WongyuKoh/Toccata/hardware/mechanical/touchscreen/rev3/README.md

# R31 터치스크린 수정 3판 (B1 · L2) — 2026-10-01

화면은 사용자가 고른 **B1 Waveshare 7-DSI-TOUCH-C**입니다(7인치, 가로 1024×600, DSI). 자리는 **L2 가운데 화면 뚜껑**(x501~721, y214~341.5, 윗면 z72.85)입니다. 모든 좌표는 `design/numbers.json`의 `placement` 블록(L2 확정값 `cad/spec/body_L2.json`)에서 스크립트로 계산합니다.

**상태:** 2026-10-01 사용자 승인("3판 승인"). `design/CAD_SPEC_rev3.md`를 CAD 세션에 넘겼고 CAD가 만드는 중입니다(사양과 다르게 만든 곳은 CAD가 목록으로 보냄). 설계 기준 R31·D14·D16·D19·D20~D24를 3판 값으로 고쳤습니다. 2판(공식 TD2, L1) 기록은 `../rev2_td2/`로 옮겼습니다(CAD L1 보관본이 거기서 읽음). CAD 3판은 통합본 v15 탭 09, `cad/src/touchscreen_rev3.py`입니다(사양과 다르게 만든 18곳은 W1 확인 완료).

| 폴더·파일 | 내용 |
|---|---|
| `touch_rev3_review.html` | 검수용 한 장짜리 페이지(검수할 것, 3D 렌더 9장, 도면 6장, 회로도 2장, 개념도) |
| `design/` | numbers.json(3a) · design.json · texts.json · **CAD_SPEC_rev3.md** · README_rev3.md · 개념도 · 스크립트(geom3 → build3 → draw3 → build3d) |
| `drawings/` | 치수 도면 t01 조립 옆 단면 · t02 뚜껑 평면 · t03 받침 부품도 · t04 뚜껑 변경부 · t05 받침다리·작은 부품 · t06 배선 (SVG·PNG, 생성기 `src/`, 점검 결과 drawings.json) |
| `model3d/` | 3D 미리보기(출력용 아님): 렌더 9장, GLB 2개(세운/접은), `viewer_B1.html`(브라우저에서 돌려 보기), 간섭 검사 결과(22°·25°·90° + 69자세, 간섭 0) |

회로도는 `hardware/pcb` 개정 C(SCH-01·SCH-06, △16)입니다.

**받은 뒤 확인할 것:**
- 화면 뒤 커넥터 방향: 반대면 받침 창·홈·뚜껑 구멍·클립을 x611 기준으로 뒤집고, A형 리본을 씁니다.
- M2.5 구멍 깊이
- 동봉 전원선 3핀 하우징 핀 배치: 통전 검사로 확인합니다.
- Pi 5 방열판과 리본 사이 틈
- 뒤꿈치 틈 0.37 mm와 클립 틈

**L2 앞판 40° 반영 뒤 바뀐 값 (10/1, CAD 실측)** — numbers.json·도면은 43° 때 L2 값으로 계산했고, CAD가 rev 3을 만드는 동안에는 다시 돌리지 않습니다.
- 가운데 유닛 뒷면이 y341.5 → y342.5로 바뀌어 뚜껑 깊이가 128.5가 됐습니다. 접은 받침 끝(y339.05)과 뚜껑 뒤끝 사이 여유는 2.45 → 3.45입니다. 뚜껑 나사 자리는 그대로입니다.
- 스피커 윗면이 z148.06 → z144.65로 바뀌었습니다. 접은 화면 위(z95.35)와의 여유는 52.71 → 49.30입니다.
- 소리 길 27° 규칙은 3.50 mm, D14는 228.5 mm로 둘 다 통과합니다. 화면과는 관계없습니다.
