WongyuKoh/Toccata/hardware/mechanical/sound-requirements.md

# Toccata — 요구 조건 (소리 · 제작 · 비용)

> 2026-09-24 · 대화에서 정한 요구 조건 모음. 설계와 부품 선정은 **이 문서만을 기준**으로 한다
> 근거 조사: [오디오 체인 조합 조사 보고서](../../docs/report/toccata-audio-chain.html) · 출발점 메모: [curcuit/material.md](curcuit/material.md)
> 이 문서로 만든 설계: [제작 설계서 v3 — 도면·치수·부품표·비용](../../docs/report/toccata-build-v3.html)

이 문서는 두 층으로 나뉜다.

- **요구사항(R)**: 사용자가 직접 말한 것
- **도출 조건(D)**: 요구사항을 지키려고 조사 중에 나온 기술 조건

---

## 1. 요구사항 (R)

### 1.1 음원 — 소리를 만드는 프로그램

| ID | 요구 | 원문 요지 |
|---|---|---|
| R1 | 피아노 소리를 낸다 | "피아노 소리를 낼 수 있는 것" |
| R2 | 누르는 세기·속도에 따라 소리가 달라진다 | "누르는 파워, 스피드에 따라 소리의 크기가 달라지잖아" |
| R3 | 댐퍼 페달을 지원한다 | "댐퍼 페달도 있으니까 그것도 되는 프로그램" |
| R4 | 88키 전부, 시간 제한 없이 동작한다 | "키 제한과 시간 제한 없는 프로그램" |
| R5 | 무료이거나 비용이 적게 들고, 위 기능을 모두 제공한다 | "무료거나 비용이 얼마 안 들면 좋을 거 같고, 내가 말한 기능을 모두 제공해야" |
| R6 | 실제 피아노처럼 동작한다 | "실제 피아노처럼 작동되게 할 수 있는 프로그램 혹은 오픈소스" |

### 1.2 입력 — 건반·페달에서 신호로

| ID | 요구 | 원문 요지 |
|---|---|---|
| R7 | 건반을 얼마나, 어느 속도로 눌렀는지와 페달 여부를 전달한다 | "건반이 어느정도, 어느 속도로 눌렸는지를 측정해서 정보를 전달… 페달 여부도" |
| R8 | 입력 신호는 우리가 변환해서 제공한다 | "입력 신호를 변환을 해서 제공을 할 수밖에 없어" |
| R9 | 하드웨어는 그대로 두고 음원 소프트웨어만 바꿀 수 있다 | "하드웨어는 동일하고 소프트웨어만 바꾼다고 하면 호환이 될까?" |

### 1.3 구현 방식

| ID | 요구 | 원문 요지 |
|---|---|---|
| R10 | 음원 칩이 아니라 소프트웨어로 소리를 만든다 | "그러면 소프트웨어로 해보자" |
| R11 | 꼭 라즈베리파이일 필요는 없다 | "라즈베리파이가 아니여도 되는데" |

### 1.4 소리 출력 — 앰프와 스피커

| ID | 요구 | 원문 요지 |
|---|---|---|
| R12 | 프로그램 + 앰프 + 스피커가 모두 호환되고 음질 그대로 동작한다 | "3개가 모두 호환 및 음질 그대로 작동이 되는 구성" |
| R13 | 스피커는 피아노 본체에 부착한다. 완제품보다 부품형 | "우리 피아노에 부착형… 아두이노 스피커에 가까운 제품" |
| R14 | 좋은 스피커와 앰프로 음량 손실이 없어야 한다 | "좋은 스피커를 사용해서 음량손실이 없게" |
| R15 | 헤드폰을 꽂으면 스피커가 꺼진다 | "2번방식으로 가는데" (② = 헤드폰 자동 차단 구성) |
| R16 | 88키 모두 소리가 깨지지 않고 제대로 나온다 | "88키 모두 소리가 깨지는 거 없이 제대로 나오게" |

### 1.5 기준선 — "실제 피아노처럼"의 의미

R2·R3는 고급 기능이 아니라 **지금 팔리는 입문형 디지털 피아노도 갖춘 기본기**다(Yamaha P-145, Roland FP-10에서 확인).

| 항목 | 입문형 디지털 피아노 | Toccata 목표 |
|---|---|---|
| 세기 → 음량·음색 | 있음 | 있음 |
| 페달 공명 | 있음 | 있음 |
| 하프페달 | 본체는 지원, 동봉 스위치 페달로는 불가(연속형 페달 별매) | 있음 |
| 스피커 | P-145: 7W×2, 12×8cm 타원 ×2 | 이 이상의 음량 |
| 최저음 | 실제 그랜드도 A0(27.5Hz) 기본음은 가장 강한 배음보다 최대 25dB 약하다 | 27.5Hz를 크게 내는 것이 아니라 **찌그러짐 0**. ~~30~100Hz 채움~~ → R25로 서브를 두지 않는다(P-145처럼 최저 옥타브는 배음으로 들린다) |

### 1.6 제작 · 구조 · 비용

| ID | 요구 | 원문 요지 |
|---|---|---|
| R17 | 도~시(C–B) 12건반을 한 세트(모듈)로 만들고, 나머지 건반도 같은 구조로 만든다 | "도부터 시까지를 한세트로 해서 똑같은 구조로 나머지 건반들이 만들어지고" |
| R18 | 모듈 단위로 탈부착해서 나눠 들고 다닐 수 있다 | "해당 부분을 묶음으로 해서 분할해서 가지고 다닐 수 있게" |
| R19 | PCB를 만들지 않고 손 납땜으로 배선한다 | "pcb를 만드는게 아니라 땜을 할거니까 케이블도 사야되고" |
| R20 | 건반은 3D 프린팅으로 만든다 | "피아노 건반은 cad로 뽑을거니까 필라멘트 등" |
| R21 | 총비용 100만원 이하. 케이블·필라멘트 같은 소모품 때문에 넘는 것은 허용 | "최대 비용을 100만원으로 잡고… 소모용 부품들에 의한 100만원 넘김은 넘어가자" |
| R22 | 건반 구조는 최대한 단순하게 해서, 원하는 기능만 최소한으로 구현한다 | "피아노 건반의 구조가 최대한 단순하게 구성해서 우리가 원하는 기능이 최소한으로 적용되도록" |
| R23 | 건반의 탄성과 복귀는 참고 영상의 컴플라이언트 메커니즘(플라스틱이 휘어서 움직이는 구조)을 참고해 구현한다. 똑같이 만들 필요는 없다 | "Compliant Mechanism 를 사용해서 탄성과 회복 동작을 구현했는데 우리도 똑같이는 아니더라도 이 점을 참고해서" |
| R24 | 페달은 댐퍼(서스테인) 하나만 둔다. 소스테누토·소프트 페달은 두지 않는다 | "나는 댐퍼만 필요하거든? 다른 페달은 빼도 돼" |
| R25 | 스피커는 좌우 2개면 된다(서브우퍼 없음). 스피커와 앰프는 비싸지 않은 것으로 고른다 | "양쪽 2개면 충분하잖아… 이정도로 비싸지 않더라도 소리는 다 커버가 될 거 같은데… 엠프도 너무 비싼 거 같아" |
| R26 | 건반뿐 아니라 스피커·CPU 상자 등 모든 파트를 따로 떼어 보관할 수 있는 독립 구조로 한다. 파트 사이는 물리적으로 고정되는 결합부를 두고, 전선은 꽂았다 뺐다 하는 커넥터로 잇는다 | "각 파트 별로 분할해서 보관이 되도록 파트별 독립적인 시스템… 결합 부분을 만들어 둬서 물리적 고정 결합… xt90? 같은 꼈다 뺐다 할 수 있는 케이블" |
| R27 | 스피커·CPU 상자 사이의 빈 뒷공간을 채워 본체 전체를 직사각형으로 하고, 그 속을 케이블 공간으로 써서 전체 길이(깊이)를 줄인다 | "뒷공간이 빈공간으로 되어있는데 그부분을 채워서 피아노의 전체적인 디자인 직사각형이 되게… 오히려 길이를 줄일 수 있잖아" |
| R28 | 보조배터리로 전원 없이(무선으로) 쓸 수 있게 하고, 보조배터리 수납 공간을 둔다 | "보조 베터리로 무선으로 할 수 있게 보조베터리 수납 공간도 제공하면 좋을 거 같아" |
| R29 | ~~빈 공간 한쪽에 건반 보관용 공간을 둔다~~ → R32 L2에서 본체 안 보관 칸 없음(사용자 승인 10/2). L2 가운데 유닛은 건반과 같은 높이(z72.85)라 안 높이가 44.85 mm뿐이고(예비 빗살 2층은 58.8 mm 필요) 안폭도 전자부로 꽉 찬다. 예비 건반은 따로 출력하는 부품 상자(약 210×180×65)에 넣어 모듈 가방과 함께 들고 다닌다 — `cad/spec/body_L2.json` key_storage | "건반 보관용 공간도 있으면 좋을 거 같아. 빈 공간은 많으니까 한쪽에 만들 수 있을 거 같아 보여" → "보관 칸은 빼도 돼"(10/2, CAD 세션 전달) |
| R30 | 스피커 파트 높이를 낮추고(210 → 150 mm 제안 → CAD L1 확정: 윗면 z232 → z134, 받침 22 → 5 mm), 앞판은 위쪽을 비스듬히(30°) 눕혀 유닛이 연주자 귀를 향하게 한다 (2026-09-30) | "스피커가 연주자쪽을 바라보게 되어있는데… 위쪽을 바라보게 해서 해도 되는 거 아니야?" → "비스듬하게 하는데 지금 보면 높이가 너무 높아. 높이를 좀 낮출 수 있어?" → "바꾸자" |
| R31 | 라즈베리파이 호환 터치스크린을 피아노 본체에 단다. ~~공식 Touch Display 2 7인치를 가운데 유닛의 출력 CU 뚜껑 위에 25° 뒤로 기울여 세운다(경첩 축 y290 z96, 화면 중심 x656 y304.7 z165.4, 가장 앞 y276.7). 운반할 때는 받침다리를 받침 뒤에 붙이고 화면을 뒤로 접어 z113에 눕힌다(스피커 윗면 z134 아래)~~ → 3판: 공식 제품이 아니어도 되는 호환 화면으로 한다. 13가지 조합을 비교해 사용자가 B1 Waveshare 7-DSI-TOUCH-C(7인치, 가로 1024×600, DSI)를 골랐다(10/1). L2 가운데 화면 뚜껑(x501~721, y214~341.5, 윗면 z72.85) 위에 25° 뒤로 기울여 세운다(경첩 축 y226.55 z81.35, 뒤꿈치 22°). 화면 가운데 x611, 보이는 영역 가운데 y240.91 z142.91, 가장 앞 y216.0이다. 운반할 때는 받침다리를 받침 뒤 클립에 끼우고 화면을 뒤로 접어 z78.35~95.35에 눕힌다(y233.05~339.05, 뚜껑 뒤끝 y341.5 안쪽 2.45 mm, 스피커 윗면 아래). 음색·볼륨·메트로놈·게임 메뉴를 터치로 조작한다. 재료는 추가되는 것만 따로 정리한다(~~103,600원~~ → 86,674원) (2026-09-30, 3판 승인 2026-10-01) | "라즈베리파이 호환 터치스크린을 피아노에 설치하면 좋겠어. 그걸 고려해서 설계 및 재료 정리를 다시 해줄래? 재료는 추가되는 재료만 알려줘. 그리고 그걸 바탕으로 ppt를 업데이트 해줘" → "모니터가 굳이 라즈베리파이 공식이 아니여도 라즈베리파이에서 터치되는 호환 제품으로 해도 돼" → "B1으로 하자" → "3판 승인" |
| R32 | 뒷바를 건반 바로 뒤에 붙여(L2) 뒤 영역을 최대한 줄이고, 케이블이 밖으로 보이지 않게 모두 닫힌 통로·앞 공간으로 넣는다. 스피커는 더 눕히고 작게, 가운데 유닛은 빈 공간 없이 촘촘하게 한다. CAD L2 확정값: 깊이 447 → ~~341.5~~ → 342.5, 가운데 윗면 z72.85(건반과 같은 높이), 스피커 앞판 수평에서 ~~43°~~ → **40°**(사용자 10/1), 스피커 윗면 ~~z148.06~~ → z144.65(L1 z134보다 10.65 높음 — 소리 길·그릴 R18·앞판 각도가 정함), 뒤 래치 없음 — `cad/spec/body_L2.json` (2026-10-01) | 사용자 요청(CAD 세션 전달): "건반과 뒤 부품을 합쳐서 뒤 영역을 최대한 줄이고, 케이블이 밖으로 안 나오게, 스피커는 더 눕히고 작게" → "앞판은 40°로 해줘" |

### 1.7 진행 방식

- 후보는 최대한 많이 찾고 보고서로 정리한다
- 부품은 이미지, 세부 스펙, 구매처 링크, 가격을 함께 보여 주어 바로 확인할 수 있게 한다
- 건반 구조는 도형 추상화가 아니라 **실제 치수를 기입한 평면도·측면도**로 설계한다. 그 도면대로 CAD를 짜면 실제로 구현되는 수준이어야 한다
- 기존 설계 자료는 참고하지 않고 이 문서만 기준으로 새로 설계한다
- 참고 영상은 §3의 분석을 기준으로 삼는다

---

## 2. 도출 조건 (D)

요구사항을 지키는 데 필요한 기술 조건이다. 사용자가 직접 말한 것이 아니라 조사에서 나왔다.

### 2.1 펌웨어 (Pico)

| ID | 조건 | 이유 |
|---|---|---|
| D1 | 페달 CC64를 0/127 대신 ADC 연속값으로 보낸다. 발을 뗐을 때는 정확히 0, ±2 이상 변할 때만 송신 | R3 하프페달. 켜짐/꺼짐 엔진에서 64 경계 떨림 방지 |
| D2 | Note Off는 정식 `0x80`, 릴리즈 벨로시티 하한 5 | Pianoteq에서 1이면 댐퍼가 내려가지 않는다는 보고 |
| D3 | 모듈마다 USB 제품 이름을 다르게 준다 (`Toccata O1`~`O7`, `Toccata PED`) | 고장 난 모듈 특정, 연결 스크립트 단순화 |
| D4 | 하드웨어 편차 보정(건반별, 흑건/백건)은 펌웨어에, 취향 곡선은 엔진에 둔다 | R9. 엔진을 바꿔도 펌웨어를 다시 보정할 필요가 없다 |
| D5 | ~~CC66(소스테누토)·CC67(소프트)도 보낸다~~ → R24로 페달을 두지 않는다(펌웨어 처리 코드는 남겨도 무해). 선택: CC88 고해상도 벨로시티 | 이해하는 엔진만 쓰고 나머지는 무시한다. 오동작은 없다 |

### 2.2 Pi 5와 소프트웨어

| ID | 조건 | 이유 |
|---|---|---|
| D6 | 8개 입력 병합은 한 곳에서만 한다 (FluidSynth `midi.autoconnect=1` 또는 Pianoteq `listen-all="1"`) | 병합 층이 겹치면 모든 음이 두 번 난다 |
| D7 | 오디오는 ALSA `hw:` 직결, 48kHz 통일, PipeWire 미설치 | 지연과 숨은 리샘플링 방지 |
| D8 | 키→소리 지연 10ms 미만 | 누르고 소리가 나기까지 지연이 체감되지 않는 한계 |
| D9 | 디지털 피크 −3~−6dBFS (최악 조건: 페달 + 저음 화음 ff) | R16. 페달 화음의 클리핑이 가장 흔한 깨짐 원인이고, 스피커로는 못 막는다 |
| D10 | 엔진 전환은 systemd 서비스 전환으로 한다 (`Conflicts=`) | DAC는 한 번에 한 프로그램만 쓸 수 있다 |
| D11 | 커널 #7320(Pi 5 I2S DMA) 대비: `hw:` 직결, 스트림 상시 유지, 워치독, 24~48시간 연속 재생 테스트 (R25로 USB 오디오를 쓰면 이 버그는 해당 없음, 연속 재생 테스트는 유지) | DAC2 Pro와 같은 PCM512x 계열 HAT에서 보고된 미해결 버그 |

### 2.3 스피커와 앰프

| ID | 조건 | 이유 |
|---|---|---|
| D12 | 스피커 유닛은 반드시 상자에 넣는다 (~~DMA105-4~~ → R25 CW-100B25: 밀폐 ~~약 4.7L~~ → ~~R26 스피커 파트 5.05L~~ → R30 **안 부피 2.9 L 이상**; CAD L1 확정값: 바깥 폭 213 × 깊이 195 × 높이 129(z5~134), 30° 앞판, 안 부피 2.95 L(유닛 빼기 전), 유닛 중심 y282.25 z81.5 — `cad/spec/body_low_L1.json`) → R32 L2: 안 부피 ~~2.218 L(유닛 빼면 2.118 L, 43°)~~ → 2.159 L(유닛 빼면 2.059 L, 앞판 40°, 유닛 중심 y260 z100.45), 흡음솜을 상자 전체에 느슨하게(유닛 뒤 10 mm·폴 벤트 앞은 비움) — `cad/spec/body_L2.json` | 상자가 없으면 뒤로 나간 소리가 앞소리를 상쇄해 저음이 사라진다 (R14). 5.05 L는 예전 유닛(DMA105-4, Qts 0.51, Vas 4.3 L)의 Qtc 0.707 값이 남은 것이다. CW-100B25(Qts 0.72, Fs 90~128 Hz)는 상자를 줄여도 Qtc가 크게 오르지 않는다: Vas 3 L로 가정하면 5.05 L에서 Qtc 0.91·Fc 약 126 Hz, 2.9 L에서 1.02·약 142 Hz(부밍 +1.4 dB). L1(2.95 L): 조준 28~39°(앉은 연주자 귀), 콘 아래 가장자리에서 귀로 가는 선이 모듈 윗판 위 약 5 mm로 지나가므로 모듈 뒤 y212~252 통로에는 z72 위로 아무것도 두지 않는다. 센서 줄과 226 mm. 앰프 앞 RC 필터가 93 Hz 아래를 이미 자르므로 체감 차이는 작고, 작은 상자가 저음 과진폭을 더 잘 막는다. Vas는 공개값이 없어 단계 0에서 추가 질량법으로 재어 확인한다. R32 L2 40°(2.06 L 유닛 뺌): Qtc 1.13, Fc 약 141~201 Hz, 솜으로 약 1.08. Vas 4 L이면 1.24라 솜을 기본으로 넣는다. 폴 벤트 앞 55.6 mm 비어 있음. 첫 x방향 공진 약 686 Hz(안폭 250, 유닛이 가운데보다 40 mm 안쪽)는 공기 속도가 큰 가운데 쪽까지 솜을 채워 줄인다. L2에서는 통로가 닫혀(y212~241, z0~27) 통로 규칙 대신 "콘 아래 끝에서 27° 선이 모듈 모서리(y212, z72.85) 위 3 mm 이상"을 지킨다(L2 40°: 3.50, 플랜지 모서리 2.61은 유닛 자기 테두리라 허용). 그릴 아래 링 벽은 없앴다(40°에서 선이 구멍 판 아래 끝 밑 1.72로 지나감, 개구율 72 %·구멍 Ø3 이상·판 2 mm). D14: 자석 중심에서 가장 가까운 홀센서까지 3D 228.5 mm, 가장 가까운 쇠까지 159.7 mm |
| D13 | 위성 스피커에 직렬 콘덴서(베이스 블로커)를 쓰지 않는다 | 계산상 330µF에서 80Hz를 오히려 +2.5dB 키운다. 상자 공진 근처에서 유닛 저항값이 약 17Ω까지 올라 콘덴서와 공진 |
| D14 | 스피커는 건반 센서 열에서 10cm 이상, 서브우퍼는 15cm 이상 떨어뜨린다. 설치 후 센서의 유휴 흔들림을 다시 측정한다 R31: 화면·경첩·받침다리에는 자석을 쓰지 않는다(3판도 같음). 3판 화면의 가장 앞(y216.0)은 센서 줄(y≈67)에서 149.0 mm 뒤다. 화면을 켠 상태와 끈 상태, 밝기 0 %와 100 %(`/sys/class/backlight/*/brightness`에 0·255, D20)에서 센서 유휴 흔들림을 다시 잰다. | 홀센서는 스피커 자석의 자기장을 입력으로 오인한다. SS49E급 기준 허용치(계산): 흔들리는 자기장 약 1.2mT, 고정 자기장 약 12mT |
| D15 | 스피커 상자, 특히 서브는 키베드에 직접 고정하지 않고 고무 등으로 진동을 격리한다 | 건반·센서 기판이 떨리면 치지 않은 음이나 잡음이 생긴다 |
| D16 | ~~앰프 HAT이 Pi에 전원을 공급하므로 Pi USB-C에 동시 급전 금지. EEPROM `PSU_MAX_CURRENT=3000`~~ → R25로 앰프 HAT이 없다. ~~Pi는 전용 5V 5A 어댑터 하나로만 급전한다~~ → R28로 Pi는 본체 안 5.1V 강압 전원 하나로만 급전한다(동시 급전 금지는 그대로, EEPROM `PSU_MAX_CURRENT=5000`) R31: 화면은 Pi GPIO 2번(5 V)·6번(GND)에서 전원을 받는다(Pi에서 나가는 방향이라 허용). 3판(B1)은 넷 `+5V_PI`다(회로 개정 C △16). 헤더 2·6번 → 점퍼 F/F 20 cm → 점퍼 M/M 20 cm → 화면 동봉선의 2.54 3핀(1 빨강 5 V · 2 빈 칸 · 3 검정 GND) → 화면 MX1.25 2핀으로 잇는다. 화면과 연장선에 다른 전원을 넣지 않는다. 화면은 약 2.15 W(5 V에서 0.43 A)다. Pi USB-C 입력은 ~~약 2.1 A~~ → 약 2.02 A, 5.1 V 레일은 2.42 A다. 피그테일(MT666) 정격은 공개되지 않았으므로 최대 부하(FluidSynth + 화면 밝기 100 % + USB 장치)에서 `vcgencmd get_throttled`가 0x0인지 확인한다. | 동시 급전으로 Pi가 파손된 사례가 있다 |
| D17 | 스피커는 연주자 쪽을 향하게 하고, 구멍이 넉넉한 그릴을 쓴다. R30: 앞판 위쪽을 30° 뒤로 눕혀 유닛 축이 앉은 연주자의 귀(스피커 중심에서 약 30° 위)를 향하게 한다. 위로 쏘기(윗판에 유닛)는 쓰지 않는다. R32(L2): 앞판을 수평에서 ~~43°~~ → 40°(수직에서 50°, 사용자 10/1)로 눕혀 유닛 축이 수평에서 50° 위를 향한다. 한계는 수평에서 37° 이상(권장 40~45°); 가운데 귀(유닛에서 32.7° 위)와 y-z면 어긋남 ~~14.4°~~ → 17.3° | 고음 손실 방지. 4인치 유닛은 약 1.2 kHz 위부터 소리가 앞으로 모인다. 위로 쏘면 연주자 귀가 축에서 약 60° 비껴 4 kHz 위가 6~10 dB 약해진다(평판 진동판 어림) |
| D18 | 서브가 없으므로(R25) 유닛에 맞춘 고역 통과 필터(약 60~100Hz)와 리미터를 걸고, 소리 게이트로 볼륨 상한을 정한다. 필터는 D7(`hw:` 직결) 때문에 ~~소프트웨어에서~~ → 앰프 입력의 콘덴서·저항(RC)으로, 리미터는 FluidSynth `synth.limiter`로 | R16. 작은 유닛은 최저 옥타브를 크게 내려 하면 과진폭으로 먼저 찌그러진다 |
| D19 | 보조배터리·충전기는 USB-C PD 20V 3A(60W) 이상을 쓴다. ~~45W 제품이면 볼륨 상한을 1dB 낮춘다~~ → R31: 45W 제품이면 볼륨 상한을 2dB 낮춘다(화면 포함). 1dB만 낮출 때는 화면을 끈다(밝기 0, D20) | R28. 평균 약 12W(SCH-06 표 13~17 W, ~~R31 화면을 더하면 16~20 W~~ → 3판 B1 화면 2.15 W로 15.69~19.69 W)지만 최대 음량의 저음 화음에서 순간 약 52W(SCH-06 rev B는 50 W, 큰 값을 기준으로 함), R31 화면을 더하면 ~~약 55 W~~ → 54.39 W(52 W + 2.15 W ÷ 0.9)까지 올라, 모자라면 전원이 끊긴다. 60 W까지 여유 ~~약 5 W~~ → 5.61 W. 45 W에서 −1 dB면 화면 포함 약 46 W로 넘치고(밝기 0이면 약 43.6~44.2 W: 백라이트를 꺼도 패널·터치 회로가 약 0.5 W 쓴다고 봄, 추정), −2 dB면 ~~약 40 W~~ → 39.39 W다. 보조배터리(74 Wh × 0.85 ≈ 62.9 Wh)로 약 3.19~4.01시간 쓴다(62.9 Wh ÷ 평균 19.69~15.69 W) |

### 2.4 검증 — 소리 게이트

R16의 합격 기준.

1. 최악 조건 연주 파일을 만든다: 88키 반음계 ff + 페달, A0~C2 뭉친 화음 최대 세기 + 페달, 옥타브 글리산도, A0 연타
2. 디지털 피크가 −3dBFS 이하인지 확인한다
3. 20~300Hz 사인 스윕을 최대 볼륨으로 튼다: 덜그럭거림·바람 소리가 없어야 하고, 건반 센서의 유휴 흔들림도 기준 안이어야 한다
4. 최악 조건 파일을 최대 볼륨으로 녹음한다: 모든 건반에서 찌그러짐이 없어야 한다
5. 통과한 볼륨보다 3dB 낮은 곳을 볼륨 상한으로 고정한다

---

### 2.5 터치스크린 (R31, 3판: B1 · L2, 2026-10-01 승인)

> 3판 값 출처: [numbers.json](touchscreen/rev3/design/numbers.json)(3a) · [CAD_SPEC_rev3.md](touchscreen/rev3/design/CAD_SPEC_rev3.md) · 회로 [hardware/pcb](../pcb/README.md) 개정 C(△16) · 재료 [hardware/bom](../bom/README.md). 2판(공식 TD2, L1 CU 뚜껑) 값은 취소선으로 남긴다

| ID | 조건 | 이유 |
|---|---|---|
| D20 | 화면은 ~~공식 Touch Display 2(DSI)로 하고 Pi 5 CAM/DISP 1 포트의 자동 인식을 쓴다(config.txt 수정 없음). 안 뜨거나 0번 포트면 `dtoverlay=vc4-kms-dsi-ili9881-7inch`(0번 포트는 `,dsi0`)를 넣는다~~ → 3판: Waveshare 7-DSI-TOUCH-C(DSI)를 Pi 5 CAM/DISP 1에 잇는다. config.txt 끝에 `dtoverlay=vc4-kms-dsi-waveshare-panel-v2,7_0_inch_c` 한 줄을 넣는다(0번 포트면 끝에 `,dsi0`). 기본 줄 `dtoverlay=vc4-kms-v3d`는 그대로 둔다. OS는 Raspberry Pi OS Lite(64-bit, 쓰는 판 고정)다. ~~가로 회전은 콘솔은 cmdline `video=DSI-1:720x1280@60,rotate=90`(이름은 kmsprint로 확인), 메뉴·게임(pygame KMSDRM)은 앱 안에서 1280×720을 돌리고 터치 좌표도 같이 돌린다~~ → 화면이 처음부터 가로 1024×600(60.0 Hz)이라 화면도 터치도 돌리지 않는다. 메뉴·게임(pygame KMSDRM)과 터치 좌표를 그대로 쓴다. 출력 이름은 kmsprint로 확인한다(Pi 5에서는 DSI-2일 수 있다). 밝기는 `/sys/class/backlight/*/brightness`에 0~255를 쓴다. 0이면 꺼진다(D14 시험, D19 화면 끄기). 연주만 할 때는 0으로 줄여 전력을 아낀다 | ~~공식 문서: `rotate=`는 텍스트 콘솔만 돌린다. KMSDRM 앱은 스스로 돌려야 한다.~~ → 3판: 오버레이와 터치 드라이버(Goodix, 5점)는 지금 Pi OS(2026-09-15, 커널 6.18.50)에 들어 있어 따로 설치하지 않는다. 그릴 픽셀이 0.61 MP로 TD2(0.92 MP)보다 33 % 적어 게임 60 fps 여유가 크다. 찬 부팅에서 가끔 화면이 안 켜진다는 보고가 있다(I2C write failed −5, raspberrypi/linux PR #7182 미반영). 재부팅으로 복구한다. 데스크톱 판은 PipeWire를 깔아 D7과 부딪힌다 |
| D21 | 터치 메뉴는 소리를 직접 내지 않는다. 음색·볼륨·리버브·메트로놈은 FluidSynth 셸(TCP)로 명령을 보낸다. 메트로놈은 피아노 음원의 높은 음(C7/G6)을 16번 채널로 짧게 낸다(선택: 작은 GM SF2의 우드블록) | D7·D10: DAC는 한 번에 한 프로그램만 쓴다. Salamander 피아노 SF2에는 10번 채널 드럼이 없다 |
| D22 | 화면은 받침(PETG, 170.7×106.0×17.0) 뒤에서 M2.5×6 4개로 화면 모서리 구멍(154×88)에 조인다. 받침은 앞 경첩 2개(축 ~~y290 z96~~ → y226.55 z81.35, M3×20, ~~x616~636.4·x703.8~724.2~~ → x538.6~559.0·x663.0~683.4, 나사는 바깥에서)와 받침 뒤 받침다리 1개(~~u20에 경첩, 95 mm~~ → u30에 축, 67 mm, 수평에서 39.78°, 발은 뚜껑 주머니 y290.43~300.7)로 25°에 세운다. 뒤꿈치는 22°에서 닿게 해 앞으로 3° 놀이를 둔다(3판: 귀 홈 바닥의 3.5 mm 멈춤 블록 z76.35에 닿음, 25°에서 0.37 mm 뜸). 다리는 화면을 22°에 댄 채 넣고 뺀다(25°에서 넣으면 발이 뒷벽 모서리를 0.66 mm 긁음). 접으면 받침 뒤 패드 4개가 뚜껑의 받침 발(16×16×5.5) 위 z78.35에 얹힌다. ~~모든 부품은 x559~753 안, y277보다 뒤에 두어 통로 규칙(y212~252에 z72 위 금지: D12 이유 칸, cad/spec/body_low_L1.json trough_rule)을 지킨다~~ → L2에는 열린 통로가 없다(소리 길은 D12의 27° 규칙). 화면 쪽은 모듈을 위로 빼야 하므로 모듈 위 금지 규칙을 지킨다. y≤215이면서 z≥72.85에는 화면 부품·선을 두지 않는다(모듈 뒤끝 y212, 뒷바 앞면 y214, 여유 1 mm). 22~90° 도는 동안 가장 앞 부품은 y216.0, 선은 약 y222.51이다. 경첩 축 y226.55 = 215 + 1 + 10.55(22°에서 받침 앞 아래 모서리가 축보다 앞으로 나오는 길이), z81.35 = 뚜껑 윗면 + 8.5 | 10 N 터치가 다리 압축 ~~39.3 N(좌굴 394 N)~~ → 27.22 N(좌굴 792 N, 29.08배)으로 간다. 경첩에는 앞뒤 12 N, 위아래 9 N이 걸린다. 사용 각도를 한 곳(다리)만 정해 과구속을 피한다. 다리는 받침 뒤에 붙여 접으므로 접은 높이가 늘지 않는다. ~~양옆 합판 뚜껑을 막지 않는다~~ → 받침 x525.65~696.35는 뚜껑 안이다(양쪽 24.65 mm). 모듈은 위로 빼므로 모듈 위에 아무것도 걸치면 안 된다. CAD 권장 경첩(y216~218, z76)은 22°에서 받침이 모듈 위로 넘어가 쓰지 않는다. 뒷바만 따로 놓였을 때(운반 중, 3.3 kg 추정) 넘어짐 여유는 1.58배이고, 건반 틀에 붙으면 훨씬 크다. 연주자 눈(y−350 z450 추정)에서 화면 가운데까지 아래로 27.46°라 기울기 25°와 2.46° 차이로 거의 정면이다. 화면은 스피커 콘과 x로 약 318 mm 떨어져 소리 길(D12)에 들어가지 않는다 |
| D23 | ~~CU 뚜껑 앞 모서리 2곳을 M3×10으로 나사형 모서리 받침에 조인다(CU-FL 자석 대신). 이 두 받침은 MS 폴리머로 합판에 붙인다. 뚜껑을 열 때는 받침 점검창에서 리본·J1 전원선을 빼고 나사 2개를 푼다~~ → L2(3판): 가운데 화면 뚜껑을 이음 레일의 M3 열압입 인서트에 M3×10 4개(앞 y246, 뒤 y322, x506·716)로 조인다. 뚜껑 쪽은 Ø6.5 × 5.5 자리파기(머리 자리 z67.35)이고 인서트 물림은 4다. 나사는 받침보다 19.6 mm 바깥이라 화면을 세운 채 풀 수 있다. O4 정비(O4 USB 플러그가 화면 뚜껑 밑에 있음): 화면을 뒤로 접는다 → 나사 4개를 푼다 → 뚜껑을 화면째 든다(리본을 꽂은 채 약 96 mm) → Pi 5 CAM/DISP 1 잠금을 올려 리본을 빼고 GPIO 2·6 점퍼 2개를 뺀다. 화면 쪽 ZIF는 받침 안이라 건드리지 않는다. 되돌릴 때는 리본 B형 방향과 점퍼(2번 빨강·6번 검정)를 확인한다 | 앞으로 당기면 뒤꿈치 힘(10 N 당김에 ~~약 161 N~~ → 150 N)과 경첩이 짝힘을 만들어 뚜껑 앞을 든다(나사 합계 ~~최대 약 80 N~~ → 앞 나사 2개 합계 약 34 N, 앞 나사 y246과 뚜껑 앞 받침 사이 30.5 mm 기준). 자석만으로는 확실하지 않다. ~~PVA는 PETG에 잘 붙지 않는다~~ → 자리파기 깊이 = 나사 자리 뚜껑 두께 11.5 − (10 − 인서트 물림)이다. 6.0으로 파면 나사 끝이 인서트 구멍 바닥에 닿는다(여유 0). 리본 여유 44 mm를 클립과 45° 접기 사이(뚜껑 밑)에 두어 뚜껑을 들 때 풀리게 한다 |
| D24 | DSI 리본은 ~~300 mm 하나로~~ → 22핀 0.5 mm 300 mm B형(반대면) 하나로(A형은 예비) Pi CAM/DISP 1 → 뚜껑 밑(z61.2, 리본 클립에 물림) → 뚜껑 구멍(~~x592~614, y292~298~~ → 22×6, x635.35~657.35, y228.55~234.55) → 경첩 고리(약 23 mm) → 받침 아래 홈 → 화면 DSI 커넥터(22핀, 입구 +x)로 잇는다. 45° 접기는 ~~Pi 위와 받침 안 두 곳~~ → 받침 안과 뚜껑 밑 두 곳뿐이고, R3으로 말아 접으며 세게 눌러 꺾지 않는다. Pi 쪽 끝은 안 쓰는 micro-HDMI 위에 얹혀 입구에 2.7 mm 꽂힌다. 경첩 고리는 ~~R10~~ → R6 이상이고, 남는 리본은 뚜껑 밑에 R10 이상 고리로 둔다. ~~클립 2개로~~ → 리본 클립(뚜껑 밑)과 누름 패드(받침 안)로 ZIF 커넥터가 당겨지지 않게 한다. 전원선(D16)은 화면 MX1.25 → 동봉 3핀 선 → 점퍼 M/M 20 cm → 점퍼 F/F 20 cm → GPIO 2·6이고, 리본 옆으로 같은 홈·고리·구멍을 지나 클립 윗면 전원선 홈(x652.6~656.1)으로 간다 | 필요 길이 ~~약 265 mm(여유 약 35 mm)~~ → 약 256 mm(여유 약 44 mm). 전원선은 필요 약 345 mm, 있는 길이 약 500~550 mm다. 접기마다 접점 면을 따라가면 B형이다(화면 커넥터가 왼쪽이면 A형, 약 200 mm). 선이 모듈 쪽으로 가장 나오는 곳은 약 y222.51이다(D22). 공식 안내: 리본을 접거나 당기지 말 것 |

받은 뒤 확인할 것 (3판, 받침·뚜껑을 출력하기 전에):

- 화면 뒤 커넥터 방향: 사진으로 오른쪽(입구 +x)이라고 봤다. 반대면 받침 창·홈·뚜껑 구멍·클립을 x611 기준으로 뒤집고 A형 리본을 쓴다.
- 모서리 M2.5 구멍 깊이: 물림 = min(깊이 − 0.5, 4.0), 최소 2.0. 박힌 스터드라 뗄 수 없으면 보스를 Ø6.2로 판다.
- 동봉 전원선 3핀 하우징: 통전 검사로 1 빨강 5 V · 2 빈 칸 · 3 검정 GND를 확인한 뒤 점퍼를 꽂는다. MX1.25→3핀 선이 120.54 mm 이상이면 이음이 뚜껑 밑에 온다.
- 실제 Pi 5: 방열판·micro-HDMI(윗면 추정 z27.3)와 리본 사이 틈, CAM/DISP 1 깊이(꽂는 길이 2.7 mm).
- 뒤꿈치 틈 0.37 mm는 출력 공차와 비슷하다. 다리 발이 주머니에 잘 안 들어가면 뒤꿈치를 0.3 mm 깎는다. 접은 다리 클립 턱과 뚜껑 사이 틈(0.78 mm)도 본다.
- 화면 아래 끝 작은 돌기(약 0.85 mm, 추정)가 받침 아래 벽 홈(x659~677) 안에 드는지, 뒤 볼록판 높이(약 2.1 mm 추정)가 맞는지 잰다. 뚜껑 레일 인서트는 CAD L2 값(Ø4.0 × 4.0, 구멍 깊이 4.5)으로 정해졌다.
- 리본 길은 폭 12 mm 종이띠로 잰다(약 256 mm / 300 mm).
- 전원을 뺐다 켜는 시험을 10번 한다(D20 찬 부팅 문제).

## 3. 참고 영상 분석

> dovetail studio, ["I 3D Printed a Working Piano"](https://www.youtube.com/watch?v=BAQskCuPaeY) (2026-08-03 게시, 7분 57초)
> 자막과 5초 간격 장면 미리보기(스토리보드)로 분석했다. 사용자가 지정한 3:13은 센서 구간이다.

### 3.1 영상에서 만든 것

| 항목 | 영상의 방식 |
|---|---|
| 규모 | 5옥타브 60건반 시제품. 약 7개월, 약 1,000시간, 50회 이상 반복 |
| 핵심 아이디어 | **컴플라이언트 메커니즘**: 플라스틱이 휘어서 움직이므로 관절·체결구가 없다. 플라스틱 상자의 경첩과 같은 원리 |
| 건반 회전 | 건반 뒤쪽의 얇은 **4절 링크(플렉셔)**. 깊이는 짧게 유지하면서 실제 피아노의 긴 레버 움직임을 흉내 낸다(자전거 서스펜션 링크에서 착안) |
| 무게감 | 건반을 누르면 컴플라이언트 힌지로 이어진 **해머(무게 레버)**가 올라간다. 레버 끝에 볼트·너트를 달아 실제 건반의 무게와 관성을 흉내 낸다 |
| 이스케이프먼트 느낌 | 출력된 스프링 형상이 누르는 도중 **촉각 턱**을 만든다 |
| 출력 | 옥타브를 한 번에 출력하면 서포트가 모델의 약 66%(모델 124g + 서포트 82g, 12시간 40분). 그래서 건반을 하나씩 분리하고 **도브테일 이음**으로 부분별 출력 후 조립했다. 필라멘트가 절반으로 줄었다 |
| 조립 | 건반 덮개는 별도 부품(색을 바꿔 출력). 무게 레버는 흰색으로 따로 출력. 도브테일 연결 부품이 흑건·백건 정렬을 잡고, 앞·뒤·바닥 연결 부품으로 마무리 |
| 부품 수·무게 | 옥타브당 53개(건반 12, 무게 레버 12, 연결 부품 12, 건반 덮개 12, 스페이서 5), 441g |
| 센서 (3:13 구간) | **적외선 반사 센서**가 흰색 해머의 위치를 연속으로 잰다. 반사량이 색에 따라 달라서 해머를 흰색으로 출력했다. 두 지점 통과 시간만 보는 방식 대신 연속 위치를 필터링·계산해 속도를 구한다 |
| 센서의 단점 | 주변 환경과 제조 편차 때문에 **보정이 필요**하다 |
| 전자부 | 직접 설계한 PCB. 보드 1장에 센서 16개, 모듈형으로 이어 붙이고(데이지 체인), 멀티플렉서를 2단(보드 단·센서 단)으로 써서 선 수를 줄였다. 중앙 보드의 Pico 2W 한 개가 MIDI 변환과 USB-C 전원을 맡는다 |
| 음원 | FluidSynth |
| 60건반 제작량 | 건반 800g·41시간 + 해머·덮개 660g·22시간 + 조립 연결부 470g·15시간 = 약 1,930g·78시간 (건반당 약 32g) |
| 제작자가 밝힌 문제 | 센서와 건반의 신뢰성이 부족하다. 다음 버전은 **PETG 출력과 홀 센서**로 바꿀 계획이라고 했다 |
| 시청자 반응 (댓글) | 기계 소음이 크다, 지연이 크게 느껴진다는 지적이 있었다. 시연에서는 "무게감이 딱 맞다", "집의 전자 피아노보다 낫다"는 반응도 있었다 |

### 3.2 Toccata 설계에 주는 시사점

| 구분 | 내용 | 관련 요구 |
|---|---|---|
| **가져온다** | 컴플라이언트 힌지로 회전과 복귀를 만든다 (핀·금속 스프링 없이) | R22, R23 |
| **가져온다** | 부분별로 나눠 출력하고 끼워 맞춰 조립해 서포트를 없앤다 | R20, R21 |
| **가져온다** | 건반 위치를 연속으로 재고 계산으로 속도를 구한다 | R2, R7 |
| **가져온다** | 옥타브 단위 모듈 + 멀티플렉서 | R17 |
| **가져온다** | 제작자의 교훈: PETG 출력 + 홀 센서 | 신뢰성 |
| 선택 | 무게 레버(볼트·너트 추), 이스케이프먼트 턱 — 단순성이 우선이라 기본 설계에서는 필요할 때만 넣는다 | R6 vs R22 |
| 가져오지 않는다 | 적외선 반사 센서 — 주변광·색·제조 편차 보정 부담 | 신뢰성 |
| 가져오지 않는다 | 전용 PCB — 손 납땜 조건 | R19 |
| 가져오지 않는다 | 보드 데이지 체인 + Pico 1개 — 모듈마다 독립된 USB-MIDI가 탈부착과 D3·D6에 맞다 | R18, D3, D6 |
| 주의 | 기계 소음(건반이 멈추는 곳의 완충), 지연(D8) | R6, D8 |
