WongyuKoh/Toccata/hardware/mechanical/touchscreen/rev2_td2/CAD_SPEC.md

# R31 터치스크린 — CAD 요청 사양 (W1 세션, 2026-09-30)

CAD 요청 — R31 터치스크린, 수정 2판 (좌표는 L1 world mm, 그림: scratchpad/touch/design/touch_concept.svg)

A. CU 뚜껑 v2 (CU-LID 대체, PETG, 199×195×11.5, x556.5~755.5, y252~447, z76.5~88)
1) 통풍 슬롯 15개(4 폭, 중심 x596.05~708.05, 간격 8)의 앞끝을 y297 → y301로 옮긴다(구멍·경첩 받침과 살 3 mm). 뒤끝은 y397 그대로. x652.05·x660.05 슬롯은 y384~397을 메운다(다리 주머니 자리).
2) 경첩 받침 2개를 뚜껑과 한 몸으로 출력한다. 폭 20.4 = 먼 볼 8.0 + 틈 0.2 + 귀 자리 8.0 + 틈 0.2 + 가까운 볼 4.0. 나사는 +x 쪽 가까운 볼에서 넣는다.
   왼쪽: 먼 볼 x616~624, 귀 자리 x624.2~632.2, 가까운 볼 x632.4~636.4. 오른쪽: 먼 볼 x703.8~711.8, 귀 자리 x712~720, 가까운 볼 x720.2~724.2.
   볼 옆모양(y-z): 축 (y290, z96) 둘레 R5.5 원 + 아래로 넓어지는 사다리꼴(z96에서 y284.5~295.5, z88에서 y281~299). 축 위로는 R5.5 밖으로 나오면 안 된다(받침 아래 모서리가 R6.5로 지나감).
   가까운 볼은 Ø3.3 관통, 먼 볼은 Ø2.5 × 8 깊이(M3×20 직접 탭, 물림 7.6). 귀 자리 바닥(뚜껑 윗면 y281~286)이 뒤꿈치 멈춤면이다. 경첩 받침 아래(y278~300)는 속을 채운다.
3) 리본·전원선 구멍: x592~614, y292~298 관통, 위아래 모서리 R1.
4) 받침다리 주머니: x649~663. 뒷벽은 y397.4에서 수직(위 모서리 C0.5). 바닥 z84.5는 y394.4~397.4. 앞은 30° 경사로 (y388.34, z88) → (y394.4, z84.5). 주머니 아래는 x646~666, y384~402를 z80까지 속을 채운 덩어리로 만든다.
5) 접이 받침 발 4개 16×16×8(z88~96): (x566~582, y352~368), (x566~582, y398~414), (x730~746, y352~368), (x730~746, y398~414).
6) 뚜껑 고정 구멍 2개: 중심 (570.8, 272.5), (741.3, 272.5). Ø3.4 관통, 위에서 Ø6.5 × 7.5 자리파기(머리 밑 4.0 남김). M3×10.
7) 뚜껑 밑면 CU-FL 자석 자리는 없앤다. CU-RR 자석(741.3, 426.5)은 그대로 둔다. 1판의 뒤 띠 받침대 축 받침은 없다.
8) 밑면 리본 클립 자리: (x605, y320) 둘레 30×12, 밑면 리브 사이.
9) 출력: 리브 면(z76.5)을 베드에 두고, 윗판은 리브 사이를 브리지로 출력한다(브리지 속도를 낮춤). 기존 방법 h(윗면을 베드에)는 윗면의 경첩 받침과 받침 발 때문에 쓸 수 없다. x 방향 구멍(Ø3.3, Ø2.5)은 물방울 모양으로 뽑고 드릴로 다듬는다. 약 205 g, 약 8시간.

B. 나사형 모서리 받침 2개 (CU-FL x561.8~579.8, CU-FR x732.3~750.3, 둘 다 y263.5~281.5, z64.5~76.5)
- 18×18×12, 자석 포켓 없음, 윗면 가운데 Ø2.5 × 10 구멍. 모서리 두 면을 목공본드 대신 MS 폴리머(세메다인 슈퍼X)로 붙인다. 나머지 10개 받침은 그대로. 조립 목록에서 CU-MAG-SUP-CU-FL과 CU-MAG-LID-CU-FL을 뺀다.

C. 화면 받침(크래들) 새 STL, PETG
받침 좌표: u = 유리 아래 끝에서 화면 위쪽으로, w = 유리 앞면에서 뒤로, x는 world와 같다(가운데 x656). DSI 커넥터가 −x 쪽(x≈638.7), J1이 아래(u36.5~43)에 오게 놓는다.
1) 바깥: x559.04~752.96(193.92), u −2.5~122.74(125.24), w −1.0~16.0(17.0). 옆벽 2.0, 유리와 틈 0.3. 옆벽 앞끝은 유리보다 1.0 앞(w −1).
2) 뒷판: w9.4~12.4(두께 3.0). 러그가 닿는 면 w9.4는 받은 화면으로 재서 맞춘다(도면 추정: 몸체 6.42 + 러그 3.0).
3) 러그 나사 구멍 4개: x = 586, 726 / u = 24.77, 95.48. Ø2.7 관통, 뒤에서 Ø5 자리파기(남는 두께 1.5, 동봉 M2.5).
4) Pi 스탠드오프 피함 구멍 4개 Ø7: x = 618.21, 676.21 / u = 35.62, 84.62.
5) ㄴ자 점검창: 윗부분 x596~666, u46~74(리본 접힘 + DSI 커넥터), 아랫부분 x640~666, u30~46(J1). 덮개는 창보다 사방 1.5 mm 큰 2 mm 판(턱에 얹힘)이고, 끼움부는 창보다 0.2 mm 작다. 걸쇠 2개.
6) 뒤 리브: 바깥 둘레 + 가로 리브 u20(다리 걸이 밑)과 u108(다리 클립), w12.4~16.0. 경첩 귀, 다리 걸이, 다리 클립 말고는 w16보다 뒤로 나오는 것이 없어야 한다.
7) 아래 트인 홈(리본 + 전원선): x592~614, u −2.5~3.0, w8~16, 뒤(w16) 쪽이 트여 있어 선을 뒤로 빼낼 수 있다.
8) 경첩 귀 2개: 두께 8.0, x624.2~632.2와 x712.0~720.0. 축 (u −9.0, w16.0), 구멍 Ø3.3, 축 둘레 살 R4.2 이상. 귀는 받침 아래 뒤쪽(u −2.5, w8~16)에서 축까지 이어진다.
   뒤꿈치: 모델을 22°로 돌렸을 때 귀의 앞 아래 끝이 world (y283, z88)에 닿게 한다(22° 상태에서 z88 평면으로 자름). 축에서 R10.63. 25°에서는 0.38 mm 뜬다.
9) 받침다리 걸이: 축 (u20, w19.5), x 방향. 가까운 볼 x646.7~650.7(Ø3.3 관통), 먼 볼 x661.3~667.3(Ø2.5 × 6 막힌 구멍, 물림 5.4). 다리 자리 x651~661(양쪽 틈 0.3). 볼 옆모양은 축 둘레 R3.8 + 뒷판 리브로 이어짐, 아래쪽 45° 모따기(서포트 없이).
10) 다리 클립: u105~111, x647.5~650.5와 x661.5~664.5, w16~22.5, 안쪽으로 0.5 mm 걸림 턱.
11) 리본 클립 자리(안쪽): u10~20, x597~613. 리본 접힘 자리 u52~68, x597~613(45°).
12) 확인값: 25° 사용 상태 가장 앞 (y277.34, z109.08), 가장 뒤 (y345.68, z215.4), 가장 높은 곳 z222.58. 22°에서 가장 앞 y276.67. 90° 접은 상태 y296.5~421.74, z96~113.
13) 출력: 윗변(u122.74 면)을 베드에 세워 출력(높이 약 131). 귀가 위로 온다. 다리 걸이와 클립은 45° 모따기로 서포트 없이. 러그 구멍은 물방울 모양. 약 80 g, 약 4.5시간.

D. 받침다리 새 STL: PETG 10(x) × 6, 축 구멍 Ø3.3 중심에서 발끝 중심까지 95.0, 양 끝 R3(전체 길이 101). 넓은 면을 베드에 눕혀 출력. 사용 상태: 축 world (y305.43, z120.8), 발끝 (y394.4, z87.5), 수평에서 20.5°. 접은 상태: 받침 뒤 w16.5~22.5, u17~118.

E. 작은 부품: ㄴ자 점검창 덮개 2 mm(윗부분 73×31 + 아랫부분 29×17.5), 리본 클립 2개 30×12×3. 선택: 화면 덮개 196×128×3(접은 화면 위, 받침 테두리에 얹힘).

F. 조립 파일: CU-LID 대신 CU 뚜껑 v2를 넣는다. 화면(TD2 7인치 상자 189.32×120.24×14.92)과 받침은 25° 사용 상태로, 받침다리도 사용 상태로 넣는다. 접은 상태는 별도 보기로 둔다. CU-FL·CU-FR 받침은 나사형으로 바꾼다.

G. 받은 부품으로 확인할 것: Pi 5에서 CAM/DISP 1의 실제 위치와 리본이 나오는 방향(±x). 받침과 뚜껑을 출력하기 전에 폭 16 mm 종이띠로 리본 길을 재어 285 mm를 넘지 않는지 본다. TD2 러그 높이와 스탠드오프 길이, J1 위치와 방향, 동봉 M2.5 나사 길이(4.5 mm 이상)도 잰다.
