WongyuKoh/Toccata/hardware/mechanical/key-action-v4/concepts/F1/design.md

# F1 — 오버테일 카운터레버 (over-tail counter-lever)

모든 수치는 `calc.py`가 계산했고 출력은 `results.txt`에 있다. 단위는 mm·g·ms이고, z = 0은 책상면, y = 0은 흰건반 앞끝(립)이다.

## 1. 한 줄 요약

건반은 뒤끝(y205)의 Ø3 강철봉에 걸려 도는 강체다. 보이는 부분 바로 뒤, 이름판 커버 아래의 빈 공간(y151~196)에 건반마다 무게 레버가 하나씩 있다. 레버의 짧은 앞 코(nose)가 건반 속으로 들어가 윗판을 아래에서 밀어 올리고, 뒤쪽에는 9×25 평철 조각(흰 70.6 g, 검 65.4 g)이 실려 있다.
건반을 누르면 코가 눌리면서 평철이 올라간다. 손을 떼면 평철이 떨어지면서 건반을 앞 업스톱(v3 훅 + 펠트)까지 밀어 올린다. 쉬는 위치는 업스톱 펠트가 정하고, 건반을 그 위치에 붙잡아 두는 힘은 중력뿐이다. 플라스틱에 걸리는 상시 응력은 최대 1.46 MPa다.

## 2. 제외한 네 구조와 무엇이 다른가

| 제외 구조 | F1과의 차이 |
|---|---|
| (a) 꼬리 추 시소 | 건반에는 추가 없다. 추는 별도 레버에 있어 건반 앞이 10 mm 내려갈 때 평철이 7.8 mm 오른다(R = 0.78). 그래서 같은 무게감을 내는 데 필요한 깊이가 C안 372 mm가 아니라 v3 프레임 212 mm다. |
| (b) Casio 뒤축 건반 + 건반 아래 해머 | 레버가 건반 **아래가 아니라 위·뒤**(보이지 않는 꼬리 위쪽 빈 공간)에 있다. 그래서 건반 앞쪽 아래(센서 바 y59~77.5)가 그대로 비어 있고, v3 전자부·건반 높이 z43.5·딥을 바꾸지 않는다. 연결은 슬롯이 아니라 중력으로 눌린 한쪽 접촉이라 유격이 0이다(블로그의 "덜걱" 원인 제거). |
| (c) 뒤축 건반 + 스프링 + 추가 질량 | 복귀 힘의 100 %가 중력이다. 스프링은 선택 사항이고 BOM에 넣지 않았다. |
| (d) 시소 건반 꼬리가 추 레버를 들어 올림 | 건반은 시소가 아니다(피벗이 맨 뒤). 레버를 미는 것은 꼬리가 아니라 건반 몸통 뒤끝 안쪽(y141)이고, 방향도 아래로 누르는 것이다. |

## 3. 목표 대비 결과 (brief §6)

| 항목 | 흰건반 (y13) | 검은건반 (y62.5) | 목표 |
|---|---|---|---|
| 균형 무게 B(쉼 → 바닥) | 45.8 → 42.9 g | 44.1 → 41.3 g | — |
| 마찰(손가락 환산, 쉼/중간/바닥) | 7.7 / 4.9 / 6.5 g | 5.4 / 4.6 / 6.5 g | 명시 |
| 다운웨이트 DW(움직이기 시작) | **53.5 g** (스트로크 중 49.1~53.5) | **49.5 g** (47.4~49.5) | 47~55 ✓ |
| 업웨이트 UW | **38.1 g** (36.4~39.7) | **38.7 g** (34.7~39.6) | ≥ 20 ✓ |
| y0 립 / 검 앞모서리 y52.5에서 B | 42.9 g | 41.2 g | — |
| 유효 질량 m_eff(쉼/중간/바닥) | 76.3 / 71.4 / 68.7 g (건반 10.5 + 레버 58~66) | 72.2 / 67.3 / 64.4 g | ≥ 60 ✓ |
| 재타건 지점(자석 40 % 복귀)까지 | 36.3 ms → **27.6 Hz** | 35.1 ms → **28.5 Hz** | ≥ 13.3 Hz ✓ |
| 완전 복귀(업스톱 첫 접촉) | **57.6 ms** | **55.7 ms** | < 60 ms ✓ |
| 연타(0.5 m/s로 누르고, 40 %에서 다시 누름) | 26.8 ms 간격 = 37.4 Hz | 22.2 ms = 45.1 Hz | — |
| 앞/뒤 비 F(y90)/F(y13) | 1.67 | F(y90)/F(y62.5) 1.24 | 명시 |
| 플라스틱 상시 응력 최대 | 1.46 MPa (용골 y149) | 0.75 MPa | < 2 ✓ |
| 자석 이동 / 바닥 간격 | 6.78 / 4.04 mm | 8.72 / 4.63 mm | 간격 ≥ 3 ✓ |
| 가장 높은 움직이는 점 | 레버 z54.6 (ff 타건 순간 z56.4) | z54.3 (ff z55.9) | 커버 아래 z57.5 |

재타건 가정: 펌웨어는 자석이 바닥에서 **이동량의 40 %** 만큼 돌아오면 재타건을 허용한다. 수식 추정 t = √(2·딥·m_eff/((B−마찰)·g))는 60.6 ms(완전 복귀)와 38.3 ms(40 %)이고, 시뮬레이션 값과 맞는다. 복귀 시간은 m_eff/(B−마찰)로 정해진다. 그래서 v2.0 문서의 "중력 복귀는 질량과 무관하게 약 40 ms로 고정"이라는 주장은 틀렸다. 반복 속도를 제한하는 것도 완전 복귀가 아니라 40 % 지점이다.

선택 사항인 보조 스프링을 달아 손가락 환산 +6 gf를 더하면 재타건 33.9 ms, 완전 복귀 53.8 ms가 된다. 다만 DW도 6 g 오른다. 목표를 이미 만족하므로 넣지 않는다.

## 4. 좌표표 (y, z) — 쉼 → 바닥

### 흰건반 (D 단면 기준, 레버 피벗 x = 건반 중심)

| 점 | 쉼 | 바닥 |
|---|---|---|
| 건반 피벗 봉 중심 KP (Ø3, 옥타브당 1개) | (205.00, 18.00) | 고정 |
| 레버 피벗 봉 중심 LP (Ø3, 옥타브당 1개) | (151.00, 35.83) | 고정 |
| 건반 앞 윗모서리(딥 기준점) | (0.00, 43.50) | (−1.00, 33.50) |
| 손가락 점 y13 윗면 | (13.00, 43.50) | (11.99, 34.13) |
| 업스톱 접점(크로스바 윗면 / 훅 펠트 3T 밑면 z25.1) | (12.25, 25.10) | (12.13, 15.72) |
| 다운스톱 접점(앞 바닥판 밑면 / 앞 펠트 윗면 z13.84) | (6.60, 23.50) | (6.57, 13.84) |
| 자석 면 중심(소자 열 y67, 소자 z12.68) | (65.80, 23.50) | (65.70, 16.72) |
| 연결점: 건반 쪽 천 패드 면 | (141.00, 40.90) | (139.96, 37.76) |
| 연결점: 레버 코 중심(R2) | (141.37, 38.90) | (140.89, 35.80) |
| 건반 무게중심(20.8 g) | (81.65, 32.79) | (81.08, 26.77) |
| 레버 무게중심(74.3 g) | (174.14, 31.44) | (174.37, 38.74) |
| 평철 중심(9×25×40) | (174.22, 31.59) | (174.40, 38.90) |
| 레버 탭 윗면(위 펠트 밑면 z48.75) | (203.84, 31.88) | (202.52, 48.25) |
| 레버 탭 아랫면(가드 펠트 윗면 z26.43) | (203.21, 27.93) | (203.12, 44.30) |

레버 각도는 쉼 −9.14°에서 바닥 +8.68°까지 움직인다. 건반 각도는 0 → 2.788°다.

### 검은건반 (C# 단면 기준)

| 점 | 쉼 | 바닥 |
|---|---|---|
| KP / LP | (205.00, 18.00) / (151.00, 35.83) | 고정 |
| 앞 윗모서리 y52.5 | (52.50, 55.50) | (50.47, 46.00) |
| 손가락 점 y62.5 | (62.50, 55.50) | (60.45, 46.62) |
| 업스톱 접점(크로스바 y76.5~80) | (78.25, 25.10) | (78.05, 17.25) |
| 다운스톱 접점(바닥판 y52.7~59 / 펠트 윗면 z14.27) | (55.85, 23.50) | (55.80, 14.27) |
| 자석 면 중심(소자 z10.15) | (64.20, 23.50) | (64.13, 14.78) |
| 연결점: 브리지 밑 천 패드 | (138.00, 41.42) | (136.68, 37.24) |
| 레버 코 중심(R2, 코 팔 13) | (138.42, 39.42) | (137.92, 35.31) |
| 건반 무게중심(17.2 g) | (111.13, 36.55) | (110.16, 30.71) |
| 레버 무게중심(69.0 g) | (172.64, 31.61) | (172.88, 38.58) |
| 평철 중심(9×25×37) | (172.72, 31.74) | (172.91, 38.74) |
| 탭 윗면 / 아랫면 | (203.83, 31.69) / (203.18, 27.74) | (202.48, 48.41) / (203.09, 44.46) |

검은건반 딥 각도는 3.545°다. 흰건반보다 28 % 더 도는 만큼 검은건반 레버의 코 팔을 13 mm로 늘려 레버 회전을 흰건반(17.8°)과 비슷한 18.2°로 맞췄다.

### 부품 형상 (기준 자세 = 레버 중간 행정, 흰건반)

- **레버**: 코+팔 y139~148 · z33.3~38.3 · 폭 3.6(x −0.5~3.1), 허브 링 Ø7.2/Ø3.2 · 폭 4.4, 캐리어는 옆판 1.5 + 바닥 1.2 + 앞뒤 벽 1.2(y153.4~195.8, 폭 10.5), 평철 y154.6~194.6 · z22.8~47.8, 뒤 탭 y195.8~207.8 · z36.3~40.3 · 폭 5(x 0.5~5.5). 검은건반 레버는 코 팔이 3 mm 길고(y136) 평철이 37 mm다.
- **건반 용골(keel)**: 속 웹 y136~146(x −4.5~−1.5, 두께 3), 목 y146~149 · z9.5~33.5, 추 아래 앞단 y149~172 · z9.3~16.8 · 폭 4.5, 뒷단 y172~197 · z7.8~12.3 · 폭 8, 라이저 y197~200 · z6.3~22.5, C훅 y200~208.5 · z13.5~22.5(봉 z18 둘레, 뒤로 열림).
- **프레임 추가분**: 핀 판 13장(두께 1.2, y147~160, z5~38, 레버 칸 경계 x = 이웃 건반 중심의 중점, A#|B 핀만 0.35 왼쪽으로)이 윗면 J-슬롯에 레버 봉을 받친다. 뒤 빗(rear comb) 블록 y200~209 · z5~52에는 건반 봉 구멍 Ø3.1(z18), 훅 슬롯 3.8 × 12, 탭 포켓 6 × 8.7이 있다. 포켓 바닥에는 가드 펠트 3T(윗면 z26.4), 천장에는 위 펠트 3T(밑면 z48.8)를 붙인다.
- **x 배치**: 레버 칸 폭 11.72~12.84, 캐리어 10.5, 한쪽 여유 0.61~1.17 mm(`results.txt` x layout).

## 5. v3에서 바꾼 것 / 뺀 것

- **뺀 것(v3)**: 리프 플렉서, 척추 2개, 척추 레일(y196~209), M3×40 클램프 4개, 세트스크루 4개, 황동 원판 4개, 뒤 두 번째 바닥 레일(y138~144), 운반 모드. 크리프로 무게가 10~30 % 줄던 문제가 원리적으로 없어진다.
- **뺀 것(그랜드 대비)**: 해머·윕펜·잭·렙레버·백체크·댐퍼, 밸런스 레일 핀, 건반 납추.
- **뺀 것(GHS·Casio 대비)**: 건반 아래 해머와 해머 레일, 슬롯식 연결, 해머 쪽 스위치(센서는 v3처럼 건반 자석을 그대로 읽는다).
- **바꾼 인터페이스**: (1) 제어 기판을 y145.5~195.5에서 **y82~132(z7~8.6, 부품 ≤ z14.5, 4067 모듈·RP2040-Zero는 헤더 없이 납작하게)** 로 옮긴다. 눌린 건반과의 여유는 흰 3.0, 검 1.4 mm다. USB-C는 15 cm 연장선으로 v3 USB 터널까지 뺀다. (2) 건반을 콤이 아니라 한 개씩 뽑는다. 길이는 208.5이고, 보이는 부분은 v3 그대로다. (3) 흰건반 윗판을 2.6에서 2.0으로 줄인다(리프 역할이 없어짐). (4) 흰건반 노치면 아래 모따기를 1.5에서 2.5로 늘린다. 검은건반 앞면이 원호로 움직여 흰 노치면에 닿는 것을 피하기 위해서이며, 최소 여유는 0.37 mm다. (5) 업스톱 훅 립 방향을 앞쪽으로 뒤집는다. 건반을 4 mm 뒤로 밀면 걸린다. (6) 뒤 커버 윗판을 y150~200 구간만 2.5에서 1.5로 줄인다. 밑면은 z57.5가 되고 윗면 z59는 그대로다. (7) 앞 펠트 윗면 높이를 새 피벗 기준으로 흰 z13.84, 검 z14.27로 다시 정한다.
- **그대로 둔 것**: 프레임 깊이 212, 전체 깊이 410, 흰건반 윗면 z43.5, 검은건반 z55.5, 딥 10 / 9.5, 센서 바·자석 위치, 가이드 탭과 부싱 펠트, 도브테일 모듈.

## 6. 부품표 (옥타브 1개)

| 부품 | 종류 | 재질 | 수량 | 개당 질량 | 크기 |
|---|---|---|---|---|---|
| 흰건반(몸통 + 용골 + C훅 일체) | 출력 | PETG | 7 | 20.5 g | 208.5 × 22.5 × 37.7 |
| 검은건반(몸통 + 브리지 + 용골) | 출력 | PETG | 5 | 16.9 g | 157 × 11 × 49.7 |
| 레버 캐리어(흰·검 2종, 옆판 1장 구조) | 출력 | PETG | 12 | 3.6 g | 약 72 × 10.5 × 31 |
| 평철 추 9T × 25 × 40 / × 37 | 구매 | SS400 | 7 / 5 | 70.6 / 65.4 g | 절단 조각 |
| Ø3 연마봉(건반 봉·레버 봉) | 구매 | SUS304 | 2 | 9 g | 163.5 |
| 자석 Ø5×2 N35 | 구매(v3) | NdFeB | 12 | 0.3 g | — |
| 코 패드 부싱 천 0.6T | 소모품 | 양모 | 12 | — | 8 × 4 |
| 탭 펠트 3T(위·가드) | 소모품 | 양모 | 24 | — | 5 × 8 |
| 업스톱 훅 펠트·앞 펠트·가이드 부싱 | 소모품(v3) | 양모 | v3와 같음 | — | — |
| 프레임(+ 핀 판 13, 뒤 빗 블록) | 출력(v3 개조) | PETG | 1 | 184 g | 168.5 × 212 |
| 센서 바 · 뒤 커버 | 출력(v3) | PETG | 각 1 | 16 / 44 g | — |

옥타브당 출력 부품은 건반 12 + 레버 12 = 24개이고, v3 프레임·커버·센서 바를 더하면 27개다. 구매 부품은 평철 12 + 봉 2 + 자석 12 = 26개다. 옥타브당 강철은 821 g, 88건반 전체로는 6.03 kg(평철 3.54 m)이다.

## 7. 구매 (v3 기본 구성 대비 증감)

| 품목 | 사양 | 수량 | 금액 | 출처 |
|---|---|---|---|---|
| 평철 SS400 9T×25 | 1 m 단위 4개 | 4 | 18,000 | 온라인 평철 절단 판매 — 추정 |
| 평철 절단 | 88컷(직접 쇠톱이면 약 3시간, 0원) | 88 | 26,400 | 추정 |
| SUS304 연마봉 Ø3 × 1 m | 2.46 m 필요 → 3개 | 3 | 28,800 | baegwan.net 9,600원/개 확인 |
| USB-C 연장선 15 cm | 모듈당 1개 | 7 | 24,500 | 추정 |
| v3 척추 클램프 철물 제거 | M3×40, 세트스크루, 황동 원판, 와셔, 너트 | 7 | −17,500 | 추정 |
| **기본 구성 증감** | | | **+80,200** | 583,219 → 663,419원(한도 100만원 이내) |
| 소모품: 펠트·부싱 천 추가 | | | 5,000 | 추정 |

## 8. 출력 계획

- **건반**: 윗면을 베드에 대고 거꾸로 뽑는다. 용골은 윗면에서 떨어져 있으므로 **설계에 넣은 0.8 mm 떼어내기 리브**(흰 1.5 g, 검 2.0 g)로 받친다. 흰건반 7개를 나란히 놓으면 169.5 × 208.5, 검은건반 5개는 67 × 157이라 220 베드에 한 판씩 들어간다.
- **레버**: 옆판을 베드에 눕혀 뽑으므로 서포트가 없다. 12개(72 × 31)가 한 판에 들어간다. Ø3.2 구멍은 드릴로 다듬는다.
- **프레임**: v3처럼 바로 세워 뽑는다. 핀 판과 뒤 빗 블록이 프레임에 붙어 있고, 가장 높은 곳은 z52이다.
- **양·시간(15 g/h)**: 옥타브당 건반·레버·리브 291 g(v3 콤 267 g), 프레임 +8.8 g, 모듈 합계 535 g(v3 502 g). 88건반 액션 부품은 2.14 kg · 143 h, 악기 전체는 5.25 kg · 350 h(v3 5.00 kg · 332 h)다.

## 9. 조립과 한 건반 빼기

1. 프레임 준비: EVA 시트를 깔고 앞 펠트(흰 z13.84, 검 z14.27이 되게), 업스톱 훅 펠트, 가이드 부싱 펠트를 붙인다(v3와 같다). 제어 기판은 y82~132에 둔다. 뒤 빗 포켓에 가드 펠트와 위 펠트를 붙이고, 건반 봉(Ø3 × 163.5)은 모듈 끝에서 옆으로 밀어 넣는다.
2. 건반: 자석을 CA로 붙인다. 건반 앞을 1 mm 들고 제자리보다 4 mm 앞에 내려놓은 뒤 4 mm 뒤로 민다. C훅이 건반 봉에 딸깍 걸리고 크로스바가 훅 립 아래로 들어간다. 레버가 없는 동안 건반은 앞 펠트에 눕는다. 12개를 모두 끼운다.
3. 레버 세트: 평철을 각 캐리어에 넣고 CA를 한 방울 떨어뜨린다. 레버 봉에 12개를 순서대로 끼우고, 평철 쪽을 손으로 들어 코가 내려간 자세를 유지한다. 그 상태로 제자리보다 5 mm 앞에서 봉을 핀 J-슬롯에 내리고 5 mm 뒤로 민다. 코가 건반 패드 아래로, 탭이 포켓으로 들어간다. 손을 놓으면 평철이 떨어지면서 건반 12개가 업스톱까지 올라온다. 마지막으로 봉 고정 클립을 끼운다.
4. 뒤 커버를 끼운다.
5. **한 건반 빼기(공구 없음)**: 뒤 커버를 빼고 → 레버 세트를 5 mm 앞으로 당겨 든다(평철은 들린 채 매달린다) → 건반을 4 mm 앞으로 당겨 들어낸다. 용골이 평철 밑을 지나가므로 레버를 그대로 두고는 건반만 뺄 수 없다. 옥타브 단위로 레버 세트를 먼저 빼는 방식이다.

## 10. 소음

- 다운스톱: 앞 펠트 3T(v3). 피크 7~18 N(0.1~1.0 m/s 타건).
- 레버 과회전: 탭이 뒤 빗 포켓 천장의 위 펠트 3T(5 × 8)에 닿는다. 피크는 mf 6 N, ff 약 50 N이고 ff에서 펠트가 2.4 mm 눌린다. 뒤쪽 커버 아래라 들리는 소리는 적지만 가장 큰 충돌이다.
- 복귀: 건반은 업스톱 훅 펠트 3T에, 레버 탭은 가드 펠트(쉼보다 1.5 mm 아래)에 거의 동시에 내려앉는다. 가드 피크는 3.5~4.2 N이다. 되튐은 흰 0.66, 검 0.57 mm(손가락 위치)로, 재타건 지점 40 %보다 훨씬 작다. 0.2 mm 안으로 가라앉기까지 약 100 ms 걸린다.
- 연결부: PETG 코(R2)가 부싱 천 0.6T를 누르는 한쪽 접촉이고 중력으로 늘 눌려 있어 유격이 0이다. 바닥에서만 최대 0.43 mm 떨어졌다가 0.37 m/s 이하로 천 위에 다시 앉는다("톡" 수준).
- 건반 봉 C훅: 쉴 때는 봉이 건반을 아래로 눌러 아래 턱이 받는다. 다운스톱 충격 순간에만 위 턱이 최대 +5.6 N을 받는다. 그래서 위 턱 안쪽에 부싱 천 0.5T를 붙이고 꼭 맞게 끼운다.
- 레버 봉: 늘 아래로 눌려 있어 달그락거리지 않는다. 평철은 CA로 붙어 있다.

## 11. 위험

1. **가드 펠트 공차**: 가드는 탭에서 1.5 mm, 코에서 0.29 mm 아래에 있다. 가드가 0.3 mm 이상 높게 붙으면 레버가 가드에 얹히고, 건반이 업스톱에 눌리지 않아 헐거워진다. 단계 0에서 심(shim)으로 맞춘다.
2. **ff 과회전**: 위 펠트가 67 % 눌리고 레버 꼭대기가 z56.4까지 올라 커버 밑면 z57.5와 1.1 mm만 남는다. 펠트가 주저앉으면 평철이 커버에 닿을 수 있다.
3. **용골**: 폭 3~8 mm의 얇은 판이고 상시 1.46 MPa를 받는다. 출력 공차와 떼어내기 리브 자국이 영향을 줄 수 있다.
4. **분해 순서**: 건반만 따로 뺄 수 없다. 레버 세트(840 g)를 먼저 빼야 한다.
5. **무게**: 강철 6 kg이 더해져 모듈이 0.59 kg에서 약 1.45 kg이 되고, 악기 전체는 약 18 kg이 된다.
6. **제어 기판 이전**: 부품을 z14.5 이하로 맞춰야 하고, 검은건반 아래 여유가 1.4 mm뿐이다.
7. **마찰 가정**: 피벗 μ 0.2, 가이드 2 gf, 코 μ 0.3을 가정했다. DW/UW가 이 값에 달려 있다.
8. **검은건반 앞면 여유 0.37 mm**: 흰 노치 모따기 2.5와 출력 정확도에 달려 있다.
9. **펠트 모델**: E 0.4 MPa, ζ 0.35라는 가정에 따라 되튐과 안착 시간이 바뀐다. ζ 0.5면 되튐은 0.33 mm로 줄어든다.

## 12. 단계 0 시험 (빨리 틀렸음을 확인하는 순서)

1. 흰건반 1개, 레버 1개, 2칸 프레임 조각(핀·뒤 빗·앞 레일·훅)을 뽑는다. y13에 동전을 올려 DW/UW를 잰다. 합격은 DW 47~55, UW ≥ 30이다.
2. 휴대폰 240 fps로 바닥에서의 복귀를 찍는다. 합격은 40 % 지점까지 ≤ 40 ms, 완전 복귀 ≤ 65 ms, 되튐 ≤ 1 mm다.
3. ff 낙하 시험: 100 g을 50 mm 높이에서 건반 앞에 100번 떨어뜨린다. 평철이 커버 높이(z57.5 표시)를 넘지 않는지, 위 펠트가 영구 변형되는지 본다.
4. 가드 심을 ±0.3 mm 바꿔 가며 건반이 늘 업스톱에 눌려 앉는지 확인한다.
5. 40 °C에서 7일 둔 뒤 건반 높이와 DW 변화를 잰다. 합격은 1 g 미만이다(용골·훅 크리프 확인).
6. pp/ff 녹음을 v3 리프 시제품과 비교한다(소음).
