WongyuKoh/Toccata/hardware/mechanical/key-action-v4/concepts/H1/design.md

# H1 — 뒤축 건반 + 무게추 해머 (카시오 PX-720 / 야마하 GHS 방식, 축소판)

모든 수치는 `calc.py`가 계산했고 원문은 `results.txt`에 있다. 그림은 `h1_side.png`(백건 D·흑건 C# 단면, 실선 = 정지, 점선 = 끝까지 누름).
단위 mm, g, N, ms. 좌표: y = 백건 립 앞끝 0, 뒤쪽 +; z = 책상면 0; x = 가로.

## 1. 한눈에

- **건반**은 뒤끝(y171, z40)의 Ø3 SUS304 봉에 걸려 도는 출력 레버다. 이 점은 v3 리프의 순간 회전 중심 (171.04, 40.96)과 같아서, **y146 앞쪽(센서·자석·앞 펠트·가이드 탭·훅)은 v3와 한 치도 다르지 않다.** 자석 이동량도 백 6.12 / 흑 8.46 mm로 v3와 같다.
- 건반 밑에 매달린 **러그**(R3 둥근 끝, 백 y108, 흑 y96)가 **해머 코의 펠트 1T 패드**를 누른다. 해머는 두 번째 Ø3 봉(y127.55, z15)에 걸려 있고, 긴 뒷팔 끝(건반 봉 **뒤쪽**, y182–207)에 **9×25 평철 조각**(백 24 mm 42.4 g, 흑 22 mm 38.9 g + 2 mm 출력 심)이 있다.
- 누르면 해머 코가 내려가고 추가 11.9 mm 올라간다(10.4°). 손을 떼면 추가 떨어지며 러그를 밀어 건반을 올린다. 건반은 v3와 같은 **가이드 탭의 훅(펠트 3T)**에 닿아 멈춘다. 추는 해머 무게로 늘 러그를 누르고 있어서 **결합부 유격이 0**이다(블로그의 "덜걱" 원인이 없다).
- 세게 치면 추 윗면이 **스톱 레일 밑 펠트 3T**(z55.5)에 부딪혀 멈춘다(야마하 GHS·카시오의 윗 스펀지와 같은 역할).
- 흰 건반·검은 건반이 **같은 해머 하나**를 쓴다. 흑건 러그를 앞(y96)에, 백건 러그를 뒤(y108)에 두고 해머 봉 위치를 풀어서 두 색 모두 해머가 똑같이 10.43° 돌게 했다.
- 스프링은 없다(기본). 선택 사항으로 스톱 레일에 약한 보조 스프링 자리를 둔다(§9).

## 2. 핵심 수치 (brief §6)

| 항목 | 백건 | 흑건 | 목표 |
|---|---|---|---|
| DW (y13 / 흑 y62.5) | 47.7 g | 51.0 g | 47–55 |
| UW | 35.6 g | 40.4 g | ≥ 20 |
| 균형 (DW+UW)/2 | 41.7 g | 45.7 g | |
| 마찰 (DW−UW)/2 | 6.1 g (핀 1.6 + 러그 미끄럼 4.2 + 가이드 0.3) | 5.3 g | |
| DW 립(y0) / 흑건 앞끝(y52.5) | 44.1 g | 46.7 g | |
| 앞뒤 힘 비 F(y90)/F(y13) | 1.95 (v3와 같음) | | |
| 유효 질량 m_eff (행정 중간) | 92.5 g (정지 79.5 → 바닥 107.4) | 95.0 g | 60–100 |
| 바닥 → 40 % 복귀(재타건 점) | 41.3 ms | 39.3 ms | |
| 완전 복귀 (스프링 없음 / 있음) | 63.6 / 56.4 ms | 60.8 / 53.8 ms | 이상적으로 < 60 |
| 재타건 속도, 손가락 힘 1.5 N / 2.0 N | 12.0 / 14.4 Hz | 12.4 / 15.2 Hz | ≥ 13.3 |
| 정지 시 플라스틱 최대 응력 | 0.53 MPa (해머 뒷팔 뿌리) | | < 2 |
| 자석 이동 / 바닥 틈(보스–센서 윗면) | 6.12 / 3.45 mm | 8.46 / 3.56 mm | ≥ 3.0 |
| 건반 밑면–센서 바 (바닥) | 3.38 mm | 3.12 mm | |
| 움직이는 부품 최소 틈 | 1.06 mm (링 뒤 ↔ 뒷벽) | | ≥ 1.0 |
| 백건 윗면 / 가장 높은 움직임 / 커버 | z43.5 / z56.9 (ff) / **z66** | | v3 커버 z59 |
| 프레임 깊이 / 전체 깊이 | 212 / 410 (변화 없음) | | |

재타건 속도의 가정: 바닥에서 손을 떼고, 센서 위치로 40 % 올라왔을 때 다시 일정한 손가락 힘으로 누르며, 바닥 펠트에 닿으면 다시 뗀다(6회 반복, 마지막 3주기 평균). 1.5 N(153 gf)에서는 12.0 Hz로 목표에 못 미치고, 약 1.75 N부터 13.3 Hz를 넘는다. 보조 스프링은 1.5 N 재타건 속도를 바꾸지 못한다(돌아올 때 도운 에너지를 누를 때 손가락이 다시 낸다) — §9.

## 3. 좌표표 (정지 = 펠트가 막 닿은 설계 위치, 바닥 = 앞 펠트 첫 접촉)

### 백건 (D) — 건반 3.351°, 해머 10.43°

| 점 | 정지 (y, z) | 바닥 (y, z) | 비고 |
|---|---|---|---|
| 건반 봉 중심 (고정) | (171.00, 40.00) | 같음 | Ø3 SUS304, 핀 24장 관통 |
| 해머 봉 중심 (고정) | (127.55, 15.00) | 같음 | Ø3 SUS304, 핀 24장 관통 |
| 건반 윗면 앞끝 | (0.00, 43.50) | (0.09, 33.50) | 딥 10.0 |
| 손가락 점 (DW 측정) | (13.00, 43.50) | (13.07, 34.26) | |
| 앞 다운스톱 접촉 | (6.60, 23.50) | (7.85, 13.92) | v3 앞 레일 펠트 3T |
| 크로스바 윗면 = 훅 접촉 (업스톱) | (87.50, 25.10) | (88.51, 20.25) | 훅 펠트 z25.1–28.1 |
| 자석 면 중심 | (65.80, 23.50) | (66.94, 17.38) | 센서 소자 y67 z12.68 |
| 러그 중심 (R3) | (108.73, 19.92) | (110.01, 16.31) | |
| 러그–패드 접촉점 | (108.00, 17.01) | (109.82, 13.32) | 패드 = 해머 코의 펠트 1T |
| 건반 무게중심 | (78.53, 36.02) | (78.93, 30.62) | 21.9 g |
| 해머 무게중심 | (188.74, 27.27) | (185.51, 38.15) | 49.0 g |
| 추(평철) 무게중심 | (194.50, 28.50) | (190.95, 40.40) | 42.4 g |
| 추 앞-아래 / 앞-위 | (182.0, 16.5) / (182.0, 40.5) | (180.83, 26.34) / (176.48, 49.94) | |
| 추 뒤-위 (가장 높은 점) / 뒤-아래 | (207.0, 40.5) / (207.0, 16.5) | (201.07, 54.47) / (205.41, 30.86) | |

### 흑건 (C#) — 건반 4.574°, 해머 10.43°

| 점 | 정지 (y, z) | 바닥 (y, z) | 비고 |
|---|---|---|---|
| 건반 윗면 앞끝 | (52.50, 55.50) | (51.64, 46.00) | 딥 9.5 |
| 손가락 점 (DW 측정) | (62.50, 55.50) | (61.61, 46.80) | |
| 앞 다운스톱 접촉 | (55.85, 23.50) | (57.53, 14.37) | v3 흑건 스톱 펠트 3T |
| 크로스바 = 훅 접촉 | (87.50, 25.10) | (88.95, 18.49) | |
| 자석 면 중심 | (64.20, 23.50) | (65.86, 15.04) | 소자 z10.15 |
| 러그 중심 (R3) | (96.73, 22.91) | (98.33, 17.04) | |
| 러그–패드 접촉점 | (96.00, 20.00) | (98.14, 14.05) | |
| 건반 무게중심 | (105.40, 40.19) | (105.59, 34.95) | 15.8 g |
| 해머 무게중심 | (188.37, 27.90) | (185.03, 38.70) | 46.1 g |
| 추 무게중심 | (194.50, 29.50) | (190.77, 41.38) | 38.9 g (22 mm, 밑에 2 mm 심) |

고정면: 스톱 레일 펠트 면 z55.50 (y178–209), 받침판 펠트 면 z15.70 (y180.4–209, 건반을 뺐을 때만 추가 닿음), 훅 아랫면 z28.1 (y84–91), 바닥 z5.0, 커버 z63.5–66.0.

### 해머 윤곽 (정지, 월드 y, z; 백건용. x 두께는 괄호)

- 코 패드 (8.0): (93.5,14.6) (113.0,9.7) (113.0,14.7) (93.5,19.6) — 윗면 14° 기울임, 펠트 1T. 패드 법선이 누르는 동안 늘 뒤쪽(+y)을 향해 건반을 봉 쪽으로 민다(정지 0.37 N → 바닥 0.10 N).
- 앞팔 (8.0): (113.0,9.7) (119.5,11.0) (119.5,19.0) (113.0,14.7)
- 보스 (8.0): y119.5–135.5, z11–19, 아래로 열린 Ø3 스냅 홈(목 2.8)
- 뒷팔 (6.0): (135.5,11.5) (180.4,17.5) (180.4,24.5) (135.5,18.5) — 누르면 건반 속(내폭 ≥ 8.6)으로 들어간다
- 추 링 (10.6): y180.4–207.8, z16.5–40.5, 옆벽 0.8, 앞면 9 mm 뒤 경사(건반 봉 핀과 틈 1.49)

## 4. 동작과 소음

| 충돌 | 부딪히는 면 | 계산값 | 대책 |
|---|---|---|---|
| 누름 끝 (건반) | 앞 펠트 3T (v3) | pp 0.10 mm/4 N, ff(6 N) 0.35 mm/15 N | v3와 같음 |
| 누름 끝 (추) | 스톱 레일 펠트 3T, 9×25 면 전체 | ff 0.87 mm/50 N, 10 N 타건 1.10 mm/70 N; 추 최고 z56.5 < 레일 58.5 | 면 접촉·두꺼운 펠트, 레일 5 mm |
| 추가 튕긴 뒤 러그 재착지 | 패드 펠트 1T | 떨어지는 거리 0.21–0.42 mm | 펠트 + 흑연 |
| 손 뗀 뒤 복귀 | 훅 펠트 3T | 충돌 에너지 3.9 mJ (v3 설계 4.8 mJ), 되튐 0.67 mm, 러그–패드 틈 0 | 결합부가 벌어지지 않음 |
| 건반을 뺐을 때 | 받침판 펠트 1T | 추가 0.8 mm 내려앉음 | |

결합부 유격: 0. 러그는 틈이 있는 홈이 아니라 해머 무게로 눌린 한쪽 접촉이다(누르는 힘 정지 백 1.51 N / 흑 0.86 N, 바닥 1.58 / 0.89 N). 자유 복귀 시뮬레이션에서 러그–패드 틈은 백·흑 모두 0.000 mm(보조 스프링을 넣은 흑건만 0.003 mm).

## 5. 부품표 (옥타브 1개)

| 부품 | 종류 | 수 | 질량 | 크기 / 비고 |
|---|---|---|---|---|
| 프레임 (콤 핀 24+24장 포함) | 출력 PETG | 1 | 178 g | 168.5×212, v3 척추 레일·뒤 스톱 레일 삭제 |
| 받침판 (제어 기판 덮개 + 추 휴지 펠트) | 출력 | 1 | 9 g | 164.5×28.6×1.2, 나사 2 |
| 스톱 레일 (앞 세움턱 3×3.5) | 출력 | 1 | 21 g | 164.5×31×5, 뒷벽 위 M3×10 3개 |
| 뒤 커버 | 출력 | 1 | 48 g | 윗면 z66 (v3 +7) |
| 센서 바 | 출력 | 1 | 17 g | v3 그대로 |
| 백건 | 출력 | 7 | 21.6 g | 22.5×174.5×20, 뒤 혀 슬롯(+y로 열림, 목 2.8) |
| 흑건 | 출력 | 5 | 15.5 g | 11×122×32, 같은 혀 |
| 해머 | 출력 | 12 | 6.6 g | 114.3×10.6×31, 옆으로 눕혀 출력 |
| 흑건 추 심 | 출력 | 5 | 0.56 g | 9×25×2 |
| 추 (평철 9×25 조각) | 구매 | 7 + 5 | 42.4 / 38.9 g | 24 mm / 22 mm, 링에 압입 + 에폭시 |
| SUS304 Ø3 봉 | 구매 | 2 | 9.1 g | 164 mm |
| M3×10 | 구매 | 5 | | 스톱 레일 3 + 받침판 2, PETG 직결 |
| 자석 Ø5×2 N35, DRV5055A2 | v3 | 12 | | 변화 없음 |
| 펠트 | v3 재고 | | | 패드 1T ×12, 스톱 3T 25×164, 받침 1T, 훅 3T ×12, 앞 펠트 |

출력물 34개, 구매 부품 19개(봉 2, 추 12, 나사 5) / 옥타브. 강철은 옥타브당 509 g, 88건반 3.74 kg.

## 6. 구매 (88건반 기준)

| 품목 | 사양 | 수량 | 금액 | 출처 |
|---|---|---|---|---|
| SUS304 연마봉 Ø3 × 1 m | 건반·해머 축 | 3 | 28,800 | 배관몰 baegwan.net (Φ3×1M 9,600원, 2026-09-27 확인) |
| 착불 배송비 | | 1 | 4,000 | 추정 |
| 평철 SS400 9×25, 1 m | 백 24 mm ×52 + 흑 22 mm ×36 | 3 | 18,000 | 추정 (소량 절단 판매처 가격 미확인) |
| 평철 배송비 | | 1 | 4,000 | 추정 |
| 5분 에폭시 | 추 고정 | 1 | 3,500 | 추정 |
| 흑연 가루 | 패드 마찰 0.25 → 0.15 | 1 | 3,000 | 추정 |
| M3×10 추가 | 스톱 레일·받침판 | 40 | 2,400 | v3 굿나잇몰 단가 |
| 빠지는 것: M3×40, 세트스크루, 황동 원판, M4 와셔 32, M3 너트 63 | | | −18,509 | v3 구매목록 |

기본 구성 변화 **+45,191원 → 583,219 → 628,410원** (한도 100만원). 공구: 쇠톱·줄(평철 88번 자르기) 또는 절단 주문. 1.5 mm 렌치는 필요 없어짐.

## 7. 출력 계획 (PETG, 0.4 노즐, 0.2 층, 220×220 베드)

- 모듈당 584 g, 39.0 h. 88건반(모듈 7 + 끝 부속, 낭비 10 %) 4.81 kg, 321 h. (v3 건반부 4.13 kg / 275 h, 방법 D 7.6 kg / 304 h)
- 판 배치: 프레임 168.5×212 한 판 / 백건 7개 나란히 164.5×174.5 (윗면을 베드에) / 흑건 5개 55×122 / 해머 6개씩 옆으로 눕혀 204×114 두 판 / 스톱 레일·받침판·커버·센서 바·심 한 판씩. 모두 220×220 안.
- 콤 핀(1.6 T)은 세워 출력되고, 봉 구멍 Ø3.1을 뚫린 채 출력한 뒤 Ø3 드릴로 한 번에 리밍한다.
- 해머 링 안 치수 9.1×25.1(크러시 리브 0.15), 출력 뒤 평철을 눌러 넣고 에폭시 한 방울.

## 8. 조립과 분리

1. 프레임 바닥 EVA를 붙일 때 리본 길(폭 20, y77–182)을 오려 내고, 리본을 프레임 바닥 **밑**으로 지나게 한다(콤 핀이 바닥 위를 막기 때문).
2. 제어 기판(70×28로 줄임, 4067은 헤더 소켓 없이 평납땜, 부품 ≤ z13)을 y181–209에 놓고, USB-C는 v3처럼 뒷벽 개구로 낸다. 받침판(펠트 1T)을 나사 2개로 덮는다.
3. 두 콤에 Ø3 봉을 옆면에서 밀어 넣고 끝 마개로 막는다(PTFE 그리스 소량).
4. 평철을 24 mm(52개)·22 mm(36개)로 자르고 버를 없앤다. 흑건 해머에는 2 mm 심을 먼저 넣고 추를 압입 + 에폭시. 코 패드에 펠트 1T + 흑연.
5. 해머를 해머 봉 위에서 눌러 스냅(추는 받침판 펠트 위에 0.8 mm 뜬다).
6. 스톱 레일 밑에 펠트 3T 띠를 붙이고 뒷벽 위에 M3×10 3개.
7. 건반: 자석 압입(v3), 건반을 해머 코 위에 얹고 **4 mm 뒤로 밀면** 혀 슬롯이 건반 봉에 스냅되고 크로스바가 훅 밑으로 들어간다.
8. 커버를 스냅으로 끼운다. y13에서 47–50 g 확인(가벼운 건반은 해머 링 옆에, 무거운 건반은 건반 앞 바닥판에 텅스텐 퍼티).

**건반 하나 빼기(공구·커버 분리 없음):** 건반을 4 mm 앞으로 당겨 스냅을 풀고 앞을 조금 들어 앞으로 뽑는다. 혀 윗면 z43.5가 커버 앞 가림판(아래끝 z44.5, 흑건 노치 그대로) 밑을 지난다. 해머는 받침판 위로 내려앉는다.
**해머 빼기:** 건반을 뺀 뒤 커버와 스톱 레일(나사 3)을 떼고 위로 뽑는다.

## 9. 스프링 판단 ("필요하다면")

계산상 **필요 없다.** 선택 사항으로 스톱 레일에 Ø5 구멍을 뚫어 두고, SUS 선경 0.25 / 외경 4.0 / 18회 / 자유장 12.5(k 0.0355 N/mm) 압축 스프링을 넣으면 추 행정의 마지막 40 %에서만 추를 눌러(정지 시 하중 0) 완전 복귀가 백 63.6 → 56.4 ms, 흑 60.8 → 53.8 ms로 줄어든다. 대신 바닥 근처에서 힘이 48 → 69 g으로 커져 "턱"이 생기고, 일정한 손가락 힘(1.5 N)의 재타건 속도는 12.0 Hz 그대로다. 재타건을 빠르게 하는 것은 스프링이 아니라 m_eff를 낮추는 것뿐이다(§12 표).

## 10. 무엇을 뺐나

- 그랜드 대비: 해머 섕크·이스케이프먼트(잭·렛오프)·리피티션 레버·백체크·댐퍼·캡스턴 나사·밸런스 핀/펀칭·프런트 핀을 모두 뺐다. 건반 + 추 레버 하나, 축 2개만 남았다.
- GHS/카시오 대비: 러버 돔 스위치(홀센서가 건반을 직접 읽음), 러그를 가두는 홈(한쪽 접촉 + 해머 예압으로 바꿈), 금속 섀시, 해머 아래 스펀지(추는 평소 공중에 떠 있고 받침은 건반을 뺐을 때만 씀)를 뺐다.
- v3 대비: 리프·척추·척추 레일·세트스크루·M3×40 클램프·황동 원판·뒤 두 번째 바닥을 뺐다. 늘 휘어 있는 플라스틱이 없다(정지 응력 6 MPa → 최대 0.53 MPa).
- 방법 D 대비: 추를 건반 **밑**이 아니라 건반 봉 **뒤**에 두어 건반 높이가 z58 → z43.5 그대로이고, 해머 자석도 필요 없다(건반 자석을 v3 센서가 그대로 읽음). 필라멘트 7.6 → 4.8 kg.

## 11. v3와 바뀌는 인터페이스

- 뒤 커버 윗면 z59 → **z66**(+7), 커버 뒤 스커트 7 mm 길어짐, 뒷벽 윗면 z56.5 → z58.5(스톱 레일 자리).
- 제어 기판 70×50 → 70×28, 위치 y181–209(v3 y145.5–195.5), 4067 평납땜, 받침판 밑.
- 리본: 바닥 위 차선(x60–82) → 바닥 밑 EVA 홈.
- 프레임: 척추 레일(y196–209)·뒤 스톱 레일(y138–144) 삭제, 건반 콤 핀(y165–175)·해머 콤 핀(y118.5–136.5) 추가.
- 건반: 콤(7개·5개 한 덩어리) → 낱개. 리프 대신 혀 슬롯, 밑에 러그.
- y146 앞(센서 바, 자석, 앞 펠트, 흑건 스톱, 탭·훅)과 폭 1254·깊이 410은 그대로. 건반 보관함(338.8×172×77)에는 낱개 건반을 x 방향으로 눕혀 넣는다.

## 12. 왜 커버가 올라가나, 그리고 대안

- 추가 해야 할 일은 "손가락 일 = BW × 행정 + 건반 위치에너지"를 위치에너지로 갚는 것이다. 9×25 직사각 추의 높이와 상승량을 나눠 쓰면 가능한 위치에너지는 ρ·w·L·(B/2)²에 비례한다(B = 받침판 z16.5에서 스톱 펠트까지). 같은 형상에서 커버 z59면 추 17 mm·DW 30.4 g, z62면 20 mm·37.8 g, z66이어야 24 mm·47.7 g이다. 추 밑의 제어 기판이 B를 7.5 mm 먹는다.
- 트레이드오프(건반 봉 y171, DW ≥ 47.5가 되는 가장 낮은 커버): 러그 y106 → 커버 z64.5, 추 35.3 g, m_eff 109, 완전 복귀 68.3 ms, 11.2 Hz / y108 → z66.0, 42.4 g, 92.5, 63.6 ms, 12.0 Hz / y110 → z68.0, 49.5 g, 81.6, 60.3 ms, 12.6 Hz / y112 → z71.0, 57.4 g, 75.2, 57.7 ms, 12.9 Hz (재타건은 1.5 N 기준).
- 대안 H1-B: 건반 봉을 y164로 당기고 9×32 평철(L32)을 쓰면 커버 z61(+2)에서 DW 47.0, m_eff 96.6, 완전 복귀 65.1 ms, 최소 틈 1.09. 대가는 앞뒤 힘 비 1.95 → 2.04와 자석 이동 6.12 → 5.95, 그리고 v3 앞쪽 운동이 조금 달라지는 것.

## 13. 위험과 단계 0 시험

위험: (1) 러그–패드 미끄럼(행정당 백 1.50, 흑 2.23 mm)의 마찰 계수가 불확실하다 — μ 0.10/0.25/0.35에서 백 DW 46.3/50.5/53.3, UW 37.1/32.6/29.5. 패드 펠트가 10⁶회에 닳을 수 있다. (2) 스톱 레일은 ff 타건마다 50–70 N을 받는다(굽힘 6.1–8.6 MPa, 순간). (3) 해머가 옆으로 ±0.84 mm 흔들려 이웃 링과 최악 0.94 mm — 비비면 소리. (4) 평철 88조각 절단 품질·링 압입. (5) 커버 +7 mm. (6) 훅 펠트가 오래 눌리면 건반 높이가 v3처럼 조금 올라감(훅 하중 백 0.77 N). (7) 1.5 N 손가락 힘에서 재타건 12 Hz.

단계 0 (반증 시험, 약 2일):
1. 3건반 쿠폰(백·흑·백, 프레임 조각 + 진짜 봉·추): y13 DW/UW를 동전 추로 측정. **UW < 25 g 또는 DW−UW > 16 g이면 불합격.**
2. 휴대폰 240 fps로 바닥에서 손 뗀 뒤 완전 복귀 측정. **75 ms를 넘거나 복귀 때 "덜걱" 두 번 소리가 나면 불합격.**
3. 패드 재료 3종(펠트 1T / 펠트 + 흑연 / PTFE 테이프) 경사판 마찰 계수 비교.
4. 스톱 레일 조각에 10 N 타건 10⁴회(캠 지그) → 균열·펠트 영구 눌림 < 0.3 mm.
5. 건반 혀 스냅 빼는 힘 2–5 N, 해머 보스 스냅, 봉 리밍 뒤 24장 핀 정렬.
6. ff 연타 소리 녹음을 v3 리프 쿠폰과 비교.
