WongyuKoh/Toccata/hardware/mechanical/key-action-v4/concepts/K1/design.md

# K1 — 뒤축 건반 + 강철 압축 스프링 + 관성 추 (부품 최소 기준안)

모든 수치는 `calc.py`가 계산하고 `results.txt`에 찍은 값이다. 단위 mm, g, N, ms. 좌표는 brief와 같다(z = 0 책상면, y = 0 백건 립 앞끝, +y 뒤쪽).

## 1. 한 줄 요약과 동작

- 레버는 건반 하나뿐이다. 건반 뒤끝(y200, z33.5)이 옥타브당 1개인 **Ø5 S45C 연마봉**에 걸려 돈다.
- **강철 압축 스프링**이 프레임 바닥(z5)에서 건반 꼬리 속(y138)을 밀어 올려 건반을 되돌린다. 플라스틱은 상시 힘을 거의 받지 않는다(정지 시 최대 0.89 MPa).
- 백건 머리 속에는 **16×16×34 사각봉(68.3 g)**, 흑건 앞쪽 속에는 **6×19×47 평철(42.1 g)**을 출력 중 멈춤(pause)으로 넣어 완전히 가둔다. 이 추가 관성을 만든다.
- 스프링 예압이 건반 무게와 추 무게를 함께 들어 올리므로 누르기 시작하는 힘은 50 g이다. 추의 무게는 손끝에 느껴지지 않고 **관성만** 남는다.
- 정지 높이는 앞쪽 훅 펠트(v3와 같은 수평 훅)가 정하고, 바닥은 앞 펠트가 정한다. 연결부(커플링)가 없으므로 Casio 블로그의 "덜걱" 소리 원인이 없다.

## 2. 건반 좌표표 (정지 → 끝까지 눌림 = 딥 펠트 첫 접촉)

### 백건 (D 건반 대표, 회전 2.862°)

| 점 | 정지 (y, z) | 바닥 (y, z) |
|---|---|---|
| 회전축 (고정) | (200.0, 33.5) | 고정 |
| 윗면 앞끝 (딥 기준) | (0.0, 43.5) | (−0.2, 33.5) |
| 손가락 점 (DW/UW) | (13.0, 43.5) | (12.7, 34.1) |
| 무게중심 (건반+추) | (37.9, 33.5) | (38.1, 25.4) |
| 스프링 위 시트 (윗판 밑면) | (138.0, 40.9) | (137.7, 37.8) |
| 스프링 아래 시트 (고정) | (138.0, 5.0) | 고정 |
| 업스톱 크로스바 윗면 | (43.2, 25.1) | (43.9, 17.3) |
| 다운스톱 패드 중심 (밑면) | (7.5, 23.5) | (8.2, 13.9) |
| 센서 자석 면 중심 | (65.8, 24.1) | (66.4, 17.4) |
| 뒤 팔 윗면 (y146) | (146.0, 43.5) | (145.6, 40.8) |
| 포크 끝 | (204.0, 33.5) | (204.0, 33.7) |
| 사각봉 16×16×34 | y4.0~38.0, z24.5~40.5 | 건반과 함께 회전 |

프레임 쪽: 업스톱 펠트 자유면 z24.63, 훅 손가락 z27.63~29.63 (y42.50~45.50, 두께 2.0), 가이드 탭 y45.5~50.5 (폭 7.5 + 부싱 펠트 0.5T 양쪽), 다운스톱 펠트 윗면 z13.90 (레일 윗면 z10.90, 펠트 y3~12), 스프링 가이드 기둥 Ø3.2 z5~20.

### 흑건 (C# 대표, 회전 3.675°)

| 점 | 정지 (y, z) | 바닥 (y, z) |
|---|---|---|
| 회전축 (고정) | (200.0, 33.5) | 고정 |
| 윗면 앞 모서리 (딥 기준) | (52.5, 55.5) | (51.4, 46.0) |
| 손가락 점 (DW/UW) | (62.5, 55.5) | (61.4, 46.6) |
| 무게중심 (건반+추) | (87.9, 41.7) | (87.6, 34.5) |
| 스프링 위 시트 (윗판 밑면) | (138.0, 53.5) | (136.8, 49.5) |
| 스프링 아래 시트 (고정) | (138.0, 5.0) | 고정 |
| 업스톱 크로스바 윗면 | (105.0, 25.1) | (105.7, 19.0) |
| 다운스톱 패드 중심 | (55.1, 23.5) | (56.0, 14.2) |
| 센서 자석 면 중심 | (64.2, 23.7) | (65.1, 15.0) |
| 뒤 팔 윗면 (y146) | (146.0, 43.5) | (145.5, 40.0) |
| 포크 끝 | (204.0, 33.5) | (204.0, 33.8) |
| 평철 6×19×47 (세워서) | y53~100, z33~52 | 건반과 함께 회전 |

프레임 쪽: 업스톱 펠트 자유면 z24.59, 훅 손가락 z27.59~29.59 (y104.25~107.25), 가이드 탭 y107.3~115, 다운스톱 펠트 윗면 z14.23 (레일 z11.23, 펠트 y51.5~58.7 — v3 자리), 스프링 가이드 기둥 Ø3.2 z5~30.

### 건반 몸체
- 백건: v3와 같은 아래가 열린 U채널(윗판 2.6, 벽 1.2). 머리 y0~50 폭 22.5, 꼬리 벽은 y144에서 끝(제어 기판 위를 피함), y144~196은 폭 10, 높이 z29.5~43.5의 뒤 팔. 추 공간 y2.7~38.5(바닥 1.0이 다운스톱 패드), 가이드 리브 2장 y40~50.5(슬롯 8.6), 크로스바 y41.5~45 z23.5~25.1.
- 흑건: 밑폭 11·윗폭 9.5, 몸체 벽 y51.5~144, 뒤 팔 y144~196(폭 9). 평철 받침판 z32~33(y52.7~101), 크로스바 y103.25~106.75.
- 뒤끝 포크: 폭 6, y194~204, z28~39, 뒤로 열린 슬롯 5.05(축 Ø5). 슬롯 끝 뒤에 Ø5×2 N35 고정 자석(센서 자석과 같은 품목)이 축을 끌어당겨 앉힌다.

## 3. 스프링 (피아노선 SWP-A, 양끝 닫힘·연마)

| | 백건 | 흑건 |
|---|---|---|
| 선경 × 외경 | 0.45 × 5.5 | 0.45 × 5.0 (외경이 달라 섞이지 않음) |
| 유효 권수 / 총 권수 | 40 / 42 | 75 / 77 |
| 자유장 L0 | 84.1 | 85.0 |
| 스프링 상수 | 0.0781 N/mm | 0.0570 N/mm |
| 설치 길이 정지 → 바닥 | 35.90 → 32.79 | 48.50 → 44.48 |
| 힘 정지 → 바닥 | 3.77 → 4.01 N (+6.4 %) | 2.08 → 2.31 N (+11.0 %) |
| 전단 응력 (바닥) | 638 MPa = 0.26 UTS | 335 MPa = 0.13 UTS |
| 밀착 길이 / 허용 변형 사용률 | 18.9 / 0.79 | 34.6 / 0.80 |
| 서지 주파수 | 157 Hz | 103 Hz |

- 흰·검 공용 스프링 하나는 계산으로 탈락: 흑건 시트가 z60 이상이어야 하고(흑건 윗판 밑면은 z53.5), 흑건 힘 상승이 17.2 g이 된다.
- 비틀림 스프링(축에 동축)도 계산했다: 선경 1.3이면 백건 상승 8.3 g로 압축과 비슷하고, 선경 1.2면 6.1 g로 더 평평하지만 굽힘 응력 0.79 UTS이며 코일이 건반 사이 8 mm에 들어가야 하고 건반 1개 분리가 어렵다. 그래서 압축 스프링을 택했다.
- 건반별 조정: 스프링 아래 0.5 mm 출력 와셔 1장 = 손끝 1.72 g(백) / 2.33 g(흑). 스프링 하중 공차 ±10 %면 손끝 ±12.7 g이므로 **설치 길이에서의 하중 공차를 지정해 주문**하거나 재서 나눠 쓴다.

## 4. 핵심 수치 (results.txt)

| 항목 | 백건 | 흑건 |
|---|---|---|
| DW / UW 누르기 시작 (손가락 점) | 50.0 / 43.6 g | 50.0 / 44.3 g |
| DW / UW 바닥 | 58.9 / 52.4 g | 62.2 / 56.5 g |
| 마찰 (손끝 환산) | 3.2 g (축 0.8 + 자석 0.7 + 가이드 1.6 + 스프링 0.1) | 2.8 g |
| 마찰 3배일 때 DW / UW | 56.4 / 37.0 g | 55.6 / 38.6 g |
| m_eff 앞끝 (y0 / 흑 y52.5) | 65.2 g | 37.2 g |
| m_eff 손가락 점 (y13 / 흑 y62.5) | 74.5 g | 42.9 g |
| 바닥 → 40 % 복귀 (재타건 가능) | 33.1 ms | 23.5 ms |
| 완전 복귀 (업스톱 접촉) | 51.1 ms | 35.9 ms |
| 재타건 속도 (150 / 300 gf로 다시 누름) | 17.3 / 20.7 Hz | 23.9 / 28.7 Hz |
| 앞/뒤 힘 비 (y90 ÷ y13) | 1.70 | — |
| 자석 이동량 / 바닥 간격 | 6.69 / 4.70 mm | 8.68 / 4.90 mm |
| 자기장 (축 위) 정지 → 바닥 | 3.7 → 31.9 mT | 2.3 → 29.2 mT |

- 스프링이 없으면 건반은 돌아오지 않는다(추 때문에 앞이 무겁다: 백 +148 N·mm).
- 같은 관성에 일정한 힘(중력식)으로 되돌리면 완전 복귀 54.8 ms(백). 스프링의 상승분이 3.7 ms를 줄인다.
- 관성을 더 늘리면: 사각봉 60 mm(가상, 강철 120.6 g)에서 m_eff 94.3 g(y13에서 107.8 g), 완전 복귀 60.4 ms, 재타건 14.5 Hz. 즉 이 구조로 **완전 복귀 60 ms 안에서 앞끝 m_eff 약 93 g까지** 가능하지만 앞 업스톱을 두려면 머리 속에 34 mm까지만 들어간다.
- v2.0의 "중력 복귀 약 40 ms 고정" 주장은 틀렸다: 복귀 시간은 √(m_eff / (BW − 마찰))에 비례한다(47 g → 50 ms, 128 g → 83 ms).

## 5. 부품표

### 옥타브당 출력물 (15개, 477 g, 약 31.8 h)
| 부품 | 수량 | g/개 | 비고 |
|---|---|---|---|
| 백건 | 7 | 24.0 | 윗면을 베드에, z19.0에서 멈춤 → 사각봉 넣기 |
| 흑건 | 5 | 16.6 | 윗면을 베드에, z22.5에서 멈춤 → 평철 넣기 |
| 프레임 | 1 | 165 | v3 175 g − 척추 레일 18.9 − 뒤 스톱 레일 9.1 + 핀 콤 15.6 + 스프링 기둥 2.1 |
| 센서 바 | 1 | 17 | v3 그대로 |
| 뒤 커버 | 1 | 44 | v3 그대로 |
| (선택) 조정 와셔 0.5 mm | 필요한 만큼 | — | 스프링 아래 |

### 옥타브당 구매 부품 (동작 관련 37개)
압축 스프링 12(백 7, 흑 5), 사각봉 7, 평철 5, Ø5 축 1, 고정 자석 12. 센서·자석·기판·펠트는 v3와 같다.

### 88건반 합계
- 필라멘트 3.90 kg(낭비 10 % 포함), 약 260 h(15 g/h). v3 4.13 kg / 275 h보다 조금 적다.
- 강철: 추 5.07 kg + 축 8개 + 스프링 = 5.27 kg. 모듈 무게 0.59 → **1.28 kg**.
- 220×220 베드: 백건 7개 168×204(높이 20), 흑건 5개 65×152.5(높이 32), 프레임 168.5×212(높이 36.5) — 모두 들어간다.

## 6. 조립 (옥타브 하나)
1. 건반 출력: 멈춤 층에서 추를 넣고 이어서 출력(바닥 1.0이 추 위를 브리지로 덮는다). 추가 흔들리면 CA 한 방울.
2. 센서 자석(백 0.57 mm, 흑 0.23 mm 안으로 들어가게)과 포크 고정 자석을 밑면 포켓에 압입 + CA.
3. 프레임: EVA 바닥(리본 차선 x60~82, y128~146 구간은 EVA를 22 mm 폭으로 따내 리본을 바닥판 밑으로 통과), 앞 펠트(백 y3~12, 흑 y51.5~58.7), 훅 펠트 12조각, 탭 부싱 펠트 0.5T.
4. Ø5 축을 핀 콤 13장에 끼운다(양끝 핀은 억지 끼움).
5. 스프링을 가이드 기둥에 꽂는다(백 외경 5.5, 흑 외경 5.0).
6. 건반 설치: 건반을 3.5 mm 앞쪽에 두고 스프링 위에 얹어, 살짝 누른 채 뒤로 3.5 mm 민다 → 크로스바가 훅 밑으로 들어가고 포크가 축에 "딱" 붙는다(자석).
7. y13 다운웨이트를 재서 와셔로 맞춘다. 센서 바·제어 기판은 v3 그대로. 뒤 커버를 끼운다.

**건반 1개 분리:** 뒤 커버를 뺀다(스냅) → 건반을 앞으로 3.5 mm 당긴다(자석 약 2 N 이상) → 들어낸다. 스프링은 기둥에 남는다. 공구 없음.

## 7. 소음 (모든 충돌)
- 다운스톱: 추가 든 건반이 펠트 3T(181 mm²)를 친다. 앞끝 0.3/0.6/1.0 m/s에서 2.9/11.7/32.6 mJ, 펠트 압축 25/38/50 %. 스프링 건반(m_eff 12 g)보다 5.4배 큰 에너지 → 더 묵직한 "툭".
- 업스톱(손을 뗄 때): 4.16 mJ(백) / 4.04 mJ(흑)가 훅 펠트 24 mm²로, 압축 40 %, 되튐 0.72 / 0.80 mm, 0.1 mm 안으로 가라앉기까지 97 / 102 ms.
- 스프링: 서지 157 Hz(백) / 103 Hz(흑). 멈출 때 "핑" 울림이 날 수 있다 → 가이드 기둥에 실리콘 그리스, 필요하면 기둥에 얇은 펠트 슬리브.
- 축: 자석이 포크를 축에 늘 붙여 슬롯 틈 0.05가 없어진다 → 덜걱임 없음. 흑건은 복귀 중 축 반력이 0을 지나지만 포크가 위아래를 모두 잡는다.
- 커플링 없음(레버 1개), 추는 완전히 갇힘.

## 8. v3 인터페이스 변경
- 리프·척추·클램프 나사·세트스크루·황동 원판·뒤 스톱 레일 → 없음. 그 자리(y190~205)에 핀 콤 + Ø5 축(y200, z33.5).
- 건반이 y204까지 길어짐(뒤 커버 밑). 백·흑 꼬리 벽은 y144에서 끝나고 뒤 팔은 z29.5 위로 올라가 제어 기판 부품(z20) 위 6.0 mm 이상 띄움.
- 스프링 기둥 12개(y138)를 프레임 바닥에. 리본 차선은 이 줄에서 바닥판 밑 EVA 홈으로 지나간다.
- 업스톱 훅·가이드 탭 위치: 백 y11.5~25 → y42.5~50.5, 흑 y77.5~91 → y104.25~115.
- 다운스톱 레일 윗면을 새 회전각에 맞춤(백 z10.90, 흑 z11.23). 백건 펠트 y1.5~10.5 → y3~12.
- 센서: 센서 바·기판·소자 위치 그대로. 자석만 0.57 / 0.23 mm 안으로 넣어 바닥 간격을 v3와 같은 4.7 / 4.9로 유지(이동량 6.69 / 8.68 mm로 v3보다 큼).
- 프레임 깊이 212, 전체 깊이 410, 뒤 커버 z59 그대로. 뒤 팔 윗면과 커버 가림판 사이 1.0.

## 9. 참고 구조와 비교해 뺀 것
- 그랜드: 해머·윕펜·잭·렙리션·댐퍼·백체크·밸런스 레일·앞 레일 핀·납 → 레버 1개 + 강철 추 1개 + 스프링 1개.
- GHS / Casio PX: 따로 도는 해머 레버와 그 축, 건반↔해머 연결 슬롯(떼는 소리의 원인), 고무 돔 스위치 → 없음.
- v3: 상시 약 6 MPa를 받던 PETG 리프, 척추 클램프, 세트스크루 → 없음.

## 10. 위험과 단계 0 시험
위험: 스프링 하중 공차(±10 % = ±12.7 g), 스프링 서지 울림, 바닥으로 갈수록 힘이 오름(백 +8.9 g, 흑 +12.2 g), 마찰이 작아 UW가 높음(43.6 g, 튀는 느낌), 강철 5.3 kg 추가, 흑건 관성이 백건의 약 0.57배, 자석 고정력 2 N은 추정값, 스프링 주문제작 가격 추정, 추 96개 절단.

단계 0 시험(하나라도 떨어지면 구조를 다시 본다):
1. 건반 2개(백·흑) 쿠폰 프레임: y13 DW 50±3, UW ≥ 40, 바닥 DW ≤ 62.
2. 센서 로그(5.9 kHz)로 손 뗀 뒤 40 % 복귀 ≤ 36 ms, 완전 복귀 ≤ 56 ms.
3. 포크 자석: 저울로 당겨 떼는 힘 ≥ 2 N, 1 N로 앞으로 끌어도 건반이 밀리지 않을 것. 모자라면 Ø6×3 자석 또는 닫힌 구멍 + 옥타브 단위 축 뽑기로 후퇴.
4. 100회 빠른 연타 녹음: 스프링 "핑", 업스톱 두 번 튐이 들리는지.
5. 스프링 10개를 설치 길이에서 하중 측정 → 편차로 분류·와셔 방식 결정.
6. 강철 추를 넣은 건반과 뺀 건반의 센서 곡선 비교, 이웃 건반을 눌렀을 때 신호 변화 ≤ 1 %.
7. 30일 정지 후 앞끝 높이 변화 ≤ 0.3 mm(펠트 압밀).

## 11. 구매 (88건반, v3.2 기본 583,219원 대비)
| 품목 | 사양 | 수량 | 단가 | 합계 | 출처 |
|---|---|---|---|---|---|
| 압축 스프링 백·흑 | 위 3절 사양 | 60 + 40 | — | 60,000 | 국내 소량 주문제작 — estimate |
| S45C 연마봉 Ø5 × 1 m | 164 mm × 8개로 절단 | 2 | 4,790 | 9,580 | 배관몰 baegwan.net (확인) |
| 배송비 (연마봉) | | 1 | 6,000 | 6,000 | 배관몰 안내 (확인) |
| SS400 사각봉 16×16, 34 mm 절단 | 백건 추 | 56 | 800 | 44,800 | estimate |
| SS400 평철 6×19, 47 mm 절단 | 흑건 추 | 40 | 700 | 28,000 | estimate |
| 네오디뮴 Ø5×2 N35 | 포크 고정 | 100 | 80 | 8,000 | dgmagnet (v3 L21 단가) |
| (빠짐) M3×40 34개, M3×10 세트 40개, 황동 원판 4봉, M3 너트 63개 | | | | −18,189 | v3 구매목록 |
| **차이** | | | | **+138,191** | 기본 721,410원 (한도 1,000,000) |

절단 없는 대안: 백건 5/8" 쇠구슬 2개(32.9 g, 베어링스토어 50개 5,100원 확인) + 흑건 5/16" 쇠구슬 5개 → m_eff 37.3 / 14.9 g, 완전 복귀 39.3 / 23.3 ms(표 2절). 가볍고 싸지만 피아노 관성은 절반.
