WongyuKoh/Toccata/hardware/mechanical/key-action-v4/concepts/S1/design.md

# S1 — 미니 시소 (밸런스 핀 시소 + 꼬리 강철 추, 백건만 보조 스프링)

모든 숫자는 `calc.py`를 돌린 `results.txt`에서 가져왔다(절 번호 [n]은 그 파일의 절). 좌표는 v3와 같다: x 가로, y = 백건 앞끝 0에서 뒤로 +, z = 책상 0에서 위로 +, 단위 mm·g·N·ms.

## 0. 한 줄 결론

212 mm 프레임 안에서 시소는 된다. 다만 **흑건만 순수 무게추로 돌아오고, 백건은 무게추가 복귀 힘의 48 %만 내고 나머지는 강철 압축 스프링(선경 0.4)이 낸다.** 백건까지 무게추만으로 돌리려면 회전축을 y122까지 앞으로 당겨야 해서 앞/뒤 힘 비가 3.55가 되거나([12a]), 프레임을 39~49 mm 늘리고 강철 7.8~9.6 kg을 써야 한다([12b]). 짧은 시소의 세 가지 약점이 모두 숫자로 나왔다: 앞/뒤 힘 비 2.60(v3 2.2), 백건 관성 19.4 g(GHS 약 100 g), 88건반 강철 9.0 kg.

## 1. 구조와 동작

```
 측면(백건 D, 정지)                       뒤 커버 z56.5~59
                                        ┌────────────────────────────┐
                                        │ 꼬리 스톱 바 z51.3~56.2     │ ← 뒷벽 홈에 끼우고 손나사 2개
                                        │  펠트3T(y185~197)  스프링자리 │
  손가락 y13                             └──────┬──────────────┬───────┘
  ▼  윗면 z43.5                                  ▼ (누르면 강철 막대가 올라와 펠트에 닿음 = 1차 바닥)
 ┌──────────────────────────────────────┬──────────────────────────┐ z44.2
 │ 백건 몸체(PETG, 아래 열린 U)          │█ 강철 9x32x50 (113 g) █ ○ │ ← ○ = 스프링 우물 Ø6.6
 │  훅▲   자석●                  핀◎ y140│█  y148~198             █ ○ │
 └──┬─────────────────────────────┬──┴──┴──────────────────────────┘ 용골 z11
    │v3 훅(정지=위 멈춤)  센서바 y59~77.5│밸런스 레일 y135~145 + 핀 받침 날개(홈 R1.5 + 천 0.5T)
  앞 펠트(2차 바닥, 0.5 늦게)   제어 기판 y94~133 (39x70)          뒷벽 y209~212
```

- 건반은 PETG 한 덩어리 시소다. y140에 박은 강철 평행핀 Ø3×10이 밸런스 레일 날개(두께 2.0) 윗면의 반원 홈(천 0.5T 라이닝)에 얹힌다. 날개는 건반 밑의 틈(폭 2.3)에 들어가 좌우도 잡는다. 핀 하중은 항상 아래로 향한다([8] R = 2.33 N).
- 꼬리(y146~206.5)에 강철 평철 9×32를 세워 넣는다(백건 50 mm·113 g, 흑건 37 mm·84 g). 누르면 앞이 내려가고 꼬리가 올라온다.
- 정지 위치: v3 앞 훅 그대로. 꼬리 무게(+백건 스프링)가 앞을 들어 건반 크로스바가 훅 펠트를 위로 누른 채 쉰다. 높이는 훅이 정하므로 펠트가 조금 눌려도 앞 높이는 거의 그대로다.
- 바닥: 1차 = 올라온 강철 막대 윗면이 꼬리 스톱 바 아래 펠트에 닿는다(무게추가 직접 멈춘다 = Casio의 "추가 위 스펀지에 닿음"과 같은 생각). 2차 = v3 앞 펠트가 0.5 mm 뒤에 닿아 손가락 힘을 받는다.
- 복귀: 흑건은 무게추만(중력 100 %). 백건은 무게추 48 % + 꼬리 끝 우물 속 압축 스프링 52 %([2-w]). 스프링이 부러져도 백건은 DW 25.3 g / UW 18.9 g로 여전히 돌아온다([4]).
- 센서는 v3 그대로(자석 y65.8/64.2, 소자 y67). 제어 기판은 꼬리 밑이 아니라 건반 앞팔 밑(y94~133)으로 옮겼다.

- 피아노의 앞 레일 핀 대신 v3 탭+훅을 그대로 쓴다. 탭 하나가 좌우 안내와 정지(위 멈춤)를 함께 하므로 둥근 핀을 따로 두면 정지용 부품이 하나 더 필요하다. 밸런스 레일 펀칭 펠트 대신 강철 핀 + 천 0.5T 홈을 쓴 이유는 하중을 받는 면을 딱딱하게 두어 높이가 펠트 눌림에 좌우되지 않게 하기 위해서다(앞 높이는 훅이 정하므로 홈 천이 조금 눌려도 자석 높이는 그보다 덜 변한다).

### 왜 정지는 앞 훅, 바닥은 꼬리인가 (핀이 튀지 않게)
꼬리가 무거운 시소가 앞 펠트에 부딪히면 핀이 위로 튕겨 나간다. [3]의 충격량(핀을 홈 쪽으로 누르면 +): 앞 펠트로만 멈추면 백건 −5147, 흑건 −6674(핀이 들림). 꼬리 펠트(타격 중심 앞, 백 112 mm·흑 71 mm 안쪽)로 멈추면 +3222 / +1302. 복귀도 앞 훅에 닿으면 +5251 / +7779인데, 피아노처럼 꼬리 끝 밑 백레일에 얹으면 −2210 / −474로 복귀 때마다 핀이 뜬다. 그래서 "정지 = 앞 훅, 1차 바닥 = 꼬리 펠트" 조합이다.

## 2. 목표 대비 핵심 수치 (brief §6)

| 항목 | 백건 (D) | 흑건 (C#) | 목표 / 비고 |
|---|---|---|---|
| 다운웨이트 DW (정지, 손가락 백 y13 / 흑 y62.5) | 50.0 g | 49.9 g | 47~55 |
| 업웨이트 UW (정지 근처 / 바닥에서 출발) | 42.4 / 50.0 g | 43.8 / 42.0 g | ≥ 20 |
| 균형 무게 / 마찰(정지 위치 DW−UW의 반) | 46.2 / 3.79 g | 46.8 / 3.05 g | 마찰: 핀 0.86, 탭 부싱 2.98 g |
| 앞끝(y0 / y52.5) DW / UW | 45.3 / 38.5 g | 44.1 / 38.9 g | |
| 바닥에서 DW (스프링 증가분) | 57.9 g | 47.9 g | 백 +16 %, 흑 −4 % |
| 유효 질량 m_eff (손가락 / 앞끝) | 19.4 / 16.0 g | 42.7 / 33.5 g | GHS ~100, C 47, 스프링 12 |
| 재타건점(센서 이동 40 % 복귀)까지 | 16.4 ms | 24.7 ms | 가정: 40 % 복귀 시 펌웨어 재타건 |
| 완전 복귀(훅 닿음) | 26.4 ms | 39.3 ms | < 60 ✓ |
| 재타건 속도 1/(2·t_rt) (손가락도 같은 시간) | 30.5 Hz | 20.3 Hz | ≥ 13.3 ✓ (손가락 0.3 m/s면 34.9 / 27.9 Hz) |
| 완전복귀 기준 1/(2·t_full) | 19.0 Hz | 12.7 Hz | 참고(흑건은 완전 복귀만 기다리면 13.3 미달) |
| 앞/뒤 힘 비 F(y90)/F(손가락) | 2.60 (130.2 g) | 1.56 (78.0 g) | v3 2.2, 그랜드 ~1.5 |
| 자석 이동 / 정지 틈 / 바닥 틈 | 5.27 / 10.82 / 5.55 | 8.07 / 13.35 / 5.28 | 이동 ≥ 5, 틈 ≥ 3.0 ✓ |
| 정지 시 플라스틱 최대 응력 | 0.664 MPa (프레임 훅) | | < 2 MPa ✓ |
| 복귀 후 훅에서 튐 / ±0.2 mm 안정 | 0.82 mm / 52.3 ms | 1.08 mm / 85.0 ms | 펠트 E 1.0 MPa, ζ 0.3 |
| 핀 들림(바닥 충돌, 손가락 속도 0.5/1.0/1.5 m/s) | 0.011 / 0.099 / 0.230 mm | 0.030 / 0.174 / 0.331 mm | 천 라이닝 홈에 다시 앉음 |
| 과주행(바닥 넘어 앞끝) 0.5/1.0/1.5 m/s | 0.63 / 0.78 / 0.94 mm | 1.16 / 1.55 / 1.95 mm | |

v2.0의 "무게추 복귀는 약 40 ms로 고정이라 13.3 Hz 불가" 주장 확인: 순수 무게추 변형([12c], y_b 122)의 백건 완전 복귀는 39.4 ms로 주장과 맞다. 추가 지배하는 시소에서는 가속도 ≈ g·UW/m_eff ≈ g·(앞팔/꼬리팔)이라 추 질량과 무관하다는 말도 맞다. 하지만 재타건을 40 % 복귀에서 하면 24.8 ms → 20.2 Hz로 13.3 Hz를 넘는다. 따라서 "완전 복귀를 기다리면 불가, 부분 복귀 재타건이면 가능"이 정확한 결론이다.

## 3. 좌표표 (정지 / 끝까지 누름), mm — [6]

회전 중심 = 핀 축 (140.00, 27.00). 끝까지 누른 각도: 백 4.079°, 흑 6.126°.

### 백건 (D)
| 요소 | 정지 (y, z) | 바닥 (y, z) |
|---|---|---|
| 핀 축(피벗) | (140.00, 27.00) | (140.00, 27.00) |
| 손가락점 | (13.00, 43.50) | (12.15, 34.42) |
| 앞 윗모서리(딥 10) | (0.00, 43.50) | (−0.82, 33.50) |
| 훅 접촉(크로스바 윗면, v3) | (12.25, 25.10) | (12.71, 16.02) |
| 앞 펠트 접촉(앞 바닥판 중심, v3) | (6.60, 23.50) | (7.19, 14.02) |
| 자석 면 중심 | (65.80, 23.50) | (66.24, 18.23) |
| 건반 전체 무게중심 | (159.61, 29.00) | (159.42, 30.39) |
| 강철 막대 중심 | (173.00, 28.20) | (172.83, 30.54) |
| 막대 윗면 앞/뒤 모서리 | (148.00, 44.20) / (198.00, 44.20) | (146.76, 44.73) / (196.63, 48.28) |
| 꼬리 펠트 접촉점 | (188.00, 44.20) / (196.00, 44.20) | (186.65, 47.57) / (194.63, 48.14) |
| 스프링 우물 바닥(스프링 아래 자리) | (202.50, 17.63) | (203.01, 22.10) |
| 용골 바닥 앞/뒤 | (146.00, 11.00) / (206.50, 11.00) | (147.12, 11.47) / (207.47, 15.77) |
| 꼬리 끝 윗면 | (206.50, 44.20) | (205.11, 48.89) |

### 흑건 (C#)
| 요소 | 정지 (y, z) | 바닥 (y, z) |
|---|---|---|
| 핀 축 | (140.00, 27.00) | (140.00, 27.00) |
| 손가락점 | (62.50, 55.50) | (59.90, 47.07) |
| 앞 윗모서리(딥 9.5) | (52.50, 55.50) | (49.96, 46.00) |
| 훅 접촉(v3) | (78.25, 25.10) | (78.81, 18.52) |
| 앞 펠트 접촉(v3) | (55.85, 23.50) | (56.70, 14.54) |
| 자석 면 중심 | (64.20, 23.50) | (65.01, 15.43) |
| 무게중심 | (173.74, 27.94) | (173.45, 31.53) |
| 강철 막대 중심 | (186.80, 26.21) | (186.62, 31.21) |
| 막대 윗면 앞/뒤 모서리 | (168.30, 42.21) / (205.30, 42.21) | (166.52, 45.14) / (203.30, 49.09) |
| 꼬리 펠트 접촉점 | (188.00, 42.21) / (196.00, 42.21) | (186.10, 47.24) / (194.06, 48.10) |
| 용골 바닥 앞/뒤 | (146.00, 9.01) / (206.50, 9.01) | (147.89, 9.75) / (208.04, 16.21) |
| 꼬리 끝 윗면 | (206.50, 42.21) | (204.50, 49.22) |

### 프레임 쪽 치수 — [6b], [7]
| 부위 | 값 |
|---|---|
| 백건 앞 펠트(2차 바닥) 윗면 | z13.24 @ y3.29 → z13.80 @ y11.09 (4.08° 경사), 레일 윗면 = 펠트 윗면 − 3.0 |
| 흑건 앞 펠트 윗면 | z13.70 @ y53.55 → z14.38 @ y59.85 (6.13°) |
| 꼬리 스톱 펠트 아랫면(1차 바닥) | z47.57 @ y186.65 → z48.14 @ y194.63 (4.08°), 펠트 3T 띠 y185~197, 스톱 바 z51.28~56.2 |
| 밸런스 레일 | y135~145, 윗면 z21.5, 날개 12장 두께 2.0 × y134.5~142.8, 날개 윗면 z27.0(홈 앞 평면 3.9 mm), 홈 PETG R2.0 바닥 z25.0 + 천 0.5T → 자리 R1.5 |
| 스프링(백건만) | 스톱 바 포켓 Ø6.6×3 @ y202.5, 윗자리 z54.28, 건반 우물 바닥 z17.63 |
| 제어 기판 | y94~133 × x47.25~117.25(5×7 만능기판을 39×70으로 자름), 부품 ≤ z15.0, 누른 건반 밑과 틈 백 5.24 / 흑 3.61 |
| USB 선 통로 | F 꼬리 밑 x71~80, z5~10.5 (백건 용골 z11) — 밸런스 레일·뒷벽에 같은 터널 |
| 뒤 커버 앞 가림판 | 아랫면 z44.5 → z46.5 (누른 꼬리와 틈 1.74). 흑건 솟은 부분은 y144에서 끝(누르면 z55.76, 커버와 틈 0.74) |
| 뒷벽 틈 | 누른 꼬리의 가장 뒤 점: 백 y207.47(틈 1.53), 흑 y208.04(틈 0.96) |
| 높이 범위 | 움직이는 가장 높은 곳 z55.5(흑건 윗면, 누르면 내려감), 가장 낮은 곳 z9.01(흑건 용골, 누르면 올라감), 꼬리 윗면 최고 z49.22 |
| 깊이 | 건반 y0~206.5, 프레임 212 그대로, 전체 410 그대로 |

### 건반 CAD 치수(계산 입력값)
- 공통: 윗판 2.0, 벽 1.2, 아래가 열린 U. 앞팔 밑면 z23.5, 백건 윗면 z43.5, 흑건 윗면 z55.5(v3).
- 백건: 머리 y0~50(폭 22.5), 좁은 몸 y50~134(v3 키별 폭, D 14.36 등), 피벗 보스 y134~146(속 75 %, 날개 홈 2.3×z23.5~29.5 아래 열림, 가로 구멍 Ø3.05 @ (140, 27) — 핀은 CA로 고정, 억지끼움 없음). 꼬리 y146~206.5는 164.5/12 = 13.708 균등 격자, 폭 12.708(틈 1.0). 꼬리 상자 z11.0~44.2, 바닥 1.2, 막대 주머니 y148~198(위로 열림, 안폭 10.3 — 막대 9와 에폭시로 고정), 막대 뒷벽 y198~199.2, 스프링 우물 Ø6.6 @ y202.5(바닥 z17.63), 꼬리 끝벽 y205.3~206.5.
- 흑건: 솟은 부분 y51.5/52.5~144(v3 단면), 아래 몸 y51.5~134(폭 11), 보스 y134~146(폭 11), 꼬리 y146~206.5(폭 12.708), 용골 z9.01, 꼬리 윗면 z42.21, 막대 주머니 y168.3~205.3(막대 9×32×37), 우물 없음.
- 자석·크로스바·앞 바닥판·가이드 리브: v3 치수 그대로.

## 4. 시소의 한계 — 숫자로 (왜 이 절충인가)

### 4.1 핀 위치 스윕 [11] (212 안, 막대 최대 + 스프링으로 DW 50)
| 핀 y | 백 막대 | 중력 몫 | 스프링 N | 앞/뒤 비 | 자석 이동 | m_eff | t_rt / t_full ms |
|---|---|---|---|---|---|---|---|
| 130 | 106 g | 61 % | 0.29 | 3.02 | 4.90 | 23.8 | 17.5 / 28.1 |
| 135 | 124 g | 64 % | 0.29 | 2.79 | 5.09 | 23.3 | 17.7 / 28.4 |
| **140** | **113 g** | **48 %** | **0.48** | **2.60** | **5.27** | **19.4** | **16.4 / 26.4** |
| 150 | 90 g | 21 % | 0.93 | 2.33 | 5.59 | 14.3 | 14.5 / 23.3 |
| 160 | 68 g | 1 % | 1.54 | 2.14 | 5.86 | 11.6 | 13.3 / 21.6 |

핀을 뒤로 보내면 앞/뒤 비와 자석 이동은 좋아지지만 꼬리가 짧아져 무게추가 하는 일이 사라진다(y160에서는 막대가 건반 앞팔 무게만 겨우 상쇄하는 1 %). y140이 흑건을 스프링 없이 순수 무게추로 돌릴 수 있는 가장 뒤쪽 위치이자 자석 이동 ≥ 5를 지키는 절충점이다.

### 4.2 순수 무게추 [12]
- 212 안: 막대(9×25, 스톡 폭 중 들어가는 가장 큰 것)만으로 DW 50에 닿는 가장 뒤 핀은 y122 — 앞/뒤 비 3.55, 자석 이동 4.57(< 5), 흑건 꼬리 11.0 mm 상승, 제어 기판 자리 21 mm뿐, 강철 7.0 kg. 전체 평가 [12c]: 백 t_rt 24.8 / t_full 39.4 ms(20.2 Hz), 흑 31.8 / 50.1 ms(15.7 Hz).
- 프레임을 늘리면: 핀 y150은 꼬리 y246.5까지(프레임 251, 전체 449, +39 mm, 강철 7.8 kg), 핀 y160은 y256.5(프레임 261, 전체 459, 강철 9.6 kg). +100 mm(전체 509)면 강철 3.1~3.9 kg, m_eff 59~67 g. 212 → 251 이상이면 프레임이 220 베드에 한 번에 들어가지 않는다.
- 결론: 짧은 시소는 "추 질량 ∝ (앞팔/꼬리팔)" 때문에 강철을 많이 먹고, 관성은 "추 × (꼬리팔/앞팔)²"이라 거의 안 늘어난다. 무게와 관성을 동시에 얻으려면 레버비로 증폭하는 해머(GHS·Casio식)가 맞는 구조다.

### 4.3 옵션 [10b] (백건)
| 옵션 | m_eff | 중력 몫 | 스프링 예하중 | t_rt / t_full | 비고 |
|---|---|---|---|---|---|
| 머리에 쇠구슬 Ø10 ×4(16.4 g) | 31.0 g | 17 % | 0.76 N | 20.9 / 33.5 ms | 흑건 42.7 g과 관성 차이를 줄임, 우물 z25.5로 가능 |
| 쇠구슬 ×8(32.9 g) | 41.6 g | −12 % | 1.02 N | 24.4 / 39.1 | 이 스프링으로는 바닥 근처 밀착 여유 부족(불가) |
| 평철 대신 쇠구슬 3층(자르기 없음) | 15.0 g | 19 % | 0.75 N | 14.4 / 23.2 | 강철 절반 |
| 백건 막대 없음(스프링만) | 9.7 g | −16 % | 1.07 N | 11.7 / 18.7 | 이 스프링으로 불가, 사실상 스프링 건반 |

## 5. 부품표 (옥타브 모듈 1개)

| 부품 | 종류 | 재료 | 1개 질량 | 수량 | 비고 |
|---|---|---|---|---|---|
| 백건 | 출력 | PETG 흰색 | 28.6 g | 7 | 윗면을 베드에, 서포트 없음 |
| 흑건 | 출력 | PETG 검정 | 23.0 g | 5 | 〃 |
| 프레임(바닥·앞 레일·훅/탭·흑건 스톱 레일·밸런스 레일+날개 12·뒷벽·기판 받침) | 출력 | PETG 회색 | 169 g | 1 | 164.5×212, v3에서 척추 레일 빼고 밸런스 레일 추가 |
| 센서 바 | 출력 | PETG | 16 g | 1 | v3 그대로 |
| 꼬리 스톱 바 | 출력 | PETG | 12 g | 1 | 164×23×4.9, 스프링 포켓 7 |
| 뒤 커버 | 출력 | PETG | 44 g | 1 | 앞 가림판 아랫면만 z46.5로 |
| 강철 막대 백건 9×32×50 | 구매(절단) | SS400 평철 | 113.0 g | 7 | 주머니에 에폭시 |
| 강철 막대 흑건 9×32×37 | 구매(절단) | SS400 평철 | 83.6 g | 5 | 〃 |
| 평행핀 Ø3×10 | 구매 | SUS | 0.56 g | 12 | 보스 구멍 Ø3.05 + CA |
| 압축 스프링 d0.4 OD6 L50 | 구매 | 피아노선/SUS | 0.73 g | 7 | 백건만, k 0.036 N/mm(계산), 설치 36.65 mm |
| 자석 Ø5×2 N35 | 구매(v3) | NdFeB | 0.29 g | 12 | v3와 같음 |
| M3 손나사 + 너트 | 구매 | 강 | — | 2+2 | 스톱 바 고정(공구 없이 분리) |
| 펠트 3T 띠(꼬리 스톱) 164×12 | 구매(v3 BOM 펠트) | 양모 | — | 1 | 가능하면 단단한 펠트(E ≥ 2.5 MPa → 핀 들림 0.028 mm) |
| 부싱 천 0.5T 조각(날개 홈) | 구매(v3 BOM) | 양모 천 | — | 12 | |

옥타브당 출력물 16개(v3 5개), 구매 부품 47개(막대 12, 핀 12, 스프링 7, 자석 12, 손나사 2, 너트 2 — 펠트·천 제외).

## 6. 출력 계획 [9]
- PETG: 옥타브 모듈 557 g → 37.1 h. 88건반 4.14 kg(+10 % 낭비 4.56 kg) → 304 h(15 g/h). v3는 5.0 kg·332 h.
- 모든 부품이 220×220에 들어간다: 프레임 164.5×212, 건반 길이 206.5(윗면을 베드에, 백건 22.5 폭이라 한 판에 8개, 흑건 12.7 폭이라 14개).
- 건반을 뒤집어 뽑으면 U 채널·막대 주머니·스프링 우물이 모두 베드 쪽이나 위로 열려 서포트가 필요 없다. 핀 가로 구멍은 물방울 모양(teardrop), 주머니 바닥(1.2)과 우물 바닥은 10.3 / 6.6 mm 브리지.
- 강철: 옥타브 1,225 g(막대 1,210 g = 7×113 + 5×84), 88건반 9.00 kg. 모듈 무게 약 1.87 kg(v3 0.59 kg). 평철 9×32 4.06 m(톱날 1.5 mm 포함) → 1 m ×5, 88번 절단.

## 7. 조립 순서와 건반 1개 빼기
1. 평철 9×32를 백건용 50 mm ×52, 흑건용 37 mm ×36으로 자르고(쇠톱 88회, 작업 시간은 추정 2~3시간) 모서리를 줄로 다듬는다.
2. 건반을 뽑고 자석(v3 방식), 평행핀(CA)을 붙인다. 막대를 주머니에 에폭시로 붙인다.
3. 프레임에 앞 펠트·훅 펠트(v3), 날개 홈에 천 0.5T, 스톱 바 아래 펠트 띠를 붙인다.
4. 백건 우물에 스프링을 넣는다(그리스 한 방울 — 울림 방지).
5. 건반을 제자리보다 3.5 mm 앞에 내려놓는다(핀은 날개 앞 평면에, 크로스바는 훅 앞에). 뒤로 3.5 mm 밀면 핀이 홈에 떨어지고 크로스바가 훅 밑으로 들어간다(v3 D12와 같은 동작).
6. 꼬리 스톱 바를 뒷벽 홈에 끼우고 스프링 윗끝을 포켓에 맞춘 뒤 손나사 2개를 돌린다. 뒤 커버를 끼운다.
7. 조정 [9]: 백건 DW는 우물 바닥 스페이서(1 mm당 +1.81 g), 흑건은 텅스텐 퍼티(ME14) — 꼬리(y192)에 1 g이면 +0.67 g, 앞(y57) 밑에 1 g이면 −1.07 g.

**건반 1개 빼기(공구 없음):** 뒤 커버를 벗긴다 → 백건이면 스톱 바 손나사 2개를 풀어 들어낸다(흑건은 그대로 둬도 됨) → 꼬리를 약 2 mm 들어 핀을 홈에서 빼고 → 건반을 3.5 mm 앞으로 당겨 크로스바를 훅에서 빼고 → 앞을 들어 꺼낸다. 스프링은 건반 우물에 남는다.

## 8. 소음 — 모든 충돌과 완충
| 충돌 | 무엇이 무엇에 | 완충 | 계산값 |
|---|---|---|---|
| 누름 1차 바닥 | 강철 막대 윗면 → 꼬리 스톱 펠트 3T | 펠트, 타격 중심 앞이라 핀 쪽 충격 없음 | 최대 23.8 N(백, 1 m/s) |
| 누름 2차 바닥 | 앞 바닥판 → 앞 펠트 3T (0.5 mm 뒤) | 펠트 | 16.5 N(백, 1 m/s) |
| 핀 | 핀이 홈에서 살짝 뜬 뒤 다시 앉음 | 홈에 천 0.5T | 0.099 mm(백 1 m/s), 0.174 mm(흑 1 m/s) |
| 복귀 | 크로스바 → 훅 펠트 3T | 펠트 | 튐 0.82 / 1.08 mm, 안정 52 / 85 ms |
| 스프링 | 코일 울림 | 예하중 항상 있음, 우물이 안내, 그리스 | — |
| 연결부 유격 | 없음(별도 해머·레버 없음) | — | 블로그의 "덜걱" 원인(해머-건반 슬롯 유격) 자체가 없다 |
| 막대 덜걱 | 막대가 주머니에서 흔들림 | 에폭시 고정 | — |

## 9. 위험과 단계 0 시험
위험
1. 무겁다: 88건반 강철 9.00 kg, 모듈 1.87 kg(v3 0.59 kg). R18(나눠 들기)에 부담.
2. 백건 관성 19.4 g로 가볍고 흑건 42.7 g와 차이가 크다. 쇠구슬 4개 옵션으로 31.0 g까지(스프링 0.76 N, 중력 몫 17 %).
3. 앞/뒤 힘 비 2.60 — v3(2.2)보다 나쁘다. 검은 건반 사이(y90)를 누르면 130 g.
4. 세게 칠 때 핀이 0.1~0.33 mm 뜬다(탁 소리 가능). 대책: 천 라이닝(기본), 단단한 꼬리 펠트(E 2.5 → 0.028 mm), 그래도 들리면 날개 홈에 0.1 mm 틈 걸림턱 추가.
5. 스톡 스프링의 실제 k를 모른다(계산은 선경 0.4·유효 40감김 가정) → 우물 스페이서로 맞춤.
6. 탭 부싱 마찰(2.98 g)은 가정값(한쪽 0.05 N 예압)이다.
7. 평철 88번 절단(손으로 2~3시간). 외주하면 절단비 3,000원/회(원자재닷컴 9~10t) → 264,000원.
8. 흑건 용골 z9.01은 바닥(z5)과 4 mm — 선이나 이물이 꼬리 밑에 끼면 안 된다.

단계 0 시험(빨리 반증하는 법): 백건 1 + 흑건 1 + 3건반 폭 프레임 쿠폰(밸런스 레일·날개·v3 훅·앞 펠트 레일·뒷벽 + 스톱 바)을 뽑고 막대·핀·스프링을 넣는다.
- 동전으로 DW/UW(y13, y62.5, y90) 측정 → DW 45~55, UW ≥ 30, y90/y13 ≤ 2.8이 아니면 기각.
- 휴대폰 240 fps로 복귀 촬영 → 백 t_full ≤ 35 ms, 흑 ≤ 50 ms, 40 % 복귀 ≤ 37 ms(13.3 Hz)가 아니면 기각.
- 강하게 16분음표 연타 → 핀에서 딸깍 소리가 mf에서 들리면 걸림턱 추가 후 재시험.
- 스프링 k 측정(추 50 g, 100 g) → 우물 깊이 보정.

## 10. v3 인터페이스 변경
- 리프 콤 2개(백·흑) → 개별 건반 12개(길이 206.5). 척추 레일, 클램프 나사 4, 세트스크루 4, 황동 원판 4, x기준 핀 제거.
- 밸런스 레일(y135~145, 날개 12) 추가, 꼬리 스톱 바(y186~209, z51.28~56.2) + 뒷벽 홈 + 손나사 2 추가.
- 제어 기판 y145.5~195.5 → y94~133(39×70으로 자름, 부품 ≤ z15, 4067은 짧은 핀으로 낮게). 리본은 센서 바 뒤(y77.5)에서 기판까지 16 mm로 짧아진다. RP2040-Zero USB-C는 90° 꺾인 플러그 → 바닥 통로 x71~80 → 뒷벽 구멍 x71~81 z5~12(v3 x74~94 z5~21).
- 앞 펠트 레일 경사 3.35° → 4.08°(백), 흑건 스톱 레일 4.62° → 6.13°, 펠트 윗면 높이는 §3 값.
- 뒤 커버 앞 가림판 아랫면 z44.5 → z46.5. 흑건 솟은 윗면은 y144에서 끝낸다(v3 142 테이퍼 끝과 비슷).
- 센서 바·자석 위치·훅/탭·도브테일·전체 깊이 410·폭 1254는 그대로.

## 11. 구매 품목과 가격 [10]
| 품목 | 규격 | 88건반 수량 | 단가(원) | 합계(원) | 출처 |
|---|---|---|---|---|---|
| 평철 | SS400 9×32(2.26 kg/m), 1 m | 5 | 7,000 | 35,000 | estimate (9×32 단위중량은 평철 규격표, 가격 미확인) |
| 평행핀 | SUS Ø3×10, 100개 | 1 | 10,000 | 10,000 | estimate (NFAS 다웰핀 M3 약 100원/개 표기) |
| 압축 스프링 | 선경 0.4, 외경 6, 자유장 50, 100EA | 1 | 60,000 | 60,000 | NaviMRO 현대스프링 100EA 팩 47,990~69,990원 확인, 이 규격 가격은 estimate |
| 쇠톱날 | 바이메탈 2개 | 2 | 3,000 | 6,000 | estimate |
| M3 손나사 + 너트 | 모듈당 2세트 | 18 | 300 | 5,400 | estimate |
| (옵션) 쇠구슬 Ø10 | 탄소강 1 kg(약 243개) | 0~1 | 6,500 | 0 | 다나와·베어링스토어 1 kg 5,900~6,900원 |
| 제거: v3 클램프 나사·세트스크루·황동 원판 | 모듈당 4+4+4 | — | — | −16,920 | v3 BOM, 근사 |
| **기본 구성 증감** | | | | **+99,480** | 583,219 → 약 682,700원(한도 100만 안) |

텅스텐 퍼티는 밀도가 8~11 g/cm³(강철 7.85의 1.0~1.4배)인데 값은 25 g에 약 8달러라, 추 재료로는 의미가 없고 건반별 미세 조정용으로만 쓴다.

## 12. 기준 대비 뺀 것
- 그랜드 액션 대비: 윕펜·잭·해머·섕크·렛오프·리피티션 레버·댐퍼·캡스턴·백체크·앞 레일 핀·밸런스 펀칭 펠트 없음. 건반 납(key lead)은 꼬리의 강철 막대 1개로 대체.
- GHS/Casio 대비: 별도 해머 레버와 그 축, 건반-해머 연결 슬롯(유격·덜걱 소리의 원인), 고무 돔 스위치 없음(홀 센서).
- v3 대비: 예하중이 걸린 PETG 리프(크리프 1순위 위험), 척추·세트스크루 조정, 클램프 나사 없음.
