WongyuKoh/Toccata/hardware/mechanical/key-action-v4/concepts/W1/design.md

# W1 — 짧은 시소 건반 + 꼬리가 들어 올리는 무게 레버

2026-09-27 · 모든 수치는 `calc.py`를 돌린 `results.txt`에서 옮겼다(절 번호 A~M 표기).
단위 mm · g · ms. z = 0 책상, y = 0 백건 립 앞끝, +y 뒤쪽. 대표 건반은 백건 D, 흑건 C#.

## 1. 한 줄 요약

건반은 Ø4 스테인리스 봉(y141, z21.5) 위에 얹힌 시소다. 앞을 누르면 뒤 꼬리의 캡스턴(y188.3)이 올라가고, 그 위에 펠트로 얹혀 있는 무게 레버(Ø3 봉 y203.5 z33.5에 매달린 9×50×21.5 평철 블록 76 g)를 들어 올린다. 손을 떼면 레버의 무게가 꼬리를 눌러 건반을 되돌린다. 스프링·이스케이프먼트·리피티션·댐퍼는 없다. 건반과 레버 사이에 홈(슬롯)이 없어서 덜걱거릴 틈 자체가 없다(항상 중력으로 눌려 붙어 있다).

## 2. 작동 순서 (도면 없이 읽는 설명)

1. 쉬는 상태: 레버(76 g 강철)가 건반 꼬리의 캡스턴을 1.50 N으로 누른다 → 건반 앞이 들린다 → 꼬리 끝(y196~199)의 펠트 1.5T가 뒤 선반(z20) 위에 얹혀 높이를 정한다. 멈춤 = 펠트 + 중력. 플라스틱에 상시 응력 최대 0.71 MPa(I).
2. 누름: 건반이 4.04°(흑 6.17°) 돌면서 캡스턴이 3.3 mm 올라가고, 레버가 12.4°(흑 10.3°) 돌아 강철 중심이 6.1 mm, 앞 모서리가 11.2 mm 올라간다. 바닥은 앞 펠트 3T(백 y1.5~10.5)가 받고, 같은 순간 강철 앞 윗모서리가 업스톱 레일 펠트(면 z65.7)에 닿는다(틈 0, 허용 ±0.3).
3. 떼기: 레버 무게가 건반을 밀어 올린다. 바닥 → 재타건점(자석 40 % 상승) 35.5 ms, 끝까지 55.8 ms(백). 흑건 31.2 / 49.3 ms(F).
4. 자석 Ø5×2는 y67(소자 바로 위)로 옮겼다. 백 이동 5.22 mm(정지 10.82 → 바닥 5.60), 흑 7.97 mm(13.35 → 5.38)(D).

## 3. 좌표표 (쉬는 상태 → 끝까지 누른 상태)

### 3.1 백건 (D) — B절

| 점 | 쉼 (y, z) | 바닥 (y, z) |
|---|---|---|
| 건반 회전축 K (SUS Ø4 봉 중심) | (141.00, 21.50) | 고정 |
| 레버 회전축 L (SUS Ø3 봉 중심) | (203.50, 33.50) | 고정 |
| 립 윗면 (y0) | (0.00, 43.50) | (−1.20, 33.50) |
| 손가락 점 y13 | (13.00, 43.50) | (11.77, 34.42) |
| 앞 다운스톱 접점 (건반 밑면) | (6.00, 23.50) | (6.20, 13.97) — 펠트 윗면 z13.97 |
| 뒤 멈춤 펠트 밑면 (뒤 선반 위) | (197.50, 20.00) | (197.47, 23.99) |
| 자석 면 중심 | (67.00, 23.50) | (67.04, 18.28) |
| 건반 무게중심 (21.8 g) | (85.03, 33.70) | (84.31, 29.72) |
| 캡스턴 꼭대기 = 접점 | (188.32, 31.00) | 접점 (188.39, 34.25) |
| 레버 무게중심 (80.2 g) | (174.52, 43.63) | (177.36, 49.60) |
| 강철 앞 윗모서리 (최고점) | (149.00, 54.50) | (154.76, 65.68) |
| 강철 뒤 윗모서리 | (199.00, 54.50) | (203.60, 54.98) |

회전: 건반 a = 0.0706 rad(4.04°), 레버 b = 0.2157 rad(12.36°). 레버비 j = db/da = 3.12(쉼) → 2.92(바닥).

### 3.2 흑건 (C#) — B절

| 점 | 쉼 (y, z) | 바닥 (y, z) |
|---|---|---|
| 흑건 윗면 앞모서리 | (54.50, 55.50) | (51.35, 46.00) |
| 손가락 점 (앞모서리 + 10) | (64.50, 55.50) | (61.29, 47.08) |
| 앞 다운스톱 접점 | (56.10, 23.50) | (56.38, 14.36) — 펠트 윗면 z14.36 |
| 뒤 멈춤 펠트 밑면 | (197.50, 20.00) | (197.33, 26.09) |
| 자석 면 중심 | (67.00, 23.50) | (67.21, 15.53) |
| 건반 무게중심 (16.7 g) | (112.59, 36.78) | (111.11, 33.63) |
| 캡스턴 꼭대기 = 접점 | (180.61, 31.00) | 접점 (180.22, 35.17) |
| 레버 무게중심 | (174.52, 43.63) | (176.79, 48.63) |
| 강철 앞 윗모서리 | (149.00, 54.50) | (153.61, 63.87) |

회전: 건반 0.1078 rad(6.17°), 레버 0.1791 rad(10.26°), j = 1.77 → 1.59. 레버는 백·흑 공통 부품이고, 흑건은 캡스턴 위치만 다르다(y180.61).

### 3.3 고정 부품 좌표

| 항목 | 위치 |
|---|---|
| 밸런스 레일 | y137~145, z5~19.5, 윗면에 Ø4 봉 홈. x60~82 z5~10 리본 터널(v3와 같은 자리) |
| 뒤 선반 (멈춤) | y196~209, z18~20, 아래 리브 x = 13.708·i (x82.2 리브는 USB 플러그 자리라 뺌). USB 플러그(z9.45~16.95)와 1.05 틈 |
| 지느러미(핀) 4장 | x0.5(두께 0.8) · x41.1 · x123.4(1.6) · x164.0(0.8), y148~209, z5~70.8. Ø3 레버봉 구멍(203.5, 33.5), 업스톱 레일 홈 y149~168 z67.8~70.8(앞으로 열림). 제어 기판 x47.25~117.25를 피한다 |
| 업스톱 레일 | 평철 3T×19, y149~168, 밑면 펠트 2T(면 z65.68 백 기준) |
| 먼지 커버 | 윗면 z73.18(v3 z59 → +14.2), 앞 가림판 y145~147 아래끝 z44.5 |
| 제어 기판 | v3 그대로 y145.5~195.5, 부품 ≤ z20. 건반 빔 밑면 z21.5(틈 1.50) |

### 3.4 최소 여유 (E절, 스트로크 전 구간 + ff 과다 누름 0.6 mm 포함)

백: 빔↔레버 밑면 2.16, 꼬리↔허브 2.26, 밑면↔센서 바 3.77, 밸런스 블록↔레일 1.55, 빔↔기판 1.50, 레버↔가림판 2.00.
흑: 1.49, 1.25, 2.65, 1.32, 1.50, 2.00, 흑건 앞면↔백건 노치 1.18. 자석-소자 최소 5.38(≥ 3.0).

## 4. 힘·관성·복귀 (C, F, G절)

| 항목 | 백 (y13) | 흑 (y64.5) |
|---|---|---|
| 균형 무게 BW | 47.05 g | 46.34 g |
| 마찰 (밸런스봉 0.69 / 레버봉 0.67 / 캡스턴 미끄럼 0.62 / 가이드 부싱 1.47) | 3.45 g | 4.17 g |
| 다운웨이트 DW | 50.50 g (립 y0 45.83) | 50.51 g |
| 업웨이트 UW | 43.60 g | 42.16 g |
| 바닥에서 DW / UW | 45.37 / 30.17 g | 43.11 / 27.83 g |
| 유효 질량 m_eff | 65.8 g (립 54.2) | 56.9 g |
| 재타건 t(40 %) · 1/(2t) | 35.5 ms · 14.1 Hz | 31.2 ms · 16.0 Hz |
| 끝까지 복귀 | 55.8 ms | 49.3 ms |
| 앞/뒤 힘 비 DW(y90)/DW(y13) | 2.52 | — |

- 가정: 펌웨어는 자석이 바닥에서 이동량의 40 %(백 2.09 mm, 흑 3.12 mm) 올라오면 다시 칠 준비를 한다. 1/(2·t40)은 다시 누르는 데도 같은 시간이 걸린다는 보수적 가정, 10 ms에 다시 누르면 22.0 Hz.
- v2.0의 "무게와 상관없이 약 40 ms" 주장 확인(H절): 시간은 √(m_eff/UW)로 움직인다(h10 → 44.6 ms, h24 → 35.4 ms). 재타건에 필요한 것은 40 % 상승이라 전체 복귀의 약 62 %다.
- 힘 곡선이 누를수록 10 % 가벼워진다(레버 무게중심이 축보다 10 mm 위에 있어서).

### 스프링 (사용자 허용, 기본안에는 넣지 않음)

- 보조 스프링(F절): 커버/레일에 매단 SUS 선경 0.30 · 외경 6 · 유효 약 6권 압축 스프링이 레버 이동의 뒤 50 %에서만 닿는다(바닥에서 +12 g). 백 31.4 / 50.4 ms(15.9 Hz), 흑 27.3 / 44.3 ms. 자유장 9.9 mm가 자리에 들어간다.
- W1-S 변형(F2절): 캡스턴 y191.5 + 강철 h15.9(56 g)로 m_eff 81.4 g, 커버 z68.5. 스프링 없이 12.5 Hz / 62.7 ms로 목표 미달, +12 g 스프링이면 14.2 Hz / 56.5 ms. 관성이 더 크고 강철이 줄지만 스프링 88개가 붙는다.

## 5. 소음 (G, H2절)

| 충돌 | 완충 | 계산값 |
|---|---|---|
| 건반 바닥 (앞) | 펠트 3T (v3 자리) | ff 3 N에서 최대 15.3 N |
| 레버 위 (업스톱) | 강철 레일 밑 펠트 2T, 딥과 동시에 닿게(틈 0) | ff 38 N, fff 62 N (그래서 레일이 강철이다) |
| 레버가 캡스턴에 다시 내려앉음 | 레버 밑 펠트 2T (1.5T도 가능) | 바닥에서 레버가 0.13~0.34 mm 떠올랐다 0.12~0.46 m/s로 내려앉는다(백 pp~fff). 흑 fff 1.57 mm |
| 복귀 끝 (뒤 선반) | 꼬리 밑 펠트 1.5T | 최대 13.9 N, 건반 앞이 복귀 뒤 딥의 22 %만큼 한 번 되내려간다 |
| 건반↔레버 연결 틈 | 없음 (중력 접촉, 백 1.50 N · 흑 0.99 N 예하중) | 슬롯 덜걱 소음 원인 제거 |

블로그의 '덜걱'은 연결 홈의 틈 때문이었다. W1은 홈이 없고 항상 눌려 붙어 있어 그 원인은 없다. 대신 세게 칠 때 무거운 레버가 잠깐 뜨고 다시 앉는 소리가 남는다(펠트 위라 둔탁한 '툭').

## 6. 부품 (옥타브당)

| 부품 | 종류 | 재료 | 개수 | 질량 | 치수 | 비고 |
|---|---|---|---|---|---|---|
| 백건 | 출력 | PETG | 7 | 21.5 g | y0~199, 헤드 22.5 폭 | 윗판 2.0, 벽 1.2 U채널 + 숨은 빔 8×7(y147~191), 얇은 꼬리 8×3, 노치 R2.05 |
| 흑건 | 출력 | PETG | 5 | 16.4 g | y53.5~199 | 앞면을 v3보다 2.0 뒤로(53.5/54.5) |
| 레버 캐리어 | 출력 | PETG | 12 | 4.1 g | 64×13 | 허브 Ø9·구멍 Ø3.1, 양쪽 벽 1.0, 허브 폭 13.6(핀 옆 12.8) |
| 무게 블록 | 구매 | SS400 | 12 | 76.0 g | 9×50×21.5 | 9T×50 평철을 21.5로 절단 |
| 건반 봉 | 구매 | SUS304 | 1 | 16 g | Ø4×163.5 | 밸런스 레일 홈에 눕힘 |
| 레버 봉 | 구매 | SUS304 | 1 | 9 g | Ø3×163.5 | 핀 4장 관통 |
| 업스톱 레일 | 구매 | SS400 | 1 | 73 g | 3×19×163 | 핀 홈에 앞에서 끼움 |
| 자석 | 구매 | N35 | 12 | 0.3 g | Ø5×2 | v3와 같음, 위치만 y67 |
| 펠트 | 소모 | 양모 | 12+12+1+… | — | 2T 9×19.5(레버 밑), 1.5T 8×3(꼬리), 2T 19×163(레일), 3T 앞 스톱(v3) | |
| 프레임 | 출력 | PETG | 1 | 198 g | 164.5×212 | v3 프레임 − 척추 레일 − 두 번째 바닥 + 밸런스 레일 + 뒤 선반 + 핀 4 + 높인 뒷벽 |
| 커버 | 출력 | PETG | 1 | 49 g | 164.5×67 | 먼지 커버(기능 없음) |
| 센서 바 | 출력 | PETG | 1 | 17 g | v3 | 그대로 |

옥타브당 출력 27개, 구매 15개(강철 12 + 봉 2 + 레일 1, 자석·펠트 제외). 강철 911 g/옥타브, 88건 6.68 kg. 모듈 무게 약 1.52 kg(K).

## 7. 출력 계획 (K절)

- 건반: 윗면을 베드에 대고 뒤집어(v3와 같은 방향), 숨은 빔·꼬리는 100 % 채움, 노치 R2.05는 작은 아치 브리지. 199 mm로 220 베드에 들어간다.
- 레버 캐리어: 쓰는 자세 그대로 세워서, 허브 구멍은 Ø3.0 티어드롭으로 뽑고 Ø3.1 드릴로 리밍.
- 프레임 164.5×212, 커버 164.5×67 — 전부 220×220 안.
- 모듈 545 g = 36.3 h, 88건 전체(끝 부속·v3 기타 출력·예비 건반 포함) 5.39 kg, 359 h.

## 8. 조립 · 한 건반 빼기

1. 프레임: EVA, 앞 펠트(백 y1.5~10.5, 흑 y53.5~58.7), 가이드 탭 부싱 펠트(v3), Ø4 봉을 밸런스 레일 홈에 눌러 넣기.
2. 센서 바·제어 기판: v3 그대로.
3. 건반: 자석 y67 압입, 꼬리 끝 밑에 1.5T 펠트. 건반을 위에서 내려 가이드 리브가 탭을 감싸고 노치가 Ø4 봉에 앉게 한다.
4. 레버: 강철 블록을 캐리어에 에폭시로 붙이고 밑에 2T 펠트 띠(y177~196.5). 핀 → 레버 12개 → 핀 순서로 Ø3 봉을 꿴다(허브끼리 맞대어 x 위치가 잡힘). 레버가 캡스턴 위에 내려앉는다.
5. 업스톱 레일(3T×19 + 2T 펠트)을 핀 홈에 앞에서 밀어 넣고, 커버를 얹는다.
6. 조정: 건반별 DW는 캡스턴 0.3 mm당 백 1.51 g · 흑 1.14 g이므로, 출력 뒤에는 텅스텐 퍼티(건반 앞 = 가볍게, 강철 위 = 무겁게)로 맞춘다.

한 건반 빼기(공구 없음): 커버를 들고 → 업스톱 레일을 앞으로 뽑고 → 그 건반의 레버를 손으로 27° 젖힌 채(강철 뒤 모서리가 뒷벽에 닿는 각도, 캡스턴 위로 7.2 mm가 비어 노치 2.05 mm를 들기에 충분 — K절) → 건반 앞을 들어 노치를 봉에서 떼고 앞으로 빼낸다.

## 9. v3에서 바뀌는 곳

- 뒤 커버 z59 → z73.2, 뒷벽 z56.5 → z70.8. z59로는 이 구조의 DW가 최대 12.3 g밖에 안 나온다(J2절). 제어 기판을 옮겨 빔을 9 mm 내려도 z64.3이다.
- 리프 콤·척추 레일·M3×35 클램프·세트스크루·황동 원판·훅(업스톱)·두 번째 바닥 레일 삭제 → 밸런스 레일 + Ø4 봉, 뒤 선반, 핀 4장 + Ø3 봉, 강철 업스톱 레일.
- 건반이 콤이 아니라 12개 낱개. 겉모양(y0~146, z23.5~43.5)은 v3 그대로.
- 자석 y65.8/64.2 → y67.0(백·흑). 흑건 앞면 2.0 mm 뒤로(누를 때 흑건 윗면이 3.15 mm 앞으로 미끄러지므로 백건 노치와 1.18 여유를 둠).
- 앞 가이드 탭은 v3 그대로 두고 훅만 뺀다. 커버 가림판 y146 → y145~147.
- 제어 기판·센서 바·리본 차선·USB 터널은 그대로(뒤 선반은 USB 플러그 위로 1.05 떠 있음).
- 총 깊이 410 그대로.

## 10. 비용 (L절, 가격은 모두 추정 표시)

추가: 9T×50 평철 6 m 14,000(추정) · SUS304 Ø4 4 m 7,000(추정) · SUS304 Ø3 4 m 6,000(추정) · 3T×19 평철 3,000(추정). 삭제: M3×35 32개 · 세트스크루 32개 · 황동 원판 32개 · 너트 64개 = 17,920(추정). 기본 구성 +12,080원. 절단을 맡기면 +44,000(추정, 직접 자르면 0), 펠트 +5,000(소모품), 스프링 옵션 +13,200(추정).

## 11. 위험과 단계 0 시험

위험은 StructuredOutput `risks`와 같다. 단계 0: (1) 3건반 시편 + 강철 1개로 y13 DW/UW를 저울로 재기(계산 50.5/43.6 g) (2) 240 fps 폰 영상으로 바닥 → 40 % 35.5 ms, 끝 55.8 ms 확인 (3) 펠트 낙하 시험으로 K·e 측정 (4) ff 녹음으로 업스톱·재착지 소리 비교 (5) 60 °C 2 h 뒤 건반 높이 변화.
