WongyuKoh/Toccata/hardware/mechanical/touchscreen/rev3/design/CAD_SPEC_rev3.md

# R31 터치스크린 — CAD 요청 사양 수정 3판 3a (B1: Waveshare 7-DSI-TOUCH-C, L2 뒷바)

작성 2026-10-01 · 좌표는 L2 world mm (x = A0 왼쪽에서 가로, y = 흰건반 앞끝에서 뒤로, z = 책상에서 위로) · 그림 `touch_concept_rev3.svg`
수치 출처: `numbers.json` (geom3.py가 L2 값에서 계산). L2 값: **확정본 L2_cu.json** · 스피커 유닛 자리: body_L2.json 사본(md5 2d716999, 저장소와 같음).
표시: 【새로】 3판에서 새로 생김, 【변경】 2판·v13과 다름, 【그대로】 v13 규칙을 그대로 씀, **【3a】 검수 뒤 이번에 고침**.

## 0. 자리 블록 (이 값 하나에서 모든 좌표를 계산)
| 항목 | 값 |
|---|---|
| 화면 가운데 x (XC) | 611 |
| 뚜껑 x / y / 윗면 z | x501~721 / y214~341.5 / z72.85 (판 3, 리브 밑면 = 출력 바닥 z61.35) |
| 모듈 위 금지 | y ≤ 215 이면서 z ≥ 72.85 에 화면 부품·선 없음 (여유 1) |
| 경첩 축 y / z | y226.55 / z81.35 — y = keep-out y215 + 1.0 clearance + front reach 10.55 (cradle corner u-2.5 w-1.0 at 22.0 deg); z = lid top + 8.5 |
| Pi 5 (L2 확정) | 방향 "USB/RJ45 end +x, GPIO edge +y" → 회전 0° · CAM/DISP 1 x589~592, y263~278, 입구 x589 z26.0 방향 −x, 깊이 3 · 리본 기둥 x582~600, y262~280 |
| Pi 5 GPIO 2·6 | (550.37, 315.77) · (555.45, 315.77), 핀 끝 z32.6 |
| 뚜껑 고정 (L2) | M3×10 4개: y246, y322, x≈506·716 (이음 레일 x491~511·711~731, z55.35~61.35, 인서트) |
| 통풍 슬롯 | 화면 뒤 배기 8개 34×4: x564~598 · x624~658, y300~325 (간격 7) |
| 스피커 | 윗면 z148.06, 뒷면 y341.5, 유닛 가운데 x160.5 / x1061.5, y258.5 (body_L2) |

받침 좌표: xr = x − 611, u = 유리 아래 끝에서 화면 위쪽으로, w = 유리 앞면에서 뒤로. world = M·[xr, u, w, 1] (M은 numbers.json `poses`).
L2 값이 바뀌면 `python3 geom3.py && python3 build3.py && python3 draw3.py && python3 build3d.py`만 다시 돌리면 모든 수치가 바뀝니다.

## 3a에서 고친 것 (검수 반영)
| 항목 | 3판 처음 | 3a |
|---|---|---|
| 귀 옆모양 | 뒤꿈치 옆에 점이 하나 더 있음 (u-17.4, w11.15) → 22°에서 멈춤 블록을 2.1 mm, 25°에서 1.83 mm 파고듦 → 약 42.1°에서 멈춰 25°로 못 씀 | 축 원 R4.2 + 받침 아래 u-2.5(w8~13) + 뒤꿈치 (u-16.26, w8.38)만 감싼 모양. 블록과 22°에서 0.0(닿음), 25~90°에서 0.37 이상 |
| 출력 높이 | 약 117(사양) / 120.9(도면, 잘못된 점) — 서로 다름 | 119.76 (u103.5 − 뒤꿈치 u-16.26) |
| 아래 가로 리브 | u30 (다리 축 줄) → 축 나사 머리가 2.35 mm 파고들고 넣는 길이 막힘 | u24 (u23~25) → 머리·넣는 길과 2.0 mm 이상 |
| 아래 벽 홈 | 없음 (화면 아래 끝 작은 돌기가 걸림) | xr48~66 (x659~677), u-2.5~0 관통, w-1~8 |
| 벽·보스 | 모델과 사양이 다름(모델은 아래 벽에도 틈, 보스가 따로 섬) | 아래 벽 안쪽 u0(유리가 얹힘), 위 틈 0.5, 옆 틈 0.3; 보스는 옆벽까지 채움 |
| 리본 클립 | 납작한 30×12×3 (전원선이 리본을 들어 올림) | 윗면에 전원선 홈 x652.6~656.1, 깊이 1.8; 핀 길이 4.5 |
| 뚜껑 밑 리본 높이 | z59.85 (클립과 안 맞음) | z61.2 (뚜껑 밑면에 붙고 클립에 물림 z61.05~61.35) |
| 리본 끝 (Pi 쪽) | z26까지 곧게 내려와 U자로 셈(+3.42), 추정 HDMI를 1.3 mm 파고듦, 꽂는 길이 3.5 | 기둥 x583 그대로(입구 − 보강판 3 − R3). 안 쓰는 HDMI 위(z27.45)에 얹혀 19.93°로 입구에 들어감. 꽂는 길이 2.7(커넥터 깊이 3 − 0.3) |
| 리본 길이 | 261.74 mm (여유 38.26) | 256.32 mm (여유 43.68) |
| 전원선 길이 | 341.45 (뚜껑 두께 11.5만 셈, 뚜껑 밑 3.5 빠짐) | 344.95 (길 점으로 한 번씩 셈: 뚜껑 윗면→홈 높이 12.7, 뚜껑 밑 213.21) |
| 소리 길 | 스피커 추정 자리로 259.69 | body_L2 유닛 가운데(x160.5/1061.5, y258.5)로 248.58; 27° 규칙 3.53 mm |
| 다리 넣기 | 순서 없음 | 화면을 22°(뒤꿈치)에 댄 채 넣고 뺌. 25°에서 넣으면 발이 뒷벽 위 모서리를 0.66 mm 긁음 |
| 뚜껑 나사 자리 | 값 없음 (모델과 도면이 서로 다름) | Ø6.5 × 5.5 자리파기(머리 자리 z67.35), 레일 인서트 물림 4 (추정) |
| O4 정비 | 없음 | 뚜껑을 화면째 들고 Pi 쪽 ZIF를 풂. 리본을 꽂은 채 약 96 mm 들 수 있음 |
| 스터드가 박혀 있을 때 | 스터드를 뗌 (못 뗄 수도 있음) | 보스를 Ø6.2로 w13.7까지 파고 뒤에서 나사 (뒷판·축 그대로) |
| Pi 방향 | 회전 0을 손으로 넣음 | L2 글 "USB/RJ45 end +x, GPIO edge +y"에서 읽음. CAD 커넥터 상자와 0.4 mm 안에서 맞는지 확인(틀리면 멈춤) |
| 낱말 | '귀 자리'가 귀와 귀 홈 둘 다를 뜻함 | 귀 = 받침 쪽 x542.8~550.8(8.0), 귀 홈 = 뚜껑 볼 사이 x542.6~551.0(8.4) |

## 2판·v13과 달라진 것
| 항목 | 2판 / v13 | 3판 (3a) |
|---|---|---|
| 화면 | Touch Display 2 7인치 유리 189.32×120.24 | 7-DSI-TOUCH-C 166.1×101.0×8.0 (가로 기본, 돌리지 않음) |
| 자리 | L1 CU 뚜껑 (화면 가운데 x656) | L2 가운데 뚜껑 x501~721, y214~341.5, z72.85 |
| 화면 가운데 x | 656 | 611 |
| 경첩 축 | y290 z96 | y226.55 z81.35 (모듈 위 금지 규칙에서 계산) |
| 축 자리(받침 좌표) | u-9, w16 (뒤 리브 면) | u-9, w13 (뒷판 뒷면) → 앞 돌출 17→14 |
| 받침 크기 | 193.92×125.24×17 | 170.7×106.0×17.0 |
| 화면 고정 | 러그 4개 M2.5 (TD2) | 모서리 구멍 4개(154×88) M2.5×6, 보스 Ø8(옆벽까지 채움) |
| 뒤꿈치 | 뚜껑 윗면에 닿음, 축에서 R10.63 | 귀 홈 바닥에 3.5 mm 멈춤 블록, 축에서 R8.6 |
| 경첩 x | x616~636.4 · x703.8~724.2 (나사 +x) | x538.6~559.0 · x663.0~683.4 (대칭, 나사는 바깥에서) |
| 리본 구멍 | x592~614, y292~298 | x635.35~657.35, y228.55~234.55 (22×6 그대로) |
| DSI 커넥터 | 15핀 1 mm, x≈638.66, 입구 -x | 22핀 0.5 mm, x628.85~634.25, u36.5~52.4, 입구 +x |
| 리본 | FIT0997 22→15핀 300 mm | GUOCONN 22핀 0.5 mm 300 mm B형 (A형은 예비) |
| 점검창 | ㄴ자 창 | 네모 창 x626.5~656.0, u33~69 + 접힘 자리 볼록 덮개 |
| 받침다리 | u20·w19.5 축, 95 mm, 20.5° | u30·w16.5 축, 67 mm, 39.78° |
| 다리 주머니 | 경사 앞 y383.5 (v13 기록), 뒷벽 y397.4 | 경사 앞 y290.43, 뒷벽 y300.7 |
| 접은 높이 | z96~113 | z78.35~95.35 |
| 접이 받침 발 | 16×16×8, x566~582·730~746 | 16×16×5.5, x535~551·671~687, 뒤 발에 턱 |
| 받침 뒤 패드 (v13 ⑥) | x566~582·730~746, u53~69 (v13 기록) | xr±60~76, u20~36·u70~86 (4개) |
| 채움 바닥 (v13 ②) | z76.5 (v13 기록) | z61.35 (L2 뚜껑 리브 밑면) |
| 통풍 슬롯 (v13 ③) | y302~397 (v13 기록) | 화면 뒤 배기 8개 34×4, y300~325 (CAD L2 배기 자리) |
| 리본 클립 핀 (v13 ④) | x592.05·616.05, y320 (v13 기록) | x634.35·658.35, y242.55, 핀 길이 4.5 |
| 다리 클립 턱 (v13 ⑤) | w22.52부터 (v13 기록) | w19.52부터, u87~93 |
| 받침 아래 뒤 모서리 | 없음 | C2 모따기 (경첩 볼과 틈 0.59) |
| 뚜껑 고정 | D23 모서리 받침 + 앞 나사 2 | L2 레일 인서트 M3×10 4개 (y246·322), 자리파기 Ø6.5×5.5 |

## A. 가운데 뚜껑 (L2 뚜껑에 더할 것)
뚜껑 자체(판, 리브, 뒤 자석, 이음 레일)는 CAD 세션의 L2 설계를 따릅니다. 아래는 화면 때문에 더하는 것입니다.

【10/1 CAD L2 실제값과 맞춤】 CU-SCREENLID는 x501.5~720.5, y214~341.5, z61.35~72.85(윗판 3 = z69.85~72.85, 바깥 벽 3, 갈비 2 = x531/571/611/651/691 · y254/290, 나사 보스 10×12)입니다. 아래 A의 더하는 것들이 갈비보다 먼저입니다: 갈비는 리본·전원선 구멍(x635.35~657.35 × y228.55~234.55)과 그 둘레 벽, 클립 핀 자리((634.35, 242.55)·(658.35, 242.55)), 경첩 받침 밑 채움, 주머니 덩어리, 접이 발 자리와 만나는 곳에서 끊거나 그 덩어리에 합칩니다. 특히 x651 갈비는 구멍을 지나므로 구멍 둘레 벽까지만 둡니다.
1) 【변경】 경첩 받침 2개(뚜껑과 한 몸). 폭 20.4 = 먼 볼 8.0 + 귀 홈 8.4 + 가까운 볼 4.0. 귀 홈(볼 사이) 8.4 = 귀 8.0 + 틈 0.2 × 2. 나사는 바깥쪽 가까운 볼에서 넣습니다.
   - 왼쪽: 가까운 볼 x538.6~542.6, 귀 홈 x542.6~551.0, 먼 볼 x551.0~559.0 (나사 −x 쪽에서)
   - 오른쪽: 먼 볼 x663.0~671.0, 귀 홈 x671.0~679.4, 가까운 볼 x679.4~683.4 (나사 +x 쪽에서)
   - 볼 옆모양(y-z): 축 (y226.55, z81.35) 둘레 R5.5 + 아래로 넓어지는 사다리꼴(z81.35에서 y221.05~232.05, z72.85에서 y217.55~235.55). 축 위로 R5.5 밖으로 나오면 안 됩니다.
   - 가까운 볼 Ø3.3 관통, 먼 볼 Ø2.5 × 8 (M3×20 직접 탭, 물림 7.6).
   - 【새로】 뒤꿈치 멈춤 블록: 귀 홈 바닥을 z76.35까지 올립니다(뚜껑 윗면 + 3.5). x = 귀 홈, y217.55~224.55. 22°에서 귀의 뒤꿈치가 (y219.55, z76.35)에 닿습니다.
   - 【그대로】 경첩 받침 밑은 출력 바닥 z61.35까지 채웁니다.
2) 【변경】 리본·전원선 구멍 22×6: x635.35~657.35, y228.55~234.55 관통, 위아래 모서리 R1. 둘레 벽 2 mm를 z61.35까지 채웁니다. CAD 권장(x580~602, y224~236)과 다른 이유: 화면 커넥터가 오른쪽(+x)이라 받침 안 리본이 x638.2~650.0로 내려옵니다. 구멍 밑은 L2 앞 빈 공간(y214~241)입니다.
3) 【변경】 받침다리 주머니: x604~618. 앞 30° 경사는 (y290.43, z72.85) → (y296.49, z69.35). 바닥 z69.35는 y296.49~300.7. 뒷벽 y300.7 수직(위 모서리 C0.5).
   - 경사 앞끝 규칙(v13 ①을 다시 계산): 다리를 반지름 3 캡슐로 보고 경사·윗면과 0.2 mm 이상 떨어지게 함. 2판 규칙(y291.63)이면 0.4 mm 파고듦 → y290.43로 당김(최소 틈 0.2).
   - 【3a】 다리는 화면을 22°(뒤꿈치)에 댄 채 넣고 뺍니다(D 참조). 뒷벽 위 모서리를 더 깎는 방법은 쓰지 않습니다. 발이 뒷벽에 닿는 점(z72.35)이 바로 그 모서리 아래라서 깎으면 발 자리가 없어집니다.
   - 【그대로】 주머니 밑 덩어리 x601~621, y287.43~303.7를 z61.35까지 채웁니다.
4) 【변경】 접이 받침 발 4개 16×16, 높이 5.5 (z72.85~78.35): x535.0~551.0, y255.55~271.55; x535.0~551.0, y305.55~321.55 (턱 있음); x671.0~687.0, y255.55~271.55; x671.0~687.0, y305.55~321.55 (턱 있음).
   - 【새로】 뒤 발 2개에 턱: y322.05~324.05, z78.35~80.35 (접은 받침이 뒤로 밀리지 않게).
5) 【변경】 리본 클립 자리: 뚜껑 밑 덩어리 x631.35~661.35, y236.55~248.55, z61.35~69.85(출력 바닥까지 채움). 밑에서 막힌 구멍 Ø3.1 × 5 두 개: (634.35, 242.55), (658.35, 242.55). 클립(E-2)이 밑에서 리본을 덩어리 밑면에 눌러 잡습니다.
6) 【변경】 통풍(배기) 슬롯 8개, 각 34(x) × 4(y): 왼쪽 줄 x564~598, 오른쪽 줄 x624~658, y = 300~304, 307~311, 314~318, 321~325. CAD L2의 "화면 뒤 배기 y300~325, 8×(4×34)"를 다리 주머니 덩어리 양옆으로 나눔. 접으면 덮임(운반 때, 전원 끔).
7) 【변경】【3a】 뚜껑 나사 자리 (L2 CAD 설계: 이음 레일 20×6 윗면의 M3 인서트, 앞 2개는 기둥 위): M3×10 4개, y246, y322, x506·716 (뚜껑 끝 ±5 = 레일 위 겹침 10 mm의 가운데).
   - 뚜껑 쪽: Ø8 기둥을 z61.35까지 채움, 구멍 Ø3.4, 위에서 Ø6.5 × 5.5 자리파기(머리 자리 z67.35). 머리 밑 뚜껑 살 6.
   - 레일 쪽(CAD L2 실제값, 10/1): 인서트 SEAM-INS M3 열압입 Ø4.0 × 4.0, 구멍 Ø4.0 × 깊이 4.5(레일 윗면 z61.35에서) → 물림 4.0(인서트 전체), 나사 끝 z57.35, 구멍 바닥 z56.85보다 0.5 위, 구멍 밑 레일 살 1.5.
   - 【확정】 자리파기는 5.5(머리 자리 z67.35)입니다. CAD 뚜껑의 지금 값 6.0(머리 자리 z66.85)이면 물림 4.5로 나사 끝이 구멍 바닥 z56.85에 닿아(여유 0) 조이기 전에 바닥을 칩니다.
   - 규칙: 자리파기 깊이 = 나사 자리 뚜껑 두께 11.5 − (10 − 인서트 물림). CAD가 인서트 길이를 바꾸면 이 식으로 다시 잡습니다(추정 값).
   - 앞 기둥 x496~506 · x716~726: 나사 x506·716이 기둥 안쪽 모서리 위에 옵니다. 인서트가 레일 안에 있어서 괜찮습니다. CAD가 기둥을 안쪽으로 2 옮기면 나사 밑이 기둥 가운데가 됩니다(CAD가 정함).
   - 받침 x525.65~696.35에서 19.6 mm 밖이라 화면을 세운 채 풀 수 있습니다. 경첩 받침·받침 발과 겹치지 않습니다.
8) 자석은 뚜껑 뒤에만 둡니다. 화면·경첩·다리에는 자석이 없습니다(D14).
9) 출력: 리브 면을 베드에. 경첩 받침·주머니 덩어리·구멍 벽·클립 덩어리·나사 기둥은 모두 출력 바닥 z61.35까지 채워 서포트 없이 뽑습니다. x 방향 구멍(Ø3.3, Ø2.5)은 물방울 모양으로 뽑고 드릴로 다듬습니다.

## B. 뚜껑 고정과 O4 정비
- 【변경】 L2에서는 D23의 나사형 모서리 받침 대신 레일 인서트에 M3×10 4개를 씁니다(앞 y246, 뒤 y322, A-7). 자석은 옆 뚜껑에만 있고 화면 쪽에는 없습니다(D14).
- 앞으로 10 N 당길 때(뒤꿈치 150 N과 경첩이 짝힘) 앞 나사 두 개 합계 약 34 N (앞 나사 y246와 뚜껑 앞 받침 사이 30.5 mm 기준).
- 【3a】 O4 정비(O4 USB 플러그가 화면 뚜껑 밑에 있음 — CAD 요청 "리본을 쉽게 뽑게"):
  1. 화면을 뒤로 접는다(다리는 클립에)
  2. M3×10 4개를 푼다(앞 y246, 뒤 y322)
  3. 뚜껑을 화면째 천천히 든다(리본을 꽂은 채 약 96 mm까지)
  4. Pi 5 CAM/DISP 1의 잠금 막대를 올리고 리본을 뺀다(화면 쪽 ZIF는 받침 안이라 건드리지 않음)
  5. GPIO 2·6의 암-암 점퍼 2개를 뺀다
  6. 뚜껑을 옆에 둔다 → O4 플러그 작업
  7. 되돌릴 때: 리본 B형 방향 확인 후 잠금, 점퍼 2번 빨강·6번 검정, 나사 4개
  - 리본 여유 44 mm는 클립과 45° 접기 사이 (뚜껑 밑): 뚜껑을 들 때 이 여유가 풀림에 둡니다. 클립에서 Pi까지 풀린 리본은 약 131 mm(여유 포함 175)입니다. 그래서 꽂은 채 약 96 mm 들 수 있습니다(곧은 선 − 굽힘 10, 추정).
  - 뽑는 곳은 Pi 쪽 CAM/DISP 1입니다. 화면 쪽 ZIF는 받침 안(점검창 덮개 밑)이라 정비 때 건드리지 않습니다.

## C. 화면 받침(크래들) 새 STL, PETG
받침 좌표 xr·u·w (위 0장). 화면은 굵은 테두리(9.65)가 아래, 커넥터 창이 오른쪽(+x)에 오게 넣습니다.
1) 바깥: xr-85.35~85.35 (x525.65~696.35, 폭 170.7), u-2.5~103.5 (106.0), w-1.0~16.0 (17.0). 옆벽 앞끝은 유리보다 1.0 앞(w−1).
   - 【3a】 벽 안쪽 면을 정해 둡니다. 아래 벽 u-2.5~0(두께 2.5, 안쪽 면 u0에 유리 아래 끝이 얹힘, 틈 0). 위 벽 u101.5~103.5(위 틈 0.5). 옆벽 xr±83.35~±85.35(틈 0.3). 벽은 모두 w−1~16입니다.
   - 【3a】【새로】 아래 벽 홈: xr48~66 (x659~677), u-2.5~0 관통, w-1~8.
     - 이유: 화면 아래 끝에 작은 돌기가 있습니다. 도면 앞모습에서 xr54.99~59.24, 약 0.85 튀어나오고, 사진에서는 아래 면의 홈과 탭입니다.
     - 돌기 양옆 여유는 6.99/6.76 mm입니다. 유리는 홈 양옆의 아래 벽에 얹힙니다.
     - 앞모습 기준이라 커넥터 쪽과 상관없습니다. G-1에서 뒤집어도 홈은 그대로입니다.
     - 오른쪽 귀(xr60.2~68.2)와 x가 xr60.2~66에서 겹치지만, 홈은 w8 앞쪽만 뚫습니다. 귀가 붙는 아래 벽 w8~13는 남습니다.
2) 뒷판: w10.5~13.0 (두께 2.5). 화면 뒷면은 w8. 가운데 볼록판(높이 약 2.1, xr-56.65~14.35, u32.2~71.0)과 0.4 mm 뜹니다. 판과 화면 사이 2.5 mm 틈으로 리본·전원선이 지나갑니다.
3) 【변경】 화면 고정 보스 4개: xr ±77 (534, 688) / u 6.5, 94.5. Ø8 기둥 w8~16, 화면 뒷면(w8)에 닿음. 구멍 Ø2.8, 뒤(w16)에서 Ø5.5 자리파기, 나사 머리 자리 w11 → M2.5×6 물림 3 mm.
   - 【3a】 보스는 옆벽 안쪽 면(xr±83.35)까지 폭 8(u)로 이어 채웁니다(w8~16).
   - 구멍 깊이 규칙(깊이 모름): 물림 e = min(구멍 깊이 − 0.5, 4.0), 최소 2.0. 머리 자리 w = 8.0 + (6 − e). 받은 화면에서 깊이가 3.5보다 얕으면 그만큼 와셔를 넣거나 머리 자리를 올립니다.
4) 【변경】 커넥터(화면 뒤, 추정 ±0.5 — G 참조):
   - DSI: 22핀 0.5 mm ZIF(가로형), xr17.85~23.25 (x628.85~634.25), u36.5~52.4(핀 가운데 u43.8), 입구는 +x(xr23.25).
   - 전원: MX1.25 2핀(가로형), xr19.35~24.35, u56.6~65.2, 입구 +x. 5V·GND.
   - 화면 뒤 창: xr17.35~43.55, u30.2~70.5.
5) 【변경】 점검창(뒷판을 뚫음): xr15.5~45 (x626.5~656.0), u33~69. ZIF 잠금, MX1.25, 리본 접힘 자리가 모두 보입니다. 창 둘레 리브는 창보다 1.8 mm 밖에 둡니다(덮개 턱 자리).
6) 【새로】 리본 길(받침 안): 커넥터 입구에서 +x로 4 mm → 45° 접기 자리 xr27.25~38.95, u37.95~49.65(R3으로 말아 접기, 날카롭게 꺾지 않음) → −u로 xr27.25~38.95를 따라 내려감 → 아래 홈. 전원선은 xr40.45~43.45로 리본 옆을 내려감.
7) 【새로】 리본 누름 패드(뒷판 안쪽): xr26.75~39.45, u8~16, w8.6~10.5 (리본 두께 + 0.3 틈). 캡톤테이프를 함께 씁니다.
8) 【변경】 아래 트인 홈(리본 + 전원선): xr25.75~44.95 (x636.75~655.95), u-2.5~3, w8~16. 아래와 뒤가 트여 선을 뒤에서 넣고 뺍니다.
9) 뒤 리브(w13~16, 두께 2): 바깥 둘레 벽을 w16까지, 가로 리브 2개, 다리 길 벽 2개, 점검창 둘레, 패드 4개, 보스 4개. 가로 리브는 다리 길(xr±7.3)에서 끊습니다.
   - 【3a】 가로 리브는 u24(u23~25)와 u80입니다.
     - 3판 처음의 u30는 다리 축 줄 위였습니다. 그래서 축 나사 머리가 2.35 mm 파고들고 넣는 길이 막혔습니다. 이제 다리 축 줄(u30) 둘레에는 리브가 없습니다.
     - 규칙: 리브 가운데 u = 다리 축 u − 걸이 볼 R3.8 − 여유 1.2 − 리브 반 두께 1 (내림).
   - 확인: 축 나사 머리(Ø5.7 × 1.65, xr-10.95~-9.3)와 −x에서 넣는 나사 전체(xr-30.95~-9.3, u27.15~32.85, w13.65~19.35)가 모든 뒤 리브·패드·보스와 2.0 mm 이상 떨어집니다(가장 가까운 것: 다리 길 벽 1).
10) 【새로】 받침 아래 뒤 모서리(u-2.5, w16) C2 모따기: 22~90° 도는 동안 경첩 볼과 0.59 mm 이상 떨어집니다(모따기 없으면 1 mm 파고듦).
11) 【변경】 뒤 패드 4개 16×16, w13~16: (xr-76~-60, u20~36), (xr-76~-60, u70~86), (xr60~76, u20~36), (xr60~76, u70~86). 접으면 뚜껑 받침 발 위에 얹힙니다.
12) 【변경】 경첩 귀 2개: 두께 8.0, 귀 x542.8~550.8와 x671.2~679.2(뚜껑의 귀 홈 x542.6~551.0·671.0~679.4 안, 양쪽 틈 0.2). 축 (u-9, w13), 구멍 Ø3.3.
    - 【3a】 귀 옆모양(u, w)은 아래 네 가지만 감싼 볼록 모양이고, 다른 돌기는 두지 않습니다. 앞 변은 뒤꿈치 (u-16.26, w8.38) → 받침 아래 (u-2.5, w8) 곧은 선. 받침 아래 변은 u-2.5 (w8~13)로 받침 아래 벽에 붙음. 뒤 변은 (u-2.5, w13) → 축 원 접점 (u-6.27, w16.19). 축 원 R4.2(중심 u-9, w13)를 뒤쪽으로 돌아 접점 (u-12.69, w15). 아래 변은 접점 (u-12.69, w15) → 뒤꿈치 (u-16.26, w8.38) 곧은 선.
    - 이렇게 하면 22°에서 뒤꿈치 (u-16.26, w8.38)가 귀의 가장 낮은 점이 됩니다. 이 점이 world (y219.55, z76.35)에서 멈춤 블록에 닿습니다(축에서 R8.6).
    - 귀 전체 윤곽과 블록·홈 바닥 사이 틈은 22°에서 0.0(닿음), 25~90°에서 0.37 이상입니다(25°에서 가장 작음). 윤곽 점은 numbers.json `cradle.ear.profile_uw`에 있습니다.
    - 뒤꿈치 모서리는 R0.3 이하로만 둥글게 합니다. 더 둥글면 멈추는 각이 22°보다 조금 커집니다.
13) 【변경】 받침다리 걸이: 축 (u30, w16.5), x 방향. 가까운 볼 xr-9.3~-5.3 (Ø3.3 관통), 먼 볼 xr5.3~11.3 (Ø2.5 × 6 막힘, 물림 5.4). 다리 자리 xr−5~5 (틈 0.3). 볼 둘레 R3.8, 아래쪽 45° 모따기.
    - 【3a】 축 나사는 M3x20 ISO 7380(머리 Ø5.7 × 1.65)입니다. −x에서 넣고 육각 L렌치 2.0로 조입니다. 머리는 가까운 볼 바깥 면 xr-9.3에 평평하게 닿고, C-9 확인값대로 둘레가 비어 있습니다.
14) 【변경】 다리 길: 벽 xr-7.3~-5.3·5.3~7.3, u26.2~103.5. 접은 다리는 뒷판 위 w13.5~19.5에 눕습니다.
15) 【그대로·값 변경】 다리 클립 턱(v13 ⑤): 몸 xr−8.5~−5.3 / 5.3~8.5, u87~93, 걸림 0.8(다리 위 0.5), 걸림 턱 w19.52~20.72 (두께 1.2). 접으면 턱 끝 z73.63 (뚜껑과 0.78).
16) 확인값: 25° 가장 앞 (y216.61, z93.16), 가장 높은 곳 z189.23, 가장 뒤 y276.81. 22° 가장 앞 y216.0. 22~90° 전체 가장 앞 y216.0 (> y215). 90° 접음 y233.05~339.05, z78.35~95.35.
    - 평면 자리: 25°에서 y216.61~276.81, 22°에서 앞끝 y216.0입니다. 도면에 '25° y216.00'으로 쓰면 틀립니다.
17) 【3a】 출력: 윗변(u103.5 면)을 베드에 세워 출력합니다. 높이는 119.76(= u103.5 − 뒤꿈치 u-16.26)이고 귀가 위로 옵니다.
    - 다리 걸이·클립·패드는 45° 모따기로 서포트 없이 뽑습니다. 보스 구멍은 물방울 모양입니다. 아래 벽 홈은 맨 위라 서포트가 필요 없습니다.
    - 약 82 g, 약 3.7시간(추정).

18) 【새로】 선 나가는 방향과 굽힘 반경 (CAD 요청):
    - DSI 리본(22핀 0.5 mm, 폭 약 11.7, 두께 약 0.3): 화면 ZIF 입구 +x → 45° 말아 접기 R3 → −u로 내려감 → 아래 홈에서 아래로 나감 → 경첩 고리 약 23.04 mm (줄 길이 17.04(22°)·16.95(25°)·12.34(접음), 둥근 고리 R6.36~8.83) → 뚜껑 구멍으로 −z.
    - 【3a】 뚜껑 밑: 리본을 뚜껑 밑면에 붙입니다(가운데 z61.2, 클립에 물리는 높이 z61.05~61.35). 길은 +y 38.95 → 45° 접기 → −x 63.35 → 리본 기둥 x583에서 아래로 33.75입니다. 기둥은 CAD 지킴 구역 x582~600 안입니다.
    - 【3a】 Pi 쪽 끝: R3로 +x로 굽혀 안 쓰는 micro-HDMI 위(z27.45)에 2 mm 얹힙니다. 그다음 19.93°로 4 mm 가서 CAM/DISP 1 입구(x589, 입구 −x)에 2.7 꽂습니다.
    - 기둥 x583은 규칙 값입니다(drop column = mouth - (stiffener 3.0 + R3) = 583.00). 기둥을 입구 쪽으로 옮기면 보강판이 곧게 나올 길이가 없어 실제 리본으로 만들 수 없습니다.
    - 아래로 내려가서 +x로 도는 것은 90° 굽힘 두 번이고 U자가 아닙니다. 길이를 더하지 않습니다.
    - 【3a】 전원선(MX1.25 2핀 → 2.54 3핀 → 점퍼): 입구 +x → 리본 옆 xr40.45~43.45로 내려감 → 같은 홈·고리·구멍(x654.35) → 뚜껑 밑 클립의 전원선 홈(z60.15) → +y → −x → GPIO 2·6 (550.37, 315.77)로 내려감. 3핀 이음은 22×6 구멍을 지나갑니다.
    - 선이 모듈 쪽으로 가장 나오는 곳은 약 y222.51입니다(> y215).

## D. 받침다리 새 STL
PETG 10(x) × 6, 축 구멍 Ø3.3 중심에서 발끝 중심까지 67, 양 끝 R3(전체 73). 넓은 면을 베드에 눕혀 출력.
사용 상태: 축 world (y246.2, z115.22), 발끝 (y297.7, z72.35), 수평에서 39.78°. 접은 상태: 받침 뒤 w13.5~19.5, u27~100.
다리 길이·축 자리 결정: 접은 다리가 받침 윗끝 안(u100 ≤ 102.5), 발이 뚜껑 뒤끝에서 40.8 mm 안, 각도 25~40°에서 팔 길이가 가장 큰 쪽(38.6 mm).
【3a】 넣고 빼는 순서: **화면을 22°(뒤꿈치)까지 앞으로 기울여 댄 채** 다리를 내리거나 올립니다.
- 22°에서는 다리 축이 y244.4 z116.2로 2.05 mm 옮겨 갑니다. 그래서 뒷벽 위 모서리까지 71.36로 발 끝 반경 70.0보다 멉니다.
- 다리가 수평 아래 39.95°까지 내려오면 발이 경사(y294.29, z70.62)에 먼저 닿습니다. 손을 놓으면 화면이 25°로 돌아가며 발이 경사를 타고 뒷벽까지 미끄러집니다.
- 25°에서 그대로 내리면 뒷벽 위 모서리까지 69.34로 70.0보다 가깝습니다. 다리가 수평 아래 36.15°에서 발이 모서리에 먼저 닿고, 최대 0.66 mm 긁습니다(수평 아래 38.2°).

## E. 작은 부품
1) 【변경】 점검창 덮개: 끼움부는 창보다 0.2 mm 작고(두께 = 뒷판 2.5), 턱은 사방 1.5 mm 크고 두께 2. 【새로】 안쪽 볼록 자리 xr26.25~39.95, u36.95~50.65를 w15.2까지 비움(R3 말아 접은 리본 자리), 바깥 살 1.2. 걸쇠 2개.
2) 【3a】 리본 클립 30×12×3 (뚜껑 밑, z58.05~61.05):
   - 윗면에 핀 Ø3 두 개, 길이 4.5(구멍 5보다 0.5 짧게).
   - 윗면에 전원선 홈 x652.6~656.1(폭 3.5), 깊이 1.8, y 방향으로 끝까지.
   - 평평한 나머지 면은 리본(x640.50~652.2)만 누릅니다. 홈은 리본 끝에서 0.4, 핀 가장자리에서 0.75 떨어집니다.
3) 선택: 화면 덮개 173×108×3 (접은 화면 위, 받침 테두리에 얹힘).

## F. 조립 파일 / 3D
- 화면 상자 166.1×101.0×8.0 (+ 뒤 볼록판 2.1), 커넥터 두 개 표시. 받침·화면은 25° 사용 상태(M = poses.cradle_use), 받침다리는 사용 상태. 접은 상태(poses.cradle_fold)는 별도 보기.
- 변환: world = M·[xr, u, w, 1]. M(25°) = [[1, 0, 0, 611.0], [0, 0.422618, 0.906308, 218.57], [0, 0.906308, -0.422618, 95.0], [0, 0, 0, 1]]. (u, w 좌표계는 왼손계라 det = −1. 오른손계가 필요하면 v = −w를 쓰고 3번째 열 부호를 바꿈.)
- Pi 5(L2 확정): 판 x542.0~627.0, y262.0~318.0, 윗면 z24.1, 회전 0°. CAM/DISP 1 x589~592, y263~278. micro-HDMI(추정) x562.0~585.0, y262.0~269.5, 윗면 z27.3; 방열판(추정) x572.0~583.0, y276.0~293.0.
- 【3a】 3D 모델은 이 사양과 같게 만듭니다.
  - 아래 벽 안쪽 u0(유리가 얹힘), 위 벽 안쪽 u101.5. 보스는 옆벽까지 채웁니다.
  - 귀는 `cradle.ear.profile_uw`, 가로 리브는 u24·u80, 아래 벽 홈을 넣습니다.
  - 리본은 `ribbon.waypoints`(뚜껑 밑 z61.2, Pi에 2.7 꽂음), 전원선은 `power_wire.waypoints`입니다.
  - 클립 핀은 4.5, 뚜껑 나사 자리는 A-7입니다. 미리보기 STL은 출력용이 아닙니다.

## G. 받은 부품으로 확인할 것 (출력 전에)
1) 커넥터가 어느 쪽인지: 사진 3장(Pi 구멍 좌우 반전, 케이블 위치, 전원이 FPC 위)으로 "화면 앞에서 볼 때 커넥터 창이 오른쪽, 입구 +x"로 판단했습니다.
   - 반대면 창·홈·구멍·클립을 x611 기준으로 뒤집습니다. 구멍은 x564.65~586.65이 되어 CAD 권장 x580~602와 거의 같습니다.
   - 그때 리본은 약 200 mm이고 A형(같은 면, 예비로 산 것)입니다. 경첩·다리·패드와 아래 벽 홈(앞모습 기준)은 그대로입니다.
2) 모서리 구멍: 나사산 깊이를 잽니다(C-3 규칙). 동봉 스탠드오프는 달지 않습니다.
   - 【3a】 모서리가 박힌 스터드(도면 옆모습 13.4, 약 5.4 튀어나옴)라서 뗄 수 없으면 보스를 팝니다.
     - Ø6.2(둥근 스터드 5.8 이하 또는 육각 5)로 w8~13.7까지 파고, 보스는 Ø8.6로 키웁니다.
     - 남은 바닥 2.3를 지나 뒤에서 M2.5×6을 스터드 암나사에 조입니다(물림 3.7). 머리는 w16 면 위로 1.8 나옵니다.
     - 뒷판과 축은 그대로입니다. 접었을 때 머리는 뚜껑과 3.7, 받침 발과 평면에서 3.83 떨어집니다.
   - (하지 말 것) 뒷판을 스터드 뒤로 물리면 2.9 mm 뒤로 갑니다. 그러면 축 y229.23, 접은 끝 y341.73(뚜껑 뒤끝과 -0.23 mm)이라 맞지 않습니다.
3) 뒤 볼록판 높이(약 2.1 추정): 2.1보다 높으면 뒷판 안쪽 면 = 8.0 + 높이 + 0.4로 다시 계산.
4) Waveshare MX1.25→3핀 선 길이(약 100~150 추정): 120.54 mm 이상이면 3핀 이음이 뚜껑 밑에 옵니다. 짧으면 경첩 고리 안에 오므로 열수축튜브로 감쌉니다(22×6 구멍 통과 가능).
5) 리본: 받침과 뚜껑을 출력하기 전에 폭 12 mm 종이띠로 길을 잽니다. L2 Pi 자리까지 약 256 mm / 300 mm (여유 44). Pi 자리가 바뀌면 numbers.json `ribbon_table`과 공식으로 다시 봅니다.
6) 뒤꿈치 틈 0.37 mm는 출력 공차와 비슷합니다. 다리 발이 주머니에 잘 안 들어가면 뒤꿈치를 0.3 mm 깎습니다.
7) 【3a】 화면 아래 끝 돌기: 받으면 위치(xr54.99~59.24 추정)와 튀어나온 높이(약 0.85, 1 이하로 봄)를 잽니다. 홈 xr48~66 밖이면 홈을 옮깁니다. 스위치나 슬롯이면 손이 닿는지도 봅니다.
8) 【3a】 실제 Pi 5에서 확인할 것:
   - micro-HDMI 윗면 높이(추정 z27.3)와, 리본이 그 위에 얹혀 입구로 들어가는지.
   - CAM/DISP 1 깊이(CAD 상자 3, 꽂는 길이 2.7).
   - 추정 방열판은 CAD 리본 지킴 구역(x582부터)을 1 mm 넘게 그려져 있습니다. 실제 방열판은 지킴 구역 밖이어야 합니다(리본 끝과 추정 방열판 모서리: y -0.35, x -0.15).
9) 【3a】 뚜껑 레일 인서트 길이(추정 4): 다르면 A-7 식으로 자리파기 깊이를 다시 잡습니다.

## H. 도면·3D 반영 기록 (검사에서 나온 것, 3a에서 모두 반영함 — 2026-10-01)
- 귀(t01 확대 A, t03 단면 C–C): 뒤꿈치 옆 점 (u-17.4, w11.15)을 빼고 `cradle.ear.profile_uw`로 그립니다. 출력 높이는 119.76입니다.
- t03 뒤 모습·F–F: 가로 리브는 u24이고, 축 나사 머리 둘레가 비어 있어야 합니다. 뒤에서 본 모습(좌우 반전)은 왼쪽이 +x이므로 '+x' 글자가 왼쪽에 옵니다(반영).
- t03 앞 모습·아래 단면: 아래 벽 홈 xr48~66.
- t05·t06: 클립 전원선 홈, 핀 4.5, 리본은 HDMI 위에 얹혀 입구로(U자 아님), O4 정비 순서(B).
- t02 J: 평면 자리는 '22~25° y216.0~276.81' 또는 '25° y216.61~276.81'로 씁니다.
- t01: z110.19는 '보이는 영역 아래 끝을 보는 선'입니다(가운데를 보는 선은 y212에서 z157.93). 52.71 치수 글자 가림은 고쳤습니다.
- t04 7번과 이 사양 A-7·B: 뚜껑 고정은 【변경】(L2 CAD 설계)입니다. 자리파기 Ø6.5 × 5.5, 인서트 물림 4. 3D 모델도 이 값입니다(반영).
- 리본 기둥은 x583 그대로입니다(입구 쪽으로 옮기자는 제안은 보강판 규칙을 깸). 추정 HDMI·방열판과 닿는 것은 실제 Pi 5로 확인합니다(G-8).
- 도면 보기 틀과 제목의 x611·뚜껑 범위는 numbers.json에서 계산해 넣어야 자리 블록이 바뀌어도 맞습니다.
