WongyuKoh/Toccata/hardware/pcb/page/circuit.html

## 전자부 회로도

W1(v4 W1+ r4.5) 건반 액션의 전자부 회로도입니다. W1은 센서 바·센서 기판·제어 기판·리본·USB를 이전 설계에서 그대로 가져와 글과 블록도로만 적어 두었는데, 이것을 W1 좌표·자석 위치·기판 외곽에 맞춰 CAD에 그대로 옮길 수 있는 회로도로 만들었습니다. 부품 번호·핀 번호·넷 이름·값·연결을 모두 적었고, 보드 두 장은 실제 구멍 좌표로 부품 자리를 잡았습니다. 기준은 W1 r4.5 좌표 모델(geometry.json 2026-09-29, circuit_r43·circuit_r44 블록)과 DESIGN.md입니다. 모듈 핀 배치는 판매 페이지·데이터시트·위키로 확인했고, 전기 설계 검토에서 나온 필수 수정 3건을 반영했습니다(△ 표시).

### 00W1에서 전자부로 들어오는 값

항목 | W1 값 (r4.3~r4.5) | 회로에 반영한 곳
자석 | Ø5×2 N35, 건반 밑 y67 (센서 소자 열 바로 위), S극 아래 | SCH-02 표, BRD-02
자석 x (센서 x) | C 7.431 · C# 21.215 · D 35.25 · D# 49.285 · E 63.07 · F 77.359 · F# 90.573 · G 104.037 · G# 117.5 · A 130.964 · A# 144.427 · B 157.641; 끝 부속 A0 10.287 · A#0 26.927 · B0 40.141 · C8 11.75(오른쪽 로컬) | SCH-02·04, BRD-02
자석–소자 간격 쉼/강체 바닥/과다 | 백 10.82 / 5.60 / 5.24 mm, 흑 13.35 / 5.32 / 4.76 mm; 1 N 정착 바닥 백 5.52 · 흑 5.47(흑은 강체 바닥보다 0.15 위) | SCH-02 표
센서 출력 (DRV5055A2, 3.3 V) | 백 약 4 → 22 mT (ADC 약 2207 → 2862), 흑 약 2 → 25 mT (2138 → 2962); 최대 31 mT < 선형 ±44 mT. 재무장(자석 복귀 50 %) 백 ADC ≈2373 · 흑 ≈2282, 1 N 바닥 백 ≈2890 · 흑 ≈2907 | SCH-02 표 · A2 형 유지
펌웨어 규칙 | 재무장 = 자석 복귀 50 %. 유령 거름(U6, W1 r4.5 DESIGN 0.1 = gfilter): 같은 건반, 앞끝 0.3 m/s 이상 음의 note-on부터 250 ms 안에 재무장하면 의심 → note-on부터 500 ms 안의 첫 다시 눌림이 min(0.45 m/s, 앞 음 × 25 %)보다 느리면 버림, 500 ms 뒤는 보통 음. 자석 단위: 앞끝 = 자석 × 1.91(백)/1.18(흑), 비율 27.5 / 28.2 % | SCH-03 주 9
제어 기판 외곽 | x47.25~117.25 × y145.5~195.5, 홈 x81.92~84.72 × y≤172 (F|F# 핀 발 y148.6~170.7 + 킬 y144.5~148.6, r4.5), 금지 x81.22~85.42 × y≤173.2 (제로 PCB만 y172~173.2에 걸침) | BRD-01
기판 고정 (r4.4~r4.5) | 바닥 구멍 x46.25~118.25 × y144.5~196.5로 기판을 밑에서 넣음. 매단 Ø6 보스 4개(받침 6 × 7.5 / 6 × 7.3, 밑면 z10.6, 둘레 1.3 부품 없음), M3×6 ×2 밑에서(L35 ISO 7380 Ø5.7 × 1.65), 위치 핀 ×2. J301·J302는 넣기 전에 납땜 | BRD-01 주 8 (△14)
USB 플러그 · 선반 홈 | 홈 x76.45~91.55, 플러그 폭 12.5 → 양옆 1.30. Waveshare 치수도(USB-C가 오른쪽에서 4.67)로 제로를 x75.14에 → 리셉터클 x79.53~88.47 가운데 x84.00 | BRD-01 주 1·3 (△15)
끝 부속 센서 바 (r4.2) · 리드 길 (r4.4) | 왼쪽 x0.5~46.5 (A#0 낮은 구간 x19.93~33.93), 오른쪽 로컬 x0.5~23.0. 레일 밑 차선 EL x13.53~22.48 · ER x7.59~14.00, 뒷벽 홈 z5~12 | SCH-04 주 6, BRD-02 EL·ER (△13)
프레임 레일·리브 | 밸런스 레일 뒷면 y144.5, 선반 리브 앞면 y196.8(x49.4~50.6, x115.4~116.6), 기판 부품 ↔ 프레임 1.3 | BRD-01 고정 자리 (△14)
높이 | 부품 ≤ z20 (y145.8~194.5), 뒤 띠 ≤ z16.7, 제로 PCB z11.9~12.9·부품 ≤ z16.3; 기판 밑은 바닥 구멍(r4.5) | BRD-01 주 3
리본·EXT 경로 | 리본 차선 x59~82 (높이 5.0), 리본 중심 x70.48(J201 = 차선 여유 1.32 / 1.36). J301도 아랫면 납땜, 기판 밑으로. EXT 선: 기판 밑 → USB 플러그 밑 → 뒷벽 개구 | SCH-02·03, BRD-01 주 6·7

9장회로도 7 + 배치도 2 (A3)

6종 보드SB ×7 · MB ×7 · EL · ER · PB · PS + CU 배선

115줄부품표 (KiCad 심볼·풋프린트 포함)

117개넷 (도면마다 다시 계산)

0 / 0연결 검사 오류 / 글자끼리 겹침 (자동)

3줄구매 목록에 반영됨: L67 10 µF 50개 7,150원 · L68 1206 1 kΩ 10개 440원 · 핀헤더 1×40 5 → 9줄

저장 위치: 저장소 hardware/pcb/ — schematic/(SCH-01~07 SVG), board/(BRD-01·02), netlist/(CSV), src/(생성기), README.md(규칙·KiCad 옮기는 순서). 도면은 한 소스에서 만들고, 그린 선·라벨로 연결을 다시 계산해 의도한 넷리스트와 대조했습니다.

### 01도면

1. SCH-01 · 시스템 연결도
2. SCH-02 · 옥타브 센서 기판 (SB ×7)
3. SCH-03 · 옥타브 제어 기판 (MB ×7)
4. SCH-04 · 끝 부속 센서 기판 (EL · ER) + EXT 연결
5. SCH-05 · 페달 보드 (PB) + 댐퍼 페달 센서 (PS)
6. SCH-06 · 전원 (CU)
7. SCH-07 · 오디오 (CU)
8. BRD-01 · 제어 기판 배치 (위에서 봄, 모듈 좌표)
9. BRD-02 · 센서 기판 배치 (SB · EL · ER, 위에서 봄)

">>" 표시는 맞물린 커넥터(플러그–잭)입니다. KiCad에서는 연결이 아니므로 양쪽 핀에 같은 넷 이름을 붙여 두었습니다. 도면을 누르면 크게 볼 수 있고, "2배·3배"로 페이지 안에서 확대해 옆으로 넘겨 볼 수 있습니다. 색: 초록 선 = 배선, 갈색 테두리 = 부품, 파란 상자 = 산 모듈, 점선 갈색 = 케이블, 노란 △ = 이전 글 사양 대비 변경.

SCH-01 · 시스템 연결도맞춤2배3배크게 보기 ↗

SCH-01 · 시스템 연결도

모든 파트·보드와 그 사이 선(W 번호), 선 목록. 파트 사이는 모두 꽂았다 빼는 커넥터(R26). 개정 C: 화면 A605와 W605~W608(△16).

SCH-02 · 옥타브 센서 기판 (SB ×7)맞춤2배3배크게 보기 ↗

SCH-02 · 옥타브 센서 기판 (SB ×7)

DRV5055A2 ×12(U201~U212, 핀 1 VCC · 2 GND · 3 OUT), 센서마다 100 nF, 버스 양 끝 10 µF, 리본 16심 2×8 블록 J201. 표: 센서 x(= W1 자석 x)·먹스 채널·리본 선 번호, W1 자석–소자 간격과 자기장·출력·ADC 범위.

SCH-03 · 옥타브 제어 기판 (MB ×7)맞춤2배3배크게 보기 ↗

SCH-03 · 옥타브 제어 기판 (MB ×7)

RP2040-Zero(A301)가 4067 모듈(A302)의 SIG를 GP26(ADC0)로 읽고 GP2~GP5로 채널을 고른다. GP6~GP8 ID 점퍼, GP14 PED 점퍼, EXT 보호 R301~R308, 테스트 포인트. 표: ID 점퍼·핀 배정.

SCH-04 · 끝 부속 센서 기판 (EL · ER) + EXT 연결맞춤2배3배크게 보기 ↗

SCH-04 · 끝 부속 센서 기판 (EL · ER) + EXT 연결

A0·A#0·B0는 O1, C8은 O7의 EXT로. 기판은 W1 끝 부속 센서 바 안(EL x1.0~46.5, ER x1.0~23.0), 1 kΩ은 아랫면 1206(△13). JST-XH 6P 위치 1 = GND(검정 끝선) … 6 = 3V3(빨강 끝선).

SCH-05 · 페달 보드 (PB) + 댐퍼 페달 센서 (PS)맞춤2배3배크게 보기 ↗

SCH-05 · 페달 보드 (PB) + 댐퍼 페달 센서 (PS)

페달 안 DRV5055 → 1 kΩ → 3 m TRS → PJ-313(TN = GND) → 1 kΩ + 100 nF → GP26. 링 급전 20 Ω, 팁 100 kΩ 풀다운, GP14 = GND → 'Toccata PED'.

SCH-06 · 전원 (CU)맞춤2배3배크게 보기 ↗

SCH-06 · 전원 (CU)

HUSB238 20 V → 5 A 지연 퓨즈 → 로커 스위치 → +20V(앰프) · XL4016 → +5V1(Pi 5 USB-C 리드, 허브 DC). 별 접지점 = 강압 IN−. 표: 전원 예산. 개정 C(△16): 화면 A605 = Pi 40핀 헤더 2·6번 → 점퍼 F/F·M/M → 동봉선 2.54 3핀 → MX1.25 2핀(넷 +5V_PI), DSI 리본 W605, 예산에 화면 포함.

SCH-07 · 오디오 (CU)맞춤2배3배크게 보기 ↗

SCH-07 · 오디오 (CU)

동글 → 볼 헤드폰 잭 J701(노멀 TN·RN) → J702 → 1 µF×2 병렬 + 1 kΩ(AGND) → XH-A232 → XT30 → CW-100B25 ×2(BTL).

BRD-01 · 제어 기판 배치 (위에서 봄, 모듈 좌표)맞춤2배3배크게 보기 ↗

BRD-01 · 제어 기판 배치 (위에서 봄, 모듈 좌표)

5×7 cm 기판 위 RP2040-Zero·4067 모듈·리본 2×8·EXT·보호 저항·점퍼·테스트 포인트의 구멍 좌표. W1 r4.3 홈(x81.92~84.72 × y145.5~172, F|F# 핀 발)과 금지 구역(주황, x81.22~85.42 × y≤173.2). 제로 x75.14(USB-C 가운데 = 선반 홈 가운데 x84.00, △15). 기판은 W1 r4.5 바닥 구멍(점선)으로 밑에서 넣고 매단 보스 4곳에 고정(△14).

BRD-02 · 센서 기판 배치 (SB · EL · ER, 위에서 봄)맞춤2배3배크게 보기 ↗

BRD-02 · 센서 기판 배치 (SB · EL · ER, 위에서 봄)

161.6 × 15.24 SB(오른쪽 턱 기둥과 0.4): 센서 12개 리드 구멍 열, 3V3·GND·OUT 행, 100 nF·10 µF 자리, 리본 2×8 블록, 고정 구멍. 아래: 끝 부속 EL(45.5)·ER(22.0) 기판 — 센서·아랫면 1206 부품·리드 패드·필요한 리브 틈.

### 02이전 글 사양 대비 바꾼 점 (도면의 △)

△ | 도면 | 변경 | 이유 | 부품
1 | SCH-02 | 버스 양 끝 C213·C214 10 µF | 글 사양에는 있으나 구매 목록에 없었음 | 구매: 1206 10 µF 16 V 50개(아이씨뱅큐 P001248090, 7,150원)
2 | SCH-03 | 먹스 VCC–GND C301 100 nF | 모듈 C1이 사진으로만 보여 미확인 | 100 nF 여분
3 | SCH-04 | EL·ER 기판 10 µF | 3V3가 150 + 350 mm 선 끝 | △1과 같은 묶음
4 | SCH-05 | 링 급전 R503 20 Ω (100 Ω ×5 병렬) | TS 플러그·꽂는 순간 3V3–GND 단락 → PED 보드 리셋 (검토 R1, 필수) | 100 Ω 여분
5 | SCH-06 | 별 접지점 = 강압 IN− 단자 | 동글–Pi–강압–앰프 GND 루프 험 (R7) | —
6 | SCH-03·04 | EXT·XH 순서 1 GND · 2~5 EXT1~4 · 6 3V3 | 밸런스선 빨강 1 + 검정 5 → 빨강 = 3V3 | —
7 | SCH-05 | 페달 센서 OUT 뒤 R551 1 kΩ | 3 m 케이블 용량이 OUT에 직결 (TI: OUT에 C 직결 금지) | 1 kΩ 여분
8 | SCH-03·04 | EXT: 센서 옆 1 kΩ 직렬(EL R401~R403, ER R411) + MB 100 kΩ 풀다운(R301~R304, O1 1~3·O7 1만) | 끝 부속을 빼면 입력이 떠서 유령 음 (R4, 필수). 1 kΩ은 약 0.6 m 선 용량을 센서 OUT에서 뗌 | 1 kΩ·100 kΩ 여분
9 | SCH-05 | 페달 잭 TN → GND | 플러그 없으면 팁 = 0 V | —
10 | SCH-07 | AGND: 잭 슬리브·1 kΩ는 앰프 IN G로만 | 험 방지 배선 규칙 | —
11 | SCH-05 | R502 100 kΩ 팁→GND 고정, GP27 안 씀 | 이전 글 사양의 'GP27로 뗀 쪽 전압 구동'은 GPIO가 0/3.3 V만 내서 불가 (R3) | —
12 | SCH-02·03 | 리본 16심 모두 (15 GND, 16 3V3), 2×8 블록 | 끊긴 선 유령 음·전원 여유 (R27), IDC 헤더와 번호 같음 | —
— | BRD-01 | RP2040-Zero를 안쪽 구멍 핀 헤더(몰드 뺌)로, 약 +1.3 mm | 밑면에 칩·수정·LDO가 있어 평평하게 안 붙음. W1 r4.3이 뒤 선반에 플러그 홈을 내 플러그와 1.3 mm | 구매: 핀헤더 1×40 ×4 (144핀)
— | BRD-01 | 모든 구멍을 제로 핀 격자(x76.52+2.54i, y173.59+2.54j)로, 4067 모듈 x54.93~72.71 세로 | 만능기판 한 장의 구멍에 모두 맞게 · W1 r4.3 홈·금지 구역 | —
13 | SCH-04·BRD-02 | EL·ER R401~R403·R411 1 kΩ을 1206 칩(아랫면)으로, 기판을 W1 끝 부속 센서 바 안(EL 45.5, ER 22.0)으로 | 센서 바가 기판 윗면을 모두 덮어 리드형 저항 자리가 없음. W1 r4.2 끝 부속 센서 바 x0.5~46.5 / x0.5~23.0 | 구매: 1206 1 kΩ 10개(아이씨뱅큐 P011433924, 440원)
14 | BRD-01 | 기판 고정 자리 (50.0,149.0)(114.5,149.0)(50.0,192.5)(114.5,192.5) — W1 r4.5 매단 보스, M3×6 밑에서 2 · 위치 핀 2 | v3 P114 자리는 M3 머리가 밸런스 레일과 0.75, 선반 리브와 1.05 (W1 1.3 규칙 위반) | M3×6 = 구매 목록 L35
15 | BRD-01 | 제로를 x75.14로(+0.14), J301 아랫면 납땜 | Waveshare 치수도: USB-C가 오른쪽에서 4.67(가운데보다 0.14 왼쪽) → 플러그를 W1 선반 홈 가운데 x84.00에(양옆 1.30). 리본은 차선 안 중심 x70.48 그대로 | —
— | 전체 | 테스트 포인트 8곳 | 검토 R30 | —
16 | SCH-01·06 | 화면 A605 = Waveshare 7-DSI-TOUCH-C(B1): Pi 헤더 핀 2(5 V)·6(GND) → P603 → W606 F/F 20 cm → X601⇄X602 → W607 M/M 20 cm → X603⇄X604(동봉선 2.54 3핀: 1 빨강 · 2 빈 칸 · 3 검정) → W608 → P604 MX1.25 ⇄ A605. 넷 +5V_PI(Pi 안 5 V 레일, P601 MT666 ← +5V1)·GND. DSI = W605 FFC 22핀 300 mm B형. 예산: 화면 2.15 W, 평균 약 16~20 W, 순간 약 54.4 W, 60 W 여유 약 5.6 W, 45 W면 −2 dB | R31(10/1 B1 선택). D16: 화면은 Pi에서 나가는 방향으로만. D19 여유. D14: 화면·경첩·다리에 자석 없음 | 구매 목록 v4touch No.135 · No.49·50 · No.51~54 (반영됨)

W1 기구와 맞춘 것. RP2040-Zero는 밑면에 칩·수정·LDO가 있어 핀 헤더로 세웠고(약 +1.3 mm), W1 r4.3이 뒤 선반에 USB 플러그 위 홈을 내어 플러그와 선반 사이 1.3 mm를 되찾았습니다. 제어 기판 배치(BRD-01)도 r4.3 형상 검사에 들어가 기판 부품 ↔ 프레임 최소 1.3 mm입니다.

### 02bW1 기구 쪽에 요청한 것과 반영 결과 (W1 r4.4~r4.5)

# | 회로가 요청한 것 | W1 결과

1 | 제어 기판 부품 자리를 격자 좌표로: 제로 x75.14~93.14 × y172.0~195.5, 4067 x54.93~72.71 × y152.0~192.64, J301 x61.28~79.06 × y148.19/150.73(아랫면 납땜, 리본 기판 밑 z5~9), J302 x94.30~107.00 × y193.91 | 반영. 리셉터클 x79.53~88.47 그대로
2 | USB 플러그 면 y약 196.8(리셉터클이 제로 밖으로 1.0~1.5), 몰드 y196.8~221.8 | 반영. 선반 홈 x76.45~91.55 틈 1.30, 뒷벽 개구 z5~21 틈 2.70
3 | 제어 기판 고정 4곳 (50.0,149.0)(114.5,149.0)(114.5,192.5)(50.0,192.5) | 바뀜: 한 덩어리 프레임에 기판을 넣을 길이 없어 기판 밑 바닥을 뚫고(x46.25~118.25 × y144.5~196.5, 리셉터클 뒤 y197.8) 밑에서 넣음. 받침 = 위에 매단 Ø6 보스(밑면 z10.6), M3×6 ×2 밑에서(ISO 7380 머리 Ø5.7 × 1.65: 레일 1.65, 리브 1.45, 기판 모서리 밖 0.10), 위치 핀 ×2(놀음 0.10), 넣는 길 틈 0.60
4 | 끝 부속 센서 기판 받침·뒤 리브 틈(EL x15~38, ER x6~16)·리드 길 | 반영: 레일 밑 차선 EL x13.53~22.48 · ER x7.59~14.00 (z5~10), 뒷벽 홈 z5~12, 리드는 y77.39 안에서 EL x14.83~21.18 · ER x8.89~12.70으로 모음
5 | SB 뒤 받침 리브 틈 x60~82 → x59~82 | 반영 (리본 양옆 1.32 / 1.36)
6 | 금지 구역과 제로 PCB 겹침 정리 | 금지 구역 y173.2 그대로, 제로 PCB가 y172.0~173.2에 걸친다고 P23에 기록
7 | C301 = 1206 칩, 레버가 떨어지는 곳 | 반영: D#·G# 매단 보스, E·F 4067 위(13.25°), F#·G 기판 윗면, O1·O7의 G R301 위(0.40 N)
+ | F|F# 핀 발 | r4.5: 바닥 대신 킬(y144.5~148.6, z3~19.3)로 밸런스 레일 뒷면에 붙음, 핀 앞끝 y152 → y148.6 — 둘 다 기판 홈 안이라 회로 변화 없음
8 | (2차) 센서 바 오른쪽 턱(v3 P112)을 모델에 넣거나, 턱 없이 바 오른쪽 끝을 무엇이 잡는지 P36에 적기 | 반영(r4.5 회로 2차): 두 조각 ㄱ자 턱, 립 x161.5~163.0 z13.6~15.1, 기둥 x163.0~164.3. 회로: SB를 x162.6까지(기둥과 0.4). EL·ER은 턱 없이 왼쪽 M3 ×2 + 리브
9 | (2차) 유령 거름 글을 gfilter와 같게(창 = note-on부터 재무장까지 250 ms), 유령이 다시 닿는 시각을 구해 '다시 눌림 시각 상한' 정하기 | 반영: note-on부터 250 ms 안 재무장 → 의심, note-on부터 500 ms 안의 첫 다시 눌림만 판정. 재무장 28건을 1.5 s까지 돌려 스스로 다시 닿는 것 0건(흔들림 ≤ 222 ms) — 500 ms는 약 2배, 시험 11에서 확인
10 | (2차) DESIGN §11 6단계: D#·G# 레버는 매단 보스 위(16.75°) | 반영: D#·G# 매단 보스 16.75°, F#·G 기판 윗면 24.00 / 23.50°, E·F 4067 13.25°
11 | (2차) EL 바닥에 새어 든 기판 구멍 자르기 틈 x46.25~46.8 × y144.5~196.5 없애기 | 반영: EL 바닥 한 조각(x0.2~46.8)
12 | (2차) 구매 목록 글: L35 용도(매단 보스·밑에서), SE4에 MB C301 ×7(97개 사용), L20·L21 = 건반 88 + 페달 1, 엑셀 제목 r4.5 | 반영: L35 매단 보스·밑에서, SE4 97개 사용·예비 3, L20·L21 89개·예비 11, 제목 r4.5 (합계 1,060,470원 그대로)
13 | (2차) 단계 0 시험 21 뒤 리본 차선이 바뀌면 알리기 | 바뀐 것 없음 — 시험 21 결과가 나오면 W1이 알림

### 02c구매 목록에 넣거나 고칠 줄

2026-09-29 구매 목록(엑셀·07 탭 선택기)에 모두 반영됐습니다(새 줄 L67·L68). 기록으로 남깁니다.

줄 | 바꿀 내용 | 근거
L67 (반영) | 1206 10 µF 16 V 50개 (아이씨뱅큐 P001248090, 7,150원) ×1 — SB C213·C214 ×7 + EL C404 + ER C412 = 16개 | △1·△3
L68 (반영) | Yageo RC1206JR-071KL 1206 1 kΩ 10개 (아이씨뱅큐 P011433924, 44원 × 10 = 440원, VAT 포함) — EL R401~R403 + ER R411 = 4개 | △13
SE7 핀헤더 1×40 | 5 → 9줄 (먹스 7 × (16+8) = 168핀 + 제로 8 × 18 = 144핀) | 제로를 핀 헤더로
SE7 핀헤더 소켓 1×40 | 빼기 (EXT는 L66 JST-XH를 패드에 직접 납땜, 암 헤더 안 씀) | J302·J401·J411 = 패드만
SEV2 RP2040-Zero 용도 | '캐스털레이션 직접 납땜' → '안쪽 구멍 핀 헤더 1×9 ×2(몰드 뺌), 캡톤 위 약 +1.3 mm' | BRD-01 주 3
L29 1 kΩ·100 kΩ·100 Ω 용도 | 1 kΩ: R701·R702·R501·R551 / 100 kΩ: R301(O1·O7)·R302·R303·R502 / 100 Ω: R503 20 Ω = 100 Ω ×5 병렬(필수) | bom.csv
C05 리본 용도 | 리본 16심 전부(OUT 12 + 3V3 ×2 + GND ×2) ×7 + EL·ER 리드 가닥 | △12
L66 용도 | 200 mm 연장선을 모듈 쪽 150 · 끝 부속 쪽 50으로 자름 (가운데 자르면 100이라 모자람) | W403·W413 150 mm
C04 USB 케이블 (반영) | 몰드 ≤ 12.5 × 7.6 × 25 — 폭이 넘으면 안 들어감(선반 홈과 한쪽 1.30). 지금 NA993은 두께 미공개 → 단계 0 시험 19로 확인, 대안 CVILUX DH-20M50052(11.97 × 6.42 × 20.93) | W1 r4.5 1d-3
L56 1 µF 용도 | '약 80 Hz' → '약 93 Hz' (1 kΩ + 앰프 입력 9 kΩ) | SCH-07
(선택) L29 10 kΩ | 회로에서 쓰지 않음(예비로 둘지 선택) | bom.csv
L01 Raspberry Pi 5 용도 (10/1 새로 고칠 글) | '(R25: HAT 없음, GPIO 배선 없음)' → 'HAT 없음. GPIO는 헤더 2·6번에서 화면 5 V만 나감(R31)' | △16

### 03부품이 오면 먼저 확인할 것

항목 | 확인
PD 트리거 | 무부하로 전원마다 20 V. 20 V 3 A(60 W) 보조배터리는 HUSB238이 3.25 A를 요구해 15·12·5 V로 떨어질 수 있다.
XL4016 | 무부하 5.10~5.15 V에 맞추고 가변저항 고정 뒤 연결. MT666 빨강 = +, 허브 선 중심 = + 확인.
PJ-313 ×3 | 플러그 없음: T–TN, R–RN 닫힘이어야 한다. 노멀 없는 제품이면 헤드폰 차단(R15)이 안 된다.
RP2040-Zero | 복제품: LDO 표시(5핀 RT9013·ME6217) 확인, O1 3V3 전류 60~130 mA, 부팅 불안하면 XOSC 지연 64.
센서 | 자석 없이 1.59~1.71 V, S극을 표시면에 가까이 하면 오름. 건반을 얹은 쉼 백 ≈1.78 · 흑 ≈1.72 V, 바닥 백 ≈2.31 · 흑 ≈2.39 V(±10 %). EXT를 빼면 0.15 V 아래.
페달 | 꽂은 상태 링–슬리브 3.05 V 이상, 뺀 상태 팁 약 0 V.
앰프·스피커 | 36 dB 이득 확인 → 소프트웨어 음량 상한. 스피커 Re 6~7 Ω(4 Ω 판매분 주의).
허브 | Pi 선을 뺐을 때 Pi 5V 핀 0 V(역급전 없음).
화면 (△16) | 동봉선 2.54 3핀 하우징 = 1 빨강 5 V · 2 빈 칸 · 3 검정 GND인지 통전 검사 뒤 점퍼 연결. 화면 쪽 5 V를 부하 때 잼(점퍼 왕복 강하 계산 약 0.05 V). 최대 부하에서 vcgencmd get_throttled = 0x0(Pi 입력 약 2.0 A). 화면 켬·끔, 밝기 0·100 %에서 센서 유휴 흔들림 다시 잼(D14). config.txt: dtoverlay=vc4-kms-dsi-waveshare-panel-v2,7_0_inch_c.

### 04KiCad로 옮기는 순서

1. 프로젝트를 보드별로: octave-sensor(SB), octave-control(MB, PB 겸용 가능), end-parts, pedal-sensor, 문서용 cu-wiring. 한 PCB에 7장을 넣지 않는다.
2. 라이브러리: 아래 부품표의 KiCad 심볼·풋프린트 열. 직접 만들 것 = 4067 모듈 심볼·풋프린트, PJ-313 풋프린트(패드 이름 T/TN/R/RN/S), 모듈 심볼(HUSB238·XL4016·XH-A232·동글·RaspberryPi5 헤더 유닛·Waveshare 7-DSI-TOUCH-C), 전원 심볼 +20V·+5V1·+5V_PI.
3. RP2040-Zero는 dj505/RP2040-Zero-KiCAD 라이브러리(패드 번호 = 이 도면), 3V3 핀을 power_out으로. DRV5055는 Sensor_Magnetic:DRV5055A2xLPGxQ1, Value를 DRV5055A2QLPG로.
4. 번호 매기기: Annotate → First free after sheet number × 100, X 위치순 — 이 도면과 같은 번호가 나온다.
5. ERC: 선으로 들어오는 전원(SB의 +3V3, +3V3_EL·+3V3_ER, +20V, +5V1, +5V_PI, PS의 PED_VCC, 각 GND)에 PWR_FLAG. GND·+3V3는 로컬 라벨이 아니라 전원 심볼로. +3V3_EL·+3V3_ER도 프로젝트 전원 심볼로 추가.
6. 외곽·자리: BRD-01·02 좌표. 제어 기판은 x81.22~85.42 × y145.5~173.2(W1 r4.3) 비움, 홈 x81.92~84.72 × y145.5~172.0 따냄. EL·ER 기판은 BRD-02 아래 그림.

### 05부품표 (KiCad 심볼·풋프린트, 구매 목록 코드)

"전체 수량" = 보드 수 × 보드당, MB의 보호 저항은 실장하는 보드만 셈. 구매 목록 코드는 v4 재료 목록(xlsx)의 부품 코드입니다. 부품 사진·가격은 재료·절감 선택 탭에 있습니다.

SCH-02 · 센서 기판 SB — 27줄

보드 | 부품 | 값 | 설명 | 보드 수 | 보드당 | 전체 | 실장 | KiCad 심볼 | KiCad 풋프린트 | 코드
SB | U201 | DRV5055A2QLPG | TI DRV5055A2QLPG, TO-92-3 (LPG) | 7 | 1 | 7 | | Sensor_Magnetic:DRV5055A2xLPGxQ1 (Value = DRV5055A2QLPG) | Package_TO_SOT_THT:TO-92_Inline_W4.0mm_Horizontal_FlatSideUp → 2.54 간격으로 복사 수정 | L20
SB | C201 | 100n | Samsung CL31B104KCFNNNE 1206 100 nF 100 V X7R | 7 | 1 | 7 | | Device:C | Capacitor_SMD:C_1206_3216Metric_Pad1.33x1.80mm_HandSolder | SE4
SB | U202 | DRV5055A2QLPG | TI DRV5055A2QLPG, TO-92-3 (LPG) | 7 | 1 | 7 | | Sensor_Magnetic:DRV5055A2xLPGxQ1 (Value = DRV5055A2QLPG) | Package_TO_SOT_THT:TO-92_Inline_W4.0mm_Horizontal_FlatSideUp → 2.54 간격으로 복사 수정 | L20
SB | C202 | 100n | Samsung CL31B104KCFNNNE 1206 100 nF 100 V X7R | 7 | 1 | 7 | | Device:C | Capacitor_SMD:C_1206_3216Metric_Pad1.33x1.80mm_HandSolder | SE4
SB | U203 | DRV5055A2QLPG | TI DRV5055A2QLPG, TO-92-3 (LPG) | 7 | 1 | 7 | | Sensor_Magnetic:DRV5055A2xLPGxQ1 (Value = DRV5055A2QLPG) | Package_TO_SOT_THT:TO-92_Inline_W4.0mm_Horizontal_FlatSideUp → 2.54 간격으로 복사 수정 | L20
SB | C203 | 100n | Samsung CL31B104KCFNNNE 1206 100 nF 100 V X7R | 7 | 1 | 7 | | Device:C | Capacitor_SMD:C_1206_3216Metric_Pad1.33x1.80mm_HandSolder | SE4
SB | U204 | DRV5055A2QLPG | TI DRV5055A2QLPG, TO-92-3 (LPG) | 7 | 1 | 7 | | Sensor_Magnetic:DRV5055A2xLPGxQ1 (Value = DRV5055A2QLPG) | Package_TO_SOT_THT:TO-92_Inline_W4.0mm_Horizontal_FlatSideUp → 2.54 간격으로 복사 수정 | L20
SB | C204 | 100n | Samsung CL31B104KCFNNNE 1206 100 nF 100 V X7R | 7 | 1 | 7 | | Device:C | Capacitor_SMD:C_1206_3216Metric_Pad1.33x1.80mm_HandSolder | SE4
SB | U205 | DRV5055A2QLPG | TI DRV5055A2QLPG, TO-92-3 (LPG) | 7 | 1 | 7 | | Sensor_Magnetic:DRV5055A2xLPGxQ1 (Value = DRV5055A2QLPG) | Package_TO_SOT_THT:TO-92_Inline_W4.0mm_Horizontal_FlatSideUp → 2.54 간격으로 복사 수정 | L20
SB | C205 | 100n | Samsung CL31B104KCFNNNE 1206 100 nF 100 V X7R | 7 | 1 | 7 | | Device:C | Capacitor_SMD:C_1206_3216Metric_Pad1.33x1.80mm_HandSolder | SE4
SB | U206 | DRV5055A2QLPG | TI DRV5055A2QLPG, TO-92-3 (LPG) | 7 | 1 | 7 | | Sensor_Magnetic:DRV5055A2xLPGxQ1 (Value = DRV5055A2QLPG) | Package_TO_SOT_THT:TO-92_Inline_W4.0mm_Horizontal_FlatSideUp → 2.54 간격으로 복사 수정 | L20
SB | C206 | 100n | Samsung CL31B104KCFNNNE 1206 100 nF 100 V X7R | 7 | 1 | 7 | | Device:C | Capacitor_SMD:C_1206_3216Metric_Pad1.33x1.80mm_HandSolder | SE4
SB | U207 | DRV5055A2QLPG | TI DRV5055A2QLPG, TO-92-3 (LPG) | 7 | 1 | 7 | | Sensor_Magnetic:DRV5055A2xLPGxQ1 (Value = DRV5055A2QLPG) | Package_TO_SOT_THT:TO-92_Inline_W4.0mm_Horizontal_FlatSideUp → 2.54 간격으로 복사 수정 | L20
SB | C207 | 100n | Samsung CL31B104KCFNNNE 1206 100 nF 100 V X7R | 7 | 1 | 7 | | Device:C | Capacitor_SMD:C_1206_3216Metric_Pad1.33x1.80mm_HandSolder | SE4
SB | U208 | DRV5055A2QLPG | TI DRV5055A2QLPG, TO-92-3 (LPG) | 7 | 1 | 7 | | Sensor_Magnetic:DRV5055A2xLPGxQ1 (Value = DRV5055A2QLPG) | Package_TO_SOT_THT:TO-92_Inline_W4.0mm_Horizontal_FlatSideUp → 2.54 간격으로 복사 수정 | L20
SB | C208 | 100n | Samsung CL31B104KCFNNNE 1206 100 nF 100 V X7R | 7 | 1 | 7 | | Device:C | Capacitor_SMD:C_1206_3216Metric_Pad1.33x1.80mm_HandSolder | SE4
SB | U209 | DRV5055A2QLPG | TI DRV5055A2QLPG, TO-92-3 (LPG) | 7 | 1 | 7 | | Sensor_Magnetic:DRV5055A2xLPGxQ1 (Value = DRV5055A2QLPG) | Package_TO_SOT_THT:TO-92_Inline_W4.0mm_Horizontal_FlatSideUp → 2.54 간격으로 복사 수정 | L20
SB | C209 | 100n | Samsung CL31B104KCFNNNE 1206 100 nF 100 V X7R | 7 | 1 | 7 | | Device:C | Capacitor_SMD:C_1206_3216Metric_Pad1.33x1.80mm_HandSolder | SE4
SB | U210 | DRV5055A2QLPG | TI DRV5055A2QLPG, TO-92-3 (LPG) | 7 | 1 | 7 | | Sensor_Magnetic:DRV5055A2xLPGxQ1 (Value = DRV5055A2QLPG) | Package_TO_SOT_THT:TO-92_Inline_W4.0mm_Horizontal_FlatSideUp → 2.54 간격으로 복사 수정 | L20
SB | C210 | 100n | Samsung CL31B104KCFNNNE 1206 100 nF 100 V X7R | 7 | 1 | 7 | | Device:C | Capacitor_SMD:C_1206_3216Metric_Pad1.33x1.80mm_HandSolder | SE4
SB | U211 | DRV5055A2QLPG | TI DRV5055A2QLPG, TO-92-3 (LPG) | 7 | 1 | 7 | | Sensor_Magnetic:DRV5055A2xLPGxQ1 (Value = DRV5055A2QLPG) | Package_TO_SOT_THT:TO-92_Inline_W4.0mm_Horizontal_FlatSideUp → 2.54 간격으로 복사 수정 | L20
SB | C211 | 100n | Samsung CL31B104KCFNNNE 1206 100 nF 100 V X7R | 7 | 1 | 7 | | Device:C | Capacitor_SMD:C_1206_3216Metric_Pad1.33x1.80mm_HandSolder | SE4
SB | U212 | DRV5055A2QLPG | TI DRV5055A2QLPG, TO-92-3 (LPG) | 7 | 1 | 7 | | Sensor_Magnetic:DRV5055A2xLPGxQ1 (Value = DRV5055A2QLPG) | Package_TO_SOT_THT:TO-92_Inline_W4.0mm_Horizontal_FlatSideUp → 2.54 간격으로 복사 수정 | L20
SB | C212 | 100n | Samsung CL31B104KCFNNNE 1206 100 nF 100 V X7R | 7 | 1 | 7 | | Device:C | Capacitor_SMD:C_1206_3216Metric_Pad1.33x1.80mm_HandSolder | SE4
SB | C213 | 10µ | C3216-10UF(K 16V) 1206 10 µF 16 V (50개 단위) | 7 | 1 | 7 | | Device:C | Capacitor_SMD:C_1206_3216Metric_Pad1.33x1.80mm_HandSolder | L67
SB | C214 | 10µ | C3216-10UF(K 16V) 1206 10 µF 16 V (50개 단위) | 7 | 1 | 7 | | Device:C | Capacitor_SMD:C_1206_3216Metric_Pad1.33x1.80mm_HandSolder | L67
SB | J201 | 리본 16심 → 2×8 구멍 (2.54) | EUNSUNG 2651-16P 플랫 케이블 (16심 전부 사용) | 7 | 1 | 7 | | Connector_Generic:Conn_02x08_Odd_Even | Connector_PinHeader_2.54mm:PinHeader_2x08_P2.54mm_Vertical (패드만, 리본 직접 납땜) | C05

SCH-03 · 제어 기판 MB — 18줄

보드 | 부품 | 값 | 설명 | 보드 수 | 보드당 | 전체 | 실장 | KiCad 심볼 | KiCad 풋프린트 | 코드
MB | J301 | 리본 16심 입력 2×8 | EUNSUNG 2651-16P 플랫 케이블 (16심 전부 사용) | 7 | 1 | 7 | | Connector_Generic:Conn_02x08_Odd_Even | Connector_PinHeader_2.54mm:PinHeader_2x08_P2.54mm_Vertical (패드만, 리본 직접 납땜) | C05
MB | A302 | CD74HC4067 16채널 먹스 모듈 | CD74HC4067 16채널 먹스 모듈 (파츠파츠 PP-A324) | 7 | 1 | 7 | | Toccata:CD74HC4067_Breakout (직접 만듦, 핀 1~16 C0~C15, 17~24 J2) | Toccata:CD74HC4067_Breakout_40.6x17.8 (행 간격 15.24) 또는 PinHeader_1x16 + PinHeader_1x08 | SEV2
MB | A302-HDR | 1×16 + 1×8 | 핀헤더 1×40 2.54 mm (자름) — 먹스 모듈 1×16 + 1×8 | 7 | 24 | 168 | 모듈에 수 헤더가 들어 있으면 안 삼 | — | Connector_PinHeader_2.54mm (풋프린트는 A 줄 참조) | SE7
MB | C301 | 100n | Samsung CL31B104KCFNNNE 1206 100 nF 100 V X7R | 7 | 1 | 7 | | Device:C | Capacitor_SMD:C_1206_3216Metric_Pad1.33x1.80mm_HandSolder | SE4
MB | A301 | RP2040-Zero | Waveshare RP2040-Zero (파츠파츠 PP-A799-2) | 7 | 1 | 7 | | dj505/RP2040-Zero-KiCAD : RP2040-Zero (3V3 핀을 power_out으로) | bobu01/RP2040-Zero-Kicad-Footprint-1mm 또는 dj505 풋프린트를 1.0 mm 드릴로 복사 (핀 헤더용, 번호는 dj505 그대로) | SEV2
MB | A301-HDR | 1×9 ×2 | 핀헤더 1×40 2.54 mm — RP2040-Zero용 1×9 ×2 (먹스 168 + 제로 144 = 312핀 → 1×40 9줄) | 7 | 18 | 126 | 좌·우 열만 (아래 줄 없음), 몰드 뺌 | — | Connector_PinHeader_2.54mm (풋프린트는 A 줄 참조) | SE7
MB | JP304 | 열림 | SolderJumper_2_Open | 7 | 1 | 7 | 모두 열림 (PB는 JP504) | Jumper:SolderJumper_2_Open | Jumper:SolderJumper-2_P1.3mm_Open_Pad1.0x1.5mm (만능기판: 두 구멍 브리지)
MB | JP301 | | SolderJumper_2_Open | 7 | 1 | 7 | O1·O3·O5·O7 닫음 | Jumper:SolderJumper_2_Open | Jumper:SolderJumper-2_P1.3mm_Open_Pad1.0x1.5mm (만능기판: 두 구멍 브리지)
MB | JP302 | | SolderJumper_2_Open | 7 | 1 | 7 | O2·O3·O6·O7 닫음 | Jumper:SolderJumper_2_Open | Jumper:SolderJumper-2_P1.3mm_Open_Pad1.0x1.5mm (만능기판: 두 구멍 브리지)
MB | JP303 | | SolderJumper_2_Open | 7 | 1 | 7 | O4~O7 닫음 | Jumper:SolderJumper_2_Open | Jumper:SolderJumper-2_P1.3mm_Open_Pad1.0x1.5mm (만능기판: 두 구멍 브리지)
MB | J302 | EXT 패드 1×6 (2.54) | 패드만 — L66 모듈 쪽 리드를 아랫면에서 직접 납땜 (헤더 없음) | 7 | 1 | 7 | O1·O7만 L66 모듈 쪽 리드(W403·W413)를 아랫면에서 납땜, O2~O6 비움 | Connector_Generic:Conn_01x06 | Connector_PinHeader_2.54mm:PinHeader_1x06_P2.54mm_Vertical (패드만)
MB | R301 | 100k | 탄소피막 1/4 W 5 % 100 kΩ | 7 | 1 | 2 | O1·O7 | Device:R | Resistor_THT:R_Axial_DIN0207_L6.3mm_D2.5mm_P7.62mm_Horizontal | L29
MB | R302 | 100k | 탄소피막 1/4 W 5 % 100 kΩ | 7 | 1 | 1 | O1 | Device:R | Resistor_THT:R_Axial_DIN0207_L6.3mm_D2.5mm_P7.62mm_Horizontal | L29
MB | R303 | 100k | 탄소피막 1/4 W 5 % 100 kΩ | 7 | 1 | 1 | O1 | Device:R | Resistor_THT:R_Axial_DIN0207_L6.3mm_D2.5mm_P7.62mm_Horizontal | L29
MB | R304 | 100k | 탄소피막 1/4 W 5 % 100 kΩ | 7 | 1 | 0 | 없음 (비움) | Device:R | Resistor_THT:R_Axial_DIN0207_L6.3mm_D2.5mm_P7.62mm_Horizontal | L29
MB | TP301 | | TestPoint | 7 | 1 | 7 | | Connector:TestPoint | TestPoint:TestPoint_THTPad_D1.5mm_Drill0.7mm
MB | TP302 | | TestPoint | 7 | 1 | 7 | | Connector:TestPoint | TestPoint:TestPoint_THTPad_D1.5mm_Drill0.7mm
MB | TP303 | | TestPoint | 7 | 1 | 7 | | Connector:TestPoint | TestPoint:TestPoint_THTPad_D1.5mm_Drill0.7mm

SCH-04 · 끝 부속 EL·ER — 20줄

보드 | 부품 | 값 | 설명 | 보드 수 | 보드당 | 전체 | 실장 | KiCad 심볼 | KiCad 풋프린트 | 코드
EL | U401 | DRV5055A2QLPG | TI DRV5055A2QLPG, TO-92-3 (LPG) | 1 | 1 | 1 | | Sensor_Magnetic:DRV5055A2xLPGxQ1 (Value = DRV5055A2QLPG) | Package_TO_SOT_THT:TO-92_Inline_W4.0mm_Horizontal_FlatSideUp → 2.54 간격으로 복사 수정 | L20
EL | R401 | 1k | Yageo RC1206JR-071KL 1206 1 kΩ 5 % 1/4 W (10개 단위) | 1 | 1 | 1 | | Device:R | Resistor_SMD:R_1206_3216Metric_Pad1.30x1.75mm_HandSolder (아랫면) | L68
EL | C401 | 100n | Samsung CL31B104KCFNNNE 1206 100 nF 100 V X7R | 1 | 1 | 1 | | Device:C | Capacitor_SMD:C_1206_3216Metric_Pad1.33x1.80mm_HandSolder | SE4
EL | U402 | DRV5055A2QLPG | TI DRV5055A2QLPG, TO-92-3 (LPG) | 1 | 1 | 1 | | Sensor_Magnetic:DRV5055A2xLPGxQ1 (Value = DRV5055A2QLPG) | Package_TO_SOT_THT:TO-92_Inline_W4.0mm_Horizontal_FlatSideUp → 2.54 간격으로 복사 수정 | L20
EL | R402 | 1k | Yageo RC1206JR-071KL 1206 1 kΩ 5 % 1/4 W (10개 단위) | 1 | 1 | 1 | | Device:R | Resistor_SMD:R_1206_3216Metric_Pad1.30x1.75mm_HandSolder (아랫면) | L68
EL | C402 | 100n | Samsung CL31B104KCFNNNE 1206 100 nF 100 V X7R | 1 | 1 | 1 | | Device:C | Capacitor_SMD:C_1206_3216Metric_Pad1.33x1.80mm_HandSolder | SE4
EL | U403 | DRV5055A2QLPG | TI DRV5055A2QLPG, TO-92-3 (LPG) | 1 | 1 | 1 | | Sensor_Magnetic:DRV5055A2xLPGxQ1 (Value = DRV5055A2QLPG) | Package_TO_SOT_THT:TO-92_Inline_W4.0mm_Horizontal_FlatSideUp → 2.54 간격으로 복사 수정 | L20
EL | R403 | 1k | Yageo RC1206JR-071KL 1206 1 kΩ 5 % 1/4 W (10개 단위) | 1 | 1 | 1 | | Device:R | Resistor_SMD:R_1206_3216Metric_Pad1.30x1.75mm_HandSolder (아랫면) | L68
EL | C403 | 100n | Samsung CL31B104KCFNNNE 1206 100 nF 100 V X7R | 1 | 1 | 1 | | Device:C | Capacitor_SMD:C_1206_3216Metric_Pad1.33x1.80mm_HandSolder | SE4
EL | C404 | 10µ | C3216-10UF(K 16V) 1206 10 µF 16 V (50개 단위) | 1 | 1 | 1 | | Device:C | Capacitor_SMD:C_1206_3216Metric_Pad1.33x1.80mm_HandSolder | L67
EL | J401 | 리드선 패드 ×5 | Conn_pads | 1 | 1 | 1 | | Connector_Generic:Conn_01x0N (J401 = 01x05, J411 = 01x03) | Connector_PinHeader_2.54mm:PinHeader_1x05 / 1x03_P2.54mm_Vertical (패드만)
EL | X401 | JST-XH 6P (끝 부속 쪽) | JST-XH 6핀 밸런스 연장선 5S 200 mm (모듈 쪽 150 · 끝 부속 쪽 50으로 잘라 씀) | 1 | 1 | 1 | | Connector_Generic:Conn_01x06 | 보드 밖 (Exclude from board) — 선 대 선 커넥터 | L66
EL | X402 | JST-XH 6P (모듈 쪽) | JST-XH 6핀 밸런스 연장선 5S 200 mm (모듈 쪽 150 · 끝 부속 쪽 50으로 잘라 씀) | 1 | 1 | 1 | | Connector_Generic:Conn_01x06 | 보드 밖 (Exclude from board) — 선 대 선 커넥터 | L66
ER | U411 | DRV5055A2QLPG | TI DRV5055A2QLPG, TO-92-3 (LPG) | 1 | 1 | 1 | | Sensor_Magnetic:DRV5055A2xLPGxQ1 (Value = DRV5055A2QLPG) | Package_TO_SOT_THT:TO-92_Inline_W4.0mm_Horizontal_FlatSideUp → 2.54 간격으로 복사 수정 | L20
ER | R411 | 1k | Yageo RC1206JR-071KL 1206 1 kΩ 5 % 1/4 W (10개 단위) | 1 | 1 | 1 | | Device:R | Resistor_SMD:R_1206_3216Metric_Pad1.30x1.75mm_HandSolder (아랫면) | L68
ER | C411 | 100n | Samsung CL31B104KCFNNNE 1206 100 nF 100 V X7R | 1 | 1 | 1 | | Device:C | Capacitor_SMD:C_1206_3216Metric_Pad1.33x1.80mm_HandSolder | SE4
ER | C412 | 10µ | C3216-10UF(K 16V) 1206 10 µF 16 V (50개 단위) | 1 | 1 | 1 | | Device:C | Capacitor_SMD:C_1206_3216Metric_Pad1.33x1.80mm_HandSolder | L67
ER | J411 | 리드선 패드 ×3 | Conn_pads | 1 | 1 | 1 | | Connector_Generic:Conn_01x0N (J401 = 01x05, J411 = 01x03) | Connector_PinHeader_2.54mm:PinHeader_1x05 / 1x03_P2.54mm_Vertical (패드만)
ER | X411 | JST-XH 6P (끝 부속 쪽) | JST-XH 6핀 밸런스 연장선 5S 200 mm (모듈 쪽 150 · 끝 부속 쪽 50으로 잘라 씀) | 1 | 1 | 1 | | Connector_Generic:Conn_01x06 | 보드 밖 (Exclude from board) — 선 대 선 커넥터 | L66
ER | X412 | JST-XH 6P (모듈 쪽) | JST-XH 6핀 밸런스 연장선 5S 200 mm (모듈 쪽 150 · 끝 부속 쪽 50으로 잘라 씀) | 1 | 1 | 1 | | Connector_Generic:Conn_01x06 | 보드 밖 (Exclude from board) — 선 대 선 커넥터 | L66

SCH-05 · 페달 PB·PS — 14줄

보드 | 부품 | 값 | 설명 | 보드 수 | 보드당 | 전체 | 실장 | KiCad 심볼 | KiCad 풋프린트 | 코드
PS | U551 | DRV5055A2QLPG | TI DRV5055A2QLPG, TO-92-3 (LPG) | 1 | 1 | 1 | | Sensor_Magnetic:DRV5055A2xLPGxQ1 (Value = DRV5055A2QLPG) | Package_TO_SOT_THT:TO-92_Inline_W4.0mm_Horizontal_FlatSideUp → 2.54 간격으로 복사 수정 | L20
PS | C551 | 100n | Samsung CL31B104KCFNNNE 1206 100 nF 100 V X7R | 1 | 1 | 1 | | Device:C | Capacitor_SMD:C_1206_3216Metric_Pad1.33x1.80mm_HandSolder | SE4
PS | R551 | 1k | 탄소피막 1/4 W 5 % 1 kΩ | 1 | 1 | 1 | | Device:R | Resistor_THT:R_Axial_DIN0207_L6.3mm_D2.5mm_P7.62mm_Horizontal | L29
PS | P501 | TRS 플러그 (PS 쪽) | Plug_TRS | 1 | 1 | 1 | | Connector_Audio:AudioPlug3 | 보드 밖 (Exclude from board)
PB | J501 | PJ-313 페달 잭 | BSUN PJ-313 3.5 mm 스테레오 잭 (노멀 접점) | 1 | 1 | 1 | | Connector_Audio:AudioJack3_SwitchTR (핀 번호 = T, TN, R, RN, S) | 직접 만듦 Toccata:Jack_3.5mm_PJ-313 — 패드 이름을 T/TN/R/RN/S로 (통전 검사로 확인) | L15
PB | R501 | 1k | 탄소피막 1/4 W 5 % 1 kΩ | 1 | 1 | 1 | | Device:R | Resistor_THT:R_Axial_DIN0207_L6.3mm_D2.5mm_P7.62mm_Horizontal | L29
PB | R502 | 100k | 탄소피막 1/4 W 5 % 100 kΩ | 1 | 1 | 1 | | Device:R | Resistor_THT:R_Axial_DIN0207_L6.3mm_D2.5mm_P7.62mm_Horizontal | L29
PB | R503 | 20Ω | 탄소피막 1/4 W 5 % 100 Ω | 1 | 5 | 5 | | Device:R (Value 20R = 100 Ω ×5 병렬) | Resistor_THT:R_Axial_DIN0207_L6.3mm_D2.5mm_P7.62mm_Horizontal ×5 | L29
PB | C501 | 100n | Samsung CL31B104KCFNNNE 1206 100 nF 100 V X7R | 1 | 1 | 1 | | Device:C | Capacitor_SMD:C_1206_3216Metric_Pad1.33x1.80mm_HandSolder | SE4
PB | A501 | RP2040-Zero | Waveshare RP2040-Zero (파츠파츠 PP-A799-2) | 1 | 1 | 1 | | dj505/RP2040-Zero-KiCAD : RP2040-Zero (3V3 핀을 power_out으로) | bobu01/RP2040-Zero-Kicad-Footprint-1mm 또는 dj505 풋프린트를 1.0 mm 드릴로 복사 (핀 헤더용, 번호는 dj505 그대로) | SEV2
PB | A501-HDR | 1×9 ×2 | 핀헤더 1×40 2.54 mm — RP2040-Zero용 1×9 ×2 (먹스 168 + 제로 144 = 312핀 → 1×40 9줄) | 1 | 18 | 18 | 좌·우 열만 (아래 줄 없음), 몰드 뺌 | — | Connector_PinHeader_2.54mm (풋프린트는 A 줄 참조) | SE7
PB | JP504 | 닫음 (브리지) | SolderJumper_2_Bridged | 1 | 1 | 1 | | Jumper:SolderJumper_2_Bridged | Jumper:SolderJumper-2_P1.3mm_Bridged_Pad1.0x1.5mm (만능기판: 두 구멍 납땜)
PB | TP501 | | TestPoint | 1 | 1 | 1 | | Connector:TestPoint | TestPoint:TestPoint_THTPad_D1.5mm_Drill0.7mm
PB | TP502 | | TestPoint | 1 | 1 | 1 | | Connector:TestPoint | TestPoint:TestPoint_THTPad_D1.5mm_Drill0.7mm

SCH-06 · 전원 CU — 18줄

보드 | 부품 | 값 | 설명 | 보드 수 | 보드당 | 전체 | 실장 | KiCad 심볼 | KiCad 풋프린트 | 코드
CU | A601 | HUSB238 PD 트리거 → 20 V | HUSB238 PD 트리거 모듈 5~20 V (HAM6113) | 1 | 1 | 1 | | Toccata:HUSB238_Trigger (1·2 VOUT+, 3·4 GND) | 보드 밖 (Exclude from board) | L57
CU | F601 | 5 A T (0218005.MXP) | Littelfuse 0218005.MXP 5 A 지연형 5×20 mm | 1 | 1 | 1 | | Device:Fuse | 보드 밖 (Exclude from board) — 인라인 홀더 BU914 | L60
CU | F601-HLD | 5×20 mm | Coms BU914 인라인 퓨즈 홀더 5×20 mm | 1 | 1 | 1 | | — | 보드 밖 (Exclude from board) — 선 사이 | L60
CU | SW601 | KCD1-101A | KCD1-101A 로커 스위치 (SPST, 2핀) | 1 | 1 | 1 | | Switch:SW_SPST | 보드 밖 (Exclude from board) — I/O 판 | L59
CU | A602 | XL4016 강압 → 5.1 V | XL4016 강압 모듈 XH-M401 (HAM6415) → 5.1 V | 1 | 1 | 1 | | Toccata:XL4016_Buck (1 IN+, 2 IN−, 3 OUT+, 4 OUT−) | 보드 밖 (Exclude from board) | L58
CU | P601 | USB-C 수 2선 (MT666) | MAXTEK MT666 USB-C 수 2선 DIY 전원선 | 1 | 1 | 1 | | Connector:USB_C_Plug_USB2.0 (A4 VBUS, A1 GND만 사용 — A5·B5·A6·A7·S1에 NC 표시) | 보드 밖 (Exclude from board) | C24
CU | P602 | DC 플러그 (허브 어댑터 선) | NEXTU 710U3 유전원 USB 허브 (10포트) | 1 | 1 | 1 | | Connector_Generic:Conn_01x02 (1 = 중심 +, 2 = 슬리브) | 보드 밖 (Exclude from board) — 허브 어댑터 선 | L17
CU | TP601 | | TestPoint | 1 | 1 | 1 | | Connector:TestPoint | TestPoint:TestPoint_THTPad_D1.5mm_Drill0.7mm
CU | TP602 | | TestPoint | 1 | 1 | 1 | | Connector:TestPoint | TestPoint:TestPoint_THTPad_D1.5mm_Drill0.7mm
CU | TP603 | | TestPoint | 1 | 1 | 1 | | Connector:TestPoint | TestPoint:TestPoint_THTPad_D1.5mm_Drill0.7mm
CU | A603 | Raspberry Pi 5 2GB — 40핀 헤더 유닛 | Raspberry Pi 5 2GB | 1 | 1 | 1 | | Toccata:RaspberryPi5 유닛 B = 40핀 헤더 (2 = 5V, 6 = GND만 그림; 4 = 5V 안 씀) | 보드 밖 (Exclude from board) — Pi 5 보드 | L01
CU | P603 | F/F 끝 → 핀 2·6 | 실리콘 점퍼 26 AWG 20 cm F/F 빨강 1 + 검정 1 (W606, Pi 헤더 쪽 끝) | 1 | 1 | 1 | | Connector_Generic:Conn_01x02 (1 = 빨강 5 V, 2 = 검정 GND) | 보드 밖 (Exclude from board) — 점퍼 선 끝 (1핀 하우징 ×2) | v4touch No.51 · No.52
CU | X601 | F/F 끝 | W606 다른 끝 — P603과 같은 점퍼 (따로 사지 않음) | 1 | 1 | 1 | | Connector_Generic:Conn_01x02 (1 = 빨강 5 V, 2 = 검정 GND) | 보드 밖 (Exclude from board) — 점퍼 선 끝 (1핀 하우징 ×2)
CU | X602 | M/M 끝 | 실리콘 점퍼 26 AWG 20 cm M/M 빨강 1 + 검정 1 (W607, X601에 꽂는 끝) | 1 | 1 | 1 | | Connector_Generic:Conn_01x02 (1 = 빨강 5 V, 2 = 검정 GND) | 보드 밖 (Exclude from board) — 점퍼 선 끝 (1핀 ×2) | v4touch No.53 · No.54
CU | X603 | M/M 끝 | W607 다른 끝 — X602와 같은 점퍼 (따로 사지 않음) | 1 | 1 | 1 | | Connector_Generic:Conn_01x02 (1 = 빨강 5 V, 2 = 검정 GND) | 보드 밖 (Exclude from board) — 점퍼 선 끝 (1핀 ×2)
CU | X604 | 2.54 3핀 (동봉선) | 화면 동봉 전원선 W608의 2.54 3핀 하우징 (A605에 들어 있음) | 1 | 1 | 1 | | Connector_Generic:Conn_01x03 (1 = 빨강 5 V, 2 = 빈 칸 NC, 3 = 검정 GND) | 보드 밖 (Exclude from board) — 동봉 전원선 끝 | v4touch No.135 동봉
CU | P604 | MX1.25 2핀 | W608 다른 끝 — MX1.25 2핀 플러그 (X604와 같은 선, 따로 사지 않음) | 1 | 1 | 1 | | Connector_Generic:Conn_01x02 (1 = 5 V, 2 = GND — 우리 번호, 빨강 = 1) | 보드 밖 (Exclude from board) — 동봉 전원선 끝
CU | A605 | Waveshare 7-DSI-TOUCH-C | Waveshare 7-DSI-TOUCH-C 7인치 DSI 정전식 터치 1024×600 IPS (약 2.15 W, 동봉: 전원선 MX1.25 2핀 → 2.54 3핀, 22핀 200 mm 리본 2) | 1 | 1 | 1 | | Toccata:Waveshare_7-DSI-TOUCH-C (1 = 5V, 2 = GND: MX1.25 2핀. DSI 22핀은 선 목록 W605) | 보드 밖 (Exclude from board) — 화면 모듈 | v4touch No.135

SCH-07 · 오디오 CU — 18줄

보드 | 부품 | 값 | 설명 | 보드 수 | 보드당 | 전체 | 실장 | KiCad 심볼 | KiCad 풋프린트 | 코드
CU | A701 | Apple USB-C → 3.5 mm (MW2Q3) | Apple USB-C → 3.5 mm 어댑터 MW2Q3 | 1 | 1 | 1 | | Toccata:USB_Audio_Dongle (T, R, S) | 보드 밖 (Exclude from board) | L51
CU | P701 | W701 플러그 | Plug_TRS | 1 | 1 | 1 | | Connector_Audio:AudioPlug3 | 보드 밖 (Exclude from board)
CU | J701 | PJ-313 헤드폰 잭 | BSUN PJ-313 3.5 mm 스테레오 잭 (노멀 접점) | 1 | 1 | 1 | | Connector_Audio:AudioJack3_SwitchTR (핀 번호 = T, TN, R, RN, S) | 직접 만듦 Toccata:Jack_3.5mm_PJ-313 — 패드 이름을 T/TN/R/RN/S로 (통전 검사로 확인) | L15
CU | P702 | W702 플러그 | Plug_TRS | 1 | 1 | 1 | | Connector_Audio:AudioPlug3 | 보드 밖 (Exclude from board)
CU | J702 | PJ-313 앰프 입력 잭 | BSUN PJ-313 3.5 mm 스테레오 잭 (노멀 접점) | 1 | 1 | 1 | | Connector_Audio:AudioJack3_SwitchTR (핀 번호 = T, TN, R, RN, S) | 직접 만듦 Toccata:Jack_3.5mm_PJ-313 — 패드 이름을 T/TN/R/RN/S로 (통전 검사로 확인) | L15
CU | C701 | 1µ | 리드형 적층 세라믹 1 µF 50 V X7R | 1 | 1 | 1 | | Device:C | Capacitor_THT:C_Disc_D5.0mm_W2.5mm_P5.00mm (리드 간격 실측) | L56
CU | C702 | 1µ | 리드형 적층 세라믹 1 µF 50 V X7R | 1 | 1 | 1 | | Device:C | Capacitor_THT:C_Disc_D5.0mm_W2.5mm_P5.00mm (리드 간격 실측) | L56
CU | R701 | 1k | 탄소피막 1/4 W 5 % 1 kΩ | 1 | 1 | 1 | | Device:R | Resistor_THT:R_Axial_DIN0207_L6.3mm_D2.5mm_P7.62mm_Horizontal | L29
CU | C703 | 1µ | 리드형 적층 세라믹 1 µF 50 V X7R | 1 | 1 | 1 | | Device:C | Capacitor_THT:C_Disc_D5.0mm_W2.5mm_P5.00mm (리드 간격 실측) | L56
CU | C704 | 1µ | 리드형 적층 세라믹 1 µF 50 V X7R | 1 | 1 | 1 | | Device:C | Capacitor_THT:C_Disc_D5.0mm_W2.5mm_P5.00mm (리드 간격 실측) | L56
CU | R702 | 1k | 탄소피막 1/4 W 5 % 1 kΩ | 1 | 1 | 1 | | Device:R | Resistor_THT:R_Axial_DIN0207_L6.3mm_D2.5mm_P7.62mm_Horizontal | L29
CU | A702 | XH-A232 (HW-404) | XH-A232 (HW-404) TPA3110 2×15 W 앰프 보드 | 1 | 1 | 1 | | Toccata:XH-A232 (1 L, 2 G, 3 R, 4 VCC, 5 GND, 6 L+, 7 L−, 8 R+, 9 R−) | 보드 밖 (Exclude from board) | L53
CU | X703 | XT30U-M | AMASS XT30U-M 18 AWG 10 cm | 1 | 1 | 1 | | Connector:Conn_01x02_Pin | Connector_AMASS:AMASS_XT30U-M_1x02_P5.0mm_Vertical (패드 1 = −) · 보드 밖 (Exclude from board) | L61
CU | X704 | XT30U-F | AMASS XT30U-F 18 AWG 10 cm | 1 | 1 | 1 | | Connector:Conn_01x02_Socket | Connector_AMASS:AMASS_XT30U-F_1x02_P5.0mm_Vertical (패드 1 = −) · 보드 밖 (Exclude from board) | L61
CU | LS701 | CW-100B25 8 Ω (왼쪽) | 삼미 CW-100B25 4인치 8 Ω 25 W | 1 | 1 | 1 | | Device:Speaker (핀 1 = +) | 보드 밖 (Exclude from board) | L07
CU | X705 | XT30U-M | AMASS XT30U-M 18 AWG 10 cm | 1 | 1 | 1 | | Connector:Conn_01x02_Pin | Connector_AMASS:AMASS_XT30U-M_1x02_P5.0mm_Vertical (패드 1 = −) · 보드 밖 (Exclude from board) | L61
CU | X706 | XT30U-F | AMASS XT30U-F 18 AWG 10 cm | 1 | 1 | 1 | | Connector:Conn_01x02_Socket | Connector_AMASS:AMASS_XT30U-F_1x02_P5.0mm_Vertical (패드 1 = −) · 보드 밖 (Exclude from board) | L61
CU | LS702 | CW-100B25 8 Ω (오른쪽) | 삼미 CW-100B25 4인치 8 Ω 25 W | 1 | 1 | 1 | | Device:Speaker (핀 1 = +) | 보드 밖 (Exclude from board) | L07

### 06선 목록

W | 종류 | 길이 | 한쪽 | 다른 쪽 | 심선 | 코드
W101~W107 | 플랫 리본 2651-16P, 16심 전부 사용 | 약 180 mm ×7 | SB J201 (2×8) | MB J301 (2×8) | 16 (3V3 ×2, GND ×2, 신호 12) | C05
W201~W207 | USB-A → C 1 m (C 쪽 몰드 ≤ 12.5×7.6×25) | 1 m ×7 | 허브 다운스트림 | O1~O7 RP2040-Zero USB-C | USB 2.0 | C04
W208 | USB-A → C 1 m (CU 안, 짧게 묶음) | 1 m | 허브 다운스트림 | PB RP2040-Zero USB-C | USB 2.0 | C04
W209 | 허브 기본 업스트림 선 | 허브 부속 | 허브 업스트림 | Pi 5 USB-A | USB 3.0 | L17
W401 | EL 리드 (리본 가닥 5심) | 350 mm | EL J401 (아랫면) | X401 XH 6P (끝 부속 쪽 50 mm, 뒤 통로) | 5 (XH 1·2·3·4·6) | C05 · L66
W403 | O1 EXT 연장 6심 (L66 모듈 쪽 150 mm) | 150 mm | O1 MB J302 (아랫면) | X402 JST-XH 6P (모듈 쪽) | 6 | L66
W411 | ER 리드 (리본 가닥 3심) | 300 mm | ER J411 (아랫면) | X411 XH 6P (끝 부속 쪽 50 mm, 뒤 통로) | 3 (XH 1·2·6) | C05 · L66
W413 | O7 EXT 연장 6심 (L66 모듈 쪽 150 mm) | 150 mm | O7 MB J302 (아랫면) | X412 JST-XH 6P (모듈 쪽) | 6 | L66
W501 | 3.5 mm 스테레오 3 m (한쪽 잘라 페달에 납땜) | 3 m | PS U551 (페달 안) | P501 → J501 (I/O 판) | 3 (T OUT, R VCC, S GND) | L50
W502 | 잭 → PB 단선 | 약 10 cm | J501 T·TN·R·S | PB | 4 | SE12
W601 | USB-C ↔ C PD 60 W | 2 m / 0.6 m | 충전기 / 보조배터리 | A601 USB-C | PD | C23 / C22
W602 | 20 V 배선 16 AWG | 약 1 m | A601 → F601 → SW601 | A602 IN · A702 VCC | 2 | C13
W603 | USB-C 수 2선 (MT666) | 약 25 cm | A602 OUT | Pi 5 USB-C | 2 (빨강 +, 검정 −) | C24
W604 | 허브 어댑터 선 (잘라 씀) | 약 30 cm | A602 OUT | 허브 DC 입력 | 2 (중심 +) | L17 부속
W605 | DSI FFC 22핀 0.5 mm 300 mm B형(반대면), A형 보험 | 300 mm | Pi 5 CAM/DISP 1 | A605 DSI 22핀 | 22 (1 ↔ 1) | v4touch 49·50
W606 | 실리콘 점퍼 26 AWG F/F 빨강·검정 | 20 cm ×2 | Pi 헤더 핀 2·6 (P603) | X601 ⇄ X602 | 2 (빨강 5 V, 검정 GND) | v4touch 51·52
W607 | 실리콘 점퍼 26 AWG M/M 빨강·검정 | 20 cm ×2 | X602 (X601에 꽂음) | X603 ⇄ X604 (3핀 1·3) | 2 | v4touch 53·54
W608 | 화면 동봉 전원선 MX1.25 2핀 → 2.54 3핀 | 동봉 | X604 2.54 3핀 하우징 | P604 ⇄ A605 MX1.25 2핀 | 2 (가운데 빈 칸) | v4touch 135
W701 | 3.5 mm 스테레오 1.5 m (볼 쪽 잘라 납땜) | 1.5 m | 동글 A701 (플러그 P701) | J701 T·R·S (볼) | 3 | C14
W702 | 3.5 mm 스테레오 1.5 m (볼 쪽 잘라 납땜) | 1.5 m | J701 TN·RN·S | P702 → J702 (CU) | 3 | C14
W703·W705 | 스피커선 16 AWG, 쌍마다 꼼 | 약 0.6 m ×2 | A702 L± / R± | X703 / X705 XT30U-M | 2 ×2 | C13
W704·W706 | 스피커선 16 AWG | 약 0.3 m ×2 | X704 / X706 XT30U-F | LS701 / LS702 | 2 ×2 | C13
X701 | USB-C(F) → USB-A(M) 젠더 | — | 동글 | Pi 5 USB-A | — | L52

### 07모듈 핀 번호

RP2040-Zero: 패드 = dj505 KiCad 라이브러리 번호, WS P1 = Waveshare 회로도 번호. 구멍 좌표는 모듈 왼쪽 위(USB 가장자리) 기준 mm.

패드 (dj505) | Waveshare P1 | 이름 | 가장자리 | 구멍 x (mm) | 구멍 y (mm, USB 가장자리 기준) | Toccata 용도
1 | 23 | 5V | 왼쪽 | 1.38 | 1.59 | 연결 금지 (USB VBUS)
2 | 22 | GND | 왼쪽 | 1.38 | 4.13 | GND
3 | 21 | 3V3 | 왼쪽 | 1.38 | 6.67 | +3V3
4 | 20 | GP29 | 왼쪽 | 1.38 | 9.21 | NC
5 | 19 | GP28 | 왼쪽 | 1.38 | 11.75 | NC
6 | 18 | GP27 | 왼쪽 | 1.38 | 14.29 | NC
7 | 17 | GP26 | 왼쪽 | 1.38 | 16.83 | MUX_SIG / PED_ADC
8 | 16 | GP15 | 왼쪽 | 1.38 | 19.37 | NC
9 | 15 | GP14 | 왼쪽 | 1.38 | 21.91 | PED_SEL
10 | 1 | GP0 | 오른쪽 | 16.62 | 1.59 | NC
11 | 2 | GP1 | 오른쪽 | 16.62 | 4.13 | NC
12 | 3 | GP2 | 오른쪽 | 16.62 | 6.67 | MUX_S0
13 | 4 | GP3 | 오른쪽 | 16.62 | 9.21 | MUX_S1
14 | 5 | GP4 | 오른쪽 | 16.62 | 11.75 | MUX_S2
15 | 6 | GP5 | 오른쪽 | 16.62 | 14.29 | MUX_S3
16 | 7 | GP6 | 오른쪽 | 16.62 | 16.83 | ID0
17 | 8 | GP7 | 오른쪽 | 16.62 | 19.37 | ID1
18 | 9 | GP8 | 오른쪽 | 16.62 | 21.91 | ID2
19 | 14 | GP13 | 아래 | 3.92 | 21.91 | NC
20 | 13 | GP12 | 아래 | 6.46 | 21.91 | NC
21 | 12 | GP11 | 아래 | 9.00 | 21.91 | NC
22 | 11 | GP10 | 아래 | 11.54 | 21.91 | NC
23 | 10 | GP9 | 아래 | 14.08 | 21.91 | NC

4067 모듈(SparkFun BOB-09056 복제, 40.64 × 17.78, 두 줄 간격 15.24): 심볼 핀 ↔ 모듈 헤더. J2 1번(네모 패드) = GND.

심볼 핀 | 이름 | 모듈 헤더 | 헤더 핀
1 | C0 | J1 | 1
2 | C1 | J1 | 2
3 | C2 | J1 | 3
4 | C3 | J1 | 4
5 | C4 | J1 | 5
6 | C5 | J1 | 6
7 | C6 | J1 | 7
8 | C7 | J1 | 8
9 | C8 | J1 | 9
10 | C9 | J1 | 10
11 | C10 | J1 | 11
12 | C11 | J1 | 12
13 | C12 | J1 | 13
14 | C13 | J1 | 14
15 | C14 | J1 | 15
16 | C15 | J1 | 16
17 | GND | J2 | 1
18 | VCC | J2 | 2
19 | EN | J2 | 3
20 | S0 | J2 | 4
21 | S1 | J2 | 5
22 | S2 | J2 | 6
23 | S3 | J2 | 7
24 | SIG | J2 | 8

### 08파일 위치 (저장소)

파일 | 내용
hardware/pcb/schematic/SCH-01~07_*.svg | 회로도 7장 (A3, mm)
hardware/pcb/board/BRD-01·02_*.svg | 기판 배치도 2장
hardware/pcb/netlist/netlist.csv | 도면·보드·넷·부품·핀 (그린 도면에서 다시 계산)
hardware/pcb/netlist/bom.csv | 부품표 (KiCad 심볼·풋프린트·구매 목록 코드)
hardware/pcb/netlist/cables.csv | 선 목록 W101~W706
hardware/pcb/netlist/wiring_MB.csv | 제어 기판 점 대 점 배선 (구멍 좌표)
hardware/pcb/netlist/rp2040_zero_pads.csv · mux_module_pins.csv | 모듈 핀 번호표
hardware/pcb/README.md | 규칙, 변경 목록, KiCad 옮기는 순서, 도착 후 확인
hardware/pcb/src/ | 생성기 (build.py → 도면·CSV, page.py → 이 탭)

근거: TI DRV5055 SBAS640C, TI CD74HC4067, RP2040 데이터시트(E11), Waveshare RP2040-Zero 위키·회로도, SparkFun BOB-09056, Hynetek HUSB238, TI TPA3110D2, AMASS XT30, KiCad 9/10 라이브러리. 조사 노트 원문은 저장소 hardware/pcb/research/.
