WongyuKoh/Toccata/hardware/mechanical/touchscreen/compare/touch_compare_2026-10-01.html

# Toccata 터치스크린 조합 비교

R31 피아노 내장 터치스크린 · 조합 13가지 · 2026-10-01 · 값은 9/30 밤~10/1 새벽 확인 · 고르는 것은 사용자가 해요

지금 설계(rev 2)는 공식 Raspberry Pi Touch Display 2 7인치(TD2)에 맞춰 그렸고, CAD v13으로 이미 만들어 두었어요. 공식 화면이 아니어도 된다고 하셔서, Pi 5에 붙일 수 있는 화면 조합 13가지를 같은 기준(같은 경첩 축, 같은 CU 뚜껑, 같은 전력 계산)으로 다시 계산해 한곳에 모았어요. 이 페이지는 하나를 고르지 않아요. 표와 카드를 보고 고르시면 돼요.

지금 안(rev 2) 추가 비용 103,600원 = TD2 95,700 + FIT0997 리본 5,390 + 점퍼 935 × 2 + M3×20 4개 400 + M3×10 4개 240. 값은 9/30 밤~10/1 새벽에 판매 페이지에서 본 VAT 포함 값이에요. 모든 합계에 경첩·다리·뚜껑용 공통 나사 640원이 들어 있어요.

배송비: 엘레파츠·아이씨뱅큐·11번가(굿나잇몰)는 이미 주문 목록에 있는 판매처라, 이 줄들은 기존 주문에 합친다고 보고 0원으로 넣었어요. 쿠팡·G마켓·11번가 해외직구·옥션·디바이스마트(66,000원 이상) 화면은 판매처 무료배송이에요. 알리 조합(C3·C4b)은 배송비를 확인하지 못해 0원으로 두었어요. 카드마다 배송비 줄에 이유를 적었어요.

### 새 소식: 뒷바를 다시 설계해요 (L2, 10/1)

건반 뒤에 뒷바를 바로 붙이고 깊이를 447 mm에서 약 330~350 mm로 줄이는 설계(L2)를 CAD 세션에서 하고 있어요. 화면이 올라갈 가운데 뚜껑의 깊이가 약 100~125 mm로 줄고, 윗면 높이도 z88에서 z72.8쯤으로 바뀌어요. 그래서 이 페이지의 장착 그림과 숫자(경첩 축 y290 z96, 접은 높이 z113 등)는 지금 설계(L1) 기준이에요. 화면을 고르면 L2 사양에 맞춰 받침과 뚜껑을 다시 그려요.

L2에서 달라지는 점: 화면을 뒤로 접으면 받침이 뚜껑 위에 눕는데, 그 길이가 짧을수록 좋아요. CAD 세션은 "접은 깊이 약 120 mm 이하가 유리"하다고 했어요. 표에 접은 길이 칸을 넣었어요(받침 길이, 앞쪽 경첩 약 15 mm는 따로). 유리 110 mm 이하 · 경계 110~126 mm(뚜껑 뒤로 조금 넘을 수 있음) · 불리 126 mm 넘음(접는 방법을 바꿔야 할 수 있음). 가로로 짧은 1024×600·1280×800 화면(B1, C1b, C3, C4b)과 5인치(A2)가 유리하고, 16:9 7인치(A1, B2, B3)와 HDMI 7인치(A3, C1)는 길어요. L2 사양이 나오기 전이라 확정은 아니에요.

## 한눈에 보기 (추가 비용이 적은 순서)

조합 | 화면 | 연결 | 추가 비용 합계 | 지금 안 대비 | 받는 시기 | 설계 변경 | 접은 길이 (L2) | Pi 5 설정 | 한 줄 평
C1 7인치 HDMI 호환품 (쿠팡 최저가) 가장 쌈게임에 유리(가로) | 7인치 · 1024×600 가로 | HDMI + USB (FFC 선) | 56,440원 | −47,160원 | 10/20~10/23 해외, 10/20 표시 | 받침 새로 (A3와 같은 받침) | 129.3 mm 불리 | 대개 없음 (EDID) | 가장 싸요. 복제품이고 10/20에 와서 반품이 어려워요(왕복 32,200원).
C1b Surenoo 7인치 HDMI Display-D 게임에 유리(가로) | 7인치 · 1024×600 가로 | HDMI + USB-C (FFC 선) | 64,070원 | −39,530원 | 10/13~10/20 해외, 10/13 표시 | 두꺼운 받침 새로 + 다리 다시 계산 | 107.0 mm 유리 | 대개 없음 (EDID) | C1보다 7,630원 비싸고 1주 빨라요. 두꺼워서 접은 높이가 5.75 mm 올라가요.
A2 공식 5인치 Touch Display 2 | 5인치 · 720×1280 세로 · 매 프레임 90° 회전 필요 | DSI 리본 300 mm | 73,724원일부 미확인 | −29,876원 | 10/2~10/7 국내, 값 미확인 | 받침 새로 + 접이 발 손봄 | 96.5 mm 유리 | 없음 (자동 인식) | 가장 싼 국내 공식품이에요. 화면이 작아 흰 레인이 6.9 mm로 좁아요.
B1 Waveshare 7-DSI-TOUCH-C 게임에 유리(가로) | 7인치 · 1024×600 가로 | DSI 22핀 리본 300 mm | 86,274원 | −17,326원 | 10/15~10/22 해외, 추정 | 받침 새로 (뚜껑 그대로) | 106.0 mm 유리 | config.txt 한 줄 | 지금 안(rev 2)보다 1.7만 원 싸고 가로 화면이에요. 해외라 10월 중하순에 와요.
A1 공식 7인치 Touch Display 2 가장 빠름설계 변경 없음 | 7인치 · 720×1280 세로 · 매 프레임 90° 회전 필요 | DSI 리본 300 mm | 101,224원 | −2,376원 | 10/2~10/6 국내 재고 | 없음 (CAD v13 그대로) | 125.2 mm 경계 | 없음 (자동 인식) | 지금 설계 그대로라 바로 만들 수 있어요. 세로 화면이라 앱이 매 프레임 돌려야 해요.
A3 Waveshare 7인치 HDMI (C) 정품 가장 빠름게임에 유리(가로) | 7인치 · 1024×600 가로 | HDMI + USB (FFC 선) | 105,206원 | +1,606원 | 10/2~10/6 국내 재고 | 받침 새로 (뚜껑 그대로) | 129.3 mm 불리 | 대개 없음 (EDID) | 국내에서 바로 오는 가로 화면이에요. 밝기는 스위치로 켜고 끄기만 돼요.
C4b Waveshare 7inch DSI LCD (E) 게임에 유리(가로) | 7인치 · 1280×800본딩 가로 | DSI 리본 300 mm (22→15핀) | 106,464원일부 미확인 | +2,864원 | 10/12~10/25 해외, 추정 | 작은 받침만 새로 (두께·다리 그대로) | 109.2 mm 유리 | config.txt 한 줄 | 7인치 1280×800 본딩 DSI예요. 설계 변경이 작지만 알리 값이 미확인이에요.
C2 8인치 HDMI 아크릴 일체형 (쿠팡) 게임에 유리(가로) | 8인치 · 1280×800 가로 · 180° 뒤집기 (가벼움) | HDMI + USB (FFC 선) | 107,830원 | +4,230원 | 10/16~10/23 해외, 10/16 표시 | 테두리 없는 받침 새로 + 다리 다시 (여유 1.0 mm) | 137.0 mm 불리 | 대개 없음 + 180° 뒤집기 | 8인치 1280×800 중 가장 싸요. 어둡고(220 cd/m²) 반품이 사실상 안 돼요.
B2 Waveshare 7-DSI-TOUCH-A 화질 가장 좋음 | 7인치 · 720×1280본딩 세로 · 매 프레임 90° 회전 필요 | DSI 22핀 리본 400 mm | 108,449원 | +4,849원 | 10/12~10/26 해외, 추정 | 받침 외곽 그대로, 점검창 옮김 | 125.2 mm 경계 | config.txt 한 줄 | TD2와 같은 외곽에 광학 본딩이에요. 그래도 세로 화면이고 400 mm 리본이 필요해요.
C3 Waveshare 7EP-CAPLCD 게임에 유리(가로) | 7인치 · 1280×800본딩 가로 | HDMI FFC + USB 터치 + GPIO 전원 | 108,762원일부 미확인 | +5,162원 | 10/12~10/25 해외, 추정 | 받침 새로 + 다리 걸이 다시 | 109.2 mm 유리 | 대개 없음 (EDID) | HDMI 중 화질이 가장 좋아요. 국내 판매처가 없고 값·배송비가 미확인이에요.
B3 Waveshare 7inch DSI LCD (H) 화질 가장 좋음게임에 유리(가로) | 7인치 · 1280×720본딩 가로 · 회전 없음 (달기에 따라 180° 뒤집기) | DSI 22핀 리본 400 mm | 120,649원 | +17,049원 | 10/15~10/22 해외, 추정 | 받침 외곽 그대로, 창은 실물 보고 | 125.2 mm 경계 | config.txt 한 줄 | 7인치 본딩 가로 화면이에요. 비싸고, 옛 드라이버라 켜짐 문제 보고가 있어요.
B4 Waveshare 8-DSI-TOUCH-A 화질 가장 좋음 | 8인치 · 800×1280본딩 세로 · 매 프레임 90° 회전 필요 | DSI 22핀 리본 300 mm | 124,874원 | +21,274원 | 10/15~10/22 해외, 추정 (10/2 표시) | 받침 새로 (양옆 여유 0.6 mm) | 124.0 mm 경계 | config.txt 한 줄 | 8인치라 레인이 넓어요(10.7 mm). 세로라 회전이 필요하고 뚜껑 폭에 꽉 차요.
C4a Waveshare 8inch DSI LCD (C) 게임에 유리(가로) | 8인치 · 1280×800본딩 가로 | DSI 리본 300 mm (22→15핀) | 138,974원 | +35,374원 | 10/12~10/22 해외, 추정 | 받침 새로 (양옆 여유 0.6 mm) | 124.0 mm 경계 | config.txt 한 줄 | 8인치 본딩 가로 화면이에요. 가장 비싸고 뚜껑 폭에 꽉 차요.

- 가장 쌈 추가 비용 합계가 가장 적어요.
- 가장 빠름 화면이 국내 재고라 10/2~10/6에 와요. A3는 선까지 모두 이때 오고, A1의 300 mm 리본은 10/14쯤 오지만 통합(11/16) 때만 필요해요.
- 설계 변경 없음 CAD v13(rev 2)을 그대로 출력해요.
- 화질 가장 좋음 광학 본딩(유리와 액정 사이 틈을 메워 반사가 적은 방식)이면서 공개된 밝기가 400 cd/m² 이상이에요. C3·C4a·C4b도 광학 본딩이지만 밝기가 350이거나 공개되지 않았어요.
- 게임에 유리(가로) 처음부터 가로 화면이라 앱이 매 프레임 90° 돌리지 않아도 돼요. 그중 1024×600(A3·B1·C1·C1b)은 그릴 픽셀이 가장 적어 60 fps 여유가 가장 커요.
- 본딩 광학 본딩 화면이에요. 「일부 미확인」은 화면이나 리본 값 중 오늘 다시 확인하지 못한 줄이 있다는 뜻이에요.

### 고르는 법 (무엇이 중요한지에 따라)

- 설계를 그대로 두고 바로 시작하고 싶으면 → A1 (101,224원, 10/2~10/6, 설정 없음). 대신 세로 화면이라 게임이 매 프레임 90° 돌려야 해요.
- 돈이 가장 중요하면 → C1 (56,440원, 10/20 해외, 반품 어려움). 국내 공식품 중에서는 A2 (73,724원, 5인치라 작음).
- 가로 화면(게임 60 fps 여유)이 중요하고 빨리 받아야 하면 → A3 (105,206원, 10/2~10/6). 싸게는 B1 (86,274원)·C1b (64,070원), 대신 해외라 10월 중순 이후에 와요.
- 화면이 크고 레인이 넓어야 하면 → 8인치: C2 (107,830원, HDMI, 어두움), B4 (124,874원, 세로), C4a (138,974원, 가로·본딩).
- 화질(광학 본딩, 반사가 적음)이 중요하면 → 7인치 가로: C4b (106,464원, DSI, 밝기 비공개)·B3 (120,649원, 450 cd/m²), 7인치 세로: B2 (108,449원), 8인치: B4 (세로)·C4a (가로). 모두 해외라 10/12 이후에 와요.
- 받침 STL 마감(10/18) 전에 실물을 재고 싶으면 → 국내 재고인 A1·A2·A3. 나머지는 10/12 이후에 와서, 판매처 도면만 보고 받침을 먼저 그려야 해요.

## 받는 시기 (화면 = 굵은 막대, 부품 = 가는 막대)

국내 재고 화면해외 화면(추정 범위) 리본·선 같은 부품중국 국경절 한국 휴일 10/3·10/5·10/9판매 페이지 표시일(믿기 어려움)

용어 풀이 (처음 보는 말이 있으면 여기서 찾아요)

##### 화면·연결

DSI

Pi 전용 화면 단자예요. 납작한 리본 하나로 그림과 터치가 함께 가요.

HDMI

TV와 같은 단자예요. 터치는 USB 선이 따로 필요해요.

FFC / FPC

얇고 납작한 선이에요. FFC는 따로 사는 선, FPC는 화면에 붙어 나오는 선이에요. 뚜껑 구멍 22×6을 그대로 지나가요.

CAM/DISP 0·1

Pi 5에 있는 카메라·화면 겸용 단자 두 개예요. 이 페이지는 1번을 기준으로 적었어요.

GPIO 2번·6번

Pi 5의 40핀 머리에서 핀 자리 번호예요. 2번(4번도)은 5 V, 6번은 GND(0 V)예요.

광학 본딩

유리와 액정 사이 틈을 투명 접착제로 메운 방식이에요. 반사가 적고 또렷해 보여요.

IPS / TN

IPS는 옆에서 봐도 색이 덜 변하는 패널, TN은 싸지만 옆에서 보면 색이 변하는 패널이에요.

cd/m²

밝기 단위예요. 숫자가 클수록 밝아요(교실에서는 300 이상이 편해요).

NTSC 68%

표현할 수 있는 색 범위예요. 클수록 색이 진해요.

EDID

화면이 Pi에게 자기 해상도를 알려 주는 정보예요.

Goodix (GT911·GT9271)

터치 칩 이름이에요. 리눅스에 기본 드라이버가 들어 있어요.

OSD

화면 뒤 버튼으로 여는 설정 메뉴예요(밝기 등).

DDC/CI

HDMI 선으로 밝기 같은 모니터 설정을 바꾸는 규격이에요.

PWM

아주 빠르게 켰다 껐다 해서 밝기를 조절하는 신호예요.

##### Pi 5 설정 (리눅스)

config.txt / cmdline.txt

Pi가 켜질 때 읽는 설정 파일이에요. 대부분 한 줄만 넣으면 돼요.

dtoverlay (오버레이)

config.txt에 적는 한 줄짜리 장치 설정이에요. 이 화면이 붙어 있다고 Pi에게 알려 줘요.

KMS / KMSDRM

KMS는 리눅스가 화면 해상도를 정하고 그림을 내보내는 방식이에요. KMSDRM은 데스크톱 없이 게임(pygame)이 화면에 바로 그리는 방식이에요. 화면을 돌리는 기능이 없어서 세로 화면은 앱이 직접 돌려야 해요.

kmsprint

화면 출력 이름(DSI-1, HDMI-A-1 등)을 보여 주는 명령이에요.

evdev

리눅스가 터치·키 입력을 앱에 넘기는 통로예요. 게임은 여기서 손가락 위치를 받아요.

hid-multitouch

USB 터치 화면용 기본 드라이버예요. 따로 설치할 것이 없어요.

ALSA

리눅스 소리 장치 체계예요. HDMI 소리 장치가 새로 생기면 장치 번호가 바뀔 수 있어서 꺼 두기를 권해요.

sysfs (/sys/…)

리눅스 설정 파일 경로예요. /sys/class/backlight/…/brightness에 숫자를 쓰면 밝기가 바뀌어요.

세로 화면

패널이 원래 세로(720×1280 등)라, 가로로 쓰려면 앱이 매 프레임 그림을 90° 돌려 보내야 해요.

MP · fps

MP는 백만 픽셀, fps는 1초에 그리는 장수예요. 그릴 픽셀이 적을수록 60 fps를 지키기 쉬워요.

##### 위치·설계

x · y · z

피아노 전체 기준 위치(mm)예요. x는 왼쪽→오른쪽, y는 앞(연주자)→뒤, z는 바닥에서 잰 높이예요.

u · w

받침에 붙은 위치(mm)예요. u는 경첩 쪽 모서리에서 화면 위쪽으로 잰 거리, w는 유리 앞면에서 뒤로 잰 깊이예요.

D_c

받침 전체 두께(mm)예요. 두꺼울수록 접었을 때 높아져요(rev 2는 17).

받침(크래들)

화면을 잡고 경첩으로 도는 출력 부품이에요.

CU 뚜껑

가운데 칸(Pi 5·앰프가 든 칸)의 뚜껑이에요. 폭 199, 깊이 195 mm이고 모든 조합에서 그대로 써요.

여물통 · y254

건반 뒤와 CU 뚜껑 사이 홈(y212~252)이에요. 스피커 소리가 귀로 가는 길이라 z72 위로 아무것도 나오면 안 돼요. 그래서 22°로 눕혀도 화면 가장 앞이 y254보다 뒤에 있어야 해요.

안전율

부품이 견디는 힘 ÷ 실제로 받는 힘이에요. 클수록 튼튼해요.

O4

가운데 옥타브(가온 다가 있는 옥타브)예요.

rev 2 · CAD v13

공식 7인치(TD2)에 맞춘 지금 설계와 그 CAD 파일이에요.

L56

구매 목록(parts list)의 56번 줄이에요.

##### 규칙 번호 (sound-requirements.md)

D7

소리는 ALSA로 사운드 카드에 바로 보내요. HDMI 소리 장치는 꺼 두기를 권해요.

D14

스피커·화면의 자기장이 건반 센서를 흔들지 않게 하는 규칙이에요. 화면을 켜고 끈 상태, 밝기 0 %와 100 %에서 센서 흔들림을 다시 재요.

D16

Pi는 한 곳에서만 전원을 받아요. 화면 전원은 Pi(GPIO나 USB)에서 받고, 화면에 다른 전원을 넣지 않아요.

D19

충전기·보조배터리는 60 W 이상이에요. 45 W 제품이면 볼륨 상한을 2 dB 낮추고, 1 dB만 낮출 때는 화면을 꺼요.

D20

공식 TD2 화면 설정 규칙이에요. 세로 화면은 앱이 1280×720으로 그린 뒤 화면과 터치를 함께 90° 돌려요.

## 조합별 카드 (같은 순서)

C1C · 싸게·크게

### 7인치 1024×600 HDMI 호환품(쿠팡 최저가) + FFC 선 두 벌

가장 쌈게임에 유리(가로)

56,440원

지금 안 대비 −47,160원

10/20~10/23 · 해외, 10/20 표시

무명 7인치 HDMI 정전식 터치 (Waveshare 7inch HDMI LCD (C) 복제형, 쿠팡 8836448367, 옵션 [01] IPS Touch LCD) 제품 사진

제품 사진 (누르면 크게)

화면

무명 7인치 HDMI 정전식 터치 (Waveshare 7inch HDMI LCD (C) 복제형, 쿠팡 8836448367, 옵션 [01] IPS Touch LCD)

크기·해상도

7인치 · 1024×600

방향

가로(landscape) 기본, 회전 필요 없음

연결

HDMI(표준 A) + micro-USB 1개(터치와 전원 겸용), 백라이트 스위치

패널

IPS(판매 표기), 밝기 비공개, 커버 유리·광학 본딩 없음

터치

정전식 5점, USB HID(판매 문구 '드라이브 프리')

외곽 (mm)

164.90 × 124.26 (고정 귀 포함, 판매 사진 도면), 몸체 높이 106.96, 두께 약 8 (Waveshare (C) Rev4.1 기준, 이 제품은 미확인)

보이는 영역 (mm)

154.21 × 85.92

C1 쿠팡 판매 사진 치수

Waveshare (C) Rev4.1 외형 도면 (같은 모양)

쿠팡 판매 사진 치수 + Waveshare (C) Rev4.1 외형 (같은 모양) (누르면 크게)

#### 살 것

품목 | 수량 | 단가 | 금액 | 판매처 | 확인
7인치 1024×600 IPS 정전식 HDMI 터치 (쿠팡 8836448367, [01] IPS Touch LCD) 오늘 확인: 38,310원(정가 48,900원), 무료배송, 10/20 도착 예정, 5개 남음, 판매자 평가 14건 이하, 상품평 0개, 묶음배송 불가, 단순 변심 반품 왕복 32,200원 | 1 | 38,310원 | 38,310원 | 쿠팡 (판매자 제스117, 해외직구·구매대행, CJ대한통운) (https://www.coupang.com/vp/products/8836448367?itemId=25750932443) coupang.com | 확인
Wild Wire FFC HDMI 헤드 D-3 (micro HDMI 곧은형, Pi 쪽) 옵션 D-3 선택. Pi 5 HDMI0에 꽂아요 | 1 | 3,300원 | 3,300원 | 엘레파츠 (24시간 발송) (https://www.eleparts.co.kr/goods/view?no=12558075) eleparts.co.kr | 확인
Wild Wire FFC HDMI 헤드 A-1 (HDMI-A 곧은형, 화면 쪽) 옵션 A-1 선택. 화면 오른쪽 끝 HDMI에 꽂으면 옆으로 약 17 mm 나와요 | 1 | 3,300원 | 3,300원 | 엘레파츠 (24시간 발송) (https://www.eleparts.co.kr/goods/view?no=12558075) eleparts.co.kr | 확인
Wild Wire FFC HDMI-50Cm (20핀 0.5 mm 리본) 경로 약 404 mm라 30 cm는 짧아요 | 1 | 2,145원 | 2,145원 | 엘레파츠 (24시간 발송) (https://www.eleparts.co.kr/goods/view?no=11845384) eleparts.co.kr | 확인
Wild Wire FFC USB 헤드 USB A-1 (Pi 쪽) 옵션 USB A-1. Pi의 빈 USB-A 포트에 꽂아요 | 1 | 3,300원 | 3,300원 | 엘레파츠 (24시간 발송) (https://www.eleparts.co.kr/goods/view?no=11833566) eleparts.co.kr | 확인
Wild Wire FFC USB 헤드 Micro-1 (화면 쪽) 옵션 Micro-1. 화면 micro-USB(터치+전원)에 꽂아요 | 1 | 3,300원 | 3,300원 | 엘레파츠 (24시간 발송) (https://www.eleparts.co.kr/goods/view?no=11833566) eleparts.co.kr | 확인
Wild Wire FFC USB 리본 50 cm 기본 715원 + 50 cm 옵션 1,430원(VAT 포함). 경로 약 472 mm라 여유 28 mm | 1 | 2,145원 | 2,145원 | 엘레파츠 (24시간 발송) (https://www.eleparts.co.kr/goods/view?no=11851039) eleparts.co.kr | 확인
스텐 유두 렌치볼트 M3 × 20 mm (경첩 축 2, 다리 축 1, 예비 1) 모든 조합 공통. 개당 값은 추정 | 4 | 100원 | 400원 | 11번가 굿나잇몰 (기존 볼트 주문에 옵션 추가) (https://www.11st.co.kr/products/4236198413) 11st.co.kr | 미확인
스텐 유두 렌치볼트 M3 × 10 mm (CU 뚜껑 앞 고정 2, 예비 2) 모든 조합 공통. 개당 값은 추정 | 4 | 60원 | 240원 | 11번가 굿나잇몰 (기존 L56 줄 +4) (https://www.11st.co.kr/products/4236198413) 11st.co.kr | 미확인
배송비 | | | 0원 | 쿠팡 무료배송 + 엘레파츠 줄은 기존 엘레파츠 주문에 합침(따로 사면 +3,000원) + 11번가 나사는 기존 주문에 합침
합계 | | | 56,440원 | 지금 안(103,600원) 대비 −47,160원

화면 38,310 + HDMI FFC 세트 8,745 + USB FFC 세트 8,745 + 공통 나사 640 = 56,440원. 쿠팡은 무료배송이고, 엘레파츠 부품은 기존 엘레파츠 주문에 합치면 배송비가 없어요(따로 사면 공급가 6만 원 미만이라 3,000원 추가 → 59,440원). 더 싼 변형: 뚜껑 선 구멍을 22×8로 키우면 동봉 USB 선을 써서 USB FFC 세트 8,745원을 아낄 수 있어요(47,695원). 다만 선 굵기(OD 약 3.5~4 mm)가 구멍 아래 14 mm 공간에서 꺾이는지 확인해야 해요. 늦거나 불량이면 같은 받침에 맞는 Waveshare (C) 정품을 엘레파츠에서 87,076원에 24시간 안에 받을 수 있어요(그때 합계 105,206원).

##### 받는 시기

쿠팡 표시 10/20 도착 예정(해외 발송). 중국 국경절 뒤라 10/23까지 밀릴 수 있어요. FFC 부품은 엘레파츠 24시간 발송이라 10/2~10/6 도착(10/3, 10/5, 10/9 휴일 반영).

##### Pi 5 설정

대부분 설정이 필요 없어요. Pi OS Bookworm 이후 KMS는 화면이 보내는 EDID(해상도 정보)를 읽어 알맞은 해상도를 고릅니다(Raspberry Pi 공식 문서). 복제품이라 EDID가 틀리면 /boot/firmware/cmdline.txt 끝에 video=HDMI-A-1:1024x600M@60 한 줄을 넣어요(HDMI0 포트 기준). 판매자·위키의 hdmi_cvt 줄은 Bookworm부터 무시되니 넣지 않아요. 연결: Pi HDMI0 → D-3 머리 → HDMI FFC 50 cm → A-1 머리 → 화면 HDMI. 터치와 전원: Pi 빈 USB-A → A-1 머리 → USB FFC 50 cm → Micro-1 머리 → 화면 micro-USB. GPIO 선은 쓰지 않아요. 터치는 USB HID라 커널 기본 드라이버(hid-multitouch)로 evdev에 잡히고, pygame(SDL2 KMSDRM)이 손가락 이벤트로 받아요. 가로 화면이라 앱의 90° 회전 코드는 빼요. 밝기는 기판 스위치로 켜고 끄는 것만 돼요. HDMI 소리 장치 때문에 ALSA 번호가 바뀌지 않게 config.txt의 dtoverlay=vc4-kms-v3d를 dtoverlay=vc4-kms-v3d,noaudio로 바꾸는 것을 권해요. 외부 TV는 HDMI1에 가진 1 m 공식 케이블로 꽂고, 게임의 'HDMI 연결 감지'는 HDMI-A-2만 보게 해요.

##### 전력

화면이 더 쓰는 전력 | 약 3.1 W (Pi USB-A)
평균 | 16.7~20.7 W
순간 최대 | 55.4 W (60 W까지 4.6 W 남음)
배터리 | 약 3.0~3.8시간
45 W 충전기 −2 dB | 40.4 W

화면 약 3.1 W(같은 모양 Hosyond 제품의 0.62 A 기준, 이 제품 값은 미확인). Pi USB에서 받아요. 평균 16.7~20.7 W, 최대 55.4 W(60 W까지 4.6 W 여유), 45 W 충전기 −2 dB일 때 40.4 W, 배터리 3.0~3.8시간. Pi 입력 2.21 A, 5.1 V 레일 2.61 A, Pi USB 사용 0.82/1.6 A. TD2보다 약 0.6 W 더 써요.

#### 장착 (축척 스케치)

위에서 본 접은 상태. 파란 선 = 받침, 회색 = 화면 유리, 진한 회색 = 보이는 화면, 주황 = DSI 리본, 보라 = HDMI, 초록 = USB, 빨강 = 전원선, 점선 네모 = 뚜껑 아래 Pi 5. 선과 단자는 화면 뒤에 있어요. HDMI 단자 x728.5·u99 / USB 단자 x728.5·u71.

옆에서 본 모습(y·z, mm). 실선 = 25°로 세운 상태, 점선 = 뒤로 접은 상태. 경첩 축·뚜껑·다리 주머니는 모든 조합에서 같아요.

받침 x561.25~747.75 (폭 186.5), 뚜껑 여유 왼쪽 4.75 · 오른쪽 7.75 mm. 접은 상태 y296.5~425.8, 받침 두께 17.00.

들어가요. 받침 x561.25~747.75(폭 186.5), CU 뚜껑 여유 왼쪽 4.75 mm·오른쪽 7.75 mm예요(단자가 오른쪽 +x 끝이라 곧은 FFC 머리 17 mm까지 넣은 값). 접은 높이 z113(스피커 윗면 z134 아래), 22°에서 가장 앞 y276.7(통로 y254 통과), 접은 뒤끝 y425.8(뒷면 y447 안), 사용 중 맨 위 z226.2. 선 길이는 HDMI 약 404 mm, USB 약 472 mm라 둘 다 50 cm FFC로 닿아요. 뚜껑 선 구멍 22×6은 그대로 써요(얇은 FFC 두 장을 겹쳐 통과). 다리 힘 39.9 N(안전율 9.9), 뒤꿈치 163 N, 뚜껑 나사 79 N, 넘어짐 안전율 2.4예요.

설계 변경: 뚜껑 v2는 그대로예요. 받침(크래들)만 새로 그려요: 귀 구멍 156.90×114.96에 맞춘 판, 오른쪽 끝 HDMI·USB 머리 자리, 받침 뒤를 따라 오른쪽 끝에서 아래 홈(x592~614)까지 FFC 두 장이 지나는 길, 점검창을 단자 쪽으로 옮기기. 경첩 귀·뒤꿈치·다리 걸이·접이 발은 rev 2와 같아요(받침 두께 D_c 17 그대로). 이 받침은 Waveshare (C) 정품에도 그대로 맞아요.

#### 게임 영향

9.6 mm 2옥타브 흰 레인0.94 : 1 1옥타브 화면 : 실제 건반 0.61 MP 매 프레임 그릴 픽셀가로 회전 없음

1024×600 가로라 회전 없이 그려요. 그릴 픽셀이 TD2(1280×720)보다 33% 적어 Pi 5 2GB에서 60 fps 여유가 가장 커요(A3·B1·C1b와 같음). 활성 폭 154.2 mm라 2옥타브 흰 레인은 9.6 mm(64 px), 1옥타브 화면은 O4 옥타브와 0.94:1이에요. 16:9 그림은 1024×576으로 위아래에 띠가 생겨요. HDMI 변환 칩 때문에 지연이 약 1프레임 늘지만 게임의 화면 보정으로 지워져요.

##### 장점

- 가장 싸요. 지금 rev 2(TD2) 묶음보다 47,160원 적어요.
- 가로 화면이라 앱에서 매 프레임 돌릴 필요가 없어요.
- 받침 하나를 Waveshare (C) 정품과 같이 써서, 문제가 생기면 국내 정품으로 바로 바꿀 수 있어요.
- 터치가 USB HID라 드라이버가 필요 없어요.
- 두께가 약 8 mm라 접은 높이가 TD2와 같아요(z113).

##### 단점

- 10/20 도착이라 받침 모델링 마감(10/18) 전에 실물을 잴 수 없어요.
- 밝기를 소프트웨어로 못 바꿔요. 스위치로 켜고 끄기만 해서 D14 0 % 시험과 D19 화면 끄기는 손으로 해요.
- HDMI와 USB 선이 따로라 FFC 부품이 17,490원 들어요.
- 커버 유리·광학 본딩이 없어 화질은 보통이에요.

##### 위험

- 복제품이라 EDID가 틀리거나 품질이 고르지 않을 수 있어요. EDID가 틀리면 video= 한 줄로 맞춰요.
- 판매자 평가가 14건 이하이고 상품평이 0개예요. 통신판매업 신고가 2026년이라 이력이 짧아요.
- 해외직구라 단순 변심 반품은 왕복 32,200원이에요.
- 상세 표에 해상도가 '1280*800'으로 잘못 적혀 있어요. 받으면 1024×600인지 확인해요.
- Wild Wire 머리와 리본이 서로 맞는지 직접 확인하지 못했어요. 같은 브랜드로 맞춰 사요.
- 전력 3.1 W는 비슷한 제품 값이라 실제와 다를 수 있어요.

#### 확인한 것 / 미확인

오늘 다시 연 것: 쿠팡 상품 페이지(가격, 배송 방법 해외직구, 10/20, 재고 5개, 판매자 평가, 반품비, 판매자 정보), 엘레파츠 FFC 머리·리본 4개 페이지(3,300/2,145원, 24시간 발송), 엘레파츠 (C) 정품 87,076원. 더 싸거나 빠른 같은 물건을 찾아봤어요: 쿠팡 45,540원(10/13)은 다른 기판(Surenoo Display-D, C1b로 따로 정리), 쿠팡 44,660원(10/13)은 스탠드 케이스형 다른 물건, G마켓 42,770원은 TN이고 IPS는 47,270원, 롯데ON은 오늘 42,000원이라 모두 38,310원보다 비싸거나 모양이 달라요. 확인 못 한 것: 실제 전력·두께·EDID, 동봉 나사 크기, 나사 값(추정).

- 공통 나사 M3×20 4개와 M3×10 4개(640원)는 모든 조합에서 추정값이에요.

맨 위 표로 ↑

C1bC · 싸게·크게

### 7인치 1024×600 HDMI Surenoo Display-D(쿠팡, 10/13 도착) + FFC 선 두 벌

게임에 유리(가로)

64,070원

지금 안 대비 −39,530원

10/13~10/20 · 해외, 10/13 표시

Surenoo 7inch LCD Display-D 1024×600 Inner-HDMI 정전식 터치 (쿠팡 9038497904) 제품 사진

제품 사진 (누르면 크게)

화면

Surenoo 7inch LCD Display-D 1024×600 Inner-HDMI 정전식 터치 (쿠팡 9038497904)

크기·해상도

7인치 · 1024×600

방향

가로(landscape) 기본, 회전 필요 없음

연결

기판 안쪽 HDMI(표준 A, 뒤판 위에서 옆으로 꽂음) + USB-C(터치·전원) + 4핀 1.25 mm(터치·전원 확장) + PWM 패드 + OSD 버튼 5개 + 3.5 mm

패널

IPS 7인치, 밝기 비공개, OSD로 밝기 조절, 판매 문구에 PWM 밝기 조절

터치

정전식 5점, USB 터치(판매 문구 '드라이버 프리')

외곽 (mm)

유리 164.9 × 102 (보이는 틀 99.96), 기판 154.9 × 92.02, 전체 두께 15.15 (판매 사진 도면)

보이는 영역 (mm)

154.21 × 85.92

C1b 쿠팡 판매 사진 도면

쿠팡 판매 사진 도면 (네 귀 구멍 간격 없음) (누르면 크게)

#### 살 것

품목 | 수량 | 단가 | 금액 | 판매처 | 확인
Surenoo 7inch LCD Display-D 1024×600 (쿠팡 9038497904, [01] 옵션1) 오늘 확인: 45,540원(정가 68,310원), 무료배송, 10/13 도착 예정, 3개 남음, 단순 변심 반품 왕복 5,000원. 같은 상품 다른 판매자 45,840원(평가 73%) | 1 | 45,540원 | 45,540원 | 쿠팡 (판매자 Nanchang can mao clothing Co., 평가 87%·61건, 해외직구) (https://www.coupang.com/vp/products/9038497904?itemId=27643594625) coupang.com | 확인
Wild Wire FFC HDMI 헤드 D-3 (Pi 쪽) 옵션 D-3 | 1 | 3,300원 | 3,300원 | 엘레파츠 (24시간 발송) (https://www.eleparts.co.kr/goods/view?no=12558075) eleparts.co.kr | 확인
Wild Wire FFC HDMI 헤드 A-1 (화면 쪽) 옵션 A-1. 기판 안쪽 HDMI에 누워서 꽂혀요 | 1 | 3,300원 | 3,300원 | 엘레파츠 (24시간 발송) (https://www.eleparts.co.kr/goods/view?no=12558075) eleparts.co.kr | 확인
Wild Wire FFC HDMI-50Cm 경로 약 276 mm(추정) | 1 | 2,145원 | 2,145원 | 엘레파츠 (24시간 발송) (https://www.eleparts.co.kr/goods/view?no=11845384) eleparts.co.kr | 확인
Wild Wire FFC USB 헤드 USB A-1 (Pi 쪽) 옵션 USB A-1 | 1 | 3,300원 | 3,300원 | 엘레파츠 (24시간 발송) (https://www.eleparts.co.kr/goods/view?no=11833566) eleparts.co.kr | 확인
Wild Wire FFC USB 헤드 USB C-1 (화면 쪽) 옵션 USB C-1. 화면 USB-C(터치+전원) | 1 | 3,300원 | 3,300원 | 엘레파츠 (24시간 발송) (https://www.eleparts.co.kr/goods/view?no=11833566) eleparts.co.kr | 확인
Wild Wire FFC USB 리본 50 cm 기본(5 cm) 715원 + 50 cm 옵션 1,430원(VAT 포함) = 2,145원. 경로 약 348 mm(추정) | 1 | 2,145원 | 2,145원 | 엘레파츠 (24시간 발송) (https://www.eleparts.co.kr/goods/view?no=11851039) eleparts.co.kr | 확인
스텐 유두 렌치볼트 M2.5 × 8 mm (기판 고정) 동봉 액세서리에 나사가 있으면 필요 없어요. 값은 추정 | 4 | 100원 | 400원 | 11번가 굿나잇몰 (규격 목록에 M2.5 있음) (https://www.11st.co.kr/products/4236198413) 11st.co.kr | 미확인
스텐 유두 렌치볼트 M3 × 20 mm 모든 조합 공통, 값 추정 | 4 | 100원 | 400원 | 11번가 굿나잇몰 (https://www.11st.co.kr/products/4236198413) 11st.co.kr | 미확인
스텐 유두 렌치볼트 M3 × 10 mm (+4) 모든 조합 공통, 값 추정 | 4 | 60원 | 240원 | 11번가 굿나잇몰 (https://www.11st.co.kr/products/4236198413) 11st.co.kr | 미확인
배송비 | | | 0원 | 쿠팡 무료배송 + 엘레파츠 줄은 기존 엘레파츠 주문에 합침(따로 사면 +3,000원) + 11번가 나사는 기존 주문에 합침
합계 | | | 64,070원 | 지금 안(103,600원) 대비 −39,530원

화면 45,540 + HDMI FFC 세트 8,745 + USB-C FFC 세트 8,745 + M2.5 나사 400(추정) + 공통 640 = 64,070원. 엘레파츠는 기존 주문 합배송 가정(따로면 +3,000원). C1보다 7,630원 비싸지만 1주일 빨리 오고 반품비가 5,000원으로 싸요.

##### 받는 시기

쿠팡 표시 10/13 도착 예정(중국 판매자 직접 발송). 국경절(10/1~10/8) 때문에 10/20까지 늦어질 수 있어요. FFC 부품은 10/2~10/6.

##### Pi 5 설정

C1과 같아요. EDID로 1024×600이 잡히면 설정이 없고, 안 잡히면 cmdline.txt에 video=HDMI-A-1:1024x600M@60 한 줄을 넣어요. 연결: Pi HDMI0 → D-3 → FFC → A-1 → 기판 안쪽 HDMI, Pi USB-A → A-1 → FFC → C-1 → 화면 USB-C(터치+전원). 터치는 USB HID로 evdev에 잡혀요. 밝기는 뒷면 OSD 버튼으로 바꿔요. 판매 문구의 'PWM 밝기 조절'과 'USB 디밍 프로그램'이 Pi에서 되는지는 확인하지 못했어요. 이어폰 단자가 있어 HDMI 소리 장치가 생기므로 config.txt를 dtoverlay=vc4-kms-v3d,noaudio로 바꾸는 것을 권해요. 가로라 회전은 없어요.

##### 전력

화면이 더 쓰는 전력 | 약 3 W (Pi USB-A)
평균 | 16.6~20.6 W
순간 최대 | 55.3 W (60 W까지 4.7 W 남음)
배터리 | 약 3.0~3.8시간
45 W 충전기 −2 dB | 40.3 W

화면 약 3.0 W로 가정했어요(판매 페이지에 전력 없음, 미확인). Pi USB에서 받아요. 평균 16.6~20.6 W, 최대 55.3 W(여유 4.7 W), 45 W −2 dB 40.3 W, 배터리 3.05~3.78시간, Pi 입력 2.19 A, Pi USB 0.8/1.6 A.

#### 장착 (축척 스케치)

위에서 본 접은 상태. 파란 선 = 받침, 회색 = 화면 유리, 진한 회색 = 보이는 화면, 주황 = DSI 리본, 보라 = HDMI, 초록 = USB, 빨강 = 전원선, 점선 네모 = 뚜껑 아래 Pi 5. 선과 단자는 화면 뒤에 있어요. HDMI 단자 x636.0·u64 (추정) / USB 단자 x636.0·u40 (추정).

옆에서 본 모습(y·z, mm). 실선 = 25°로 세운 상태, 점선 = 뒤로 접은 상태. 경첩 축·뚜껑·다리 주머니는 모든 조합에서 같아요.

받침 x571.25~740.75 (폭 169.5), 뚜껑 여유 왼쪽 14.75 · 오른쪽 14.75 mm. 접은 상태 y296.5~403.5, 받침 두께 22.75.

들어가요. 귀가 없는 유리형이라 기판의 M2.5 구멍(판매 도면에 Pi용 58×49 위치가 나와 있음)으로 뒤판에 고정해요. 가운데 x656에 두면 받침 x571.25~740.75(폭 169.5), 뚜껑 여유 양쪽 14.75 mm. 두께가 15.15 mm라 받침이 두꺼워져(받침 두께 D_c 22.75) 접은 높이 z118.75(z133 이하 통과), 22°에서 가장 앞 y271.3(통과), 접은 뒤끝 y403.5. 단자가 뒤판 위에 누워 있어 옆으로 튀어나오지 않아요. 선 길이 추정은 HDMI 약 276 mm, USB 약 348 mm로 50 cm FFC면 넉넉해요. 뚜껑 구멍 22×6 그대로(FFC 두 장 겹침). 다리 힘 36 N(안전율 10.9), 뒤꿈치 147 N, 뚜껑 나사 71 N, 넘어짐 안전율 2.7.

설계 변경: 뚜껑 v2는 그대로예요. 받침을 새로, 그리고 rev 2보다 두껍게(뒤판 앞면 w약 21.75) 그려요. 경첩 축 기준은 같아서 뒤꿈치·접이 발은 그대로지만, 다리 걸이(u20, w19.5)는 약 5.75 mm 뒤로 옮기고 25° 각도를 다시 맞춰야 해요. 판매 도면에 네 귀 구멍 간격이 없어 Pi 구멍(58×49) 기준으로 그리고, 받으면 재서 고쳐요. Waveshare (C)와 모양이 달라 C1 받침과 바꿔 쓸 수 없어요.

#### 게임 영향

9.6 mm 2옥타브 흰 레인0.94 : 1 1옥타브 화면 : 실제 건반 0.61 MP 매 프레임 그릴 픽셀가로 회전 없음

C1과 같아요. 1024×600 가로, 2옥타브 흰 레인 9.6 mm(64 px), 1옥타브 0.94:1, 픽셀이 적어 60 fps 여유가 커요. HDMI 지연 약 1프레임은 보정으로 지워요.

##### 장점

- C1보다 1주일 빠른 10/13 도착 예정이에요.
- 판매자 평가가 보이고(87%, 61건) 반품비가 5,000원으로 싸요.
- USB-C와 OSD 밝기 버튼이 있어요.
- 단자가 뒤판 위에 누워 있어 옆으로 튀어나오지 않아요.

##### 단점

- C1보다 7,630원 비싸요.
- 두께 15.15 mm라 접은 높이가 z118.75로 5.75 mm 높아지고 다리 걸이를 다시 계산해야 해요.
- 네 귀 구멍 간격이 공개되지 않아 받기 전에는 받침을 확정할 수 없어요.
- 소프트웨어 밝기 조절은 확인되지 않았어요.

##### 위험

- 사양·치수가 판매 사진뿐이에요. 기판 모양이 사진과 다르면 받침을 다시 그려야 해요.
- 안쪽 HDMI에 FFC 머리를 꽂을 때 LCD 뒷면과 약 6 mm 틈에 들어가는지 받아서 확인해야 해요.
- 국경절 때문에 도착이 늦어질 수 있어요.
- 전력이 공개되지 않았어요.

#### 확인한 것 / 미확인

오늘 쿠팡 페이지에서 가격·도착일·재고·판매자(다른 판매자 45,840원 포함)·반품비·상세 사진을 확인했어요. 상세 사진으로 이 제품이 Waveshare (C) 복제형이 아니라 Surenoo 'Display-D'라는 다른 기판임을 확인했어요. 확인 못 한 것: 전력, 네 귀 구멍 간격, 소프트웨어 밝기 조절, 동봉품.

- 공통 나사 M3×20 4개와 M3×10 4개(640원)는 모든 조합에서 추정값이에요.

맨 위 표로 ↑

A2A · 국내·빠름

### 공식 5인치(Touch Display 2 5") + 공식 300 mm 리본: 가장 싼 공식품

73,724원

지금 안 대비 −29,876원

10/2~10/7 · 국내, 값 미확인

Raspberry Pi Touch Display 2 5" (SC1975) 제품 사진

제품 사진 (누르면 크게)

화면

Raspberry Pi Touch Display 2 5" (SC1975)

크기·해상도

5인치 · 720×1280 (세로 기본)

방향

세로 기본. 앱이 1280×720으로 그린 뒤 90° 돌림(A1과 같음)

연결

MIPI DSI: Pi 5 CAM/DISP 1(22핀) → 화면(15핀), 디스플레이용 300 mm 리본 + GPIO 5 V 전원 2가닥

패널

TFT LCD(노멀리 블랙), 시야각 80°, 500 cd/m², 안티글레어

터치

정전식 5점, 리본 안의 I2C, 커널 드라이버

외곽 (mm)

143.4 × 91.46 × 15.9 (Pi 스탠드오프 포함). 러그 면까지 8.5, 러그 간격 103.7 × 51

보이는 영역 (mm)

110.4 × 62.1

Raspberry Pi 공식 기계 도면 (Touch Display 2 5인치)

Raspberry Pi 공식 기계 도면 (Touch Display 2 5인치) (누르면 크게)

#### 살 것

품목 | 수량 | 단가 | 금액 | 판매처 | 확인
Raspberry Pi Touch Display 2 5인치 (SC1975) 오늘 19:14 페이지 저장본 값(62,000원+VAT)이에요. 23:30에 다시 열려 했지만 사이트가 접속을 거부했어요. 국내에 다른 싼 판매처가 없어요(엘레파츠 없음, 비티텍 121,600원, 쿠팡은 해외 144,200원~) | 1 | 68,200원 | 68,200원 | 디바이스마트 (평균 준비 1~2일, 66,000원 이상 무료배송) (https://www.devicemart.co.kr/goods/view?no=15907263) devicemart.co.kr | 미확인
Raspberry Pi 5 공식 디스플레이 리본 Standard–Mini 300 mm (SC1132) 5인치도 화면 쪽이 15핀이라 7인치와 같은 리본이에요 | 1 | 3,080원 | 3,080원 | 아이씨뱅큐 (해외 재고, 2주 이내, 기존 주문에 합침) (https://www.icbanq.com/P015646405) icbanq.com | 확인
[엘레파츠] 실리콘 점퍼 케이블 26AWG-RED (20cm, F/F) 5 V 연장 1단 | 1 | 451원 | 451원 | 엘레파츠 (https://www.eleparts.co.kr/goods/view?no=9461190) eleparts.co.kr | 확인
[엘레파츠] 실리콘 점퍼 케이블 26AWG-BLACK (20cm, F/F) GND 연장 1단 | 1 | 451원 | 451원 | 엘레파츠 (https://www.eleparts.co.kr/goods/view?no=9461199) eleparts.co.kr | 확인
[엘레파츠] 실리콘 점퍼 케이블 26AWG-RED (20cm, M/M) 5 V 연장 2단 | 1 | 451원 | 451원 | 엘레파츠 (https://www.eleparts.co.kr/goods/view?no=9756990) eleparts.co.kr | 확인
[엘레파츠] 실리콘 점퍼 케이블 26AWG-BLACK (20cm, M/M) GND 연장 2단 | 1 | 451원 | 451원 | 엘레파츠 (https://www.eleparts.co.kr/goods/view?no=9756998) eleparts.co.kr | 확인
스텐 유두 렌치볼트 M3 × 20 mm 모든 조합 공통, 값 추정 | 4 | 100원 | 400원 | 11번가 굿나잇몰 (https://www.11st.co.kr/products/4236198413) 11st.co.kr | 미확인
스텐 유두 렌치볼트 M3 × 10 mm (+4) 모든 조합 공통, 구매 목록 값 | 4 | 60원 | 240원 | 11번가 굿나잇몰 (https://www.11st.co.kr/products/4236198413) 11st.co.kr | 미확인
배송비 | | | 0원 | 디바이스마트 화면은 66,000원 이상 무료배송(9/30 저장본 기준), 아이씨뱅큐 리본·엘레파츠 점퍼·11번가 나사는 기존 주문에 합침
합계 | | | 73,724원 | 지금 안(103,600원) 대비 −29,876원

화면만 디바이스마트(68,200원이라 무료배송)이고 리본·점퍼·나사는 A1과 같아요. 디바이스마트 한 곳(화면+FIT0997+CH254 점퍼 2줄)으로 사면 76,100원이고, FIT0997 준비 1주 때문에 한꺼번에 오면 10/12 무렵 받아요. 다른 국내 판매처는 훨씬 비싸요.

##### 받는 시기

화면: 디바이스마트 준비 1~2일 → 10/2~10/7 도착(오늘 오후 기준). 리본은 A1과 같이 10/14 무렵, 책상 시험은 동봉 리본으로 바로 해요

##### Pi 5 설정

A1과 같아요. 자동 인식이라 설정이 없고, 안 뜨면 config.txt에 dtoverlay=vc4-kms-dsi-ili9881-5inch 한 줄을 넣어요(0번 포트면 ,dsi0). 전원은 GPIO 2번(5 V)과 6번(GND). 세로 화면이라 앱이 화면과 터치를 90° 돌려요. 밝기는 /sys/class/backlight로 조절해요.

##### 전력

화면이 더 쓰는 전력 | 약 1.5 W (GPIO 2·6번)
평균 | 15.0~19.0 W
순간 최대 | 53.7 W (60 W까지 6.3 W 남음)
배터리 | 약 3.3~4.2시간
45 W 충전기 −2 dB | 38.7 W

화면 약 1.5 W(추정). 평균 15.0~19.0 W, 순간 최대 53.7 W(60 W까지 6.3 W 여유), 배터리 3.3~4.2시간, Pi 입력 1.89 A, 5.1 V 레일 2.29 A. 45 W 충전기 −2 dB에서 38.7 W로 13개 조합 중 전력이 가장 적어요.

#### 장착 (축척 스케치)

위에서 본 접은 상태. 파란 선 = 받침, 회색 = 화면 유리, 진한 회색 = 보이는 화면, 주황 = DSI 리본, 보라 = HDMI, 초록 = USB, 빨강 = 전원선, 점선 네모 = 뚜껑 아래 Pi 5. 선과 단자는 화면 뒤에 있어요. DSI 리본 단자 x608.3·u45 (추정).

옆에서 본 모습(y·z, mm). 실선 = 25°로 세운 상태, 점선 = 뒤로 접은 상태. 경첩 축·뚜껑·다리 주머니는 모든 조합에서 같아요.

받침 x572.00~720.00 (폭 148.0), 뚜껑 여유 왼쪽 15.50 · 오른쪽 35.50 mm. 접은 상태 y296.5~393.0, 받침 두께 17.00.

받침 폭 148(x572~720), 뚜껑 여유 왼쪽 15.5, 오른쪽 35.5 mm. 도면에서 러그 면이 유리에서 8.5 mm라 받침 두께 17 mm가 그대로예요. 그래서 접은 윗면 z113, 22° 가장 앞 y276.7로 rev 2와 같아요. 접은 뒤끝 y393. 리본 길 약 228~242 mm라 300 mm에 58~72 mm가 남아요. 뚜껑 구멍 22×6은 그대로예요. 다만 접은 받침이 오른쪽 접이 발(x730~746)에 닿지 않고, 뒤쪽 접이 발(y398~414)까지 오지 않아요. 받침 뒤에 오른쪽 패드를 팔처럼 늘리거나 뚜껑의 오른쪽 접이 발을 x700~716으로 옮겨야 해요. 다리 힘 30 N(안전율 13), 뒤꿈치 123 N, 뚜껑 나사 59 N로 여유가 더 있어요.

설계 변경: 받침을 새로 그려요. 외곽 약 148 × 96.5 × 17, 가운데 x646(O4 쪽으로 10 mm), 러그 나사 자리 4개(103.7 × 51 간격), 뒷판 앞면은 w8.5(받은 화면으로 확인). 리본·전원 점검창은 커넥터가 가는 쪽(−x 끝 근처)으로 옮겨요. 다리 걸이(u20)는 그대로, 다리 클립은 u105~111에서 약 u85~91로 내려요(접으면 다리 끝이 받침 위로 약 24 mm 나오지만 뚜껑 안이에요). 오른쪽 접이 발을 받칠 패드 팔을 붙이거나, 뚜껑 v2의 오른쪽 접이 발 2개를 옮겨요. 경첩 귀·뒤꿈치·아래 홈은 rev 2와 같아요. CAD는 받침·점검창 덮개·조립 파일을 다시 만들어요.

#### 게임 영향

6.9 mm 2옥타브 흰 레인0.67 : 1 1옥타브 화면 : 실제 건반 0.92 MP 매 프레임 그릴 픽셀세로 매 프레임 90° 회전 필요

활성 폭 110.4 mm라 2옥타브 흰 레인 6.9 mm, 검은 레인 4.1 mm로 작고, 1옥타브 화면은 실제 건반과 0.67:1이에요. 9 mm 메뉴 버튼은 약 5줄 들어가요. 픽셀과 회전 부담은 A1과 같아요(1280×720 = 0.92 MP, 매 프레임 90° 회전).

##### 장점

- 국내에서 오는 조합 중 가장 싸요(rev 2보다 29,876원 적음). 13개 중에서는 C1·C1b 다음이에요
- 공식품이라 자동 인식이고 설정이 없어요
- 전력이 약 1.5 W로 가장 적어요
- 접은 높이·뚜껑 구멍·경첩 자리가 rev 2와 같아요
- 가벼워서 다리·나사 힘에 여유가 커요

##### 단점

- 화면이 작아 2옥타브 레인이 6.9 mm, 검은 레인이 4.1 mm예요
- 메뉴 글자와 버튼이 작아요(약 5줄)
- 세로 화면이라 회전 처리는 A1과 같아요
- 받침을 새로 그리고 접이 받침도 손봐야 해요

##### 위험

- 국내 판매처가 디바이스마트 하나뿐인데 오늘 밤 접속이 안 돼 값·재고를 다시 확인하지 못했어요
- 받침 재설계가 STL 마감(10/18) 안에 끝나야 해요
- 작은 레인 때문에 데모에서 게임이 잘 안 보일 수 있어요

#### 확인한 것 / 미확인

화면 값(68,200원, 준비 1~2일)은 오늘 19:14 디바이스마트 저장본이고, 밤에는 접속이 거부되어 다시 확인하지 못했어요. 리본(아이씨뱅큐 3,080원)과 점퍼(엘레파츠 451원)는 오늘 밤 확인했어요. 엘레파츠에는 5인치가 없고, 비티텍 121,600원, 쿠팡은 해외 발송 144,200~163,400원이에요(오늘 밤 확인). 외곽·러그·두께는 공식 도면(td2_5_mech.png)에서 읽었고, 커넥터 위치와 전력 1.5 W는 추정이에요. 받침 계산은 combos/fit_groupA.py로 다시 했어요.

- Raspberry Pi Touch Display 2 5인치 (SC1975) (68,200원): 오늘 19:14 페이지 저장본 값(62,000원+VAT)이에요. 23:30에 다시 열려 했지만 사이트가 접속을 거부했어요. 국내에 다른 싼 판매처가 없어요(엘레파츠 없음, 비티텍 121,600원, 쿠팡은 해외 144,200원~)
- 공통 나사 M3×20 4개와 M3×10 4개(640원)는 모든 조합에서 추정값이에요.

맨 위 표로 ↑

B1B · DSI 호환·해외

### Waveshare 7-DSI-TOUCH-C (7인치 1024×600 가로) + 22핀 300 mm 리본

게임에 유리(가로)

86,274원

지금 안 대비 −17,326원

10/15~10/22 · 해외, 추정

Waveshare 7-DSI-TOUCH-C (7인치 DSI 정전식 터치, Pi 5·CM5 전용) 제품 사진

제품 사진 (누르면 크게)

화면

Waveshare 7-DSI-TOUCH-C (7인치 DSI 정전식 터치, Pi 5·CM5 전용)

크기·해상도

7인치 · 1024×600, 60.0 Hz (커널 드라이버 타이밍으로 계산)

방향

처음부터 가로(landscape). 앱에서 화면이나 터치를 돌릴 필요가 없어요.

연결

MIPI DSI 22핀 0.5 mm (Pi 5 CAM/DISP 1) + MX1.25 2핀 5 V 전원(GPIO에서)

패널

IPS, 400 cd/m², 시야각 170°, 알루미늄 뒷판. 광학 본딩 표기가 없어서, 유리와 액정 사이에 틈이 있는 구조로 봐요(반사가 조금 더 있음).

터치

정전식 5점, Goodix 컨트롤러(리본 안 I2C), 커널 기본 드라이버 → evdev 터치 장치

외곽 (mm)

166.10 × 101.00 × 8.0 (Pi 스탠드오프를 달면 13.4). 뒷면 네 귀에 M2.5 탭 구멍 154 × 88(가장자리에서 6.05 / 6.50). 앞 테두리는 왼쪽 3.97, 오른쪽 7.55, 위 4.94, 아래 9.65. 포장 무게 약 0.34 kg

보이는 영역 (mm)

154.58 × 86.42

Waveshare 7-DSI-TOUCH-C 치수 도면

Waveshare 7-DSI-TOUCH-C 치수 (누르면 크게)

#### 살 것

품목 | 수량 | 단가 | 금액 | 판매처 | 확인
Waveshare 7-DSI-TOUCH-C 7인치 DSI 정전식 터치 1024×600 IPS 오늘 페이지 값은 기존가 79,900원이고, 7% 쿠폰을 받으면 73,510원이에요. 도착일 표시는 없고 상품평은 0개예요. 동봉품: 22핀 약 200 mm 반대면 리본 2개, MX1.25→2.54 3핀 전원선, MX1.25 4핀 선, 스탠드오프. | 1 | 79,900원 | 79,900원 | G마켓 해외직구 (판매자 이룸종합상사4, CJ 무료배송, 150달러 이하라 관부가세 없음) (https://item.gmarket.co.kr/Item?goodscode=4783965807) gmarket.co.kr | 확인
GUOCONN 0.5*22P*300*B FFC 22핀 0.5 mm 300 mm 반대면(B형, Reverse) Pi 5 CAM/DISP 1과 화면 22핀을 잇는 본 리본이에요. 오늘 페이지 기준 개당 391원, 해외재고 120개, 평균 발송 10/21, 최소 5개, 두께 0.3 mm예요. 동봉 200 mm 리본은 피아노 안 경로에는 짧아요. 책상 위 시험에는 바로 쓸 수 있어요. | 5 | 391원 | 1,955원 | 엘레파츠 (해외재고, 평균 발송 10/21, 기존 엘레파츠 주문에 합치면 배송비 0원) (https://www.eleparts.co.kr/goods/view?no=18622271) eleparts.co.kr | 확인
GUOCONN 0.5*22P*300*A FFC 22핀 0.5 mm 300 mm 같은 면(A형, Same Side) 보험용이에요. 우리 경로에는 45° 접힘이 두 번 있어서, 필요한 접점 면이 Waveshare 그림과 다를 수 있어요. 틀리면 다시 주문해서 받기까지 약 2주가 걸리니 함께 사 둬요. 빼면 1,975원 줄어요. | 5 | 395원 | 1,975원 | 엘레파츠 (해외재고, 평균 발송 10/21, 기존 엘레파츠 주문에 합치면 배송비 0원) (https://www.eleparts.co.kr/goods/view?no=18581287) eleparts.co.kr | 확인
[엘레파츠] 실리콘 점퍼 케이블 26AWG-RED (20cm, F/F) 화면 5 V 연장 1단이에요. GPIO 2번에 꽂아요. | 1 | 451원 | 451원 | 엘레파츠 (24시간 안 발송) (https://www.eleparts.co.kr/goods/view?no=9461190) eleparts.co.kr | 확인
[엘레파츠] 실리콘 점퍼 케이블 26AWG-BLACK (20cm, F/F) GND 연장 1단이에요. GPIO 6번에 꽂아요. | 1 | 451원 | 451원 | 엘레파츠 (24시간 안 발송) (https://www.eleparts.co.kr/goods/view?no=9461199) eleparts.co.kr | 확인
[엘레파츠] 실리콘 점퍼 케이블 26AWG-RED (20cm, M/M) 5 V 연장 2단이에요. 화면 동봉 전원선(MX1.25→2.54 3핀)의 암 소켓에 꽂아요. | 1 | 451원 | 451원 | 엘레파츠 (24시간 안 발송) (https://www.eleparts.co.kr/goods/view?no=9756990) eleparts.co.kr | 확인
[엘레파츠] 실리콘 점퍼 케이블 26AWG-BLACK (20cm, M/M) GND 연장 2단이에요. | 1 | 451원 | 451원 | 엘레파츠 (24시간 안 발송) (https://www.eleparts.co.kr/goods/view?no=9756998) eleparts.co.kr | 확인
스텐 유두 렌치볼트 M3 × 20 mm 경첩 축 2개, 다리 축 1개, 예비 1개예요. 모든 조합에 똑같이 들어가요. 값은 예전 추정값이에요. | 4 | 100원 | 400원 | 11번가 굿나잇몰 (기존 볼트 주문에 옵션 추가) (https://www.11st.co.kr/products/4236198413) 11st.co.kr | 미확인
스텐 유두 렌치볼트 M3 × 10 mm (기존 L56 줄 수량 +4) CU 뚜껑 앞 모서리 고정 2개와 예비 2개예요. 모든 조합에 똑같이 들어가요. 오늘 다시 보지는 않았어요. | 4 | 60원 | 240원 | 11번가 굿나잇몰 (기존 L56 줄) (https://www.11st.co.kr/products/4236198413) 11st.co.kr | 미확인
배송비 | | | 0원 | G마켓 해외직구 무료배송(CJ) + 엘레파츠 줄은 기존 엘레파츠 주문에 합침(따로 사면 +3,000원) + 11번가 나사는 기존 주문에 합침
합계 | | | 86,274원 | 지금 안(103,600원) 대비 −17,326원

화면 79,900 + 리본 B형 1,955 + A형 보험 1,975 + 점퍼 1,804 + 공통 나사 640 = 86,274원이에요. A형 보험을 빼면 84,299원(−19,301원)이에요. G마켓 쿠폰가 73,510원을 쓰면 79,884원이고, A형까지 빼면 77,909원이에요. 엘레파츠 줄은 기존 엘레파츠 주문에 합친다고 보고 배송비를 0원으로 넣었어요. 따로 주문하면 3,000원이 더 들어요. 다른 가게도 있어요. 11번가 엠알오동원은 90,600원이에요(합계 96,974원). 국내 택배로 10/2 도착이라고 나오지만, 알리 설명을 옮긴 구매대행 글이라 확인되지 않았어요. 쿠팡 다빈은 97,600원이에요(합계 103,974원, 10/16 도착 표시). 알리 목록가는 60,635원이에요(합계 약 67,009원). 로봇 확인 화면 때문에 오늘은 못 봤어요. Waveshare 직판은 42.99달러 ≈ 58,195원에 DHL 운임이 더해져요. 운임은 결제 단계에서만 나와서 확인하지 못했어요. 리본만 쿠팡 리셀포얼 300 mm B형 2개(12,170원, 10/15 도착 표시)로 바꾸면 10,215원이 더 들지만 약 1주 빨라요.

##### 받는 시기

화면은 해외 구매대행이라 중국 국경절(10/1~10/8) 뒤에 발송돼요. 약 10/15~10/22에 도착할 것으로 봐요(추정, 페이지에 날짜 없음). 리본은 엘레파츠 평균 발송이 10/21이라 10/22~10/23에 와요. 화면이 먼저 오면 동봉 200 mm 리본으로 책상 위 시험은 바로 할 수 있어요.

##### Pi 5 설정

config.txt 끝에 한 줄을 넣어요: dtoverlay=vc4-kms-dsi-waveshare-panel-v2,7_0_inch_c. CAM/DISP 1 기준이고, 0번 포트를 쓰면 끝에 ,dsi0을 붙여요. 기본 줄 dtoverlay=vc4-kms-v3d는 그대로 둬요. 이 오버레이는 지금 Pi OS(2026-09-15, 커널 6.18.50)에 들어 있어서 따로 설치할 것이 없어요. 리본은 Pi 22핀과 화면 22핀을 잇고, 15핀용이 아니에요. 전원은 동봉 3핀 선을 점퍼로 늘려 GPIO 2번(5 V)과 6번(GND)에 꽂아요. 밝기는 /sys/class/backlight/*/brightness에 0~255를 쓰면 돼요. 0이면 꺼지니 D14의 0 %/100 % 시험과 D19의 화면 끄기가 돼요. 터치는 커널 기본 Goodix 드라이버라 따로 설치할 것이 없어요. 가로 화면이라 회전 설정도 필요 없어요. 앱은 kmsprint로 DSI 출력 이름을 확인해서 골라요(Pi 5에서는 DSI-2일 수 있어요).

##### 전력

화면이 더 쓰는 전력 | 약 2.15 W (GPIO 2·6번)
평균 | 15.7~19.7 W
순간 최대 | 54.4 W (60 W까지 5.6 W 남음)
배터리 | 약 3.2~4.0시간
45 W 충전기 −2 dB | 39.4 W

화면은 약 2.15 W를 써요(위키 기준 5 V 0.43 A 이상 필요). Pi GPIO에서 전원을 받아요. 평균 15.7~19.7 W, 순간 최대 54.4 W예요. 60 W까지 5.6 W가 남아요. 배터리는 약 3.2~4.0시간으로 TD2보다 약 4~6분 길어요. 5.1 V 선은 2.42 A, Pi 입력은 2.02 A예요. 45 W 충전기 −2 dB 모드는 39.4 W로 통과해요. Pi USB 전류는 그대로예요(0.2/1.6 A).

#### 장착 (축척 스케치)

위에서 본 접은 상태. 파란 선 = 받침, 회색 = 화면 유리, 진한 회색 = 보이는 화면, 주황 = DSI 리본, 보라 = HDMI, 초록 = USB, 빨강 = 전원선, 점선 네모 = 뚜껑 아래 Pi 5. 선과 단자는 화면 뒤에 있어요. DSI 리본 단자 x633.4·u63 (추정).

옆에서 본 모습(y·z, mm). 실선 = 25°로 세운 상태, 점선 = 뒤로 접은 상태. 경첩 축·뚜껑·다리 주머니는 모든 조합에서 같아요.

받침 x570.65~741.35 (폭 170.7), 뚜껑 여유 왼쪽 14.15 · 오른쪽 14.15 mm. 접은 상태 y296.5~402.5, 받침 두께 17.00.

받침 폭이 170.7 mm(x570.65~741.35)라 CU 뚜껑 양쪽에 14.15 mm씩 남아요. 접은 높이는 z113으로 TD2와 같아요. 22°에서 가장 앞은 y276.7이라 여물통 기준 y254를 통과해요. 접은 상태는 y296.5~402.5이고, 사용 중 맨 위는 z205.1이에요. 커넥터 입이 −x(뚜껑 구멍 쪽)를 봐서 리본이 x≈636에서 홈(x605)까지 곧게 가요. 리본 경로는 약 271 mm라 300 mm 리본에 29 mm가 남아요. 뚜껑 선 구멍(22×6)은 그대로예요. 다리 힘 36.7 N(안전율 10.7), 뒤꿈치 150 N, 넘어짐 안전율 2.6이에요.

설계 변경: 받침(크래들)만 새로 그려요. 바깥 크기는 170.7 × 106이에요. 러그 대신 네 귀의 M2.5 구멍 154 × 88(x579·733, u6.5·94.5)로 고정해요. 화면 뒤가 평평해서, 뒷판을 약 1.4 mm 띄우는 받침살을 둬요. 그 틈으로 리본이 지나가요. 점검창은 커넥터 자리(대략 x605~640, u30~75)로 옮겨요. 경첩 귀, 다리 걸이, 아래 홈 위치는 그대로예요. v13 받침 뒤 패드(x566~582, x730~746)는 받침 폭 밖으로 4.65 mm씩 나가니 안쪽으로 옮겨요. 뒤쪽 접이 발(y398~414)에는 받침이 4.5 mm만 걸리니 받침 윗변에 턱을 덧대요. CU 뚜껑 v2와 구멍은 그대로 써요.

#### 게임 영향

9.6 mm 2옥타브 흰 레인0.94 : 1 1옥타브 화면 : 실제 건반 0.61 MP 매 프레임 그릴 픽셀가로 회전 없음

2옥타브 화면의 흰 레인은 9.6 mm(64 px), 검은 레인은 5.8 mm예요. 1옥타브 화면은 O4 옥타브와 0.94:1이에요. 그릴 픽셀이 0.61 MP로 TD2(0.92 MP)보다 33 % 적어요. 그래서 Pi 5 2GB에서 pygame 60 fps 여유가 B 그룹 네 조합 중 가장 커요(13개 중에서는 A3·C1·C1b와 같이 가장 커요). 가로 화면이라 매 프레임 그림을 돌리는 복사가 없어요. 16:9 그림은 1024×576으로 넣고, 위아래에 12 px씩 남아요.

##### 장점

- 가로 화면이라 앱이 화면과 터치를 돌리지 않아도 돼요.
- 그릴 픽셀이 가장 적어서 게임 속도 여유가 커요.
- config.txt 한 줄과 커널 기본 드라이버로 터치와 밝기 조절까지 돼요.
- 확인된 값으로 지금 안보다 약 1.7만 원 싸요. 쿠폰을 쓰면 약 2.4만 원 싸요.
- CU 뚜껑을 그대로 쓰고, 리본 길이도 29 mm가 남아 넉넉해요.

##### 단점

- 5점 터치이고 광학 본딩이 없어서 반사가 조금 더 있어요.
- 해상도가 1024×600로 TD2보다 낮아요. 다만 714 mm 거리에서는 거의 구별이 안 돼요.
- 받침을 새로 그려야 해요.
- 해외 구매대행이라 반품과 수리가 어려워요.

##### 위험

- G마켓 판매자는 상품평이 0개이고, 알리 상품을 옮긴 구매대행 글이에요. 받으려면 개인통관고유부호(해외 물건을 받을 때 쓰는 번호)가 필요해요.
- 페이지에 도착일이 없어요. 중국 연휴 때문에 10월 중순~하순으로 봐요. 10/23까지 안 오면 국내에서 TD2 7인치를 사는 길을 남겨 둬요.
- 경로의 접힘 때문에 리본 접점 면이 반대일 수 있어요. A형 보험 리본으로 대비해요.
- Waveshare DSI 드라이버에 '오래 꺼 둔 뒤 켜면 가끔 화면이 안 켜진다'는 보고가 있어요. 고치는 패치는 아직 반영되지 않았어요. 받으면 전원을 뺐다 켜는 시험을 10번 해요.
- 커넥터 위치는 사진 도면에서 읽은 추정값이에요. 받침을 뽑기 전에 실물로 재요.

#### 확인한 것 / 미확인

오늘 다시 연 것: G마켓 4783965807의 가격·쿠폰·무료배송(브라우저), 11번가 9512310445와 쿠팡 9380265718의 값과 표시 도착일, 엘레파츠 리본(391·395원, 재고, 평균 발송 10/21, Reverse 0.3 mm)과 점퍼(451원), Waveshare 직판 42.99달러와 10/1~4 출고 중지 공지. 지금 Pi OS(2026-09-15, 커널 6.18.50)가 쓰는 rpi-6.18.y의 오버레이 설명서와 v2 드라이버(7_0_inch_c 1024×600, 60.0 Hz), 위키의 설정 줄·밝기 명령·0.43 A도 확인했어요. 확인 못 한 것: 알리 가격(로봇 확인 화면, 우회하지 않음), Waveshare DHL 운임, 실제 도착일, 커넥터 좌표(사진 도면 추정), M3 나사값(예전 추정), 디바이스마트(접속 시간 초과), 네이버(접속 차단).

- 공통 나사 M3×20 4개와 M3×10 4개(640원)는 모든 조합에서 추정값이에요.

맨 위 표로 ↑

A1A · 국내·빠름

### 공식 7인치(Touch Display 2) + 공식 300 mm 디스플레이 리본: 지금 설계 그대로

가장 빠름설계 변경 없음

101,224원

지금 안 대비 −2,376원

10/2~10/6 · 국내 재고

Raspberry Pi Touch Display 2 7" (SC1635) 제품 사진

제품 사진 (누르면 크게)

화면

Raspberry Pi Touch Display 2 7" (SC1635)

크기·해상도

7인치 · 720×1280 (세로 기본)

방향

세로 기본. 앱이 1280×720으로 그린 뒤 화면과 터치를 90° 돌림(D20)

연결

MIPI DSI: Pi 5 CAM/DISP 1(22핀) → 화면(15핀), 디스플레이용 300 mm 리본 + GPIO 5 V 전원 2가닥

패널

TFT LCD(노멀리 블랙), 시야각 85°, 500 cd/m², 안티글레어, 커버 유리 0.7 mm

터치

정전식 5점. 리본 안의 I2C로 연결되고 커널 드라이버가 기본으로 잡음

외곽 (mm)

189.32 × 120.24 × 14.92 (Pi 스탠드오프 포함). 러그 면까지 9.4

보이는 영역 (mm)

154.56 × 86.94

Raspberry Pi 공식 기계 도면 (Touch Display 2 7인치)

Raspberry Pi 공식 기계 도면 (Touch Display 2 7인치) (누르면 크게)

#### 살 것

품목 | 수량 | 단가 | 금액 | 판매처 | 확인
Raspberry Pi Touch Display 2 7인치 (SC1635) 9/30 23:29 확인: 재고 있음, 24시간 안 발송. 동봉품: Pi 5용 22→15핀 200 mm 리본(책상 시험용), 15→15핀 리본, GPIO 전원선, M2.5 나사 8개 | 1 | 95,700원 | 95,700원 | 엘레파츠 (기존 엘레파츠 주문에 합침, 무료배송) (https://www.eleparts.co.kr/goods/view?no=16630499) eleparts.co.kr | 확인
Raspberry Pi 5 공식 디스플레이 리본 Standard–Mini 300 mm (SC1132) 2,800원+VAT. 22핀(Pi)→15핀(화면) 디스플레이용이라 TD2 동봉 리본과 같은 종류이고 길이만 300 mm예요. rev 2의 FIT0997(5,390원)과 길이가 같아 설계가 바뀌지 않아요 | 1 | 3,080원 | 3,080원 | 아이씨뱅큐 (해외 재고, 2주 이내, 기존 아이씨뱅큐 주문에 합침) (https://www.icbanq.com/P015646405) icbanq.com | 확인
[엘레파츠] 실리콘 점퍼 케이블 26AWG-RED (20cm, F/F) 화면 5 V 연장 1단(GPIO 2번). 재고 있음 | 1 | 451원 | 451원 | 엘레파츠 (https://www.eleparts.co.kr/goods/view?no=9461190) eleparts.co.kr | 확인
[엘레파츠] 실리콘 점퍼 케이블 26AWG-BLACK (20cm, F/F) GND 연장 1단(GPIO 6번) | 1 | 451원 | 451원 | 엘레파츠 (https://www.eleparts.co.kr/goods/view?no=9461199) eleparts.co.kr | 확인
[엘레파츠] 실리콘 점퍼 케이블 26AWG-RED (20cm, M/M) 5 V 연장 2단(TD2 전원선 하우징에 꽂음) | 1 | 451원 | 451원 | 엘레파츠 (https://www.eleparts.co.kr/goods/view?no=9756990) eleparts.co.kr | 확인
[엘레파츠] 실리콘 점퍼 케이블 26AWG-BLACK (20cm, M/M) GND 연장 2단 | 1 | 451원 | 451원 | 엘레파츠 (https://www.eleparts.co.kr/goods/view?no=9756998) eleparts.co.kr | 확인
스텐 유두 렌치볼트 M3 × 20 mm 경첩 축 2 + 다리 축 1 + 예비 1. 옵션 값은 추정(모든 조합 공통) | 4 | 100원 | 400원 | 11번가 굿나잇몰 (기존 볼트 주문 옵션) (https://www.11st.co.kr/products/4236198413) 11st.co.kr | 미확인
스텐 유두 렌치볼트 M3 × 10 mm (+4) CU 뚜껑 앞 모서리 고정 2 + 예비 2. 구매 목록 값(모든 조합 공통) | 4 | 60원 | 240원 | 11번가 굿나잇몰 (기존 L56 줄) (https://www.11st.co.kr/products/4236198413) 11st.co.kr | 미확인
배송비 | | | 0원 | 엘레파츠(화면·점퍼)는 6만 원 이상이라 무료배송, 아이씨뱅큐 리본과 11번가 나사는 기존 주문에 합침
합계 | | | 101,224원 | 지금 안(103,600원) 대비 −2,376원

화면은 엘레파츠, 리본은 아이씨뱅큐, 점퍼는 엘레파츠, 나사는 11번가예요. 모두 이미 있는 주문에 합쳐서 배송비가 없어요. 다른 조합: 디바이스마트 한 곳(rev 2 BOM, 화면+FIT0997+CH254 점퍼) 103,600원(오늘 오후 값, FIT0997 준비 1주). 리본만 아이씨뱅큐 FIT0997(4,620원, 1주)로 하면 102,764원, Adafruit 5822(3,520원, 미국 재고 7~10일)면 101,664원, 엘레파츠 Waveshare DSI 300 mm(B)(4,532원, 10/16 발송)면 102,676원. 화면을 쿠팡(103,370원, 10/2 도착)에서 사면 7,670원 더 비싸요. 아이씨뱅큐 기존 주문에 해외 재고 리본을 넣을 때는 다른 부품이 늦게 오지 않게 부분 배송을 고르세요(리본만 따로 주문하면 배송비가 붙을 수 있어요, 금액 미확인).

##### 받는 시기

화면: 10/1 발송 → 10/2(금)~10/6(화) 도착(10/3·10/5 택배 휴무). 300 mm 리본: 해외 재고 2주 이내라 10/14 무렵(중국 연휴로 10/20까지 늦을 수 있음). 리본은 통합(11/16) 때만 필요하고, 책상 시험은 동봉 200 mm 리본으로 바로 해요

##### Pi 5 설정

설정이 필요 없어요. CAM/DISP 1 포트에 꽂으면 Pi 5가 스스로 알아봐요(공식 문서). 안 뜨면 config.txt에 dtoverlay=vc4-kms-dsi-ili9881-7inch 한 줄을 넣어요(0번 포트면 끝에 ,dsi0). 리본은 22핀(Pi)→15핀(화면) 디스플레이용이어야 해요. 카메라용 리본은 모양이 같아도 핀 배열이 달라 안 돼요. 전원은 빨간 선을 GPIO 2번(5 V), 검은 선을 6번(GND)에 꽂아요. 세로 화면이라 앱이 1280×720으로 그린 뒤 화면과 터치 좌표를 함께 90° 돌려요. 콘솔 글자만 돌릴 때는 cmdline.txt에 video=DSI-1:720x1280@60,rotate=90을 써요. 밝기는 커널이 만드는 /sys/class/backlight 장치로 조절해요(정확한 이름은 받은 뒤 확인).

##### 전력

화면이 더 쓰는 전력 | 약 2.5 W (GPIO 2·6번)
평균 | 16.1~20.1 W
순간 최대 | 54.8 W (60 W까지 5.2 W 남음)
배터리 | 약 3.1~3.9시간
45 W 충전기 −2 dB | 39.8 W

화면 약 2.5 W(공식 수치가 없어 추정). Pi GPIO 2·6번에서 받아요(Pi에서 나가는 방향이라 D16 허용). 평균 16.1~20.1 W, 순간 최대 54.8 W(60 W까지 5.2 W 여유), 배터리 3.1~3.9시간, Pi 입력 2.09 A, 5.1 V 레일 2.49 A. 45 W 충전기는 −2 dB에서 39.8 W로 괜찮고, −1 dB에서는 화면을 꺼야 해요(sysfs로 끔).

#### 장착 (축척 스케치)

위에서 본 접은 상태. 파란 선 = 받침, 회색 = 화면 유리, 진한 회색 = 보이는 화면, 주황 = DSI 리본, 보라 = HDMI, 초록 = USB, 빨강 = 전원선, 점선 네모 = 뚜껑 아래 Pi 5. 선과 단자는 화면 뒤에 있어요. DSI 리본 단자 x629.7·u60.

옆에서 본 모습(y·z, mm). 실선 = 25°로 세운 상태, 점선 = 뒤로 접은 상태. 경첩 축·뚜껑·다리 주머니는 모든 조합에서 같아요.

받침 x559.04~752.96 (폭 193.9), 뚜껑 여유 왼쪽 2.54 · 오른쪽 2.54 mm. 접은 상태 y296.5~421.7, 받침 두께 17.00.

rev 2와 같아요. 받침 폭 193.92(x559.04~752.96), 뚜껑 양쪽 여유 2.54 mm. 접은 윗면 z113으로 스피커 윗면 z134보다 21 mm 낮아요. 접은 뒤끝 y421.7로 뒷면 y447 안이에요. 22°에서 가장 앞이 y276.7이라 통로(y254)를 지켜요. 리본 길 264.7 mm로 300 mm 리본에 35 mm가 남아요. 뚜껑 구멍 22×6은 그대로예요. 다리 힘 39.4 N(안전율 10), 뒤꿈치 161 N, 뚜껑 나사 78 N.

설계 변경: 없어요. CAD v13(rev 2)을 그대로 출력해요. 리본을 FIT0997 대신 공식 SC1132로 사도 둘 다 22→15핀 300 mm라 리본 클립·홈·구멍이 그대로예요.

#### 게임 영향

9.6 mm 2옥타브 흰 레인0.94 : 1 1옥타브 화면 : 실제 건반 0.92 MP 매 프레임 그릴 픽셀세로 매 프레임 90° 회전 필요

활성 폭 154.6 mm. 2옥타브 흰 레인 9.6 mm(1280 기준 80 px), 검은 레인 5.8 mm, 1옥타브 화면은 실제 건반과 0.94:1이에요. 세로 패널이라 매 프레임 1280×720(0.92 MP)을 90° 돌려야 해서 pygame 60 fps 여유가 A 그룹(국내) 세 조합 중 가장 적어요(A2와 같음). 13개 중 가장 적은 것은 8인치 세로인 B4예요. GPU로 돌리는 방법은 아직 시험하지 않았어요.

##### 장점

- 설계와 CAD(v13)가 끝나 있어 다시 그릴 것이 없어요
- Pi 5가 자동으로 알아봐 설정이 없어요
- 국내 재고, 24시간 안 발송이에요
- 공식품이라 KC 인증과 교환이 쉬워요
- 밝기를 소프트웨어로 0~100 % 조절할 수 있어 D14·D19 시험이 쉬워요
- 선이 리본 1개와 전원선 2가닥뿐이에요

##### 단점

- 세로 화면이라 앱이 매 프레임 화면과 터치를 돌려야 해요
- A 그룹(국내) 세 조합 중 두 번째로 비싸요
- 그릴 픽셀이 0.92 MP로 A3보다 50% 많아요

##### 위험

- 회전 처리가 60 fps를 깎을 수 있어요(GPU 회전은 미시험)
- 300 mm 리본이 해외 재고라 10/14~10/20쯤 와요. 통합 전에는 충분해요
- 디바이스마트는 오늘 밤 접속이 안 돼 그쪽 값은 오늘 오후 값이에요

#### 확인한 것 / 미확인

오늘 밤 23:29에 엘레파츠 TD2 7인치(95,700원, 재고 있음, 24시간 발송)와 점퍼 4종(451원, 재고 있음)을 다시 열어 확인했어요. 아이씨뱅큐 공식 SC1132 300 mm(3,080원, 해외 재고 2주 이내)도 확인했어요. 공식 SKU(SC1131/1132/1133 = 200/300/500 mm, 카메라와 호환 안 됨)는 판매처 목록으로 확인했어요. 디바이스마트는 밤에 접속이 거부되어 오늘 19:14~20:22 저장본 값(TD2 95,700원, FIT0997 5,390원 준비 1주, 66,000원 이상 무료배송·아니면 2,700원)만 있어요. 화면 전력 2.5 W와 M3 나사 값은 추정이에요.

- 공통 나사 M3×20 4개와 M3×10 4개(640원)는 모든 조합에서 추정값이에요.

맨 위 표로 ↑

A3A · 국내·빠름

### Waveshare 7인치 HDMI LCD (C) 정품 + FFC HDMI·USB 선: 가로 화면

가장 빠름게임에 유리(가로)

105,206원

지금 안 대비 +1,606원

10/2~10/6 · 국내 재고

Waveshare 7inch HDMI LCD (C) Rev4.1 (엘레파츠 WVS-11199) 제품 사진

제품 사진 (누르면 크게)

화면

Waveshare 7inch HDMI LCD (C) Rev4.1 (엘레파츠 WVS-11199)

크기·해상도

7인치 · 1024×600 (가로 기본)

방향

가로 기본. 회전 없음

연결

HDMI(화면 표준 HDMI-A) ← Pi 5 micro-HDMI(HDMI0), FFC HDMI 50 cm + 곧은 헤드 2개 / 터치·전원 micro-USB ← Pi USB-A, FFC USB 50 cm + 곧은 헤드 2개

패널

IPS, 300 cd/m², 명암비 800:1, 시야각 170°, 터치 유리 일체(광학 본딩 표기 없음)

터치

정전식 5점, USB HID(GT911). 드라이버 없이 hid-multitouch로 잡힘

외곽 (mm)

164.90 × 124.27 (고정귀 포함) / 몸체 164.90 × 106.96 × 8.0. 고정귀 구멍 156.90 × 114.96

보이는 영역 (mm)

154.21 × 85.92

Waveshare (C) Rev4.1 외형 치수 (누르면 크게)

#### 살 것

품목 | 수량 | 단가 | 금액 | 판매처 | 확인
Waveshare 7inch HDMI LCD (C) Rev4.1 (7인치 1024×600 정전식 HDMI) 79,160원+VAT. 동봉 HDMI 선·USB 선은 책상 시험용이에요(가진 1 m micro-HDMI 선으로도 시험 가능) | 1 | 87,076원 | 87,076원 | 엘레파츠 (재고 있음, 24시간 안 발송, 기존 주문 합배송) (https://www.eleparts.co.kr/goods/view?no=3321145) eleparts.co.kr | 확인
Wild Wire FFC HDMI 헤드 D-3 (micro HDMI 곧은형, Pi 쪽) 길이 26 mm, 폭 17 mm. Pi HDMI0에 꽂아요. 꺾인 D-1/D-2도 같은 값이에요 | 1 | 3,300원 | 3,300원 | 엘레파츠 (옵션 D-3) (https://www.eleparts.co.kr/goods/view?no=12558075) eleparts.co.kr | 확인
Wild Wire FFC HDMI 헤드 A-1 (HDMI-A 곧은형, 화면 쪽) 길이 27 mm, 화면 옆으로 약 17 mm 나와요 | 1 | 3,300원 | 3,300원 | 엘레파츠 (옵션 A-1) (https://www.eleparts.co.kr/goods/view?no=12558075) eleparts.co.kr | 확인
Wild Wire FFC HDMI-50Cm (20핀 0.5 mm FFC) 재고 있음. 경로 약 404 mm라 30 cm(1,672원)는 짧아요 | 1 | 2,145원 | 2,145원 | 엘레파츠 (https://www.eleparts.co.kr/goods/view?no=11845384) eleparts.co.kr | 확인
Wild Wire FFC USB 헤드 USB A-1 (USB-A 곧은형, Pi 쪽) 17 × 28.5 mm. Pi의 빈 USB-A(RJ45 쪽 위)에 꽂아요 | 1 | 3,300원 | 3,300원 | 엘레파츠 (옵션 USB A-1) (https://www.eleparts.co.kr/goods/view?no=11833566) eleparts.co.kr | 확인
Wild Wire FFC USB 헤드 Micro-1 (micro-USB 곧은형, 화면 쪽) 17 × 23 mm. 화면의 Touch 단자(전원+터치)에 꽂아요 | 1 | 3,300원 | 3,300원 | 엘레파츠 (옵션 Micro-1) (https://www.eleparts.co.kr/goods/view?no=11833566) eleparts.co.kr | 확인
Wild Wire FFC USB 2.0 케이블 50 cm (옵션 50cm) 기본(5 cm) 715원 + 50 cm 옵션 1,430원(VAT 포함) = 2,145원. 경로 약 472 mm라 여유 28 mm뿐이에요. 종이띠로 재서 485 mm를 넘으면 1 m(3,135원)로 바꿔요 | 1 | 2,145원 | 2,145원 | 엘레파츠 (https://www.eleparts.co.kr/goods/view?no=11851039) eleparts.co.kr | 확인
스텐 유두 렌치볼트 M3 × 20 mm 모든 조합 공통, 값 추정 | 4 | 100원 | 400원 | 11번가 굿나잇몰 (https://www.11st.co.kr/products/4236198413) 11st.co.kr | 미확인
스텐 유두 렌치볼트 M3 × 10 mm (+4) 모든 조합 공통, 구매 목록 값 | 4 | 60원 | 240원 | 11번가 굿나잇몰 (https://www.11st.co.kr/products/4236198413) 11st.co.kr | 미확인
배송비 | | | 0원 | 엘레파츠 한 곳에서 6만 원 이상이라 무료배송, 11번가 나사는 기존 주문에 합침
합계 | | | 105,206원 | 지금 안(103,600원) 대비 +1,606원

화면과 선 6개 모두 엘레파츠라 한 번에 와요(6만 원 이상 무료배송). GPIO 점퍼와 DSI 리본은 필요 없어요. USB FFC를 1 m로 바꾸면 106,196원이에요. 같은 모양 다른 국내 판매처: 메카솔루션 OEM (C)형 88,000원(아크릴 케이스 포함, 복제품), 디바이스마트 PRC판 88,000원(준비 1주, 오늘 밤 미확인). 둘 다 정품보다 싸지 않아요.

##### 받는 시기

모두 국내 재고, 24시간 안 발송 → 10/2(금)~10/6(화) 도착

##### Pi 5 설정

config.txt는 고치지 않아요. Pi 5의 KMS는 hdmi_cvt 같은 옛 설정을 쓰지 않고 화면이 보내는 EDID로 1024×600을 잡아요. 화면은 HDMI0(HDMI-A-1)에 꽂아 부팅 글자도 이 화면에 나오게 하고, TV는 HDMI1(HDMI-A-2)에 가진 1 m 선으로 꽂아요(TV 연결 감지는 HDMI-A-2만 봐요). 해상도가 틀리면 /boot/firmware/cmdline.txt 끝에 video=HDMI-A-1:1024x600M@60D 한 줄을 넣어요. HDMI 소리는 쓰지 않으니 dtoverlay=vc4-kms-v3d,noaudio로 꺼 두면 ALSA 번호가 바뀌지 않아요(선택, D7). 터치는 USB HID라 드라이버 없이 evdev로 SDL에 들어가고, 앱이 이 장치를 내장 화면에 맞춰 써요. 가로 기본이라 회전이 없어요. 밝기는 기판 스위치로 켜고 끄기만 돼요. 소프트웨어 밝기는 Waveshare 스크립트(Pi OS Lite에서 미확인)나 PWM 패드 개조(0 Ω 저항 떼고 GPIO PWM 연결, 미확인)가 필요해요.

##### 전력

화면이 더 쓰는 전력 | 약 2.45 W (Pi USB-A)
평균 | 16.0~20.0 W
순간 최대 | 54.7 W (60 W까지 5.3 W 남음)
배터리 | 약 3.1~3.9시간
45 W 충전기 −2 dB | 39.7 W

화면 약 2.45 W(Waveshare: 백라이트 켬 490 mA, 끔 90 mA). Pi USB-A 하나에서 받아요(Pi USB 합계 0.69/1.6 A). 평균 16.0~20.0 W, 순간 최대 54.7 W(60 W까지 5.3 W 여유), 배터리 3.1~3.9시간, Pi 입력 2.08 A, 5.1 V 레일 2.48 A. 스위치로 백라이트를 끄면 0.45 W라 45 W 충전기 −1 dB에서도 44.1 W로 들어가요. 화면에 다른 전원을 넣지 않아 역급전 걱정이 없어요(D16).

#### 장착 (축척 스케치)

위에서 본 접은 상태. 파란 선 = 받침, 회색 = 화면 유리, 진한 회색 = 보이는 화면, 주황 = DSI 리본, 보라 = HDMI, 초록 = USB, 빨강 = 전원선, 점선 네모 = 뚜껑 아래 Pi 5. 선과 단자는 화면 뒤에 있어요. HDMI 단자 x728.5·u99 / USB 단자 x728.5·u71.

옆에서 본 모습(y·z, mm). 실선 = 25°로 세운 상태, 점선 = 뒤로 접은 상태. 경첩 축·뚜껑·다리 주머니는 모든 조합에서 같아요.

받침 x561.25~747.75 (폭 186.5), 뚜껑 여유 왼쪽 4.75 · 오른쪽 7.75 mm. 접은 상태 y296.5~425.8, 받침 두께 17.00.

기판 164.9 × 124.27(고정귀 포함), 두께 8 mm. 오른쪽 끝의 HDMI·USB 헤드가 약 17 mm 나와서 화면 가운데를 x646으로 10 mm 옮겨요. 받침 폭 186.5(x561.25~747.75), 뚜껑 여유 4.75/7.75 mm. 받침 두께 17 mm가 그대로라 접은 윗면 z113, 22° 가장 앞 y276.7이에요. 접은 뒤끝 y425.8로 뒷면 y447 안이고, 접이 발 네 개가 모두 받침 밑에 와요. 선 길이는 HDMI 약 404 mm(50 cm에 96 mm 남음), USB 약 472 mm(50 cm에 28 mm로 빠듯)예요. FFC 두 장을 겹쳐 22×6 구멍과 받침 아래 홈으로 넣고, 헤드는 FFC를 넣은 뒤 끼우니 구멍을 키우지 않아요. 다리 힘 39.9 N(안전율 9.9), 뒤꿈치 163 N, 뚜껑 나사 79 N.

설계 변경: 받침을 새로 그려요. 폭 186.5, 가운데 x646, 고정귀 나사 자리 4개(156.9 × 114.96), Pi 스탠드오프 피함 구멍은 없애요. 오른쪽 벽에 HDMI·USB 헤드 자리(약 17 mm)와 백라이트 스위치 구멍을 내요. FFC 두 장이 아래 홈에서 기판 뒤를 지나 오른쪽 끝까지 가는 길을 만들어요. 뚜껑 v2는 그대로예요(구멍 22×6, 경첩 받침, 다리 주머니, 접이 발, 통풍 슬롯). 뚜껑 밑 리본 클립이 FFC 두 장을 함께 잡는지만 확인해요. 뚜껑을 뗄 때는 Pi 쪽 헤드를 빼고 FFC를 구멍으로 빼요. CAD는 받침·점검창 덮개·조립 파일을 다시 만들어요.

#### 게임 영향

9.6 mm 2옥타브 흰 레인0.94 : 1 1옥타브 화면 : 실제 건반 0.61 MP 매 프레임 그릴 픽셀가로 회전 없음

활성 폭 154.2 mm라 레인 크기가 A1과 같아요(2옥타브 흰 레인 9.6 mm = 64 px, 1옥타브 0.94:1). 가로 1024×600이라 회전이 없고 그릴 픽셀이 0.61 MP로 A1보다 33% 적어 60 fps 여유가 가장 커요(B1·C1·C1b와 같음). 16:9 그림은 1024×576으로 넣어요. HDMI 변환 칩 때문에 약 1프레임 늦지만 게임의 화면 보정으로 없애요.

##### 장점

- 가로 화면이라 회전 코드가 없어요
- 그릴 픽셀이 33% 적어 게임 60 fps에 여유가 있어요
- 국내 재고, 모든 부품이 한 판매처에서 24시간 안 발송이에요
- 드라이버 없는 USB 터치예요
- 두께 8 mm로 얇고, 뚜껑은 그대로 써요
- GPIO 선이 필요 없어요

##### 단점

- 국내 재고 조합(A1~A3) 중 가장 비싸요(rev 2보다 1,606원 많음)
- 밝기를 소프트웨어로 조절하지 못하고 스위치로 켜고 끄기만 해요
- Pi의 HDMI 포트 하나와 USB 포트 하나를 써요
- 헤드 4개의 FFC 잠금부가 약해 조심해서 다뤄야 해요
- 받침을 새로 그려야 해요

##### 위험

- USB FFC 여유가 28 mm뿐이라 실제로 짧을 수 있어요(1 m로 바꾸면 해결)
- FFC 두 장이 접을 때마다 경첩 고리를 지나서 오래 쓰면 끊길 수 있어요(시험 필요)
- D-3 헤드 폭 17 mm가 옆 HDMI 포트의 TV 선 플러그에 닿을 수 있어요(포트 간격 약 13.4 mm 추정)
- EDID가 1024×600을 제대로 안 알리면 video= 한 줄이 필요해요
- D14의 밝기 0 % 시험은 스위치로 끈 상태로만 할 수 있어요

#### 확인한 것 / 미확인

오늘 밤 23:29에 엘레파츠 화면(87,076원, 재고 있음, 24시간 발송), HDMI 헤드(3,300원, D-3·A-1 옵션 있음), FFC HDMI 50 cm(2,145원, 재고 있음), USB 헤드(3,300원, USB A-1·Micro-1 옵션 있음), USB FFC(50 cm 옵션 2,145원)를 다시 열어 확인했어요. 헤드 치수는 판매 페이지 그림에서 읽었어요. Waveshare 위키에서 외곽·전류(490/90 mA)·밝기 300 cd/m²·Rev4.1을, Raspberry Pi 문서에서 video= 문법과 HDMI-A-1/2 이름, 옛 hdmi_* 설정을 KMS가 쓰지 않는다는 것을 확인했어요. 미확인: USB FFC 폭, 실제 선 길이, Pi 5에서 EDID 동작, Waveshare 밝기 스크립트, TV 선과 헤드가 닿는지.

- 공통 나사 M3×20 4개와 M3×10 4개(640원)는 모든 조합에서 추정값이에요.

맨 위 표로 ↑

C4bC · 싸게·크게

### Waveshare 7inch DSI LCD (E) 7인치 1280×800 광학 본딩 DSI (해외 직구)

게임에 유리(가로)

106,464원

지금 안 대비 +2,864원

10/12~10/25 · 해외, 추정

Waveshare 7inch DSI LCD (E) (7인치 넓은 색역 정전식 터치, DSI) 제품 사진

제품 사진 (누르면 크게)

화면

Waveshare 7inch DSI LCD (E) (7인치 넓은 색역 정전식 터치, DSI)

크기·해상도

7인치 · 1280×800

방향

가로(landscape) 기본, 회전 필요 없음

연결

MIPI DSI 15핀 1.0 mm FPC + PH2.0 4핀(5 V·GND·SDA·SCL)

패널

IPS, 광학 본딩 강화유리 6H, 색역 NTSC 68%, 밝기 비공개

터치

정전식 10점, I2C(Goodix, 커널 기본 오버레이)

외곽 (mm)

유리 170.18 × 104.20, 두께 8.0 (Pi용 M2.5 받침 8은 떼어냄), 기판 M3 구멍 95 × 68

보이는 영역 (mm)

151.80 × 95.10

Waveshare 7inch DSI LCD (E) 치수 도면

Waveshare 7inch DSI LCD (E) 치수 (누르면 크게)

#### 살 것

품목 | 수량 | 단가 | 금액 | 판매처 | 확인
Waveshare 7inch DSI LCD (E) (알리익스프레스 Waveshare 공식 스토어) 오늘 검색 목록에 Waveshare Official Store '7인치 DSI 1280×800 IPS 광학 본딩' 100,940원이 떴지만 상품 페이지는 로봇 확인으로 열지 못했어요. 배송비 미확인. Waveshare 직판은 오늘 $66.99(약 90,624원) + 배송비(미확인) | 1 | 100,940원 | 100,940원 | 알리익스프레스 (검색 목록가) (https://ko.aliexpress.com/w/wholesale-waveshare-7inch-DSI-LCD-1280x800-optical-bonding.html) aliexpress.com | 미확인
Raspberry Pi 5 공식 디스플레이 리본 Standard–Mini 300 mm (SC1132) 2,800원+VAT. 22핀(Pi)→15핀(화면) 디스플레이용 300 mm라 rev 2의 FIT0997과 종류·길이가 같아요. A1·A2와 같은 줄이에요. 카메라용(SC1129)은 모양이 같아도 핀 배열이 달라 못 써요 | 1 | 3,080원 | 3,080원 | 아이씨뱅큐 (해외 재고, 2주 이내, 기존 아이씨뱅큐 주문에 합침) (https://www.icbanq.com/P015646405) icbanq.com | 확인
[엘레파츠] 실리콘 점퍼 26AWG 20cm F/F 빨강·검정, M/M 빨강·검정 PH2.0 4핀 선의 5 V·GND를 GPIO 2번·6번까지 늘려요 | 4 | 451원 | 1,804원 | 엘레파츠 (24시간 발송) (https://www.eleparts.co.kr/goods/view?no=9461190) eleparts.co.kr | 확인
스텐 유두 렌치볼트 M3 × 20 mm 모든 조합 공통, 값 추정 | 4 | 100원 | 400원 | 11번가 굿나잇몰 (https://www.11st.co.kr/products/4236198413) 11st.co.kr | 미확인
스텐 유두 렌치볼트 M3 × 10 mm (+4) 모든 조합 공통, 값 추정 | 4 | 60원 | 240원 | 11번가 굿나잇몰 (https://www.11st.co.kr/products/4236198413) 11st.co.kr | 미확인
배송비 | | | 0원 | 알리 배송비 미확인(0원으로 둠) + 아이씨뱅큐 리본·엘레파츠 점퍼·11번가 나사는 기존 주문에 합침
합계 | | | 106,464원 | 지금 안(103,600원) 대비 +2,864원

알리 목록가 100,940 + 공식 300 mm 리본 SC1132 3,080 + 점퍼 1,804 + 공통 나사 640 = 106,464원이에요. 알리 배송비는 확인하지 못해 0원으로 두었어요. 리본은 A1·A2와 같은 아이씨뱅큐 줄이라 기존 아이씨뱅큐 주문에 합쳐요. rev 2처럼 디바이스마트 FIT0997(5,390원)을 쓰면 디바이스마트 단독 주문(66,000원 미만)이라 배송비 2,700원이 붙어 111,474원이에요(9/30 저장본 값, 오늘 밤 미확인). 직판이면 90,624원 + 배송비(미확인)라 배송비가 약 1만 원 이하일 때만 더 싸요. 국내 판매처는 없었어요(쿠팡, 다나와, 엘레파츠, 메카솔루션, 11번가 0건, 디바이스마트 접속 불가).

##### 받는 시기

Waveshare 창고 10/5부터 출고. 알리면 10/15~10/25, 직판 DHL이면 10/12~10/19로 추정해요(미확인). 300 mm 리본(SC1132)은 아이씨뱅큐 해외 재고(2주 이내)라 10/14 무렵 와요(중국 연휴로 10/20까지 늦을 수 있어요, 추정). 리본은 통합(11/16) 때 필요해요.

##### Pi 5 설정

config.txt에 dtoverlay=vc4-kms-dsi-waveshare-panel,8_0_inch 한 줄(Waveshare 위키가 (E)에도 이 줄을 씀, 커널 기본 오버레이). CAM/DISP 1 포트, 0번이면 ,dsi0. 리본 22→15핀 디스플레이용 300 mm(공식 SC1132, 동봉 12 cm는 짧음). 전원은 동봉 PH2.0 4핀 선의 5 V·GND만 GPIO 2번·6번에 이어요. 터치는 Goodix(evdev), 밝기는 /sys/class/backlight/*/brightness 0~255. 가로라 회전 없음. HDMI 두 포트는 비어 있어요.

##### 전력

화면이 더 쓰는 전력 | 약 2.6 W (GPIO 2·6번)
평균 | 16.2~20.2 W
순간 최대 | 54.9 W (60 W까지 5.1 W 남음)
배터리 | 약 3.1~3.9시간
45 W 충전기 −2 dB | 39.9 W

화면 약 2.6 W로 가정(공개 값 없음). GPIO에서 받아요. 평균 16.2~20.2 W, 최대 54.9 W(여유 5.1 W), 45 W −2 dB 39.9 W, 배터리 3.12~3.89시간, Pi 입력 2.11 A.

#### 장착 (축척 스케치)

위에서 본 접은 상태. 파란 선 = 받침, 회색 = 화면 유리, 진한 회색 = 보이는 화면, 주황 = DSI 리본, 보라 = HDMI, 초록 = USB, 빨강 = 전원선, 점선 네모 = 뚜껑 아래 Pi 5. 선과 단자는 화면 뒤에 있어요. DSI 리본 단자 x620.0·u80 (추정).

옆에서 본 모습(y·z, mm). 실선 = 25°로 세운 상태, 점선 = 뒤로 접은 상태. 경첩 축·뚜껑·다리 주머니는 모든 조합에서 같아요.

받침 x568.61~743.39 (폭 174.8), 뚜껑 여유 왼쪽 12.11 · 오른쪽 12.11 mm. 접은 상태 y296.5~405.7, 받침 두께 17.00.

넉넉히 들어가요. 받침 x568.61~743.39(폭 174.78), 뚜껑 여유 양쪽 12.1 mm. 두께 8이라 받침 두께 D_c 17로 rev 2와 같고 접은 높이 z113, 22°에서 가장 앞 y276.7, 접은 뒤끝 y405.7. 리본 274.9/300 mm(여유 25.1). 뚜껑 구멍 22×6 그대로. 다리 38 N(안전율 10.4), 뒤꿈치 155 N, 뚜껑 나사 75 N, 넘어짐 안전율 2.5.

설계 변경: 뚜껑 v2는 그대로예요. 받침만 작게 새로 그려요(M3 95×68 고정, FPC·PH2.0 점검창). 받침 두께와 다리 걸이는 rev 2와 같아요. 리본도 rev 2와 같은 종류(22→15핀 300 mm, 공식 SC1132)라 설계 변경이 작은 고화질 안이에요.

#### 게임 영향

9.4 mm 2옥타브 흰 레인0.92 : 1 1옥타브 화면 : 실제 건반 1.02 MP 매 프레임 그릴 픽셀가로 회전 없음

1280×800 가로, 광학 본딩, 넓은 색역이라 7인치 중 가장 선명한 쪽이에요(픽셀 0.118 mm, C3와 같음). 활성 폭 151.8 mm라 2옥타브 흰 레인 9.4 mm(80 px), 1옥타브 0.92:1. 픽셀 1.02 MP로 60 fps 예산 안이고, DSI라 지연이 적어요.

##### 장점

- 7인치 중 해상도가 가장 높은 쪽이고(1280×800, C3와 같음) 색이 진해요(광학 본딩, NTSC 68%).
- DSI 설정 한 줄, sysfs 밝기, HDMI 두 포트가 남아요.
- 접은 높이·받침 두께·리본이 rev 2와 같아 설계 변경이 작은 편이에요(받침 외곽은 새로 그려요).
- 뚜껑 여유가 12 mm로 넉넉해요.

##### 단점

- 국내 판매처가 없어요.
- rev 2보다 2,864원 비싸요(알리 목록가 기준, 배송비 미확인).
- 밝기와 전력 값이 공개되지 않았어요.

##### 위험

- 알리 값·배송비를 상품 페이지에서 확인하지 못했어요.
- 국경절 때문에 늦게 와요.
- 300 mm 리본은 아이씨뱅큐 해외 재고라 10/14~10/20쯤 와요. 통합(11/16) 전에는 충분해요.

#### 확인한 것 / 미확인

오늘 Waveshare 판매 페이지($66.99, 무게 0.29 kg, 구성품: 15핀 FPC 50·160 mm, MIPI-DSI-Cable-12cm, PH2.0 4핀 선 약 200 mm, 나사)와 위키(설정 줄 8_0_inch, Pi 5는 스프링 핀 전원, sysfs 밝기)를 확인했어요. 알리 검색 목록가만 봤고 상품 페이지·배송비는 확인하지 못했어요. 리본은 아이씨뱅큐 SC1132(3,080원, 해외 재고 2주 이내)를 오늘 밤 확인했어요(A1과 같은 줄).

- Waveshare 7inch DSI LCD (E) (알리익스프레스 Waveshare 공식 스토어) (100,940원): 오늘 검색 목록에 Waveshare Official Store '7인치 DSI 1280×800 IPS 광학 본딩' 100,940원이 떴지만 상품 페이지는 로봇 확인으로 열지 못했어요. 배송비 미확인. Waveshare 직판은 오늘 $66.99(약 90,624원) + 배송비(미확인)
- 공통 나사 M3×20 4개와 M3×10 4개(640원)는 모든 조합에서 추정값이에요.

맨 위 표로 ↑

C2C · 싸게·크게

### 8인치 1280×800 HDMI 아크릴 일체형(쿠팡) + FFC 선 두 벌, 테두리 없는 받침

게임에 유리(가로)

107,830원

지금 안 대비 +4,230원

10/16~10/23 · 해외, 10/16 표시

LCDwiki MPI8008 '8inch HDMI Display-Y' (쿠팡 표기 MPI0808, 브랜드 CFsunbird, 쿠팡 9676810746) 제품 사진

제품 사진 (누르면 크게)

화면

LCDwiki MPI8008 '8inch HDMI Display-Y' (쿠팡 표기 MPI0808, 브랜드 CFsunbird, 쿠팡 9676810746)

크기·해상도

8인치 · 1280×800

방향

가로(landscape) 기본. 단자 홈을 왼쪽에 두려고 180° 돌려 달면 앱에서 상하좌우를 뒤집어요

연결

HDMI + micro-USB 'TOUCH'(터치와 전원 겸용) + micro-USB 'POWER'(전원만, 안 씀) + 백라이트 버튼

패널

IPS 8인치, 밝기 220 cd/m²(낮은 편), 커버 유리 1 mm + 아크릴 3겹 틀, 광학 본딩 없음

터치

정전식 5점, USB HID(LCDwiki: 터치 드라이버 불필요)

외곽 (mm)

197.0 × 132.0 × 12.0 (아크릴 포함 전체, LCDwiki 도면). 뒷면 가운데 Pi 고정 구멍 4개 58 × 49(M2.5 구리 기둥), 한쪽 끝에 50 × 66 단자 홈

보이는 영역 (mm)

172.22 × 107.64

LCDwiki MPI8008 도면

LCDwiki MPI8008 도면 (누르면 크게)

#### 살 것

품목 | 수량 | 단가 | 금액 | 판매처 | 확인
8인치 1280×800 IPS HDMI 터치 아크릴 케이스 일체형 (쿠팡 9676810746, 01 Capacitive touch) 오늘 확인: 89,300원, 무료배송, 10/16 도착 예정, 판매자 평가 14건 이하, 상품평 0개, 단순 변심 반품 왕복 89,300원(상품값과 같음) | 1 | 89,300원 | 89,300원 | 쿠팡 (판매자 다온전기, 해외직구·구매대행, CJ대한통운) (https://www.coupang.com/vp/products/9676810746?itemId=28934940406) coupang.com | 확인
Wild Wire FFC HDMI 헤드 D-3 (Pi 쪽) 옵션 D-3 | 1 | 3,300원 | 3,300원 | 엘레파츠 (24시간 발송) (https://www.eleparts.co.kr/goods/view?no=12558075) eleparts.co.kr | 확인
Wild Wire FFC HDMI 헤드 A-1 (화면 쪽) 옵션 A-1. 단자 홈(깊이 약 9 mm) 안에 들어가요 | 1 | 3,300원 | 3,300원 | 엘레파츠 (24시간 발송) (https://www.eleparts.co.kr/goods/view?no=12558075) eleparts.co.kr | 확인
Wild Wire FFC HDMI-50Cm 180° 돌려 달면 경로 약 231 mm라 30 cm(1,672원)도 되지만 여유를 위해 50 cm | 1 | 2,145원 | 2,145원 | 엘레파츠 (24시간 발송) (https://www.eleparts.co.kr/goods/view?no=11845384) eleparts.co.kr | 확인
Wild Wire FFC USB 헤드 USB A-1 (Pi 쪽) 옵션 USB A-1 | 1 | 3,300원 | 3,300원 | 엘레파츠 (24시간 발송) (https://www.eleparts.co.kr/goods/view?no=11833566) eleparts.co.kr | 확인
Wild Wire FFC USB 헤드 Micro-1 (화면 'TOUCH' 쪽) 옵션 Micro-1. TOUCH 포트 하나로 터치와 전원을 함께 받아요(LCDwiki) | 1 | 3,300원 | 3,300원 | 엘레파츠 (24시간 발송) (https://www.eleparts.co.kr/goods/view?no=11833566) eleparts.co.kr | 확인
Wild Wire FFC USB 리본 50 cm 기본(5 cm) 715원 + 50 cm 옵션 1,430원(VAT 포함) = 2,145원. 경로 약 357 mm | 1 | 2,145원 | 2,145원 | 엘레파츠 (24시간 발송) (https://www.eleparts.co.kr/goods/view?no=11851039) eleparts.co.kr | 확인
스텐 유두 렌치볼트 M2.5 × 8 mm (케이스 Pi 구멍 4개로 뒤판 고정) 값은 추정. 뒤판 3 mm + 구리 기둥 나사산 약 5 mm | 4 | 100원 | 400원 | 11번가 굿나잇몰 (규격 목록에 M2.5 있음) (https://www.11st.co.kr/products/4236198413) 11st.co.kr | 미확인
스텐 유두 렌치볼트 M3 × 20 mm 모든 조합 공통, 값 추정 | 4 | 100원 | 400원 | 11번가 굿나잇몰 (https://www.11st.co.kr/products/4236198413) 11st.co.kr | 미확인
스텐 유두 렌치볼트 M3 × 10 mm (+4) 모든 조합 공통, 값 추정 | 4 | 60원 | 240원 | 11번가 굿나잇몰 (https://www.11st.co.kr/products/4236198413) 11st.co.kr | 미확인
배송비 | | | 0원 | 쿠팡 무료배송 + 엘레파츠 줄은 기존 엘레파츠 주문에 합침(따로 사면 +3,000원) + 11번가 나사는 기존 주문에 합침
합계 | | | 107,830원 | 지금 안(103,600원) 대비 +4,230원

화면 89,300 + HDMI FFC 세트 8,745 + USB FFC 세트 8,745 + M2.5 나사 400(추정) + 공통 640 = 107,830원. 엘레파츠는 기존 주문 합배송 가정(따로면 +3,000원). 쿠팡에 더 싼 8인치 1280×800 HDMI는 없었어요(다음은 107,760원짜리 다른 제품, SY8008-610G 220,000원).

##### 받는 시기

쿠팡 표시 10/16 도착 예정(해외 발송). 10/23까지 밀릴 수 있어요. FFC 부품은 10/2~10/6.

##### Pi 5 설정

EDID가 맞으면 설정이 없어요. 안 맞으면 cmdline.txt에 video=HDMI-A-1:1280x800M@60 한 줄을 넣어요. LCDwiki가 알려 주는 hdmi_cvt, hdmi_group, max_usb_current 같은 줄은 Bookworm부터 무시되거나 필요 없으니 넣지 않아요. 연결: Pi HDMI0 → D-3 → HDMI FFC → A-1 → 화면 HDMI, Pi 빈 USB-A → A-1 → USB FFC → Micro-1 → 화면 'TOUCH'(터치+전원). 'POWER' 포트는 비워 둬요. 터치는 USB HID(evdev). 밝기는 뒷면 버튼으로만 바꿔요(누를 때마다 10 %씩, 3초 누르면 꺼짐). 단자 홈을 뚜껑 구멍 쪽(왼쪽)으로 두려고 180° 돌려 달면, 앱에서 화면과 터치 좌표를 상하좌우로 뒤집어요(콘솔은 video=HDMI-A-1:1280x800M@60,rotate=180). config.txt는 dtoverlay=vc4-kms-v3d,noaudio를 권해요.

##### 전력

화면이 더 쓰는 전력 | 약 3.79 W (Pi USB-A)
평균 | 17.5~21.5 W
순간 최대 | 56.2 W (60 W까지 3.8 W 남음)
배터리 | 약 2.9~3.6시간
45 W 충전기 −2 dB | 41.2 W

화면 3.79 W(LCDwiki, 밝기 100 %). Pi USB에서 받아요. 평균 17.5~21.5 W, 최대 56.2 W(60 W까지 3.8 W 여유), 45 W 충전기 −2 dB 41.2 W, 배터리 2.9~3.6시간. Pi 입력 2.34 A, 5.1 V 레일 2.74 A, Pi USB 0.96/1.6 A. TD2보다 약 1.3 W 더 써요.

#### 장착 (축척 스케치)

위에서 본 접은 상태. 파란 선 = 받침, 회색 = 화면 유리, 진한 회색 = 보이는 화면, 주황 = DSI 리본, 보라 = HDMI, 초록 = USB, 빨강 = 전원선, 점선 네모 = 뚜껑 아래 Pi 5. 선과 단자는 화면 뒤에 있어요. HDMI 단자 x607.5·u47 / USB 단자 x607.5·u77.

옆에서 본 모습(y·z, mm). 실선 = 25°로 세운 상태, 점선 = 뒤로 접은 상태. 경첩 축·뚜껑·다리 주머니는 모든 조합에서 같아요.

받침 x557.50~754.50 (폭 197.0), 뚜껑 여유 왼쪽 1.00 · 오른쪽 1.00 mm. 접은 상태 y296.5~433.5, 받침 두께 19.60.

들어가요. 다만 테두리 없는 받침으로만 들어가요. 폭이 197 mm라 CU 뚜껑(199 mm) 양옆 여유가 1.0 mm뿐이에요. 테두리 벽(2.0 + 틈 0.3)을 두르면 201.6 mm가 되어 넘치므로, 받침은 경첩 귀와 다리가 붙은 뒤판만 두고 케이스 뒤 가운데의 Pi 구멍 4개(58×49)에 M2.5 나사로 조여요. 케이스를 180° 돌려 단자 홈(50×66)을 왼쪽(뚜껑 구멍 쪽)에 둬요. 받침 x557.5~754.5, 접은 높이 z115.6(통과), 22°에서 가장 앞 y274.3(통과), 접은 뒤끝 y433.5(y447 안), 사용 중 맨 위 z234.3. 선 길이는 HDMI 약 231 mm, USB 약 357 mm. 뚜껑 구멍 22×6 그대로(FFC 두 장 겹침). 다리 힘 45 N(안전율 8.7), 뒤꿈치 184 N, 뚜껑 나사 89 N, 넘어짐 안전율 2.1로 TD2보다 낮지만 모두 기준 안이에요. 합판 뚜껑과 겹치지는 않지만 출력·조립 오차가 1 mm를 넘으면 합판 뚜껑 위로 걸쳐요.

설계 변경: 뚜껑 v2는 그대로예요. 받침은 완전히 새로 그려요: 테두리 없는 뒤판(케이스보다 좁게), 가운데 M2.5 구멍 4개(58×49), 단자 홈 창과 FFC 길, 백라이트 버튼 창, 경첩 귀·뒤꿈치·다리 걸이. 받침 두께가 D_c 19.6으로 늘어 다리 걸이 위치와 25° 각도를 다시 맞춰요. 아크릴 모서리가 드러나므로 운반할 때 긁힘을 막는 덮개를 생각해요. rev 2 받침은 쓰지 못해요.

#### 게임 영향

10.7 mm 2옥타브 흰 레인1.05 : 1 1옥타브 화면 : 실제 건반 1.02 MP 매 프레임 그릴 픽셀가로 180° 뒤집기 (가벼움)

1280×800 가로예요. 활성 폭 172.2 mm라 2옥타브 흰 레인 10.7 mm(80 px), 1옥타브 화면은 O4 옥타브와 1.05:1로 거의 같은 크기예요. 픽셀은 1.02 MP로 1024×600의 1.67배지만 pygame 60 fps 예산 안이에요. 180° 달면 매 프레임 뒤집기가 더해지지만 가벼운 작업이에요. 밝기가 220 cd/m²라 밝은 교실에서는 흐리게 보일 수 있어요. 16:9 그림은 1280×720으로 띠가 생겨요.

##### 장점

- 뚜껑에 들어가는 가장 큰 크기(8인치, B4·C4a와 같음)이고 해상도도 1280×800이에요.
- 2옥타브 레인이 10.7 mm로 넓어져 게임이 보기 쉬워요.
- LCDwiki에 치수 도면이 있고 뒷면 Pi 구멍으로 단단히 고정할 수 있어요.
- micro-USB 하나로 터치와 전원을 같이 받아요.
- C1보다 4일 빠른 10/16 도착 예정이에요.

##### 단점

- 양옆 여유가 1.0 mm뿐이라 받침을 테두리 없이 새로 그려야 해요.
- 밝기가 220 cd/m²로 어둡고, 소프트웨어로 밝기를 못 바꿔요(버튼만).
- rev 2보다 4,230원 비싸요.
- 전력이 3.79 W로 60 W 여유가 3.8 W로 줄어요.
- 무거워서(약 0.45 kg 추정) 넘어짐 안전율이 2.1로 내려가요.

##### 위험

- 쿠팡 상세 표에는 해상도 '800x480', 모델 'MPI0808'로 적혀 있어 다른 패널이 올 수 있어요. 받으면 1280×800인지 먼저 확인해요.
- 반품비가 89,300원이라 사실상 반품이 어려워요.
- 판매자 평가가 14건 이하예요.
- EDID가 틀리면 video= 한 줄로 맞춰야 해요.
- 단자 홈 안에서 FFC 머리가 제대로 꽂히는지 받아서 확인해야 해요.

#### 확인한 것 / 미확인

오늘 쿠팡 페이지(가격, 10/16, 해외직구, 반품비 89,300원, 판매자 정보, 상세 표)와 쿠팡 8인치 검색(더 싼 같은 제품 없음)을 확인했어요. LCDwiki 8inch HDMI Display-Y(MPI8008) 페이지와 도면 PDF로 외곽 197×132×12, 활성 172.22×107.64, 전력 3.79 W, 밝기 220 cd/m², TOUCH 포트가 전원 겸용, 뒷면 Pi 구멍 58×49와 단자 홈 50×66을 확인했어요. 확인 못 한 것: 쿠팡 제품이 정말 MPI8008인지(상세 표가 어긋남), 동봉품, 무게.

- 공통 나사 M3×20 4개와 M3×10 4개(640원)는 모든 조합에서 추정값이에요.

맨 위 표로 ↑

B2B · DSI 호환·해외

### Waveshare 7-DSI-TOUCH-A (7인치 720×1280, TD2와 같은 외곽) + 22핀 400 mm 리본

화질 가장 좋음

108,449원

지금 안 대비 +4,849원

10/12~10/26 · 해외, 추정

Waveshare 7-DSI-TOUCH-A (7인치 DSI 정전식 터치, 광학 본딩) 제품 사진

제품 사진 (누르면 크게)

화면

Waveshare 7-DSI-TOUCH-A (7인치 DSI 정전식 터치, 광학 본딩)

크기·해상도

7인치 · 720×1280, 61.2 Hz (커널 드라이버 타이밍으로 계산)

방향

처음부터 세로(portrait)예요. 가로로 쓰려면 앱이 매 프레임 그림을 90° 돌려서 보내야 해요. 터치는 오버레이 옵션으로 커널에서 돌려요.

연결

MIPI DSI 22핀 0.5 mm (Pi 5 CAM/DISP 1) + MX1.25 2핀 5 V 전원(GPIO에서)

패널

IPS, 광학 본딩 강화유리(6H), 지문 방지 코팅, 450 cd/m², 시야각 170°, 금속 뒷판

터치

정전식 10점, Goodix GT9271(I2C), 커널 기본 드라이버 → evdev 터치 장치

외곽 (mm)

189.32 × 120.24 × 9.3 (러그 면까지. TD2 9.4와 거의 같고, Pi 스탠드오프를 달면 14.8). M2.5 러그 4개가 140 × 70.71로 TD2와 같은 자리예요. 모서리 R8

보이는 영역 (mm)

155.00 × 88.00

Waveshare 7-DSI-TOUCH-A 도면

Waveshare 7-DSI-TOUCH-A 도면 (누르면 크게)

#### 살 것

품목 | 수량 | 단가 | 금액 | 판매처 | 확인
Waveshare 7-DSI-TOUCH-A 7인치 DSI 정전식 터치 720×1280 IPS 광학 본딩 오늘 페이지 값은 판매가 101,100원이고, 조건부 가격은 100,090원부터예요. 11번가 10월 쿠폰 2만 원 표시가 있지만 조건은 확인하지 못했어요. 동봉품은 C형과 같아요(22핀 200 mm 반대면 리본 2개, 전원선). | 1 | 101,100원 | 101,100원 | 11번가 해외직구 (판매자 신정종합상사G7, 무료배송, '중국에서 10/1 발송' 표시) (https://www.11st.co.kr/products/9609527225) 11st.co.kr | 확인
GUOCONN 0.5*22P*400*B FFC 22핀 0.5 mm 400 mm 반대면(B형, Reverse) Pi 5 CAM/DISP 1과 화면 22핀을 잇는 본 리본이에요. 오늘 페이지 기준 개당 488원, 해외재고 155개, 평균 발송 10/21, 최소 5개예요. 이 화면은 커넥터 입이 뚜껑 구멍 반대쪽을 봐서, 300 mm는 여유가 3~9 mm로 모자라요. | 5 | 488원 | 2,440원 | 엘레파츠 (해외재고, 평균 발송 10/21, 기존 엘레파츠 주문에 합치면 배송비 0원) (https://www.eleparts.co.kr/goods/view?no=18579661) eleparts.co.kr | 확인
GUOCONN 0.5*22P*400*A FFC 22핀 0.5 mm 400 mm 같은 면(A형, Same Side) 보험용이에요. 경로의 45° 접힘 때문에 필요한 접점 면이 Waveshare 그림과 다를 수 있어요. 빼면 2,465원 줄어요. | 5 | 493원 | 2,465원 | 엘레파츠 (해외재고, 평균 발송 10/21, 기존 엘레파츠 주문에 합치면 배송비 0원) (https://www.eleparts.co.kr/goods/view?no=18622270) eleparts.co.kr | 확인
[엘레파츠] 실리콘 점퍼 케이블 26AWG-RED (20cm, F/F) 화면 5 V 연장 1단이에요. GPIO 2번에 꽂아요. | 1 | 451원 | 451원 | 엘레파츠 (24시간 안 발송) (https://www.eleparts.co.kr/goods/view?no=9461190) eleparts.co.kr | 확인
[엘레파츠] 실리콘 점퍼 케이블 26AWG-BLACK (20cm, F/F) GND 연장 1단이에요. GPIO 6번에 꽂아요. | 1 | 451원 | 451원 | 엘레파츠 (24시간 안 발송) (https://www.eleparts.co.kr/goods/view?no=9461199) eleparts.co.kr | 확인
[엘레파츠] 실리콘 점퍼 케이블 26AWG-RED (20cm, M/M) 5 V 연장 2단이에요. 동봉 전원선의 암 소켓에 꽂아요. | 1 | 451원 | 451원 | 엘레파츠 (24시간 안 발송) (https://www.eleparts.co.kr/goods/view?no=9756990) eleparts.co.kr | 확인
[엘레파츠] 실리콘 점퍼 케이블 26AWG-BLACK (20cm, M/M) GND 연장 2단이에요. | 1 | 451원 | 451원 | 엘레파츠 (24시간 안 발송) (https://www.eleparts.co.kr/goods/view?no=9756998) eleparts.co.kr | 확인
스텐 유두 렌치볼트 M3 × 20 mm 경첩 축 2개, 다리 축 1개, 예비 1개예요. 모든 조합에 똑같이 들어가요. 값은 예전 추정값이에요. | 4 | 100원 | 400원 | 11번가 굿나잇몰 (기존 볼트 주문에 옵션 추가) (https://www.11st.co.kr/products/4236198413) 11st.co.kr | 미확인
스텐 유두 렌치볼트 M3 × 10 mm (기존 L56 줄 수량 +4) CU 뚜껑 앞 모서리 고정 2개와 예비 2개예요. 모든 조합에 똑같이 들어가요. | 4 | 60원 | 240원 | 11번가 굿나잇몰 (기존 L56 줄) (https://www.11st.co.kr/products/4236198413) 11st.co.kr | 미확인
배송비 | | | 0원 | 11번가 해외직구 무료배송 + 엘레파츠 줄은 기존 엘레파츠 주문에 합침(따로 사면 +3,000원) + 11번가 나사는 기존 주문에 합침
합계 | | | 108,449원 | 지금 안(103,600원) 대비 +4,849원

화면 101,100 + 400 mm 리본 B형 2,440 + A형 보험 2,465 + 점퍼 1,804 + 공통 나사 640 = 108,449원이에요. A형을 빼면 105,984원이에요. 조건부 가격 100,090원이 적용되면 1,010원 더 싸요. 엘레파츠 줄은 기존 주문에 합친다고 보고 배송비를 0원으로 넣었어요. 따로 주문하면 3,000원이 더 들어요. 다른 가게도 있어요. 쿠팡 다빈은 107,400원이에요(합계 114,749원, 10/16 도착 표시). 11번가에는 g13trading 108,200원(해외배송)과 테크성원 120,200원이 있어요. 알리 목록가는 67,572원이에요(합계 약 74,921원, 오늘 못 봄). Waveshare 직판은 49.99달러 ≈ 67,671원에 DHL 운임이 더해져요(운임 미확인).

##### 받는 시기

화면은 11번가에 '중국에서 10/1 발송'으로 나와요. 해외직배송은 영업일로 5~15일이라 10/12~10/26에 올 것으로 봐요(추정, 한국 휴일 10/3·10/5·10/9 제외). 쿠팡 판매분은 10/16 도착으로 나와요. 리본은 10/22~10/23에 와요. 책상 위 시험은 동봉 200 mm 리본으로 바로 할 수 있어요.

##### Pi 5 설정

config.txt에 한 줄을 넣어요: dtoverlay=vc4-kms-dsi-waveshare-panel-v2,7_0_inch_a,swapxy,invx. swapxy와 invx는 터치 좌표를 커널에서 90° 돌리는 옵션이에요. 방향이 거꾸로면 invx 대신 invy를 써요. 이 오버레이는 지금 Pi OS(커널 6.18.50)에 들어 있어요. 화면은 KMS에서 720×1280 세로로 잡혀요. KMSDRM은 데스크톱 없이 화면에 바로 그리는 방식인데, SDL2의 KMSDRM에는 화면 회전 기능이 없어요(SDL2 소스로 확인). 그래서 게임이 1280×720으로 그린 뒤 매 프레임 90° 돌려서 보내야 해요. cmdline.txt의 rotate=는 글자 콘솔만 돌려요. 전원은 GPIO 2번과 6번이고, 밝기는 /sys/class/backlight에 0~255를 써요.

##### 전력

화면이 더 쓰는 전력 | 약 2.5 W (GPIO 2·6번)
평균 | 16.1~20.1 W
순간 최대 | 54.8 W (60 W까지 5.2 W 남음)
배터리 | 약 3.1~3.9시간
45 W 충전기 −2 dB | 39.8 W

화면은 약 2.5 W를 써요(위키 기준 5 V 0.5 A 이상 필요). GPIO에서 전원을 받아요. 평균 16.1~20.1 W, 순간 최대 54.8 W로 5.2 W가 남아요. 배터리는 약 3.1~3.9시간이에요. 5.1 V 선은 2.49 A, Pi 입력은 2.09 A예요. 모두 지금 TD2 안과 같아요.

#### 장착 (축척 스케치)

위에서 본 접은 상태. 파란 선 = 받침, 회색 = 화면 유리, 진한 회색 = 보이는 화면, 주황 = DSI 리본, 보라 = HDMI, 초록 = USB, 빨강 = 전원선, 점선 네모 = 뚜껑 아래 Pi 5. 선과 단자는 화면 뒤에 있어요. DSI 리본 단자 x671.0·u53 (180° 돌려 달기, 추정).

옆에서 본 모습(y·z, mm). 실선 = 25°로 세운 상태, 점선 = 뒤로 접은 상태. 경첩 축·뚜껑·다리 주머니는 모든 조합에서 같아요.

받침 x559.04~752.96 (폭 193.9), 뚜껑 여유 왼쪽 2.54 · 오른쪽 2.54 mm. 접은 상태 y296.5~421.7, 받침 두께 17.00.

겉치수와 러그가 TD2와 같아서 rev 2 받침 외곽을 그대로 써요(폭 193.92, 뚜껑 여유 양쪽 2.54). 접은 높이는 z113, 22°에서 가장 앞은 y276.7, 접은 뒤끝은 y421.7이에요. 다만 커넥터 입이 T자 홈 쪽을 봐요. 도면과 Waveshare 연결 사진으로 판단한 추정이에요. 도면 방향 그대로 달면 입이 +x(뚜껑 구멍 반대)를 봐서 리본이 받침 안에서 되돌아와야 해요. 그래서 화면을 180° 돌려 달기를 권해요. 그러면 커넥터가 x≈671, u≈53에 오고 입이 −x를 봐서 리본이 홈까지 곧게 가요. 이때 경로가 약 297 mm라 300 mm 리본은 3 mm밖에 남지 않아요. 400 mm 리본을 쓰면 약 100 mm가 남는데, 뚜껑 밑 리본 클립 옆에 납작하게 접어 둬요. 뚜껑 선 구멍(22×6)은 그대로예요. 다리 힘 39.6 N(안전율 10.0), 넘어짐 안전율 2.4예요.

설계 변경: rev 2 받침의 외곽, 러그 구멍, 경첩 귀, 다리 걸이는 그대로 써요. ㄴ자 점검창은 180° 돌려 단 커넥터 자리(대략 x660~680, u44~78, 전원 소켓 포함)로 옮기거나 넓혀요. 리본 접힘 자리(x597~613)에서 커넥터까지 +x로 가는 길(u 약 53)도 비워 둬요. TD2용 Ø7 스탠드오프 피함 구멍은 없어도 돼요. 러그 면이 9.3으로 TD2(9.4)와 0.1 mm 차이지만 무시해도 돼요. CU 뚜껑 v2는 그대로예요.

#### 게임 영향

9.6 mm 2옥타브 흰 레인0.94 : 1 1옥타브 화면 : 실제 건반 0.92 MP 매 프레임 그릴 픽셀세로 매 프레임 90° 회전 필요

2옥타브 화면의 흰 레인은 9.6 mm(80 px), 검은 레인은 5.8 mm예요. 1옥타브 화면은 0.94:1이에요. 픽셀은 0.92 MP로 TD2와 같아요. 세로 화면이라 매 프레임 1280×720 그림을 90° 돌려 한 번 더 복사해야 해요. 그래서 60 fps 여유가 B1(7-DSI-TOUCH-C)보다 적어요(지금 TD2 안과 같은 조건). pygame의 GPU 회전(pygame._sdl2)은 아직 시험하지 않았어요. 터치 회전은 커널 옵션이라 앱 코드가 필요 없어요.

##### 장점

- 광학 본딩, 10점 터치, 450 cd/m²로 7인치 중 화질이 좋아요.
- 겉치수와 러그가 TD2와 같아서 받침 외곽을 그대로 써요.
- config.txt 한 줄로 켜지고, 터치 회전도 같은 줄의 옵션으로 해결돼요.
- 국내 판매 값이 지금 TD2 묶음과 거의 같아서(+4,849원) 값 부담이 작아요.

##### 단점

- 세로 화면이라 앱이 매 프레임 그림을 돌려야 해요. TD2와 같은 문제가 그대로 남아요.
- 300 mm 리본으로는 모자라서 400 mm가 필요해요.
- 점검창 위치를 옮겨야 해요.
- 해외 구매대행이라 반품과 수리가 어려워요.

##### 위험

- 커넥터 입 방향은 도면과 사진으로 판단한 추정이에요. 받으면 먼저 확인하고 받침을 뽑아요.
- 11번가 판매자 평가가 거의 없고, 알리 글을 옮긴 구매대행이에요.
- 도착 예상이 10/12~10/26로 넓게 퍼져 있어요(추정).
- 400 mm DSI 리본은 Pi 공식 500 mm 리본도 팔리는 만큼 괜찮다고 보지만, 실제 화면으로 시험해야 해요.
- Waveshare 드라이버에 '오래 꺼 둔 뒤 켜면 가끔 화면이 안 켜진다'는 보고가 있어요(패치 미반영). 받으면 전원을 뺐다 켜는 시험을 10번 해요.

#### 확인한 것 / 미확인

오늘 다시 연 것: 11번가 9609527225(101,100원, 조건부 100,090원, 중국 10/1 발송 표시), 쿠팡 9165577833(107,400원, 10/16 도착 표시), 11번가 g13trading·테크성원, 엘레파츠 400 mm 리본 B형 488원·A형 493원(재고, 평균 발송 10/21, Reverse/Same Side 표기), Waveshare 직판 49.99달러. rpi-6.18.y 오버레이의 7_0_inch_a와 swapxy·invx·invy 옵션, 드라이버 720×1280 61.2 Hz도 확인했고, SDL2 KMSDRM 소스에 회전 코드가 없다는 것도 확인했어요. 확인 못 한 것: 알리 가격, DHL 운임, 도착일, 커넥터 입 방향과 좌표(도면·사진 추정), M3 나사값.

- 공통 나사 M3×20 4개와 M3×10 4개(640원)는 모든 조합에서 추정값이에요.

맨 위 표로 ↑

C3C · 싸게·크게

### Waveshare 7EP-CAPLCD 7인치 1280×800 광학 본딩 HDMI (해외 직구)

게임에 유리(가로)

108,762원

지금 안 대비 +5,162원

10/12~10/25 · 해외, 추정

Waveshare 7EP-CAPLCD (7인치 넓은 색역 정전식 터치, HDMI) 제품 사진

제품 사진 (누르면 크게)

화면

Waveshare 7EP-CAPLCD (7인치 넓은 색역 정전식 터치, HDMI)

크기·해상도

7인치 · 1280×800

방향

가로(landscape) 기본, 회전 필요 없음

연결

HDMI(표준) + HDMI FFC 20핀 헤더 + USB-C(터치) + USB-C(전원) + PH1.25 4핀(터치) + PH2.0 3핀(전원) + 3.5 mm + 버튼 보드 헤더

패널

IPS, 광학 본딩 강화유리 6H, 350 cd/m², 명암비 800:1, 색역 NTSC 68%

터치

정전식 10점, USB HID(드라이버 불필요, Waveshare)

외곽 (mm)

유리 170.18 × 104.20 (R4.5), 기판 161.00 × 99.50, 두께 8.30 + M2.5 받침 4.0

보이는 영역 (mm)

150.72 × 94.20

Waveshare 7EP-CAPLCD 치수 도면

Waveshare 7EP-CAPLCD 치수 (누르면 크게)

#### 살 것

품목 | 수량 | 단가 | 금액 | 판매처 | 확인
Waveshare 7EP-CAPLCD (알리익스프레스 Waveshare 공식 스토어) 오늘 검색 목록에서 104,800원을 봤지만 상품 페이지는 로봇 확인이 떠서 열지 못했어요. 배송비·도착일 미확인. Waveshare 직판은 오늘 $78.99(약 106,857원) + 배송비(결제 단계에서만 나옴, 미확인) | 1 | 104,800원 | 104,800원 | 알리익스프레스 (검색 목록가, 25개 판매) (https://ko.aliexpress.com/item/1005008057666559.html) aliexpress.com | 미확인
[Waveshare] DIY HDMI 케이블 0.5 m FFC (20핀 0.5 피치, 반대면) 동봉 FFC 2개의 길이를 몰라서 삽니다. 경로 약 274 mm. 동봉 'Micro HDMI Adapter'와 같은 Waveshare 규격 | 1 | 1,518원 | 1,518원 | 엘레파츠 (24시간 발송) (https://www.eleparts.co.kr/goods/view?no=6135661) eleparts.co.kr | 확인
[엘레파츠] 실리콘 점퍼 26AWG 20cm F/F 빨강·검정, M/M 빨강·검정 동봉 PH2.0 3핀 전원선을 GPIO 4번(5 V)·6번(GND)까지 늘려요. F/F 검정 9461199, M/M 빨강 9756990, M/M 검정 9756998도 오늘 451원 확인 | 4 | 451원 | 1,804원 | 엘레파츠 (24시간 발송) (https://www.eleparts.co.kr/goods/view?no=9461190) eleparts.co.kr | 확인
스텐 유두 렌치볼트 M3 × 20 mm 모든 조합 공통, 값 추정 | 4 | 100원 | 400원 | 11번가 굿나잇몰 (https://www.11st.co.kr/products/4236198413) 11st.co.kr | 미확인
스텐 유두 렌치볼트 M3 × 10 mm (+4) 모든 조합 공통, 값 추정 | 4 | 60원 | 240원 | 11번가 굿나잇몰 (https://www.11st.co.kr/products/4236198413) 11st.co.kr | 미확인
배송비 | | | 0원 | 알리 배송비 미확인(0원으로 둠) + 엘레파츠 줄은 기존 엘레파츠 주문에 합침(따로 사면 +3,000원) + 11번가 나사는 기존 주문에 합침
합계 | | | 108,762원 | 지금 안(103,600원) 대비 +5,162원

알리 목록가 기준 104,800 + FFC 1,518 + 점퍼 1,804 + 공통 640 = 108,762원(알리 배송비 미확인이라 0으로 둠). Waveshare 직판이면 106,857원 + 배송비(미확인)라 12~14만 원대로 봐요. 국내 판매처는 찾지 못했어요(쿠팡, 다나와 가격비교, 엘레파츠, 메카솔루션, 11번가 검색 0건, 디바이스마트는 접속 불가). 동봉 PH1.25→USB-A 터치선이 짧으면 USB 연장선(약 1~2천 원)이 더 필요해요.

##### 받는 시기

Waveshare 창고가 10/1~10/4 출고를 멈추고 10/5부터 보내요. 알리 일반 배송이면 10/15~10/25, 직판 DHL이면 10/12~10/19쯤으로 추정해요(미확인).

##### Pi 5 설정

EDID로 1280×800이 잡히면 설정이 없어요. Waveshare 위키는 옛 방식 hdmi_cvt 줄만 알려 주는데 Bookworm부터 무시되므로, 안 잡히면 cmdline.txt에 video=HDMI-A-1:1280x800M@60을 넣어요. Pi 5에서 직접 확인한 자료는 없어요. 연결: Pi HDMI0 → 동봉 'Micro HDMI Adapter' → 0.5 m FFC → 화면 HDMI FFC 헤더. 터치: 동봉 PH1.25 4핀→USB-A 선을 Pi 빈 USB-A에 꽂아요(PH1.25 쪽을 뚜껑 구멍 아래에서 위로 넣어요). 전원: 동봉 PH2.0 3핀 선 + 점퍼 2단으로 GPIO 4번(5 V)·6번(GND)에 꽂아요(0.6 A, Pi에서 나가는 방향이라 D16 허용). 밝기: 버튼 보드(OSD)나 DDC/CI로 바꿔요. Waveshare 위키 방법은 sudo apt install ddcutil 후 ddcutil setvcp 10 <0~100>이에요(Pi 5 KMS에서 되는지는 미확인). config.txt는 dtoverlay=vc4-kms-v3d,noaudio를 권해요. 가로라 회전은 없어요.

##### 전력

화면이 더 쓰는 전력 | 약 3 W (GPIO 4·6번 (터치는 USB))
평균 | 16.6~20.6 W
순간 최대 | 55.3 W (60 W까지 4.7 W 남음)
배터리 | 약 3.0~3.8시간
45 W 충전기 −2 dB | 40.3 W

화면 3 W(위키: 5 V 600 mA). GPIO에서 받아요. 평균 16.6~20.6 W, 최대 55.3 W(여유 4.7 W), 45 W −2 dB 40.3 W, 배터리 3.05~3.78시간, Pi 입력 2.19 A, 5.1 V 레일 2.59 A, Pi USB 0.3/1.6 A(터치만).

#### 장착 (축척 스케치)

위에서 본 접은 상태. 파란 선 = 받침, 회색 = 화면 유리, 진한 회색 = 보이는 화면, 주황 = DSI 리본, 보라 = HDMI, 초록 = USB, 빨강 = 전원선, 점선 네모 = 뚜껑 아래 Pi 5. 선과 단자는 화면 뒤에 있어요. HDMI 단자 x578.9·u70 / USB 단자 x626.0·u8 (터치 PH1.25) / 전원 단자 x646.0·u8 (추정).

옆에서 본 모습(y·z, mm). 실선 = 25°로 세운 상태, 점선 = 뒤로 접은 상태. 경첩 축·뚜껑·다리 주머니는 모든 조합에서 같아요.

받침 x568.61~743.39 (폭 174.8), 뚜껑 여유 왼쪽 12.11 · 오른쪽 12.11 mm. 접은 상태 y296.5~405.7, 받침 두께 19.90.

들어가요. 받침 x568.61~743.39(폭 174.78), 뚜껑 여유 양쪽 12.1 mm. 기판의 M2.5 받침 4개(153×91.5)로 뒤판에 고정해요. 두께 8.3 + 받침 4.0 = 12.3 mm라 받침 두께 D_c 19.9, 접은 높이 z115.9(통과), 22°에서 가장 앞 y274.0(통과), 접은 뒤끝 y405.7. FFC 헤더와 PH 선을 쓰면 옆으로 나오는 플러그가 없어요. HDMI FFC 경로 약 274 mm라 50 cm면 넉넉하고 30 cm는 짧아요. 터치선은 약 306 mm가 필요해요(동봉 선 길이 미확인). 뚜껑 구멍 22×6 그대로(FFC 한 장 + PH1.25 하우징 + 전원선 2가닥을 하나씩 통과). 다리 힘 38 N(안전율 10.4), 뒤꿈치 155 N, 뚜껑 나사 75 N, 넘어짐 안전율 2.5.

설계 변경: 뚜껑 v2는 그대로예요. 받침을 새로 그려요: M2.5 받침 4개 자리(153×91.5), 왼쪽 끝 HDMI FFC 헤더 창, 아래 가장자리 PH1.25·PH2.0 창, 버튼 보드 헤더 창. 받침 두께가 D_c 19.9로 늘어 다리 걸이 위치를 다시 맞춰요. 유리 크기가 7inch DSI LCD (E)와 같아서(170.18×104.2) C4b 받침과 바깥 모양을 같이 쓸 수 있어요.

#### 게임 영향

9.4 mm 2옥타브 흰 레인0.92 : 1 1옥타브 화면 : 실제 건반 1.02 MP 매 프레임 그릴 픽셀가로 회전 없음

1280×800 가로, 광학 본딩에 색역 NTSC 68%라 HDMI 후보 가운데 화질이 가장 좋아요. 보이는 폭 150.7 mm라 2옥타브 흰 레인 9.4 mm(80 px), 1옥타브 0.92:1이에요. 픽셀 1.02 MP로 60 fps 예산 안이에요. HDMI 지연 약 1프레임은 보정으로 지워요.

##### 장점

- HDMI 후보 중 화질이 가장 좋아요(본딩, 350 cd/m², 넓은 색역, 10점 터치).
- FFC 헤더와 PH 선을 써서 옆으로 튀어나오는 플러그가 없어요.
- 필요한 선 대부분이 상자에 들어 있어요.
- DDC/CI로 밝기를 소프트웨어로 바꿀 가능성이 있어요.

##### 단점

- 국내 판매처가 없어요.
- rev 2보다 5,162원 이상 비싸고, 직판이면 더 비싸요.
- 10월 중하순 도착이라 받침 모델링 마감 전에 실물을 못 재요.
- 선이 세 갈래(FFC, 터치선, 전원선)라 배선이 가장 많아요.

##### 위험

- 알리 값·배송비·도착일을 상품 페이지에서 확인하지 못했어요(로봇 확인).
- 동봉 FFC와 터치선 길이를 몰라요.
- Pi 5 KMS에서 EDID와 DDC/CI 밝기 조절이 되는지 확인한 자료가 없어요.
- 국경절 때문에 출고가 늦어요.

#### 확인한 것 / 미확인

오늘 Waveshare 판매 페이지에서 $78.99와 구성품(HDMI 납작 선 1 m, USB-A→C 1 m, Micro HDMI·HDMI 어댑터, FFC 20핀 2개, PH1.25→USB-A 선, 3핀 선, 버튼 보드)을 확인했고, 위키에서 3 W·600 mA, 350 cd/m², DDC/CI 밝기, 옛 방식 설정 줄을 확인했어요. 알리 검색 목록가 104,800원은 봤지만 상품 페이지는 로봇 확인으로 열지 못했어요. 국내 판매처 검색은 모두 0건이었어요. Waveshare 배송비는 장바구니·결제 단계에서만 계산되어 확인하지 않았어요.

- Waveshare 7EP-CAPLCD (알리익스프레스 Waveshare 공식 스토어) (104,800원): 오늘 검색 목록에서 104,800원을 봤지만 상품 페이지는 로봇 확인이 떠서 열지 못했어요. 배송비·도착일 미확인. Waveshare 직판은 오늘 $78.99(약 106,857원) + 배송비(결제 단계에서만 나옴, 미확인)
- 공통 나사 M3×20 4개와 M3×10 4개(640원)는 모든 조합에서 추정값이에요.

맨 위 표로 ↑

B3B · DSI 호환·해외

### Waveshare 7inch DSI LCD (H) (7인치 1280×720 가로, TD2와 같은 외곽) + 22핀 400 mm 리본

화질 가장 좋음게임에 유리(가로)

120,649원

지금 안 대비 +17,049원

10/15~10/22 · 해외, 추정

Waveshare 7inch DSI LCD (H) (7인치 DSI 정전식 터치, 광학 본딩) 제품 사진

제품 사진 (누르면 크게)

화면

Waveshare 7inch DSI LCD (H) (7인치 DSI 정전식 터치, 광학 본딩)

크기·해상도

7인치 · 1280×720, 62.1 Hz (커널 드라이버 타이밍으로 계산)

방향

처음부터 가로(landscape)예요. 다는 방향에 따라 앱이 그림을 180° 뒤집어야 할 수 있어요(받은 뒤 확인).

연결

MIPI DSI 22핀 0.5 mm (Pi 5 CAM/DISP 1) + MX1.25 2핀 5 V 전원(GPIO에서)

패널

IPS, 광학 본딩 강화유리(6H), 지문 방지 코팅, 450 cd/m², 시야각 170°, 금속 뒷판

터치

정전식 10점, Goodix GT911(I2C), 커널 기본 드라이버예요. 오버레이가 터치 축을 가로에 맞게 이미 돌려 줘요.

외곽 (mm)

189.32 × 120.24 × 9.3 (러그 면까지. Pi 스탠드오프를 달면 14.8). M2.5 러그 4개가 140 × 70.71로 TD2와 같은 자리예요. 7-DSI-TOUCH-A와 같은 판이에요.

보이는 영역 (mm)

155.00 × 88.00

Waveshare 7inch DSI LCD (H) 치수 도면

Waveshare 7inch DSI LCD (H) 치수 (누르면 크게)

#### 살 것

품목 | 수량 | 단가 | 금액 | 판매처 | 확인
Waveshare 7inch DSI LCD (H) 7인치 1280×720 IPS 광학 본딩 10점 터치 (Standard Ver.) 오늘 페이지 값은 판매가 113,300원이고, 에브리직구 8% 쿠폰(−9,060원)을 받으면 104,240원이에요. 옵션은 추가금 없는 '02 Standard Ver.'를 골라요. 도착일 표시는 없어요. 동봉품: 22핀 200 mm 반대면 리본 2개, 전원선. | 1 | 113,300원 | 113,300원 | G마켓 해외직구 (판매자 이룸종합몰2, CJ 무료배송, 150달러 이하라 관부가세 없음) (https://item.gmarket.co.kr/Item?goodscode=4787571376) gmarket.co.kr | 확인
GUOCONN 0.5*22P*400*B FFC 22핀 0.5 mm 400 mm 반대면(B형, Reverse) Pi 5와 화면 22핀을 잇는 본 리본이에요. 이 화면은 커넥터 입이 뚜껑 구멍 반대쪽을 봐서, 어느 방향으로 달아도 300 mm는 모자라요. | 5 | 488원 | 2,440원 | 엘레파츠 (해외재고, 평균 발송 10/21, 기존 엘레파츠 주문에 합치면 배송비 0원) (https://www.eleparts.co.kr/goods/view?no=18579661) eleparts.co.kr | 확인
GUOCONN 0.5*22P*400*A FFC 22핀 0.5 mm 400 mm 같은 면(A형, Same Side) 보험용이에요. 접점 면이 반대일 때 써요. 빼면 2,465원 줄어요. | 5 | 493원 | 2,465원 | 엘레파츠 (해외재고, 평균 발송 10/21, 기존 엘레파츠 주문에 합치면 배송비 0원) (https://www.eleparts.co.kr/goods/view?no=18622270) eleparts.co.kr | 확인
[엘레파츠] 실리콘 점퍼 케이블 26AWG-RED (20cm, F/F) 화면 5 V 연장 1단이에요. GPIO 2번에 꽂아요. | 1 | 451원 | 451원 | 엘레파츠 (24시간 안 발송) (https://www.eleparts.co.kr/goods/view?no=9461190) eleparts.co.kr | 확인
[엘레파츠] 실리콘 점퍼 케이블 26AWG-BLACK (20cm, F/F) GND 연장 1단이에요. GPIO 6번에 꽂아요. | 1 | 451원 | 451원 | 엘레파츠 (24시간 안 발송) (https://www.eleparts.co.kr/goods/view?no=9461199) eleparts.co.kr | 확인
[엘레파츠] 실리콘 점퍼 케이블 26AWG-RED (20cm, M/M) 5 V 연장 2단이에요. | 1 | 451원 | 451원 | 엘레파츠 (24시간 안 발송) (https://www.eleparts.co.kr/goods/view?no=9756990) eleparts.co.kr | 확인
[엘레파츠] 실리콘 점퍼 케이블 26AWG-BLACK (20cm, M/M) GND 연장 2단이에요. | 1 | 451원 | 451원 | 엘레파츠 (24시간 안 발송) (https://www.eleparts.co.kr/goods/view?no=9756998) eleparts.co.kr | 확인
스텐 유두 렌치볼트 M3 × 20 mm 모든 조합에 똑같이 들어가요(경첩 2, 다리 1, 예비 1). 값은 예전 추정값이에요. | 4 | 100원 | 400원 | 11번가 굿나잇몰 (기존 볼트 주문에 옵션 추가) (https://www.11st.co.kr/products/4236198413) 11st.co.kr | 미확인
스텐 유두 렌치볼트 M3 × 10 mm (기존 L56 줄 수량 +4) 모든 조합에 똑같이 들어가요(CU 뚜껑 앞 모서리 2, 예비 2). | 4 | 60원 | 240원 | 11번가 굿나잇몰 (기존 L56 줄) (https://www.11st.co.kr/products/4236198413) 11st.co.kr | 미확인
배송비 | | | 0원 | G마켓 해외직구 무료배송(CJ) + 엘레파츠 줄은 기존 엘레파츠 주문에 합침(따로 사면 +3,000원) + 11번가 나사는 기존 주문에 합침
합계 | | | 120,649원 | 지금 안(103,600원) 대비 +17,049원

화면 113,300 + 400 mm 리본 B형 2,440 + A형 보험 2,465 + 점퍼 1,804 + 공통 나사 640 = 120,649원이에요. 쿠폰가 104,240원을 쓰면 111,589원(+7,989원)이고, A형까지 빼면 109,124원이에요. 엘레파츠 줄은 기존 주문에 합친다고 봤어요. 따로 주문하면 3,000원이 더 들어요. 다른 가게도 있어요. 알리 목록가는 98,000원이에요(합계 약 105,349원, 오늘 못 봄). Waveshare 직판은 58.99달러 ≈ 79,854원에 DHL 운임이 더해져요(운임 미확인). DHL이 약 1.5만 원보다 싸면 이 조합에서는 직판이 가장 싸요. 11번가 이룸상사46은 180,900원이에요. 쿠팡에서는 이 모델을 찾지 못했어요.

##### 받는 시기

화면은 해외 구매대행이라 중국 국경절 뒤에 발송돼요. 약 10/15~10/22에 올 것으로 봐요(추정, 페이지에 날짜 없음). Waveshare 직판이면 10/5 이후 출고, DHL 3~8 영업일이라 약 10/12~10/20이에요(추정). 리본은 10/22~10/23에 와요.

##### Pi 5 설정

config.txt에 한 줄을 넣어요: dtoverlay=vc4-kms-dsi-waveshare-panel,7_0_inchH. v2가 아닌 예전 오버레이예요. 0번 포트를 쓰면 끝에 ,dsi0을 붙여요. 지금 Pi OS(커널 6.18.50)에 들어 있어요. 가로 1280×720으로 잡혀서 회전이 필요 없어요. 화면을 도면 기준 180° 돌려 달아야 하면, 앱이 그림을 뒤집어요(매 프레임 복사 1번). 이때 터치는 같은 줄에 invx=0,invy 같은 옵션을 붙여 맞춰요(시험 필요). 오버레이의 rotation 옵션은 SDL2 KMSDRM이 무시해요. 밝기는 /sys/class/backlight에 0~255를 써요(이 드라이버에도 밝기 장치가 있어요). 전원은 GPIO 2번과 6번이에요.

##### 전력

화면이 더 쓰는 전력 | 약 2.5 W (GPIO 2·6번)
평균 | 16.1~20.1 W
순간 최대 | 54.8 W (60 W까지 5.2 W 남음)
배터리 | 약 3.1~3.9시간
45 W 충전기 −2 dB | 39.8 W

화면은 약 2.5 W를 써요(위키 기준 5 V 0.5 A 이상 필요). 평균 16.1~20.1 W, 순간 최대 54.8 W로 5.2 W가 남아요. 배터리는 약 3.1~3.9시간이에요. 5.1 V 선은 2.49 A, Pi 입력은 2.09 A예요. 모두 지금 TD2 안과 같아요.

#### 장착 (축척 스케치)

위에서 본 접은 상태. 파란 선 = 받침, 회색 = 화면 유리, 진한 회색 = 보이는 화면, 주황 = DSI 리본, 보라 = HDMI, 초록 = USB, 빨강 = 전원선, 점선 네모 = 뚜껑 아래 Pi 5. 선과 단자는 화면 뒤에 있어요. DSI 리본 단자 x671.0·u53 (180° 돌려 달기, 추정).

옆에서 본 모습(y·z, mm). 실선 = 25°로 세운 상태, 점선 = 뒤로 접은 상태. 경첩 축·뚜껑·다리 주머니는 모든 조합에서 같아요.

받침 x559.04~752.96 (폭 193.9), 뚜껑 여유 왼쪽 2.54 · 오른쪽 2.54 mm. 접은 상태 y296.5~421.7, 받침 두께 17.00.

겉치수와 러그가 TD2와 같아서 rev 2 받침 외곽을 그대로 써요. 접은 높이는 z113, 22°에서 가장 앞은 y276.7, 접은 뒤끝은 y421.7이에요. 커넥터는 7-DSI-TOUCH-A와 같은 자리이고, 입이 T자 홈 쪽을 봐요(추정). 그림이 똑바로 나오는 방향으로 달았을 때 입이 +x를 보면, 리본이 받침 안에서 되돌아와야 해서 경로가 약 330 mm가 돼요. 180° 돌려 달면 약 297 mm예요. 어느 쪽이든 300 mm는 모자라고 400 mm면 돼요. 뚜껑 선 구멍(22×6)은 그대로예요.

설계 변경: rev 2 받침의 외곽, 러그 구멍, 경첩 귀, 다리 걸이는 그대로예요. 점검창은 다는 방향에 따라 둘 중 하나로 정해요. 도면 방향이면 rev 2 창(x596~666, u46~74)을 그대로 두고 리본이 되돌아올 자리를 더해요. 180° 방향이면 창을 x660~680 쪽으로 옮겨요. 어느 쪽이 위인지는 받은 뒤에 봐야 해서, 받침 출력은 실물 확인 뒤로 미뤄요. CU 뚜껑 v2는 그대로예요.

#### 게임 영향

9.6 mm 2옥타브 흰 레인0.94 : 1 1옥타브 화면 : 실제 건반 0.92 MP 매 프레임 그릴 픽셀가로 회전 없음 (달기에 따라 180° 뒤집기)

2옥타브 화면의 흰 레인은 9.6 mm(80 px), 검은 레인은 5.8 mm예요. 1옥타브 화면은 0.94:1이에요. 픽셀은 0.92 MP로 TD2와 같지만, 가로 화면이라 90° 회전 복사가 없어서 TD2보다 여유가 있어요. 다만 180° 뒤집어 달아야 하면 매 프레임 뒤집기 복사가 한 번 생겨요. 16:9 그림이 1280×720에 꼭 맞아요.

##### 장점

- 7인치 중 가장 밝은 본딩 화면이고(광학 본딩, 10점, 450 cd/m², B2와 같은 패널), 처음부터 가로 화면이에요.
- 겉치수와 러그가 TD2와 같아서 받침 외곽을 그대로 써요.
- config.txt 한 줄과 커널 기본 드라이버로 터치와 밝기까지 돼요.

##### 단점

- 확인된 값이 지금 TD2 묶음보다 비싸요(+17,049원, 쿠폰을 쓰면 +7,989원).
- 300 mm 리본으로는 모자라서 400 mm가 필요해요.
- 위아래 방향에 따라 앱에서 뒤집거나 점검창 위치를 바꿔야 할 수 있어요.
- 해외 구매대행이라 반품과 수리가 어려워요.

##### 위험

- 예전(v1) 드라이버를 써요. '오래 꺼 둔 뒤 켜면 가끔 화면이 안 켜진다'는 보고가 주로 이 드라이버 쪽이고, 패치는 아직 반영되지 않았어요. 받으면 전원을 뺐다 켜는 시험을 10번 해요.
- 커넥터 입 방향과 그림의 위쪽 방향은 받은 뒤에야 확실해요.
- G마켓 판매자는 상품평이 0개이고 도착일 표시도 없어요.
- 알리와 Waveshare 직판 값은 오늘 확인하지 못했어요.

#### 확인한 것 / 미확인

오늘 다시 연 것: G마켓 4787571376(113,300원, 8% 쿠폰가 104,240원, 옵션, 무료배송), 11번가 이룸상사46 180,900원, 엘레파츠 400 mm 리본, Waveshare 직판 58.99달러와 출고 중지 공지. rpi-6.18.y의 v1 오버레이 7_0_inchH(터치 swapxy·invx 기본), 드라이버 1280×720 62.1 Hz와 밝기 장치, GitHub PR #7182(냉간 부팅 문제, 미반영)도 확인했어요. 확인 못 한 것: 알리 가격, DHL 운임, 도착일, 커넥터 입 방향과 그림의 위쪽 방향, M3 나사값. 쿠팡과 11번가에서 더 싼 판매처는 찾지 못했어요.

- 공통 나사 M3×20 4개와 M3×10 4개(640원)는 모든 조합에서 추정값이에요.

맨 위 표로 ↑

B4B · DSI 호환·해외

### Waveshare 8-DSI-TOUCH-A (8인치 800×1280) + 22핀 300 mm 리본

화질 가장 좋음

124,874원

지금 안 대비 +21,274원

10/15~10/22 · 해외, 추정 (10/2 표시)

Waveshare 8-DSI-TOUCH-A (8인치 DSI 정전식 터치, 광학 본딩) 제품 사진

제품 사진 (누르면 크게)

화면

Waveshare 8-DSI-TOUCH-A (8인치 DSI 정전식 터치, 광학 본딩)

크기·해상도

8인치 · 800×1280, 60.0 Hz (커널 드라이버 타이밍으로 계산, 2레인)

방향

처음부터 세로(portrait)예요. 가로로 쓰려면 앱이 매 프레임 90° 돌려야 해요. 터치는 오버레이 옵션으로 커널에서 돌려요.

연결

MIPI DSI 22핀 0.5 mm (Pi 5 CAM/DISP 1) + MX1.25 2핀 5 V 전원(GPIO에서)

패널

IPS, 광학 본딩 강화유리, 400 cd/m², 시야각 178°(판매 설명). 구동 회로가 FPC에 들어 있어 두께가 11.6 mm예요.

터치

정전식 10점, Goodix GT9271(I2C), 커널 기본 드라이버 → evdev 터치 장치

외곽 (mm)

194.00 × 119.00 × 11.6 (유리 1.1 포함, 뒤 보스까지). 모서리 R2. M2.5 구멍 8개(네 귀 170 × 105, Pi용 58 × 49). 포장 무게 약 0.47 kg

보이는 영역 (mm)

172.82 × 108.24

Waveshare 8-DSI-TOUCH-A 도면

Waveshare 8-DSI-TOUCH-A 도면 (누르면 크게)

#### 살 것

품목 | 수량 | 단가 | 금액 | 판매처 | 확인
Waveshare 8-DSI-TOUCH-A 8인치 DSI 정전식 터치 800×1280 IPS 광학 본딩 오늘 페이지 값은 118,500원이에요. 설명에 'Dropshipping 및 도매 지원' 같은 알리 문구가 그대로 있어서, 실제로는 해외에서 올 가능성이 커요. 설명의 11.6 mm, 800×1280, 10점이 이 모델과 맞아요. 동봉품: 22핀 약 200 mm 리본 2개, 전원선, 나사 봉지. | 1 | 118,500원 | 118,500원 | 11번가 (판매자 구대1등장사장15, 무료배송, 우체국택배 '10/2 도착' 표시) (https://www.11st.co.kr/products/9049646842) 11st.co.kr | 확인
GUOCONN 0.5*22P*300*B FFC 22핀 0.5 mm 300 mm 반대면(B형, Reverse) Pi 5와 화면 22핀을 잇는 본 리본이에요. 커넥터가 뚜껑 구멍 바로 위에 와서 경로가 약 231~269 mm라 300 mm로 충분해요(도면 추정). | 5 | 391원 | 1,955원 | 엘레파츠 (해외재고, 평균 발송 10/21, 기존 엘레파츠 주문에 합치면 배송비 0원) (https://www.eleparts.co.kr/goods/view?no=18622271) eleparts.co.kr | 확인
GUOCONN 0.5*22P*300*A FFC 22핀 0.5 mm 300 mm 같은 면(A형, Same Side) 보험용이에요. 접점 면이 반대일 때 써요. 빼면 1,975원 줄어요. | 5 | 395원 | 1,975원 | 엘레파츠 (해외재고, 평균 발송 10/21, 기존 엘레파츠 주문에 합치면 배송비 0원) (https://www.eleparts.co.kr/goods/view?no=18581287) eleparts.co.kr | 확인
[엘레파츠] 실리콘 점퍼 케이블 26AWG-RED (20cm, F/F) 화면 5 V 연장 1단이에요. GPIO 2번에 꽂아요. | 1 | 451원 | 451원 | 엘레파츠 (24시간 안 발송) (https://www.eleparts.co.kr/goods/view?no=9461190) eleparts.co.kr | 확인
[엘레파츠] 실리콘 점퍼 케이블 26AWG-BLACK (20cm, F/F) GND 연장 1단이에요. GPIO 6번에 꽂아요. | 1 | 451원 | 451원 | 엘레파츠 (24시간 안 발송) (https://www.eleparts.co.kr/goods/view?no=9461199) eleparts.co.kr | 확인
[엘레파츠] 실리콘 점퍼 케이블 26AWG-RED (20cm, M/M) 5 V 연장 2단이에요. | 1 | 451원 | 451원 | 엘레파츠 (24시간 안 발송) (https://www.eleparts.co.kr/goods/view?no=9756990) eleparts.co.kr | 확인
[엘레파츠] 실리콘 점퍼 케이블 26AWG-BLACK (20cm, M/M) GND 연장 2단이에요. | 1 | 451원 | 451원 | 엘레파츠 (24시간 안 발송) (https://www.eleparts.co.kr/goods/view?no=9756998) eleparts.co.kr | 확인
스텐 유두 렌치볼트 M3 × 20 mm 모든 조합에 똑같이 들어가요(경첩 2, 다리 1, 예비 1). 값은 예전 추정값이에요. | 4 | 100원 | 400원 | 11번가 굿나잇몰 (기존 볼트 주문에 옵션 추가) (https://www.11st.co.kr/products/4236198413) 11st.co.kr | 미확인
스텐 유두 렌치볼트 M3 × 10 mm (기존 L56 줄 수량 +4) 모든 조합에 똑같이 들어가요(CU 뚜껑 앞 모서리 2, 예비 2). | 4 | 60원 | 240원 | 11번가 굿나잇몰 (기존 L56 줄) (https://www.11st.co.kr/products/4236198413) 11st.co.kr | 미확인
배송비 | | | 0원 | 11번가 무료배송 + 엘레파츠 줄은 기존 엘레파츠 주문에 합침(따로 사면 +3,000원) + 11번가 나사는 기존 주문에 합침
합계 | | | 124,874원 | 지금 안(103,600원) 대비 +21,274원

화면 118,500 + 리본 B형 1,955 + A형 보험 1,975 + 점퍼 1,804 + 공통 나사 640 = 124,874원이에요. A형을 빼면 122,899원이에요. 엘레파츠 줄은 기존 주문에 합친다고 봤어요. 따로 주문하면 3,000원이 더 들어요. 다른 가게도 있어요. 11번가 트렌드픽_은 120,300원이에요(같은 설명). 알리 목록가는 82,969원이에요(합계 약 89,343원, 오늘 못 봄). Waveshare 직판은 54.99달러 ≈ 74,439원에 DHL 운임이 더해져요(운임 미확인). G마켓과 쿠팡에서는 이 모델을 찾지 못했어요. 8인치 800×480이나 옛 8inch DSI LCD (C)만 있었어요. 커넥터 방향이 반대로 판명되면 400 mm 리본(B형 2,440원)으로 바꿔요.

##### 받는 시기

11번가는 '10/2 도착'으로 표시하지만, 구매대행 글이라 믿기 어려워요. 해외에서 온다면 약 10/15~10/22로 봐요(추정). 리본은 10/22~10/23에 와요. 책상 위 시험은 동봉 리본으로 바로 할 수 있어요.

##### Pi 5 설정

config.txt에 한 줄을 넣어요: dtoverlay=vc4-kms-dsi-waveshare-panel-v2,8_0_inch_a,swapxy,invx. 2레인이 기본이에요. 4레인용 8_0_inch_a_4lane도 커널에 있지만 위키는 2레인을 써요. 이 오버레이는 지금 Pi OS(커널 6.18.50)에 들어 있어요. 화면은 800×1280 세로로 잡혀요. 그래서 게임이 1280×800(또는 1280×720)으로 그린 뒤 매 프레임 90° 돌려서 보내요. 터치 방향이 틀리면 invx 대신 invy를 써요. 전원은 GPIO 2번과 6번이고, 0.8 A 이상이 필요해요. 밝기는 /sys/class/backlight에 0~255를 써요.

##### 전력

화면이 더 쓰는 전력 | 약 4 W (GPIO 2·6번)
평균 | 17.7~21.7 W
순간 최대 | 56.4 W (60 W까지 3.6 W 남음)
배터리 | 약 2.9~3.5시간
45 W 충전기 −2 dB | 41.4 W

화면은 약 4.0 W를 써요(위키 기준 5 V 0.8 A 이상 필요). 평균 17.7~21.7 W, 순간 최대 56.4 W예요. 60 W까지 3.6 W가 남아서 3 W 기준은 통과해요. 배터리는 약 2.9~3.5시간으로 TD2보다 약 15~20분 짧아요. 5.1 V 선은 2.78 A, Pi 입력은 2.38 A로 3.0 A 한도 안이에요. 45 W 충전기 −2 dB 모드는 41.4 W로 통과해요. 점퍼 한 쌍으로 0.8 A를 보내면 약 0.15 V가 떨어져요(추정). 5 V 핀 2번과 4번을 둘 다 쓰면 줄어요.

#### 장착 (축척 스케치)

위에서 본 접은 상태. 파란 선 = 받침, 회색 = 화면 유리, 진한 회색 = 보이는 화면, 주황 = DSI 리본, 보라 = HDMI, 초록 = USB, 빨강 = 전원선, 점선 네모 = 뚜껑 아래 Pi 5. 선과 단자는 화면 뒤에 있어요. DSI 리본 단자 x602.6·u40 (추정).

옆에서 본 모습(y·z, mm). 실선 = 25°로 세운 상태, 점선 = 뒤로 접은 상태. 경첩 축·뚜껑·다리 주머니는 모든 조합에서 같아요.

받침 x557.10~754.90 (폭 197.8), 뚜껑 여유 왼쪽 0.60 · 오른쪽 0.60 mm. 접은 상태 y296.5~420.5, 받침 두께 19.20.

화면 폭이 194라 받침 테두리를 2.0에서 1.6 mm로 줄여야 197.8 mm(x557.1~754.9)로 CU 뚜껑에 들어가요. 양쪽 여유가 0.6 mm뿐이라 출력 오차에 민감해요. 접은 높이는 z115.2로 2.2 mm 높아지지만 z133 한도 안이에요. 22°에서 가장 앞은 y274.6이라 여물통을 통과하고, 접은 뒤끝은 y420.5예요. 커넥터 창이 짧은 변 한쪽 끝에 있어서, 그 끝을 −x로 두면 커넥터가 x≈605로 뚜껑 구멍 바로 위에 와요(도면에서 읽은 추정). 리본 경로는 돌리는 방향에 따라 약 231~269 mm라 300 mm 리본에 31 mm 이상 남아요. 뚜껑 선 구멍(22×6)은 그대로예요. 다리 힘은 약 43 N(안전율 9.2), 넘어짐 안전율은 2.2예요.

설계 변경: 받침을 새로 그려요. 외곽 197.8 × 124, 깊이 19.2(뒤판 w18.2), 테두리 1.6이에요. 네 귀 M2.5 구멍(170 × 105)으로 고정하고, 점검창은 −x 끝(대략 x590~625)에 둬요. 경첩 귀를 뒤판(w18.2)에 붙이면 축과의 관계가 같아서, CU 뚜껑 v2(경첩 받침, 다리 주머니, 접이 발, 구멍)는 그대로 써요. v13 받침 뒤 패드와 접이 발도 받침 폭 안에 들어가요.

#### 게임 영향

10.7 mm 2옥타브 흰 레인1.05 : 1 1옥타브 화면 : 실제 건반 1.02 MP 매 프레임 그릴 픽셀세로 매 프레임 90° 회전 필요

2옥타브 화면의 흰 레인은 10.7 mm(80 px), 검은 레인은 6.4 mm로 13개 중 가장 커요(C2·C4a와 같음). 1옥타브 화면은 O4 옥타브와 1.05:1로 거의 같은 크기예요. 대신 픽셀이 1.02 MP로 TD2보다 11 % 많고, 세로라 매 프레임 90° 회전 복사도 있어요. 그래서 60 fps 여유가 13개 중 가장 적어요. 16:9 그림은 1280×720으로 넣고, 남는 80 px 띠에는 게이지를 둘 수 있어요.

##### 장점

- 8인치라 레인이 넓고(C2·C4a와 같음), 1옥타브 화면이 건반과 거의 1:1이에요.
- 광학 본딩과 10점 터치예요.
- 커넥터가 뚜껑 구멍 바로 위라 B 그룹 중 리본 경로가 가장 짧아요(약 231~269 mm).
- config.txt 한 줄로 켜져요.

##### 단점

- 세로 화면이라 앱 회전이 필요하고, 그릴 픽셀도 가장 많은 쪽이에요(1.02 MP, C2·C3·C4a·C4b와 같음).
- 받침이 CU 뚜껑 폭에 0.6 mm 여유로 꽉 차요.
- 전력이 4 W라 배터리가 약 15~20분 줄어요.
- B 그룹 네 조합 중 가장 비싸요(+21,274원). 13개 중에서는 C4a 다음으로 비싸요.

##### 위험

- 받침 가장자리가 합판 뚜껑 이음(0.5 mm 틈)에 가까워요. 출력 오차가 크면 합판 뚜껑을 들 때 걸릴 수 있어요.
- 11번가 '10/2 도착'은 구매대행 글이라 믿기 어렵고, 판매자 평가도 없어요.
- 커넥터 입 방향은 도면에서 읽은 추정이에요. 반대면 400 mm 리본이 필요해요.
- Waveshare 드라이버에 냉간 부팅 문제 보고가 있어요(패치 미반영). 받으면 전원을 뺐다 켜는 시험을 10번 해요.
- 0.8 A를 점퍼로 보내니, 화면 쪽 전압을 재서 4.75 V 이상인지 확인해요.

#### 확인한 것 / 미확인

오늘 다시 연 것: 11번가 9049646842(118,500원, 10/2 도착 표시, 설명이 이 모델과 맞음)와 9188908210(120,300원), 엘레파츠 300 mm 리본과 점퍼, Waveshare 직판 54.99달러와 공지. rpi-6.18.y 오버레이의 8_0_inch_a·8_0_inch_a_4lane, 드라이버 800×1280 60.0 Hz, 위키의 0.8 A와 설정 줄도 확인했어요. Waveshare 도면(8-DSI-LCD-A-Size-20251025)으로 커넥터 위치를 다시 읽었고, 제품 사진을 img에 새로 받았어요. 확인 못 한 것: 알리 가격, DHL 운임, 실제 도착일(국내 재고인지), 커넥터 입 방향(추정), M3 나사값.

- 공통 나사 M3×20 4개와 M3×10 4개(640원)는 모든 조합에서 추정값이에요.

맨 위 표로 ↑

C4aC · 싸게·크게

### Waveshare 8inch DSI LCD (C) 8인치 1280×800 광학 본딩 DSI: 8인치 중 유일한 가로 본딩 화면

게임에 유리(가로)

138,974원

지금 안 대비 +35,374원

10/12~10/22 · 해외, 추정

Waveshare 8inch DSI LCD (C) (8인치 정전식 터치, DSI) 제품 사진

제품 사진 (누르면 크게)

화면

Waveshare 8inch DSI LCD (C) (8인치 정전식 터치, DSI)

크기·해상도

8인치 · 1280×800

방향

가로(landscape) 기본, 회전 필요 없음

연결

MIPI DSI 15핀 1.0 mm FPC + PH2.0 4핀(5 V·GND·SDA·SCL) + USB-C 전원(안 씀)

패널

IPS, 광학 본딩 강화유리 6H, 밝기 비공개

터치

정전식 10점, I2C(Goodix, 커널 기본 오버레이에 포함)

외곽 (mm)

194.00 × 119.00, 유리+LCM 5.0 + 기판 1.6 (Pi용 받침 8은 떼어냄) → 두께 약 10(추정). 기판은 7inch DSI LCD (E)와 같은 7/8/10.1인치 공용 기판

보이는 영역 (mm)

172.82 × 108.24

Waveshare 8inch DSI LCD (C) 앞·옆 치수 도면

Waveshare 8inch DSI LCD (C) 앞·옆 치수 (누르면 크게)

#### 살 것

품목 | 수량 | 단가 | 금액 | 판매처 | 확인
Waveshare 8인치 라즈베리 파이 5 정전식 터치 디스플레이 1280×800 IPS DSI (옵션 01 8inch DSI LCD (C)) 오늘 확인: 133,450원(원가 143,500원), 무료배송, '내일출발 예정' 표시지만 발송지가 중국이라 도착은 늦어요 | 1 | 133,450원 | 133,450원 | 옥션 (판매자 다진홀딩스 4.1, 중국 발송 'Mainland') (http://itempage3.auction.co.kr/DetailView.aspx?itemno=F519663381) itempage3.auction.co.kr | 확인
Raspberry Pi 5 공식 디스플레이 리본 Standard–Mini 300 mm (SC1132) 2,800원+VAT. 22핀(Pi)→15핀(화면) 디스플레이용 300 mm라 rev 2의 FIT0997과 종류·길이가 같아요. A1·A2와 같은 줄이에요. 카메라용(SC1129)은 모양이 같아도 핀 배열이 달라 못 써요 | 1 | 3,080원 | 3,080원 | 아이씨뱅큐 (해외 재고, 2주 이내, 기존 아이씨뱅큐 주문에 합침) (https://www.icbanq.com/P015646405) icbanq.com | 확인
[엘레파츠] 실리콘 점퍼 26AWG 20cm F/F 빨강·검정, M/M 빨강·검정 동봉 PH2.0 4핀 선의 5 V·GND만 GPIO 2번·6번까지 늘려요 | 4 | 451원 | 1,804원 | 엘레파츠 (24시간 발송) (https://www.eleparts.co.kr/goods/view?no=9461190) eleparts.co.kr | 확인
스텐 유두 렌치볼트 M3 × 20 mm 모든 조합 공통, 값 추정 | 4 | 100원 | 400원 | 11번가 굿나잇몰 (https://www.11st.co.kr/products/4236198413) 11st.co.kr | 미확인
스텐 유두 렌치볼트 M3 × 10 mm (+4) 모든 조합 공통, 값 추정 | 4 | 60원 | 240원 | 11번가 굿나잇몰 (https://www.11st.co.kr/products/4236198413) 11st.co.kr | 미확인
배송비 | | | 0원 | 옥션 무료배송 + 아이씨뱅큐 리본·엘레파츠 점퍼·11번가 나사는 기존 주문에 합침
합계 | | | 138,974원 | 지금 안(103,600원) 대비 +35,374원

옥션 133,450 + 공식 300 mm 리본 SC1132 3,080 + 점퍼 1,804 + 공통 나사 640 = 138,974원이에요. 옥션은 무료배송이고, 리본은 A1·A2와 같은 아이씨뱅큐 줄이라 기존 아이씨뱅큐 주문에 합쳐 배송비가 없어요. rev 2처럼 디바이스마트 FIT0997(5,390원)을 쓰면 디바이스마트 단독 주문(66,000원 미만)이라 배송비 2,700원이 붙어 143,984원이에요(9/30 저장본 값, 오늘 밤 미확인). 더 싼 길: Waveshare 직판 $78.99(오늘 확인, 약 106,857원) + 배송비(미확인)라 배송비가 약 2.6만 원 이하면 직판이 싸요. 알리 검색 목록에 Waveshare 8인치 DSI 1280×800이 97,291원으로 보였지만 모델과 배송비를 확인하지 못했어요. 네이버 스토어 150,900원(다나와 목록, 미확인).

##### 받는 시기

옥션 판매자는 중국에서 보내는 구매대행이라 국경절 뒤 10/12~10/22쯤으로 추정해요(미확인). 직판 DHL이면 10/12~10/19 추정. 300 mm 리본(SC1132)은 아이씨뱅큐 해외 재고(2주 이내)라 10/14 무렵 와요(중국 연휴로 10/20까지 늦을 수 있어요, 추정). 리본은 통합(11/16) 때 필요해요.

##### Pi 5 설정

config.txt에 dtoverlay=vc4-kms-dsi-waveshare-panel,8_0_inch 한 줄을 넣어요. Pi 커널 기본 오버레이 목록에 '8_0_inch 8.0" 1280x800'이 있고 Waveshare 위키도 같은 줄을 써요. Pi 5 CAM/DISP 1 포트(기본 DSI1)에 꽂고, 0번 포트면 끝에 ,dsi0을 붙여요. 리본은 22핀(Pi)→15핀(화면) 디스플레이용 300 mm(공식 SC1132)예요. 카메라용 리본은 모양이 같아도 핀 배열이 달라 안 돼요. 전원은 동봉 PH2.0 4핀 선에서 5 V·GND 두 가닥만 GPIO 2번·6번에 이어요(Pi 5를 화면 뒤에 붙이는 스프링 핀 방식은 우리 구조에서 못 써요). 터치는 리본 안의 I2C로 Goodix 드라이버가 잡아 evdev로 나와요. 밝기는 /sys/class/backlight/*/brightness에 0~255를 써서 바꿔요(D14 0 %·100 % 시험, D19 화면 끄기 가능). 가로라 회전은 없어요. HDMI 두 포트가 모두 비어 외부 TV는 가진 1 m 케이블로 꽂아요.

##### 전력

화면이 더 쓰는 전력 | 약 2.5 W (GPIO 2·6번)
평균 | 16.1~20.1 W
순간 최대 | 54.8 W (60 W까지 5.2 W 남음)
배터리 | 약 3.1~3.9시간
45 W 충전기 −2 dB | 39.8 W

화면 약 2.5 W(위키: 5 V 0.5 A). GPIO에서 받아요. TD2와 같아요: 평균 16.1~20.1 W, 최대 54.8 W(여유 5.2 W), 45 W −2 dB 39.8 W, 배터리 3.13~3.91시간, Pi 입력 2.09 A, 5.1 V 레일 2.49 A, Pi USB 0.2/1.6 A.

#### 장착 (축척 스케치)

위에서 본 접은 상태. 파란 선 = 받침, 회색 = 화면 유리, 진한 회색 = 보이는 화면, 주황 = DSI 리본, 보라 = HDMI, 초록 = USB, 빨강 = 전원선, 점선 네모 = 뚜껑 아래 Pi 5. 선과 단자는 화면 뒤에 있어요. DSI 리본 단자 x620.0·u87 (추정).

옆에서 본 모습(y·z, mm). 실선 = 25°로 세운 상태, 점선 = 뒤로 접은 상태. 경첩 축·뚜껑·다리 주머니는 모든 조합에서 같아요.

받침 x557.10~754.90 (폭 197.8), 뚜껑 여유 왼쪽 0.60 · 오른쪽 0.60 mm. 접은 상태 y296.5~420.5, 받침 두께 17.60.

들어가지만 빠듯해요. 폭 194 mm라 테두리를 1.6 mm로 줄이면 받침 197.8 mm(x557.1~754.9), 양옆 여유 0.6 mm예요. 높이 119라 접은 뒤끝 y420.5(y447 안). 두께 약 10으로 보면 받침 두께 D_c 17.6, 접은 높이 z113.6, 22°에서 가장 앞 y276.1(통과), 사용 중 맨 위 z221.7. 리본은 FPC가 7인치 (E)와 같은 기판 자리라고 보고 계산하면 281.9/300 mm(여유 18.1, 기준 15를 겨우 넘음)라 받으면 FPC 위치를 꼭 재야 해요. 뚜껑 구멍 22×6 그대로(리본 + 전원선 2가닥). 다리 힘 42.9 N(안전율 9.2), 뒤꿈치 175 N, 뚜껑 나사 85 N, 넘어짐 안전율 2.2.

설계 변경: 뚜껑 v2는 그대로예요. 받침은 새로 그려요: 테두리 1.6 mm, 기판 네 귀 M3 구멍(95×68, 7인치 (E) 도면 기준)으로 고정, FPC와 PH2.0 점검창. 리본은 공식 SC1132(22→15핀 300 mm)라 rev 2의 FIT0997과 같은 종류예요. rev 2 받침은 폭 193.92라 쓰지 못해요. 뒷면 도면이 공개되지 않아 기판 위치는 받아서 재고 고쳐요.

#### 게임 영향

10.7 mm 2옥타브 흰 레인1.05 : 1 1옥타브 화면 : 실제 건반 1.02 MP 매 프레임 그릴 픽셀가로 회전 없음

8인치 1280×800 가로에 광학 본딩이에요. 뚜껑에 들어가는 가장 큰 크기(B4·C2와 같은 8인치)이고, 8인치 중 가로이면서 본딩인 것은 이것뿐이에요. 2옥타브 흰 레인 10.7 mm(80 px), 1옥타브 화면은 O4 옥타브와 1.05:1로 거의 같은 크기예요. 픽셀 1.02 MP로 60 fps 예산 안이에요. DSI라 변환 칩 지연이 없어요.

##### 장점

- 8인치 중 유일하게 가로이면서 광학 본딩·10점 터치예요.
- DSI라 설정 한 줄, sysfs 밝기 조절, HDMI 포트 두 개가 모두 남아요.
- 전력이 TD2와 같아 전원 계산을 바꿀 필요가 없어요.
- 리본 종류(22→15핀)가 rev 2와 같아요.

##### 단점

- 13개 중 가장 비싸요. rev 2보다 35,374원 더 들어요(직판이면 줄 수 있음).
- 양옆 여유가 0.6 mm라 출력 오차에 민감해요.
- 밝기 값이 공개되지 않았어요.
- 해외 발송이라 10월 중하순에 와요.

##### 위험

- FPC 위치를 모르는 상태라 300 mm 리본이 모자랄 수 있어요. 더 긴 DSI 리본은 신호가 불안해질 수 있어요. 모자라면 공식 500 mm(SC1133)로 바꿀 수 있어요(값 미확인).
- 옥션 판매자는 구매대행이라 도착일과 A/S가 불확실해요(평점 4.1).
- 두께 10 mm는 추정이에요.
- 300 mm 리본은 아이씨뱅큐 해외 재고라 10/14~10/20쯤 와요. 통합(11/16) 전에는 충분해요.

#### 확인한 것 / 미확인

오늘 Waveshare 판매 페이지($78.99, 무게 0.352 kg, 구성품: 15핀 FPC 50·160 mm, DSI-Cable-12cm, PH2.0 4핀 선 200 mm, 나사), 위키(5 V 0.5 A, 설정 줄, sysfs 밝기), 커널 오버레이 목록(8_0_inch)을 확인했어요. 옥션 페이지에서 133,450원·무료배송·옵션 '8inch DSI LCD (C)'·중국 발송을 확인했어요. 리본은 아이씨뱅큐 SC1132(3,080원, 해외 재고 2주 이내)를 오늘 밤 확인했어요(A1과 같은 줄). 확인 못 한 것: 뒷면 기판 위치와 FPC 위치, 두께, 밝기, 도착일, 직판 배송비.

- 공통 나사 M3×20 4개와 M3×10 4개(640원)는 모든 조합에서 추정값이에요.

맨 위 표로 ↑

## 뺀 후보와 이유

그룹 | 후보 | 뺀 이유
A | A4: 국내 재고(1~3일) 7인치 1024×600 (C)형 HDMI 정전식 터치, 7만 원 이하 | 찾지 못했어요. 쿠팡의 7만 원 이하 제품은 모두 10/13~10/23 도착이라 해외 발송이에요. 11번가의 7만 원 이하 제품(키메라스토어 62,800원, 라온힐조 62,750원, 도원네트웍스 69,000원 등)은 '모레 도착'이라고 떠도 상세 설명이 알리 복제이고, 키메라스토어는 '해외에서 발송되는 상품'이라고 적혀 있어요. G마켓 51,250원 제품은 10/16 도착 예측이고 터치 여부가 불분명해요. 국내에서 바로 오는 7인치 HDMI 터치는 모두 8.5만 원 이상이에요(메카솔루션 OEM (C)형 88,000원, 쿠팡 SY7008-380G 105,000원). 네이버 스마트스토어는 브라우저 안전 정책과 접속 차단(418) 때문에 확인하지 못했어요.
A | A3의 얇은 micro-HDMI·micro-USB 일반 케이블 경로(FFC 대신) | 일반 선은 플러그가 22×6 구멍을 지나가지 못해 뚜껑 구멍과 받침 홈을 약 24×14로 키워야 해요. 굵기 3.5~5 mm 선은 USB 선 묶음 위 14 mm 공간과 경첩 고리(R10)에서 잘 꺾이지 않아요. 화면 쪽은 옆 여유가 27.5 mm라 꺾인 HDMI-A 플러그도 따로 필요해요. FFC 세트가 더 얇고 싸고 구멍을 그대로 써요.
A | 카메라용 22→15핀 리본(공식 SC1129 300 mm 3,080원, ShenzenAV 30 cm 1,650원) | 디스플레이에 쓸 수 없어요. 모양은 같지만 핀 배열이 달라서 Waveshare와 라즈베리파이 모두 카메라 리본과 디스플레이 리본을 섞지 말라고 해요.
A | Waveshare 7inch HDMI LCD (H) (엘레파츠 93,577원, 24시간 발송) | (C)와 모양은 같지만 6,501원 비싸고 약 4 W로 전력이 더 많아요. 붙어 있는 OSD·오디오·VGA는 이 피아노에 쓰지 않아요. HDMI 커넥터를 포함한 두께가 13.8 mm라 접은 높이도 올라가요.
A | 쿠팡 SY7008-380G 7인치 HDMI 정전식 (105,000원, 10/2 도착) | 국내에서 빨리 오지만 (C)보다 18,000원 비싸고, 치수 도면을 확인하지 못해 받침을 미리 그릴 수 없어요.
A | 공식 7인치 터치스크린 1세대 RPI-DISP-7 (쿠팡 99,900원) | 800×480에 두껍고 오래된 모델인데 값은 TD2와 비슷해요.
A | 비티텍 FIT0997 300 mm (5,000원+VAT) | 10만 원 미만 주문에 배송비 3,500원이 붙고 재고는 문의해야 해요. 같은 길이의 공식 SC1132(아이씨뱅큐 3,080원)가 더 싸요.
B | Waveshare 8inch DSI LCD (C) (G마켓 4471168663 107,020원, 11번가 드림321에이 129,400원) | 8-DSI-TOUCH-A와 다른 옛 모델이에요(15핀, 1280×800 가로). B 그룹 범위가 아니고, 두께와 커넥터 도면도 다시 보지 않았어요.
B | 알리익스프레스 상품 페이지 (7C 60,635원 / 7A 67,572원 / H 98,000원 / 8A 82,969원, 예전 검색 목록가) | 오늘 브라우저로 열었더니 로봇 확인(reCAPTCHA) 화면이 떠서 값을 확인하지 않았어요. 빼지는 않았고, 미확인 값으로 각 카드의 합계 설명에 적었어요.
B | Waveshare 직판 (7C 42.99 / 7A 49.99 / H 58.99 / 8A 54.99달러) | 물건값은 오늘 확인했지만 DHL 운임이 결제 단계에서만 나와서 합계를 정할 수 없어요. 각 카드의 합계 설명에 다른 선택지로 적었어요.
B | 화면 동봉 22핀 200 mm 반대면 리본 (피아노 안 최종 배선용) | Pi에서 받침 홈까지 고정 경로만 170 mm라 30 mm밖에 남지 않아요. 책상 위 시험용으로만 써요.
B | Pi 5용 22핀→15핀 DSI 리본 (vctec 30 cm 5,000원 = DFRobot FIT0997, 쿠팡 Pi5-Display-Cable 등) | 화면 쪽이 15핀이라 22핀 화면(B1~B4)에는 꽂을 수 없어요.
B | Adafruit 22핀 0.5 mm FPC 20 cm (vctec 3,200원) | 200 mm라 경로(약 231~297 mm)에 짧아요.
B | GUOCONN 1.0*22P*300 (엘레파츠 730원) | 핀 간격이 1.0 mm라 Pi 5와 이 화면들의 0.5 mm 커넥터에 맞지 않아요.
B | 11번가 9545768483, 9571257815 | 설명을 열어 보니 각각 7inch DSI LCD (E)와 10.1-DSI-TOUCH-A였어요. B 그룹 모델이 아니에요.
B | 쿠팡 8826092824 (800×1280 광학 본딩, 165,800원, 10/28 도착 표시) | 목록만으로는 8인치인지 10.1인치인지 확실하지 않고, 11번가 8-DSI-TOUCH-A보다 4.7만 원 비싸서 뺐어요.
B | 디바이스마트, 네이버 스마트스토어 | 디바이스마트는 오늘 밤 접속 시간이 초과됐고, 네이버 쇼핑은 접속이 차단됐어요(418). 그래서 확인하지 못했어요.
C | Waveshare 8DP-CAPLCD (8인치 1280×800 본딩, HDMI) | 오늘 옥션 드셈유통 174,320원(무료배송), 직판 $73.99 + 배송비예요. 뒷면 단자가 위를 향해 꺾인 HDMI·USB-C 플러그가 필요하고, 같은 폭(194 mm)의 8인치 DSI (C)보다 비싸면서 HDMI 변환 지연까지 있어 C4a로 대신했어요.
C | 쿠팡 7인치 1024×600 44,660원 (Huizhou Dequan, 10/13 도착) | 스탠드 케이스형 다른 물건이에요. 상세 사진과 사양이 거의 없고 분류도 '일체형PC'로 잘못돼 있으며 치수 도면이 없어요.
C | 쿠팡 Surenoo Display-D 45,840원 (Huizhou Wanyang, 평가 73%) | C1b와 같은 제품의 다른 판매자예요. 300원 비싸고 평가가 낮아 빼두었어요.
C | G마켓 7인치 1024×600 (옴니비즈2, 42,770원) | 기본 옵션이 TN이고 IPS 터치는 +4,500원(47,270원)이라 C1(38,310원)보다 비싸요.
C | 롯데ON 7인치 1024×600 (LO2740712487) | 다나와에는 37,650원으로 떴지만 오늘 페이지 값은 42,000원이라 C1보다 비싸요.
C | 쿠팡 8인치 1280×800 107,760원(8850059930), SY8008-610G 220,000원 | C2보다 비싸고 사양·치수 도면을 확인할 수 없어요.
C | Waveshare 7EP-CAPLCD Monitor (알루미늄 케이스판) | 케이스 때문에 크고 무거우며 $96.59~99.99로 C3보다 비싸요.
C | 엘레파츠의 라즈베리파이 공식 카메라 케이블 300 mm (3,080원) / 공식 디스플레이 케이블 200 mm (1,540원) | DSI 화면선으로 FIT0997 대신 쓰려고 봤어요. 300 mm는 카메라용(SC1129)이라 못 써요. 엘레파츠에는 디스플레이용 200 mm뿐이라 경로(약 275~282 mm)보다 짧아요. 300 mm 공식 디스플레이용(SC1132)은 아이씨뱅큐에 있어서 C4a·C4b에 넣었어요(A1 참고).
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
