WongyuKoh/Toccata/hardware/mechanical/touchscreen/rev3/touch_rev3_review.html

# R31 터치스크린 수정 3판 — 검수용

B1 Waveshare 7-DSI-TOUCH-C (7인치 가로 1024×600, DSI) · 자리: L2 가운데 화면 뚜껑 (x501~721, y214~341.5, 윗면 z72.85) · 2026-10-01 · 모든 숫자는 numbers.json(3a)에서 스크립트로 계산 · 검수가 끝나면 CAD 세션에 CAD_SPEC_rev3.md를 넘김

## 검수할 것

경첩 위치 | 경첩 축 y226.55 · z81.35. CAD 권장(y216~218, z76)보다 약 9 mm 뒤·5 mm 위 — 권장 자리면 22°에서 받침이 건반 모듈 위로 넘어가고 접은 다리 자리가 없음. 22~90° 어느 각도에서도 가장 앞이 y216.0(금지선 y215 뒤)
화면 높이·각도 | 25° 기울임, 보이는 영역 가운데 y240.9 · z142.9, 가장 높은 곳 z189.2. 앉은 눈(추정)에서 내려다보는 각 27.5°라 화면과 거의 직각. 건반 뒤끝에서 가리는 것 없음
접은 상태 | z78.35~95.35, y233~339 — 뚜껑 뒤끝(y341.5)까지 2.45 mm, 스피커 윗면(z148)보다 53 mm 낮음
받침다리 | 받침 뒤 u30에 경첩, 길이 67 mm, 39.8°. 10 N으로 화면 위를 누르면 다리 27 N(좌굴 한계 792 N). 다리는 22°에서 주머니에 넣음
화면 고정 | 뒷면 네 귀 M2.5 구멍(154×88)에 M2.5×6 4개. 구멍 깊이를 몰라 물림 = min(깊이−0.5, 4), 최소 2 규칙. 동봉 스터드·스탠드오프는 달지 않음(달면 접은 끝이 뚜껑을 넘음)
커넥터 방향 (추정) | 사진으로 "DSI 입구 +x"로 판단. 받은 화면이 반대면 받침의 창·홈·뚜껑 구멍·클립을 x611 기준으로 뒤집고 예비로 산 A형 리본을 씀(그때 리본 약 202 mm)
리본·전원선 | DSI 리본 256 / 300 mm(여유 44), B형. 뚜껑 밑 z61.2로 지나 Pi DISP1(x589~592)로. 추정 Pi 방열판과 0.3 mm — 실물로 확인. 전원선 약 345 mm 필요, 있는 길이 500~550 mm
공차 수준 틈 | 뒤꿈치 틈 0.37 mm(25°), 접은 다리 클립–뚜껑 0.78, 다리 걸이–뚜껑 1.2 — 첫 출력에서 확인
O4 모듈 정비 | O4의 USB 플러그가 화면 뚜껑 밑 → 뚜껑 나사 4개를 풀고 Pi 쪽 리본(ZIF)을 풀어 뚜껑을 듦(리본 꽂은 채 약 96 mm 들 수 있음)
회로도 (개정 C) | SCH-01에 화면 A605와 선 W605(DSI)·W606~W608(5 V), SCH-06에 Pi 헤더 2(5 V)·6(GND) → 점퍼 F/F·M/M → 동봉선 → 화면, 전원 예산 순간 54.4 W(60 W까지 5.6 W). 넷 이름 +5V_PI. 연결 검사 9장 오류 0. 동봉선 3핀 하우징 핀(1 빨강 5 V, 2 빈칸, 3 검정)은 사진 추정 → 받으면 통전 검사
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
