WongyuKoh/Toccata/docs/report/toccata-v4/img/bench_vise.jpg

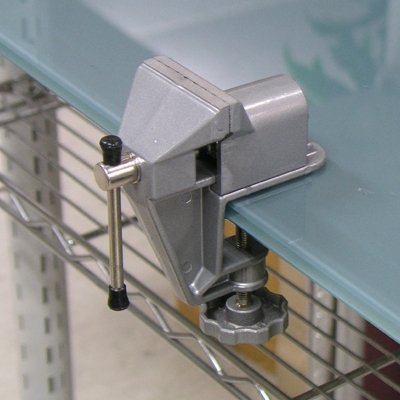
docs/report/toccata-v4/img/bench_vise.jpg
