WongyuKoh/Toccata/docs/report/toccata-v4/img/felt_2t_merino.jpg

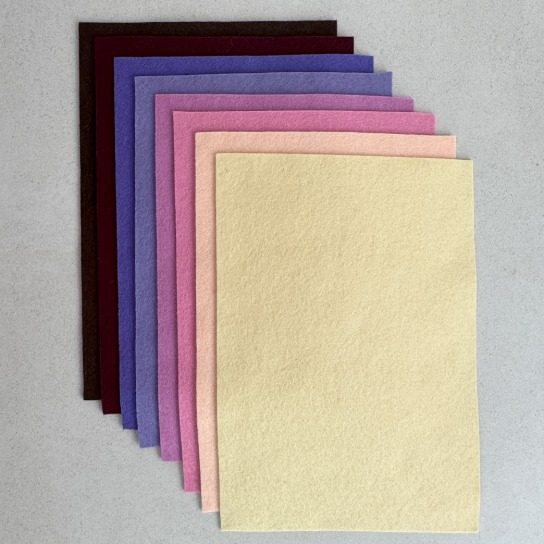
docs/report/toccata-v4/img/felt_2t_merino.jpg
