WongyuKoh/Toccata/docs/report/toccata-v4/img/felt_05t_L40.webp

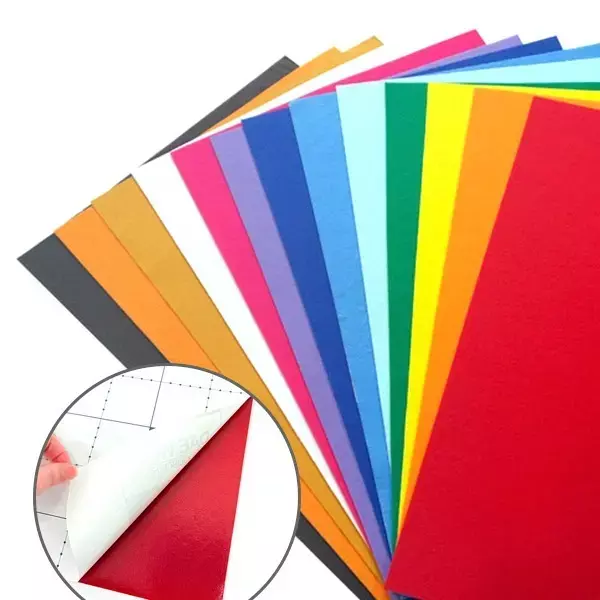
docs/report/toccata-v4/img/felt_05t_L40.webp
