WongyuKoh/Toccata/docs/report/toccata-v4/img/flat_file.jpg

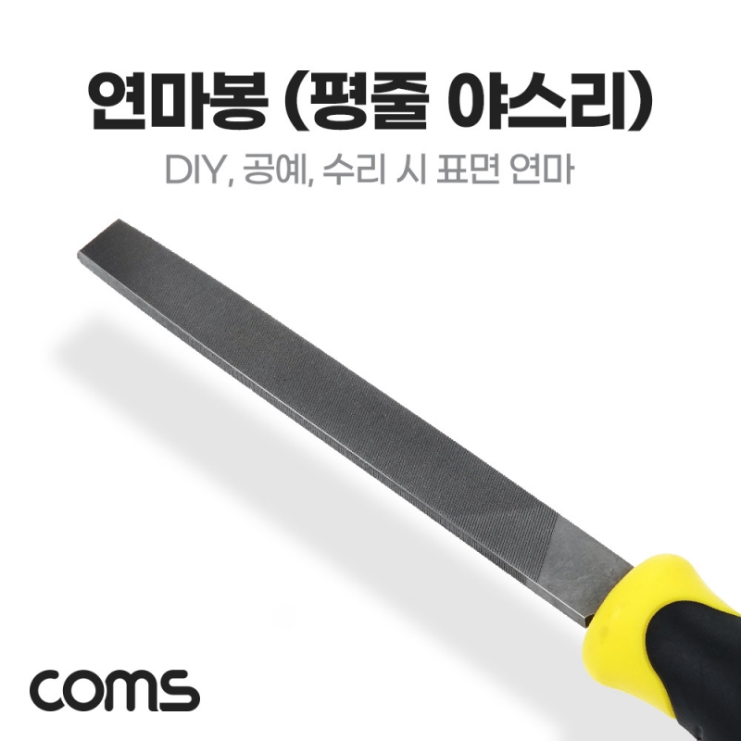
docs/report/toccata-v4/img/flat_file.jpg
