WongyuKoh/Toccata/docs/report/toccata-v4/img/goodnight_bolts.jpg

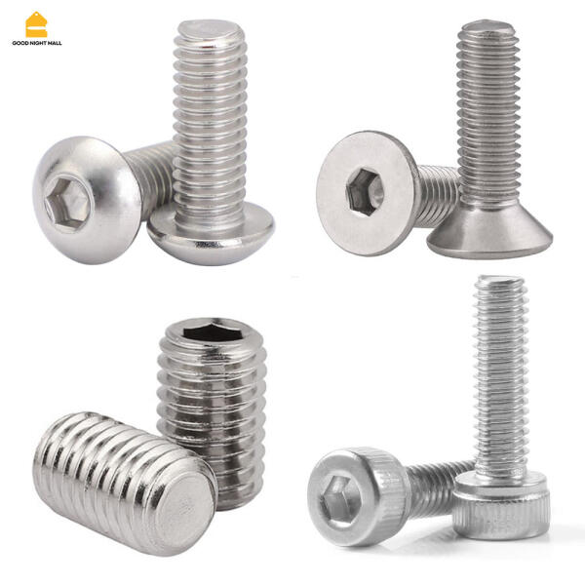
docs/report/toccata-v4/img/goodnight_bolts.jpg
