WongyuKoh/Toccata/docs/report/toccata-v4/img/m3_nut.jpg

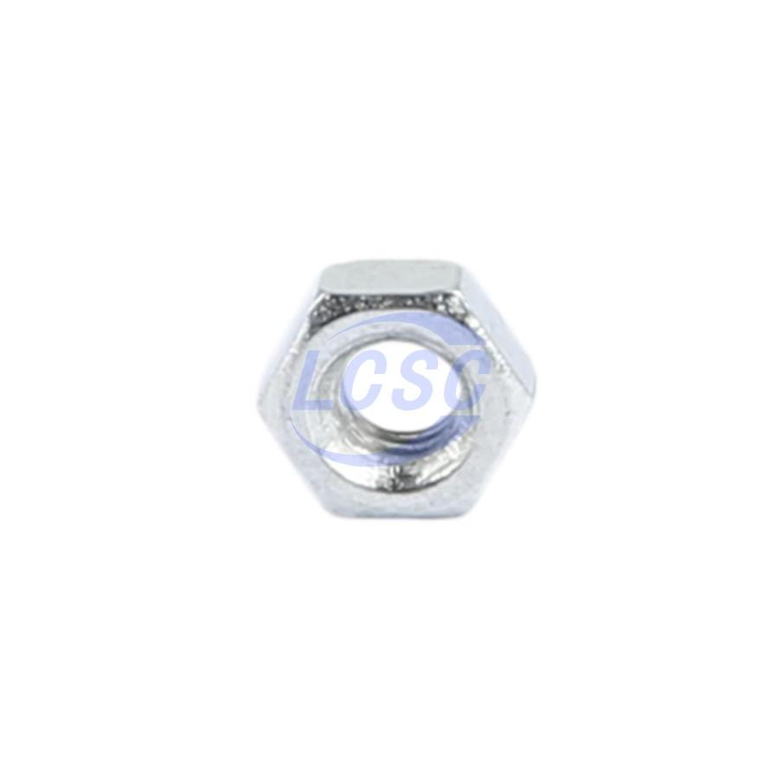
docs/report/toccata-v4/img/m3_nut.jpg
