WongyuKoh/Toccata/docs/report/toccata-v4/img/sus_rod.webp

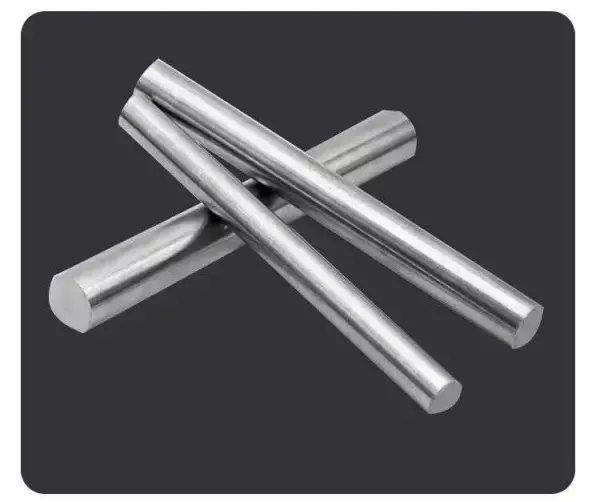
docs/report/toccata-v4/img/sus_rod.webp
