WongyuKoh/Toccata/docs/report/toccata-v4/rear/R02_rear_left.png

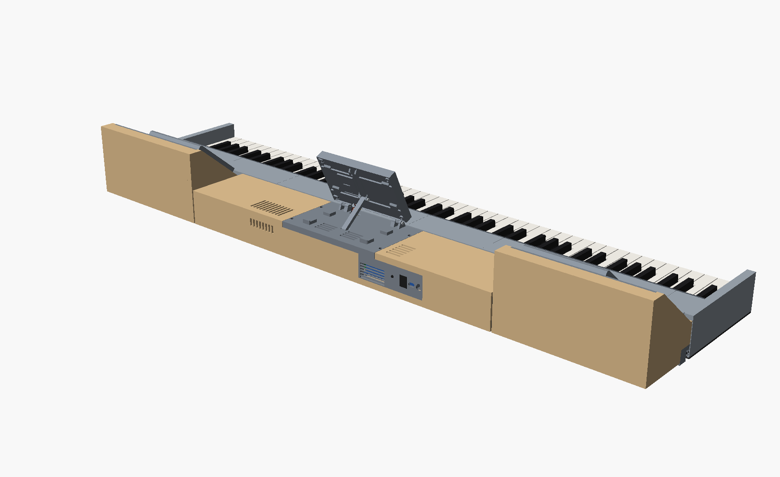
docs/report/toccata-v4/rear/R02_rear_left.png
