WongyuKoh/Toccata/hardware/mechanical/before/cad/renders/bed12.png

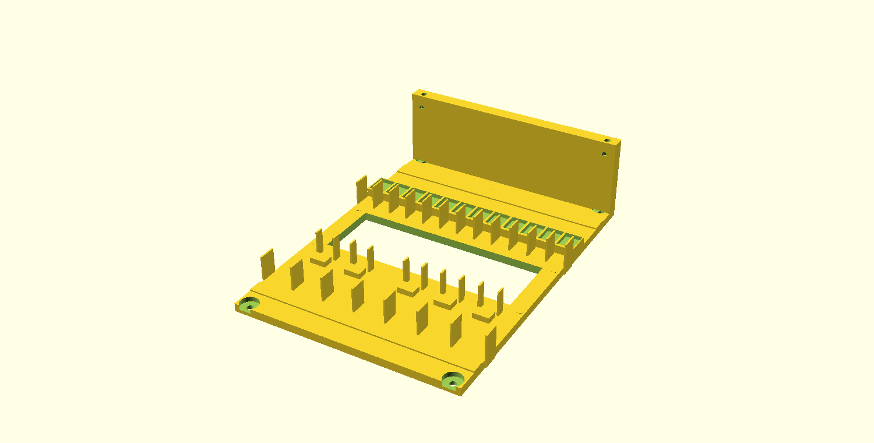
hardware/mechanical/before/cad/renders/bed12.png
