WongyuKoh/Toccata/hardware/mechanical/before/cad/renders/key_white.png

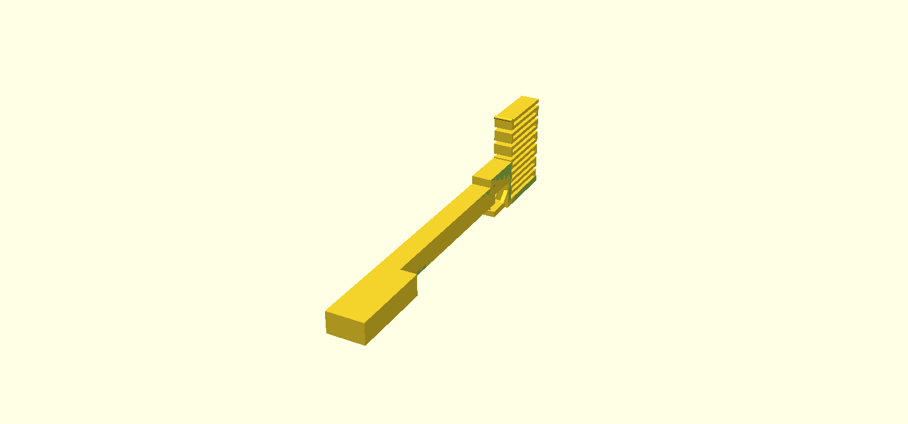
hardware/mechanical/before/cad/renders/key_white.png
