WongyuKoh/Toccata/hardware/mechanical/before/cad/renders/keys12.png

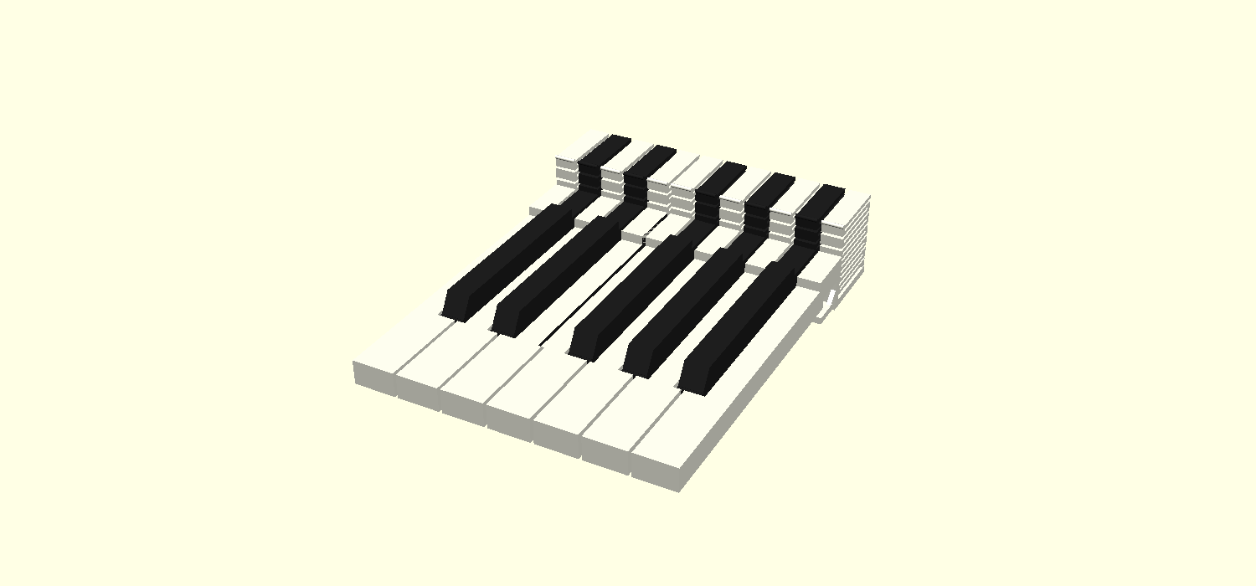
hardware/mechanical/before/cad/renders/keys12.png
