WongyuKoh/Toccata/hardware/mechanical/before/cad/renders/pivot_side.png

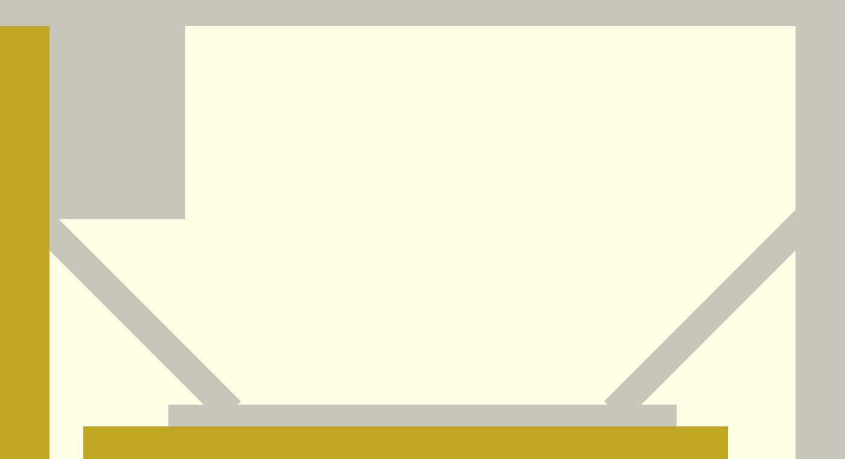
hardware/mechanical/before/cad/renders/pivot_side.png
