WongyuKoh/Toccata/hardware/mechanical/before/cad/renders/section.png

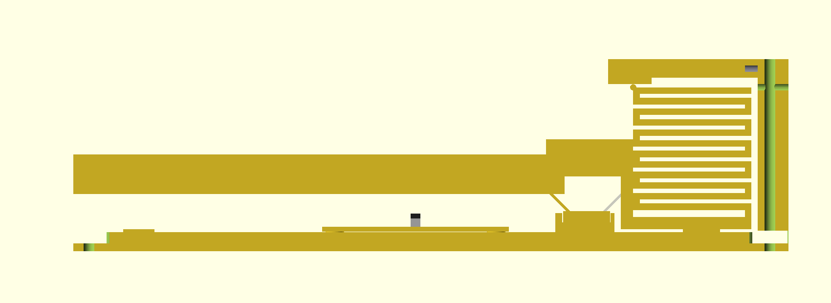
hardware/mechanical/before/cad/renders/section.png
