WongyuKoh/Toccata/hardware/mechanical/before/cad/renders/v1.5-multipart/bed3.png

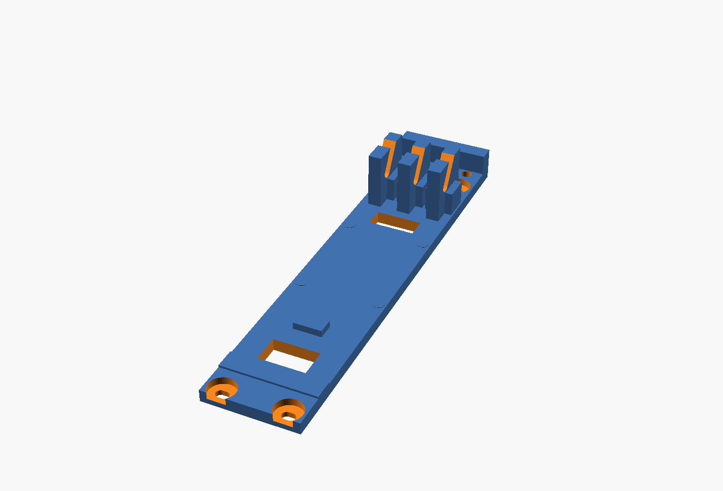
hardware/mechanical/before/cad/renders/v1.5-multipart/bed3.png
