WongyuKoh/Toccata/hardware/mechanical/before/cad/renders/v1.5-multipart/bed12.png

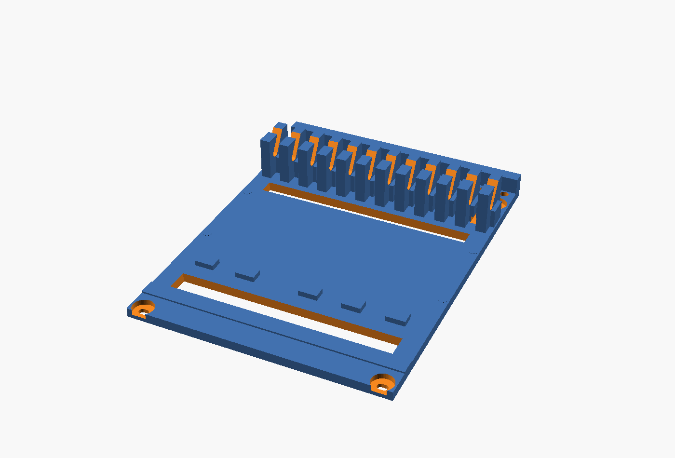
hardware/mechanical/before/cad/renders/v1.5-multipart/bed12.png
