WongyuKoh/Toccata/hardware/mechanical/before/cad/renders/v1.5-multipart/exploded.png

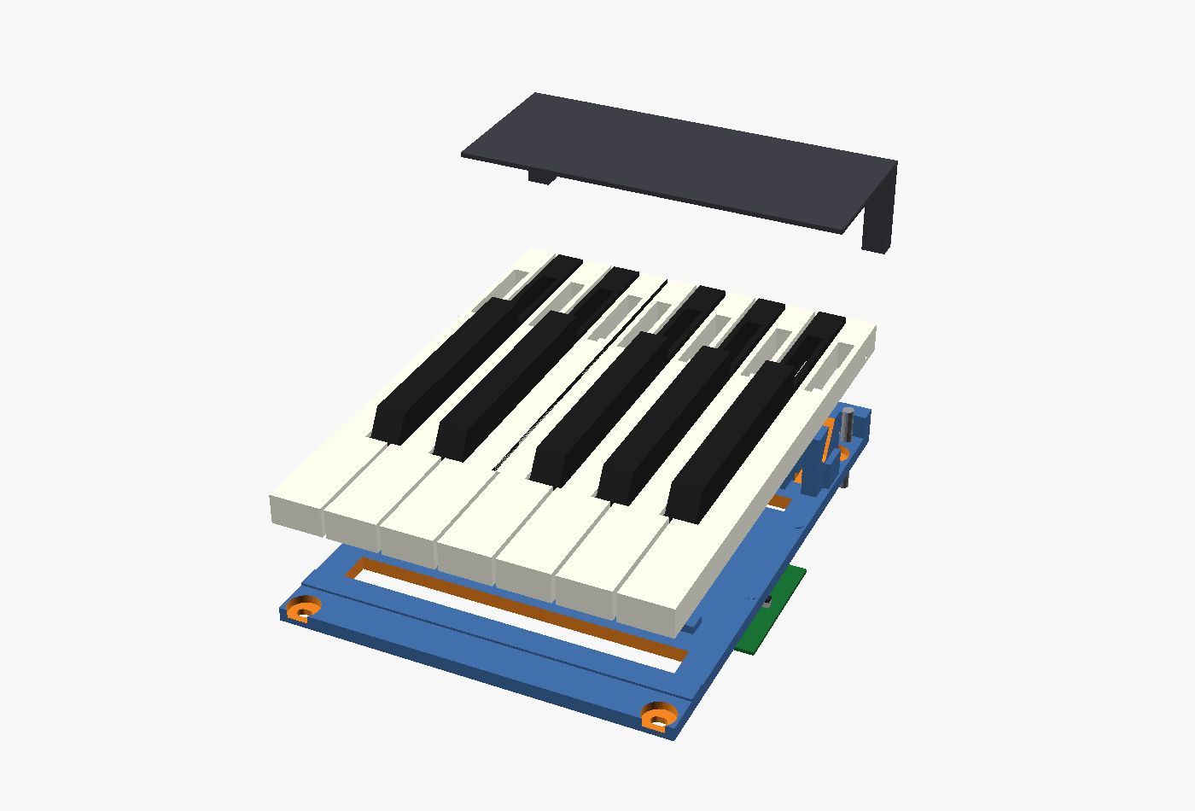
hardware/mechanical/before/cad/renders/v1.5-multipart/exploded.png
