WongyuKoh/Toccata/hardware/mechanical/before/cad/renders/v1.5-multipart/full88.png

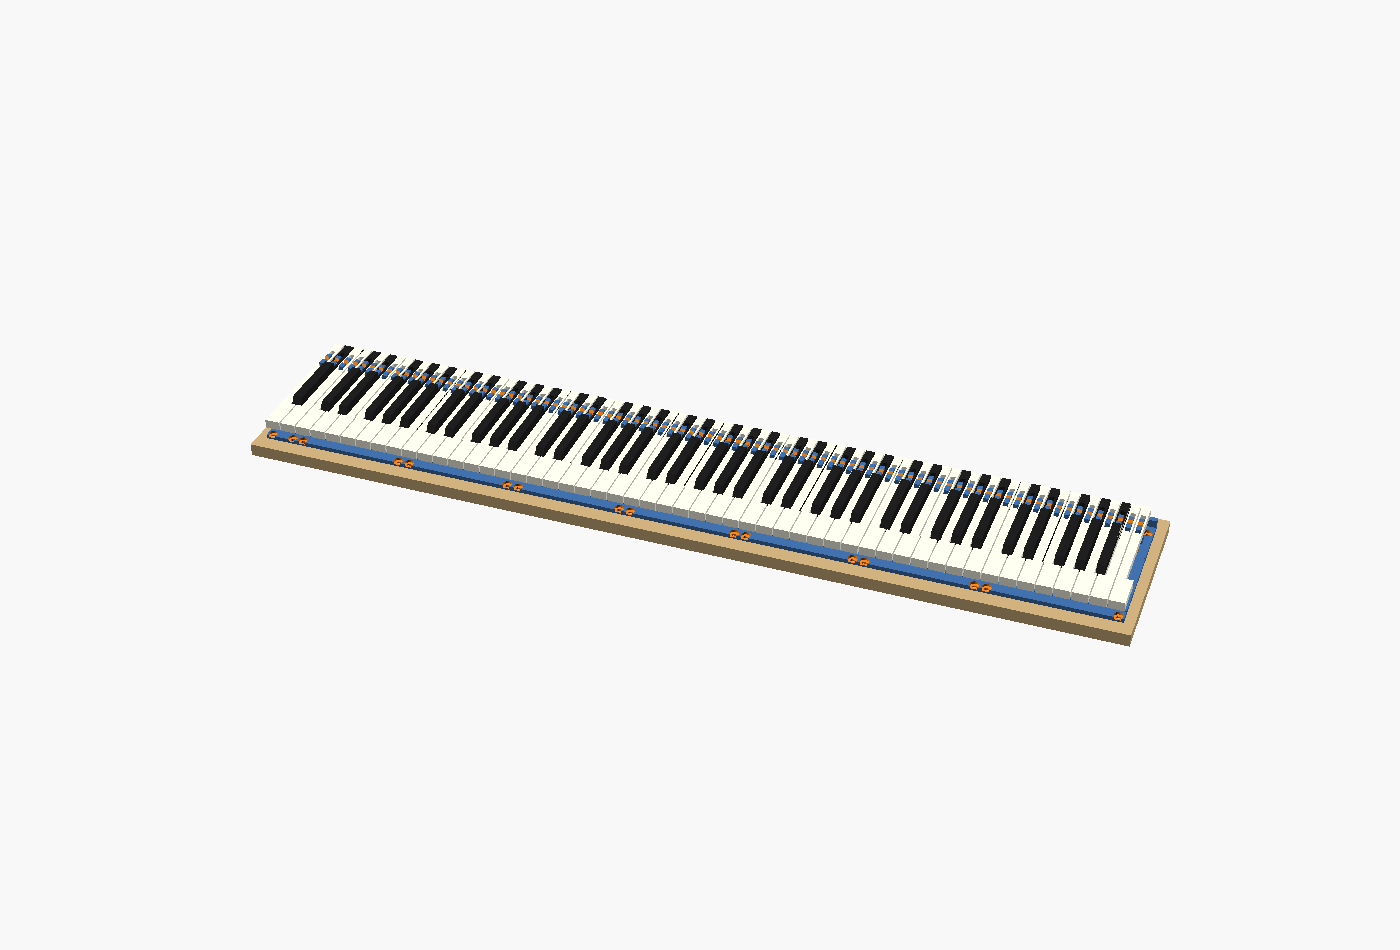
hardware/mechanical/before/cad/renders/v1.5-multipart/full88.png
