WongyuKoh/Toccata/hardware/mechanical/key-action-v4/report/r3-progress/img/hacksaw_blade.jpg

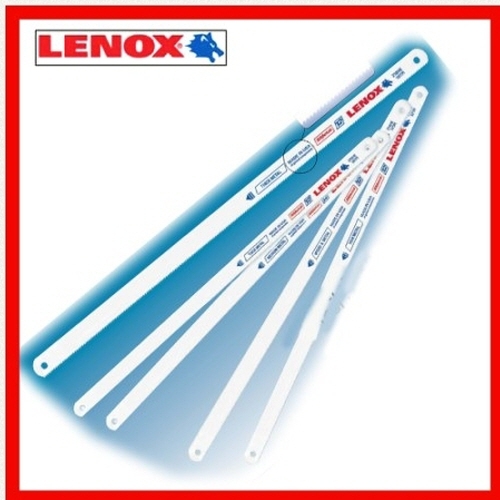
hardware/mechanical/key-action-v4/report/r3-progress/img/hacksaw_blade.jpg
