WongyuKoh/Toccata/hardware/mechanical/key-action-v4/report/r3-progress/img/spring_misumi.jpg

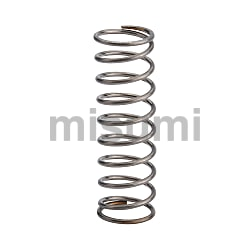
hardware/mechanical/key-action-v4/report/r3-progress/img/spring_misumi.jpg
