WongyuKoh/Toccata/hardware/mechanical/touchscreen/rev3/model3d/renders/01_연주자_시점_전체.png

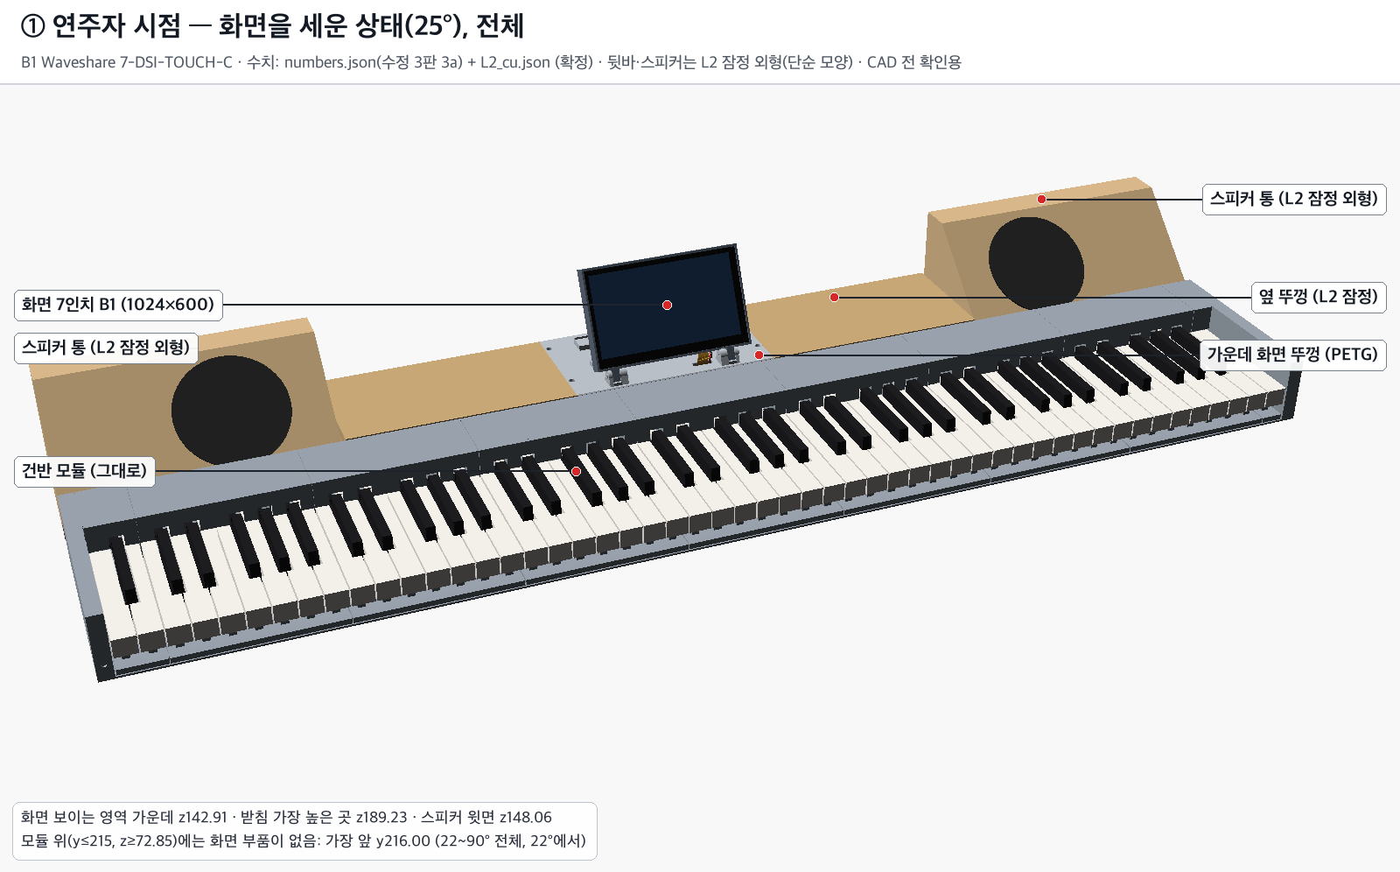
hardware/mechanical/touchscreen/rev3/model3d/renders/01_연주자_시점_전체.png
