WongyuKoh/Toccata/hardware/mechanical/touchscreen/rev3/model3d/renders/03b_옆_단면_x655_리본길.png

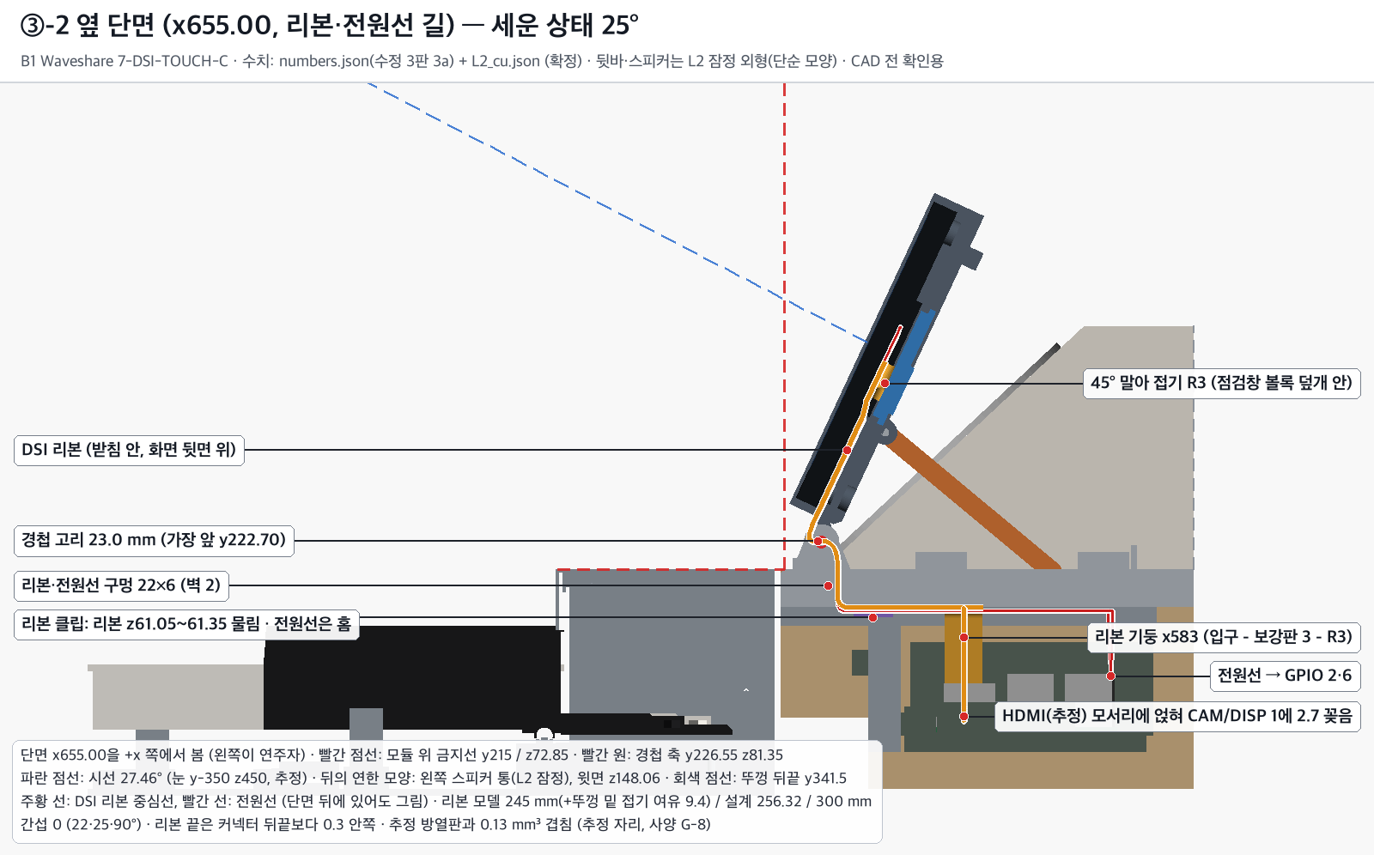
hardware/mechanical/touchscreen/rev3/model3d/renders/03b_옆_단면_x655_리본길.png
