WongyuKoh/Toccata/hardware/mechanical/touchscreen/rev3/model3d/renders/06_분해도.png

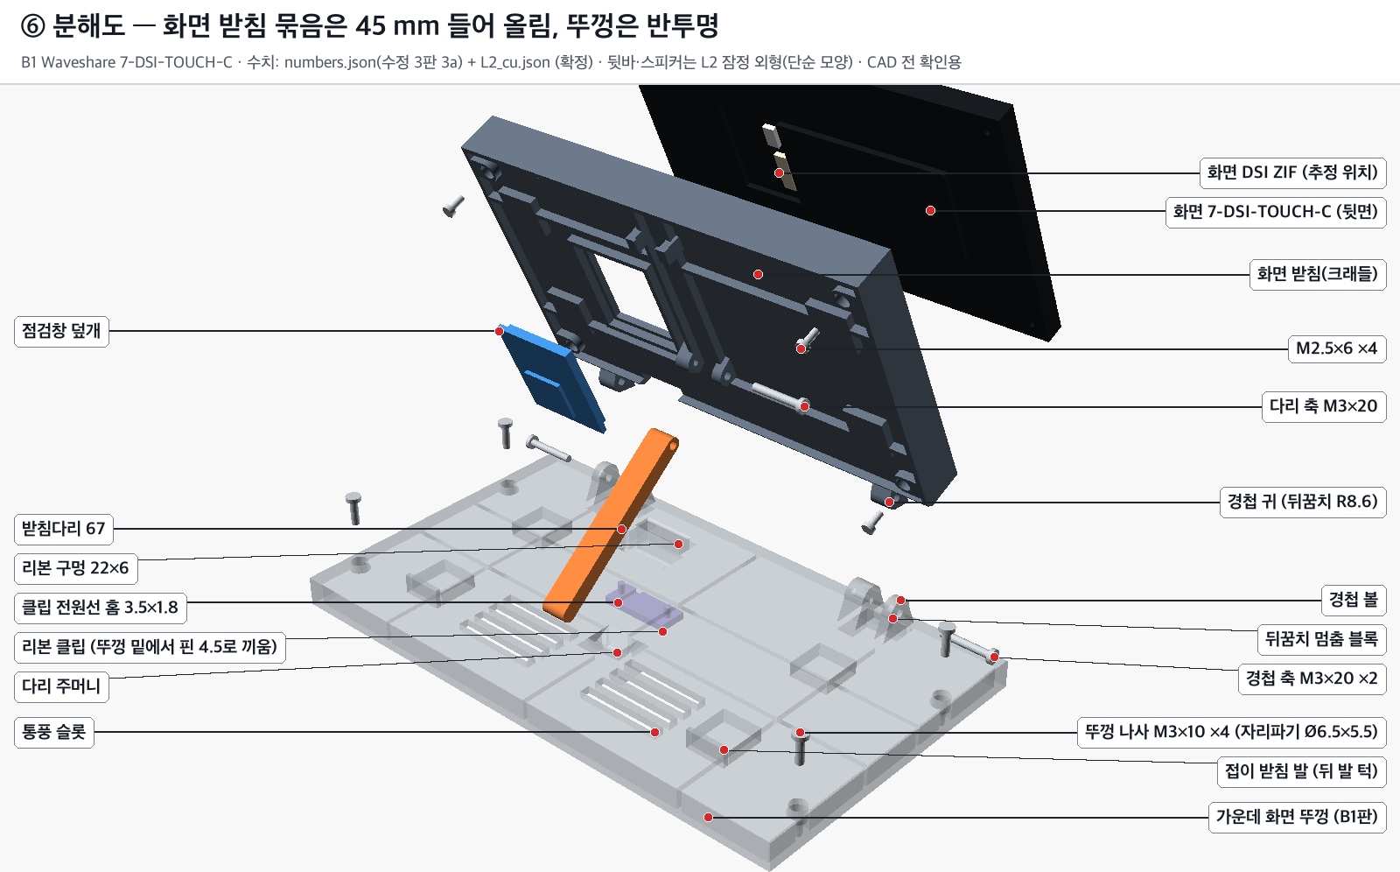
hardware/mechanical/touchscreen/rev3/model3d/renders/06_분해도.png
