WongyuKoh/Toccata/hardware/mechanical/touchscreen/rev3/model3d/renders/07_3a_고친_곳_확대.png

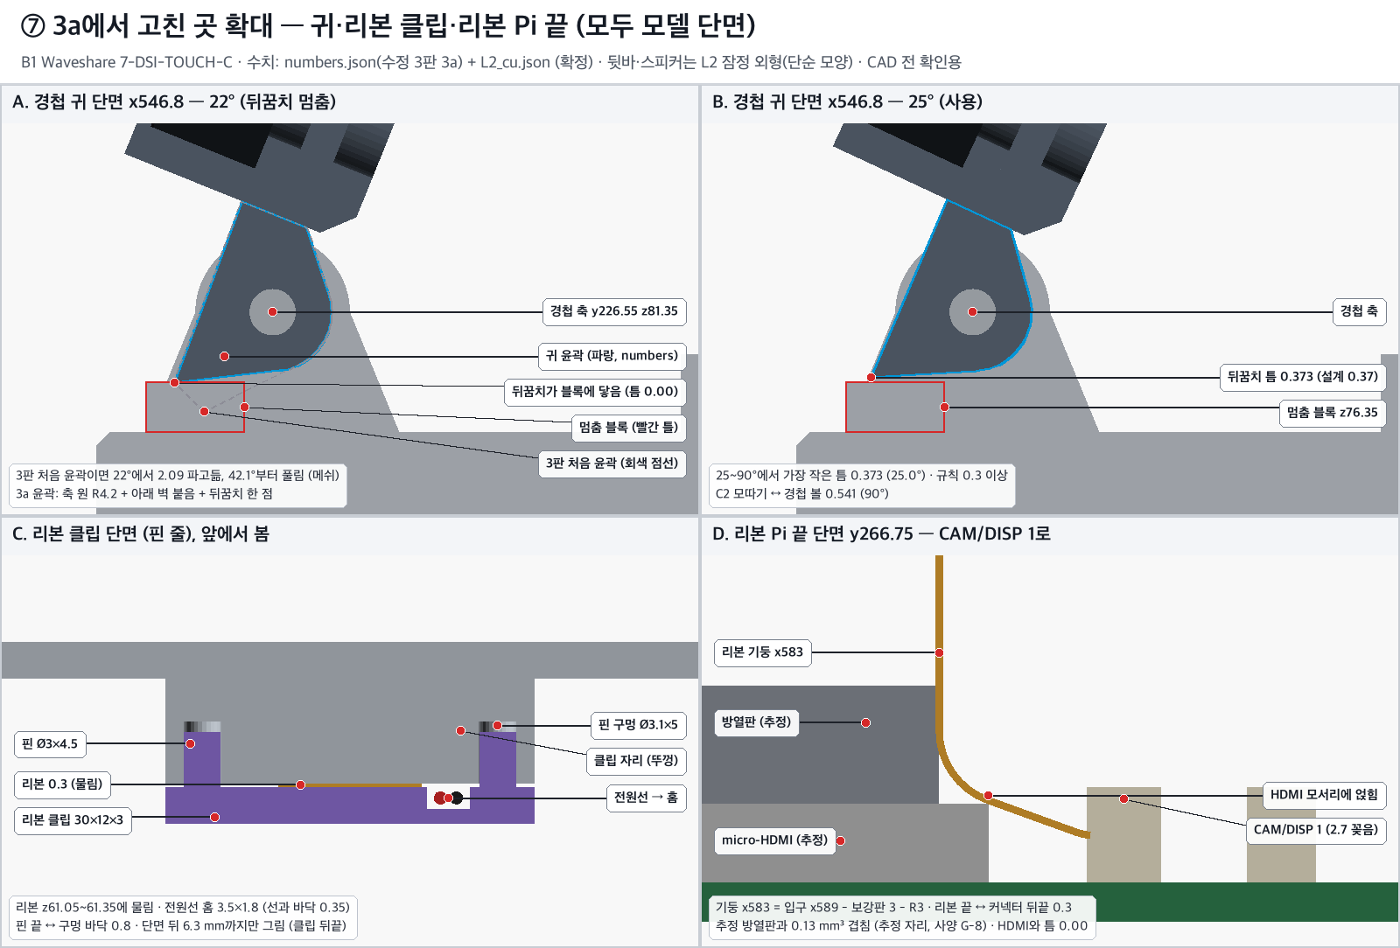
hardware/mechanical/touchscreen/rev3/model3d/renders/07_3a_고친_곳_확대.png
