WongyuKoh/Toccata/hardware/mechanical/touchscreen/rev3/model3d/renders/08_3a_다리축·아래벽홈·뚜껑나사·확인표.png

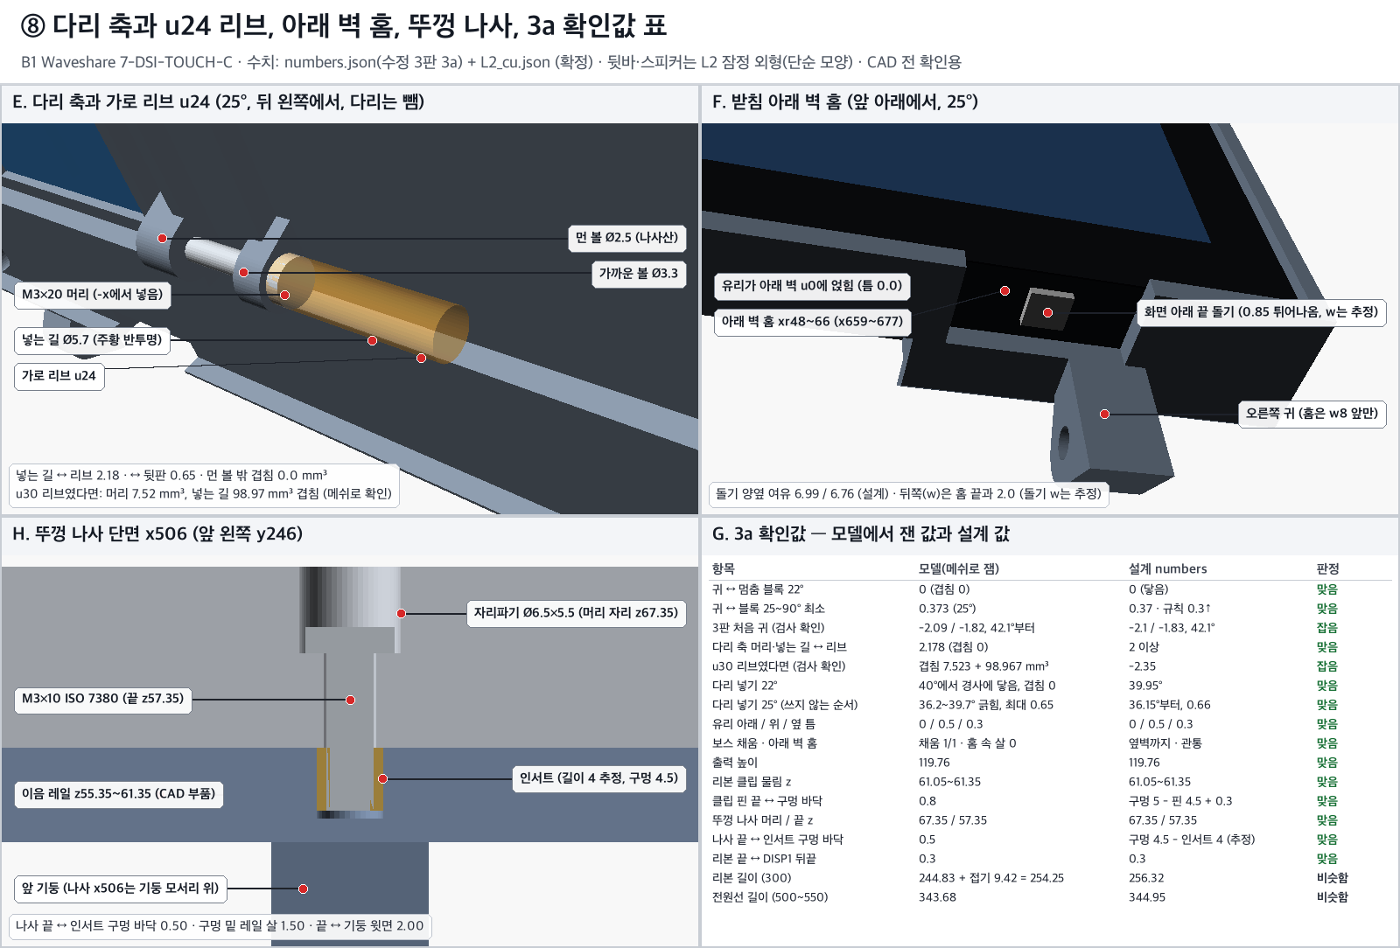
hardware/mechanical/touchscreen/rev3/model3d/renders/08_3a_다리축·아래벽홈·뚜껑나사·확인표.png
