WongyuKoh/Toccata/docs/report/toccata-purchase-list.xlsx

Sheet: 구매목록
Toccata v3.2 구매 목록 — 절감 선택 적용본
기준: 도면집 v10 절감안 탭 선택 코드(22개 부품 교체) · 가격은 2026-09-24~25 판매처 확인값(VAT·할인 반영, 원) · 구분: 기본 = 피아노에 들어가는 부품, 소모품 = 제작 중 쓰는 재료, 공구 = 제작용 공구
사용법: 파란 글씨(단위당 가격·수량·구매 O/X)만 고친다. 사지 않을 줄은 구매 칸을 X로 바꾸면 소계·최종 금액에서 빠진다(줄이 회색으로 바뀜). 예상 가격 = 단위당 가격 × 수량. 배송비는 판매처마다 따로 한 줄로 넣었다.
No | 부품명 | 단위당 가격(원) | 수량 | 용도 | 예상 가격(원) | 구매 링크 | 구분 | 구매(O/X) | 판매자 | 부품 코드 | 비고
■ 아이씨뱅큐
1 | Raspberry Pi 5 2GB (라즈베리파이 5 2GB Raspberry pi 5) | 119900원 | 1 | FluidSynth 소프트웨어 신스를 돌리고 USB-MIDI 8개(O1~O7, PED) 입력을 한 곳에서 병합하는 중앙 컴퓨터. 소리는 USB 동글(L51)로 내보낸다(R25: HAT 없음, GPIO 배선 없음) | 119900원 | https://www.icbanq.com/P016286897 | 기본 | O | 아이씨뱅큐 | L01
2 | TI DRV5055A2QLPG (TO-92-3 Linear Hall Effect Sensor, LCSC 경유) | 891원 | 100 | 건반마다 1개 + 예비 12. 표시면을 위로 눕혀 센서 바 포켓에 넣고 건반 밑 자석(Ø5×2)의 거리를 연속으로 잰다 | 89100원 | https://www.icbanq.com/P018076669 | 기본 | O | 아이씨뱅큐 (LCSC 해외 재고) | L20
3 | XHHD 육각너트 M3 강철 (LCSC C133377) | 11원 | 75 | 출력 육각 포켓·통로에 앉히는 암나사. 레일 클램프 4 + 척추 세트스크루 4 = 모듈당 8개, 끝 부속 7, 스피커 브래킷 4 → 67개 + 예비 8 | 825원 | https://www.icbanq.com/P015976209 | 기본 | O | 아이씨뱅큐 (LCSC 해외 재고) | L31
4 | Samsung CL31B104KCFNNNE (1206 100nF 100V X7R) | 44원 | 100 | 센서마다 1개(3V3–GND 디커플링, 센서 기판 아랫면) + PED 보드 | 4400원 | https://www.icbanq.com/P014968846 | 기본 | O | 아이씨뱅큐 (LCSC 해외 재고) | SE4 | 삼성 CL31B104KCFNNNE(100 V). 판매처 사진이 안 열려 품번으로 확인
5 | 핀헤더 소켓 1X40(2.54피치) | 528원 | 1 | 끝 부속 EXT 1×6 암 커넥터 2개(6+1핀 ×2)용 1줄. 4067 모듈은 암 헤더 없이 제어 기판에 직접 납땜(SE7) | 528원 | https://www.icbanq.com/P014161879 | 기본 | O | 아이씨뱅큐 | SE7
6 | 핀헤더 1×40 - 2.54MM(S/T) _ 11.5MM(1단몰드) | 165원 | 5 | 4067 모듈 7개 × (16+8)핀 = 168핀 + EXT 수 커넥터 12핀 = 180핀 → 1×40 5줄(200핀) | 825원 | https://www.icbanq.com/P005666127 | 기본 | O | 아이씨뱅큐 | SE7 | 모듈에 수 헤더가 들어 있으면 줄여도 된다
7 | [BC256] Coms 스테레오 케이블 3M AUX 3극 Stereo 3.5 M/M 고급포장 | 2860원 | 1 | 댐퍼 페달 신호선. 한쪽 플러그를 잘라 페달 안 홀센서에 납땜(팁 = 출력, 링 = 3V3, 슬리브 = GND)하고, 다른 쪽은 CU의 PJ-313 잭(L15의 두 번째)에 꽂는다 | 2860원 | https://www.icbanq.com/P004711396 | 기본 | O | 아이씨뱅큐 | L50
8 | XH-A232 (HW-404) TPA3110 2채널 앰프 보드 (제노 HAM6104) | 2750원 | 1 | 좌우 스피커(L07)를 울리는 D급 앰프. 20 V 버스(PD 트리거 L57 → 퓨즈 → 스위치)에서 8 Ω 채널당 약 21 W. 입력은 CU 트레이의 앰프 입력 잭(L15 ③)에서 받는다 | 2750원 | https://www.icbanq.com/P017179248 | 기본 | O | 아이씨뱅큐 (제노) | L53
9 | Monolithic Capacitor 1uF X7R 50V (리드형 적층 세라믹) | 133원 | 5 | 앰프 입력의 저음 차단(고역 통과) 필터. 채널마다 1 µF 2개를 병렬(2 µF)로 직렬에 넣고 1 kΩ 풀다운(L29)과 묶어 약 80 Hz 아래를 6 dB/옥타브로 줄인다(D18) | 665원 | https://www.icbanq.com/P014159115 | 기본 | O | 아이씨뱅큐 (동신전자) | L56
10 | 100W QC PD 트리거 디코이 고정출력 모듈 5V-20V (HAM6113, HUSB238) | 4950원 | 1 | 피아노의 전원 입력(USB-C). 벽 충전기(L62)나 보조배터리와 PD로 협상해 20 V를 받아 퓨즈(L60) → 스위치(L59) → 20 V 버스로 보낸다. I/O 판 안쪽 포켓에 끼워 USB-C 구멍이 밖을 향한다(R28) | 4950원 | https://www.icbanq.com/P017179277 | 기본 | O | 아이씨뱅큐 (제노) | L57
11 | 200W XL4016 DC-DC 강압 컨버터 모듈 IN 4-40V OUT 1.25-36V 5A (HAM6415, XH-M401) | 5170원 | 1 | 20 V 버스 → 5.1 V. Pi 5(USB-C 전원선 C24)와 USB 허브(L17, DC 잭)에 전원을 준다. Pi에는 이 5 V만 들어간다(D16). CU 트레이 보스에 M3×10(L34) 4개로 고정(R28) | 5170원 | https://www.icbanq.com/P017179502 | 기본 | O | 아이씨뱅큐 (제노) | L58
12 | 순간접착제 (814-2010) — V-tech 강력 순간접착제 5g (VT-041) | 1100원 | 1 | 센서 자석 Ø5×2(L21)·뚜껑 자석 Ø8×3(L65)을 포켓에 압입한 뒤 한 방울(리프 근처 사용 금지) | 1100원 | https://www.icbanq.com/P015309984 | 소모품 | O | 아이씨뱅큐 (크레텍) | ME8 | 록타이트 401 20 g 대신(ME8). 성분·점도 표기는 페이지에 없다
13 | 배송비 — 아이씨뱅큐 | 0원 | 1 | 배송비 | 0원 |  | 기본 | O |  |  | 자동 계산: 공급가(VAT 제외) 5만원 미만이면 2,700원, 이상이면 무료
 | 아이씨뱅큐 소계 |  |  |  | 233073원
■ 엘레파츠
14 | [화성고무] 피스고무발 / 28x5 (RUB-E2) | 583원 | 20 | 스피커 파트 2개(각 4개)와 가운데 유닛(6개)의 고무발 14개. 출력 받침 4 mm와 함께 뒷바를 22 mm 띄워 아래 앞쪽을 케이블 통로로 만든다(R27). 본체와 스피커 진동을 떼어 놓는다(D15) | 11660원 | https://www.eleparts.co.kr/goods/view?no=16628292 | 기본 | O | 엘레파츠 | L14
15 | [BSUN] PJ-313 3.5Ф 스테레오잭 (이어폰잭) | 198원 | 3 | ① 왼쪽 볼 앞면 헤드폰 잭: 동글(L51) 출력이 팁·링으로 들어오고 팁·링 노멀 접점이 앰프 쪽으로 나간다. 헤드폰을 꽂으면 노멀 접점이 떨어져 스피커가 기계적으로 끊긴다(R15) ② I/O 판의 댐퍼 페달 잭(R24) ③ CU 트레이의 앰프 입력 잭: 선 ②의 플러그를 받아 저음 차단 RC를 거쳐 앰프(L53) 입력으로 보낸다(R26, 파트 분리) | 594원 | https://www.eleparts.co.kr/goods/view?no=67811 | 기본 | O | 엘레파츠 | L15
16 | [ABCO] CFR 1/4W 5% 탄소피막 저항 1kΩ (10개 단위) | 25원 | 10 | 앰프 입력 풀다운 겸 저음 차단 필터(1 kΩ ×2), 필요하면 입력 감쇠(직렬 1 kΩ ×2), 페달 입력 직렬 1 kΩ | 250원 | https://www.eleparts.co.kr/goods/view?no=10911 | 기본 | O | 엘레파츠 | L29 | 10개 단위 판매(M.O.Q 10)
17 | [ABCO] CFR 1/4W 5% 탄소피막 저항 10kΩ (10개 단위) | 25원 | 10 | 예비(R25로 헤드폰 감지 회로가 빠져 설계상 필수는 아니다) | 250원 | https://www.eleparts.co.kr/goods/view?no=10951 | 기본 | O | 엘레파츠 | L29 | 10개 단위 판매(M.O.Q 10)
18 | [ABCO] CFR 1/4W 5% 탄소피막 저항 100kΩ (10개 단위) | 25원 | 10 | 페달 입력 풀다운 100 kΩ | 250원 | https://www.eleparts.co.kr/goods/view?no=10993 | 기본 | O | 엘레파츠 | L29 | 10개 단위 판매(M.O.Q 10)
19 | [ABCO] CFR 1/4W 5% 탄소피막 저항 100Ω (10개 단위) | 25원 | 10 | 예비·시험용 | 250원 | https://www.eleparts.co.kr/goods/view?no=10873 | 기본 | O | 엘레파츠 | L29 | 10개 단위 판매(M.O.Q 10)
20 | [Coms] IH190 USB-C(F) → USB-A(M) 변환 젠더 좌향 꺾임 | 1700원 | 1 | Apple 동글(USB-C 수)을 Pi 5 USB-A 포트에 꽂는 젠더 | 1700원 | https://www.eleparts.co.kr/goods/view?no=11043038 | 기본 | O | 엘레파츠 | L52
21 | [ZX Electronics] KCD1-101A BLACK I/O 로커 스위치 (2P ON-OFF, 6A 250VAC / 10A 125VAC) | 385원 | 1 | 피아노 전원 스위치. PD 트리거·퓨즈 뒤 20 V 쪽에 넣어 앰프와 강압 모듈을 함께 켜고 끈다. I/O 판의 출력 구멍에 끼운다(스냅인, R28) | 385원 | https://www.eleparts.co.kr/goods/view?no=32569 | 기본 | O | 엘레파츠 | L59
22 | [Coms] BU914 원형 휴즈 홀더 (5×20 mm, 인라인) | 1110원 | 1 | 20 V 버스 보호 퓨즈 홀더. PD 트리거 출력 + 선에 끼워 배선 단락 때 선이 타지 않게 한다 | 1110원 | https://www.eleparts.co.kr/goods/view?no=3237821 | 기본 | O | 엘레파츠 | L60
23 | [LITTELFUSE] 0218005.MXP 5 A 지연형 퓨즈 5×20 mm | 110원 | 5 | 홀더에 넣는 5 A 지연형 퓨즈 1개 + 예비 4개(R28) | 550원 | https://www.eleparts.co.kr/goods/view?no=12766820 | 기본 | O | 엘레파츠 | L60 | 최소 5개
24 | [AMASS] XT30U-M 수 커넥터 18AWG 10cm 실리콘 와이어 | 1760원 | 2 | 앰프 쪽 스피커선 커넥터(좌우 2개). 통로 양 끝으로 나온 선에 납땜 | 3520원 | https://www.eleparts.co.kr/goods/view?no=12779720 | 기본 | O | 엘레파츠 | L61
25 | [AMASS] XT30U-F 암 커넥터 18AWG 10cm 실리콘 와이어 | 1760원 | 2 | 스피커 쪽 커넥터(좌우 2개). 스피커 파트 앞판 아래로 나온 선에 납땜 | 3520원 | https://www.eleparts.co.kr/goods/view?no=12779721 | 기본 | O | 엘레파츠 | L61
26 | [NA993] Coms USB 3.1 Type C 케이블 1M USB 2.0 A to C타입 White | 1620원 | 8 | 모듈 7개 + PED 보드 → 허브 USB 8가닥. 허브에 꽂힌 채 뒷바 아래 케이블 통로에 두고, 설치 때 모듈 쪽만 꽂는다(R27). 몰드 ≤12.5×7.5×25라 통로(높이 22)에 들어간다 | 12960원 | https://www.eleparts.co.kr/goods/view?no=4313490 | 소모품 | O | 엘레파츠 | C04
27 | [EUNSUNG] Flat Data Cable 2651-16P (1m단위) | 1529원 | 2 | 센서 기판 → 제어 기판 리본(OUT 12 + 3V3 + GND, 약 180mm ×7), O1·O7 EXT 6심 연장선, 끝 부속 선 | 3058원 | https://www.eleparts.co.kr/goods/view?no=425 | 소모품 | O | 엘레파츠 | C05
28 | [EUNSUNG] Flat Data Cable 2651-16P (1m단위) | 1529원 | 1 | 점퍼 단선 대신 리본 가닥으로: 센서 기판 3V3·GND 버스, 제어 기판 링크(SIG·S0~S3·EN), ID 브리지, 기판 배선(듀폰 점퍼 X1 대체) | 1529원 | https://www.eleparts.co.kr/goods/view?no=425 | 소모품 | O | 엘레파츠 | SE12 | C05와 같은 품목을 1 m 더 산다. 주문 때 C05와 합쳐 3 m로 담아도 된다
29 | [엘레파츠] 열수축튜브 530세트 - 프라스틱케이스 | 6600원 | 1 | EXT 헤더 커넥터, 선 이음, 페달 잭 뒤쪽 절연 | 6600원 | https://www.eleparts.co.kr/goods/view?no=8170311 | 소모품 | O | 엘레파츠 | C10
30 | [KzPton] 캡톤테이프 10mm폭x33m | 4059원 | 1 | RP2040-Zero 아래 절연(캡톤 1장), 기판 아랫면 절연 | 4059원 | https://www.eleparts.co.kr/goods/view?no=557 | 소모품 | O | 엘레파츠 | C11
31 | 티테크놀로지 케이블타이, 100개 [소/100mm] [블랙] [T-C2510B] | 438원 | 1 | USB 케이블을 뒷벽 고리에 묶어 당김 방지, EXT 커넥터 고정 · 케이블 통로 안 USB 8가닥 묶음(R27) | 438원 | https://www.eleparts.co.kr/goods/view?no=9100003 | 소모품 | O | 엘레파츠 | C12
32 | [케이블스토어] 프리즘 국산 스피커케이블 50C 16AWG, 7M [블랙/PRS-50B07] | 14300원 | 1 | 앰프(L53) → 통로 → XT30 수(L61) 2쌍(좌우 각 약 0.6 m) + 스피커 파트 안 유닛 → XT30 암(각 약 0.3 m) + 20 V 전원선(PD 트리거 → 퓨즈 → 스위치 → 앰프·강압 모듈, 약 1 m) | 14300원 | https://www.eleparts.co.kr/goods/view?no=18388615 | 소모품 | O | 엘레파츠 | C13
33 | [AV0176] Coms 스테레오 케이블 1.5M AUX 3극 Stereo 3.5 M/M | 1710원 | 2 | ① 동글(L51) → 왼쪽 볼 헤드폰 잭(L15 ①) ② 헤드폰 잭 노멀 접점 → CU 트레이 앰프 입력 잭(L15 ③). 두 선 모두 CU 쪽 플러그를 남기고 끝 부속 쪽을 잘라 잭에 납땜한다(선이 끝 부속에 붙어 다니고 CU에서 뽑는다, R26) | 3420원 | https://www.eleparts.co.kr/goods/view?no=2925673 | 소모품 | O | 엘레파츠 | C14
34 | [MachLink] USB-C to C PD 60W 초고속충전 케이블, ML-CPD606 [블랙/0.6m] | 1440원 | 1 | 보조배터리 → 피아노 USB-C 입력. 보조배터리 칸에서 낮은 칸막이 위 → CU 칸 → I/O 판 선 통과 구멍으로 빼서 입력(L57)에 꽂는다(R28) | 1440원 | https://www.eleparts.co.kr/goods/view?no=17806172 | 소모품 | O | 엘레파츠 | C22
35 | [MachLink] USB-C to C PD 60W 초고속충전 케이블, ML-CPD62 [블랙/2m] | 2670원 | 1 | 벽 충전기(L62) → 피아노 USB-C 입력(L57). 제작 중에는 인두(T01) 전원선으로도 쓴다(R28) | 2670원 | https://www.eleparts.co.kr/goods/view?no=17806170 | 소모품 | O | 엘레파츠 | C23
36 | [MAXTEK] 맥스텍 USB C타입 제작용 케이블 2선 Type-C Male(숫) DIY PD 전원 [MT666] | 1190원 | 1 | 5.1 V 강압 모듈(L58) 출력 → Pi 5 USB-C 전원 입력. 벗겨진 두 선(빨강 +, 검정 −)을 강압 모듈 출력 단자에 물린다(R28) | 1190원 | https://www.eleparts.co.kr/goods/view?no=17358965 | 소모품 | O | 엘레파츠 | C24
37 | [NAVI] 종이 양면테이프, 백색/48mm/6m | 1080원 | 1 | EVA 바닥 시트와 비접착 3T 펠트를 프레임에 붙인다 | 1080원 | https://www.eleparts.co.kr/goods/view?no=17897439 | 소모품 | O | 엘레파츠 | ME9 | 2롤 → 1롤(ME9)
38 | [YUN FANG] 유연납 0.8mm 50g | 3850원 | 1 | 모듈당 약 200점, 전체 약 1,500점 손 납땜. 코어 플럭스만 쓴다(플럭스 펜 생략, CT22) | 3850원 | https://www.eleparts.co.kr/goods/view?no=12755646 | 소모품 | O | 엘레파츠 | CT5 | 모자라면 같은 상품을 더 산다(이 주문에 함께 넣으면 배송비 없음)
39 | [Coms] [NT117] Coms 디지털 테스트기 (DT-832, 9개 항목) | 7600원 | 1 | 페달 T–R–S 저항 측정, 잭 핀 확인, 통전 검사, 허브 역급전(Pi 5V 핀 0V) 확인 | 7600원 | https://www.eleparts.co.kr/goods/view?no=6779159 | 공구 | O | 엘레파츠 | CT11
40 | [Prokit] [CP-301G] PROKIT 정밀 스트리퍼 | 4500원 | 1 | 리본·단선·점퍼선 등 가는 선(AWG 20~30) 피복 벗기기 | 4500원 | https://www.eleparts.co.kr/goods/view?no=3787704 | 공구 | O | 엘레파츠 | CT21
41 | [JAKEMY] JM-CT2-2 5인치 니퍼 | 3960원 | 1 | 센서 리드·헤더 핀 자르기, 출력물 다듬기. 16AWG 스피커선 피복도 니퍼 날로 칼집을 내 벗긴다(CT16) | 3960원 | https://www.eleparts.co.kr/goods/view?no=7663472 | 공구 | O | 엘레파츠 | CT13
42 | [블루텍] 버니어캘리퍼(경제형) NA530-200 (200×0.05) | 13400원 | 1 | 리프 두께·훅 높이·164.5 수축 시편·세트스크루 돌출(1.5±0.05)·펠트 두께 측정 | 13400원 | https://www.eleparts.co.kr/goods/view?no=16549359 | 공구 | O | 엘레파츠 | CT12
43 | 배송비 — 엘레파츠 | 0원 | 1 | 배송비 | 0원 |  | 소모품 | O |  |  | 자동 계산: 공급가(VAT 제외) 6만원 미만이면 3,000원, 이상이면 무료
 | 엘레파츠 소계 |  |  |  | 110093원
■ 11번가
44 | 삼미스피커(SAAT) CW-100B25 4인치 풀레인지 8Ω 25W (KS 인증) | 9600원 | 2 | 좌우 스피커 유닛 2개(R25: 서브 없음). 스피커 파트(오꾸메 밀폐 상자, 내부 5.05 L)의 출력 앞판에 끼워 연주자 쪽을 향하게 한다. 앰프(L53)가 채널당 약 21 W(20 V)를 준다 | 19200원 | https://www.11st.co.kr/products/1565354988 | 기본 | O | 세운상가새한음향 | L07
45 | 두유레디 구름솜 300g (100% 국내산 할로우화이버) | 2700원 | 1 | 밀폐 스피커 상자 2개의 흡음재(상자당 40~60 g, 폴리필 대용) | 2700원 | https://www.11st.co.kr/products/2325598213 | 기본 | O | 두유레디 | L12
46 | 에바폼 EVA 컬러 고밀도 칼라스펀지 3T (E-210 검정, 330×490) | 2100원 | 3 | 모듈 7개·끝 부속 2개 바닥 전체에 붙이는 3T 시트(164×211 한 장씩). 남는 조각은 스피커 유닛 가스켓과 가운데 유닛 ↔ 스피커 파트 맞닿는 면의 띠(R26) | 6300원 | https://www.11st.co.kr/products/7591566666 | 기본 | O | 상우아트 | MEV1 | 상우아트 묶음배송
47 | [대원] 얇은 칼라펠트지 H 두께0.5mm 접착 30x45cm (H-20 검정) | 1500원 | 1 | 가이드 탭 양옆 부싱(0.5T, 모듈당 24조각)과, 2겹으로 겹친 뒤 스톱 펠트(1T, y138~144) | 1500원 | https://www.11st.co.kr/products/8517880969 | 기본 | O | 상우아트 | MEV1 | EVA와 같은 판매자라 묶음배송
48 | 스텐 유두 렌치볼트 M3 × 40mm (SUS304) | 130원 | 34 | 백건·흑건 척추를 레일 너트에 함께 조이는 클램프 나사(모듈당 4, 끝 부속 2씩). 굿나잇몰 묶음배송 3,500원을 이 줄에 넣었다 | 4420원 | https://www.11st.co.kr/products/4236198413 | 기본 | O | 굿나잇몰 | L32
49 | 스텐 무두 렌치볼트 M3 × 10mm (평끝 세트스크루) | 60원 | 40 | 백건·흑건 척추의 무게 조절 세트스크루(모듈당 4, 끝 부속 3). 1/8회전 = 백 2.4 g / 흑 1.8 g | 2400원 | https://www.11st.co.kr/products/4236198413 | 기본 | O | 굿나잇몰 | L33
50 | 스텐 유두 렌치볼트 M3 × 10mm | 60원 | 50 | 센서 바·센서 기판을 왼쪽 받침 기둥에 고정(모듈당 2, 끝 부속 포함)하고, CU 트레이 부품(앰프 4·강압 모듈 4·PD 트리거 2·앰프 입력 잭 기판 2·퓨즈 홀더 2)과 토글 래치 2개(각 4, L64)를 출력 보스·받침에 고정한다. PETG 구멍에 직접 탭을 내며 조인다 | 3000원 | https://www.11st.co.kr/products/4236198413 | 기본 | O | 굿나잇몰 | L34
51 | 스텐 유두 렌치볼트 M3 × 6mm | 40원 | 20 | 제어 기판을 출력 스탠드오프에 고정 — 대각 2곳만 나사, 나머지 2곳은 출력 위치 핀(v3.2) | 800원 | https://www.11st.co.kr/products/4236198413 | 기본 | O | 굿나잇몰 | L35
52 | 스텐 와셔 M4x9x0.5T | 10원 | 60 | 클램프 나사 머리 아래 Ø9 와셔(흑건 척추 카운터보어 Ø9.5×1.0 안, 32개) + 고무발 고정 피스 와셔(14개, R26) | 600원 | https://www.11st.co.kr/products/4236198413 | 기본 | O | 굿나잇몰 | L36
53 | 스텐 유두 렌치볼트 M2.5 × 6mm | 200원 | 6 | Pi 5를 CU 트레이의 출력 보스 4개(Ø2.2 탭 구멍)에 바로 조이는 나사(4개 + 예비 2). R26으로 황동 스탠드오프(L37)가 빠졌다(비용 절감안 CP7) | 1200원 | https://www.11st.co.kr/products/4236198413 | 기본 | O | 굿나잇몰 | L47
54 | 스텐 둥근머리 직결피스 8호(Ø4.2) 13mm | 40원 | 40 | 뒷바 출력 부품(도브테일 블록·CU 트레이·I/O 판·보조배터리 받침·콤 받침·XT30 받침)을 합판 면에 고정 | 1600원 | https://www.11st.co.kr/products/4353471537 | 기본 | O | 굿나잇몰 | L49 | 같은 상품의 옵션. 굿나잇몰 묶음배송(주문 화면에서 묶음 여부 확인)
55 | 스텐 둥근머리 직결피스 8호(Ø4.2) 16mm | 50원 | 8 | CW-100B25 유닛 8홀을 PETG 앞판에 고정 | 400원 | https://www.11st.co.kr/products/4353471537 | 기본 | O | 굿나잇몰 | L49 | 같은 상품의 옵션. 굿나잇몰 묶음배송(주문 화면에서 묶음 여부 확인)
56 | 스텐 둥근머리 직결피스 8호(Ø4.2) 19mm | 50원 | 8 | PETG 그릴 8곳 고정 | 400원 | https://www.11st.co.kr/products/4353471537 | 기본 | O | 굿나잇몰 | L49 | 같은 상품의 옵션. 굿나잇몰 묶음배송(주문 화면에서 묶음 여부 확인)
57 | 스텐 둥근머리 직결피스 8호(Ø4.2) 25mm | 60원 | 14 | 고무발 14개 고정 | 840원 | https://www.11st.co.kr/products/4353471537 | 기본 | O | 굿나잇몰 | L49 | 같은 상품의 옵션. 굿나잇몰 묶음배송(주문 화면에서 묶음 여부 확인)
58 | 텅스텐 퍼티 소프트 싱커 무게추 (낚시용, 22 g) | 8750원 | 1 | 무거운 건반만 낮추는 건반별 무게 미세 조정(필요할 때만, 백 ≤6 g·흑 ≤2.5 g) | 8750원 | https://www.11st.co.kr/products/9579455646 | 소모품 | O | 골드그로브 | ME14
59 | 오공 201 205 본드 800g 목공용본드 (옵션: 오공 205본드 800g) | 2840원 | 1 | 스피커 상자 2개(5.05 L ×2)와 가운데 유닛(오꾸메 11장) 접합, 출력 앞판 둘레 밀봉. 합판은 본드로만 붙이고 마스킹테이프로 눌러 굳힌다(드릴 없음) | 2840원 | https://www.11st.co.kr/products/1874655675 | 소모품 | O | 오공 본드 판매처 | SP6 | 옵션에서 "오공 205본드 800g"을 고른다(201은 다른 제품)
60 | 육각 렌치 1.5mm (볼트 상품 옵션) | 600원 | 1 | 세트스크루 무게 조절(위에서 Ø3.2 구멍으로) | 600원 | https://www.11st.co.kr/products/4236198413 | 공구 | O | 굿나잇몰 | T11
61 | 육각 렌치 2.5mm (볼트 상품 옵션) | 600원 | 1 | M3 렌치볼트 조이기 | 600원 | https://www.11st.co.kr/products/4236198413 | 공구 | O | 굿나잇몰 | T11
62 | 배송비 — 세운상가새한음향 | 4000원 | 1 | 배송비 | 4000원 |  | 기본 | O |  | L07 | 도면집 부품표 값
63 | 배송비 — 두유레디 | 3000원 | 1 | 배송비 | 3000원 |  | 기본 | O |  | L12 | 도면집 부품표 값
64 | 배송비 — 상우아트 | 3000원 | 1 | 배송비 | 3000원 |  | 기본 | O |  | MEV1 | 도면집 부품표 값 (묶음배송 1회분)
65 | 배송비 — 오공 본드 판매처 | 2500원 | 1 | 배송비 | 2500원 |  | 소모품 | O |  | SP6 | 도면집 부품표 값
66 | 배송비 — 굿나잇몰 | 3500원 | 1 | 배송비 | 3500원 |  | 기본 | O |  | L32 | 도면집 부품표 값 (묶음배송 1회분)
 | 11번가 소계 |  |  |  | 74150원
■ 메카솔루션
67 | 라즈베리파이5 방열판 / 5B 전용 / 알루미늄 (4개 세트) | 1400원 | 1 | SoC·메모리·RP1·이더넷 칩의 열을 뺀다. 팬 없는 저높이 스티커형(R25 이후 위에 HAT이 없어 높이 제한도 없다) | 1400원 | https://www.mechasolution.com/goods/goods_view.php?goodsNo=605179 | 기본 | O | 메카솔루션 | L02
68 | PCB기판/양면기판/에폭시/프로토보드 (12x18cm) | 2200원 | 2 | 센서 기판(162×15.24mm, 6행) 띠를 잘라 낸다. 1장에서 약 6띠 → 2장으로 모듈 7개 + 끝 부속 2개분 | 4400원 | https://www.mechasolution.com/goods/goods_view.php?goodsNo=540645 | 기본 | O | 메카솔루션 | L22
69 | PCB기판/양면기판/에폭시/프로토보드 (5x7cm) | 520원 | 8 | 모듈 제어 기판(RP2040-Zero + 4067) 7장 + PED 보드 1장. 자투리는 PJ-313 받침 | 4160원 | https://www.mechasolution.com/goods/goods_view.php?goodsNo=329798 | 기본 | O | 메카솔루션 | SE8 | L02·L22와 같은 주문
70 | 배송비 — 메카솔루션 | 3000원 | 1 | 배송비 | 3000원 |  | 기본 | O |  | L02 | 도면집 부품표 값 (묶음배송 1회분)
 | 메카솔루션 소계 |  |  |  | 12960원
■ 파츠파츠 직영몰
71 | (PP-A799-2) 라즈베리 파이 피코 PICO RP2040-ZERO | 3300원 | 8 | 모듈마다 1개(O1~O7) + 페달 보드 1개, 예비 없음. 4067 먹스를 스캔해 속도를 계산하고 USB-MIDI 장치('Toccata O1'~'O7', 'Toccata PED')가 된다. 캐스털레이션으로 제어 기판에 직접 납땜 | 26400원 | https://parts-parts.co.kr/product/detail.html?product_no=2383 | 기본 | O | 파츠파츠 (동신전자) | SEV2 | 예비 없음(SEV2)
72 | (PP-A324) 16채널 아날로그/디지털 멀티플렉서 모듈 | 500원 | 7 | 모듈마다 1개, 예비 없음. 홀센서 12개(C0~C11)와 끝 부속 EXT 4채널(C12~C15)을 RP2040 ADC 한 채널로 읽는다; 제어 기판에 직접 납땜(SE7) | 3500원 | https://parts-parts.co.kr/product/detail.html?product_no=303 | 기본 | O | 파츠파츠 (동신전자) | SEV2 | 합배송
73 | 배송비 — 파츠파츠 (동신전자) | 3000원 | 1 | 배송비 | 3000원 |  | 기본 | O |  | SEV2 | 도면집 부품표 값 (묶음배송 1회분)
 | 파츠파츠 직영몰 소계 |  |  |  | 32900원
■ Bambu Lab KR 공식 스토어
74 | Bambu Lab PETG Basic 화이트(30106) 스풀 포함 1kg | 16150원 | 1 | 백건 콤 7개 + 끝 부속 백건 콤 + 흰색 리프 쿠폰 + 센서 바(남는 흰색으로) | 16150원 | https://kr.store.bambulab.com/products/petg-basic | 소모품 | O | Bambu Lab | CT2 | 4개 이상 구매 시 15% 할인가
75 | Bambu Lab PETG Basic 화이트(30106) 리필 1kg | 12750원 | 1 | 흰색 두 번째 1 kg. 첫 흰색 스풀을 다 쓴 뒤 그 스풀에 끼운다 | 12750원 | https://kr.store.bambulab.com/products/petg-basic | 소모품 | O | Bambu Lab | CT2 | 4개 이상 구매 시 15% 할인가
76 | Bambu Lab PETG Basic 블랙(30105) 스풀 포함 1kg | 16150원 | 3 | 흑건 콤·A#0 콤·흑색 리프 쿠폰·방진 브래킷 + 프레임 7개·끝 부속·뒤 커버·스피커 앞판·CU 트레이·I/O 판·뒷바 받침(R26) + 시편 | 48450원 | https://kr.store.bambulab.com/products/petg-basic | 소모품 | O | Bambu Lab | CT2 | 검정 리필은 품절이라 스풀 포함. 4개 이상 15% 할인가
77 | Bambu Lab PETG Basic 스풀 포함 1kg 추가 (흰색 또는 검정) | 16150원 | 1 | R26 출력물 증가분(가운데 유닛 부품, 보관함 등) — 도면집 자동 보정 항목 | 16150원 | https://kr.store.bambulab.com/products/petg-basic | 소모품 | O | Bambu Lab | CT2+ | 색은 출력 순서를 보고 정한다. 동전 받침(CT15)도 여기서 출력
78 | 배송비 — Bambu Lab | 0원 | 1 | 배송비 | 0원 |  | 소모품 | O |  |  | 자동 계산: 7만원 이상 무료배송(미만 3,000원 가정). 15% 할인은 4개 이상 구매 조건
 | Bambu Lab KR 공식 스토어 소계 |  |  |  | 93500원
■ 다나와 (최저가 판매처)
79 | SanDisk micro SD Ultra 2022 32GB (SDSQUA4-032G-GN6MA) | 15490원 | 1 | Raspberry Pi OS Lite, FluidSynth, Salamander 음원(SF2 296MB)을 담는 부팅 카드 | 15490원 | https://prod.danawa.com/info/?pcode=20358155 | 기본 | O | 다나와 최저가 판매처 | L03 | 다나와에서 최저가 판매처로 이동해 구매. 판매처·가격이 바뀔 수 있다
80 | 이지넷유비쿼터스 NEXTU 유우젠 710U3 (10포트/USB 3.0, 유전원) | 30700원 | 1 | 모듈 7개 + PED의 USB-MIDI를 Pi 5 USB 한 포트로 모은다. 전원은 본체 5.1 V 강압 모듈(L58)에서 DC 잭으로 받는다(허브에 딸린 5 V 3 A 어댑터 선을 잘라 플러그 쪽을 쓴다). 길이 228 mm라 CU 칸(안폭 189)이 아니라 보조배터리 칸 뒤 벽에 둔다(R26·R28) | 30700원 | https://prod.danawa.com/info/?pcode=29865749 | 기본 | O | 다나와 최저가 (쿠팡 로켓배송) | L17 | 다나와에서 최저가 판매처로 이동해 구매
81 | 파워마스터 PD PPS 65W 3포트 GaN 접지형 충전기 PG65PDG2C1A (케이블미포함) | 19800원 | 1 | 벽 전원. 피아노 I/O 판의 USB-C 입력(L57)에 2 m C-C 선(C23)으로 잇는다. C1 또는 C2 포트 하나만 쓴다(두 포트를 함께 쓰면 45 W로 줄어 최대 음량에서 모자람). 제작 중에는 같은 충전기로 인두(T01)를 쓴다(R28) | 19800원 | https://prod.danawa.com/info/?pcode=59074565 | 기본 | O | 다나와 최저가 판매처 | L62 | 다나와에서 최저가 판매처로 이동해 구매
82 | 배송비 — 다나와 최저가 판매처 | 3000원 | 1 | 배송비 | 3000원 |  | 기본 | O |  | L03 | 도면집 부품표 값
 | 다나와 (최저가 판매처) 소계 |  |  |  | 68990원
■ 동진나무공장
83 | 무료배송 오꾸메 합판 400×1200×11.5mm 무료재단 | 17680원 | 1 | 스피커 파트 2개의 상자(외형 180×195×210, 내부 5.05 L)를 한 장에서 재단한다. 앞판(배플)은 PETG 출력이라 합판은 10장이다(도면 8의 재단도) | 17680원 | https://namugongjang.com/product/detail.html?product_no=1378 | 기본 | O | 동진나무공장 | L10 | 무료재단·무료배송. 재단도는 도면 8
84 | 무료배송 오꾸메 합판 600×1200×11.5mm 무료재단 | 22520원 | 1 | 가운데 유닛(894×195×100) 상자를 한 장에서 재단한다. 바닥 2·뚜껑 2·앞판·뒤판 2·끝판 2·칸막이 2 = 11장(도면 11의 재단도, R26) | 22520원 | https://namugongjang.com/product/detail.html?product_no=1378 | 기본 | O | 동진나무공장 | L63 | 무료재단·무료배송. 재단도는 도면 11
 | 동진나무공장 소계 |  |  |  | 40200원
■ 대건상사
85 | 초강력 네오디움 원형자석 5mm (Ø5×2.0T, N35) | 80원 | 100 | 건반 밑면 포켓에 압입하는 센서용 자석(S극 아래). 88 + 예비 12 | 8000원 | https://dgmagnet.com/product/%EC%B4%88%EA%B0%95%EB%A0%A5-%EB%84%A4%EC%98%A4%EB%94%94%EC%9B%80-%EC%9B%90%ED%98%95%EC%9E%90%EC%84%9D-5mm/13/ (https://dgmagnet.com/product/초강력-네오디움-원형자석-5mm/13/) | 기본 | O | 대건상사 | L21
86 | 초강력 네오디움 원형자석 8mm — 3.0T (Ø8×3mm, N35) | 160원 | 14 | 가운데 유닛 뚜껑 3장을 제자리에 붙여 두는 자석. 뚜껑마다 대각선 2곳에 뚜껑·받침 한 쌍씩(12개) + 예비 2. 출력 받침·뚜껑의 Ø8.2 포켓에 순간접착제(C18)로 붙인다(R26) | 2240원 | https://dgmagnet.com/product/detail.html?product_no=17 | 기본 | O | 대건상사 | L65 | 옵션 3.0T 선택
87 | 배송비 — 대건상사 | 2500원 | 1 | 배송비 | 2500원 |  | 기본 | O |  | L21 | 도면집 부품표 값
 | 대건상사 소계 |  |  |  | 12740원
■ 알씨뱅크
88 | 리튬폴리머 배터리 밸런스잭 연장선 5셀용 (JST-XH 6핀 수↔암, BU-LP 5S, 200mm) | 3000원 | 2 | 끝 부속 ↔ O1·O7 센서 선 6가닥을 잇는 잠금형 커넥터 2쌍. 연장선 가운데를 잘라 수·암 리드 1쌍으로 쓴다(압착 공구 불필요, R26) | 6000원 | https://www.rcbank.co.kr/shop/goods/goods_view.php?goodsno=29812 | 기본 | O | 알씨뱅크 | L66
89 | 배송비 — 알씨뱅크 | 3500원 | 1 | 배송비 | 3500원 |  | 기본 | O |  | L66 | 도면집 부품표 값
 | 알씨뱅크 소계 |  |  |  | 9500원
■ 철물박사
90 | 매미고리 1-20 (SUS304 스테인리스 토글 래치, 25×54mm) | 2400원 | 2 | 가운데 유닛 ↔ 스피커 파트를 뒷면에서 당겨 잠그는 토글 래치(이음마다 1개, 2개). 도브테일이 위치를 잡고 래치가 벌어지지 않게 한다(R26) | 4800원 | https://www.metaldiy.com/item/itemView.do?itemId=8806379117286 | 기본 | O | 철물박사 | L64
91 | 배송비 — 철물박사 | 3000원 | 1 | 배송비 | 3000원 |  | 기본 | O |  | L64 | 도면집 부품표 값
 | 철물박사 소계 |  |  |  | 7800원
■ 스튜디오분트
92 | [DHG] 3mm 대폭 양모펠트지 150×10cm | 5500원 | 1 | 백건 앞 스톱(y1.5~10.5)·흑건 스톱(y51.5~58.7) 펠트 3T와 훅 펠트 8×3 조각. 150cm 한 장에서 10mm 띠 약 15m | 5500원 | https://studiobunt.com/product/detail.html?product_no=2948 | 기본 | O | 스튜디오분트 | L39
93 | 배송비 — 스튜디오분트 | 3000원 | 1 | 배송비 | 3000원 |  | 기본 | O |  | L39 | 도면집 부품표 값
 | 스튜디오분트 소계 |  |  |  | 8500원
■ 피아노모아
94 | 듀로 피아노 페달 서스테인 (스위치형) — 홀센서 연속형 개조 | 8500원 | 1 | 댐퍼(서스테인) 페달 1개(R24). 안의 스위치를 떼고 예비 홀센서·자석을 달아 CC64를 0~127 연속값(하프페달)으로 보낸다 | 8500원 | https://pianomoa.com/product/%EB%93%80%EB%A1%9C-%ED%94%BC%EC%95%84%EB%85%B8-%ED%8E%98%EB%8B%AC-%EC%84%9C%EC%8A%A4%ED%85%8C%EC%9D%B8-%EC%A0%84%EA%B8%B0%EC%A2%8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 (https://pianomoa.com/product/듀로-피아노-페달-서스테인-전기종호환가능-전자키보드-디지털-피아노-댐퍼/4117/) | 기본 | O | 피아노모아 | L43
95 | 배송비 — 피아노모아 | 3000원 | 1 | 배송비 | 3000원 |  | 기본 | O |  | L43 | 도면집 부품표 값
 | 피아노모아 소계 |  |  |  | 11500원
■ Apple Store 온라인
96 | Apple USB-C–3.5mm 헤드폰 잭 어댑터 (MW2Q3KH/A) | 14900원 | 1 | USB DAC 겸 헤드폰 앰프. 젠더(L52)로 Pi 5 USB-A 포트에 직결해 소리를 아날로그로 바꾼다. 출력은 헤드폰 잭(L15)을 거쳐 앰프(L53)로 간다 | 14900원 | https://www.apple.com/kr/shop/product/mw2q3kh/a | 기본 | O | Apple | L51
 | Apple Store 온라인 소계 |  |  |  | 14900원
■ AliExpress
97 | 황동 라운드 디스크 8-20mm 1mm 두께 10pcs (Ø8×1, 품절이면 Ø10×1) | 2669원 | 4 | 세트스크루 끝이 PETG를 파고들지 않게 받치는 원판(레일 윗면 2 + 백건 척추 윗면 2 = 모듈당 4, 끝 부속 3, 총 31개) | 10676원 | https://ko.aliexpress.com/item/1005004333402862.html | 기본 | O | EasyNest Store | L38 | Ø8×1 옵션(품절이면 Ø10×1). 해외 배송, 환율에 따라 가격 변동
98 | FPV 비행 컨트롤러용 20개 M2/M3 실리콘 방진 그로밋 | 3040원 | 1 | 끝 부속 ↔ 스피커 파트 짧은 PETG 브래킷(40×17×6, R26)의 방진 그로밋(브래킷당 2개). 위치 고정용이고 스피커 무게는 바닥 고무발이 받친다 | 3040원 | https://ko.aliexpress.com/item/1005012184121268.html | 기본 | O | WorldBridge Store | L42 | 해외 배송, 환율에 따라 가격 변동
 | AliExpress 소계 |  |  |  | 13716원
■ PINE STORE (Pine64 공식)
99 | PINECIL – Smart Mini Portable Soldering Iron (Version 2) | 35200원 | 1 | 제어 기판·센서 기판 손 납땜(v3.2부터 인서트 열압입은 없다) | 35200원 | https://pine64.com/product/pinecil-smart-mini-portable-soldering-iron/ | 공구 | O | PINE STORE | T01 | 해외 직구. 배송비는 아래 줄
100 | PINECIL Portable Mini Stand | 2690원 | 1 | 인두 거치대 | 2690원 | https://pine64.com/product/pinecil-portable-mini-stand/ | 공구 | O | PINE STORE | T02
101 | USB TYPE-C TO USB TYPE-C SILICONE POWER CHARGING CABLE - 1 meter | 4720원 | 1 | Pinecil(T01)과 65 W PD 충전기(L62, 피아노 벽 전원)를 잇는 실리콘 C-C 케이블. 제작 중에는 피아노 충전기를 인두 전원으로 쓴다(R26) | 4720원 | https://pine64.com/product/usb-type-c-to-usb-type-c-silicone-power-charging-cable-1-meter-length/ | 공구 | O | PINE STORE | T03
102 | 배송비 — PINE STORE | 16200원 | 1 | 배송비 | 16200원 |  | 공구 | O |  | T01 | 도면집 부품표 값
 | PINE STORE (Pine64 공식) 소계 |  |  |  | 58810원
■ 무료 (다운로드)
103 | FluidSynth 2.6.1 | 0원 | 1 | 기본 피아노 엔진(0원). midi.autoconnect=1로 USB-MIDI 8개 입력을 한 곳에서 병합하고 ALSA hw:로 USB 동글(L51)에 출력, 출력 리미터 synth.limiter.active=1(D18) | 0원 | https://www.fluidsynth.org/ | 기본 | O | FluidSynth | L45 | 구매 없음
104 | Salamander Grand Piano V3 (FreePats SF2판) | 0원 | 1 | FluidSynth에 넣는 무료 그랜드 피아노 음원 | 0원 | https://freepats.zenvoid.org/Piano/acoustic-grand-piano.html | 기본 | O | FreePats | L46 | 구매 없음
 | 무료 (다운로드) 소계 |  |  |  | 0원
 | 합계
 | 기본 부품 합계 |  |  |  | 548578원
 | 소모품 합계 |  |  |  | 165284원
 | 공구 합계 |  |  |  | 89470원
 | 최종 금액 |  |  |  | 803332원
 | 확인: 판매처 소계의 합 |  |  | 최종 금액과 같아야 한다 | 803332원
 | 참고: 도면집 절감안 합계 |  |  | 출처: 사용자가 붙여 넣은 도면집 v10 절감안 선택 결과(기본 548,578 · 소모품 165,316 · 공구 89,470) | 803364원
 | 차이 (최종 − 도면집) |  |  | 모두 O일 때 −32원: 도면집이 동전 받침(CT15) 출력분 필라멘트 32원을 소모품에 더했는데, 이 표는 이미 사는 PETG로 출력하므로 따로 넣지 않았다. | -32원
 | 메모
 | · 빠진 부품(선택 코드로 사지 않음): 10µF 콘덴서(SE6), 점퍼 단선(SE12→리본), 듀폰 점퍼 40가닥(X1), 플럭스 펜(CT22), 확대경 스탠드(CT14), 전자저울(CT15→동전 추), 16AWG 스트리퍼(CT16), 4067용 암 헤더(SE7).
 | · 아이씨뱅큐·엘레파츠·Bambu Lab 배송비는 주문액에 따라 자동 계산된다. 다른 판매처 배송비는 도면집 부품표 값이며, 같은 판매자 묶음배송은 1회만 넣었다.
 | · 다나와 줄은 가격 비교 페이지다. 링크에서 최저가 판매처로 넘어가 구매하며 판매처·가격이 바뀔 수 있다.
 | · AliExpress·PINE STORE는 해외 결제라 환율·관세 기준에 따라 금액이 조금 달라질 수 있다(PINE STORE 배송비 16,200원 포함).
 | · 링크는 2026-09-25에 모두 열리는 것을 확인했다(재고·가격은 주문 시 다시 확인).

Sheet: 판매처 요약
No | 구매 사이트 | 품목 수(O) | 소계(원) | 비중
1 | 아이씨뱅큐 | 12 | 233073원 | 29.0%
2 | 엘레파츠 | 29 | 110093원 | 13.7%
3 | 11번가 | 18 | 74150원 | 9.2%
4 | 메카솔루션 | 3 | 12960원 | 1.6%
5 | 파츠파츠 직영몰 | 2 | 32900원 | 4.1%
6 | Bambu Lab KR 공식 스토어 | 4 | 93500원 | 11.6%
7 | 다나와 (최저가 판매처) | 3 | 68990원 | 8.6%
8 | 동진나무공장 | 2 | 40200원 | 5.0%
9 | 대건상사 | 2 | 12740원 | 1.6%
10 | 알씨뱅크 | 1 | 9500원 | 1.2%
11 | 철물박사 | 1 | 7800원 | 1.0%
12 | 스튜디오분트 | 1 | 8500원 | 1.1%
13 | 피아노모아 | 1 | 11500원 | 1.4%
14 | Apple Store 온라인 | 1 | 14900원 | 1.9%
15 | AliExpress | 2 | 13716원 | 1.7%
16 | PINE STORE (Pine64 공식) | 3 | 58810원 | 7.3%
17 | 무료 (다운로드) | 2 | 0원 | 0.0%
 | 최종 금액 | 87 | 803332원 | 100.0%
