WongyuKoh/Toccata/hardware/mechanical/toccata-최종-재료-2026-09-30.xlsx

Sheet: 판매처별 주문
Toccata 최종 재료 — 판매처별 주문표
만든 날: 2026-09-30 · v4 W1 r4.5 · 수량·단가를 고치면 금액·합계가 다시 계산됩니다
판매처 | 분류 | 품목 | 상품명 (판매처 표기) | 수량 | 단가(원) | 금액(원) | 구분 | 링크 | 쓰는 곳
아이씨뱅큐 | 제어·전원 | Raspberry Pi 5 (2GB) | Raspberry Pi 5 2GB (라즈베리파이 5 2GB Raspberry pi 5) | 1 | 119900 | 119900 | 기본 | https://www.icbanq.com/P016286897 | 가운데 유닛 CU 칸의 출력 트레이 보스 4개에 M2.5×6 나사(L47)로 1대를 고정한다. USB-A 한 포트에 허브 업스트림 선(W209), 다른 포트에 USB 동글(젠더 X701)을 꽂는다. 전원은 강압 모듈에서 C24 선으로 USB-C에 받는다. FluidSynth를 돌리고, 2단계 리듬게임도 콘솔 모드에서는 여기서 돌린다(PC 모드에서는 PC가 맡는다).
아이씨뱅큐 | 제어·전원 | PD 트리거 모듈 HUSB238 (20 V) | 100W QC PD 트리거 디코이 고정출력 모듈 5V-20V (HAM6113, HUSB238) | 1 | 4950 | 4950 | 기본 | https://www.icbanq.com/P017179277 | CU 칸 뒤판인 I/O 판 안쪽 포켓에 1개를 끼워 USB-C 구멍이 본체 밖을 향하게 한다. 충전기 선(C23)이나 보조배터리 선(C22)이 여기에 꽂힌다. 출력 +는 퓨즈 → 스위치로, −는 강압 모듈 IN− 별 접지점으로 간다(SCH-06 A601).
아이씨뱅큐 | 센서·MCU·기판 | 홀센서 TI DRV5055A2QLPG | TI DRV5055A2QLPG (TO-92-3 Linear Hall Effect Sensor, LCSC 경유) | 100 | 891 | 89100 | 기본 | https://www.icbanq.com/P018076669 | 건반 밑 자석(Ø5×2)과의 거리를 전압으로 재는 센서다. 모듈 센서 기판마다 12개(U201~U212) × 7 = 84, 끝 부속 EL 3개(A0·A#0·B0) + ER 1개(C8), 페달 안 1개(U551) = 89개 사용. 건반용은 표시면을 위로 눕혀 센서 바 포켓에 넣고, 다리를 2.54 간격으로 벌려 꺾어 센서 기판에 납땜한다. 페달용은 페달 바닥판에 만능기판 자투리와 함께 표시면이 위로 오게 붙인다(SCH-05 주 1). [100개 이상 개당 891원, 그 아래는 개당 1,023원]
아이씨뱅큐 | 센서·MCU·기판 | 핀헤더 1×40 (2.54 mm, 수) | 핀헤더 1×40 - 2.54MM(S/T) _ 11.5MM(1단몰드) | 9 | 165 | 1485 | 기본 | https://www.icbanq.com/P005666127 | 제어 기판에 먹스 모듈과 RP2040-Zero를 세워 납땜하는 핀이다. 먹스 7개 × (1×16 + 1×8) = 168핀, RP2040-Zero 8개(O1~O7 + 페달 보드) × 1×9 ×2 = 144핀, 합 312핀. 제로용은 플라스틱 몰드를 빼고 좌·우 줄만 쓴다(아래 줄 없음).
아이씨뱅큐 | 센서·MCU·기판 | 100 nF 1206 칩 콘덴서 (삼성) | Samsung CL31B104KCFNNNE (1206 100nF 100V X7R) | 97 | 44 | 4268 | 기본 | https://www.icbanq.com/P014968846 | 센서마다 붙이는 전원 안정 콘덴서다. 센서 기판 아랫면 센서마다 1개(C201~C212) × 7 = 84, 끝 부속 EL 3(C401~C403) + ER 1(C411), 페달 안 센서 1(C551), 페달 보드 ADC 필터 1(C501), 제어 기판 먹스 전원 C301 × 7 = 97개 사용. 센서용은 3V3–GND 패드 사이에, C301은 제어 기판 아랫면 먹스 VCC–GND 사이에, C501은 ADC 입력–GND 사이에 납땜한다.
아이씨뱅큐 | 센서·MCU·기판 | 10 µF 1206 칩 콘덴서 (50개) | C3216-10UF(K 16V) — 1206 10 µF 16 V 칩 세라믹 콘덴서 (50개 단위) | 1 | 7150 | 7150 | 기본 | https://www.icbanq.com/P001248090 | 센서 3V3 버스의 전원 안정 콘덴서다. 센서 기판 아랫면 버스 양 끝(C213 x8.25, C214 x158.11) × 7 = 14, 끝 부속 EL C404 + ER C412 = 16개 사용(회로 △1·△3).
아이씨뱅큐 | 센서·MCU·기판 | 1 kΩ 1206 칩 저항 (Yageo) | Yageo RC1206JR-071KL — 1206 1 kΩ 5 % 1/4 W 칩 저항 | 10 | 44 | 440 | 기본 | https://www.icbanq.com/P011433924 | 끝 부속 센서 기판 아랫면에서 센서 OUT에 직렬로 다는 저항이다. EL R401~R403(A0·A#0·B0) + ER R411(C8) = 4개 사용. 약 0.6 m 선의 용량이 센서 출력에 바로 걸리지 않게 한다(△8·△13). [최소 주문 10개 · 10개 단위로 판매]
아이씨뱅큐 | 오디오 | 1 µF 적층 세라믹 콘덴서 50 V | Monolithic Capacitor 1uF X7R 50V (리드형 적층 세라믹) | 4 | 133 | 532 | 기본 | https://www.icbanq.com/P014159115 | CU 트레이의 앰프 입력 잭(J702) 기판에서 앰프 입력 앞 저음 차단 필터로 쓴다. 채널마다 2개를 병렬(2 µF)로 신호에 직렬로 넣어 C701·C702(왼쪽), C703·C704(오른쪽) = 4개를 쓴다. 채널마다 1 kΩ(R701·R702, L29 줄)을 앰프 IN G(AGND)로 달아 약 93 Hz 아래를 줄인다.
아이씨뱅큐 | 건반 액션 | M3 육각너트 강철 (LCSC C133377) | XHHD 육각너트 M3 강철 (LCSC C133377) | 92 | 11 | 1012 | 기본 | https://www.icbanq.com/P015976209 | 건반 꼬리 숨은 빔의 너트 홈(폭 5.6)에 옆에서 밀어 넣어 캡스턴 나사(M3×6)를 받는다. 건반마다 1개라 모듈 12 × 7 + 끝 부속 4 = 88개다. 여기에 끝 부속 ↔ 스피커 브래킷 연결 4개(v3.2 기준, 왼쪽·오른쪽 끝 부속에 가로 너트 2개씩)를 더해 92개를 쓴다.
아이씨뱅큐 | 본체·결합 | V-tech 순간접착제 5 g (VT-041) | 순간접착제 (814-2010) — V-tech 강력 순간접착제 5g (VT-041) | 1 | 1100 | 1100 | 소모품 | https://www.icbanq.com/P015309984 | 건반 밑 센서 자석(Ø5×2) 89개(건반 88 + 페달 1)를 포켓(Ø5.2)에 눌러 넣은 뒤 한 방울씩 떨어뜨려 고정한다. 가운데 유닛 뚜껑 자석(Ø8×3) 12개도 이것으로 Ø8.2 포켓에 붙인다. 단계 0 시험 키트(C01 봉·시험 레버의 강철 고정 등)에도 조금 쓴다.
아이씨뱅큐 | 페달 | 3.5 mm 스테레오 AUX 선 3 m (페달) | [BC256] Coms 스테레오 케이블 3M AUX 3극 Stereo 3.5 M/M 고급포장 | 1 | 2860 | 2860 | 기본 | https://www.icbanq.com/P004711396 | 댐퍼 페달(책상 앞 바닥)과 가운데 유닛 I/O 판의 페달 잭(J501, L15 ②)을 잇는 신호선 1가닥(W501)이다. 한쪽 플러그를 잘라 페달 안 센서 기판에 납땜하고(팁 = 센서 출력, 링 = 3V3, 슬리브 = GND), 남은 플러그를 I/O 판 잭에 꽂는다.
아이씨뱅큐 | 건반 액션 | 캡스턴 나사 M3×6 버튼헤드 SUS304 | AOFENG ISO7380 M3-0.5X6 304 (Hex socket pan head cap screw) | 100 | 11 | 1100 | 기본 | https://www.icbanq.com/P015973844 | 건반 꼬리 숨은 빔의 캡스턴이다. 머리가 레버 밑 펠트 띠를 들어 올린다. 1/8회전(0.0625 mm)씩 돌려 높이를 맞춘다. 모듈 12 × 7 + 끝 부속 4 = 88개를 쓰고, 건반을 넣기 전에 벤치 지그와 가짜 레버(T2)에서 맞춘다. [최소 주문 100개]
아이씨뱅큐 | 배송비 | 배송비 |  | 1 | 0 | 0 | 배송비 |  | 55,000원 이상 무료
 |  | 아이씨뱅큐 소계 |  |  |  | 233897
엘레파츠 | 제어·전원 | KCD1-101A 로커 스위치 (검정) | [ZX Electronics] KCD1-101A BLACK I/O 로커 스위치 (2P ON-OFF, 6A 250VAC / 10A 125VAC) | 1 | 385 | 385 | 기본 | https://www.eleparts.co.kr/goods/view?no=32569 | I/O 판의 스위치 구멍에 1개를 끼운다(스냅인). 퓨즈 뒤 20 V 선에 들어가 앰프와 강압 모듈을 함께 켜고 끈다(SCH-06 SW601).
엘레파츠 | 제어·전원 | Coms BU914 퓨즈 홀더 (5×20) | [Coms] BU914 원형 휴즈 홀더 (5×20 mm, 인라인) | 1 | 1110 | 1110 | 기본 | https://www.eleparts.co.kr/goods/view?no=3237821 | PD 트리거 출력 + 선(트리거와 스위치 사이)에 1개를 넣는다. 홀더 빨간 선 가운데를 잘라 양쪽을 납땜하고 수축튜브로 감싼다(SCH-06 F601).
엘레파츠 | 제어·전원 | Littelfuse 5 A 지연형 퓨즈 5×20 | [LITTELFUSE] 0218005.MXP 5 A 지연형 퓨즈 5×20 mm | 5 | 110 | 550 | 기본 | https://www.eleparts.co.kr/goods/view?no=12766820 | 퓨즈 홀더(i017) 안에 1개를 넣는다. 나머지 4개는 예비로 둔다. [최소 주문 5개]
엘레파츠 | 제어·전원 | USB-C↔C PD 60W 케이블 0.6 m | [MachLink] USB-C to C PD 60W 초고속충전 케이블, ML-CPD606 [블랙/0.6m] | 1 | 1440 | 1440 | 소모품 | https://www.eleparts.co.kr/goods/view?no=17806172 | 보조배터리로 칠 때만 쓴다. 보조배터리 칸의 배터리에서 낮은 칸막이 위 → CU 칸 → I/O 판 선 통과 구멍으로 빼서 PD 트리거 USB-C 입력에 1개를 꽂는다(W601).
엘레파츠 | 센서·MCU·기판 | 16심 리본 케이블 2651-16P (센서 선) | [EUNSUNG] Flat Data Cable 2651-16P (1m단위) | 2 | 1529 | 3058 | 소모품 | https://www.eleparts.co.kr/goods/view?no=425 | 모듈마다 센서 기판 J201과 제어 기판 J301을 잇는 리본 1장(16심 전부, 약 180 mm, W101~W107) × 7. 끝 부속 EL 리드 5심 350 mm(W401)와 ER 리드 3심 300 mm(W411)도 이 리본을 갈라 만든다. 양 끝은 커넥터 없이 기판 아랫면 2×8 구멍에 바로 납땜한다.
엘레파츠 | 센서·MCU·기판 | 16심 리본 케이블 추가 1 m (배선용) | [EUNSUNG] Flat Data Cable 2651-16P (1m단위) | 1 | 1529 | 1529 | 소모품 | https://www.eleparts.co.kr/goods/view?no=425 | 리본을 한 가닥씩 갈라 기판 배선에 쓴다. 센서 기판 아랫면 3V3·GND 버스와 OUT → 리본 블록 선, 제어 기판 점 대 점 배선(SIG·S0~S3·EN·ID 브리지 등), 페달 잭 → 페달 보드 4가닥(W502, 약 10 cm).
엘레파츠 | 소모품 | 열수축튜브 530개 세트 (케이스) | [엘레파츠] 열수축튜브 530세트 - 프라스틱케이스 | 1 | 6600 | 6600 | 소모품 | https://www.eleparts.co.kr/goods/view?no=8170311 | 끝 부속 리드(EL 5가닥 + ER 3가닥)를 뒤 케이블 통로에서 L66 JST-XH 리드(끝 부속 쪽 50 mm)와 이은 8곳을 덮는다(SCH-04 주 6). CU의 퓨즈 홀더(F601) 선을 PD 트리거 출력·스위치 쪽 선과 이은 곳, 스피커선(16 AWG)을 XT30 꼬리선에 이은 곳, 페달 안 센서 납땜부, 페달 잭 뒤쪽 납땜에도 쓴다. 구매 목록은 O1·O7 제어 기판 J302 패드에 L66 리드를 납땜한 곳도 적었다. 배선 단계에서 쓴다.
엘레파츠 | 센서·MCU·기판 | 탄소피막 저항 1 kΩ (10개) | [ABCO] CFR 1/4W 5% 탄소피막 저항 1kΩ (10개 단위) | 10 | 25 | 250 | 기본 | https://www.eleparts.co.kr/goods/view?no=10911 | 1 kΩ 4개 사용. CU 칸 앰프 입력 저음 차단 필터의 풀다운 R701·R702(채널마다 1 µF 2개 병렬과 짝을 이루고, 앰프 입력 9 kΩ와 겹쳐 약 93 Hz), 페달 보드 ADC 입력 R501, 페달 안 센서 출력 바로 뒤 R551. [최소 주문 10개 · 10개 단위로 판매]
엘레파츠 | 센서·MCU·기판 | 탄소피막 저항 100 kΩ (10개) | [ABCO] CFR 1/4W 5% 탄소피막 저항 100kΩ (10개 단위) | 10 | 25 | 250 | 기본 | https://www.eleparts.co.kr/goods/view?no=10993 | EXT 입력이 떠서 유령 음이 나지 않게 하는 풀다운이다(필수, △8). O1 제어 기판 R301·R302·R303(A0·A#0·B0), O7 제어 기판 R301(C8), 페달 보드 R502(팁 → GND) = 5개 사용. [최소 주문 10개 · 10개 단위로 판매]
엘레파츠 | 센서·MCU·기판 | 탄소피막 저항 100 Ω (10개) | [ABCO] CFR 1/4W 5% 탄소피막 저항 100Ω (10개 단위) | 10 | 25 | 250 | 기본 | https://www.eleparts.co.kr/goods/view?no=10873 | 페달 보드(PB, CU 칸 안)의 링 급전 저항 R503이다. 100 Ω 5개를 병렬로 묶어 20 Ω로 쓴다. 플러그를 꽂는 순간 3V3–GND가 이어져도 전류를 약 165 mA로 막아 페달 보드가 리셋되지 않게 한다(△4, 필수). [최소 주문 10개 · 10개 단위로 판매]
엘레파츠 | 오디오 | PJ-313 3.5 mm 스테레오 잭 | [BSUN] PJ-313 3.5Ф 스테레오잭 (이어폰잭) | 2 | 198 | 396 | 기본 | https://www.eleparts.co.kr/goods/view?no=67811 | 3개 모두 쓴다. ① 왼쪽 끝 부속 볼 앞면의 헤드폰 잭(J701) ② 가운데 유닛 I/O 판의 댐퍼 페달 잭(J501) ③ CU 트레이의 앰프 입력 잭(J702). 너트 없는 PCB형이라 만능기판 자투리에 납땜해서 단다. 자투리는 12×18 기판(i081) 둘째 장의 남는 부분에서 자른다. 5×7 기판 8장은 제어 기판과 페달 보드에 모두 쓰기 때문이다. 헤드폰 잭은 왼쪽 볼의 출력 포켓에 끼운다.
엘레파츠 | 오디오 | XT30U-M 수 커넥터 (선 10 cm) | [AMASS] XT30U-M 수 커넥터 18AWG 10cm 실리콘 와이어 | 2 | 1760 | 3520 | 기본 | https://www.eleparts.co.kr/goods/view?no=12779720 | 앰프 쪽 스피커선 커넥터다. 앰프 출력에서 뒷바 아래 케이블 통로를 지나 양 끝으로 나온 스피커선(C13, 약 0.6 m) 끝에 1개씩 납땜한다(왼쪽 X703, 오른쪽 X705). 설치할 때 통로 안 XT30 받침(스피커 파트 쪽)에 끼워 둔 암(XT30U-F)에 꽂는다.
엘레파츠 | 오디오 | XT30U-F 암 커넥터 (선 10 cm) | [AMASS] XT30U-F 암 커넥터 18AWG 10cm 실리콘 와이어 | 2 | 1760 | 3520 | 기본 | https://www.eleparts.co.kr/goods/view?no=12779721 | 스피커 쪽 커넥터다. 좌우 스피커 파트 안에서 유닛 단자에 이은 스피커선(C13, 약 0.3 m)을 앞판 아래 선 구멍으로 빼서 끝에 1개씩 납땜한다(왼쪽 X704, 오른쪽 X706). 이 커넥터를 케이블 통로 안의 출력 XT30 받침(스피커 파트 쪽)에 끼워 두고, 설치할 때 앰프 쪽 수(XT30U-M)를 꽂는다.
엘레파츠 | 오디오 | 스피커선 16 AWG 7 m (프리즘) | [케이블스토어] 프리즘 국산 스피커케이블 50C 16AWG, 7M [블랙/PRS-50B07] | 1 | 14300 | 14300 | 소모품 | https://www.eleparts.co.kr/goods/view?no=18388615 | 세 곳에 잘라 쓴다. 앰프 → 통로 → XT30 수 좌우 각 약 0.6 m(W703·W705), 스피커 파트 안 유닛 → XT30 암 각 약 0.3 m(W704·W706), 20 V 전원선 약 1 m(PD 트리거 → 퓨즈 → 스위치 → 앰프·강압 모듈, W602). 모두 약 2.8 m를 쓴다.
엘레파츠 | 오디오 | 3.5 mm 스테레오 AUX 선 1.5 m | [AV0176] Coms 스테레오 케이블 1.5M AUX 3극 Stereo 3.5 M/M | 2 | 1710 | 3420 | 소모품 | https://www.eleparts.co.kr/goods/view?no=2925673 | 2가닥을 쓴다. 선 ①(W701)은 CU의 동글(L51) → 왼쪽 볼 헤드폰 잭(J701), 선 ②(W702)는 헤드폰 잭 노멀 접점 → CU 트레이 앰프 입력 잭(J702)이다. 둘 다 끝 부속 쪽 플러그를 잘라 잭에 납땜하고 CU 쪽 플러그만 남긴다(각 약 0.7 m 사용).
엘레파츠 | 본체·결합 | 화성고무 피스고무발 28×5 (RUB-E2) | [화성고무] 피스고무발 / 28x5 (RUB-E2) | 20 | 583 | 11660 | 기본 | https://www.eleparts.co.kr/goods/view?no=16628292 | 왼쪽·오른쪽 스피커 파트 밑에 4개씩, 가운데 유닛 밑에 6개 = 14개를 25 mm 직결피스로 단다. 출력 받침 4 mm와 함께 뒷바를 22 mm 띄워, 그 아래 앞쪽을 USB 케이블 통로로 쓴다. 본체와 스피커의 진동도 떼어 놓는다. [최소 주문 20개]
엘레파츠 | 배송비 | 배송비 |  | 1 | 3000 | 3000 | 배송비 |  | 66,000원 이상 무료
 |  | 엘레파츠 소계 |  |  |  | 55238
동진나무공장 | 본체·결합 | 오꾸메 합판 400×1200×11.5 (스피커) | 무료배송 오꾸메 합판 400×1200×11.5mm 무료재단 | 1 | 17680 | 17680 | 기본 | https://namugongjang.com/product/detail.html?product_no=1378 | 왼쪽·오른쪽 스피커 파트의 밀폐 상자 2개(외형 180 × 195 × 210, 안 5.05 L)를 이 한 장에서 잘라 만든다. 상자마다 옆판 2·뒤판 1·위아래판 2 = 5장, 모두 10장. 앞판(배플)은 PETG 출력이다.
동진나무공장 | 본체·결합 | 오꾸메 합판 600×1200×11.5 (가운데 유닛) | 무료배송 오꾸메 합판 600×1200×11.5mm 무료재단 | 1 | 22520 | 22520 | 기본 | https://namugongjang.com/product/detail.html?product_no=1378 | 가운데 유닛 상자(894 × 195 × 100: 예비 건반 보관함·CU 칸·보조배터리 칸)를 이 한 장에서 만든다. 바닥 2·뚜껑 2·앞판 1·뒤판 2·끝판 2·칸막이 2 = 11장.
동진나무공장 | 배송비 | 배송비 |  | 1 | 0 | 0 | 배송비
 |  | 동진나무공장 소계 |  |  |  | 40200
올스틸샵 | 건반 액션 | 강철 띠 9T×19×1 m (강철 블록용) | 사각철판 9T (SS275) 19×1000 맞춤 재단 | 4 | 8610 | 34440 | 기본 | https://www.allsteelshop.com/product/squareplate/9t | 1 m 띠를 40 mm씩 잘라 강철 블록(9×19×40, 53.7 g)을 만든다. 블록은 레버 캐리어에 밑에서 스냅으로 끼우고 MS 폴리머로 붙이는 무게 추이며, 드러난 윗면이 업스톱 패드에 닿는다. 레버마다 1개로 모듈 12 × 7 + 끝 부속 4 = 88개를 쓴다.
올스틸샵 | 배송비 | 배송비 |  | 1 | 3500 | 3500 | 배송비
 |  | 올스틸샵 소계 |  |  |  | 37940
파츠파츠 직영몰 · 파츠파츠 | 센서·MCU·기판 | RP2040-Zero 보드 (PP-A799-2) | (PP-A799-2) 라즈베리 파이 피코 PICO RP2040-ZERO | 8 | 3300 | 26400 | 기본 | https://parts-parts.co.kr/product/detail.html?product_no=2383 | 모듈 O1~O7 제어 기판마다 1개(7개) + CU 칸 페달 보드 1개 = 8개. 먹스를 돌려 센서 값을 읽고 속도를 계산해 USB-MIDI 장치('Toccata O1'~'O7', 'Toccata PED')가 된다. 안쪽 구멍에 핀 헤더 1×9 ×2(몰드 뺌)로 세워 납땜하고, 밑면 부품 위에 캡톤을 깐다(약 +1.3 mm).
파츠파츠 직영몰 · 파츠파츠 | 센서·MCU·기판 | 16채널 먹스 모듈 CD74HC4067 | (PP-A324) 16채널 아날로그/디지털 멀티플렉서 모듈 | 7 | 500 | 3500 | 기본 | https://parts-parts.co.kr/product/detail.html?product_no=303 | 모듈 O1~O7 제어 기판마다 1개(x54.93~72.71에 세로로) = 7개. 그 옥타브 홀센서 12개(C0~C11)와 끝 부속 EXT(C12~C15: O1은 A0·A#0·B0, O7은 C8)를 RP2040-Zero ADC0(GP26) 한 채널로 읽는다. 소켓 없이 핀헤더로 기판에 바로 납땜한다.
파츠파츠 직영몰 · 파츠파츠 | 배송비 | 배송비 |  | 1 | 3000 | 3000 | 배송비 |  | 100,000원 이상 무료
 |  | 파츠파츠 직영몰 · 파츠파츠 소계 |  |  |  | 32900
한국미스미 | 건반 액션 | 미스미 토션스프링 C-UA90R5-3-0.5 | 한국미스미 경제형 토션스프링 C-UA90R5-3-0.5 (SUS304-WPB, 내경 5 · 선경 0.5 · 3권 · 암 각 90° 오른쪽 감기, 암 50/50) | 100 | 310 | 31000 | 기본 | https://kr.misumi-ec.com/vona2/detail/110310556289/?HissuCode=C-UA90R5-3-0.5 | 레버 허브의 스프링 주머니(Ø6.6×3.0)에 넣고 레버 봉에 꿴다. 짧은 다리(8.0)는 허브의 가둠 홈에, 긴 다리(22.3)는 뒷벽 홈에 걸어 레버를 아래로 민다(DW 51.9 g 중 약 11 g). 레버마다 1개로 88개를 쓴다. 단계 0 시험 8에 1개, 시험 13에 3개를 더 쓰고(합 92개), 남는 8개는 보관함 옆 칸에 둔다. [100개 이상 개당 310원, 그 아래는 개당 365원]
한국미스미 | 배송비 | 배송비 |  | 1 | 0 | 0 | 배송비
 |  | 한국미스미 소계 |  |  |  | 31000
나비엠알오 | 본체·결합 | 오공 205 목공본드 800 g | [오공] 목공용 수성 접착제 (205본드) 800g K01424797 | 1 | 3949 | 3949 | 소모품 | https://www.navimro.com/g/395062/ | 스피커 상자 2개(합판 10장)와 가운데 유닛(합판 11장)을 붙인다. 출력 앞판 둘레도 이것으로 밀봉한다. 드릴 없이 본드로만 붙이고 마스킹테이프로 눌러 굳힌다.
나비엠알오 | 건반 액션 | OHP 필름 A4 0.1 mm 20매 (PET 심용) | OHP 필름 (A4) 흑백 레이저용 1PK(20매) — 카피어랜드 | 1 | 2739 | 2739 | 소모품 | https://www.navimro.com/g/37021/ | 업스톱 패드와 패드 바 쐐기 사이에 끼우는 0.1 mm PET 심이다. 6×12.2로 잘라 조립 10단계와 12장 업스톱 시점 조정에서 건반마다 필요한 만큼 넣고 뺀다(부품표 추정 약 50장). 단계 0 시험 1·6·12·14에서는 얇은 게이지로도 쓴다. 남는 심은 건반 보관함 작은 부품 통에 둔다.
나비엠알오 | 건반 액션 | WAKI PORON 5T 점착 100×100 (PON-02) | [와키(WAKI)] PORON 스폰지 접착 부착 PON-02 (100×100×5, 검정, 아크릴 점착) | 1 | 3399 | 3399 | 기본 | https://www.navimro.com/g/1028764/ | 업스톱 패드에 들어가는 폼이다. 6×12.2로 잘라 강철이 닿는 쪽에 펠트 1T를 겹치고 패드 바 쐐기에 붙인다. 모듈마다 12개 × 7 + 끝 부속 4 = 88개에, 예비 12개(건반 보관함 옆 칸)를 더해 100개를 쓴다.
나비엠알오 | 건반 액션 | WAKI 하네나이트 1T 170×245 (HNT002) | [와키(WAKI)] 충격흡수재 하네나이트 HNT002 (170×245×1, 검정) | 1 | 16489 | 16489 | 기본 | https://www.navimro.com/g/1029233/ | 앞 레일의 앞 펠트 2T 밑에 까는 1T 저반발 층이다(S21·S22). 백건 줄은 모듈 7개·끝 부속 2개마다 전체 폭 띠(y1.5~9.0, 폭 7.5, 합쳐 약 1.2 m)로, 흑건은 36개 자리마다 조각(y54.5~59.0, 폭 4.5 × 약 10.4)으로 잘라 붙인다. 필요한 면적은 약 110 cm²이다(추정).
나비엠알오 | 공구 | Ø4.0 HSS 드릴 날 SD 4.0 | [나비엠알오] 스트레이트 드릴 SD 4.0 | 1 | 990 | 990 | 공구 | https://www.navimro.com/g/171100/ | Ø3.9로 출력한 구멍을 Ø4.0으로 넓혀 Ø4 봉이 부드럽게 들어가고 레버가 잘 돌게 한다. 레버 캐리어 허브 88개, 모듈 프레임 핀 보스 5 × 7 = 35개, 끝 부속 핀 보스, 출력 공구(지그 K·L 구멍, 가짜 레버 허브), 단계 0 시편(C01a·b·d, C06a)까지 모두 약 130구멍이다.
나비엠알오 | 배송비 | 배송비 |  | 1 | 3300 | 3300 | 배송비 |  | 55,000원 이상 무료
 |  | 나비엠알오 소계 |  |  |  | 30866
스튜디오분트 | 건반 액션 | 메리노 울 펠트 2T 20×30 cm (35 블랙) | 100% 메리노양모 70수 펠트지 2mm 20×30cm (35 블랙) | 1 | 13800 | 13800 | 기본 | https://studiobunt.com/product/detail.html?product_no=4117 | 세 곳에 쓴다. 레버 88개 밑 캡스턴 펠트 띠(폭 7 × y176.5~192.0), 앞 레일의 앞 펠트(백건 줄은 모듈 7개·끝 부속 2개 전체 폭 y1.5~9.0 띠, 흑건은 36개 자리마다 y54.5~59.0 조각; 둘 다 하네나이트 1T 위), 키퍼 훅 88개 밑 펠트(5.2 × 3)이다. 한 장(600 cm²) 가운데 약 220 cm²를 쓴다(r4.5 치수로 다시 셈, 추정).
스튜디오분트 | 건반 액션 | 메리노 울 펠트 1T 20×30 cm (80 블랙) | 100% 메리노양모 70수 펠트지 1mm 20×30cm (80 블랙) | 1 | 6900 | 6900 | 기본 | https://studiobunt.com/product/detail.html?product_no=1157 | 두 곳에 쓴다. 업스톱 패드 100개(88 + 예비 12)의 강철이 닿는 면 펠트(6×12.2)와, 건반 104개(88 + 예비 16) 꼬리 밑 쉼 펠트 1.5T의 바탕이다. 쉼 펠트는 이 1T 위에 0.5T 천을 한 겹 붙여 2.7×8로 자른다(F·F#는 더 짧게). 한 장(600 cm²) 가운데 약 100 cm²를 쓴다(추정).
스튜디오분트 | 배송비 | 배송비 |  | 1 | 3000 | 3000 | 배송비 |  | 50,000원 이상 무료
 |  | 스튜디오분트 소계 |  |  |  | 23700
11번가 · 세운상가새한음향 | 오디오 | 삼미 CW-100B25 4인치 스피커 8 Ω | 삼미스피커(SAAT) CW-100B25 4인치 풀레인지 8Ω 25W (KS 인증) | 2 | 9600 | 19200 | 기본 | https://www.11st.co.kr/products/1565354988 | 좌우 스피커 파트(뒷바 양 끝, 오꾸메 밀폐 상자 내부 5.05 L)의 PETG 앞판 컷아웃(Ø94)에 1개씩 = 2개. 연주자 쪽을 향하게 EVA 가스켓(MEV1 3T 자투리)을 대고 직결피스 16 mm(L49) 4개씩으로 조인다. 선은 앞판 아래 선 구멍(본드로 막음)으로 빼서 XT30 암(L61)에 잇는다.
11번가 · 세운상가새한음향 | 배송비 | 배송비 |  | 1 | 4000 | 4000 | 배송비 |  | 100,000원 이상 무료
 |  | 11번가 · 세운상가새한음향 소계 |  |  |  | 23200
나사코리아 nasakorea.com | 건반 액션 | 밸런스 핀 Ø2×12 SUS304 (100개) | 다올핀 M2*6~20 STS304 GB119.1(ISO2338) — 옵션 2*12/100개/스텐STS304 | 1 | 16600 | 16600 | 기본 | https://www.nasakorea.com/goods/goods_view.php?goodsNo=6009 | 밸런스 레일(y135.3)에 핀 높이 게이지(T3)로 눌러 넣고 꼭대기를 z23.30에 맞춘다. 건반 블록 밑 홈(천 0.5T)이 이 핀을 물어 건반 뒤쪽의 좌우 위치를 잡는다. 모듈 12 × 7 + 끝 부속 4 = 88개를 쓴다. 이 밖에 벤치 지그(T1a) 핀 구멍에 1개, 단계 0 시험 P 쿠폰(C07a, 구멍 5개)에 5개까지 쓴다. 4개는 보관함 작은 부품 통에 둔다.
나사코리아 nasakorea.com | 배송비 | 배송비 |  | 1 | 3300 | 3300 | 배송비 |  | 100,000원 이상 무료
 |  | 나사코리아 nasakorea.com 소계 |  |  |  | 19900
11번가 · 주영종합상사 | 건반 액션 | 세메다인 슈퍼X 백색 20 mL (MS 폴리머) | 세메다인 슈퍼X 8008 탄성접착제 백색 20 mL (AX-022) | 2 | 8000 | 16000 | 소모품 | https://www.11st.co.kr/products/7459325704 | 레버 캐리어에 강철 블록을 붙이는 탄성 접착제다. 강철의 두 19×40 옆면에 얇게(블록당 약 0.2 mL) 바르고 밑에서 스냅으로 끼운 뒤 24시간 굳힌다. 조립 4단계에서 레버 88개에, 단계 0 시험 20에서 캐리어 2개에 쓴다.
11번가 · 주영종합상사 | 배송비 | 배송비 |  | 1 | 3000 | 3000 | 배송비
 |  | 11번가 · 주영종합상사 소계 |  |  |  | 19000
Apple Store 온라인 | 오디오 | Apple USB-C 헤드폰 어댑터 | Apple USB-C–3.5mm 헤드폰 잭 어댑터 (MW2Q3KH/A) | 1 | 14900 | 14900 | 기본 | https://www.apple.com/kr/shop/product/mw2q3kh/a | CU 칸에서 젠더(L52)로 Pi 5 USB-A 포트에 바로 꽂는 USB 사운드 장치(DAC + 헤드폰 앰프)다. FluidSynth 소리를 아날로그로 바꿔 선 ①(C14)로 왼쪽 볼 헤드폰 잭에 보낸다. 헤드폰을 안 꽂으면 노멀 접점을 거쳐 앰프로 간다.
Apple Store 온라인 | 배송비 | 배송비 |  | 1 | 0 | 0 | 배송비
 |  | Apple Store 온라인 소계 |  |  |  | 14900
알씨뱅크 | 센서·MCU·기판 | JST-XH 6핀 연장선 200 mm (5S) | 리튬폴리머 배터리 밸런스잭 연장선 5셀용 (JST-XH 6핀 수↔암, BU-LP 5S, 200mm) | 2 | 3000 | 6000 | 기본 | https://www.rcbank.co.kr/shop/goods/goods_view.php?goodsno=29812 | 끝 부속 센서 선과 O1·O7 제어 기판을 잇는 6핀 커넥터 2쌍이다(왼쪽 EL ↔ O1, 오른쪽 ER ↔ O7). 200 mm 선을 모듈 쪽 150 mm · 끝 부속 쪽 50 mm로 자른다. 150 mm 쪽은 O1·O7 제어 기판 J302 패드(아랫면)에, 50 mm 쪽은 끝 부속 리본 리드에 납땜하고, 두 쪽을 모듈 뒤 통로에서 꽂는다.
알씨뱅크 | 본체·결합 | M3 방진 댐퍼(그로밋) 20개 | 알씨뱅크 M3 진동 방지 댐퍼 (20개) | 1 | 4500 | 4500 | 기본 | https://www.rcbank.co.kr/shop/goods/goods_view.php?goodsno=67110 | 왼쪽·오른쪽 끝 부속과 스피커 파트를 잇는 짧은 PETG 방진 브래킷(40 × 17 × 6)에 2개씩 = 4개. 위치만 잡아 주고, 스피커 무게는 고무발이 받는다.
알씨뱅크 | 배송비 | 배송비 |  | 1 | 3500 | 3500 | 배송비 |  | 50,000원 이상 무료
 |  | 알씨뱅크 소계 |  |  |  | 14000
대건상사 | 센서·MCU·기판 | 네오디뮴 자석 Ø5×2 N35 | 초강력 네오디움 원형자석 5mm (Ø5×2.0T, N35) | 89 | 80 | 7120 | 기본 | https://dgmagnet.com/product/%EC%B4%88%EA%B0%95%EB%A0%A5-%EB%84%A4%EC%98%A4%EB%94%94%EC%9B%80-%EC%9B%90%ED%98%95%EC%9E%90%EC%84%9D-5mm/13/ | 건반 밑면 포켓(y67)에 S극이 아래로 가게 눌러 넣고 순간접착제 한 방울로 고정한다. 바로 아래 센서 바의 홀센서가 이 자석까지의 거리를 읽는다. 페달용 1개는 페달 발판 밑면 발끝 쪽에 S극이 아래로 가게 붙인다. 건반 88 + 페달 1 = 89개를 쓴다.
대건상사 | 본체·결합 | 네오디뮴 자석 Ø8×3 N35 (뚜껑) | 초강력 네오디움 원형자석 8mm — 3.0T (Ø8×3mm, N35) | 12 | 160 | 1920 | 기본 | https://dgmagnet.com/product/detail.html?product_no=17 | 가운데 유닛 뚜껑 3장이 미끄러지지 않게 붙여 둔다. 뚜껑마다 대각선 두 구석에 뚜껑 쪽·받침 쪽 한 쌍 = 12개를 Ø8.2 포켓에 순간접착제로 붙인다.
대건상사 | 배송비 | 배송비 |  | 1 | 2500 | 2500 | 배송비 |  | 50,000원 이상 무료
 |  | 대건상사 소계 |  |  |  | 11540
11번가 · 상우아트 | 본체·결합 | EVA 고밀도 폼 3T 330×490 검정 | 에바폼 EVA 컬러 고밀도 칼라스펀지 3T (E-210 검정, 330×490) | 3 | 2100 | 6300 | 기본 | https://www.11st.co.kr/products/7591566666 | 건반 모듈 7개와 끝 부속 2개 밑면 전체에 한 장씩 붙이는 3 mm 바닥 층이다(모듈 조각 163.5 × 211, 끝 부속 63 × 211·39.5 × 211). 남는 조각으로 스피커 유닛 가스켓 2개와 가운데 유닛 ↔ 스피커 파트 맞닿는 면의 띠를 만든다.
11번가 · 상우아트 | 건반 액션 | 대원 0.5T 접착 펠트지 30×45 (H-20 검정) | [대원] 얇은 칼라펠트지 H 두께0.5mm 접착 30x45cm (H-20 검정) | 1 | 1500 | 1500 | 기본 | https://www.11st.co.kr/products/8517880969 | 건반 104개(88 + 예비 16)의 스냅 노치 안쪽과 밸런스 핀 홈 양쪽 벽에 붙인다. 프레임 가이드 탭 88개의 양옆에도 붙이는 0.5T 부싱 천이다. 1.5T 쉼 펠트도 메리노 1T 위에 이 천을 한 겹 붙여 만든다. 한 장(1,350 cm²) 가운데 약 270 cm²만 쓴다(추정).
11번가 · 상우아트 | 배송비 | 배송비 |  | 1 | 3000 | 3000 | 배송비 |  | 70,000원 이상 무료
 |  | 11번가 · 상우아트 소계 |  |  |  | 10800
11번가 · 굿나잇몰 | 본체·결합 | 스텐 렌치볼트 M2.5 × 6 (Pi 고정) | 스텐 유두 렌치볼트 M2.5 × 6mm | 4 | 200 | 800 | 기본 | https://www.11st.co.kr/products/4236198413 | 가운데 유닛 CU 칸의 출력 CU 트레이 보스 4개에 Raspberry Pi 5를 바로 조인다. 4개 사용.
11번가 · 굿나잇몰 | 본체·결합 | 스텐 직결피스 8호 13 mm (뒷바) | 스텐 둥근머리 직결피스 8호(Ø4.2) 13mm | 36 | 40 | 1440 | 기본 | https://www.11st.co.kr/products/4353471537 | 뒷바 합판 면에 출력 부품을 고정한다. 도브테일 블록 4개 × 4, CU 트레이 4, I/O 판 4, 보조배터리 받침 4, 콤 받침(보관함) 4, XT30 받침 4 = 36개 사용.
11번가 · 굿나잇몰 | 본체·결합 | 스텐 직결피스 8호 16 mm (스피커 유닛) | 스텐 둥근머리 직결피스 8호(Ø4.2) 16mm | 8 | 50 | 400 | 기본 | https://www.11st.co.kr/products/4353471537 | 스피커 유닛 CW-100B25를 PETG 출력 앞판(배플)에 고정한다. 유닛마다 4개 × 2 = 8개.
11번가 · 굿나잇몰 | 본체·결합 | 스텐 직결피스 8호 19 mm (그릴) | 스텐 둥근머리 직결피스 8호(Ø4.2) 19mm | 8 | 50 | 400 | 기본 | https://www.11st.co.kr/products/4353471537 | PETG 육각 그릴을 스페이서 링(10 mm)에 통과시켜 스피커 앞판에 고정한다. 그릴마다 4곳 × 2 = 8개.
11번가 · 굿나잇몰 | 본체·결합 | 스텐 직결피스 8호 25 mm (고무발) | 스텐 둥근머리 직결피스 8호(Ø4.2) 25mm | 14 | 60 | 840 | 기본 | https://www.11st.co.kr/products/4353471537 | 고무발 14개(스피커 파트 4 × 2 + 가운데 유닛 6)를 출력 받침 4 mm와 함께 합판 바닥에 고정한다. 머리 밑에 M4 와셔를 끼운다. 14개 사용.
11번가 · 굿나잇몰 | 본체·결합 | 스텐 렌치볼트 M3 × 10 (센서 바·CU) | 스텐 유두 렌치볼트 M3 × 10mm | 36 | 60 | 2160 | 기본 | https://www.11st.co.kr/products/4236198413 | 센서 바·센서 기판을 왼쪽 받침 기둥에 고정한다: 모듈 7개 × 2 + 끝 부속 2개 × 2 = 18개. CU 트레이의 앰프 4·강압 모듈 4·앰프 입력 잭 기판 2 = 10개, 토글 래치 2개 × 4 = 8개. 합계 36개. 구매 목록 글은 PD 트리거 2·퓨즈 홀더 2를 더해 40개로 셌다.
11번가 · 굿나잇몰 | 본체·결합 | 스텐 렌치볼트 M3 × 6 (제어 기판) | 스텐 유두 렌치볼트 M3 × 6mm | 16 | 40 | 640 | 기본 | https://www.11st.co.kr/products/4236198413 | 모듈마다 제어 기판(RP2040-Zero·먹스)을 프레임의 매단 보스에 밑에서 2개로 조인다: 7 × 2 = 14개. 나머지 두 구석은 보스의 위치 핀이 잡는다. v3.2 기준으로 CU 트레이의 페달 보드(PED)도 같은 방식으로 2개를 쓴다.
11번가 · 굿나잇몰 | 본체·결합 | 스텐 평와셔 M4 (외경 9 × 0.5T) | 스텐 와셔 M4x9x0.5T | 14 | 10 | 140 | 기본 | https://www.11st.co.kr/products/4236198413 | 고무발 14개를 고정하는 25 mm 직결피스 머리 밑에 1개씩 끼운다. 14개 사용.
11번가 · 굿나잇몰 | 배송비 | 배송비 |  | 1 | 3500 | 3500 | 배송비
 |  | 11번가 · 굿나잇몰 소계 |  |  |  | 10320
11번가 · onezaze | 건반 액션 | SUS304 환봉 Ø4×1 m — 건반 봉 | [onezaze] 스텐환봉 절단판매 1M (4mm) | 2 | 1500 | 3000 | 기본 | https://www.11st.co.kr/products/1304631510 | 건반 시소의 축이다. 밸런스 레일의 봉 받침 11곳(y141, z21.5)에 놓고, 건반 노치가 위에서 스냅으로 문다. 모듈마다 161.4 mm 1토막 × 7 + 끝 부속 2토막(약 45·21) = 9토막을 쓰고, 1토막은 예비로 보관함에 둔다.
11번가 · onezaze | 건반 액션 | SUS304 환봉 Ø4×1 m — 레버 봉 | [onezaze] 스텐환봉 절단판매 1M (4mm) | 2 | 1500 | 3000 | 기본 | https://www.11st.co.kr/products/1304631510 | 무게 레버 12개가 매달려 도는 축이다(모듈 뒤쪽 y203.25, z33.5). 핀 보스 5개, 레버 허브 12개, 스프링 코일 12개를 꿰고, 이음 쪽 끝을 출력 마개로 막는다(반대쪽은 막힌 벽). 모듈마다 161.4 mm × 7 + 끝 부속 2토막(45.9·22.2) = 9토막을 쓰고, 1토막은 예비로 보관함에 둔다.
11번가 · onezaze | 배송비 | 배송비 |  | 1 | 3500 | 3500 | 배송비
 |  | 11번가 · onezaze 소계 |  |  |  | 9500
11번가 | 건반 액션 | 텅스텐 퍼티 22 g (낚시 싱커) | 텅스텐 퍼티 소프트 싱커 무게추 (낚시용, 22 g) | 1 | 8750 | 8750 | 소모품 | https://www.11st.co.kr/products/9579455646 | 조립 뒤 누르는 힘(DW)이 47~55 g을 벗어난 건반만 맞춘다. 가림판을 들고 레버 강철 앞 윗면(패드 앞)에 붙이면 DW가 오른다(1 g = 백 +1.23 / 흑 +1.14 g). 건반 앞에 붙이면 내려간다(1 g = −1.06 / −1.09 g).
11번가 | 배송비 | 배송비 |  | 1 | 0 | 0 | 배송비
 |  | 11번가 소계 |  |  |  | 8750
철물박사 | 본체·결합 | 매미고리 1-20 SUS 토글 래치 | 매미고리 1-20 (SUS304 스테인리스 토글 래치, 25×54mm) | 2 | 2400 | 4800 | 기본 | https://www.metaldiy.com/item/itemView.do?itemId=8806379117286 | 가운데 유닛과 왼쪽·오른쪽 스피커 파트의 이음 뒷면에 1개씩 = 2개. 도브테일이 위치를 잡고 래치가 당겨 잠근다. 도브테일 블록의 출력 받침에 M3 × 10 4개로 고정한다.
철물박사 | 배송비 | 배송비 |  | 1 | 3000 | 3000 | 배송비 |  | 100,000원 이상 무료
 |  | 철물박사 소계 |  |  |  | 7800
메카솔루션 | 센서·MCU·기판 | 만능기판 5×7 cm (제어 기판용) | PCB기판/양면기판/에폭시/프로토보드 (5x7cm) | 8 | 520 | 4160 | 기본 | https://www.mechasolution.com/goods/goods_view.php?goodsNo=329798 | O1~O7 모듈 제어 기판 7장(모듈 뒤쪽 바닥 구멍으로 밑에서 넣음) + CU 칸 안 페달 보드(PB) 1장 = 8장. RP2040-Zero, 먹스, 리본 블록, EXT 패드가 여기에 납땜된다.
메카솔루션 | 배송비 | 배송비 |  | 1 | 3000 | 3000 | 배송비
 |  | 메카솔루션 소계 |  |  |  | 7160
11번가 · 비젼몰 | 건반 액션 | 크레타칼라 흑연 가루 30 ml | 크레타칼라 흑연파우더(소/30ml) | 1 | 2750 | 2750 | 소모품 | https://www.11st.co.kr/products/1333385437 | 레버 캐리어 88개 밑의 캡스턴 펠트 띠 2T(S14)에서 캡스턴 머리가 닿는 면에 바른다. 붓으로 얇게 바르고 털어 낸다(조립 4단계). 단계 0 시편의 봉 구멍에도 조금 넣는다.
11번가 · 비젼몰 | 배송비 | 배송비 |  | 1 | 3000 | 3000 | 배송비 |  | 80,000원 이상 무료
 |  | 11번가 · 비젼몰 소계 |  |  |  | 5750
11번가 · 두유레디 | 오디오 | 흡음솜 300 g (할로우화이버) | 두유레디 구름솜 300g (100% 국내산 할로우화이버) | 1 | 2700 | 2700 | 기본 | https://www.11st.co.kr/products/2325598213 | 좌우 스피커 상자(밀폐, 내부 5.05 L) 안의 흡음재다. 상자당 40~60 g을 뒤판·옆판 쪽에 느슨하게 넣는다.
11번가 · 두유레디 | 배송비 | 배송비 |  | 1 | 3000 | 3000 | 배송비
 |  | 11번가 · 두유레디 소계 |  |  |  | 5700
무료 (다운로드) | 소프트웨어 | FluidSynth 2.6.1 (무료) | FluidSynth 2.6.1 | 1 | 0 | 0 | 기본 | https://www.fluidsynth.org/ | Pi 5의 microSD에 설치하는 피아노 소리 엔진. USB-MIDI 8개(O1~O7, PED)를 midi.autoconnect=1로 한 곳에 모으고, ALSA hw:로 USB 동글(L51)에 48 kHz로 낸다. 출력 리미터를 켜 둔다(D18).
무료 (다운로드) | 소프트웨어 | Salamander 그랜드 피아노 음원 (무료) | Salamander Grand Piano V3 (FreePats SF2판) | 1 | 0 | 0 | 기본 | https://freepats.zenvoid.org/Piano/acoustic-grand-piano.html | FluidSynth가 읽는 피아노 음원 SF2 파일(296 MB) 1개를 Pi 5 microSD에 넣는다.
무료 (다운로드) | 배송비 | 배송비 |  | 1 | 0 | 0 | 배송비
 |  | 무료 (다운로드) 소계 |  |  |  | 0
 |  | 최종 금액 (배송비 포함) |  |  |  | 654061

Sheet: 분류별 목록
분류 | 품목 | 수량 | 단가(원) | 금액(원) | 처음 수량 | 판매처 | 쓰는 곳 | 규격 | 링크
제어·전원 | Raspberry Pi 5 (2GB) | 1 | 119900 | 119900 | 1 | 아이씨뱅큐 | 가운데 유닛 CU 칸의 출력 트레이 보스 4개에 M2.5×6 나사(L47)로 1대를 고정한다. USB-A 한 포트에 허브 업스트림 선(W209), 다른 포트에 USB 동글(젠더 X701)을 꽂는다. 전원은 강압 모듈에서 C24 선으로 USB-C에 받는다. FluidSynth를 돌리고, 2단계 리듬게임도 콘솔 모드에서는 여기서 돌린다(PC 모드에서는 PC가 맡는다). | SoC: Broadcom BCM2712, Cortex-A76 4코어 2.4 GHz / 메모리: 2GB LPDDR4X / 포트: USB 3.0 ×2, USB 2.0 ×2, micro-HDMI ×2, USB-C 전원 / 기판 크기: 85 × 56 mm / KC: R-R-P2R-RP5 / 전원 설정: EEPROM PSU_MAX_CURRENT=5000, config.txt usb_max_current_enable=1 / 가격: 119,900원 (아이씨뱅큐 P016286897) | https://www.icbanq.com/P016286897
제어·전원 | PD 트리거 모듈 HUSB238 (20 V) | 1 | 4950 | 4950 | 1 | 아이씨뱅큐 · 아이씨뱅큐 (제노) | CU 칸 뒤판인 I/O 판 안쪽 포켓에 1개를 끼워 USB-C 구멍이 본체 밖을 향하게 한다. 충전기 선(C23)이나 보조배터리 선(C22)이 여기에 꽂힌다. 출력 +는 퓨즈 → 스위치로, −는 강압 모듈 IN− 별 접지점으로 간다(SCH-06 A601). | 칩: HUSB238 (상세 사진 'HUSB238 000DD') / 입력: USB-C 암 소켓, USB PD / 출력 전압: 5/9/12/15/20 V, 납땜 패드 3쌍 모두 열림 = 20 V(기본) / 최대 출력: 20 V 5 A 100 W (판매 표기) / 출력 단자: 구멍 패드 4개 (+ 둥근 2, − 네모 2) / 크기: 16.4 × 10 × 4.4 mm / 판매 코드: 제노 HAM6113, 아이씨뱅큐 P017179277, 4,950원 | https://www.icbanq.com/P017179277
제어·전원 | KCD1-101A 로커 스위치 (검정) | 1 | 385 | 385 | 1 | 엘레파츠 | I/O 판의 스위치 구멍에 1개를 끼운다(스냅인). 퓨즈 뒤 20 V 선에 들어가 앰프와 강압 모듈을 함께 켜고 끈다(SCH-06 SW601). | 형식: KCD1-101A, 2핀 ON-OFF(SPST), 오목형, I/O 표시 / 정격: 6 A 250 VAC / 10 A 125 VAC (DC 정격 미공개) / 패널 구멍: 약 19 × 13 mm (연구 노트 19.2 × 13.2, 테두리 21 × 15) / 단자: 러그 2개, 방향 구분 없음 / 가격: 385원 (엘레파츠 no=32569, 제품번호 EPX389PN) | https://www.eleparts.co.kr/goods/view?no=32569
제어·전원 | Coms BU914 퓨즈 홀더 (5×20) | 1 | 1110 | 1110 | 1 | 엘레파츠 | PD 트리거 출력 + 선(트리거와 스위치 사이)에 1개를 넣는다. 홀더 빨간 선 가운데를 잘라 양쪽을 납땜하고 수축튜브로 감싼다(SCH-06 F601). | 형식: 인라인 원형 홀더, 돌려 여는 뚜껑 / 퓨즈 규격: 5 × 20 mm 유리관용 / 선: 빨간 선 약 30 cm, 굵기 미공개 / 정격: 전압·전류 정격 미공개 / 가격: 1,110원 (엘레파츠 no=3237821) | https://www.eleparts.co.kr/goods/view?no=3237821
제어·전원 | Littelfuse 5 A 지연형 퓨즈 5×20 | 5 | 110 | 550 | 5 | 엘레파츠 | 퓨즈 홀더(i017) 안에 1개를 넣는다. 나머지 4개는 예비로 둔다. | 모델: Littelfuse 0218005.MXP (218 시리즈) / 크기: 5 × 20 mm 유리관 / 정격: 5 A 지연형(T, Slo-Blo), 250 VAC / 차단 용량: 50 A @ 250 VAC / 냉저항: 약 0.0104 Ω / 가격: 110원 × 5 = 550원 (엘레파츠 no=12766820) | https://www.eleparts.co.kr/goods/view?no=12766820
제어·전원 | USB-C↔C PD 60W 케이블 0.6 m | 1 | 1440 | 1440 | 1 | 엘레파츠 | 보조배터리로 칠 때만 쓴다. 보조배터리 칸의 배터리에서 낮은 칸막이 위 → CU 칸 → I/O 판 선 통과 구멍으로 빼서 PD 트리거 USB-C 입력에 1개를 꽂는다(W601). | 모델: MachLink ML-CPD606, 검정 / 단자: USB-C 수 ↔ USB-C 수, USB 2.0 / 전력: PD 60 W (20 V 3 A) / 길이: 0.6 m / 가격: 1,440원 (엘레파츠 no=17806172) | https://www.eleparts.co.kr/goods/view?no=17806172
센서·MCU·기판 | 홀센서 TI DRV5055A2QLPG | 100 | 891 | 89100 | 100 | 아이씨뱅큐 · 아이씨뱅큐 (LCSC 해외 재고) | 건반 밑 자석(Ø5×2)과의 거리를 전압으로 재는 센서다. 모듈 센서 기판마다 12개(U201~U212) × 7 = 84, 끝 부속 EL 3개(A0·A#0·B0) + ER 1개(C8), 페달 안 1개(U551) = 89개 사용. 건반용은 표시면을 위로 눕혀 센서 바 포켓에 넣고, 다리를 2.54 간격으로 벌려 꺾어 센서 기판에 납땜한다. 페달용은 페달 바닥판에 만능기판 자투리와 함께 표시면이 위로 오게 붙인다(SCH-05 주 1). | 품번: TI DRV5055A2QLPG (TO-92, LPG 벌크) / 감도: 3.3 V에서 30 mV/mT (A2 등급) / 선형 범위: 3.3 V에서 ±44 mT / 전원: 3.0~3.63 V (여기서는 3.3 V) / 자석 없을 때 출력: 1.59~1.71 V / 핀: 1 VCC · 2 GND · 3 OUT, 간격 1.27 mm / 몸통: 약 4.0 × 3.15 × 1.5 mm / 전류: 2 mA typ / 4 mA max (데이터시트 Rev C) | https://www.icbanq.com/P018076669
센서·MCU·기판 | 핀헤더 1×40 (2.54 mm, 수) | 9 | 165 | 1485 | 9 | 아이씨뱅큐 | 제어 기판에 먹스 모듈과 RP2040-Zero를 세워 납땜하는 핀이다. 먹스 7개 × (1×16 + 1×8) = 168핀, RP2040-Zero 8개(O1~O7 + 페달 보드) × 1×9 ×2 = 144핀, 합 312핀. 제로용은 플라스틱 몰드를 빼고 좌·우 줄만 쓴다(아래 줄 없음). | 형태: 1×40 수 핀헤더, 스트레이트, 1단 몰드 / 피치: 2.54 mm / 전체 길이: 11.5 mm / 나누기: 핀 손실 없이 부러뜨려 나눔 / 필요 핀: 먹스 168 + 제로 144 = 312핀 / 단가: 150원 + VAT = 165원 | https://www.icbanq.com/P005666127
센서·MCU·기판 | 100 nF 1206 칩 콘덴서 (삼성) | 97 | 44 | 4268 | 100 | 아이씨뱅큐 · 아이씨뱅큐 (LCSC 해외 재고) | 센서마다 붙이는 전원 안정 콘덴서다. 센서 기판 아랫면 센서마다 1개(C201~C212) × 7 = 84, 끝 부속 EL 3(C401~C403) + ER 1(C411), 페달 안 센서 1(C551), 페달 보드 ADC 필터 1(C501), 제어 기판 먹스 전원 C301 × 7 = 97개 사용. 센서용은 3V3–GND 패드 사이에, C301은 제어 기판 아랫면 먹스 VCC–GND 사이에, C501은 ADC 입력–GND 사이에 납땜한다. | 품번: Samsung CL31B104KCFNNNE / 용량: 100 nF ±10 % / 정격·유전체: 100 V, X7R / 크기: 1206 (3.2 × 1.6 × 1.25 mm) / 단가: 40원 + VAT = 44원 / 배송: LCSC 해외 재고, 약 1주 | https://www.icbanq.com/P014968846
센서·MCU·기판 | 10 µF 1206 칩 콘덴서 (50개) | 1 | 7150 | 7150 | 1 | 아이씨뱅큐 · 아이씨뱅큐 (오렌지반도체) | 센서 3V3 버스의 전원 안정 콘덴서다. 센서 기판 아랫면 버스 양 끝(C213 x8.25, C214 x158.11) × 7 = 14, 끝 부속 EL C404 + ER C412 = 16개 사용(회로 △1·△3). | 품명: C3216-10UF(K 16V) / 용량·정격: 10 µF ±10 %, 16 V / 크기: 1206 (3216) / 제조사·유전체: 표기 없음 (X5R 추정) / 값: 6,500원 + VAT = 7,150원 / 50개 / 배송: 국내 재고(오렌지반도체), 1~2일 | https://www.icbanq.com/P001248090
센서·MCU·기판 | 1 kΩ 1206 칩 저항 (Yageo) | 10 | 44 | 440 | 10 | 아이씨뱅큐 · 아이씨뱅큐 (element14 해외 재고) | 끝 부속 센서 기판 아랫면에서 센서 OUT에 직렬로 다는 저항이다. EL R401~R403(A0·A#0·B0) + ER R411(C8) = 4개 사용. 약 0.6 m 선의 용량이 센서 출력에 바로 걸리지 않게 한다(△8·△13). | 품번: Yageo RC1206JR-071KL / 값: 1 kΩ ±5 %, 1/4 W / 크기: 1206 (3216) 칩 / 단가: 40원 + VAT = 44원 (10개 440원) / 배송: element14 해외 재고, 4~6일 | https://www.icbanq.com/P011433924
센서·MCU·기판 | 16심 리본 케이블 2651-16P (센서 선) | 2 | 1529 | 3058 | 2 | 엘레파츠 | 모듈마다 센서 기판 J201과 제어 기판 J301을 잇는 리본 1장(16심 전부, 약 180 mm, W101~W107) × 7. 끝 부속 EL 리드 5심 350 mm(W401)와 ER 리드 3심 300 mm(W411)도 이 리본을 갈라 만든다. 양 끝은 커넥터 없이 기판 아랫면 2×8 구멍에 바로 납땜한다. | 품번: EUNSUNG 2651-16P (UL2651) / 심선: 16심, 28 AWG 연선(7/0.127) / 피치·폭: 1.27 mm, 폭 20.32 mm, 두께 0.89 mm / 표시: 1번 심 빨간 줄 / 정격: 105 °C, 300 V, 도체 저항 ≤ 224 Ω/km / 단가: 1,390원 + VAT = 1,529원/m | https://www.eleparts.co.kr/goods/view?no=425
센서·MCU·기판 | 16심 리본 케이블 추가 1 m (배선용) | 1 | 1529 | 1529 | 1 | 엘레파츠 | 리본을 한 가닥씩 갈라 기판 배선에 쓴다. 센서 기판 아랫면 3V3·GND 버스와 OUT → 리본 블록 선, 제어 기판 점 대 점 배선(SIG·S0~S3·EN·ID 브리지 등), 페달 잭 → 페달 보드 4가닥(W502, 약 10 cm). | 품번: EUNSUNG 2651-16P (C05와 같은 상품) / 심선: 28 AWG 연선(7/0.127), 16심 / 가닥 길이: 1 m × 16 = 약 16 m / 단가: 1,529원/m / 쓰는 법: 피복을 벗기고 납을 먹여 버스·점퍼로 | https://www.eleparts.co.kr/goods/view?no=425
센서·MCU·기판 | 탄소피막 저항 1 kΩ (10개) | 10 | 25 | 250 | 10 | 엘레파츠 | 1 kΩ 4개 사용. CU 칸 앰프 입력 저음 차단 필터의 풀다운 R701·R702(채널마다 1 µF 2개 병렬과 짝을 이루고, 앰프 입력 9 kΩ와 겹쳐 약 93 Hz), 페달 보드 ADC 입력 R501, 페달 안 센서 출력 바로 뒤 R551. | 품명: ABCO CFR 탄소피막 저항 / 값: 1 kΩ ±5 %, 1/4 W / 색띠: 갈·검·빨·금 / 크기: 리드형, 몸통 약 Ø2.5 × 6.3 mm (도면 풋프린트 DIN0207) / 값: 10개 250원 | https://www.eleparts.co.kr/goods/view?no=10911
센서·MCU·기판 | 탄소피막 저항 100 kΩ (10개) | 10 | 25 | 250 | 10 | 엘레파츠 | EXT 입력이 떠서 유령 음이 나지 않게 하는 풀다운이다(필수, △8). O1 제어 기판 R301·R302·R303(A0·A#0·B0), O7 제어 기판 R301(C8), 페달 보드 R502(팁 → GND) = 5개 사용. | 품명: ABCO CFR 탄소피막 저항 / 값: 100 kΩ ±5 %, 1/4 W / 색띠: 갈·검·노랑·금 / 크기: 리드형, 몸통 약 Ø2.5 × 6.3 mm / 값: 10개 250원 | https://www.eleparts.co.kr/goods/view?no=10993
센서·MCU·기판 | 탄소피막 저항 100 Ω (10개) | 10 | 25 | 250 | 10 | 엘레파츠 | 페달 보드(PB, CU 칸 안)의 링 급전 저항 R503이다. 100 Ω 5개를 병렬로 묶어 20 Ω로 쓴다. 플러그를 꽂는 순간 3V3–GND가 이어져도 전류를 약 165 mA로 막아 페달 보드가 리셋되지 않게 한다(△4, 필수). | 품명: ABCO CFR 탄소피막 저항 / 값: 100 Ω ±5 %, 1/4 W / 색띠: 갈·검·갈·금 / 쓰는 법: 5개 병렬 = 20 Ω / 값: 10개 250원 | https://www.eleparts.co.kr/goods/view?no=10873
센서·MCU·기판 | 만능기판 5×7 cm (제어 기판용) | 8 | 520 | 4160 | 8 | 메카솔루션 | O1~O7 모듈 제어 기판 7장(모듈 뒤쪽 바닥 구멍으로 밑에서 넣음) + CU 칸 안 페달 보드(PB) 1장 = 8장. RP2040-Zero, 먹스, 리본 블록, EXT 패드가 여기에 납땜된다. | 크기: 50 × 70 mm, 18 × 24 구멍 / 구조: 양면, 2.54 mm 간격 / 제어 기판 외곽: 70 × 50 mm (x47.25~117.25 × y145.5~195.5), 구멍 격자를 제로 핀 격자에 맞춰 자름 / 따낼 홈: x81.92~84.72 × y145.5~172.0 / 뚫을 구멍: M3 나사용 Ø3.2 ×2, 위치 핀용 Ø3.0 ×2 / 값: 520원 (VAT 포함) | https://www.mechasolution.com/goods/goods_view.php?goodsNo=329798
센서·MCU·기판 | RP2040-Zero 보드 (PP-A799-2) | 8 | 3300 | 26400 | 8 | 파츠파츠 직영몰 · 파츠파츠 (동신전자) | 모듈 O1~O7 제어 기판마다 1개(7개) + CU 칸 페달 보드 1개 = 8개. 먹스를 돌려 센서 값을 읽고 속도를 계산해 USB-MIDI 장치('Toccata O1'~'O7', 'Toccata PED')가 된다. 안쪽 구멍에 핀 헤더 1×9 ×2(몰드 뺌)로 세워 납땜하고, 밑면 부품 위에 캡톤을 깐다(약 +1.3 mm). | 판매 품번: 파츠파츠 PP-A799-2 (Waveshare RP2040-Zero 호환, 중국 OEM) / 크기: 18.0 × 23.5 mm / 칩: RP2040 (B2), 플래시 2 MB / USB: USB-C, USB-MIDI 장치 / 쓰는 핀: GP26(ADC0) = 먹스 SIG, GP2~5 = S0~S3, GP6~8 = ID, GP14 = PED_SEL / 3V3 전원: 원본은 RT9013-33 500 mA LDO (복제품은 확인 필요) / 값: 3,300원 (VAT 포함) | https://parts-parts.co.kr/product/detail.html?product_no=2383
센서·MCU·기판 | 16채널 먹스 모듈 CD74HC4067 | 7 | 500 | 3500 | 7 | 파츠파츠 직영몰 · 파츠파츠 (동신전자) | 모듈 O1~O7 제어 기판마다 1개(x54.93~72.71에 세로로) = 7개. 그 옥타브 홀센서 12개(C0~C11)와 끝 부속 EXT(C12~C15: O1은 A0·A#0·B0, O7은 C8)를 RP2040-Zero ADC0(GP26) 한 채널로 읽는다. 소켓 없이 핀헤더로 기판에 바로 납땜한다. | 칩: CD74HC4067 (HC, SSOP-24), 16채널 아날로그 먹스 / 기판: 약 40.6 × 17.8 mm, 두 줄 간격 15.24 mm / 핀: C0~C15 (1×16) + GND·VCC·EN·S0~S3·SIG (1×8), 2.54 mm / 고정 구멍: Ø3.3 ×2 / 기판 위 부품: 0.1 µF(VCC–GND), EN–GND 10 kΩ / 값: 500원 (VAT 포함) | https://parts-parts.co.kr/product/detail.html?product_no=303
센서·MCU·기판 | 네오디뮴 자석 Ø5×2 N35 | 89 | 80 | 7120 | 100 | 대건상사 | 건반 밑면 포켓(y67)에 S극이 아래로 가게 눌러 넣고 순간접착제 한 방울로 고정한다. 바로 아래 센서 바의 홀센서가 이 자석까지의 거리를 읽는다. 페달용 1개는 페달 발판 밑면 발끝 쪽에 S극이 아래로 가게 붙인다. 건반 88 + 페달 1 = 89개를 쓴다. | 치수: Ø5 × 2 mm (2.0T 옵션) / 재질·등급: NdFeB N35 (Br 약 1.20 T, v3 자료) / 자화 방향: 두께 방향 (원판) / 설치: 건반 밑 포켓 Ø5.2 × 2.1, S극 아래, y67 / 센서 거리: 쉼 백 10.82 / 흑 13.35 mm, 바닥 약 5.5 mm / 판매: 대건상사 80원/개, 배송비 2,500원 (5만 원 이상 무료) | https://dgmagnet.com/product/%EC%B4%88%EA%B0%95%EB%A0%A5-%EB%84%A4%EC%98%A4%EB%94%94%EC%9B%80-%EC%9B%90%ED%98%95%EC%9E%90%EC%84%9D-5mm/13/
센서·MCU·기판 | JST-XH 6핀 연장선 200 mm (5S) | 2 | 3000 | 6000 | 2 | 알씨뱅크 | 끝 부속 센서 선과 O1·O7 제어 기판을 잇는 6핀 커넥터 2쌍이다(왼쪽 EL ↔ O1, 오른쪽 ER ↔ O7). 200 mm 선을 모듈 쪽 150 mm · 끝 부속 쪽 50 mm로 자른다. 150 mm 쪽은 O1·O7 제어 기판 J302 패드(아랫면)에, 50 mm 쪽은 끝 부속 리본 리드에 납땜하고, 두 쪽을 모듈 뒤 통로에서 꽂는다. | 커넥터: JST-XH 6핀 (5S 밸런스 연장선, BU-LP 5S) / 피치: 2.50 mm / 전선: 22 AWG 실리콘, 200 mm / 선 색: 빨강 1 + 검정 5 / 자르는 길이: 모듈 쪽 150 · 끝 부속 쪽 50 mm / 값: 3,000원 | https://www.rcbank.co.kr/shop/goods/goods_view.php?goodsno=29812
건반 액션 | M3 육각너트 강철 (LCSC C133377) | 92 | 11 | 1012 | 100 | 아이씨뱅큐 · 아이씨뱅큐 (LCSC 해외 재고) | 건반 꼬리 숨은 빔의 너트 홈(폭 5.6)에 옆에서 밀어 넣어 캡스턴 나사(M3×6)를 받는다. 건반마다 1개라 모듈 12 × 7 + 끝 부속 4 = 88개다. 여기에 끝 부속 ↔ 스피커 브래킷 연결 4개(v3.2 기준, 왼쪽·오른쪽 끝 부속에 가로 너트 2개씩)를 더해 92개를 쓴다. | 규격: M3 육각너트 (건반 빔 너트 홈 폭 5.6에 들어가는 표준 크기) / 재질: 강철 (LCSC 표기 'Hex Nut M3 Steel') / 품번: XHHD, LCSC C133377 / 무게: 개당 약 0.4 g (계산값) / 가격: 11원 (VAT 포함), 아이씨뱅큐 합배송 | https://www.icbanq.com/P015976209
건반 액션 | 캡스턴 나사 M3×6 버튼헤드 SUS304 | 100 | 11 | 1100 | 100 | 아이씨뱅큐 | 건반 꼬리 숨은 빔의 캡스턴이다. 머리가 레버 밑 펠트 띠를 들어 올린다. 1/8회전(0.0625 mm)씩 돌려 높이를 맞춘다. 모듈 12 × 7 + 끝 부속 4 = 88개를 쓰고, 건반을 넣기 전에 벤치 지그와 가짜 레버(T2)에서 맞춘다. | 규격: ISO 7380 M3×6 (M3-0.5, 나사 길이 6 mm) / 재질: SUS304 스테인리스 / 머리: 둥근 버튼 Ø5.7 × 1.65, 육각 구멍 2.0 mm (ISO 7380 표준값) / 제조: AOFENG / 조정: 1/8회전 = 0.0625 mm = DW 백 +0.20 / 흑 +0.11 g / 가격: 11원 (VAT 포함), 아이씨뱅큐 해외 재고 약 1주 | https://www.icbanq.com/P015973844
건반 액션 | 대원 0.5T 접착 펠트지 30×45 (H-20 검정) | 1 | 1500 | 1500 | 1 | 11번가 · 상우아트 | 건반 104개(88 + 예비 16)의 스냅 노치 안쪽과 밸런스 핀 홈 양쪽 벽에 붙인다. 프레임 가이드 탭 88개의 양옆에도 붙이는 0.5T 부싱 천이다. 1.5T 쉼 펠트도 메리노 1T 위에 이 천을 한 겹 붙여 만든다. 한 장(1,350 cm²) 가운데 약 270 cm²만 쓴다(추정). | 제품: 대원 얇은 칼라펠트지 H, 색 H-20 검정 / 두께: 0.5 mm (접착층 포함 여부 표기 없음) / 크기: 300 × 450 mm / 뒷면: 접착형 / 재질: 폴리에스터 공예 펠트 (양모 아님) / 설계 자리: 노치 R2.55 → 유효 R2.05, 핀 홈 3.2 → 2.2, 탭 옆 놀음 ±0.05 / 가격: 1,500원/장 (11번가 상우아트) | https://www.11st.co.kr/products/8517880969
건반 액션 | 텅스텐 퍼티 22 g (낚시 싱커) | 1 | 8750 | 8750 | 1 | 11번가 · 골드그로브 | 조립 뒤 누르는 힘(DW)이 47~55 g을 벗어난 건반만 맞춘다. 가림판을 들고 레버 강철 앞 윗면(패드 앞)에 붙이면 DW가 오른다(1 g = 백 +1.23 / 흑 +1.14 g). 건반 앞에 붙이면 내려간다(1 g = −1.06 / −1.09 g). | 재질: 텅스텐 퍼티 (약 10 g/cm³, v3 자료) / 무게: 22 g / 용도: 낚시용 소프트 싱커 / 효과 (강철 앞): 1 g = DW 백 +1.23 / 흑 +1.14 g / 효과 (건반 앞): 1 g = DW 백 −1.06 / 흑 −1.09 g / 판매: 11번가 골드그로브 8,750원 | https://www.11st.co.kr/products/9579455646
건반 액션 | SUS304 환봉 Ø4×1 m — 건반 봉 | 2 | 1500 | 3000 | 2 | 11번가 · onezaze | 건반 시소의 축이다. 밸런스 레일의 봉 받침 11곳(y141, z21.5)에 놓고, 건반 노치가 위에서 스냅으로 문다. 모듈마다 161.4 mm 1토막 × 7 + 끝 부속 2토막(약 45·21) = 9토막을 쓰고, 1토막은 예비로 보관함에 둔다. | 재질: SUS304 스테인리스 환봉 / 지름: Ø4 (설계 h9 = 3.970~4.000) / 길이: 1000 mm / 자를 길이: 모듈 161.4 ± 0.2 × 7 (+예비 1), 끝 부속 약 45 / 약 21 / 토막 무게: 161.4 mm당 16.08 g / 판매: 11번가 onezaze 1,500원, 배송비 3,500원 | https://www.11st.co.kr/products/1304631510
건반 액션 | SUS304 환봉 Ø4×1 m — 레버 봉 | 2 | 1500 | 3000 | 2 | 11번가 · onezaze | 무게 레버 12개가 매달려 도는 축이다(모듈 뒤쪽 y203.25, z33.5). 핀 보스 5개, 레버 허브 12개, 스프링 코일 12개를 꿰고, 이음 쪽 끝을 출력 마개로 막는다(반대쪽은 막힌 벽). 모듈마다 161.4 mm × 7 + 끝 부속 2토막(45.9·22.2) = 9토막을 쓰고, 1토막은 예비로 보관함에 둔다. | 재질: SUS304 스테인리스 환봉 (풀림재 항복 205 MPa로 충분) / 지름: Ø4 (설계 h9 = 3.970~4.000) / 길이: 1000 mm / 자를 길이: 모듈 161.4 ± 0.2 × 7 (+예비 1), 끝 부속 45.9 / 22.2 / 꿰는 것: 핀 보스 5 (Ø3.9 출력 → Ø4.0 드릴), 레버 허브 12, 스프링 코일 12 / 판매: 11번가 onezaze 1,500원, 배송비 3,500원 (건반 봉과 합배송) | https://www.11st.co.kr/products/1304631510
건반 액션 | OHP 필름 A4 0.1 mm 20매 (PET 심용) | 1 | 2739 | 2739 | 1 | 나비엠알오 · 나비엠알오 (카피어랜드) | 업스톱 패드와 패드 바 쐐기 사이에 끼우는 0.1 mm PET 심이다. 6×12.2로 잘라 조립 10단계와 12장 업스톱 시점 조정에서 건반마다 필요한 만큼 넣고 뺀다(부품표 추정 약 50장). 단계 0 시험 1·6·12·14에서는 얇은 게이지로도 쓴다. 남는 심은 건반 보관함 작은 부품 통에 둔다. | 제품: copierland 레이저프린터용 고투명 OHP 필름 / 두께: 100 mic (0.1 mm, 포장 사진 표기) / 크기·수량: A4 (210 × 297 mm) 20매 / 자를 크기: 6 × 12.2 mm (패드와 같음, D16) / 한 장의 효과: 레버가 0.23° / 0.24° 먼저 닿음 = 건반 앞 0.18 / 0.22 mm (백 / 흑) / 가격: 5,980원, 무료배송 (11번가 핑블샵) | https://www.navimro.com/g/37021/
건반 액션 | 크레타칼라 흑연 가루 30 ml | 1 | 2750 | 2750 | 1 | 11번가 · 비젼몰 | 레버 캐리어 88개 밑의 캡스턴 펠트 띠 2T(S14)에서 캡스턴 머리가 닿는 면에 바른다. 붓으로 얇게 바르고 털어 낸다(조립 4단계). 단계 0 시편의 봉 구멍에도 조금 넣는다. | 제품: 크레타칼라(Cretacolor) 흑연 파우더 소 / 용량: 30 ml / 종류: 미술용 흑연 가루 / 바르는 곳: 캡스턴 펠트 띠 2T (y176.5~192.0, 폭 7) / 쓰는 양: 몇 g (펠트 띠 88장에 얇게) / 가격: 2,750원 + 배송 3,000원 (11번가 비젼몰) | https://www.11st.co.kr/products/1333385437
건반 액션 | 세메다인 슈퍼X 백색 20 mL (MS 폴리머) | 2 | 8000 | 16000 | 2 | 11번가 · 주영종합상사 | 레버 캐리어에 강철 블록을 붙이는 탄성 접착제다. 강철의 두 19×40 옆면에 얇게(블록당 약 0.2 mL) 바르고 밑에서 스냅으로 끼운 뒤 24시간 굳힌다. 조립 4단계에서 레버 88개에, 단계 0 시험 20에서 캐리어 2개에 쓴다. | 종류: 1액형 습기 경화 MS 폴리머(변성 실리콘) 탄성 접착제 / 제품: 세메다인 슈퍼X 8008 백색 (AX-022) / 용량·색: 20 mL 튜브, 흰색 / 접착층: 한쪽 0.10 mm (캐리어 주머니 9.2 − 강철 9.0) / 설계 값: 전단 탄성 G 약 1 MPa, 겹침 전단 1.5 MPa (가정) / 굳힘: 24시간 (선택기 카드: 24~48시간이면 쓸 수 있는 강도) / 판매: 11번가 주영종합상사 8,000원, 배송비 3,000원 | https://www.11st.co.kr/products/7459325704
건반 액션 | 메리노 울 펠트 2T 20×30 cm (35 블랙) | 1 | 13800 | 13800 | 1 | 스튜디오분트 | 세 곳에 쓴다. 레버 88개 밑 캡스턴 펠트 띠(폭 7 × y176.5~192.0), 앞 레일의 앞 펠트(백건 줄은 모듈 7개·끝 부속 2개 전체 폭 y1.5~9.0 띠, 흑건은 36개 자리마다 y54.5~59.0 조각; 둘 다 하네나이트 1T 위), 키퍼 훅 88개 밑 펠트(5.2 × 3)이다. 한 장(600 cm²) 가운데 약 220 cm²를 쓴다(r4.5 치수로 다시 셈, 추정). | 제품: 스튜디오분트 100% 메리노양모 70수 펠트지 (상품 4117) / 두께: 2 mm / 크기: 200 × 300 mm / 색: 35 블랙 / 재질: 울 100 % / 쓰는 곳: 캡스턴 띠 S14 · 키퍼 S20 · 앞 펠트 S21·S22 / 가격: 13,800원 (스튜디오분트 배송비 3,000원은 따로 한 줄, 147행) | https://studiobunt.com/product/detail.html?product_no=4117
건반 액션 | 메리노 울 펠트 1T 20×30 cm (80 블랙) | 1 | 6900 | 6900 | 1 | 스튜디오분트 | 두 곳에 쓴다. 업스톱 패드 100개(88 + 예비 12)의 강철이 닿는 면 펠트(6×12.2)와, 건반 104개(88 + 예비 16) 꼬리 밑 쉼 펠트 1.5T의 바탕이다. 쉼 펠트는 이 1T 위에 0.5T 천을 한 겹 붙여 2.7×8로 자른다(F·F#는 더 짧게). 한 장(600 cm²) 가운데 약 100 cm²를 쓴다(추정). | 제품: 스튜디오분트 100% 메리노양모 70수 펠트지 (상품 1157) / 두께: 1 mm / 크기: 200 × 300 mm / 색: 80 블랙 / 재질: 울 100 % / 쓰는 곳: 패드 닿는 면 1T (P16·D11), 쉼 펠트 1.5T 바탕 (D10·P28) / 가격: 6,900원 | https://studiobunt.com/product/detail.html?product_no=1157
건반 액션 | 강철 띠 9T×19×1 m (강철 블록용) | 4 | 8610 | 34440 | 4 | 올스틸샵 | 1 m 띠를 40 mm씩 잘라 강철 블록(9×19×40, 53.7 g)을 만든다. 블록은 레버 캐리어에 밑에서 스냅으로 끼우고 MS 폴리머로 붙이는 무게 추이며, 드러난 윗면이 업스톱 패드에 닿는다. 레버마다 1개로 모듈 12 × 7 + 끝 부속 4 = 88개를 쓴다. | 받는 형태: 9 × 19 × 1000 mm 강철 띠, 1장 1.342 kg / 재질: SS275 (설계서 SS400) / 블록 치수: 9 × 19 × 40 mm, 53.7 g, 모따기 없음 (버만 제거) / 두께 허용: 8.9~9.1 mm만 씀 (캐리어 주머니 9.2) / 자르기: 40 mm × 90번, 쇠톱 약 4시간 (DESIGN 16장) / 가격: 장당 8,610원, 배송비 3,500원 (0~10 kg) | https://www.allsteelshop.com/product/squareplate/9t
건반 액션 | 밸런스 핀 Ø2×12 SUS304 (100개) | 1 | 16600 | 16600 | 1 | 나사코리아 nasakorea.com | 밸런스 레일(y135.3)에 핀 높이 게이지(T3)로 눌러 넣고 꼭대기를 z23.30에 맞춘다. 건반 블록 밑 홈(천 0.5T)이 이 핀을 물어 건반 뒤쪽의 좌우 위치를 잡는다. 모듈 12 × 7 + 끝 부속 4 = 88개를 쓴다. 이 밖에 벤치 지그(T1a) 핀 구멍에 1개, 단계 0 시험 P 쿠폰(C07a, 구멍 5개)에 5개까지 쓴다. 4개는 보관함 작은 부품 통에 둔다. | 규격: ISO 2338 (GB119.1) 평행 핀 Ø2 × 12 / 재질: STS304 스테인리스 / 설치 위치: 밸런스 레일 y135.3, 꼭대기 z23.30 / 합격 높이: GO/NO-GO 게이지로 z23.20~23.40 / 가격: 16,600원 (판매가 100 + 옵션 16,500), 배송비 3,300원 | https://www.nasakorea.com/goods/goods_view.php?goodsNo=6009
건반 액션 | 미스미 토션스프링 C-UA90R5-3-0.5 | 100 | 310 | 31000 | 100 | 한국미스미 | 레버 허브의 스프링 주머니(Ø6.6×3.0)에 넣고 레버 봉에 꿴다. 짧은 다리(8.0)는 허브의 가둠 홈에, 긴 다리(22.3)는 뒷벽 홈에 걸어 레버를 아래로 민다(DW 51.9 g 중 약 11 g). 레버마다 1개로 88개를 쓴다. 단계 0 시험 8에 1개, 시험 13에 3개를 더 쓰고(합 92개), 남는 8개는 보관함 옆 칸에 둔다. | 품번: 한국미스미 경제형 C-UA90R5-3-0.5 / 재질: SUS304-WPB, 선경 0.5 mm / 코일: 안지름 5 (바깥 약 6), 3권 (몸통 3.25권), 오른쪽 감기 / 암: 두 암 90°, 길이 50 / 50 mm로 옴 (상품명 '암 50/50') / 자를 길이: 긴 다리 22.3 (코일 중심→끝, 코일을 떠나는 점에서 22.13), 짧은 다리 8.0 (코일을 떠나는 점에서) / 잘린 뒤: k_t 8.44 N·mm/rad, 자유각 −28.4°, 쉼 4.19 / 바닥 6.03 N·mm / 가격: 100~236개 282원 + VAT = 310원 | https://kr.misumi-ec.com/vona2/detail/110310556289/?HissuCode=C-UA90R5-3-0.5
건반 액션 | WAKI PORON 5T 점착 100×100 (PON-02) | 1 | 3399 | 3399 | 1 | 나비엠알오 | 업스톱 패드에 들어가는 폼이다. 6×12.2로 잘라 강철이 닿는 쪽에 펠트 1T를 겹치고 패드 바 쐐기에 붙인다. 모듈마다 12개 × 7 + 끝 부속 4 = 88개에, 예비 12개(건반 보관함 옆 칸)를 더해 100개를 쓴다. | 제품: WAKI PORON 스폰지 점착 PON-02 (나비엠알오 K41576125) / 재질: INOAC PORON 미세셀 우레탄 (등급 표기 없음) / 크기: 100 × 100 × 5 mm / 뒷면: 한 면 아크릴 점착 / 색: 검정 / 설계 요구: 폼 6T, 25 % 압축 0.36 MPa ± 30 %, 패드 실효 e ≤ 0.07 / 납기: 10/12 출하 예정, 해외 직수입·반품 불가 / 가격: 3,399원 (VAT 포함) | https://www.navimro.com/g/1028764/
건반 액션 | WAKI 하네나이트 1T 170×245 (HNT002) | 1 | 16489 | 16489 | 1 | 나비엠알오 | 앞 레일의 앞 펠트 2T 밑에 까는 1T 저반발 층이다(S21·S22). 백건 줄은 모듈 7개·끝 부속 2개마다 전체 폭 띠(y1.5~9.0, 폭 7.5, 합쳐 약 1.2 m)로, 흑건은 36개 자리마다 조각(y54.5~59.0, 폭 4.5 × 약 10.4)으로 잘라 붙인다. 필요한 면적은 약 110 cm²이다(추정). | 제품: WAKI 충격흡수재 하네나이트 HNT002 (나비엠알오 K41587651) / 재질: 저반발 제진 고무 (나비 표기 NBR, 내외고무) / 크기: 170 × 245 × 1 mm / 반발 탄성: 상온 10 % 미만 (제조사 자료) / 색: 검정 / 설계 요구: 저반발 PU 1T, 앞 펠트 실효 e ≤ 0.22 (설계 0.20) / 납기: 10/07 출하 예정, 해외 직수입·반품 불가 / 가격: 16,489원 (VAT 포함) | https://www.navimro.com/g/1029233/
오디오 | 1 µF 적층 세라믹 콘덴서 50 V | 4 | 133 | 532 | 5 | 아이씨뱅큐 · 아이씨뱅큐 (동신전자) | CU 트레이의 앰프 입력 잭(J702) 기판에서 앰프 입력 앞 저음 차단 필터로 쓴다. 채널마다 2개를 병렬(2 µF)로 신호에 직렬로 넣어 C701·C702(왼쪽), C703·C704(오른쪽) = 4개를 쓴다. 채널마다 1 kΩ(R701·R702, L29 줄)을 앰프 IN G(AGND)로 달아 약 93 Hz 아래를 줄인다. | 용량: 1 µF (몸통 표기 105) / 유전체·정격: X7R, 50 V / 형태: 리드형 적층 세라믹, 극성 없음, 만능기판에 바로 납땜 / 필터: 2 µF 직렬 + 1 kΩ 병렬. 앰프 입력(약 9 kΩ)과 보드 입력 콘덴서까지 넣어 계산하면 fc ≈ 93 Hz (필터만 따로 보면 79.6 Hz) / 판매: 아이씨뱅큐 P014159115 (동신전자) | https://www.icbanq.com/P014159115
오디오 | PJ-313 3.5 mm 스테레오 잭 | 2 | 198 | 396 | 3 | 엘레파츠 | 3개 모두 쓴다. ① 왼쪽 끝 부속 볼 앞면의 헤드폰 잭(J701) ② 가운데 유닛 I/O 판의 댐퍼 페달 잭(J501) ③ CU 트레이의 앰프 입력 잭(J702). 너트 없는 PCB형이라 만능기판 자투리에 납땜해서 단다. 자투리는 12×18 기판(i081) 둘째 장의 남는 부분에서 자른다. 5×7 기판 8장은 제어 기판과 페달 보드에 모두 쓰기 때문이다. 헤드폰 잭은 왼쪽 볼의 출력 포켓에 끼운다. | 규격: 3.5 mm 스테레오(TRS) 암잭 / 핀: 5핀 T·TN·R·RN·S (팁·링 노멀 접점) / 실장: 스루홀 PCB형, 너트 없음(패널형 아님) / 제조: BSUN PJ-313 / 판매: 엘레파츠 67811 | https://www.eleparts.co.kr/goods/view?no=67811
오디오 | XT30U-M 수 커넥터 (선 10 cm) | 2 | 1760 | 3520 | 2 | 엘레파츠 | 앰프 쪽 스피커선 커넥터다. 앰프 출력에서 뒷바 아래 케이블 통로를 지나 양 끝으로 나온 스피커선(C13, 약 0.6 m) 끝에 1개씩 납땜한다(왼쪽 X703, 오른쪽 X705). 설치할 때 통로 안 XT30 받침(스피커 파트 쪽)에 끼워 둔 암(XT30U-F)에 꽂는다. | 모델: AMASS XT30U-M (수) / 리드: 18 AWG 실리콘 10 cm, 빨강·검정 / 정격: 15 A (순간 30 A). 스피커 전류는 약 1.6 A rms / 크기: 앞면 약 10.2 × 5.2 mm, 길이 13.7 mm, 핀 간격 5.0 mm / 극성: 납작한 면 = +, 모따기 면 = − (KiCad 패드 1 = −, 2 = +) / 판매: 엘레파츠 12779720 | https://www.eleparts.co.kr/goods/view?no=12779720
오디오 | XT30U-F 암 커넥터 (선 10 cm) | 2 | 1760 | 3520 | 2 | 엘레파츠 | 스피커 쪽 커넥터다. 좌우 스피커 파트 안에서 유닛 단자에 이은 스피커선(C13, 약 0.3 m)을 앞판 아래 선 구멍으로 빼서 끝에 1개씩 납땜한다(왼쪽 X704, 오른쪽 X706). 이 커넥터를 케이블 통로 안의 출력 XT30 받침(스피커 파트 쪽)에 끼워 두고, 설치할 때 앰프 쪽 수(XT30U-M)를 꽂는다. | 모델: AMASS XT30U-F (암) / 리드: 18 AWG 실리콘 10 cm, 빨강·검정 / 정격: 15 A (순간 30 A). 스피커 전류는 약 1.6 A rms / 크기: 앞면 약 10.2 × 5.2 mm, 길이 12.4 mm, 핀 간격 5.0 mm / 극성: 납작한 면 = +, 모따기 면 = − (KiCad 패드 1 = −, 2 = +) / 판매: 엘레파츠 12779721 | https://www.eleparts.co.kr/goods/view?no=12779721
오디오 | 스피커선 16 AWG 7 m (프리즘) | 1 | 14300 | 14300 | 1 | 엘레파츠 | 세 곳에 잘라 쓴다. 앰프 → 통로 → XT30 수 좌우 각 약 0.6 m(W703·W705), 스피커 파트 안 유닛 → XT30 암 각 약 0.3 m(W704·W706), 20 V 전원선 약 1 m(PD 트리거 → 퓨즈 → 스위치 → 앰프·강압 모듈, W602). 모두 약 2.8 m를 쓴다. | 규격: 16 AWG (1.31 mm²), 50가닥, 2심 / 길이: 7 m / 색: 검정 겉피복, 속선 주황·흰색(판매 사진 기준) / 모델: 케이블스토어 프리즘 PRS-50B07 / 판매: 엘레파츠 18388615 | https://www.eleparts.co.kr/goods/view?no=18388615
오디오 | 3.5 mm 스테레오 AUX 선 1.5 m | 2 | 1710 | 3420 | 2 | 엘레파츠 | 2가닥을 쓴다. 선 ①(W701)은 CU의 동글(L51) → 왼쪽 볼 헤드폰 잭(J701), 선 ②(W702)는 헤드폰 잭 노멀 접점 → CU 트레이 앰프 입력 잭(J702)이다. 둘 다 끝 부속 쪽 플러그를 잘라 잭에 납땜하고 CU 쪽 플러그만 남긴다(각 약 0.7 m 사용). | 커넥터: 3.5 mm 3극(TRS) 수 ↔ 수 / 길이: 1.5 m / 모델: Coms AV0176 / 배선: 팁 = L, 링 = R, 슬리브 = AGND / 판매: 엘레파츠 2925673 | https://www.eleparts.co.kr/goods/view?no=2925673
오디오 | 삼미 CW-100B25 4인치 스피커 8 Ω | 2 | 9600 | 19200 | 2 | 11번가 · 세운상가새한음향 | 좌우 스피커 파트(뒷바 양 끝, 오꾸메 밀폐 상자 내부 5.05 L)의 PETG 앞판 컷아웃(Ø94)에 1개씩 = 2개. 연주자 쪽을 향하게 EVA 가스켓(MEV1 3T 자투리)을 대고 직결피스 16 mm(L49) 4개씩으로 조인다. 선은 앞판 아래 선 구멍(본드로 막음)으로 빼서 XT30 암(L61)에 잇는다. | 형식: 4인치 풀레인지, 8 Ω (Re 6.2 Ω) / 입력: 정격 25 W / 최대 50 W / 감도: 86 dB/1W/1m(판매처) · 89±2 dB(검사성적서) / 크기: 프레임 105 × 105 mm, 깊이 57 + 플랜지 4 mm, 컷아웃 약 Ø94 / 장착: 4-Ø4.8×6.8 장공 (PCD Ø115) / 무게: 0.74 kg (자석 280 g) / Fs: 128 Hz(판매처) / 90±18 Hz(검사성적서) — 자료가 다름 | https://www.11st.co.kr/products/1565354988
오디오 | 흡음솜 300 g (할로우화이버) | 1 | 2700 | 2700 | 1 | 11번가 · 두유레디 | 좌우 스피커 상자(밀폐, 내부 5.05 L) 안의 흡음재다. 상자당 40~60 g을 뒤판·옆판 쪽에 느슨하게 넣는다. | 소재: 100% 국내산 할로우화이버(폴리에스터), 재생솜 아님 / 용량: 300 g / 사용량: 상자당 40~60 g (두 상자 약 80~120 g) / 안전: EU RoHS 유해물질 시험성적서(FITI) / 판매: 11번가 두유레디 | https://www.11st.co.kr/products/2325598213
오디오 | Apple USB-C 헤드폰 어댑터 | 1 | 14900 | 14900 | 1 | Apple Store 온라인 · Apple | CU 칸에서 젠더(L52)로 Pi 5 USB-A 포트에 바로 꽂는 USB 사운드 장치(DAC + 헤드폰 앰프)다. FluidSynth 소리를 아날로그로 바꿔 선 ①(C14)로 왼쪽 볼 헤드폰 잭에 보낸다. 헤드폰을 안 꽂으면 노멀 접점을 거쳐 앰프로 간다. | 모델: Apple MW2Q3KH/A (USB-C → 3.5 mm) / 형식: USB 오디오 클래스 2.0 DAC + 헤드폰 앰프, 드라이버 불필요, 리눅스에서 48 kHz만 지원 / 측정(외부 자료): SNR 113 dB, SINAD 98 dB, 출력 임피던스 약 0.3~0.9 Ω / 출력: 미국판 A2049 약 1.0 Vrms, 유럽판 A2155 약 0.5 Vrms. 한국판은 확인 못 해 0.5~1 Vrms로 설계 / 지연: USB 오디오가 1~3 ms를 더함 (키→소리 계산 8~10 ms, 한계 10 ms) / 판매: Apple Store 온라인, 무료 배송 | https://www.apple.com/kr/shop/product/mw2q3kh/a
본체·결합 | V-tech 순간접착제 5 g (VT-041) | 1 | 1100 | 1100 | 1 | 아이씨뱅큐 · 아이씨뱅큐 (크레텍) | 건반 밑 센서 자석(Ø5×2) 89개(건반 88 + 페달 1)를 포켓(Ø5.2)에 눌러 넣은 뒤 한 방울씩 떨어뜨려 고정한다. 가운데 유닛 뚜껑 자석(Ø8×3) 12개도 이것으로 Ø8.2 포켓에 붙인다. 단계 0 시험 키트(C01 봉·시험 레버의 강철 고정 등)에도 조금 쓴다. | 제품: V-tech 강력 순간접착제 VT-041 (크레텍 814-2010) / 용량: 5 g / 성분·점도: 판매 페이지에 표기 없음 / 대신한 것: 록타이트 401 20 g (C18, 절감안 ME8) / 판매처·가격: 아이씨뱅큐(크레텍), 1,100원 | https://www.icbanq.com/P015309984
본체·결합 | 화성고무 피스고무발 28×5 (RUB-E2) | 20 | 583 | 11660 | 20 | 엘레파츠 | 왼쪽·오른쪽 스피커 파트 밑에 4개씩, 가운데 유닛 밑에 6개 = 14개를 25 mm 직결피스로 단다. 출력 받침 4 mm와 함께 뒷바를 22 mm 띄워, 그 아래 앞쪽을 USB 케이블 통로로 쓴다. 본체와 스피커의 진동도 떼어 놓는다. | 제조·모델: 화성고무 RUB-E2 / 크기: 외경 28 mm, 나사 구멍 약 Ø5 (판매처 표기 '28x5') / 높이: 약 18~20 mm 원뿔대 (사진과 다른 판매처 표기 D28×H18로 본 값) / 고정: 직결피스 25 mm(L49) + M4 와셔(L36) / 주문 단위: 최소 20개 / 가격: 583원/개 (엘레파츠) | https://www.eleparts.co.kr/goods/view?no=16628292
본체·결합 | 스텐 렌치볼트 M2.5 × 6 (Pi 고정) | 4 | 200 | 800 | 6 | 11번가 · 굿나잇몰 | 가운데 유닛 CU 칸의 출력 CU 트레이 보스 4개에 Raspberry Pi 5를 바로 조인다. 4개 사용. | 규격: M2.5 × 6 mm / 재질: SUS304 / 머리: 유두(소켓 캡), 2 mm 육각 렌치 / 체결: CU 트레이 보스 Ø2.2 탭 구멍, 기판 1.6 mm를 지나 약 4 mm 물림 / 판매처·가격: 11번가 굿나잇몰, 200원/개 | https://www.11st.co.kr/products/4236198413
본체·결합 | 스텐 직결피스 8호 13 mm (뒷바) | 36 | 40 | 1440 | 40 | 11번가 · 굿나잇몰 | 뒷바 합판 면에 출력 부품을 고정한다. 도브테일 블록 4개 × 4, CU 트레이 4, I/O 판 4, 보조배터리 받침 4, 콤 받침(보관함) 4, XT30 받침 4 = 36개 사용. | 종류: 스텐 둥근머리 직결피스 (끝이 드릴 모양) / 굵기: 8호, Ø4.2 / 길이: 13 mm / 구멍: 출력 부품 관통 구멍 Ø4.5 / 판매처·가격: 11번가 굿나잇몰, 40원/개 | https://www.11st.co.kr/products/4353471537
본체·결합 | 스텐 직결피스 8호 16 mm (스피커 유닛) | 8 | 50 | 400 | 8 | 11번가 · 굿나잇몰 | 스피커 유닛 CW-100B25를 PETG 출력 앞판(배플)에 고정한다. 유닛마다 4개 × 2 = 8개. | 종류: 스텐 둥근머리 직결피스 8호 (Ø4.2) / 길이: 16 mm / 물림: 16 − 유닛 플랜지 4 − EVA 가스켓 3 = 약 9 mm / 구멍: 유닛 장공 Ø4.8, PETG 앞판 파일럿 Ø3.4 / 판매처·가격: 11번가 굿나잇몰, 50원/개 | https://www.11st.co.kr/products/4353471537
본체·결합 | 스텐 직결피스 8호 19 mm (그릴) | 8 | 50 | 400 | 8 | 11번가 · 굿나잇몰 | PETG 육각 그릴을 스페이서 링(10 mm)에 통과시켜 스피커 앞판에 고정한다. 그릴마다 4곳 × 2 = 8개. | 종류: 스텐 둥근머리 직결피스 8호 (Ø4.2) / 길이: 19 mm / 체결: 그릴 스페이서 링 10 mm를 지나 PETG 앞판에 박힘 / 판매처·가격: 11번가 굿나잇몰, 50원/개 | https://www.11st.co.kr/products/4353471537
본체·결합 | 스텐 직결피스 8호 25 mm (고무발) | 14 | 60 | 840 | 14 | 11번가 · 굿나잇몰 | 고무발 14개(스피커 파트 4 × 2 + 가운데 유닛 6)를 출력 받침 4 mm와 함께 합판 바닥에 고정한다. 머리 밑에 M4 와셔를 끼운다. 14개 사용. | 종류: 스텐 둥근머리 직결피스 8호 (Ø4.2) / 길이: 25 mm / 체결: 고무발 구멍 약 Ø5 + M4 와셔(L36) / 판매처·가격: 11번가 굿나잇몰, 60원/개 | https://www.11st.co.kr/products/4353471537
본체·결합 | 오공 205 목공본드 800 g | 1 | 3949 | 3949 | 1 | 나비엠알오 · 나비엠알오 (오공) | 스피커 상자 2개(합판 10장)와 가운데 유닛(합판 11장)을 붙인다. 출력 앞판 둘레도 이것으로 밀봉한다. 드릴 없이 본드로만 붙이고 마스킹테이프로 눌러 굳힌다. | 제품: 오공 205 목공용 본드 / 용량: 800 g / 종류: 초산비닐 수지 에멀전 (흰색 목공본드) / 옵션: '오공 205본드 800g' (201은 다른 제품) / 가격: 2,840원 + 배송 2,500원 (11번가) | https://www.navimro.com/g/395062/
본체·결합 | 스텐 렌치볼트 M3 × 10 (센서 바·CU) | 36 | 60 | 2160 | 50 | 11번가 · 굿나잇몰 | 센서 바·센서 기판을 왼쪽 받침 기둥에 고정한다: 모듈 7개 × 2 + 끝 부속 2개 × 2 = 18개. CU 트레이의 앰프 4·강압 모듈 4·앰프 입력 잭 기판 2 = 10개, 토글 래치 2개 × 4 = 8개. 합계 36개. 구매 목록 글은 PD 트리거 2·퓨즈 홀더 2를 더해 40개로 셌다. | 규격: M3 × 10 mm / 재질: SUS304 / 머리: 유두 렌치볼트(육각 구멍), 2.5 mm 렌치 / 체결: 출력 구멍 Ø2.7~2.8에 자가 탭 / 센서 바 자리: (3.0, 61.9)·(3.0, 74.6) / 판매처·가격: 11번가 굿나잇몰, 60원/개 | https://www.11st.co.kr/products/4236198413
본체·결합 | 스텐 렌치볼트 M3 × 6 (제어 기판) | 16 | 40 | 640 | 20 | 11번가 · 굿나잇몰 | 모듈마다 제어 기판(RP2040-Zero·먹스)을 프레임의 매단 보스에 밑에서 2개로 조인다: 7 × 2 = 14개. 나머지 두 구석은 보스의 위치 핀이 잡는다. v3.2 기준으로 CU 트레이의 페달 보드(PED)도 같은 방식으로 2개를 쓴다. | 규격: M3 × 6 mm / 재질: SUS / 머리: DESIGN.md: ISO 7380 Ø5.7 × 1.65 (DIN 912 Ø5.5 × 3.0도 들어감) / 체결: 보스 Ø2.5 막힌 구멍에 탭, 기판 1.6 + 보스 4.4 물림 / 위치: (50.0, 149.0)·(114.5, 192.5), 밑에서 조임 / 판매처·가격: 11번가 굿나잇몰, 40원/개 | https://www.11st.co.kr/products/4236198413
본체·결합 | 스텐 평와셔 M4 (외경 9 × 0.5T) | 14 | 10 | 140 | 20 | 11번가 · 굿나잇몰 | 고무발 14개를 고정하는 25 mm 직결피스 머리 밑에 1개씩 끼운다. 14개 사용. | 규격: M4용 평와셔 / 치수: 내경 약 4.3 × 외경 9 × 두께 0.5 mm / 재질: 스테인리스 / 판매처·가격: 11번가 굿나잇몰, 10원/개 | https://www.11st.co.kr/products/4236198413
본체·결합 | EVA 고밀도 폼 3T 330×490 검정 | 3 | 2100 | 6300 | 3 | 11번가 · 상우아트 | 건반 모듈 7개와 끝 부속 2개 밑면 전체에 한 장씩 붙이는 3 mm 바닥 층이다(모듈 조각 163.5 × 211, 끝 부속 63 × 211·39.5 × 211). 남는 조각으로 스피커 유닛 가스켓 2개와 가운데 유닛 ↔ 스피커 파트 맞닿는 면의 띠를 만든다. | 제품: 대원 우드보드 EVA 고밀도 칼라스펀지 3T / 색: E-210 검정 / 크기: 330 × 490 × 3 mm (판매처가 1~3 cm 오차 고지) / 접착: 접착면 없음 (종이 양면테이프로 붙임) / 판매처·가격: 11번가 상우아트, 2,100원/장 (0.5T 펠트와 묶음배송) | https://www.11st.co.kr/products/7591566666
본체·결합 | 오꾸메 합판 400×1200×11.5 (스피커) | 1 | 17680 | 17680 | 1 | 동진나무공장 | 왼쪽·오른쪽 스피커 파트의 밀폐 상자 2개(외형 180 × 195 × 210, 안 5.05 L)를 이 한 장에서 잘라 만든다. 상자마다 옆판 2·뒤판 1·위아래판 2 = 5장, 모두 10장. 앞판(배플)은 PETG 출력이다. | 규격: 오꾸메 합판 400 × 1200 × 11.5 mm / 재단: 무료, 직선만 / 조각: 옆판 195 × 210 ×4, 뒤판 157 × 210 ×2, 위·아래판 172 × 157 ×4 / 판매처: 동진나무공장 (namugongjang.com, product_no=1378) / 가격: 17,680원 (배송 무료) | https://namugongjang.com/product/detail.html?product_no=1378
본체·결합 | 오꾸메 합판 600×1200×11.5 (가운데 유닛) | 1 | 22520 | 22520 | 1 | 동진나무공장 | 가운데 유닛 상자(894 × 195 × 100: 예비 건반 보관함·CU 칸·보조배터리 칸)를 이 한 장에서 만든다. 바닥 2·뚜껑 2·앞판 1·뒤판 2·끝판 2·칸막이 2 = 11장. | 규격: 오꾸메 합판 600 × 1200 × 11.5 mm / 재단: 무료, 직선만 / 조각: 바닥 356 × 195·338 × 195, 뚜껑 356 × 195·338 × 195, 앞판 894 × 77, 뒤판 356 × 77·338 × 77, 끝판 172 × 77 ×2, 칸막이 172 × 77·172 × 57 / 판매처: 동진나무공장 (product_no=1378) / 가격: 22,520원 (배송 무료) | https://namugongjang.com/product/detail.html?product_no=1378
본체·결합 | 네오디뮴 자석 Ø8×3 N35 (뚜껑) | 12 | 160 | 1920 | 14 | 대건상사 | 가운데 유닛 뚜껑 3장이 미끄러지지 않게 붙여 둔다. 뚜껑마다 대각선 두 구석에 뚜껑 쪽·받침 쪽 한 쌍 = 12개를 Ø8.2 포켓에 순간접착제로 붙인다. | 규격: Ø8 × 3 mm, N35 네오디뮴 / 흡착력: 한 개 약 1.1~1.2 kg (추정) / 사용 온도: 80 °C 이하 / 옵션: 3.0T (두께 3 mm) / 판매처·가격: 대건상사, 160원/개 | https://dgmagnet.com/product/detail.html?product_no=17
본체·결합 | 매미고리 1-20 SUS 토글 래치 | 2 | 2400 | 4800 | 2 | 철물박사 | 가운데 유닛과 왼쪽·오른쪽 스피커 파트의 이음 뒷면에 1개씩 = 2개. 도브테일이 위치를 잡고 래치가 당겨 잠근다. 도브테일 블록의 출력 받침에 M3 × 10 4개로 고정한다. | 제품: 매미고리 1-20, SUS304 / 길이: 잠근 상태 54 mm (본체 43.3 mm) / 본체: 폭 25.2, 높이 10 mm, 나사 구멍 2-Ø4 (간격 10.5) / 걸이: 23.3 × 11.8, 높이 8.8 mm, 나사 구멍 2-Ø4 (간격 12.5) / 판 두께: 약 1.0~1.2 mm / 판매처·가격: 철물박사, 2,400원/조 | https://www.metaldiy.com/item/itemView.do?itemId=8806379117286
본체·결합 | M3 방진 댐퍼(그로밋) 20개 | 1 | 4500 | 4500 | 1 | 알씨뱅크 | 왼쪽·오른쪽 끝 부속과 스피커 파트를 잇는 짧은 PETG 방진 브래킷(40 × 17 × 6)에 2개씩 = 4개. 위치만 잡아 주고, 스피커 무게는 고무발이 받는다. | 종류: FC 방진 댐퍼(러버), M3 볼트용 / 치수: 지름 6 mm, 높이 8.6 mm, 볼트 구멍 3 mm, 허리 홈(기판 1.6 mm용) / 수량: 20개 / 판매처·가격: 알씨뱅크 4,500원 (5만 원 미만 배송비 3,500원, 5만 원 이상 무료) | https://www.rcbank.co.kr/shop/goods/goods_view.php?goodsno=67110
소모품 | 열수축튜브 530개 세트 (케이스) | 1 | 6600 | 6600 | 1 | 엘레파츠 | 끝 부속 리드(EL 5가닥 + ER 3가닥)를 뒤 케이블 통로에서 L66 JST-XH 리드(끝 부속 쪽 50 mm)와 이은 8곳을 덮는다(SCH-04 주 6). CU의 퓨즈 홀더(F601) 선을 PD 트리거 출력·스위치 쪽 선과 이은 곳, 스피커선(16 AWG)을 XT30 꼬리선에 이은 곳, 페달 안 센서 납땜부, 페달 잭 뒤쪽 납땜에도 쓴다. 구매 목록은 O1·O7 제어 기판 J302 패드에 L66 리드를 납땜한 곳도 적었다. 배선 단계에서 쓴다. | 수축률: 2:1 / 굵기: 1.5 / 2 / 3 / 4 / 5 / 6 / 8 / 10 mm / 길이: 45 mm / 수량: 530개 / 포장: 플라스틱 보관 케이스 / 판매: 엘레파츠 no=8170311, 6,600원 | https://www.eleparts.co.kr/goods/view?no=8170311
공구 | Ø4.0 HSS 드릴 날 SD 4.0 | 1 | 990 | 990 | 1 | 나비엠알오 | Ø3.9로 출력한 구멍을 Ø4.0으로 넓혀 Ø4 봉이 부드럽게 들어가고 레버가 잘 돌게 한다. 레버 캐리어 허브 88개, 모듈 프레임 핀 보스 5 × 7 = 35개, 끝 부속 핀 보스, 출력 공구(지그 K·L 구멍, 가짜 레버 허브), 단계 0 시편(C01a·b·d, C06a)까지 모두 약 130구멍이다. | 규격: 스트레이트 드릴 SD 4.0 (나비엠알오 K11176355) / 재질: HSS (M2) / 지름: 4.0 mm / 날장·전장: 55 mm / 84 mm / 끝각: 118° / 표면: 브라이트 (은색) / 원산지: 중국 / 가격: 990원 (VAT 포함, 나비엠알오) | https://www.navimro.com/g/171100/
페달 | 3.5 mm 스테레오 AUX 선 3 m (페달) | 1 | 2860 | 2860 | 1 | 아이씨뱅큐 | 댐퍼 페달(책상 앞 바닥)과 가운데 유닛 I/O 판의 페달 잭(J501, L15 ②)을 잇는 신호선 1가닥(W501)이다. 한쪽 플러그를 잘라 페달 안 센서 기판에 납땜하고(팁 = 센서 출력, 링 = 3V3, 슬리브 = GND), 남은 플러그를 I/O 판 잭에 꽂는다. | 커넥터: 3.5 mm 3극(TRS) 수 ↔ 수 / 길이: 3 m / 모델: Coms BC256 / 배선: 팁 = OUT(페달 안 1 kΩ R551 거침), 링 = PED_VCC 3V3, 슬리브 = GND / 판매: 아이씨뱅큐 P004711396 | https://www.icbanq.com/P004711396
소프트웨어 | FluidSynth 2.6.1 (무료) | 1 | 0 | 0 | 1 | 무료 (다운로드) · FluidSynth | Pi 5의 microSD에 설치하는 피아노 소리 엔진. USB-MIDI 8개(O1~O7, PED)를 midi.autoconnect=1로 한 곳에 모으고, ALSA hw:로 USB 동글(L51)에 48 kHz로 낸다. 출력 리미터를 켜 둔다(D18). | 버전: 2.6.1 (2026-09-19 릴리스) / 형식: SoundFont 2 샘플 재생 신스, LGPL-2.1 / 입력 병합: midi.autoconnect=1 (USB-MIDI 8개) / 출력: ALSA hw:<동글>,0, 48 kHz (D7) / 리미터: synth.limiter.active=1 (D18) / 서스테인: CC64 64 이상 켜짐 / 미만 꺼짐 (하프페달 음색 없음) | https://www.fluidsynth.org/
소프트웨어 | Salamander 그랜드 피아노 음원 (무료) | 1 | 0 | 0 | 1 | 무료 (다운로드) · FreePats | FluidSynth가 읽는 피아노 음원 SF2 파일(296 MB) 1개를 Pi 5 microSD에 넣는다. | 원본: Yamaha C5 그랜드 피아노 녹음 (AKG C414 ×2, AB) / 벨로시티 층: 16단계 / 용량: SF2 296 MiB (V3+2020-06-02) / 라이선스: Creative Commons Attribution 3.0 / 배포: FreePats | https://freepats.zenvoid.org/Piano/acoustic-grand-piano.html
 | 부품·소모품·공구 합계 (배송비 제외) |  |  | 599961

Sheet: 뺀 품목
분류 | 품목 | 처음 수량 | 단가(원) | 처음 금액(원) | 판매처 | 쓰는 곳 | 링크
제어·전원 | XL4016 강압 모듈 XH-M401 | 1 | 5170 | 5170 | 아이씨뱅큐 | CU 칸 트레이 보스 4개에 M3×10(L34) 4개로 1개를 고정한다. 입력은 스위치 뒤 20 V이고, 출력 5.1 V는 Pi 5 전원선(C24)과 허브 DC 선(허브 어댑터 선을 잘라 씀) 두 곳으로 나간다(SCH-06 A602). | https://www.icbanq.com/P017179502
오디오 | TPA3110 앰프 보드 XH-A232 | 1 | 2750 | 2750 | 아이씨뱅큐 | 가운데 유닛 CU 칸 트레이의 출력 보스에 1개를 M3 나사 4개(L34)로 고정한다. 20 V 버스(PD 트리거 → 퓨즈 → 스위치 뒤)에서 전원을 받고, 입력은 앰프 입력 잭(L15 ③)과 저음 차단 RC를 거쳐 들어온다. 출력 L±·R±는 스피커선(C13) → XT30으로 좌우 스피커 2개를 울린다. | https://www.icbanq.com/P017179248
제어·전원 | USB-C↔C PD 60W 케이블 2 m | 1 | 2670 | 2670 | 엘레파츠 | 벽 충전기(L62)에서 피아노 뒤 I/O 판 USB-C 입력(L57)까지 1개로 잇는다(W601). | https://www.eleparts.co.kr/goods/view?no=17806170
제어·전원 | MAXTEK MT666 USB-C 2선 전원선 | 1 | 1190 | 1190 | 엘레파츠 | 강압 모듈(L58) 출력 단자에 빨강(+)·검정(−) 두 선을 물리고, USB-C 플러그를 Pi 5 전원 입력에 꽂는다. CU 칸 안에서 1개 사용(W603, SCH-06 P601). | https://www.eleparts.co.kr/goods/view?no=17358965
센서·MCU·기판 | USB-A → C 케이블 1 m (Coms NA993) | 8 | 1620 | 12960 | 엘레파츠 | 모듈 O1~O7의 RP2040-Zero USB-C에서 가운데 유닛 USB 허브까지 7가닥(W201~W207), 페달 보드에서 허브까지 1가닥(W208, CU 칸 안에 짧게 묶음) = 8가닥. 모듈 7가닥은 허브에 꽂힌 채 뒷바 아래 케이블 통로에 두고, 설치 때 모듈 쪽만 꽂는다(R27). | https://www.eleparts.co.kr/goods/view?no=4313490
소모품 | 캡톤 테이프 10 mm × 33 m (KzPton) | 1 | 4059 | 4059 | 엘레파츠 | RP2040-Zero 8개(모듈 제어 기판 7 + 페달 보드 1)와 만능기판 사이에 한 장씩 붙인다. 제로 밑면의 칩·수정·LDO가 양면 만능기판 윗면의 구리 패드나 납땜에 닿아 합선되지 않게 하는 절연이다. 제로는 핀 헤더로 세워 이 부품들 위(캡톤)에 얹히므로 약 1.3 mm 높아진다. 남는 테이프로 기판 아랫면 납땜 자리도 덮는다. | https://www.eleparts.co.kr/goods/view?no=557
소모품 | 케이블 타이 100 mm 100개 (T-C2510B) | 1 | 438 | 438 | 엘레파츠 | 모듈 7개의 USB-C 케이블을 모듈 뒷벽에 묶어 당겨도 빠지지 않게 한다. O1·O7의 EXT 리드(L66)도 같은 방법으로 묶는다. 뒷바 아래 케이블 통로에서 모듈 USB 케이블 7가닥을 묶어 정리하고, 페달 보드 USB(W208)는 CU 안에서 짧게 묶는다. 페달 안에서는 3 m 케이블(W501)을 한 번 묶어 당김을 막는다. | https://www.eleparts.co.kr/goods/view?no=9100003
소모품 | 유연납 0.8 mm 50 g (YUN FANG Sn63) | 1 | 3850 | 3850 | 엘레파츠 | 센서 기판 7장, 제어 기판 7장, 끝 부속 EL·ER 기판, 페달 보드, 페달 안 센서, CU 배선(잭·XT30·전원선)의 손 납땜 전체에 쓴다. 모듈당 약 200점, 전체 약 1,500점이다(구매 목록 기준). | https://www.eleparts.co.kr/goods/view?no=12755646
센서·MCU·기판 | 탄소피막 저항 10 kΩ (10개) | 10 | 25 | 250 | 엘레파츠 | 지금 회로(hardware/pcb bom.csv)에는 10 kΩ를 쓰는 곳이 없다. 예비로만 남은 줄이다. | https://www.eleparts.co.kr/goods/view?no=10951
오디오 | USB-C(암)→USB-A(수) ㄱ자 젠더 | 1 | 1700 | 1700 | 엘레파츠 | CU 칸 Pi 5의 USB-A 포트에 꽂고, 여기에 Apple 동글(L51)의 USB-C 플러그를 꽂는다(X701). 동글은 허브를 거치지 않고 Pi에 바로 붙는다. | https://www.eleparts.co.kr/goods/view?no=11043038
본체·결합 | NAVI 종이 양면테이프 48 mm × 6 m | 1 | 1080 | 1080 | 엘레파츠 | 건반 모듈 7개와 끝 부속 2개 밑면에 EVA 3T 바닥 시트를 붙일 때 띠 모양으로 쓴다. 보조배터리 칸 뒤 벽에 USB 허브(i093)를 붙일 때도 이 테이프를 쓴다. 접착면이 없는 메리노 펠트(i106 2T: 앞 펠트·키퍼 펠트)를 붙이는 데도 쓸 수 있다. 다만 펠트를 붙이는 방법은 r4.5 DESIGN.md에 적혀 있지 않다. | https://www.eleparts.co.kr/goods/view?no=17897439
공구 | Coms 디지털 멀티미터 DT-832 (NT117) | 1 | 7600 | 7600 | 엘레파츠 | 회로를 처음 켤 때 점검에 쓴다(hardware/pcb '도착 후 확인할 것' 1~8번). PD 트리거가 20 V를 내는지, 강압 모듈을 Pi에 잇기 전에 5.10~5.15 V로 맞췄는지 잰다. 잭 3개(PJ-313)는 통전 검사로 핀 글자(T·TN·R·RN·S)를 찾고, 플러그가 없을 때 노멀 접점이 닫히는지 본다. 센서 출력 1.59~1.71 V, 페달 링–슬리브 3.05 V 이상, 스피커 저항 6~7 Ω, 허브 역급전(Pi 5V 핀 0 V), O1 제로의 3V3 전류 60~130 mA도 잰다. | https://www.eleparts.co.kr/goods/view?no=6779159
공구 | Prokit 정밀 스트리퍼 CP-301G | 1 | 4500 | 4500 | 엘레파츠 | 가는 선(AWG 20~30) 피복을 벗긴다. 가장 많은 것은 리본 7줄의 양끝 16가닥씩 224가닥이다(센서 기판 J201 ↔ 제어 기판 J301 직접 납땜). 센서 기판 3V3·GND 버스와 제어 기판 링크로 쓰는 리본 가닥(SE12), 끝 부속 EL·ER 리드(W401·W411)와 JST-XH 연장선(W403·W413), 잭 → 페달 보드 선(W502), 페달 케이블(W501), 헤드폰·앰프 입력 선(W701·W702)의 자른 끝에도 쓴다. | https://www.eleparts.co.kr/goods/view?no=3787704
공구 | JAKEMY 5인치 니퍼 JM-CT2-2 | 1 | 3960 | 3960 | 엘레파츠 | 납땜 뒤 남는 다리를 자른다. 홀센서 89개(모듈 12 × 7 + 끝 부속 4 + 페달 1) × 다리 3개와 리드형 저항·콘덴서(제어 기판 R301~R303, 페달 R501~R503·R551, CU R701·R702·C701~C704)에 쓴다. 1×40 핀헤더 9줄을 1×16·1×8(먹스 7세트)과 1×9(제로 8개 × 2)로 자를 때는 핀 사이 플라스틱을 자른다(v3 CT13). 리본과 JST-XH 연장선(L66, 150 / 50 mm) 자르기, 출력물 거스러미 정리, 16 AWG 전원·스피커선 피복 칼집 내기에도 쓴다. | https://www.eleparts.co.kr/goods/view?no=7663472
공구 | 블루텍 버니어 캘리퍼스 NA530-200 | 1 | 13400 | 13400 | 엘레파츠 | 치수 확인 전반에 쓴다. 강철 블록 90개의 두께가 8.9~9.1인지 골라내고(DESIGN 10장 4단계), 봉 토막을 161.4 ± 0.2로 맞춘다. 출력 공구(지그·높이 블록·핀 게이지)를 검증하고, USB-C 케이블 몰드(≤ 12.5 × 7.6 × 25)와 제로 리셉터클 위치(오른쪽 모서리에서 4.67, pcb 확인 9번)를 잰다. 단계 0 시험의 펠트·천 두께(시험 T)와 핀 돌출(시험 P)도 이것으로 잰다. | https://www.eleparts.co.kr/goods/view?no=16549359
공구 | 코텍스 쇠톱(대) K-9301, 300 mm | 1 | 6500 | 6500 | 엘레파츠 | 강철 띠(9T×19, 1 m × 4장)를 40 mm로 90번 자른다(88 + 예비 2). Ø4 SUS 봉(1 m × 4개)도 자른다. 모듈용 161.4 mm 16토막(건반 봉 8·레버 봉 8, 예비 포함), 끝 부속용 짧은 토막 4개(건반 약 45·21, 레버 45.9·22.2), 출력 공구 3토막(31.6·20.6·31.6), 단계 0 시편 5토막(24·40·18·45·45)이다. 바이스(PD-374)에 물려 쓰며 강철·봉을 합쳐 약 3~4시간 걸린다(costsel 추정). | https://www.eleparts.co.kr/goods/view?no=9100747
공구 | LENOX 12인치 쇠톱날 T2355 | 2 | 2200 | 4400 | 엘레파츠 | 쇠톱(K-9301)에 거는 300 mm 날이다. 강철 90컷과 SUS 봉 약 28토막 자르기에 쓴다. 한 장이 무뎌지거나 부러지면 두 번째 장으로 바꾼다. | https://www.eleparts.co.kr/goods/view?no=4101973
공구 | Coms 철공용 평줄 BD079 | 1 | 6800 | 6800 | 엘레파츠 | 자른 강철 블록 90개의 절단면 버를 없앤다(모따기는 안 함). 봉 토막 끝을 161.4 ± 0.2로 맞추고 모따기한다. 출력 공구용 봉 토막 3개 끝(tools.md 준비 3)과 스프링 다리 자른 끝의 거스러미도 다듬는다(DESIGN 4장·10장 4단계). | https://www.eleparts.co.kr/goods/view?no=12185326
공구 | Prokit 탁상 바이스 PD-374 | 1 | 20000 | 20000 | 엘레파츠 | 강철 띠와 Ø4 봉을 책상 모서리에 고정해 톱질·줄질할 때 문다. 밸런스 핀이 빡빡할 때 천천히 눌러 넣는 데 쓴다(tools.md, 망치 금지). 단계 0 시험 P(핀 압입 쿠폰)와 시험 20(강철 블록을 117 N으로 누름)에서도 누르는 데 쓸 수 있다. | https://www.eleparts.co.kr/goods/view?no=2923219
공구 | 육각 렌치 2.5 mm — 볼트 상품의 추가 옵션 | 1 | 600 | 600 | 11번가 | 굿나잇몰 '유두' 렌치볼트(M3 소켓 캡)를 조인다. M3×10(L34) 36개(센서 바·기판 18 = 모듈 14 + 끝 부속 4, CU 트레이 부품 10, 토글 래치 8)와 M3×6(L35) 16개(모듈 제어 기판 7 × 2 + CU 페달 보드 2, 밑에서 조임)에 쓴다. | https://www.11st.co.kr/products/4236198413
공구 | 육각 렌치 2.0 mm — 볼트 상품의 추가 옵션 | 1 | 600 | 600 | 11번가 | 캡스턴 나사 M3×6 버튼헤드(ISO 7380) 88개를 벤치 지그에서 1/8회전씩 돌려 맞춘다(DESIGN 10장 3단계·12장). 단계 0 시험 C(캡스턴 너트 트랩)에서도 돌린다. Pi 5 고정 나사 M2.5×6(L47, 굿나잇몰 '유두') 4개에도 맞는다. | https://www.11st.co.kr/products/4236198413
건반 액션 | 0.5T 부싱 천 (i062와 같은 장, 0원) | 1 | 0 | 0 | 11번가 | 스냅 노치·밸런스 핀 홈·가이드 탭 천의 용도를 v4 비용 카드에서 따로 적은 0원 줄이다. 실제 천은 i062 한 장에서 잘라 쓴다. | https://www.11st.co.kr/products/8517880969
제어·전원 | Pi 5 방열판 (알루미늄 4조각) | 1 | 1400 | 1400 | 메카솔루션 | Pi 5 칩 4곳(SoC, 메모리, RP1, 이더넷 칩)에 한 조각씩 붙인다. 1세트 4조각을 모두 쓴다. | https://www.mechasolution.com/goods/goods_view.php?goodsNo=605179
센서·MCU·기판 | 만능기판 12×18 cm (센서 기판용) | 2 | 2200 | 4400 | 메카솔루션 | 센서 기판 띠를 잘라 내는 판이다. 모듈마다 SB 띠 161.6 × 15.24 mm(6행) 1개 × 7, 끝 부속 EL 45.5 × 15.24·ER 22.0 × 15.24. 센서 다리, 3V3·GND 버스, 칩 콘덴서, 리본이 여기에 납땜되고 센서 바 바로 아래에 들어간다. 남는 조각은 페달 안 센서 받침·PJ-313 받침으로 쓸 수 있다. | https://www.mechasolution.com/goods/goods_view.php?goodsNo=540645
3D 출력 재료 | Bambu PETG Basic 흰색 1 kg (스풀) | 1 | 16150 | 16150 | Bambu Lab KR 공식 스토어 | 흰 건반(백건) 62개를 뽑는다. 내역은 모듈마다 7개 × 7 = 49, 끝 부속 A0·B0·C8 3개, 보관함에 넣을 예비 10개다. 서포트를 포함한 백건 합계는 약 1.44 kg이라 이 스풀을 다 쓰고 리필(i088)로 이어 뽑는다. | https://kr.store.bambulab.com/products/petg-basic
3D 출력 재료 | Bambu PETG Basic 흰색 1 kg 리필 | 1 | 12750 | 12750 | Bambu Lab KR 공식 스토어 | 흰색 두 번째 1 kg이다. 첫 흰색 스풀(i087)을 다 쓴 뒤 그 빈 스풀에 끼워 나머지 백건(약 0.44 kg)을 뽑는다. 원하면 센서 바 9개(약 0.15 kg)도 여기서 뽑는다. | https://kr.store.bambulab.com/products/petg-basic
3D 출력 재료 | Bambu PETG Basic 검정 1 kg (스풀) | 5 | 16150 | 80750 | Bambu Lab KR 공식 스토어 | 백건을 뺀 나머지 출력물을 뽑는다. 모듈 프레임 7개(서포트 포함 개당 약 372 g), 끝 부속 프레임 2, 흑건 42개(88건반 36 + 예비 6), 레버 캐리어 88개, 패드 바 30, 가림판 띠 9, 봉 끝 마개 9가 여기에 들어간다. 스피커 앞판·그릴·CU 트레이·I/O 판 같은 본체 출력물과, 색이 상관없는 출력 공구 4개·단계 0 시험 키트도 이 색으로 잡았다. | https://kr.store.bambulab.com/products/petg-basic
3D 출력 재료 | Bambu PETG Basic 1 kg 추가분 | 1 | 16150 | 16150 | Bambu Lab KR 공식 스토어 | 필라멘트 여유분 1 kg이다. 흰색 2 kg과 검정 5 kg으로 모자라는 몫(주로 검정 약 0.5 kg: 단계 0 키트·출력 공구)과 실패한 출력을 다시 뽑는 데 쓴다. 색은 출력 순서를 보고 정한다. 동전 받침(CT15, 약 2 g)도 여기서 뽑는다. | https://kr.store.bambulab.com/products/petg-basic
제어·전원 | SanDisk Ultra microSD 32GB | 1 | 15490 | 15490 | 다나와 (최저가 판매처) | PC에서 Raspberry Pi OS Lite를 써 넣고 FluidSynth, Salamander 음원(296 MB), 게임을 담아 Pi 5 뒷면 microSD 슬롯에 1장 꽂는다. Pi는 이 카드로 부팅한다. | https://prod.danawa.com/info/?pcode=20358155
제어·전원 | NEXTU 710U3 10포트 전원형 USB 허브 | 1 | 30700 | 30700 | 다나와 (최저가 판매처) | 보조배터리 칸의 뒤 벽에 양면테이프로 1개를 붙인다(길이 228 mm라 CU 칸에 안 들어감). 다운스트림에 모듈 O1~O7 USB 7가닥(W201~W207)과 페달 보드 1가닥(W208)을 꽂고, 업스트림 선(W209)을 Pi 5 USB-A에 꽂는다. 전원은 허브 어댑터 선을 잘라 강압 모듈 5.1 V에 물린다(W604). | https://prod.danawa.com/info/?pcode=29865749
제어·전원 | 파워마스터 65W PD 충전기 | 1 | 19800 | 19800 | 다나와 (최저가 판매처) | 피아노를 벽 전원으로 쓸 때 콘센트에 꽂고 C23 선으로 I/O 판 USB-C 입력에 잇는다. C1 또는 C2 포트 하나만 쓴다. 제작 중에는 T03 선으로 인두(T01)에도 전원을 준다. | https://prod.danawa.com/info/?pcode=59074565
건반 액션 | DHG 양모 펠트 3T 150×10 cm (v3 부품) | 1 | 5500 | 5500 | 스튜디오분트 | v3에서는 건반 앞 멈춤 펠트 3T(백·흑)와 키퍼 훅 밑 펠트로 썼다. r4.5에서는 앞 펠트가 2T + PU 1T이고 키퍼 펠트가 2T이다. 그래서 3T 펠트를 쓰는 곳이 없다. | https://studiobunt.com/product/detail.html?product_no=2948
페달 | 듀로 서스테인 페달 (스위치형) | 1 | 8500 | 8500 | 피아노모아 | 책상 앞 바닥에 두는 댐퍼(서스테인) 페달 1개다(R24). 안의 마이크로스위치 배선을 떼고, 발판 밑면 발끝 쪽에 자석 Ø5×2를 S극이 아래로 가게 순간접착제로 붙인다. 바로 아래 바닥판에는 홀센서 DRV5055(표시면 위)·100 nF·1 kΩ을 단 만능기판 자투리(PS)를 붙이고, 3 m 선(L50)으로 I/O 판 페달 잭에 꽂는다. | https://pianomoa.com/product/%EB%93%80%EB%A1%9C-%ED%94%BC%EC%95%84%EB%85%B8-%ED%8E%98%EB%8B%AC-%EC%84%9C%EC%8A%A4%ED%85%8C%EC%9D%B8-%EC%A0%84%EA%B8%B0%EC%A2%8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
공구 | Pinecil V2 납땜 인두 | 1 | 35200 | 35200 | PINE STORE (Pine64 공식) | 모든 손 납땜에 쓴다(약 1,500점, 구매 목록 CT5). 센서 기판 7장(홀센서 12·콘덴서·리본), 제어 기판 7장과 페달 보드(RP2040-Zero 핀헤더·먹스·리본), 끝 부속 EL·ER 기판, 페달 센서, 잭 3개, 전원·스피커 선을 납땜한다. 제작 중에는 피아노 벽 충전기(L62, 65 W)로 전원을 받는다. | https://pine64.com/product/pinecil-smart-mini-portable-soldering-iron/
공구 | Pinecil 미니 인두 거치대 | 1 | 2690 | 2690 | PINE STORE (Pine64 공식) | 납땜하는 동안 달군 인두(T01)를 올려 두는 받침이다. 같이 오는 스펀지로 팁을 닦는다. 피아노에는 남지 않는다. | https://pine64.com/product/pinecil-portable-mini-stand/
공구 | Pinecil용 실리콘 USB-C 케이블 1 m | 1 | 4720 | 4720 | PINE STORE (Pine64 공식) | Pinecil(T01)을 65 W PD 충전기(L62)에 잇는 전원선이다. 인두에 닿아도 녹지 않는 실리콘 피복이라 납땜 작업대에서 쓴다. | https://pine64.com/product/usb-type-c-to-usb-type-c-silicone-power-charging-cable-1-meter-length/
공구 | 후지야 피아노선 니퍼 FKN-150G | 1 | 21989 | 21989 | 나비엠알오 | 미스미 비틀림 스프링의 두 다리를 자른다. 긴 다리는 코일 중심에서 22.3 mm(코일을 떠나는 점에서 22.13), 짧은 다리는 코일을 떠나는 점에서 8.0 mm다(DESIGN 4장·10장 4단계). 스프링 100개 × 2 = 200번이고, 실제로 쓰는 92개(건반 88 + 단계 0 시험 4)만 자르면 184번이다. | https://www.navimro.com/g/3523817/
게임 | Pi 공식 micro-HDMI→HDMI 케이블 1 m | 1 | 17050 | 17050 | 엘레파츠 | 2단계 리듬게임을 Pi 5에서 돌릴 때(콘솔 모드) Pi 5의 micro-HDMI 포트 하나에서 모니터·TV로 화면을 보낸다. 피아노 소리만 낼 때나 PC 모드로 게임을 할 때는 쓰지 않는다. | https://www.eleparts.co.kr/goods/view?no=8250328
공구 | 탭 핸들 (드릴 날 손잡이) | 1 | 5489 | 5489 | 나비엠알오 | Ø4.0 드릴 날(i126)을 끼워 손으로 돌리는 손잡이다. 출력한 레버 허브 88개와 프레임 핀 보스의 Ø3.9 구멍을 Ø4.0으로 다듬을 때(약 130구멍) 쓴다. | https://www.navimro.com/g/179331/
