WongyuKoh/Toccata/hardware/bom/final-bom/consol/brief.md

# 목표
한국에서 부품을 사는 개인(피아노 제작 취미 프로젝트)의 총비용(물건값 + 판매처별 배송비)을 최소로 만든다.
지금 판매처 19곳에 배송비가 각각 붙어 배송비만 56,600원이다. 작은 판매처의 품목을 이미 주문하는 "허브" 판매처로 옮기거나, 여러 소형 판매처 품목을 한 곳으로 묶을 수 있는지 조사한다.

## 지금 주문하는 허브와 상태 (VAT 포함 원)
- 아이씨뱅큐 icbanq.com: 이미 233,897원 → **무료배송 확정**. 여기로 옮기는 품목은 배송비 0. (5만원 VAT별도 이상 무료, 미만 2,700)
- 엘레파츠 eleparts.co.kr: 52,238원, **66,000원 이상 무료**(미만 3,000). 13,762원만 더 옮기면 3,000원도 없어진다.
- 나비엠알오 navimro.com: 20,878원, 55,000원 이상 무료(미만 3,300).
- 한국미스미 kr.misumi-ec.com: 스프링 31,000원 주문 예정. 배송비 규정 미확인(개인, 카드결제).
- 철물박사 metaldiy.com: 4,800원(매미고리), 100,000원 이상 무료(미만 3,000).
- 11번가 상우아트: 7,800원, 70,000원 이상 무료(미만 3,000).
- 11번가 굿나잇몰: 볼트류 6,820원, 배송비 3,500 무조건.
- 스튜디오분트: 20,700원, 50,000원 이상 무료(미만 3,000).
- 디바이스마트(devicemart.co.kr)는 지금 주문 없음 — 새 판매처로 여러 개를 모을 때만 의미.

# 규칙
- 사양이 **같거나 설계상 동등**해야 한다(치수·재질·핀 배치·용량). 애매하면 "동등 여부"에 이유를 쓰고 verified=false.
- 가격·재고·배송비는 **실제 상품 페이지를 열어** 확인한다(WebFetch, 안 되면 WebSearch 결과 스니펫; 그래도 안 되면 추정이라고 표시). 오늘 2026-09-30.
- 필요한 수량(qty_needed)과 판매 단위(팩)를 반영해 **필요 수량을 사는 데 드는 총액**을 계산한다.
- 각 품목마다 후보를 최대 3개(허브 판매처 우선). 후보가 없으면 "없음"과 찾아본 곳을 쓴다.
- 결과는 지정 JSON 파일에 쓴다. 채팅에 긴 설명 금지, 마지막 답은 5줄 요약.

# 출력 JSON 형식 (list)
[{"id":"i082","current":{"store":..,"total":..},"candidates":[{"store":"엘레파츠","seller":"..","url":"..","product":"상품명 그대로","pack_qty":..,"pack_price":..,"buy_packs":..,"total":..,"spec_match":"같음/동등/다름 + 이유","stock":"재고 있음/품절/미확인","verified":true,"note":".."}]}]
또, 조사하다 알게 된 판매처 배송비 규정은 "_ships" 키 대신 별도 파일 없이 목록 마지막 원소로 {"id":"_ships","ships":[{"store":..,"fee":..,"free_over_vat_incl":..,"url":..}]} 를 넣는다.
