WongyuKoh/Toccata/hardware/mechanical/before/curcuit/material.md

입력 신호를 받을려면 아날로그 신호를 받을 수 있어야 함(신호를 그래프로)
건반이 눌린 정도를 받아와야되니 버튼을 하기에는 부적절?
(건반 높이까지 버튼을 두는게 아니라 일정 높이까지 두면 그 입력신호가 들어올 때만 소리가 울리게 할 수 있음
근데? 그러면 on/off 정도지 실제 얼마나 빠르게 눌렀는지는 알 수가 없다
빠르기가 힘에 비례할까?

음 근데 그전에 midi 프로그램을 뭘 쓸건지를 정해야될 거 같은데
그 프로그램에서 신호를 지원 안해주면 결국 의미 없는 짓이잖아

——
https://www.youtube.com/watch?v=BAQskCuPaeY

참고 영상보면 볼트 너트가 있는데 그건 무게 추 인 거 같음
그리고 거기선 TCRT5000 을 사용한 걸로 추정됨
영상에선 인식하는 부분이 회전해서 거리를 측정했는데, 그러면 오차가 많이 생기지 않나?

페달도 고려를 해야될 거 같은데
