WongyuKoh/Toccata/hardware/bom/final-bom/site/img/00baac758e67.jpg

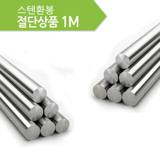
hardware/bom/final-bom/img/00baac758e67.jpg
