WongyuKoh/Toccata/hardware/bom/final-bom/img/0cbf57845308.jpg

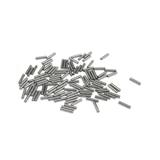
hardware/bom/final-bom/img/0cbf57845308.jpg
