WongyuKoh/Toccata/hardware/bom/final-bom/img/0d2b2344ab22.jpg

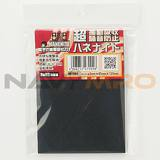
hardware/bom/final-bom/img/0d2b2344ab22.jpg
