WongyuKoh/Toccata/hardware/bom/final-bom/img/00d8f4601002.jpg

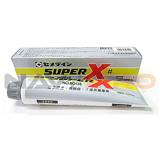
hardware/bom/final-bom/img/00d8f4601002.jpg
