WongyuKoh/Toccata/hardware/bom/final-bom/img/0d0706bb5cfb.jpg

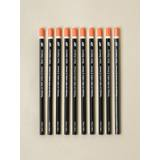
hardware/bom/final-bom/img/0d0706bb5cfb.jpg
