WongyuKoh/Toccata/hardware/bom/final-bom/img/1a706066c8da.jpg

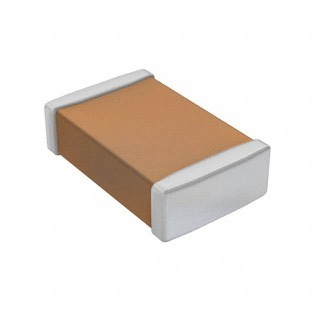
hardware/bom/final-bom/img/1a706066c8da.jpg
