WongyuKoh/Toccata/hardware/bom/final-bom/img/2b68cbbd7875.jpg

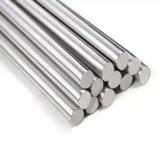
hardware/bom/final-bom/img/2b68cbbd7875.jpg
