WongyuKoh/Toccata/hardware/bom/final-bom/site/img/2b10473979c8.jpg

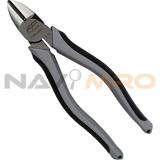
hardware/bom/final-bom/img/2b10473979c8.jpg
