WongyuKoh/Toccata/hardware/bom/final-bom/site/img/2d593d52649e.jpg

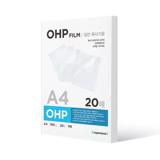
hardware/bom/final-bom/img/2d593d52649e.jpg
