WongyuKoh/Toccata/hardware/bom/final-bom/img/2ec08cbe1974.jpg

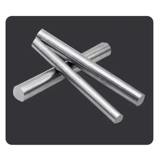
hardware/bom/final-bom/img/2ec08cbe1974.jpg
