WongyuKoh/Toccata/hardware/bom/final-bom/img/3c7d1c8180ad.jpg

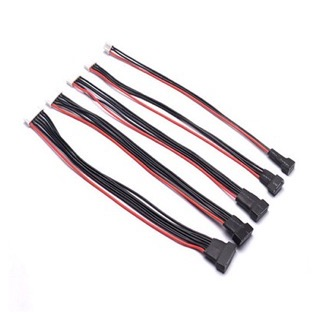
hardware/bom/final-bom/img/3c7d1c8180ad.jpg
