WongyuKoh/Toccata/hardware/bom/final-bom/site/img/3d6995011e9b.jpg

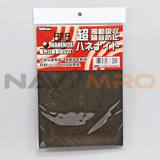
hardware/bom/final-bom/img/3d6995011e9b.jpg
