WongyuKoh/Toccata/hardware/bom/final-bom/img/3e32898e3e9e.jpg

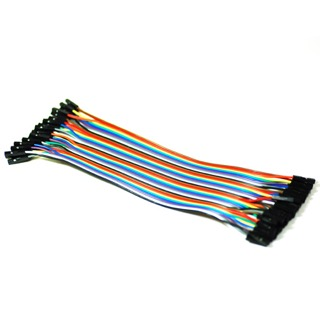
hardware/bom/final-bom/img/3e32898e3e9e.jpg
