WongyuKoh/Toccata/hardware/bom/final-bom/img/3fcfbe88de74.jpg

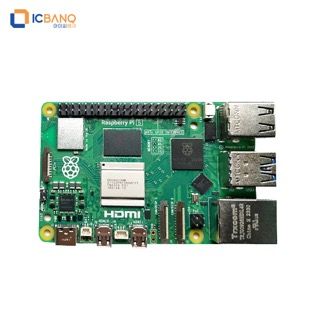
hardware/bom/final-bom/img/3fcfbe88de74.jpg
