WongyuKoh/Toccata/hardware/bom/final-bom/img/4b3b7c314418.jpg

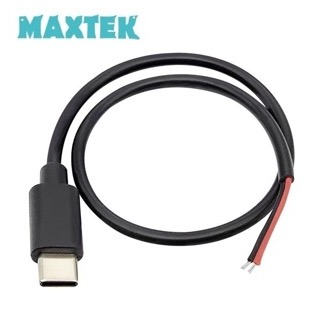
hardware/bom/final-bom/img/4b3b7c314418.jpg
