WongyuKoh/Toccata/hardware/bom/final-bom/img/4c578600e18b.jpg

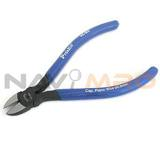
hardware/bom/final-bom/img/4c578600e18b.jpg
