WongyuKoh/Toccata/hardware/bom/final-bom/site/img/4e00f9646c31.jpg

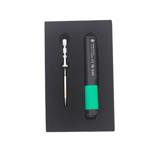
hardware/bom/final-bom/img/4e00f9646c31.jpg
