WongyuKoh/Toccata/hardware/bom/final-bom/img/5a308f747d8c.jpg

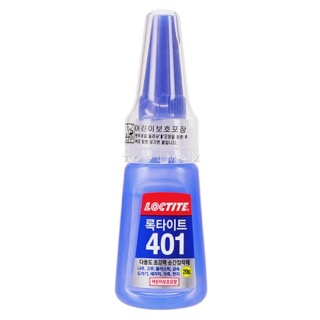
hardware/bom/final-bom/img/5a308f747d8c.jpg
