WongyuKoh/Toccata/hardware/bom/final-bom/site/img/5abd678cc75c.jpg

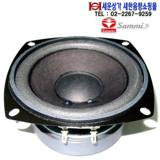
hardware/bom/final-bom/img/5abd678cc75c.jpg
