WongyuKoh/Toccata/hardware/bom/final-bom/img/5b0651d58173.jpg

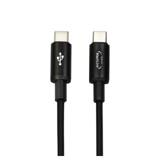
hardware/bom/final-bom/img/5b0651d58173.jpg
