WongyuKoh/Toccata/hardware/bom/final-bom/img/5efce8e1b77d.jpg

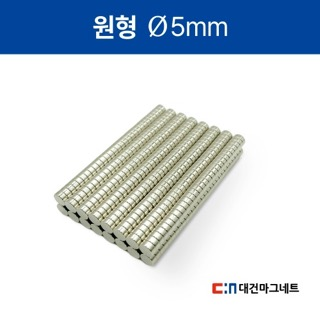
hardware/bom/final-bom/img/5efce8e1b77d.jpg
