WongyuKoh/Toccata/hardware/bom/final-bom/img/05fd5c02199e.jpg

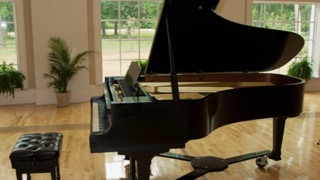
hardware/bom/final-bom/img/05fd5c02199e.jpg
