WongyuKoh/Toccata/hardware/bom/final-bom/site/img/6ad02d9cc62d.jpg

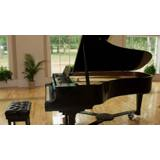
hardware/bom/final-bom/img/6ad02d9cc62d.jpg
