WongyuKoh/Toccata/hardware/bom/final-bom/site/img/6c922d71f4c1.jpg

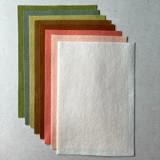
hardware/bom/final-bom/img/6c922d71f4c1.jpg
