WongyuKoh/Toccata/hardware/bom/final-bom/site/img/7fdda12d2140.jpg

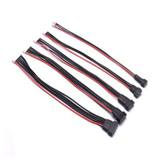
hardware/bom/final-bom/img/7fdda12d2140.jpg
