WongyuKoh/Toccata/hardware/bom/final-bom/img/8af2a2170e70.jpg

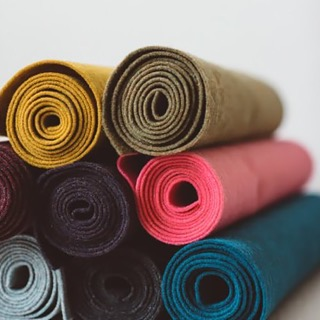
hardware/bom/final-bom/img/8af2a2170e70.jpg
