WongyuKoh/Toccata/hardware/bom/final-bom/img/8bf56228f44d.jpg

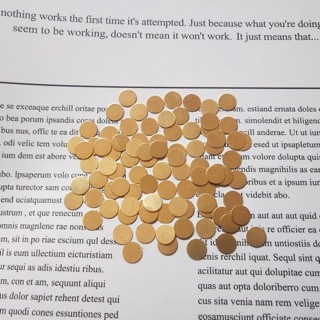
hardware/bom/final-bom/img/8bf56228f44d.jpg
