WongyuKoh/Toccata/hardware/bom/final-bom/img/8cd07baa6e51.jpg

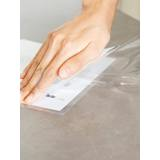
hardware/bom/final-bom/img/8cd07baa6e51.jpg
