WongyuKoh/Toccata/hardware/bom/final-bom/img/16ac3f440abe.jpg

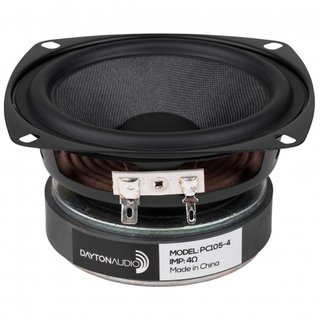
hardware/bom/final-bom/img/16ac3f440abe.jpg
