WongyuKoh/Toccata/hardware/bom/final-bom/img/30f565676a9d.jpg

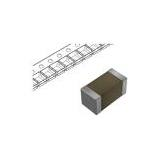
hardware/bom/final-bom/img/30f565676a9d.jpg
