WongyuKoh/Toccata/hardware/bom/final-bom/img/31cd8cda8af9.jpg

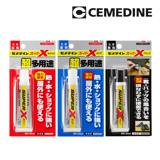
hardware/bom/final-bom/img/31cd8cda8af9.jpg
