WongyuKoh/Toccata/hardware/bom/final-bom/img/032bd517d052.jpg

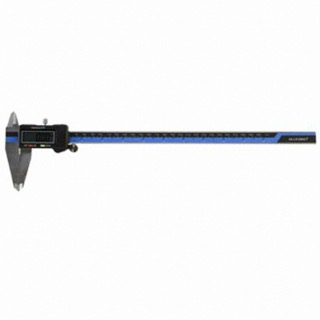
hardware/bom/final-bom/img/032bd517d052.jpg
