WongyuKoh/Toccata/hardware/bom/final-bom/img/35edd84250f3.jpg

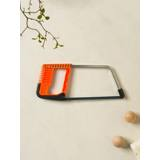
hardware/bom/final-bom/img/35edd84250f3.jpg
