WongyuKoh/Toccata/hardware/bom/final-bom/img/57b8b870c332.jpg

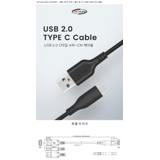
hardware/bom/final-bom/img/57b8b870c332.jpg
