WongyuKoh/Toccata/hardware/bom/final-bom/site/img/63d6ec545f23.jpg

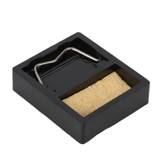
hardware/bom/final-bom/img/63d6ec545f23.jpg
