WongyuKoh/Toccata/hardware/bom/final-bom/img/77a119ff089b.jpg

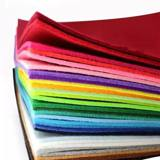
hardware/bom/final-bom/img/77a119ff089b.jpg
