WongyuKoh/Toccata/hardware/bom/final-bom/img/79c59d3f0d55.jpg

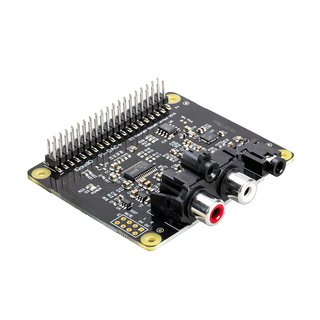
hardware/bom/final-bom/img/79c59d3f0d55.jpg
