WongyuKoh/Toccata/hardware/bom/final-bom/img/90b2122c5bdd.jpg

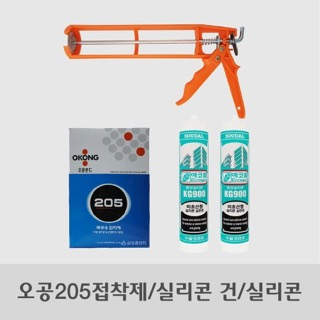
hardware/bom/final-bom/img/90b2122c5bdd.jpg
