WongyuKoh/Toccata/hardware/bom/final-bom/img/97b2b6cdd6fc.jpg

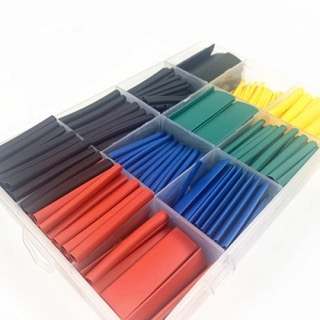
hardware/bom/final-bom/img/97b2b6cdd6fc.jpg
