WongyuKoh/Toccata/hardware/bom/final-bom/site/img/98c5c3994651.jpg

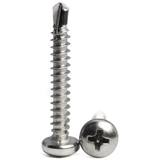
hardware/bom/final-bom/img/98c5c3994651.jpg
