WongyuKoh/Toccata/hardware/bom/final-bom/img/101d8d232244.jpg

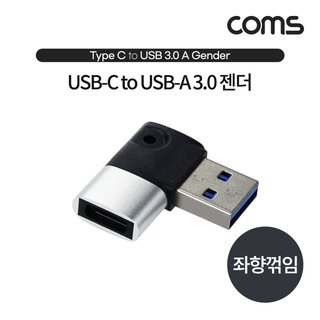
hardware/bom/final-bom/img/101d8d232244.jpg
