WongyuKoh/Toccata/hardware/bom/final-bom/img/213bdbdf4723.jpg

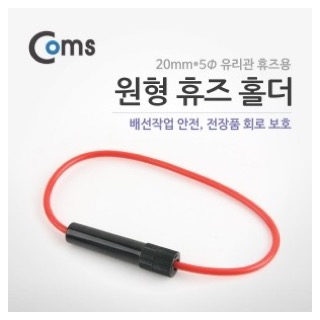
hardware/bom/final-bom/img/213bdbdf4723.jpg
