WongyuKoh/Toccata/hardware/bom/final-bom/img/314dd3e4cdbb.jpg

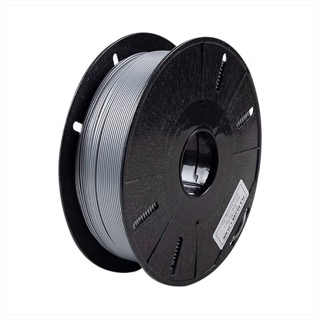
hardware/bom/final-bom/img/314dd3e4cdbb.jpg
