WongyuKoh/Toccata/hardware/bom/final-bom/site/img/382b814c1cf6.jpg

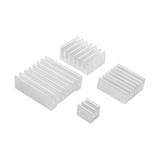
hardware/bom/final-bom/img/382b814c1cf6.jpg
