WongyuKoh/Toccata/hardware/bom/final-bom/site/img/579c9e2ec254.jpg

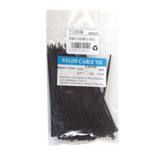
hardware/bom/final-bom/img/579c9e2ec254.jpg
