WongyuKoh/Toccata/hardware/bom/final-bom/img/622ddc4cfd4c.jpg

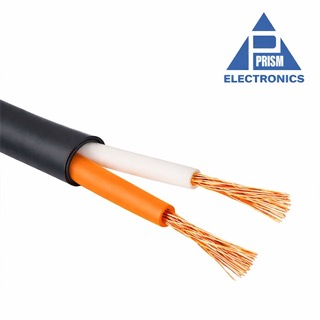
hardware/bom/final-bom/img/622ddc4cfd4c.jpg
