WongyuKoh/Toccata/hardware/bom/final-bom/site/img/1741f7a12d4f.jpg

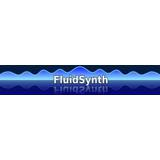
hardware/bom/final-bom/img/1741f7a12d4f.jpg
