WongyuKoh/Toccata/hardware/bom/final-bom/img/2152d238cba6.jpg

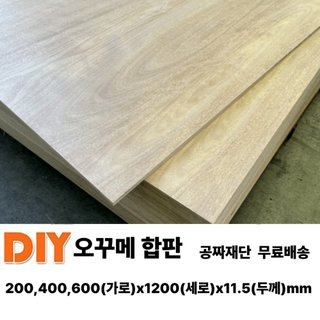
hardware/bom/final-bom/img/2152d238cba6.jpg
