WongyuKoh/Toccata/hardware/bom/final-bom/img/4931e50e480f.jpg

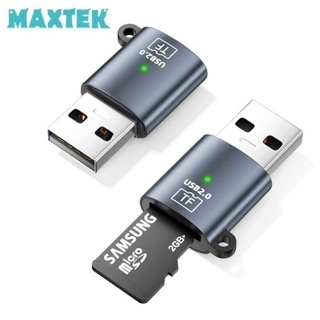
hardware/bom/final-bom/img/4931e50e480f.jpg
