WongyuKoh/Toccata/hardware/bom/final-bom/img/5543af6f773b.jpg

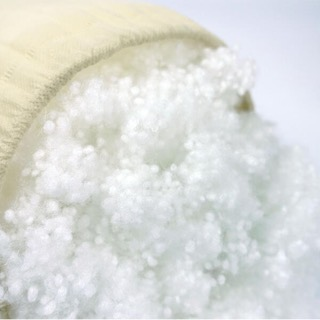
hardware/bom/final-bom/img/5543af6f773b.jpg
