WongyuKoh/Toccata/hardware/bom/final-bom/img/09948bd1c246.jpg

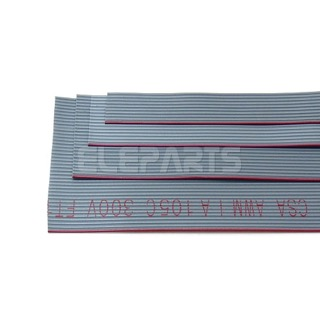
hardware/bom/final-bom/img/09948bd1c246.jpg
