WongyuKoh/Toccata/hardware/bom/final-bom/site/img/21940ad9eec2.jpg

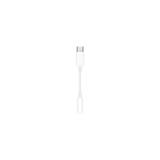
hardware/bom/final-bom/img/21940ad9eec2.jpg
