WongyuKoh/Toccata/hardware/bom/final-bom/img/29333bf05e22.jpg

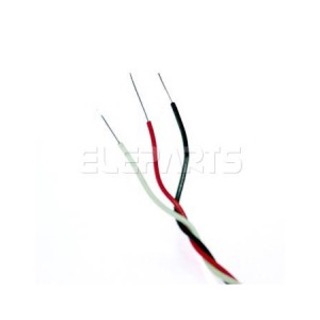
hardware/bom/final-bom/img/29333bf05e22.jpg
