WongyuKoh/Toccata/hardware/bom/final-bom/img/48245cc5c439.jpg

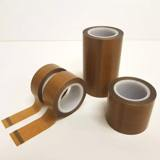
hardware/bom/final-bom/img/48245cc5c439.jpg
