WongyuKoh/Toccata/hardware/bom/final-bom/img/49668dcbfdd1.jpg

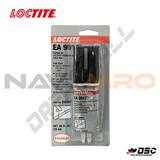
hardware/bom/final-bom/img/49668dcbfdd1.jpg
