WongyuKoh/Toccata/hardware/bom/final-bom/site/img/857016da1b7a.jpg

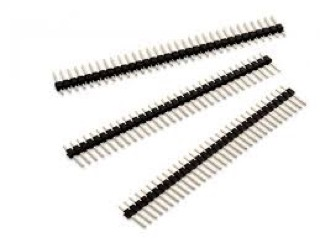
hardware/bom/final-bom/img/857016da1b7a.jpg
