WongyuKoh/Toccata/hardware/bom/final-bom/img/926713f17080.jpg

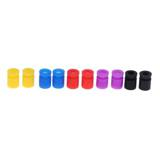
hardware/bom/final-bom/img/926713f17080.jpg
