WongyuKoh/Toccata/hardware/bom/final-bom/img/2479839be28c.jpg

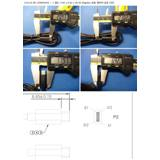
hardware/bom/final-bom/img/2479839be28c.jpg
