WongyuKoh/Toccata/hardware/bom/final-bom/site/img/5696831f28a2.jpg

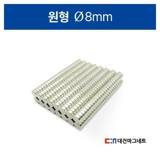
hardware/bom/final-bom/img/5696831f28a2.jpg
