WongyuKoh/Toccata/hardware/bom/final-bom/img/30359766edf1.jpg

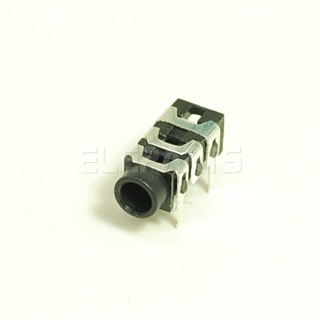
hardware/bom/final-bom/img/30359766edf1.jpg
