WongyuKoh/Toccata/hardware/bom/final-bom/img/a773c141ff21.jpg

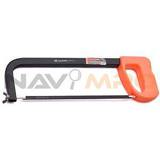
hardware/bom/final-bom/img/a773c141ff21.jpg
