WongyuKoh/Toccata/hardware/bom/final-bom/img/a6858e811c4c.jpg

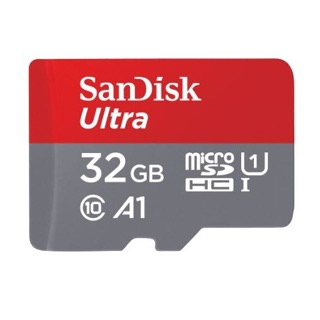
hardware/bom/final-bom/img/a6858e811c4c.jpg
