WongyuKoh/Toccata/hardware/bom/final-bom/img/a8054ecd0edc.jpg

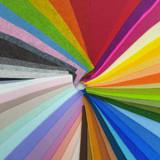
hardware/bom/final-bom/img/a8054ecd0edc.jpg
