WongyuKoh/Toccata/hardware/bom/final-bom/img/a847303e2e80.jpg

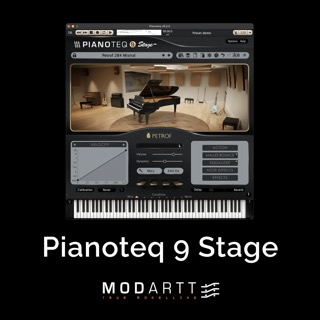
hardware/bom/final-bom/img/a847303e2e80.jpg
