WongyuKoh/Toccata/hardware/bom/final-bom/img/acb43f7c7db5.jpg

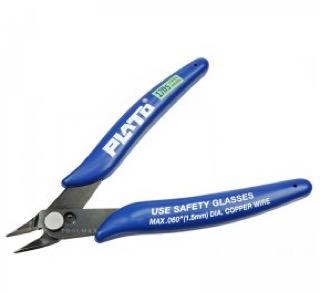
hardware/bom/final-bom/img/acb43f7c7db5.jpg
