WongyuKoh/Toccata/hardware/bom/final-bom/img/add1afb6dcb2.jpg

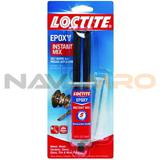
hardware/bom/final-bom/img/add1afb6dcb2.jpg
