WongyuKoh/Toccata/hardware/bom/final-bom/site/img/aed5c87a89db.jpg

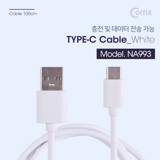
hardware/bom/final-bom/img/aed5c87a89db.jpg
