WongyuKoh/Toccata/hardware/bom/final-bom/site/img/b5cbf7bdd930.jpg

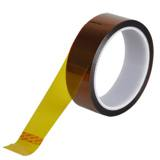
hardware/bom/final-bom/img/b5cbf7bdd930.jpg
