WongyuKoh/Toccata/hardware/bom/final-bom/site/img/b079bd4414f7.jpg

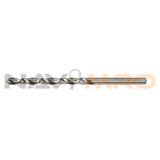
hardware/bom/final-bom/img/b079bd4414f7.jpg
