WongyuKoh/Toccata/hardware/bom/final-bom/img/beb4096e2716.jpg

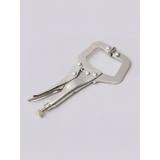
hardware/bom/final-bom/img/beb4096e2716.jpg
