WongyuKoh/Toccata/hardware/bom/final-bom/site/img/c3a75ddfcbac.jpg

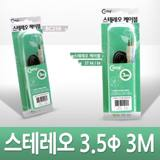
hardware/bom/final-bom/img/c3a75ddfcbac.jpg
