WongyuKoh/Toccata/hardware/bom/final-bom/site/img/c3380866f3b9.jpg

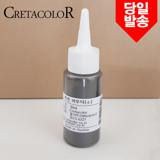
hardware/bom/final-bom/img/c3380866f3b9.jpg
