WongyuKoh/Toccata/hardware/bom/final-bom/site/img/cbdc8af7aa02.jpg

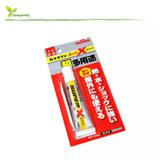
hardware/bom/final-bom/img/cbdc8af7aa02.jpg
