WongyuKoh/Toccata/hardware/bom/final-bom/site/img/cd0901dcf1cc.jpg

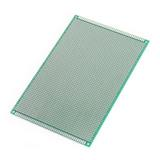
hardware/bom/final-bom/img/cd0901dcf1cc.jpg
