WongyuKoh/Toccata/hardware/bom/final-bom/img/d2026f89a87d.jpg

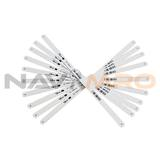
hardware/bom/final-bom/img/d2026f89a87d.jpg
