WongyuKoh/Toccata/hardware/bom/final-bom/site/img/df85a034cbc8.jpg

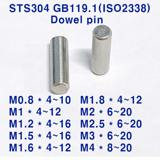
hardware/bom/final-bom/img/df85a034cbc8.jpg
