WongyuKoh/Toccata/hardware/bom/final-bom/site/img/e6a053a242ff.jpg

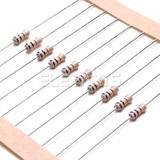
hardware/bom/final-bom/img/e6a053a242ff.jpg
