WongyuKoh/Toccata/hardware/bom/final-bom/site/img/e7f2f0b8669c.jpg

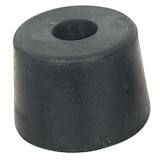
hardware/bom/final-bom/img/e7f2f0b8669c.jpg
