WongyuKoh/Toccata/hardware/bom/final-bom/site/img/e62f4203483e.jpg

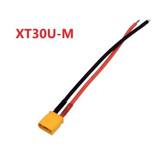
hardware/bom/final-bom/img/e62f4203483e.jpg
