WongyuKoh/Toccata/hardware/bom/final-bom/img/ea6afd9e29ac.jpg

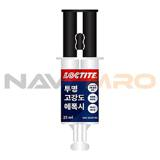
hardware/bom/final-bom/img/ea6afd9e29ac.jpg
