WongyuKoh/Toccata/hardware/bom/final-bom/img/eaaf538fc7ef.jpg

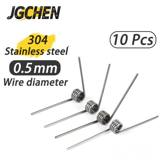
hardware/bom/final-bom/img/eaaf538fc7ef.jpg
