WongyuKoh/Toccata/hardware/bom/final-bom/img/eb859b23ecdf.jpg

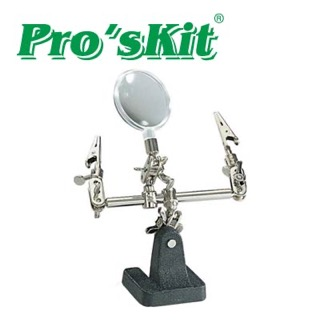
hardware/bom/final-bom/img/eb859b23ecdf.jpg
