WongyuKoh/Toccata/hardware/bom/final-bom/img/ec35c1204891.jpg

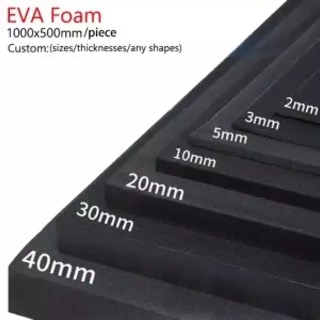
hardware/bom/final-bom/img/ec35c1204891.jpg
