WongyuKoh/Toccata/hardware/bom/final-bom/img/ec18087987eb.jpg

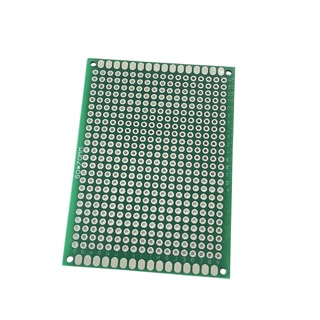
hardware/bom/final-bom/img/ec18087987eb.jpg
