WongyuKoh/Toccata/hardware/bom/final-bom/img/f7afd31e5518.jpg

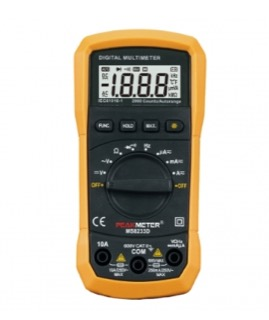
hardware/bom/final-bom/img/f7afd31e5518.jpg
