WongyuKoh/Toccata/hardware/bom/final-bom/img/f37eefface29.jpg

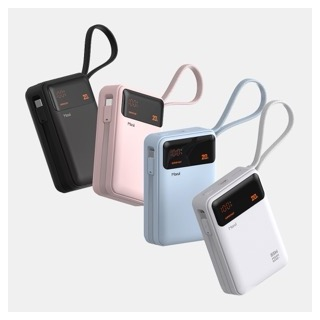
hardware/bom/final-bom/img/f37eefface29.jpg
