WongyuKoh/Toccata/hardware/bom/final-bom/img/f87ce07c9f39.jpg

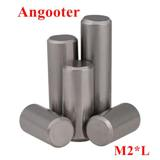
hardware/bom/final-bom/img/f87ce07c9f39.jpg
