WongyuKoh/Toccata/hardware/bom/final-bom/img/f4065a468b84.jpg

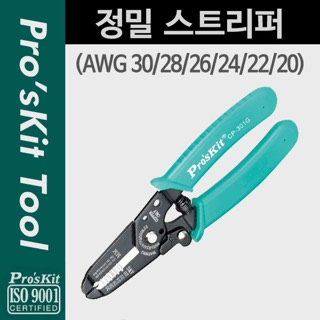
hardware/bom/final-bom/img/f4065a468b84.jpg
