WongyuKoh/Toccata/hardware/bom/final-bom/site/img/i006.jpg

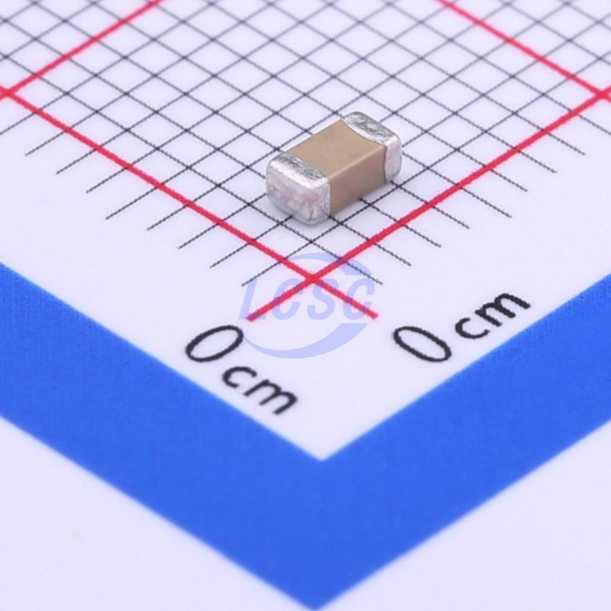
hardware/bom/final-bom/img/i006.jpg
