WongyuKoh/Toccata/hardware/bom/final-bom/site/img/i012.jpg

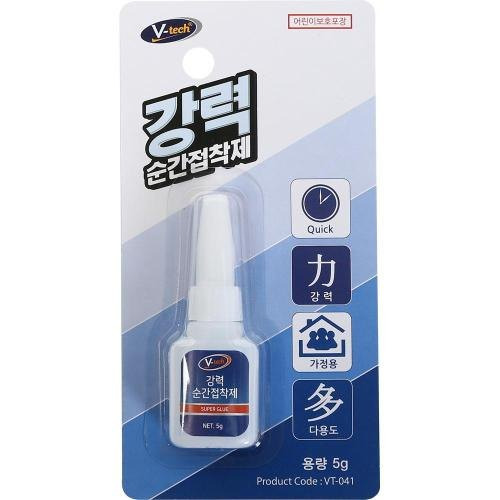
hardware/bom/final-bom/img/i012.jpg
