WongyuKoh/Toccata/hardware/bom/final-bom/site/img/i041.jpg

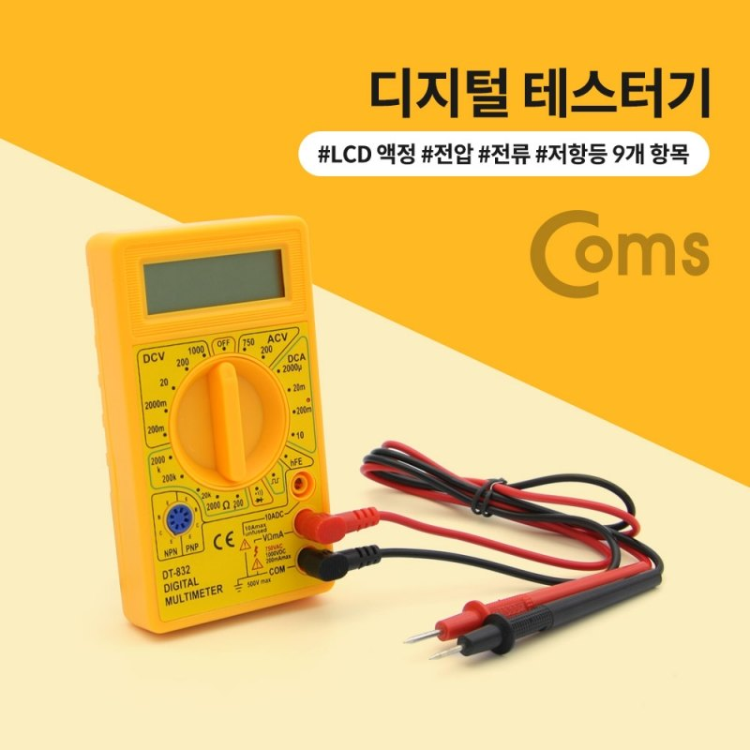
hardware/bom/final-bom/img/i041.jpg
