WongyuKoh/Toccata/hardware/bom/final-bom/site/img/i042.jpg

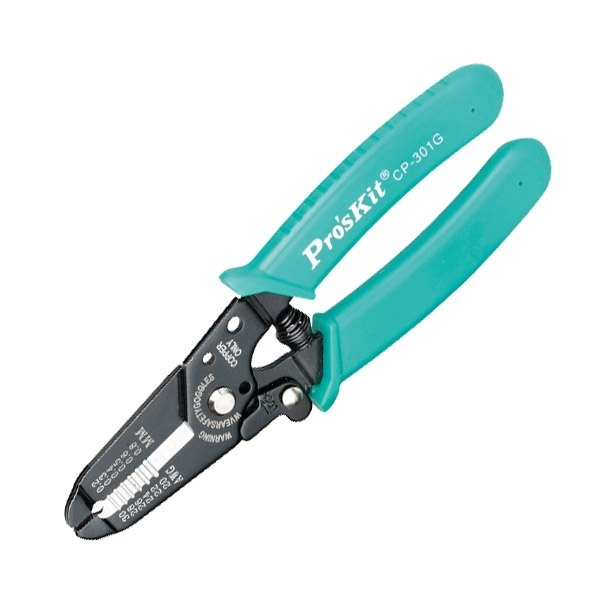
hardware/bom/final-bom/img/i042.jpg
