WongyuKoh/Toccata/hardware/bom/final-bom/site/img/i044.jpg

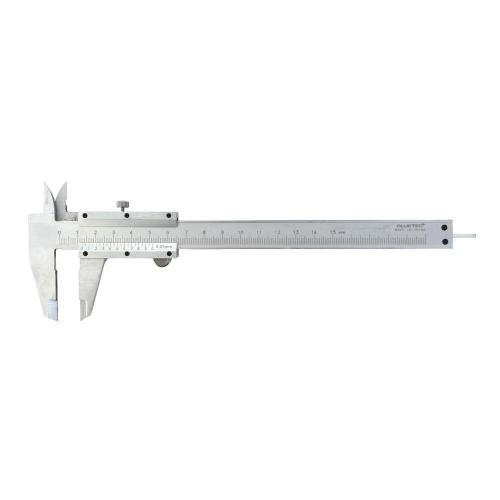
hardware/bom/final-bom/img/i044.jpg
