WongyuKoh/Toccata/hardware/bom/final-bom/site/img/i061.jpg

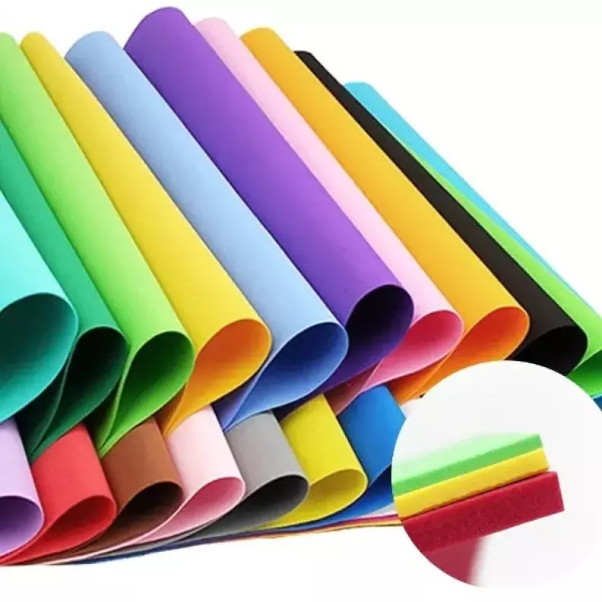
hardware/bom/final-bom/img/i061.jpg
