WongyuKoh/Toccata/hardware/bom/final-bom/site/img/i088.jpg

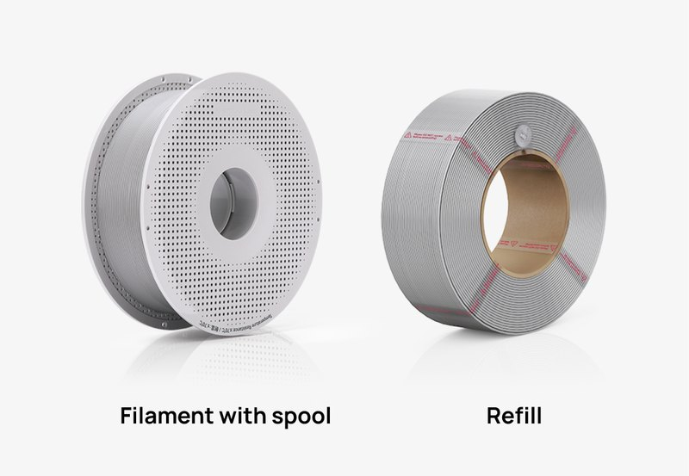
hardware/bom/final-bom/img/i088.jpg
