WongyuKoh/Toccata/hardware/bom/final-bom/site/img/i200.jpg

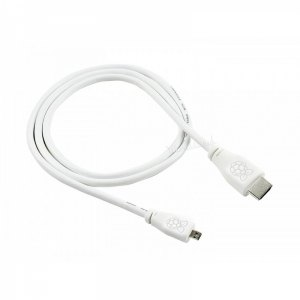
hardware/bom/final-bom/img/i200.jpg
