WongyuKoh/Toccata/hardware/bom/final-bom/site/img/t05_taphandle.jpg

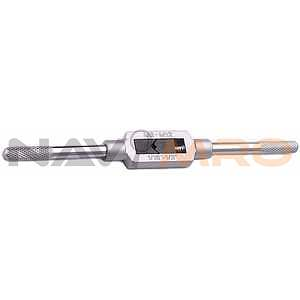
hardware/bom/final-bom/img/t05_taphandle.jpg
