WongyuKoh/Toccata/hardware/bom/final-bom/site/img/3f6031785611.jpg

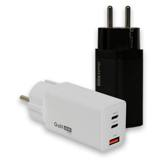
hardware/bom/final-bom/site/img/3f6031785611.jpg
