WongyuKoh/Toccata/hardware/bom/final-bom/site/img/86f46b009a06.jpg

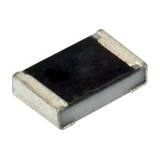
hardware/bom/final-bom/site/img/86f46b009a06.jpg
