WongyuKoh/Toccata/hardware/bom/final-bom/site/img/fbfaafef8d42.jpg

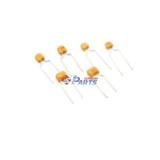
hardware/bom/final-bom/site/img/fbfaafef8d42.jpg
