WongyuKoh/Toccata/hardware/bom/final-bom/site/img/i057.jpg

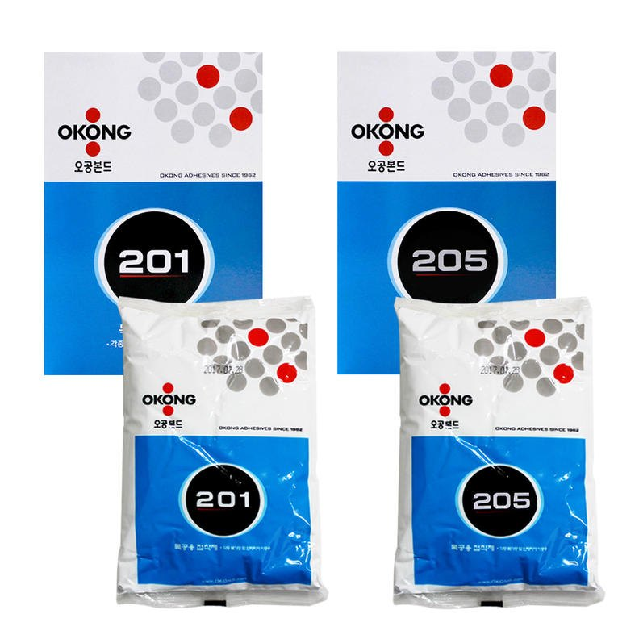
hardware/bom/final-bom/site/img/i057.jpg
