WongyuKoh/Toccata/hardware/bom/final-bom/site/img/i063.jpg

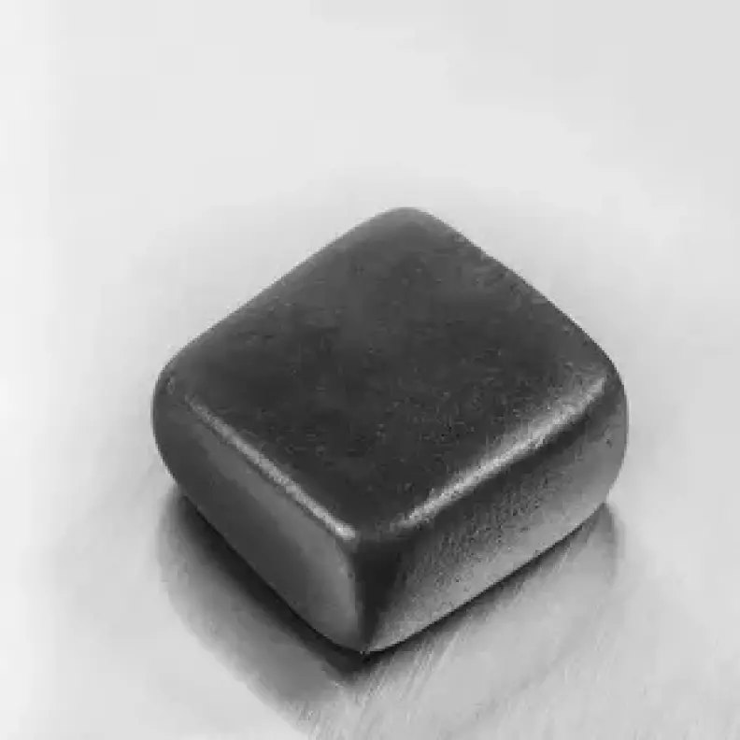
hardware/bom/final-bom/site/img/i063.jpg
