WongyuKoh/Toccata/hardware/bom/final-bom/site/img/i082.jpg

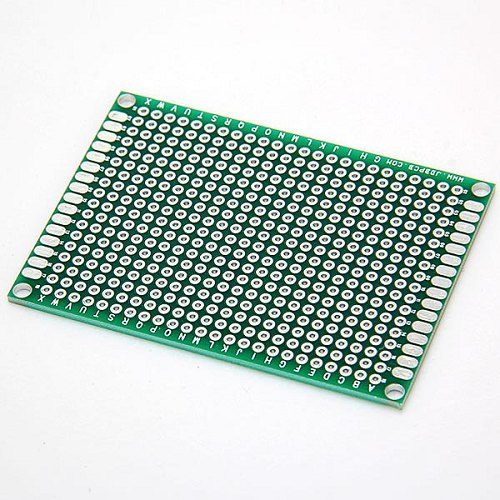
hardware/bom/final-bom/site/img/i082.jpg
