WongyuKoh/Toccata/hardware/bom/final-bom/site/img/i087.jpg

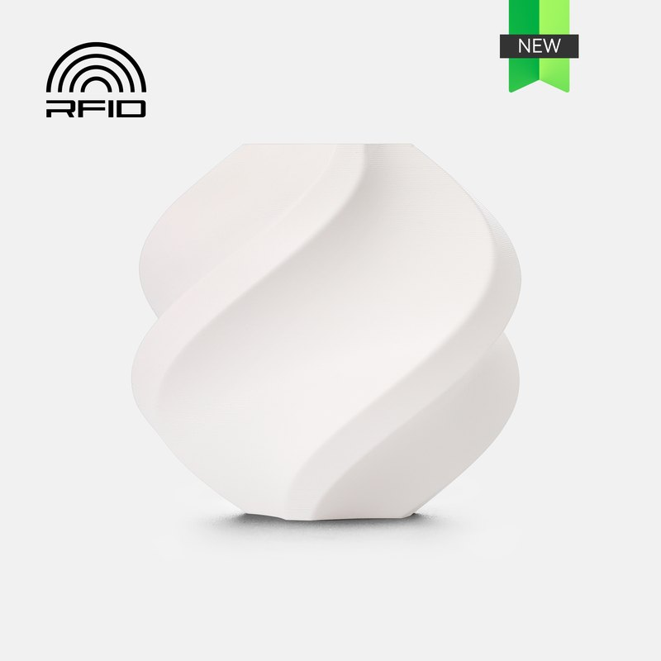
hardware/bom/final-bom/site/img/i087.jpg
