WongyuKoh/Toccata/hardware/bom/final-bom/site/img/i089.jpg

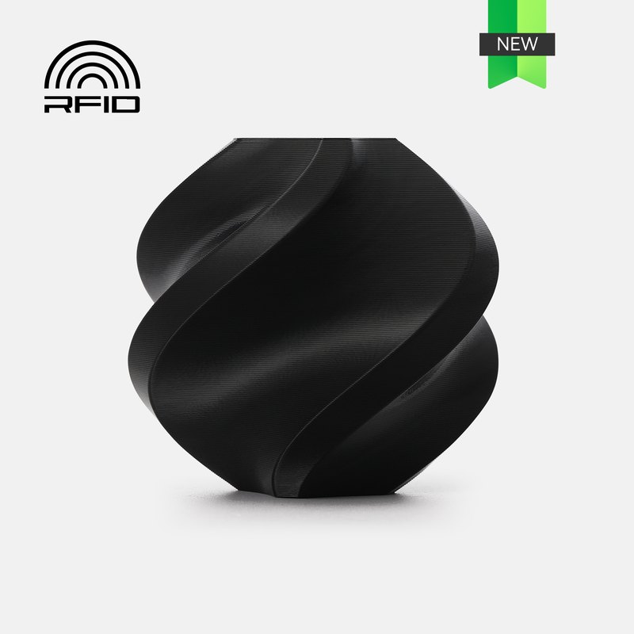
hardware/bom/final-bom/site/img/i089.jpg
