WongyuKoh/Toccata/hardware/bom/final-bom/site/img/ws_7dsi_touch_c.jpg

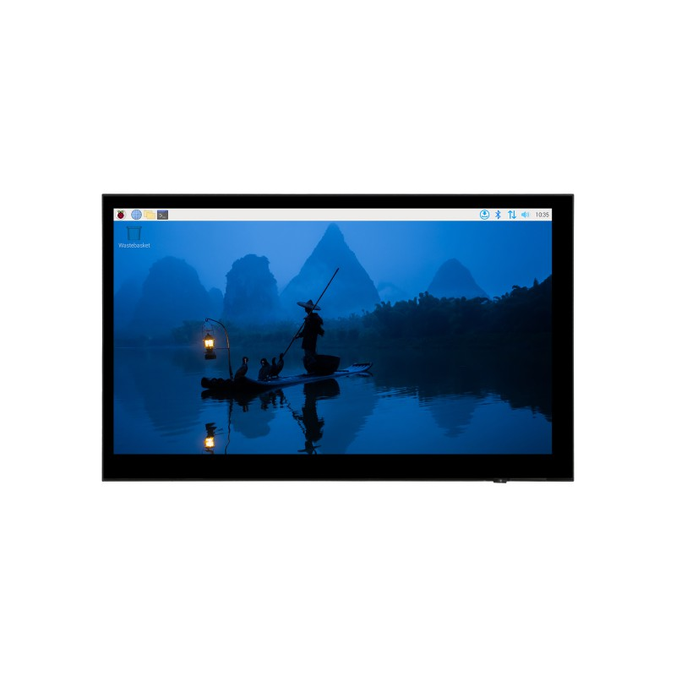
hardware/bom/final-bom/site/img/ws_7dsi_touch_c.jpg
