WongyuKoh/Toccata/hardware/mechanical/before/cad/stl/coupons.stl

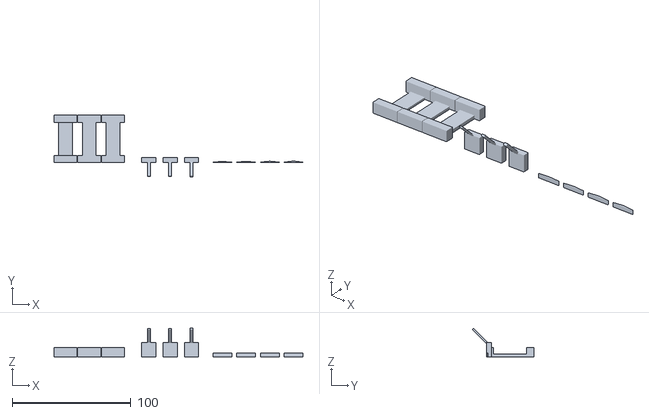
[picture p195: CAD file, 2026-10-02]
hardware/mechanical/before/cad/stl/coupons.stl
210.0 x 51.9 x 24.1
