WongyuKoh/Toccata/hardware/mechanical/before/cad/stl/v1.5-multipart/white_B.stl

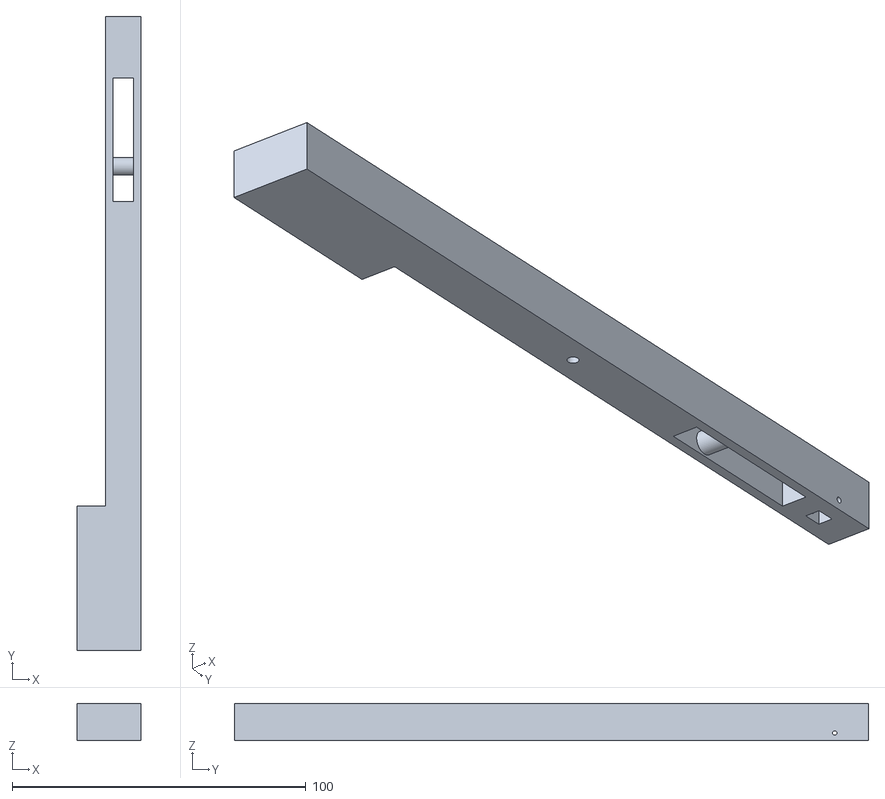
[picture p196: CAD file, 2026-10-02]
hardware/mechanical/before/cad/stl/v1.5-multipart/white_B.stl
21.9 x 216.0 x 12.7
