WongyuKoh/Toccata/hardware/mechanical/cad/stl/print/01_건반/백건_C8__1개.stl

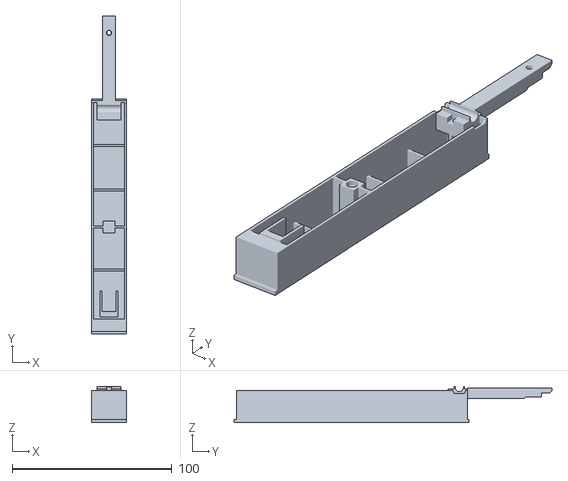
[picture p197: CAD file, 2026-10-02]
hardware/mechanical/cad/stl/print/01_건반/백건_C8__1개.stl
22.0 x 199.0 x 22.8
