WongyuKoh/Toccata/hardware/mechanical/cad/stl/print/03_프레임/끝부속프레임_왼쪽__1개.stl

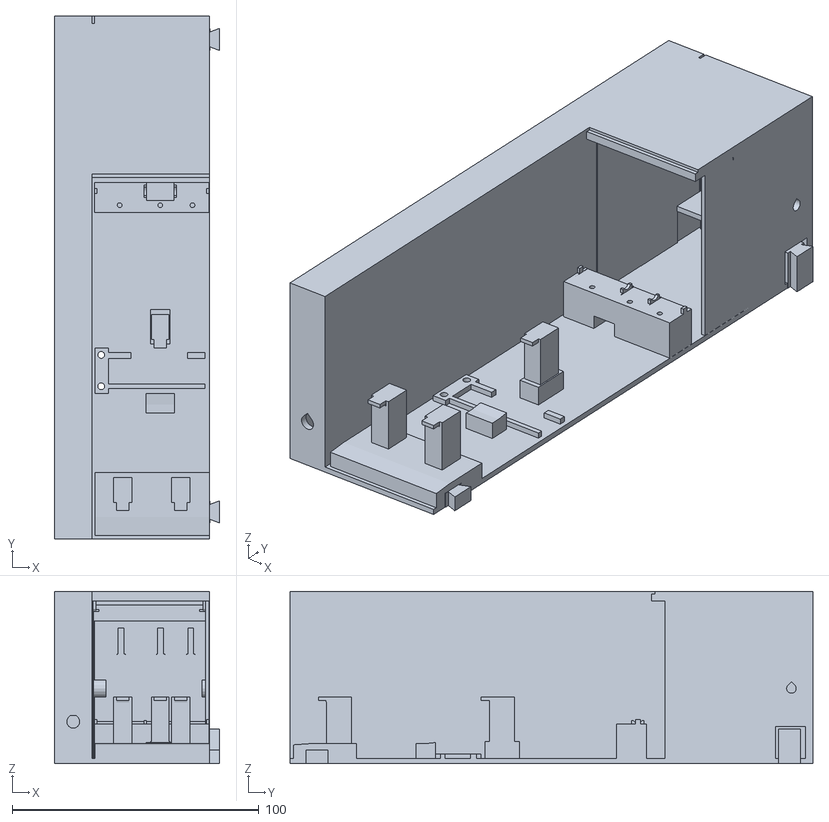
[picture p198: CAD file, 2026-10-02]
hardware/mechanical/cad/stl/print/03_프레임/끝부속프레임_왼쪽__1개.stl
67.0 x 212.0 x 69.8
