WongyuKoh/Toccata/hardware/mechanical/cad/stl/print/04b_패드바_PORON5T용/패드바_칸1_PORON5T용__7개.stl

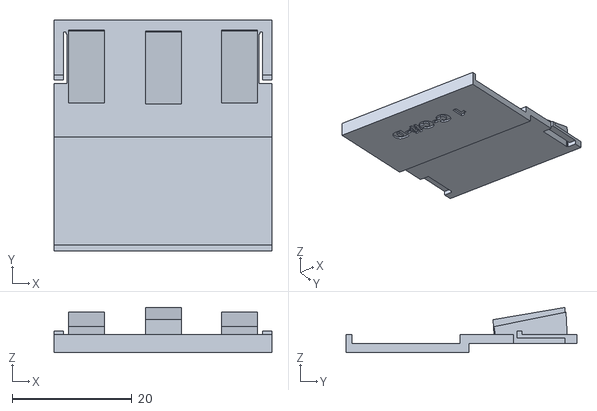
[picture p200: CAD file, 2026-10-02]
hardware/mechanical/cad/stl/print/04b_패드바_PORON5T용/패드바_칸1_PORON5T용__7개.stl
36.4 x 38.5 x 7.53
