WongyuKoh/Toccata/hardware/mechanical/cad/stl/print/05_본체출력물/통로옆마개__2개.stl

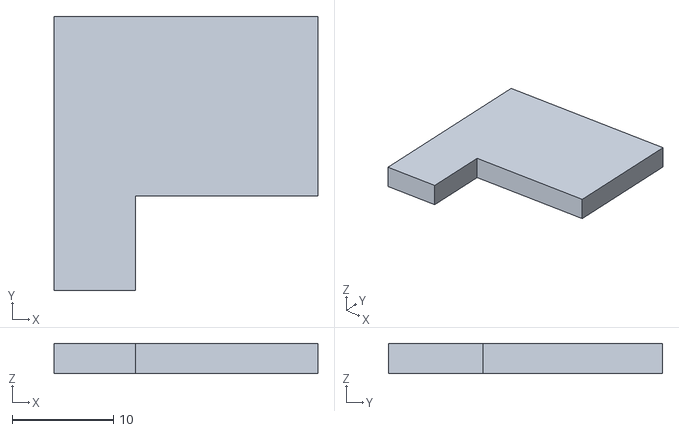
[picture p201: CAD file, 2026-10-02]
hardware/mechanical/cad/stl/print/05_본체출력물/통로옆마개__2개.stl
26.0 x 27.0 x 3.00
