WongyuKoh/Toccata/hardware/mechanical/cad/stl/print/06_출력공구/공구_벤치지그받침_T1a__1개.stl

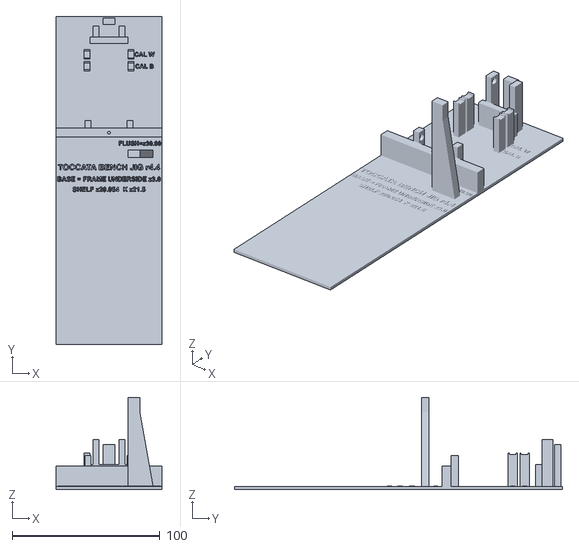
[picture p202: CAD file, 2026-10-02]
hardware/mechanical/cad/stl/print/06_출력공구/공구_벤치지그받침_T1a__1개.stl
72.0 x 222.0 x 62.5
