WongyuKoh/Toccata/hardware/mechanical/cad/stl/print/07_터치스크린/받침다리__1개.stl

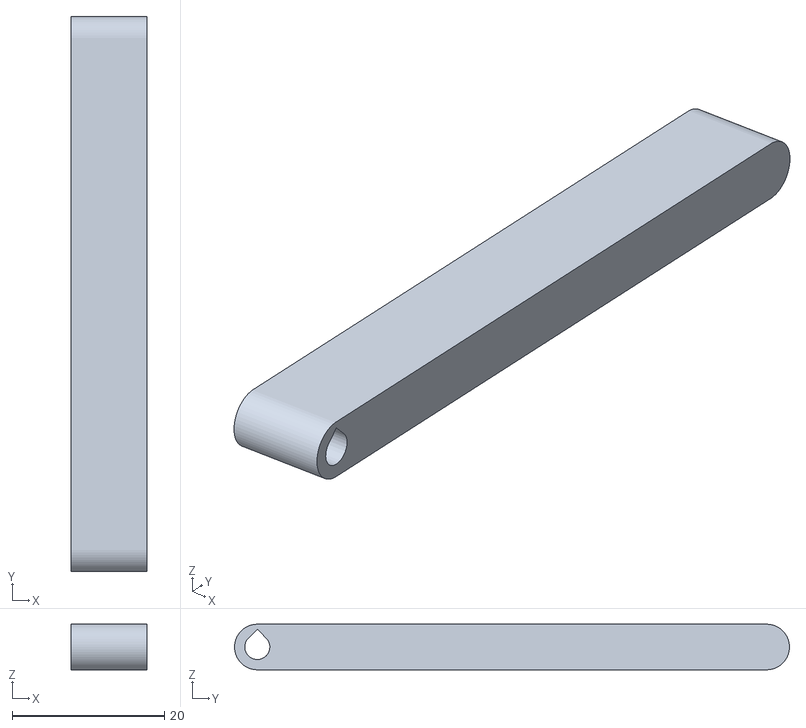
[picture p203: CAD file, 2026-10-02]
hardware/mechanical/cad/stl/print/07_터치스크린/받침다리__1개.stl
10.0 x 73.0 x 5.99
