WongyuKoh/Toccata/hardware/mechanical/key-action-v4/printables/stage0/stl/C08a.stl

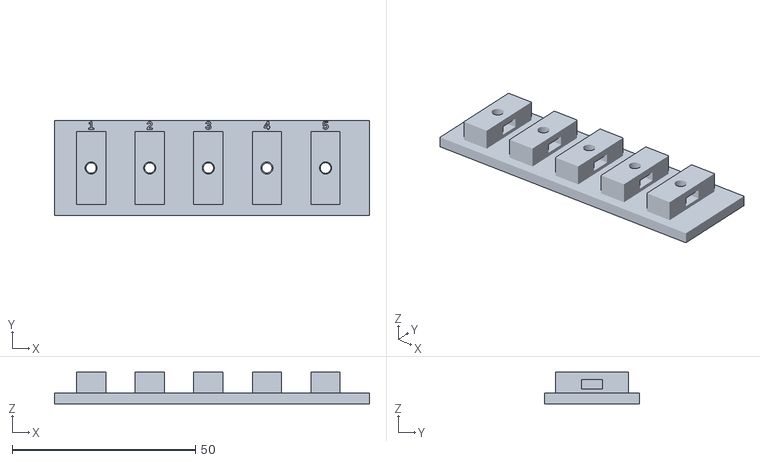
[picture p204: CAD file, 2026-10-02]
hardware/mechanical/key-action-v4/printables/stage0/stl/C08a.stl
86.0 x 26.0 x 8.70
