WongyuKoh/Toccata/hardware/mechanical/key-action-v4/printables/tools/stl/tool_pin_gauge.stl

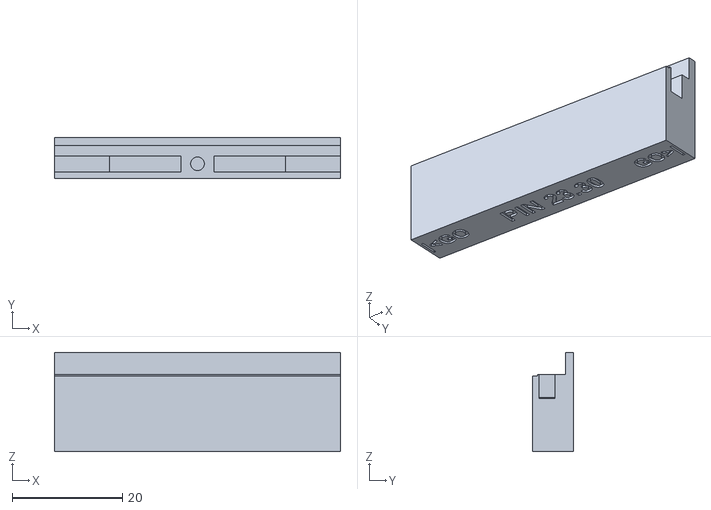
[picture p205: CAD file, 2026-10-02]
hardware/mechanical/key-action-v4/printables/tools/stl/tool_pin_gauge.stl
52.0 x 7.50 x 18.0
