WongyuKoh/Toccata/hardware/mechanical/before/cad/stl/key_black.stl

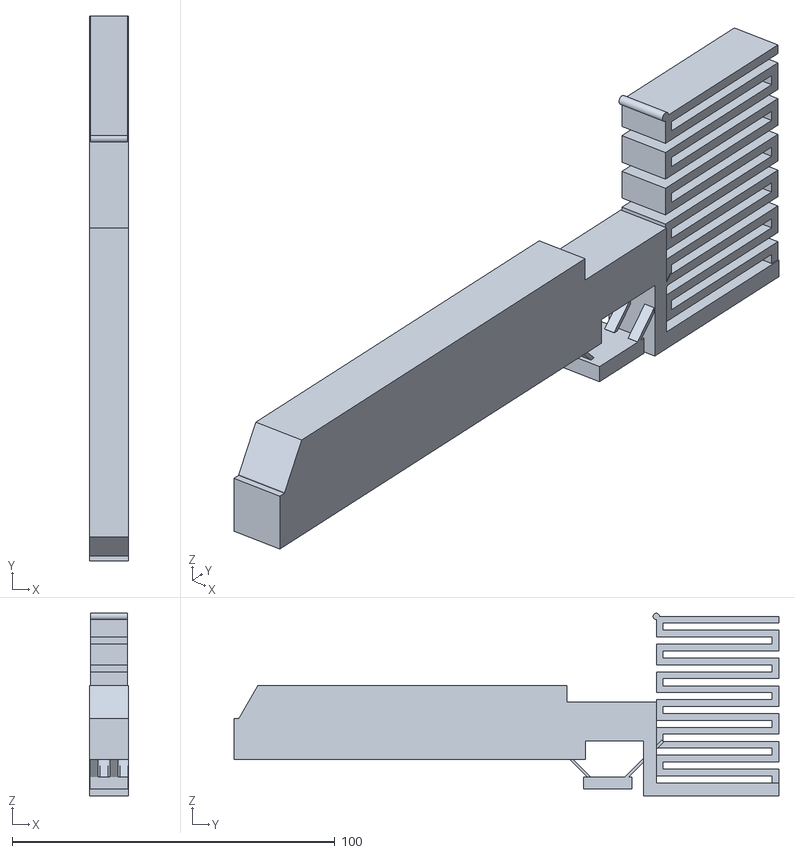
[picture p206: CAD file, 2026-10-02]
hardware/mechanical/before/cad/stl/key_black.stl
12.1 x 168.8 x 56.6
