WongyuKoh/Toccata/hardware/mechanical/before/cad/stl/v1.5-multipart/fallboard.stl

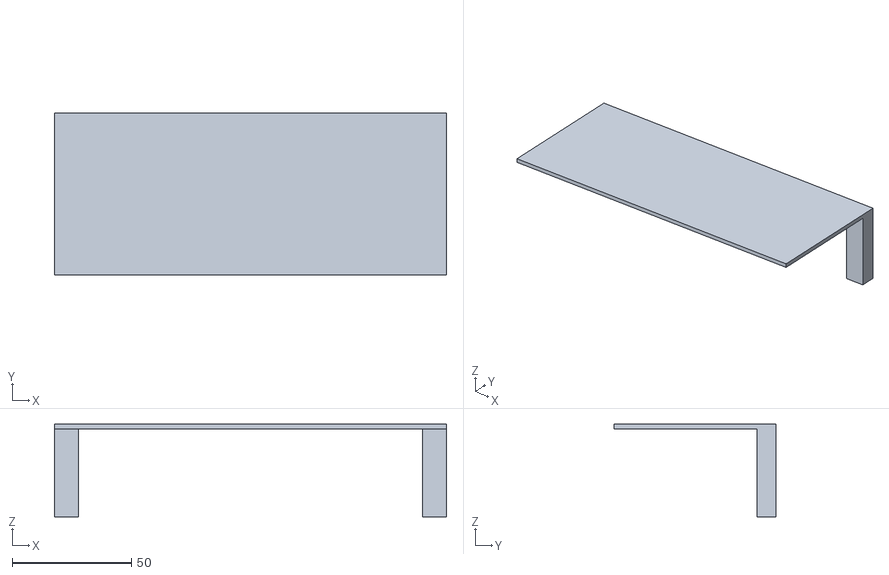
[picture p207: CAD file, 2026-10-02]
hardware/mechanical/before/cad/stl/v1.5-multipart/fallboard.stl
164.5 x 68.0 x 39.0
