WongyuKoh/Toccata/hardware/mechanical/cad/stl/print/02_레버캐리어/레버캐리어_C#__7개.stl

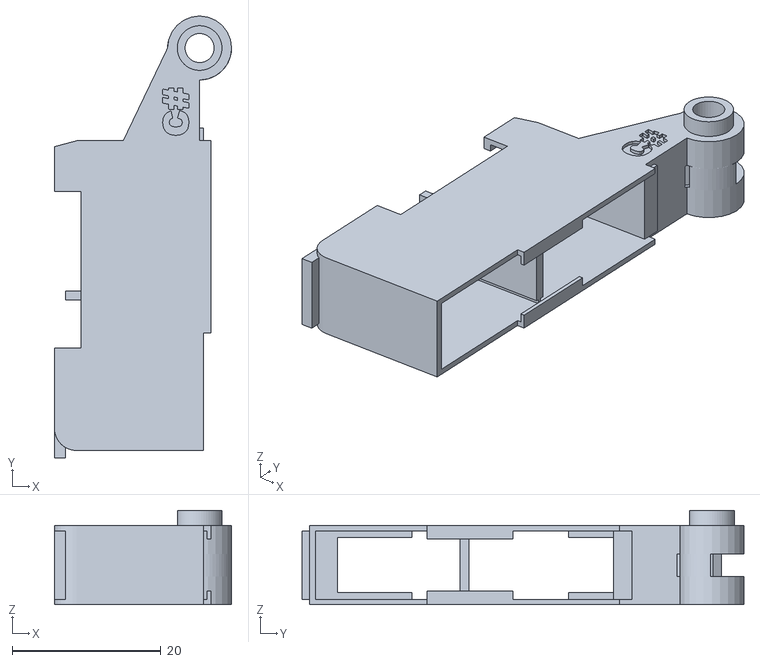
[picture p209: CAD file, 2026-10-02]
hardware/mechanical/cad/stl/print/02_레버캐리어/레버캐리어_C#__7개.stl
23.8 x 59.3 x 12.6
