WongyuKoh/Toccata/hardware/mechanical/cad/stl/print/03_프레임/끝부속프레임_오른쪽__1개.stl

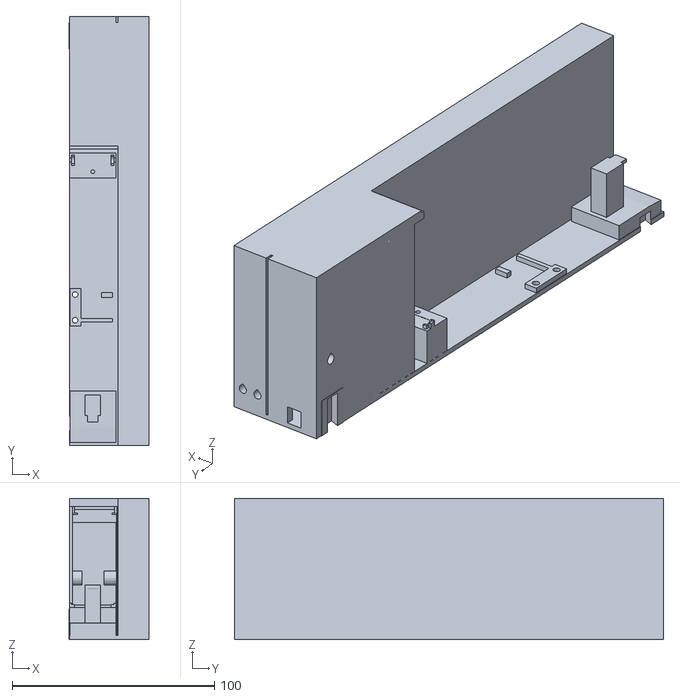
[picture p210: CAD file, 2026-10-02]
hardware/mechanical/cad/stl/print/03_프레임/끝부속프레임_오른쪽__1개.stl
39.5 x 212.0 x 69.8
