WongyuKoh/Toccata/hardware/mechanical/cad/stl/print/04_센서바·패드바·가림판·마개/레버봉끝마개__9개.stl

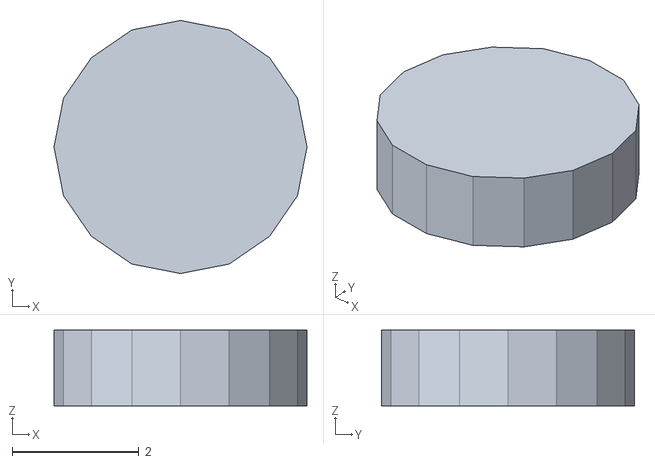
[picture p211: CAD file, 2026-10-02]
hardware/mechanical/cad/stl/print/04_센서바·패드바·가림판·마개/레버봉끝마개__9개.stl
4.00 x 4.00 x 1.20
