WongyuKoh/Toccata/hardware/mechanical/cad/stl/print/04b_패드바_PORON5T용/패드바_끝부속_오른쪽_PORON5T용__1개.stl

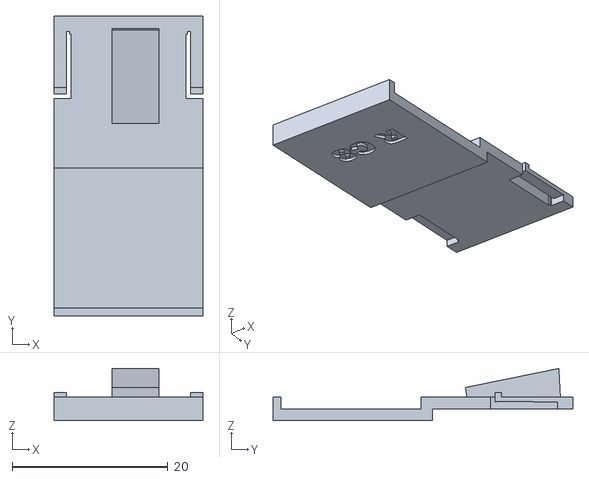
[picture p212: CAD file, 2026-10-02]
hardware/mechanical/cad/stl/print/04b_패드바_PORON5T용/패드바_끝부속_오른쪽_PORON5T용__1개.stl
19.1 x 38.5 x 6.68
