WongyuKoh/Toccata/hardware/mechanical/cad/stl/print/05_본체출력물/뒤판출력물_IO__1개.stl

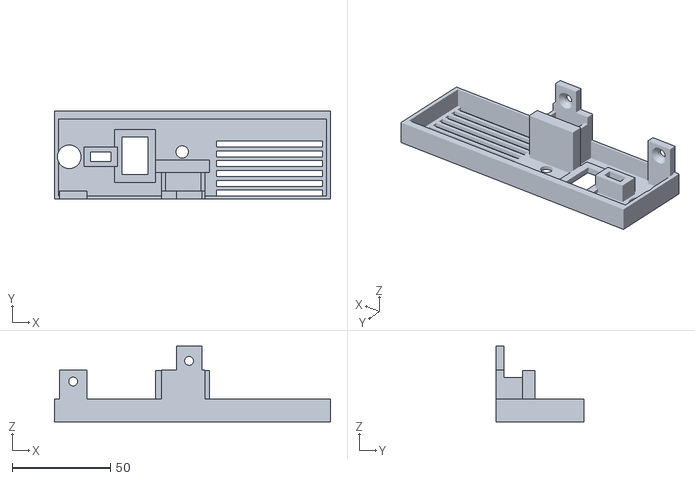
[picture p213: CAD file, 2026-10-02]
hardware/mechanical/cad/stl/print/05_본체출력물/뒤판출력물_IO__1개.stl
140.5 x 44.8 x 38.5
