WongyuKoh/Toccata/hardware/mechanical/cad/stl/print/07_터치스크린/화면받침_크래들__1개.stl

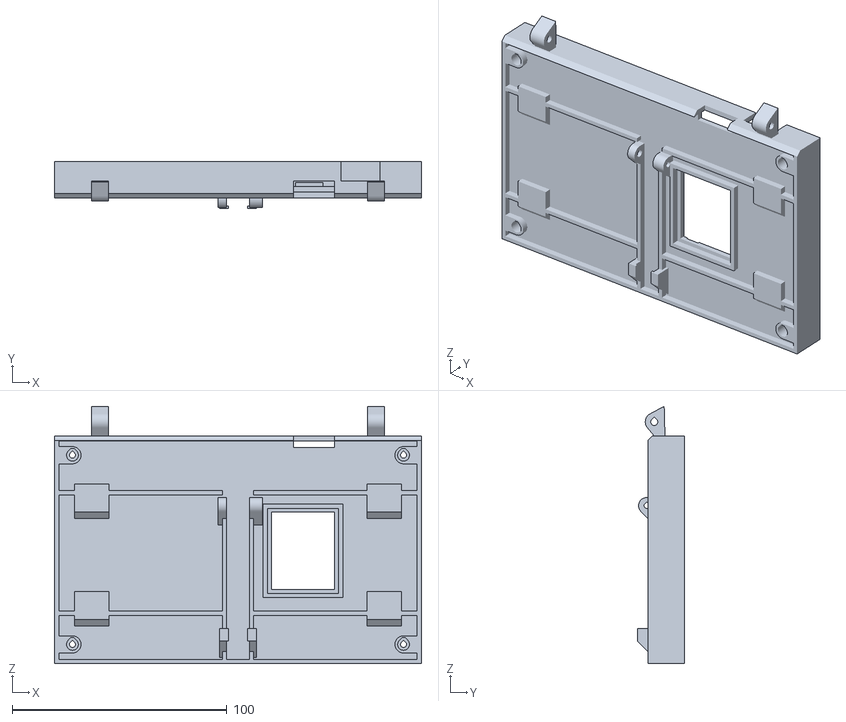
[picture p214: CAD file, 2026-10-02]
hardware/mechanical/cad/stl/print/07_터치스크린/화면받침_크래들__1개.stl
170.7 x 21.7 x 119.8
