WongyuKoh/Toccata/hardware/mechanical/key-action-v4/printables/stage0/stl/C04c.stl

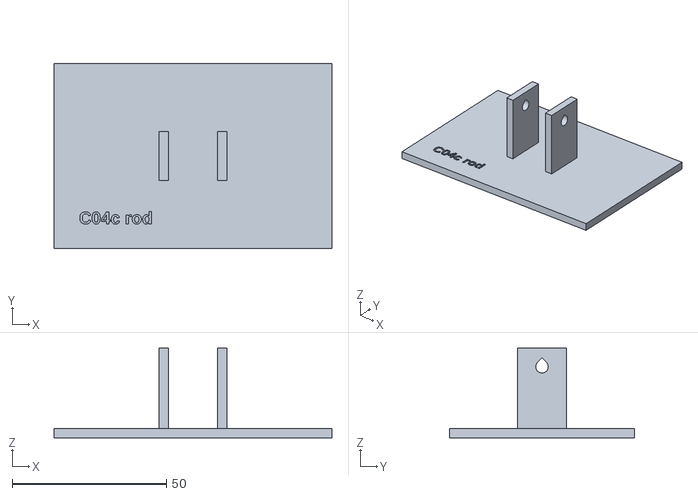
[picture p215: CAD file, 2026-10-02]
hardware/mechanical/key-action-v4/printables/stage0/stl/C04c.stl
90.0 x 60.0 x 29.0
