WongyuKoh/Toccata/hardware/mechanical/before/cad/stl/key_white.stl

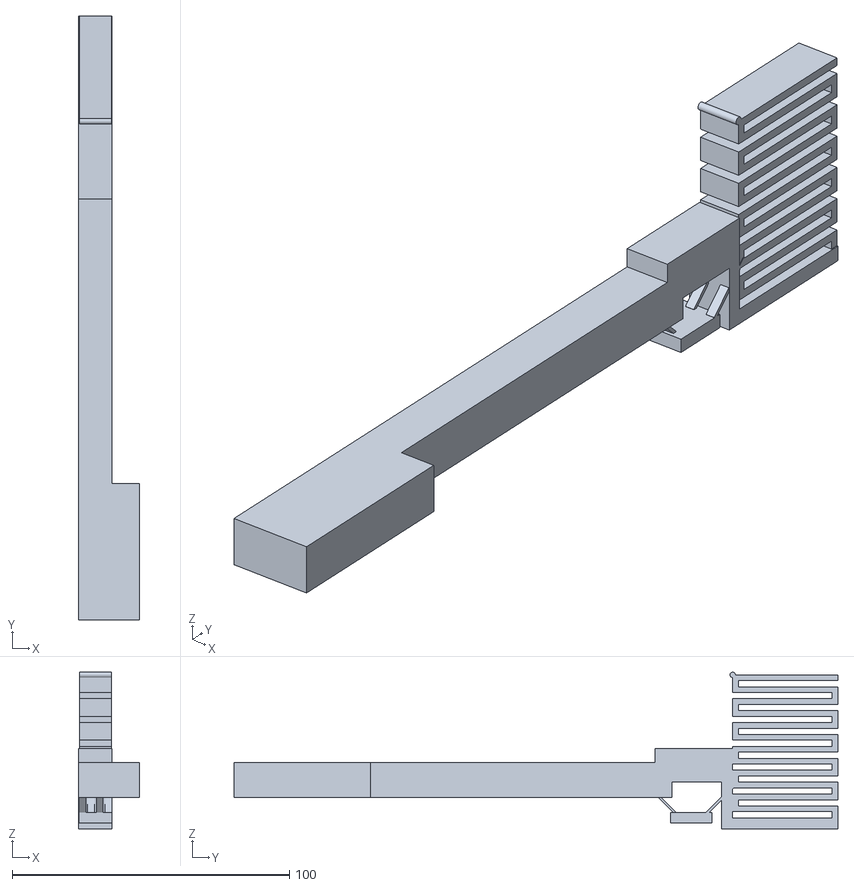
[picture p216: CAD file, 2026-10-02]
hardware/mechanical/before/cad/stl/key_white.stl
21.9 x 218.0 x 56.6
