WongyuKoh/Toccata/hardware/mechanical/before/cad/stl/v1.5-multipart/bed3.stl

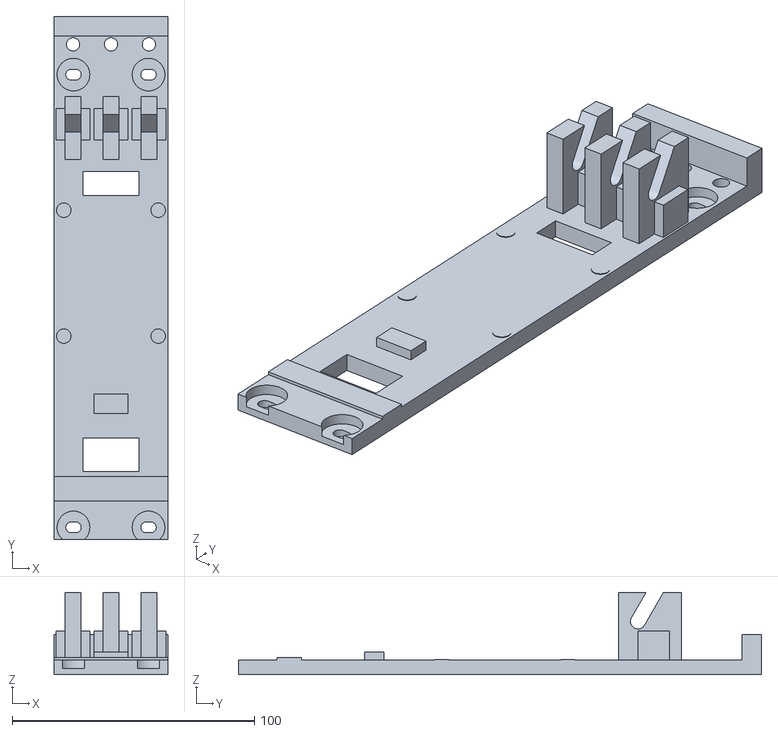
[picture p217: CAD file, 2026-10-02]
hardware/mechanical/before/cad/stl/v1.5-multipart/bed3.stl
47.0 x 216.0 x 34.0
