WongyuKoh/Toccata/hardware/mechanical/cad/stl/print/04_센서바·패드바·가림판·마개/패드바_끝부속_오른쪽__1개.stl

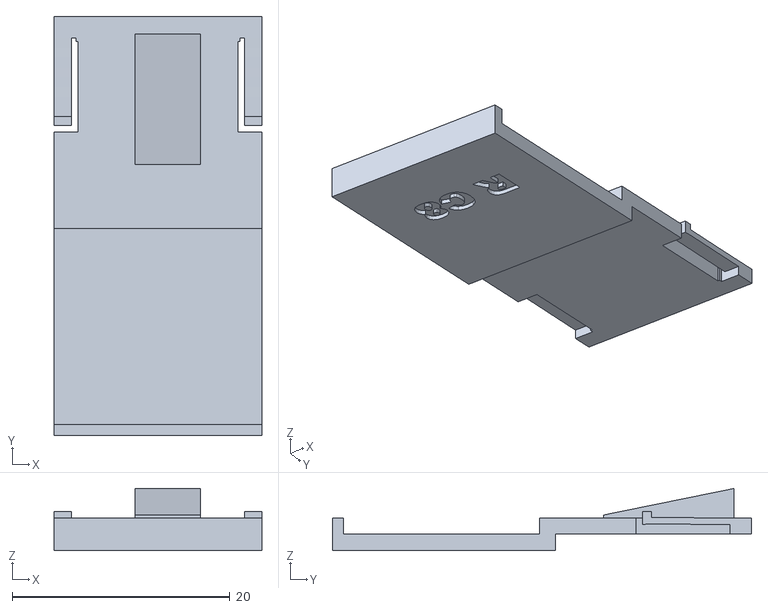
[picture p218: CAD file, 2026-10-02]
hardware/mechanical/cad/stl/print/04_센서바·패드바·가림판·마개/패드바_끝부속_오른쪽__1개.stl
19.1 x 38.5 x 5.70
