WongyuKoh/Toccata/hardware/mechanical/cad/stl/print/05_본체출력물/방진브래킷2_L__1개.stl

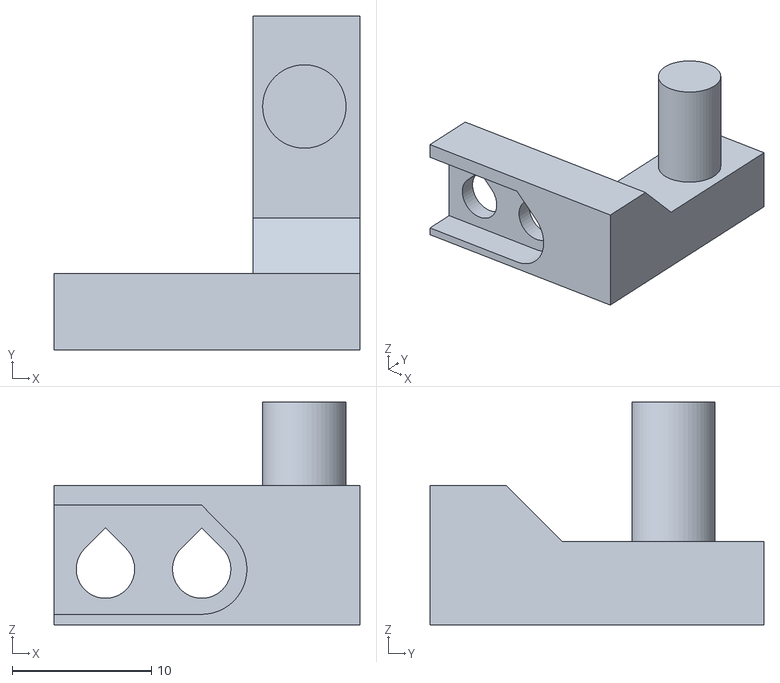
[picture p220: CAD file, 2026-10-02]
hardware/mechanical/cad/stl/print/05_본체출력물/방진브래킷2_L__1개.stl
22.0 x 24.0 x 16.0
