WongyuKoh/Toccata/hardware/mechanical/cad/stl/print/07_터치스크린/화면덮개_선택__1개.stl

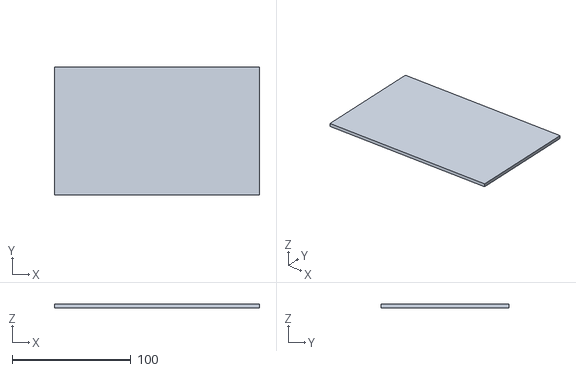
[picture p221: CAD file, 2026-10-02]
hardware/mechanical/cad/stl/print/07_터치스크린/화면덮개_선택__1개.stl
173.0 x 108.0 x 3.00
