WongyuKoh/Toccata/hardware/mechanical/key-action-v4/printables/stage0/stl/C12a.stl

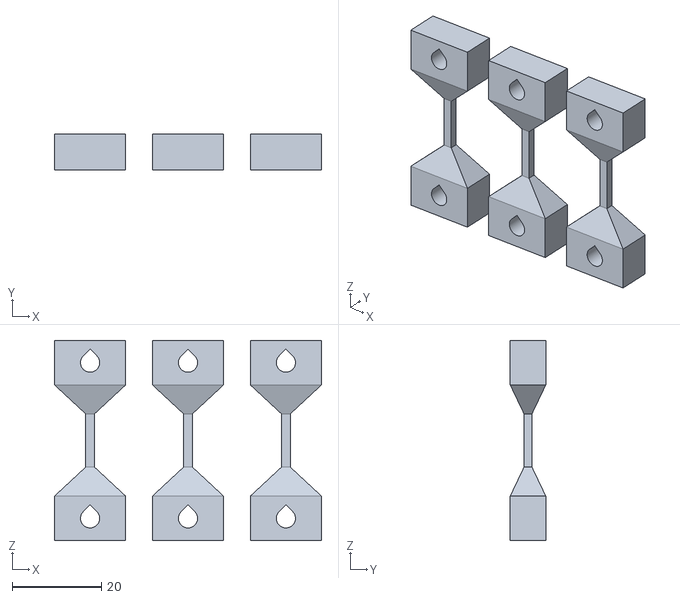
[picture p222: CAD file, 2026-10-02]
hardware/mechanical/key-action-v4/printables/stage0/stl/C12a.stl
60.0 x 8.00 x 45.0
