WongyuKoh/Toccata/hardware/mechanical/before/cad/stl/rail.stl

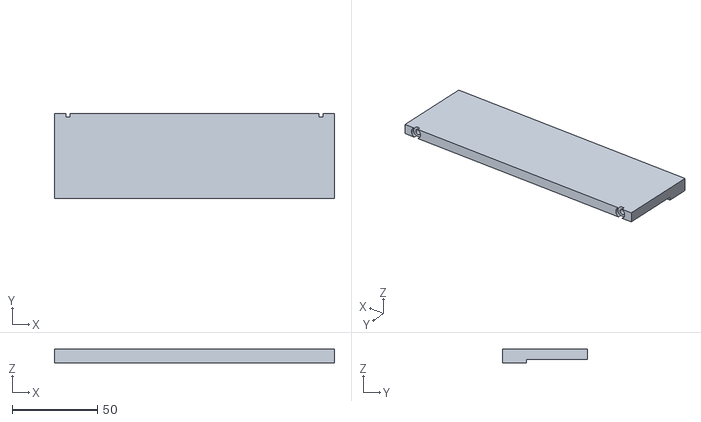
[picture p223: CAD file, 2026-10-02]
hardware/mechanical/before/cad/stl/rail.stl
164.5 x 50.0 x 8.00
