WongyuKoh/Toccata/hardware/mechanical/cad/stl/print/04_센서바·패드바·가림판·마개/센서바_오른쪽__1개.stl

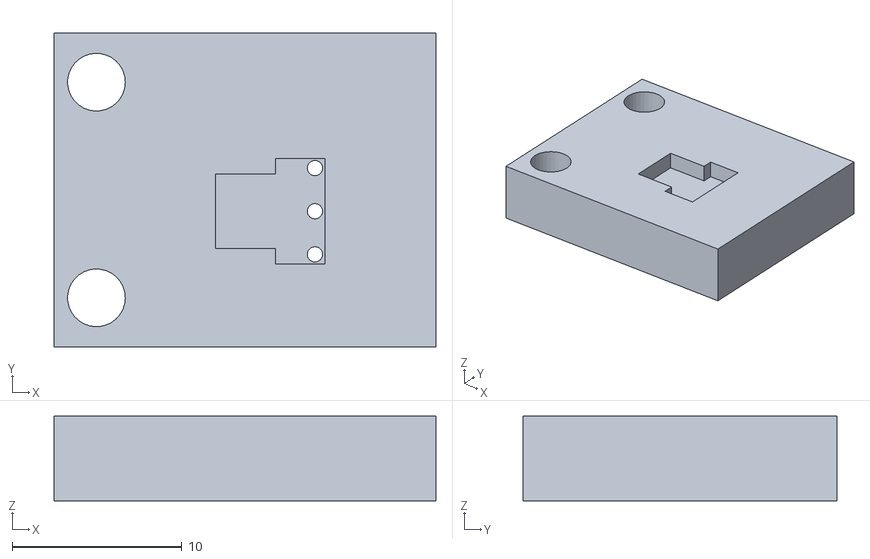
[picture p225: CAD file, 2026-10-02]
hardware/mechanical/cad/stl/print/04_센서바·패드바·가림판·마개/센서바_오른쪽__1개.stl
22.5 x 18.5 x 5.00
