WongyuKoh/Toccata/hardware/mechanical/cad/stl/print/05_본체출력물/퓨즈홀더받침__1개.stl

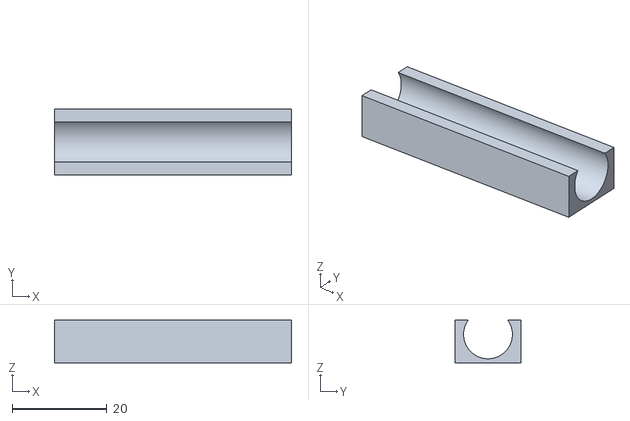
[picture p226: CAD file, 2026-10-02]
hardware/mechanical/cad/stl/print/05_본체출력물/퓨즈홀더받침__1개.stl
50.0 x 14.0 x 9.00
