WongyuKoh/Toccata/hardware/mechanical/cad/stl/print/07_터치스크린/리본클립__1개.stl

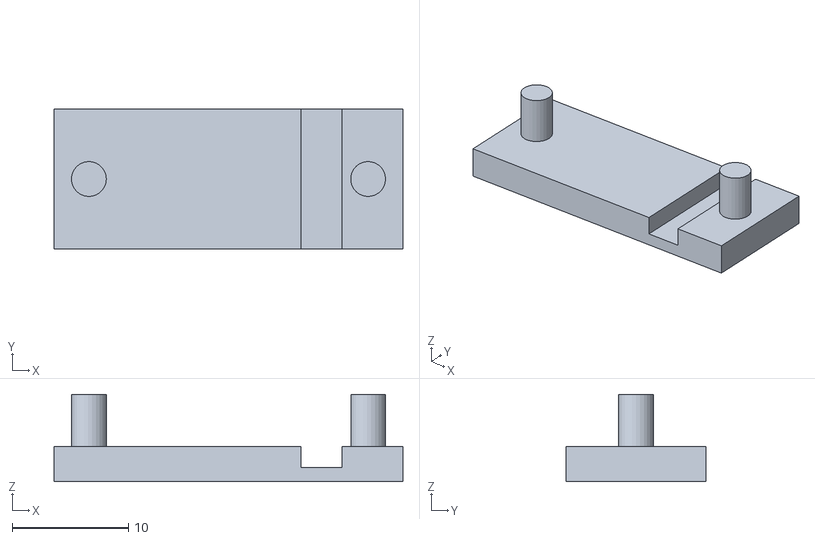
[picture p227: CAD file, 2026-10-02]
hardware/mechanical/cad/stl/print/07_터치스크린/리본클립__1개.stl
30.0 x 12.0 x 7.50
