WongyuKoh/Toccata/hardware/mechanical/key-action-v4/printables/stage0/stl/C06a.stl

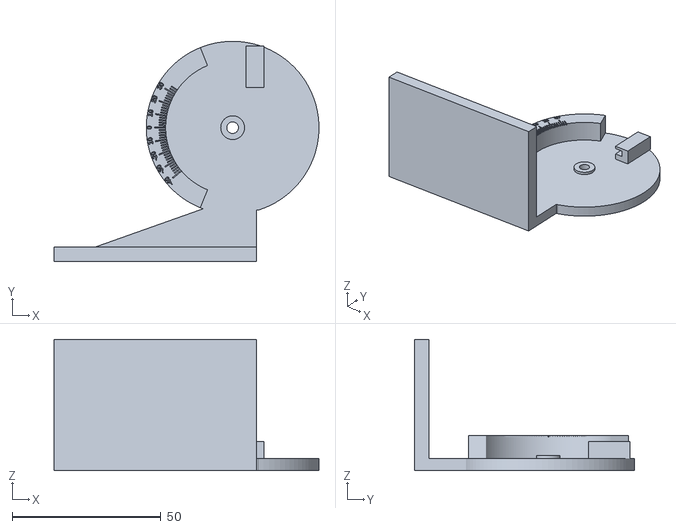
[picture p228: CAD file, 2026-10-02]
hardware/mechanical/key-action-v4/printables/stage0/stl/C06a.stl
89.0 x 74.0 x 44.0
