WongyuKoh/Toccata/hardware/mechanical/before/cad/stl/v1.5-multipart/bed13.stl

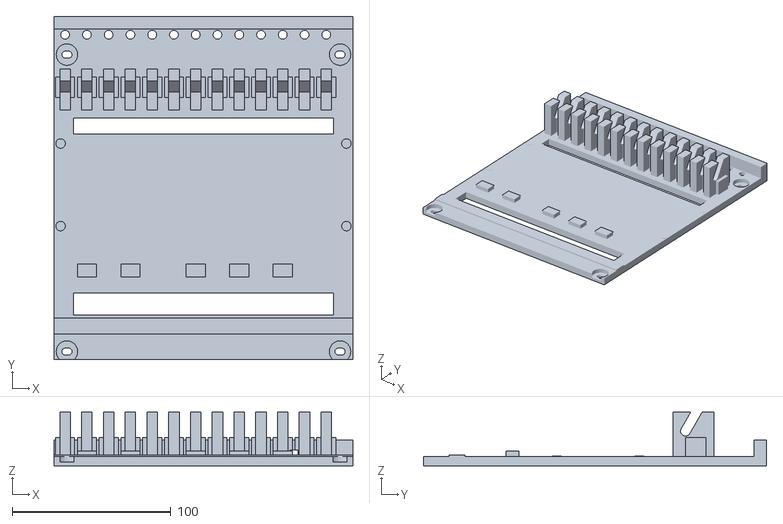
[picture p229: CAD file, 2026-10-02]
hardware/mechanical/before/cad/stl/v1.5-multipart/bed13.stl
188.0 x 216.0 x 34.0
