WongyuKoh/Toccata/hardware/mechanical/cad/stl/print/01_건반/흑건_A#·A#0__8개.stl

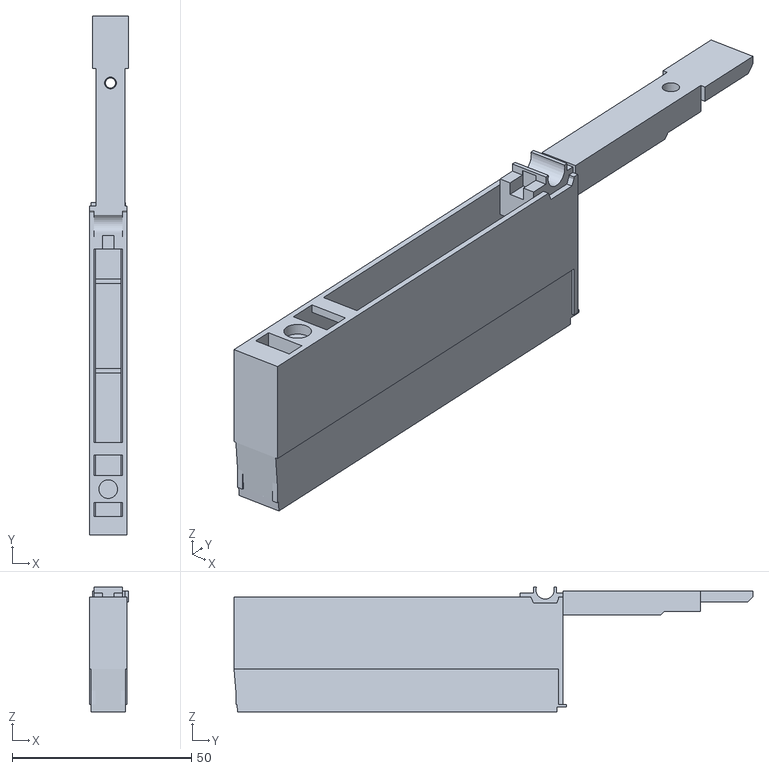
[picture p230: CAD file, 2026-10-02]
hardware/mechanical/cad/stl/print/01_건반/흑건_A#·A#0__8개.stl
10.8 x 144.8 x 34.8
