WongyuKoh/Toccata/hardware/mechanical/cad/stl/print/04_센서바·패드바·가림판·마개/패드바_칸2__7개.stl

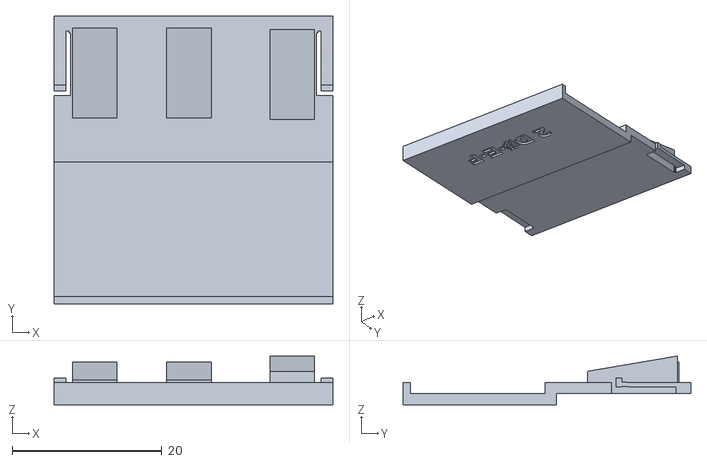
[picture p231: CAD file, 2026-10-02]
hardware/mechanical/cad/stl/print/04_센서바·패드바·가림판·마개/패드바_칸2__7개.stl
37.3 x 38.5 x 6.54
