WongyuKoh/Toccata/hardware/mechanical/cad/stl/print/04b_패드바_PORON5T용/패드바_칸2_PORON5T용__7개.stl

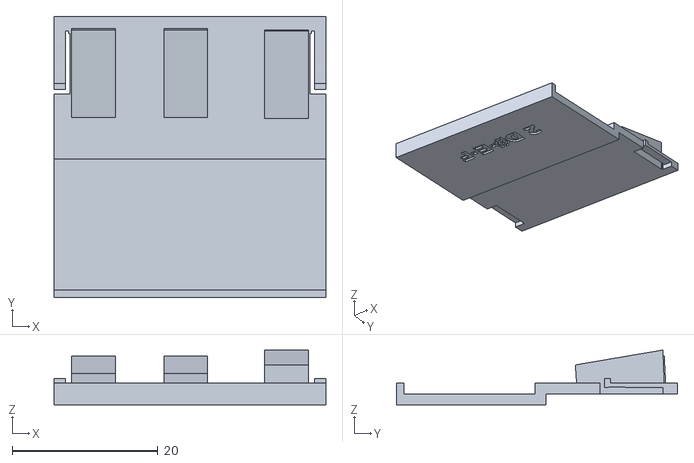
[picture p232: CAD file, 2026-10-02]
hardware/mechanical/cad/stl/print/04b_패드바_PORON5T용/패드바_칸2_PORON5T용__7개.stl
37.3 x 38.5 x 7.53
