WongyuKoh/Toccata/hardware/mechanical/cad/stl/print/05_본체출력물/뚜껑이음레일기둥_1__1개.stl

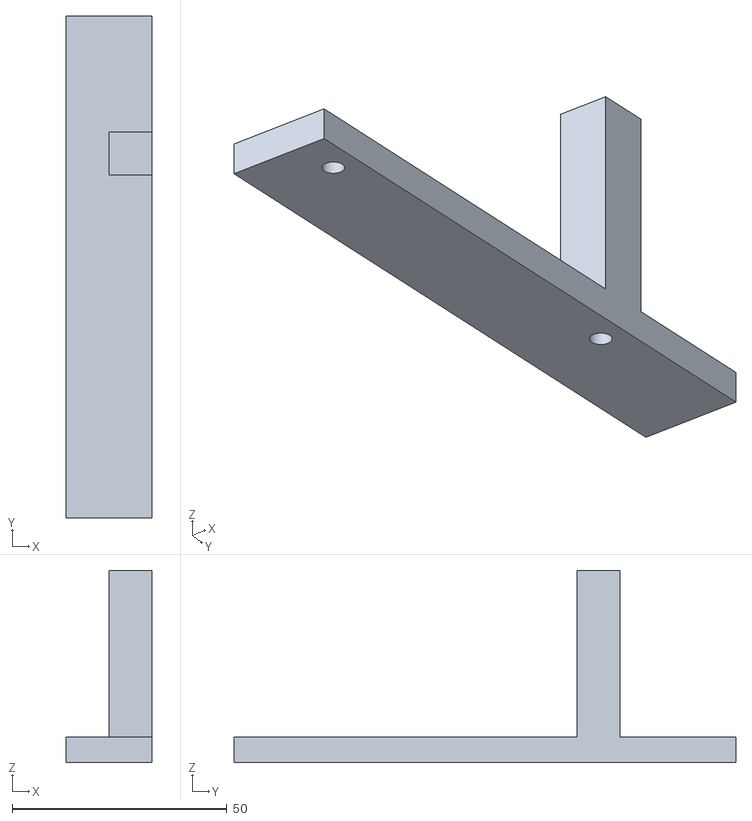
[picture p233: CAD file, 2026-10-02]
hardware/mechanical/cad/stl/print/05_본체출력물/뚜껑이음레일기둥_1__1개.stl
20.0 x 117.0 x 44.8
