WongyuKoh/Toccata/hardware/mechanical/key-action-v4/printables/stage0/stl/C04a.stl

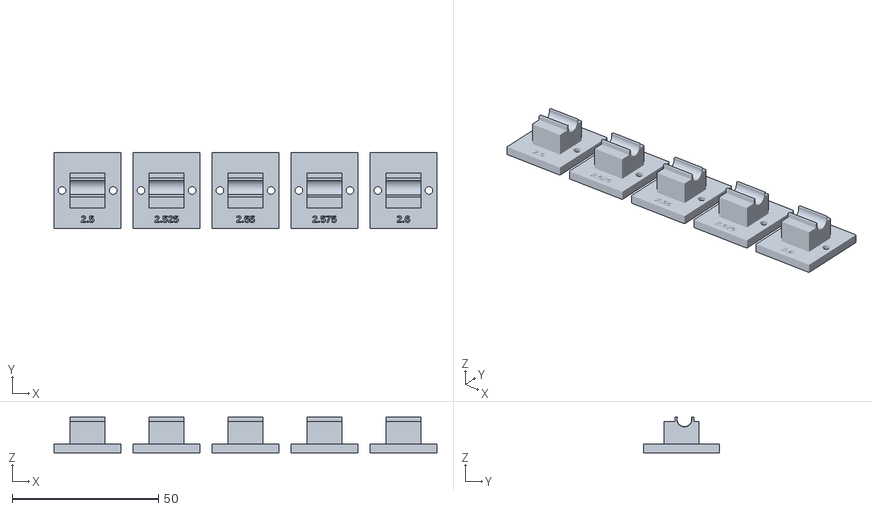
[picture p234: CAD file, 2026-10-02]
hardware/mechanical/key-action-v4/printables/stage0/stl/C04a.stl
130.8 x 26.0 x 12.2
