WongyuKoh/Toccata/hardware/mechanical/cad/stl/print/02_레버캐리어/레버캐리어_B__7개.stl

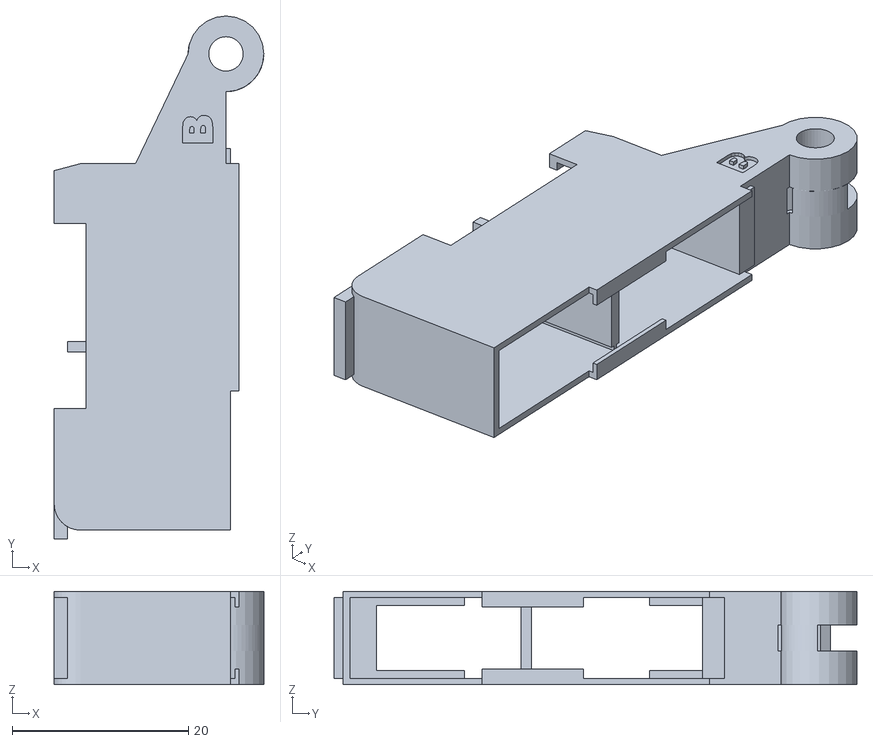
[picture p235: CAD file, 2026-10-02]
hardware/mechanical/cad/stl/print/02_레버캐리어/레버캐리어_B__7개.stl
23.8 x 59.3 x 10.6
