WongyuKoh/Toccata/hardware/mechanical/cad/stl/print/04_센서바·패드바·가림판·마개/패드바_칸3__7개.stl

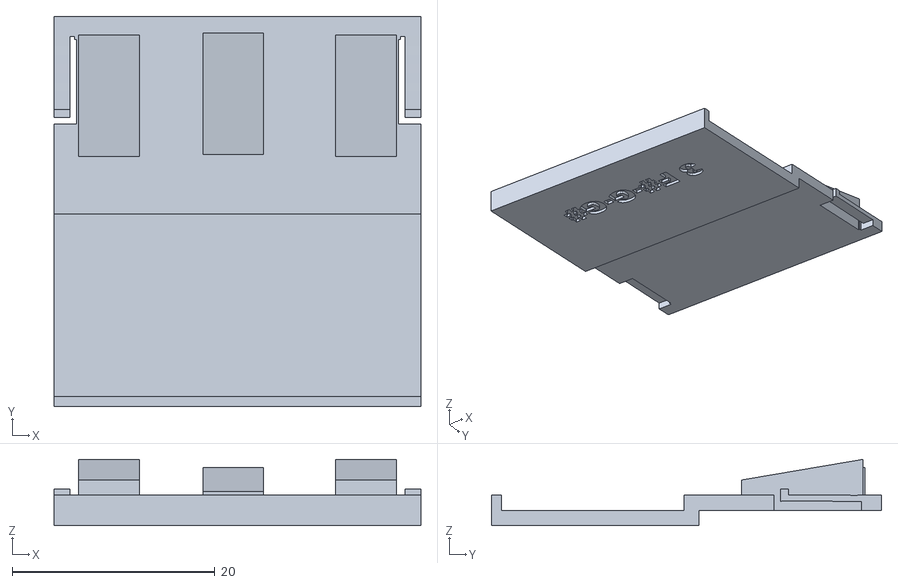
[picture p236: CAD file, 2026-10-02]
hardware/mechanical/cad/stl/print/04_센서바·패드바·가림판·마개/패드바_칸3__7개.stl
36.2 x 38.5 x 6.54
