WongyuKoh/Toccata/hardware/mechanical/cad/stl/print/05_본체출력물/스피커통로틀__2개.stl

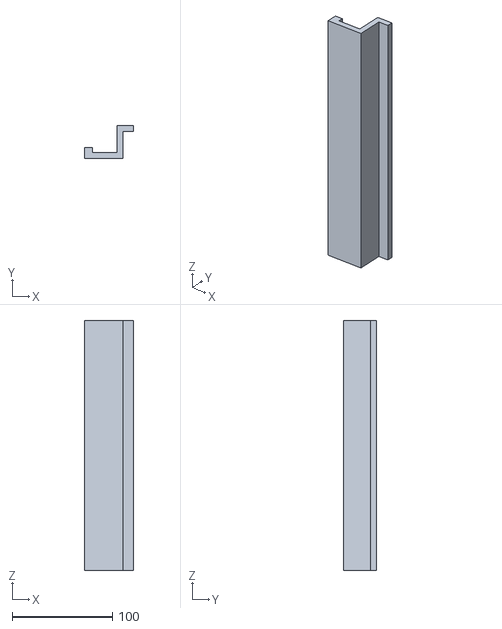
[picture p237: CAD file, 2026-10-02]
hardware/mechanical/cad/stl/print/05_본체출력물/스피커통로틀__2개.stl
48.9 x 33.0 x 250.0
