WongyuKoh/Toccata/hardware/mechanical/key-action-v4/printables/stage0/stl/C16a.stl

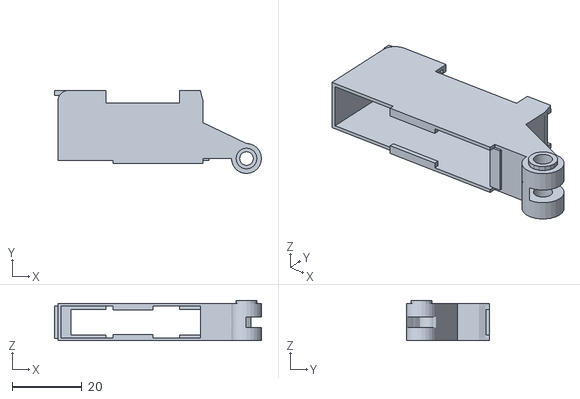
[picture p238: CAD file, 2026-10-02]
hardware/mechanical/key-action-v4/printables/stage0/stl/C16a.stl
59.3 x 23.8 x 11.6
