WongyuKoh/Toccata/hardware/mechanical/cad/stl/print/05_본체출력물/스피커그릴_경사__2개.stl

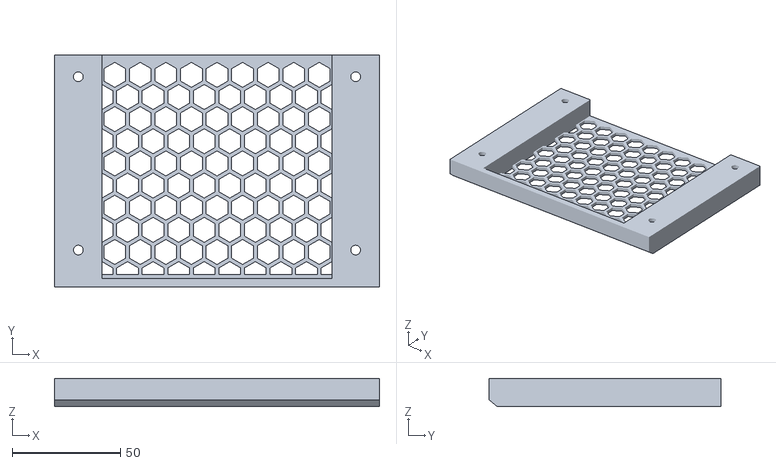
[picture p239: CAD file, 2026-10-02]
hardware/mechanical/cad/stl/print/05_본체출력물/스피커그릴_경사__2개.stl
150.0 x 107.0 x 13.0
