WongyuKoh/Toccata/hardware/mechanical/key-action-v4/printables/stage0/stl/C17a.stl

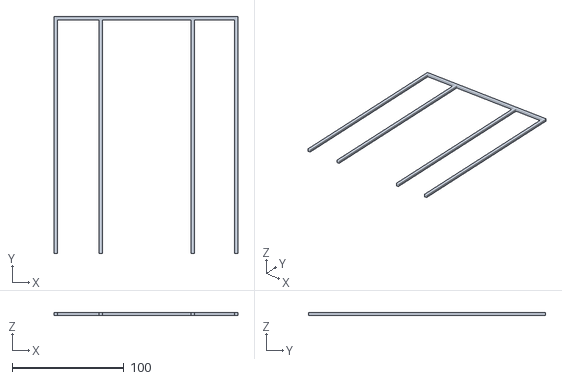
[picture p240: CAD file, 2026-10-02]
hardware/mechanical/key-action-v4/printables/stage0/stl/C17a.stl
164.5 x 212.0 x 3.00
