WongyuKoh/Toccata/hardware/mechanical/cad/stl/print/04_센서바·패드바·가림판·마개/센서바__7개.stl

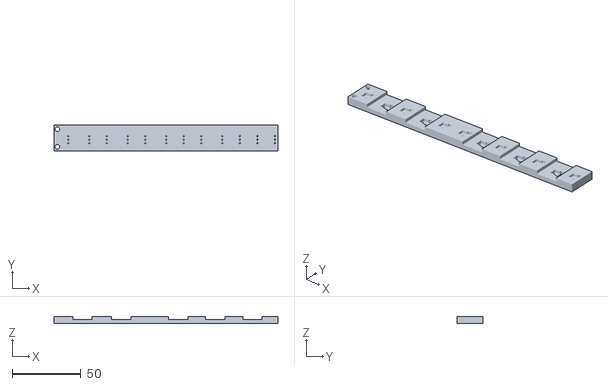
[picture p241: CAD file, 2026-10-02]
hardware/mechanical/cad/stl/print/04_센서바·패드바·가림판·마개/센서바__7개.stl
162.4 x 18.5 x 5.00
