WongyuKoh/Toccata/hardware/mechanical/cad/stl/print/05_본체출력물/보드받침기둥_PED_Ø6_5mm__2개.stl

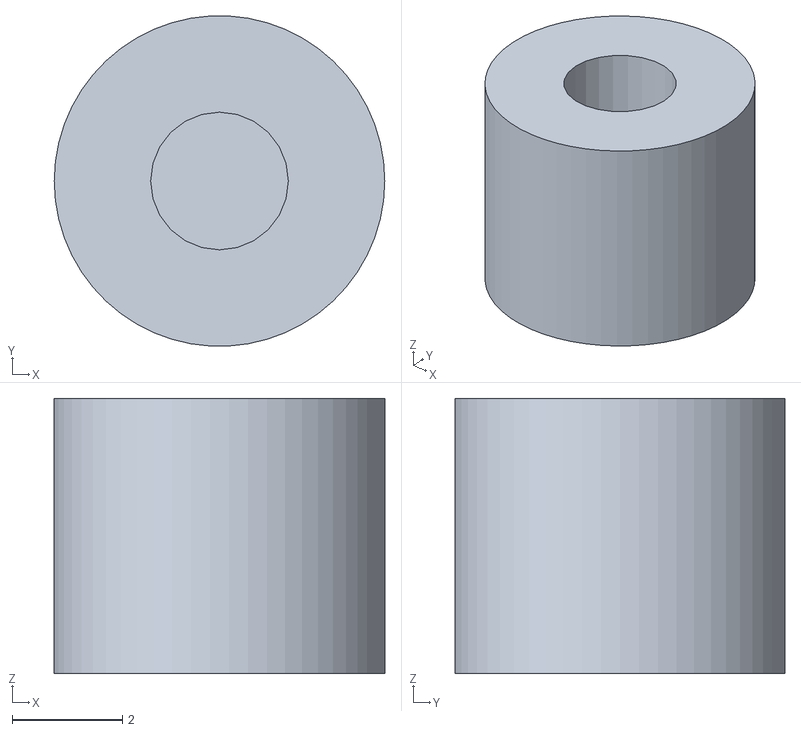
[picture p242: CAD file, 2026-10-02]
hardware/mechanical/cad/stl/print/05_본체출력물/보드받침기둥_PED_Ø6_5mm__2개.stl
6.00 x 5.99 x 5.00
