WongyuKoh/Toccata/hardware/mechanical/key-action-v4/printables/stage0/stl/C11a.stl

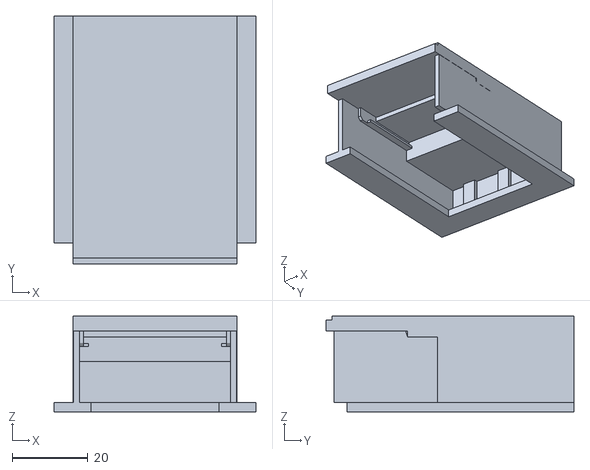
[picture p243: CAD file, 2026-10-02]
hardware/mechanical/key-action-v4/printables/stage0/stl/C11a.stl
53.5 x 65.5 x 25.4
