WongyuKoh/Toccata/hardware/mechanical/before/cad/stl/v1.5-multipart/black.stl

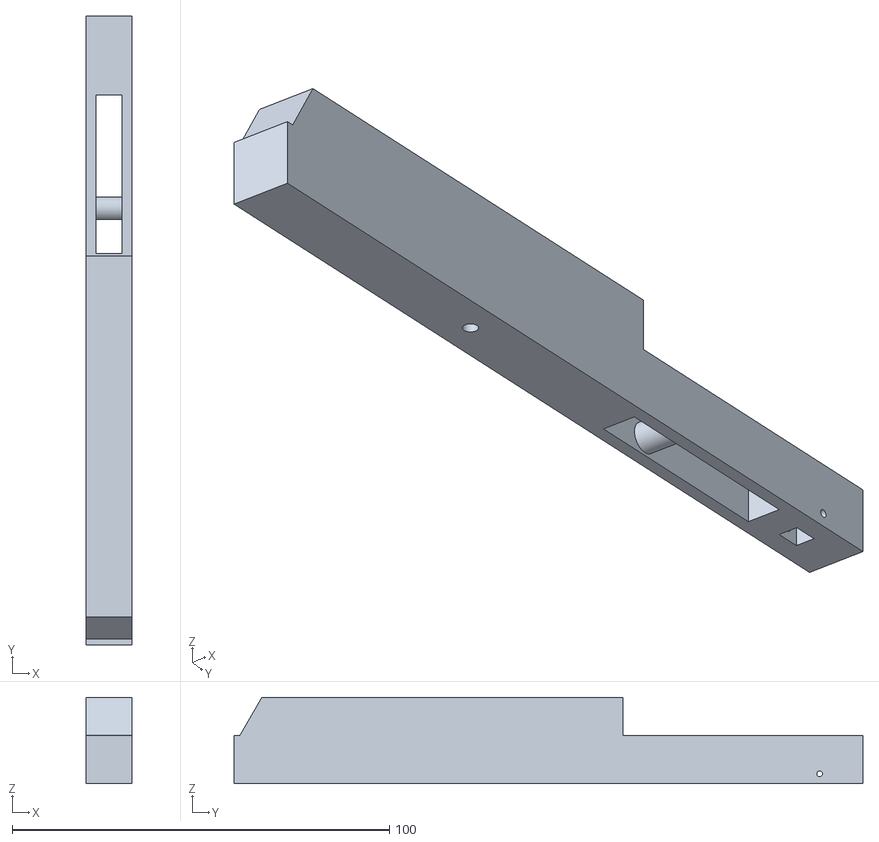
[picture p244: CAD file, 2026-10-02]
hardware/mechanical/before/cad/stl/v1.5-multipart/black.stl
12.1 x 166.8 x 22.9
