WongyuKoh/Toccata/hardware/mechanical/cad/stl/print/04_센서바·패드바·가림판·마개/가림판띠__7개.stl

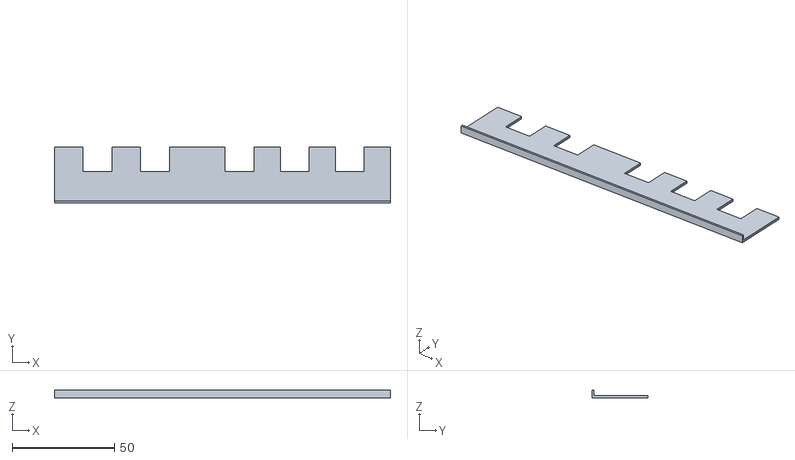
[picture p245: CAD file, 2026-10-02]
hardware/mechanical/cad/stl/print/04_센서바·패드바·가림판·마개/가림판띠__7개.stl
164.1 x 27.4 x 3.70
