WongyuKoh/Toccata/hardware/mechanical/cad/stl/print/05_본체출력물/CU화면뚜껑_터치3판__1개.stl

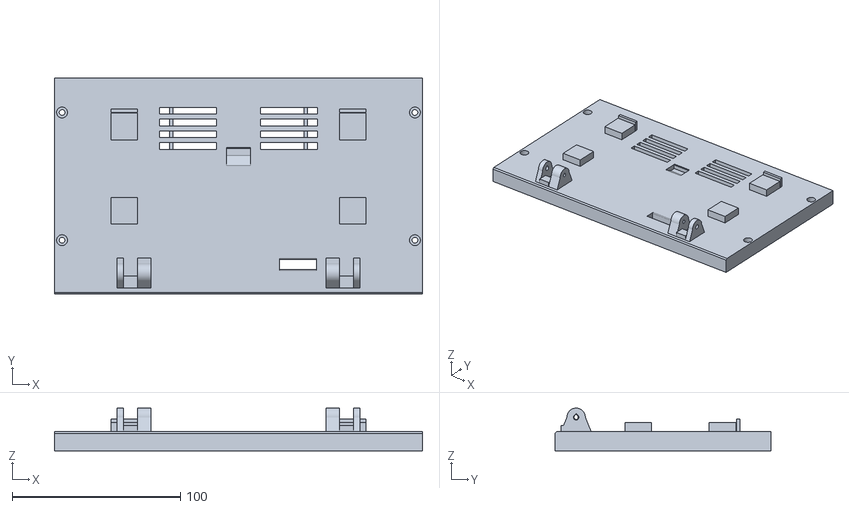
[picture p246: CAD file, 2026-10-02]
hardware/mechanical/cad/stl/print/05_본체출력물/CU화면뚜껑_터치3판__1개.stl
219.0 x 128.5 x 25.5
