WongyuKoh/Toccata/hardware/mechanical/key-action-v4/printables/stage0/stl/C03b.stl

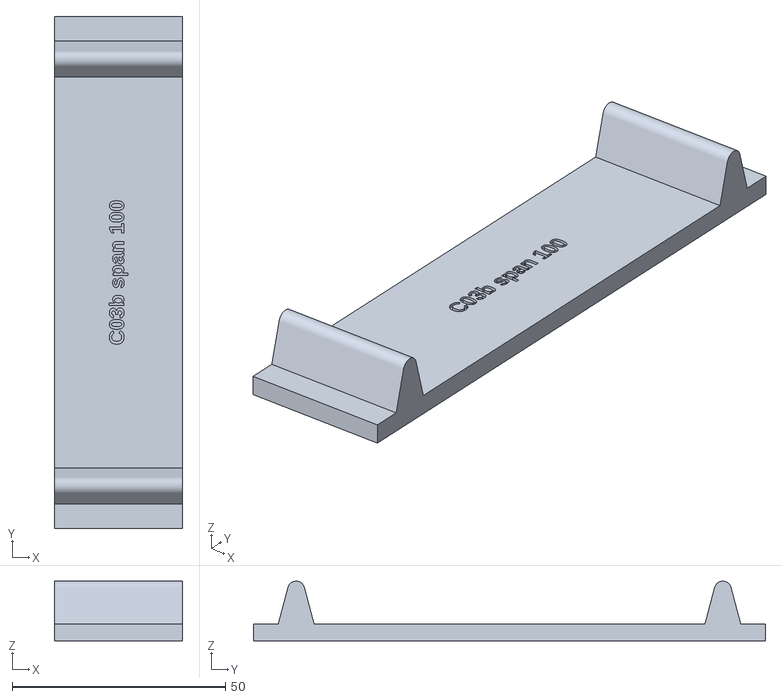
[picture p247: CAD file, 2026-10-02]
hardware/mechanical/key-action-v4/printables/stage0/stl/C03b.stl
30.0 x 120.0 x 14.0
