WongyuKoh/Toccata/hardware/mechanical/before/cad/stl/v1.5-multipart/coupons.stl

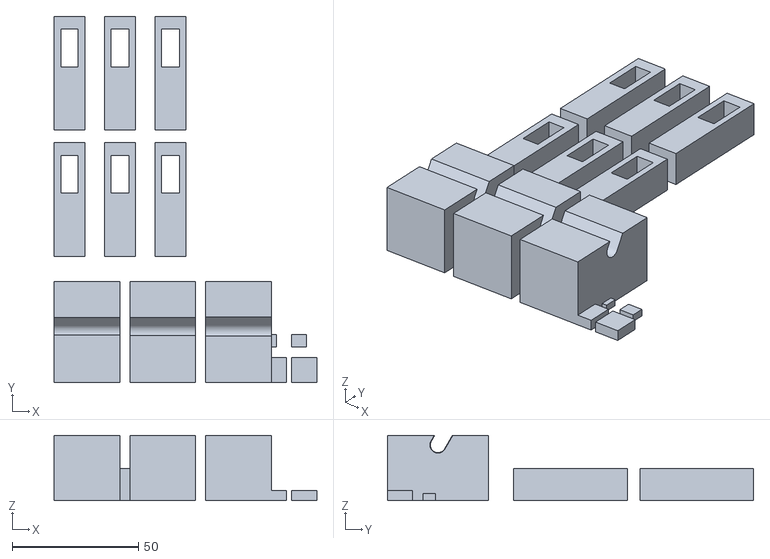
[picture p248: CAD file, 2026-10-02]
hardware/mechanical/before/cad/stl/v1.5-multipart/coupons.stl
104.0 x 145.0 x 25.8
