WongyuKoh/Toccata/hardware/mechanical/cad/stl/print/05_본체출력물/보드받침기둥_나사_Ø7_5mm__6개.stl

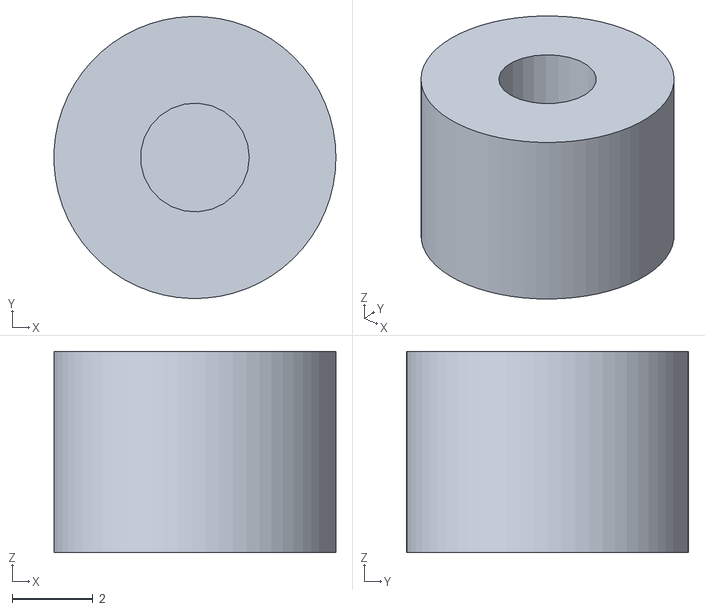
[picture p250: CAD file, 2026-10-02]
hardware/mechanical/cad/stl/print/05_본체출력물/보드받침기둥_나사_Ø7_5mm__6개.stl
7.00 x 7.00 x 5.00
