WongyuKoh/Toccata/hardware/mechanical/key-action-v4/printables/stage0/stl/C15a.stl

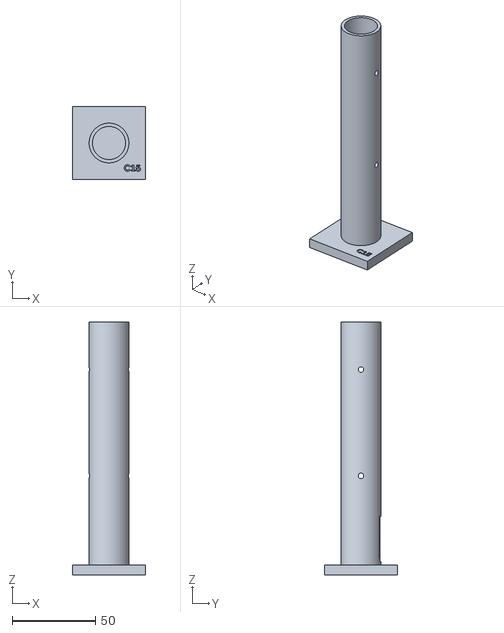
[picture p251: CAD file, 2026-10-02]
hardware/mechanical/key-action-v4/printables/stage0/stl/C15a.stl
44.0 x 44.0 x 151.8
