WongyuKoh/Toccata/hardware/mechanical/cad/stl/print/01_건반/백건_D__7개.stl

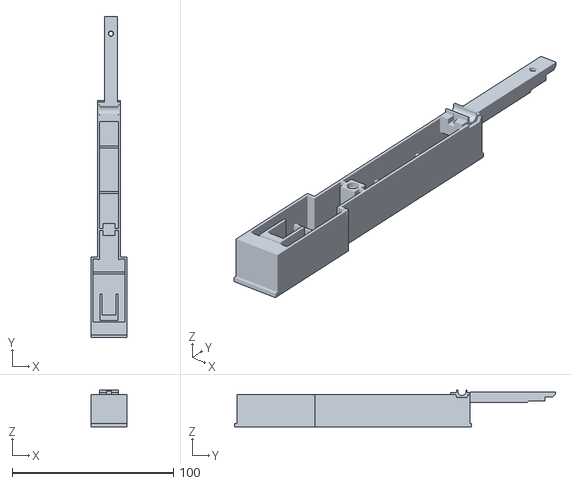
[picture p252: CAD file, 2026-10-02]
hardware/mechanical/cad/stl/print/01_건반/백건_D__7개.stl
22.0 x 199.0 x 22.8
