WongyuKoh/Toccata/hardware/mechanical/cad/stl/print/05_본체출력물/핀소켓_둥근__1개.stl

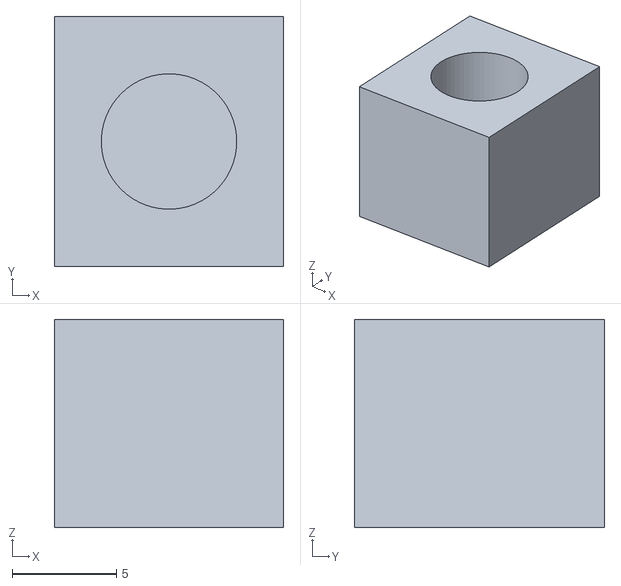
[picture p254: CAD file, 2026-10-02]
hardware/mechanical/cad/stl/print/05_본체출력물/핀소켓_둥근__1개.stl
11.0 x 12.0 x 10.0
