WongyuKoh/Toccata/hardware/mechanical/key-action-v4/printables/stage0/stl/C02b.stl

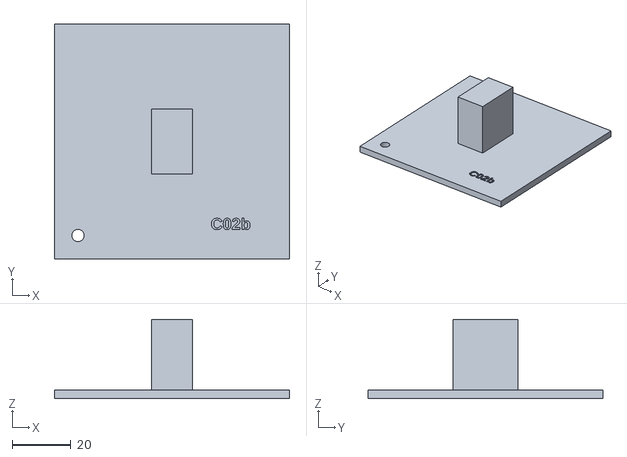
[picture p255: CAD file, 2026-10-02]
hardware/mechanical/key-action-v4/printables/stage0/stl/C02b.stl
80.0 x 80.0 x 27.0
