WongyuKoh/Toccata/hardware/mechanical/before/cad/stl/v1.5-multipart/bed12.stl

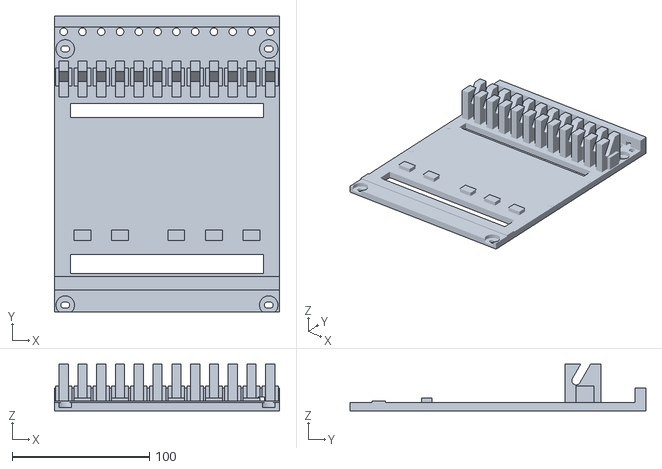
[picture p256: CAD file, 2026-10-02]
hardware/mechanical/before/cad/stl/v1.5-multipart/bed12.stl
164.5 x 216.0 x 34.0
