WongyuKoh/Toccata/hardware/mechanical/cad/stl/print/01_건반/흑건_C#·D#__14개.stl

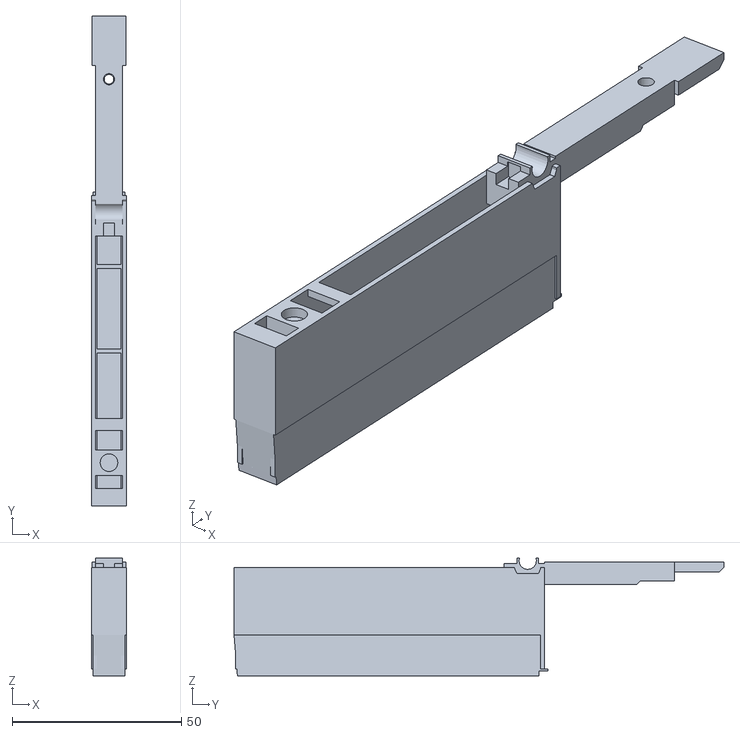
[picture p257: CAD file, 2026-10-02]
hardware/mechanical/cad/stl/print/01_건반/흑건_C#·D#__14개.stl
10.4 x 144.8 x 34.8
