WongyuKoh/Toccata/hardware/mechanical/cad/stl/print/04_센서바·패드바·가림판·마개/가림판띠_왼쪽__1개.stl

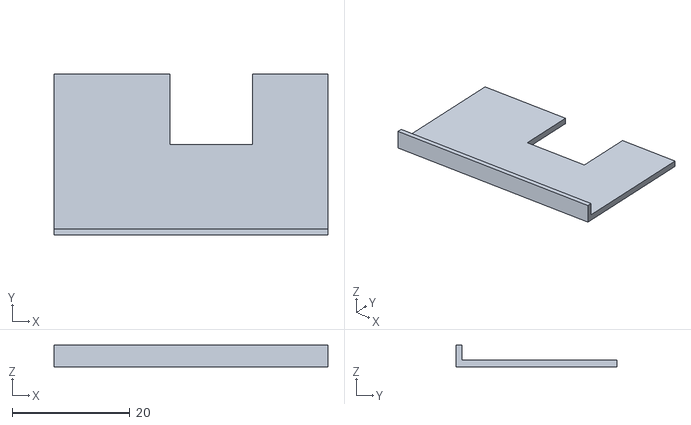
[picture p258: CAD file, 2026-10-02]
hardware/mechanical/cad/stl/print/04_센서바·패드바·가림판·마개/가림판띠_왼쪽__1개.stl
46.6 x 27.4 x 3.70
