WongyuKoh/Toccata/hardware/mechanical/key-action-v4/printables/stage0/stl/C03e.stl

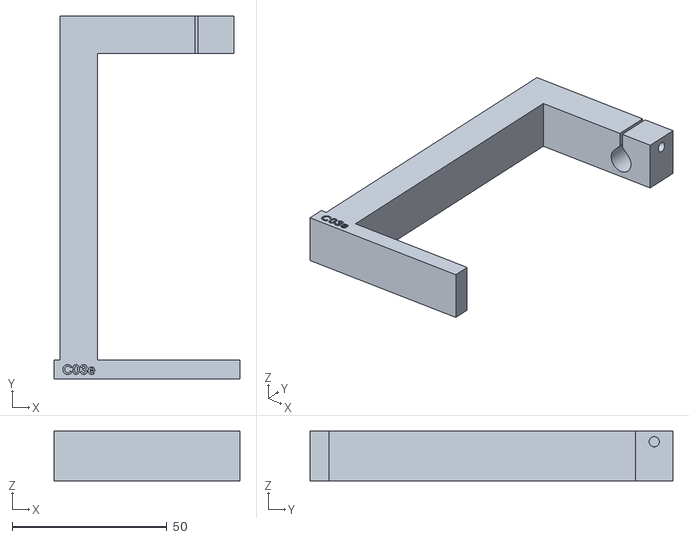
[picture p259: CAD file, 2026-10-02]
hardware/mechanical/key-action-v4/printables/stage0/stl/C03e.stl
60.0 x 117.0 x 16.0
