WongyuKoh/Toccata/hardware/mechanical/cad/stl/print/05_본체출력물/보드받침기둥_Pi_Ø6_6mm__4개.stl

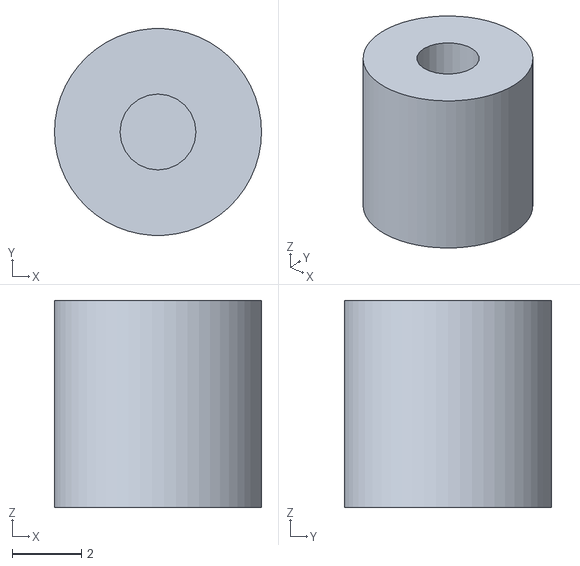
[picture p260: CAD file, 2026-10-02]
hardware/mechanical/cad/stl/print/05_본체출력물/보드받침기둥_Pi_Ø6_6mm__4개.stl
6.00 x 5.99 x 6.00
