WongyuKoh/Toccata/hardware/mechanical/key-action-v4/printables/stage0/stl/C10a.stl

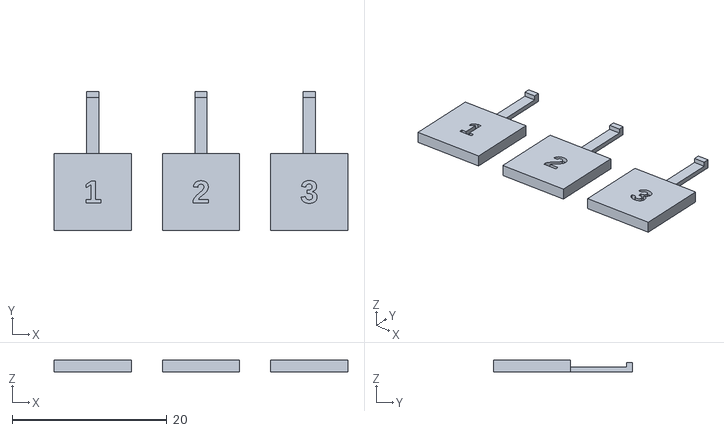
[picture p261: CAD file, 2026-10-02]
hardware/mechanical/key-action-v4/printables/stage0/stl/C10a.stl
38.0 x 18.0 x 1.50
