WongyuKoh/Toccata/hardware/mechanical/key-action-v4/printables/stage0/stl/C05a.stl

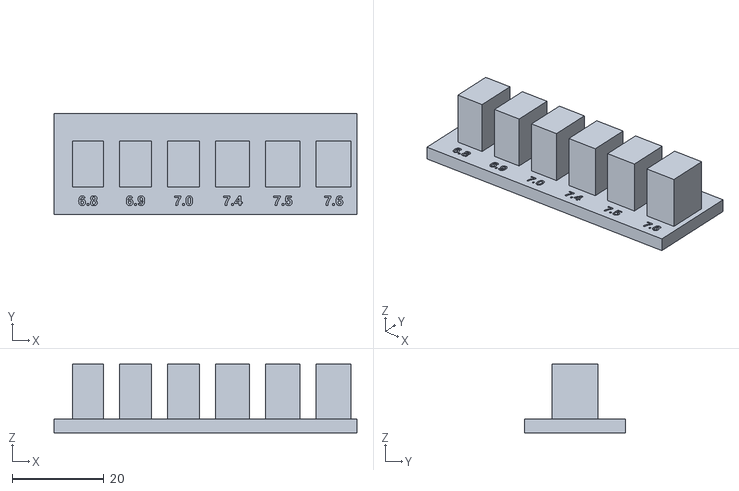
[picture p262: CAD file, 2026-10-02]
hardware/mechanical/key-action-v4/printables/stage0/stl/C05a.stl
66.0 x 22.0 x 15.0
