WongyuKoh/Toccata/hardware/mechanical/cad/stl/print/05_본체출력물/XT30집게_R__1개.stl

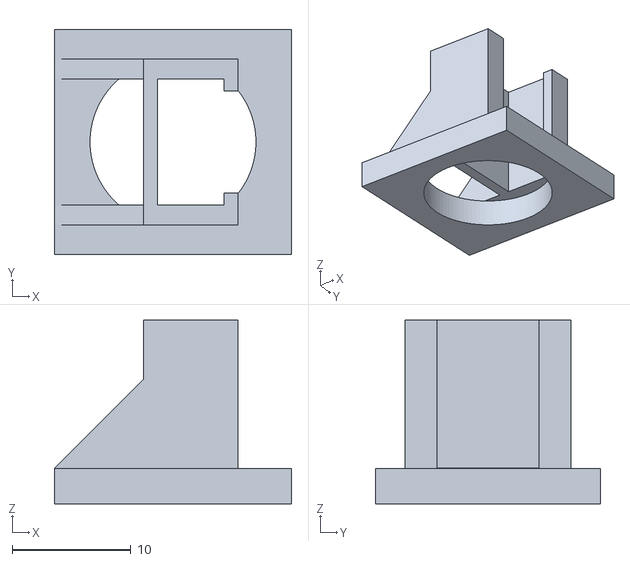
[picture p263: CAD file, 2026-10-02]
hardware/mechanical/cad/stl/print/05_본체출력물/XT30집게_R__1개.stl
20.0 x 19.0 x 15.5
