WongyuKoh/Toccata/hardware/mechanical/key-action-v4/printables/stage0/stl/C10b.stl

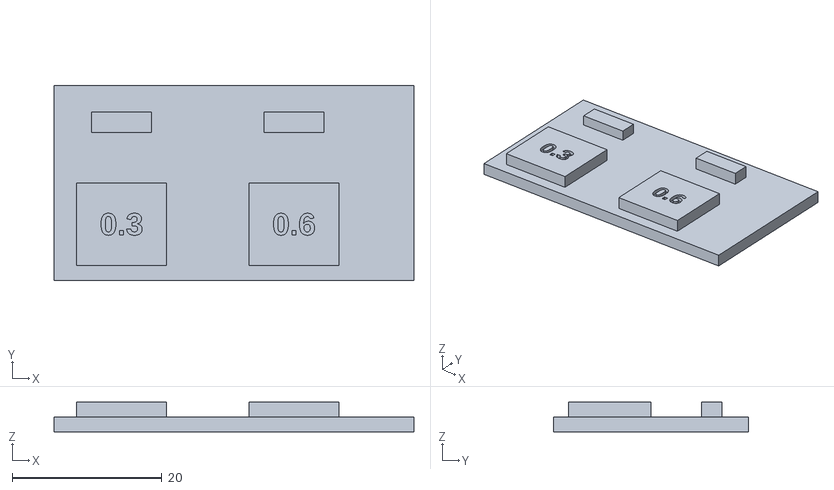
[picture p264: CAD file, 2026-10-02]
hardware/mechanical/key-action-v4/printables/stage0/stl/C10b.stl
48.0 x 26.0 x 4.00
