WongyuKoh/Toccata/hardware/mechanical/cad/stl/print/05_본체출력물/XT30집게_L__1개.stl

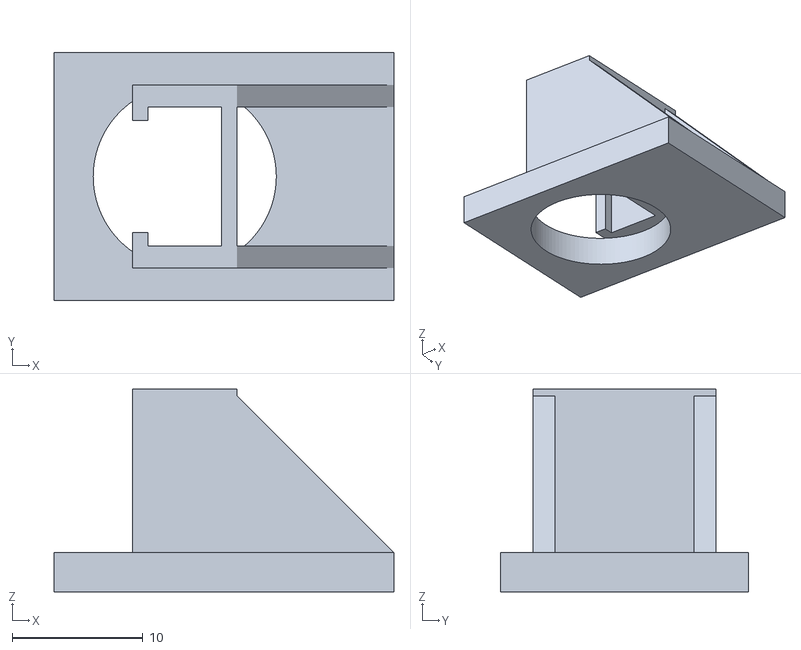
[picture p265: CAD file, 2026-10-02]
hardware/mechanical/cad/stl/print/05_본체출력물/XT30집게_L__1개.stl
26.0 x 19.0 x 15.5
