WongyuKoh/Toccata/hardware/mechanical/key-action-v4/printables/stage0/stl/C09a.stl

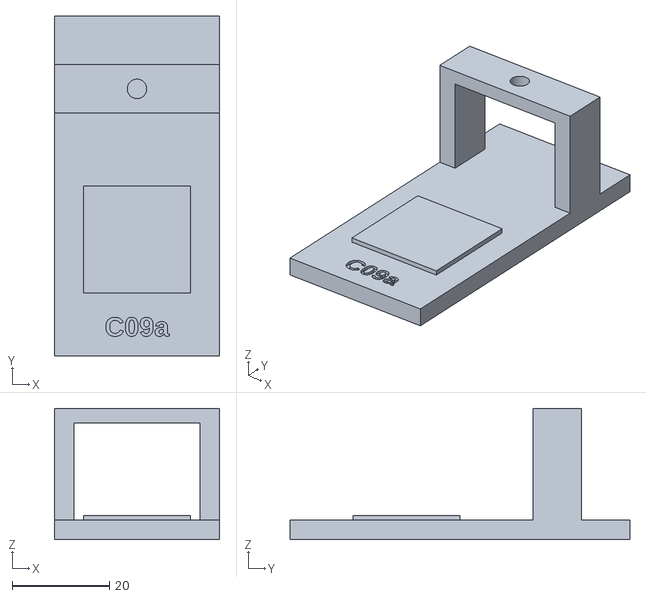
[picture p266: CAD file, 2026-10-02]
hardware/mechanical/key-action-v4/printables/stage0/stl/C09a.stl
34.0 x 70.0 x 27.0
