WongyuKoh/Toccata/hardware/mechanical/key-action-v4/printables/stage0/stl/C09b.stl

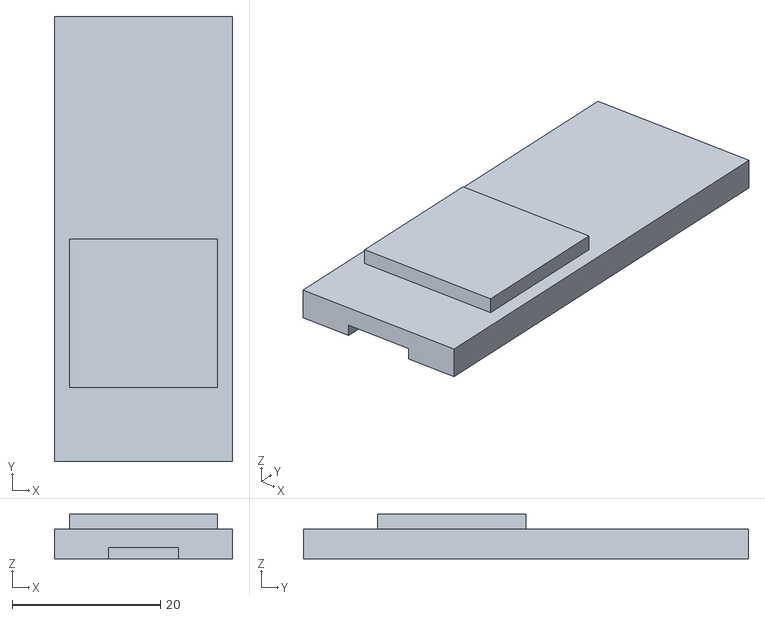
[picture p267: CAD file, 2026-10-02]
hardware/mechanical/key-action-v4/printables/stage0/stl/C09b.stl
24.0 x 60.0 x 6.00
