WongyuKoh/Toccata/hardware/mechanical/cad/stl/print/05_본체출력물/보조배터리받침__1개.stl

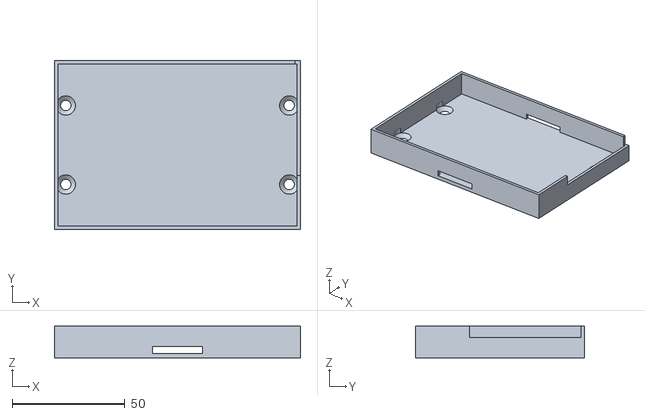
[picture p268: CAD file, 2026-10-02]
hardware/mechanical/cad/stl/print/05_본체출력물/보조배터리받침__1개.stl
109.0 x 75.0 x 14.0
