WongyuKoh/Toccata/hardware/mechanical/key-action-v4/printables/stage0/stl/C03a.stl

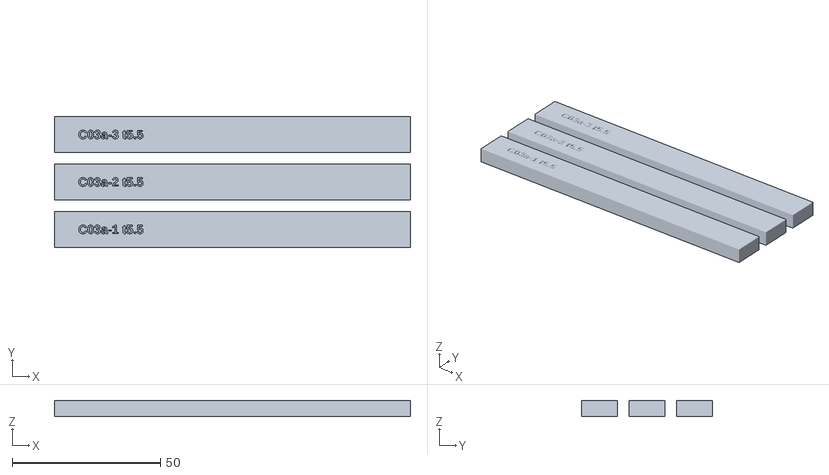
[picture p269: CAD file, 2026-10-02]
hardware/mechanical/key-action-v4/printables/stage0/stl/C03a.stl
120.0 x 44.0 x 5.50
