WongyuKoh/Toccata/hardware/mechanical/cad/stl/print/05_본체출력물/핀소켓_긴구멍__1개.stl

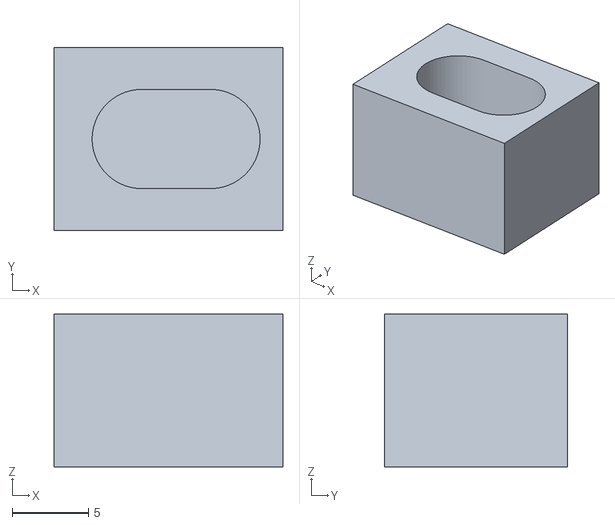
[picture p270: CAD file, 2026-10-02]
hardware/mechanical/cad/stl/print/05_본체출력물/핀소켓_긴구멍__1개.stl
15.0 x 12.0 x 10.0
