WongyuKoh/Toccata/hardware/mechanical/key-action-v4/printables/stage0/stl/C03c.stl

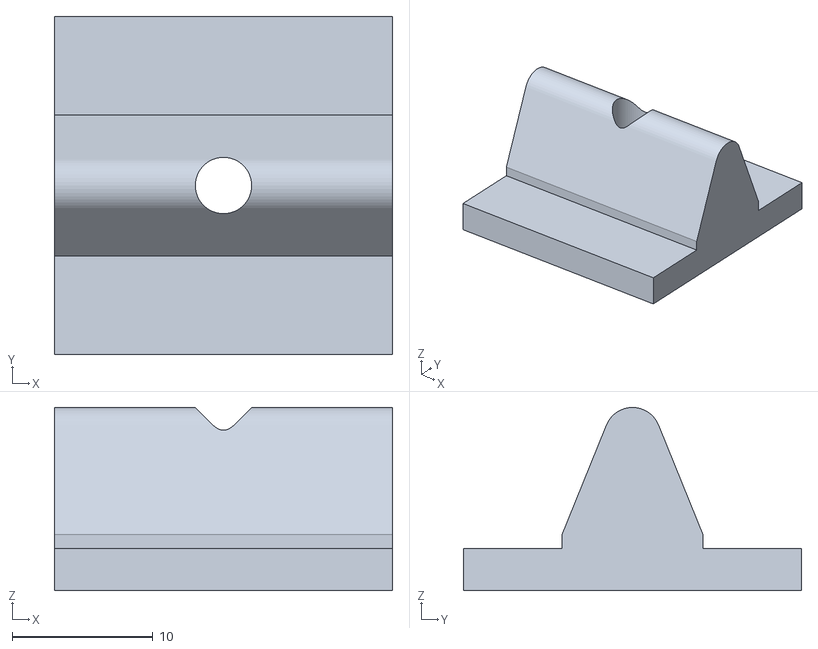
[picture p271: CAD file, 2026-10-02]
hardware/mechanical/key-action-v4/printables/stage0/stl/C03c.stl
24.0 x 24.0 x 13.0
