WongyuKoh/Toccata/hardware/mechanical/cad/stl/print/05_본체출력물/케이블집게__8개.stl

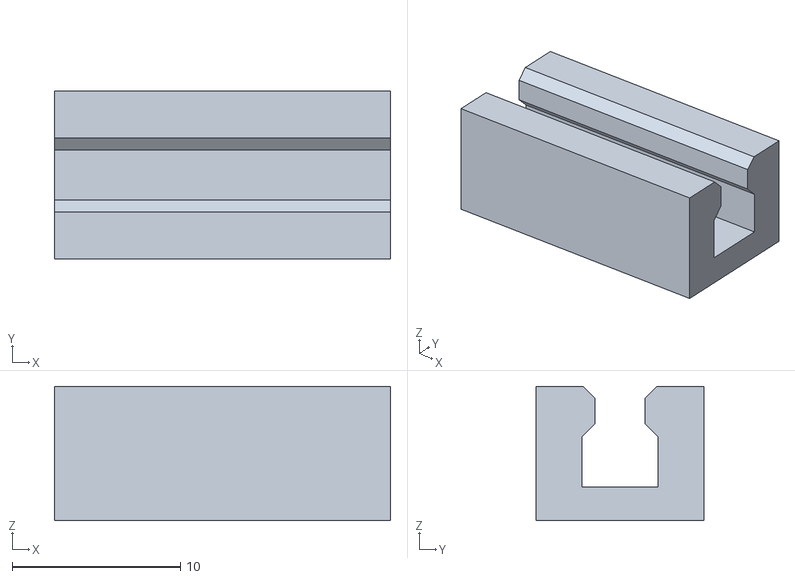
[picture p272: CAD file, 2026-10-02]
hardware/mechanical/cad/stl/print/05_본체출력물/케이블집게__8개.stl
20.0 x 10.0 x 8.00
