WongyuKoh/Toccata/hardware/mechanical/key-action-v4/printables/stage0/stl/C14a.stl

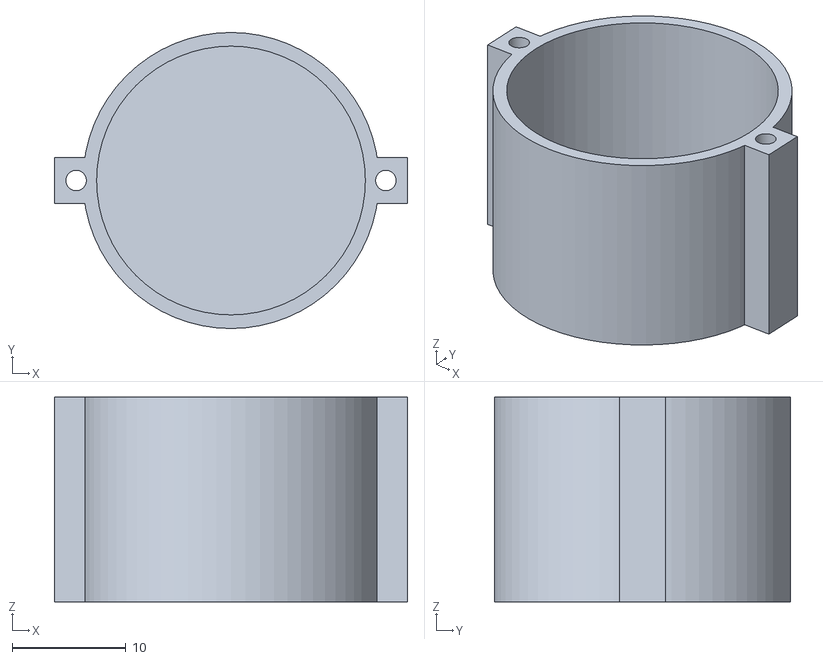
[picture p273: CAD file, 2026-10-02]
hardware/mechanical/key-action-v4/printables/stage0/stl/C14a.stl
31.0 x 26.0 x 18.0
