WongyuKoh/Toccata/hardware/mechanical/cad/stl/print/05_본체출력물/허브선반__1개.stl

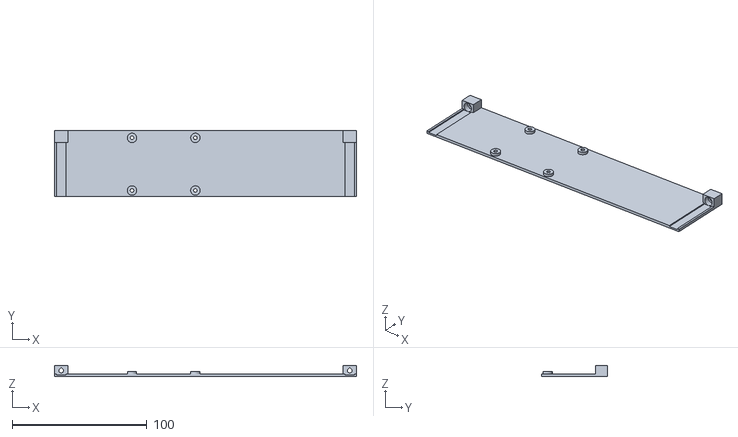
[picture p274: CAD file, 2026-10-02]
hardware/mechanical/cad/stl/print/05_본체출력물/허브선반__1개.stl
224.0 x 49.0 x 8.50
