WongyuKoh/Toccata/hardware/mechanical/key-action-v4/printables/stage0/stl/C04b.stl

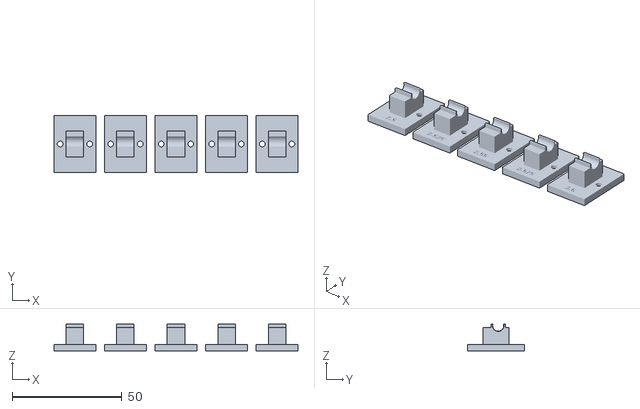
[picture p275: CAD file, 2026-10-02]
hardware/mechanical/key-action-v4/printables/stage0/stl/C04b.stl
111.0 x 26.0 x 12.2
