WongyuKoh/Toccata/hardware/mechanical/key-action-v4/printables/stage0/stl/C01d.stl

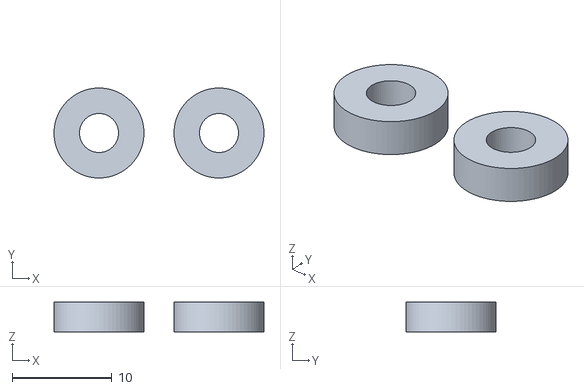
[picture p277: CAD file, 2026-10-02]
hardware/mechanical/key-action-v4/printables/stage0/stl/C01d.stl
21.0 x 9.00 x 3.00
