WongyuKoh/Toccata/hardware/mechanical/key-action-v4/printables/stage0/stl/C07b.stl

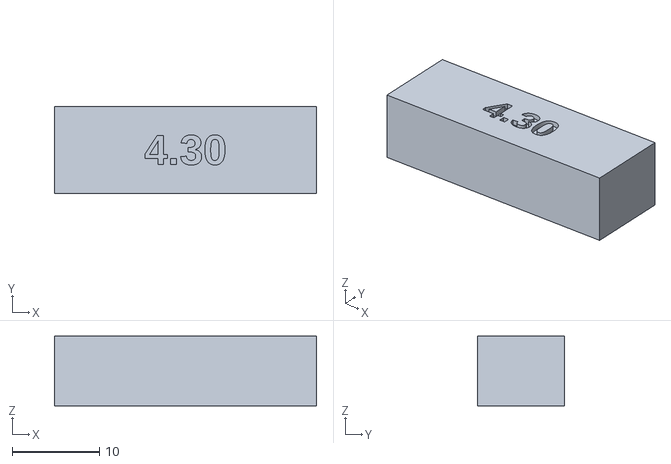
[picture p278: CAD file, 2026-10-02]
hardware/mechanical/key-action-v4/printables/stage0/stl/C07b.stl
30.0 x 10.0 x 8.00
