WongyuKoh/Toccata/hardware/mechanical/key-action-v4/printables/stage0/stl/C10c.stl

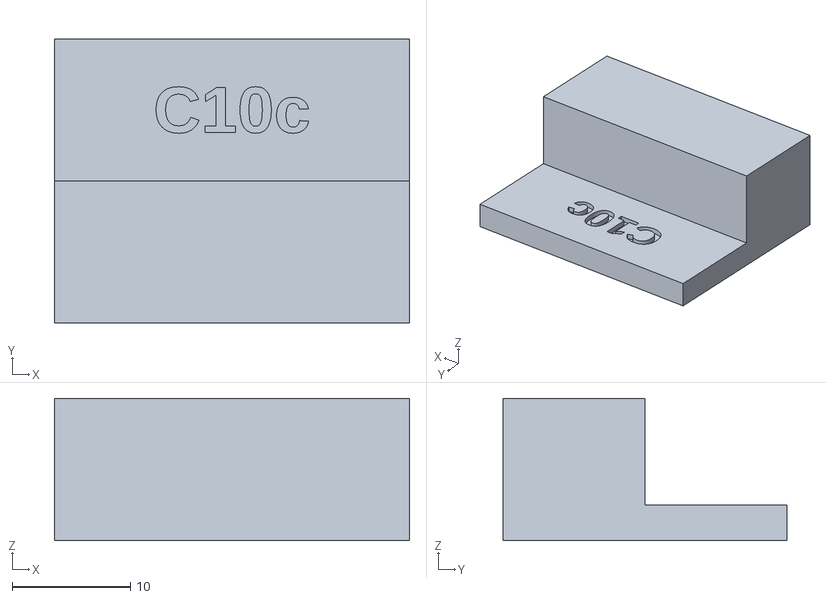
[picture p279: CAD file, 2026-10-02]
hardware/mechanical/key-action-v4/printables/stage0/stl/C10c.stl
30.0 x 24.0 x 12.0
