WongyuKoh/Toccata/hardware/mechanical/key-action-v4/printables/stage0/stl/C16b.stl

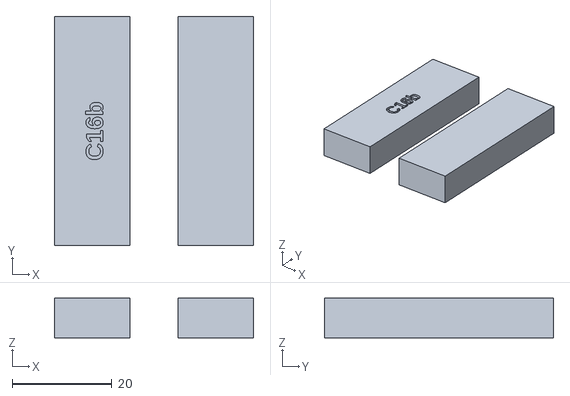
[picture p280: CAD file, 2026-10-02]
hardware/mechanical/key-action-v4/printables/stage0/stl/C16b.stl
40.0 x 46.0 x 8.00
