WongyuKoh/Toccata/hardware/mechanical/key-action-v4/printables/stage0/stl/C13a.stl

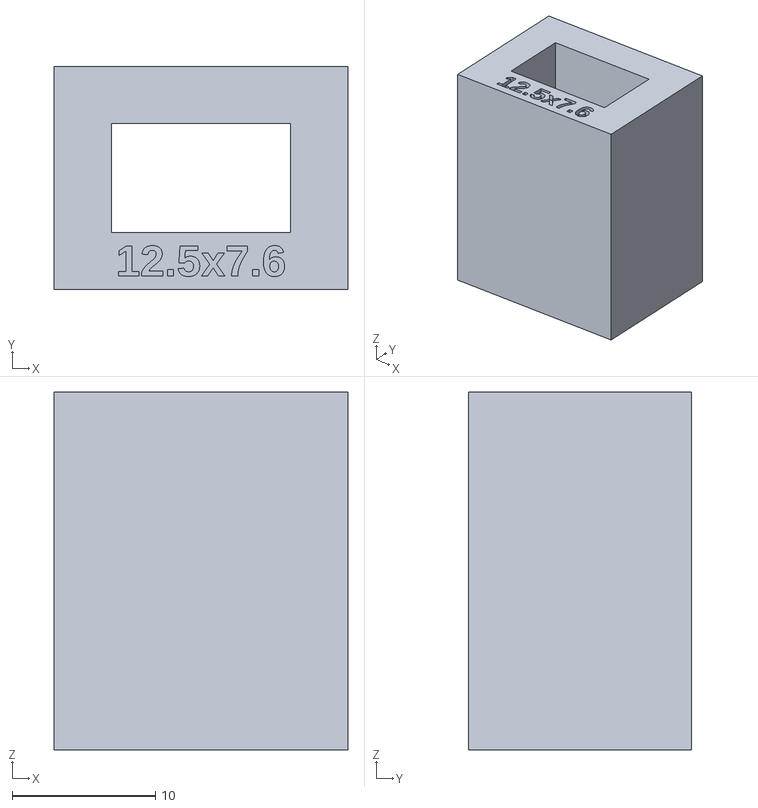
[picture p281: CAD file, 2026-10-02]
hardware/mechanical/key-action-v4/printables/stage0/stl/C13a.stl
20.5 x 15.6 x 25.0
