WongyuKoh/Toccata/hardware/mechanical/key-action-v4/printables/stage0/stl/C06b.stl

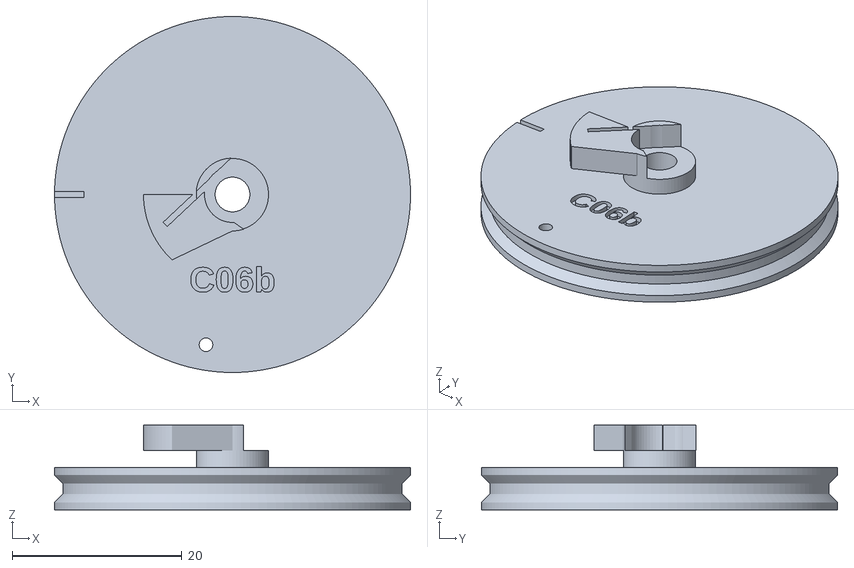
[picture p282: CAD file, 2026-10-02]
hardware/mechanical/key-action-v4/printables/stage0/stl/C06b.stl
42.0 x 42.0 x 10.0
