WongyuKoh/Toccata/hardware/mechanical/key-action-v4/printables/stage0/stl/C03d.stl

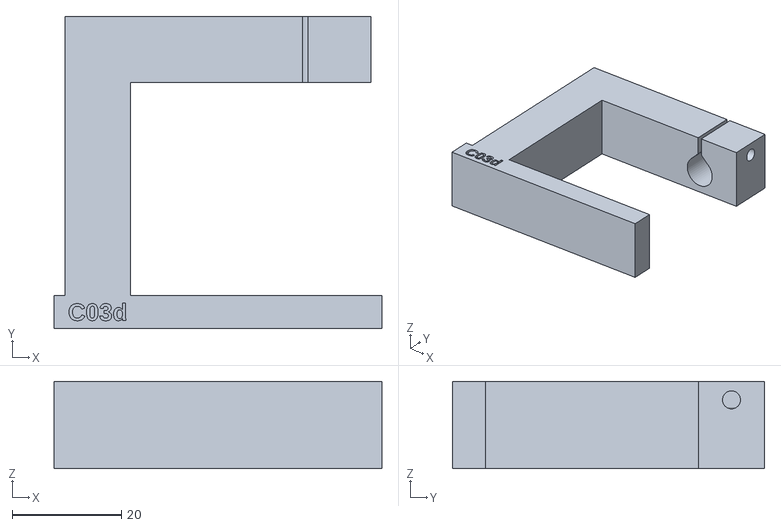
[picture p283: CAD file, 2026-10-02]
hardware/mechanical/key-action-v4/printables/stage0/stl/C03d.stl
60.0 x 57.0 x 16.0
