WongyuKoh/Toccata/hardware/mechanical/key-action-v4/printables/stage0/stl/C01b.stl

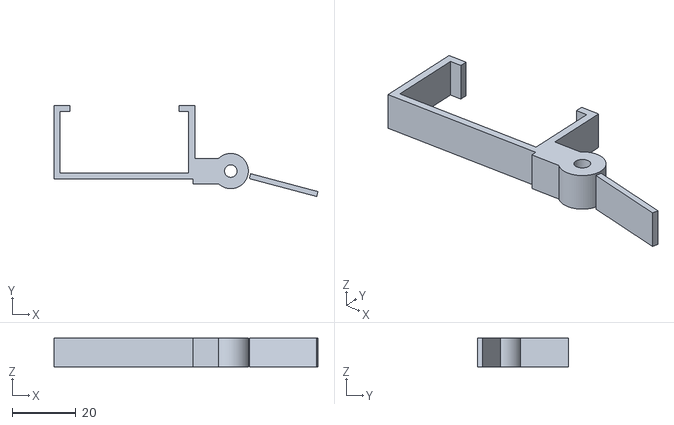
[picture p284: CAD file, 2026-10-02]
hardware/mechanical/key-action-v4/printables/stage0/stl/C01b.stl
82.5 x 28.5 x 9.00
