WongyuKoh/Toccata/hardware/mechanical/key-action-v4/printables/stage0/stl/C07a.stl

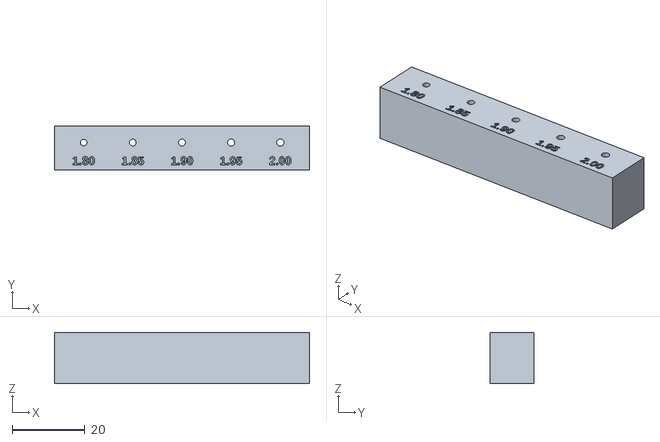
[picture p285: CAD file, 2026-10-02]
hardware/mechanical/key-action-v4/printables/stage0/stl/C07a.stl
70.0 x 12.2 x 14.0
