WongyuKoh/Toccata/hardware/mechanical/key-action-v4/printables/stage0/stl/C01c.stl

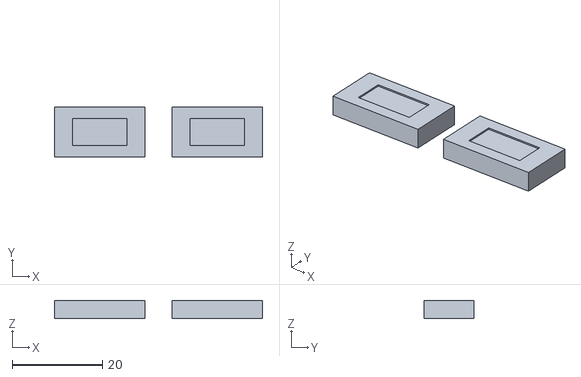
[picture p286: CAD file, 2026-10-02]
hardware/mechanical/key-action-v4/printables/stage0/stl/C01c.stl
46.0 x 11.0 x 4.00
