WongyuKoh/Toccata/hardware/mechanical/key-action-v4/printables/stage0/stl/C01a.stl

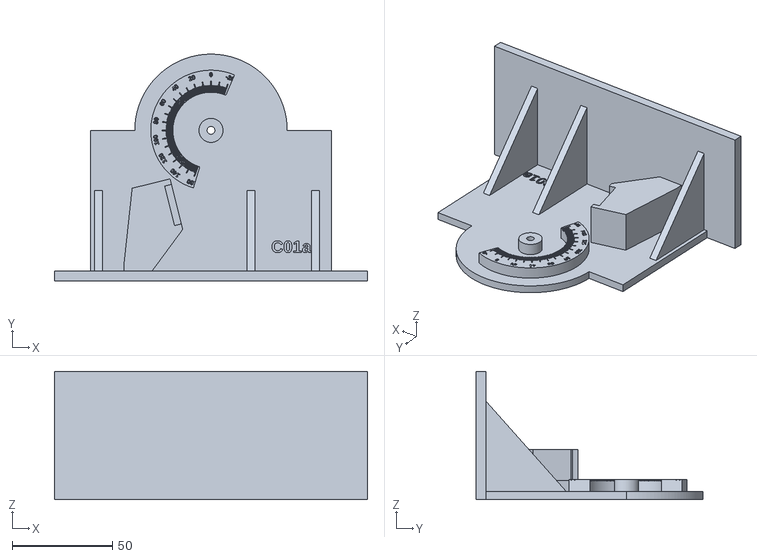
[picture p287: CAD file, 2026-10-02]
hardware/mechanical/key-action-v4/printables/stage0/stl/C01a.stl
156.0 x 113.0 x 64.0
