WongyuKoh/Toccata/hardware/mechanical/key-action-v4/printables/stage0/stl/C05b.stl

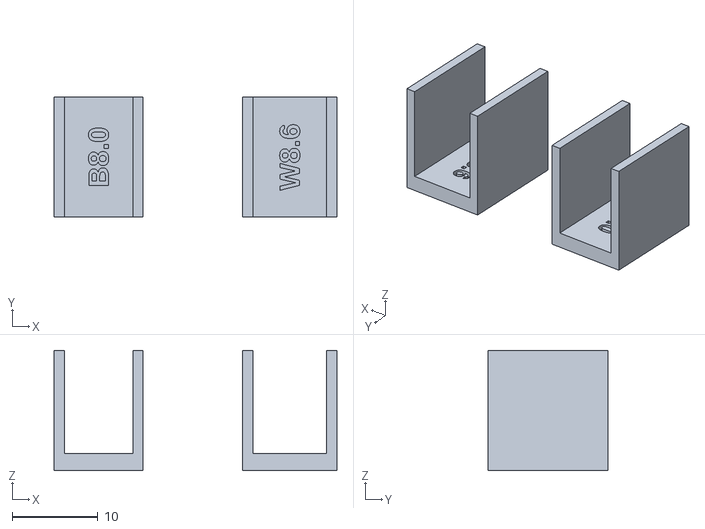
[picture p288: CAD file, 2026-10-02]
hardware/mechanical/key-action-v4/printables/stage0/stl/C05b.stl
33.0 x 14.0 x 14.0
