WongyuKoh/Toccata/hardware/mechanical/key-action-v4/printables/stage0/scad/C04a.scad

// Toccata stage-0 C04a - 스냅 노치 반지름 쿠폰 (백건 블록 폭, R2.50~2.60, 5개) (generated by make_stage0.py; print orientation, z = build direction)
$fn = 64;
difference(){
union(){
translate([-5.5000,-13.0000,0.0000]) cube([22.9620,26.0000,3.0000]);
translate([0.0000,0,0]) rotate([90,0,90]) linear_extrude(height=11.9620) polygon([[-6.0000,10.7000],[-2.1848,10.7000],[-2.1848,12.2500],[-1.3848,12.2500],[-1.4938,11.6755],[-1.4664,11.0914],[-1.3040,10.5296],[-1.0156,10.0210],[-0.6169,9.5932],[-0.1297,9.2698],[0.4193,9.0684],[1.0000,9.0000],[1.5807,9.0684],[2.1297,9.2698],[2.6169,9.5932],[3.0156,10.0210],[3.3040,10.5296],[3.4664,11.0914],[3.4938,11.6755],[3.3848,12.2500],[4.1848,12.2500],[4.1848,10.7000],[6.0000,10.7000],[6.0000,3.0000],[-6.0000,3.0000]]);
}
translate([-2.7500,0.0000,-1.0000]) cylinder(h=6.0000, d=2.6000, $fn=64);
translate([14.7120,0.0000,-1.0000]) cylinder(h=6.0000, d=2.6000, $fn=64);
translate([5.9810,-9.8000,2.4000]) rotate([0,0,0.00]) linear_extrude(height=0.8000) text("2.5", size=2.400, font="Liberation Sans:style=Bold", halign="center", valign="center");
}
difference(){
union(){
translate([21.4620,-13.0000,0.0000]) cube([22.9620,26.0000,3.0000]);
translate([26.9620,0,0]) rotate([90,0,90]) linear_extrude(height=11.9620) polygon([[-6.0000,10.7000],[-2.2110,10.7000],[-2.2110,12.2500],[-1.4110,12.2500],[-1.5192,11.6704],[-1.4901,11.0815],[-1.3251,10.5154],[-1.0334,10.0030],[-0.6308,9.5723],[-0.1392,9.2466],[0.4144,9.0438],[1.0000,8.9750],[1.5856,9.0438],[2.1392,9.2466],[2.6308,9.5723],[3.0334,10.0030],[3.3251,10.5154],[3.4901,11.0815],[3.5192,11.6704],[3.4110,12.2500],[4.2110,12.2500],[4.2110,10.7000],[6.0000,10.7000],[6.0000,3.0000],[-6.0000,3.0000]]);
}
translate([24.2120,0.0000,-1.0000]) cylinder(h=6.0000, d=2.6000, $fn=64);
translate([41.6740,0.0000,-1.0000]) cylinder(h=6.0000, d=2.6000, $fn=64);
translate([32.9430,-9.8000,2.4000]) rotate([0,0,0.00]) linear_extrude(height=0.8000) text("2.525", size=2.400, font="Liberation Sans:style=Bold", halign="center", valign="center");
}
difference(){
union(){
translate([48.4240,-13.0000,0.0000]) cube([22.9620,26.0000,3.0000]);
translate([53.9240,0,0]) rotate([90,0,90]) linear_extrude(height=11.9620) polygon([[-6.0000,10.7000],[-2.2372,10.7000],[-2.2372,12.2500],[-1.4372,12.2500],[-1.5446,11.6653],[-1.5138,11.0716],[-1.3462,10.5012],[-1.0512,9.9851],[-0.6447,9.5513],[-0.1488,9.2234],[0.4096,9.0193],[1.0000,8.9500],[1.5904,9.0193],[2.1488,9.2234],[2.6447,9.5513],[3.0512,9.9851],[3.3462,10.5012],[3.5138,11.0716],[3.5446,11.6653],[3.4372,12.2500],[4.2372,12.2500],[4.2372,10.7000],[6.0000,10.7000],[6.0000,3.0000],[-6.0000,3.0000]]);
}
translate([51.1740,0.0000,-1.0000]) cylinder(h=6.0000, d=2.6000, $fn=64);
translate([68.6360,0.0000,-1.0000]) cylinder(h=6.0000, d=2.6000, $fn=64);
translate([59.9050,-9.8000,2.4000]) rotate([0,0,0.00]) linear_extrude(height=0.8000) text("2.55", size=2.400, font="Liberation Sans:style=Bold", halign="center", valign="center");
}
difference(){
union(){
translate([75.3860,-13.0000,0.0000]) cube([22.9620,26.0000,3.0000]);
translate([80.8860,0,0]) rotate([90,0,90]) linear_extrude(height=11.9620) polygon([[-6.0000,10.7000],[-2.2634,10.7000],[-2.2634,12.2500],[-1.4634,12.2500],[-1.5700,11.6602],[-1.5374,11.0617],[-1.3674,10.4870],[-1.0690,9.9671],[-0.6586,9.5303],[-0.1583,9.2002],[0.4047,8.9948],[1.0000,8.9250],[1.5953,8.9948],[2.1583,9.2002],[2.6586,9.5303],[3.0690,9.9671],[3.3674,10.4870],[3.5374,11.0617],[3.5700,11.6602],[3.4634,12.2500],[4.2634,12.2500],[4.2634,10.7000],[6.0000,10.7000],[6.0000,3.0000],[-6.0000,3.0000]]);
}
translate([78.1360,0.0000,-1.0000]) cylinder(h=6.0000, d=2.6000, $fn=64);
translate([95.5980,0.0000,-1.0000]) cylinder(h=6.0000, d=2.6000, $fn=64);
translate([86.8670,-9.8000,2.4000]) rotate([0,0,0.00]) linear_extrude(height=0.8000) text("2.575", size=2.400, font="Liberation Sans:style=Bold", halign="center", valign="center");
}
difference(){
union(){
translate([102.3480,-13.0000,0.0000]) cube([22.9620,26.0000,3.0000]);
translate([107.8480,0,0]) rotate([90,0,90]) linear_extrude(height=11.9620) polygon([[-6.0000,10.7000],[-2.2895,10.7000],[-2.2895,12.2500],[-1.4895,12.2500],[-1.5954,11.6551],[-1.5611,11.0518],[-1.3885,10.4728],[-1.0869,9.9492],[-0.6725,9.5094],[-0.1679,9.1771],[0.3999,8.9702],[1.0000,8.9000],[1.6001,8.9702],[2.1679,9.1771],[2.6725,9.5094],[3.0869,9.9492],[3.3885,10.4728],[3.5611,11.0518],[3.5954,11.6551],[3.4895,12.2500],[4.2895,12.2500],[4.2895,10.7000],[6.0000,10.7000],[6.0000,3.0000],[-6.0000,3.0000]]);
}
translate([105.0980,0.0000,-1.0000]) cylinder(h=6.0000, d=2.6000, $fn=64);
translate([122.5600,0.0000,-1.0000]) cylinder(h=6.0000, d=2.6000, $fn=64);
translate([113.8290,-9.8000,2.4000]) rotate([0,0,0.00]) linear_extrude(height=0.8000) text("2.6", size=2.400, font="Liberation Sans:style=Bold", halign="center", valign="center");
}
