WongyuKoh/Toccata/hardware/mechanical/key-action-v4/printables/stage0/scad/C06a.scad

// Toccata stage-0 C06a - 비틀림 스프링 시험대 (브래킷·뒷벽 홈 복제·레버 각 눈금) (generated by make_stage0.py; print orientation, z = build direction)
$fn = 64;
difference(){
union(){
translate([0,0,0.0000]) linear_extrude(height=4.0000) polygon([[-60.0000,-45.0000],[8.0000,-45.0000],[8.0000,-27.7000],[8.4788,-27.7328],[10.4104,-27.0670],[12.2903,-26.2669],[14.1093,-25.3363],[15.8582,-24.2800],[17.5283,-23.1032],[19.1115,-21.8117],[20.5998,-20.4119],[21.9859,-18.9109],[23.2628,-17.3159],[24.4243,-15.6350],[25.4645,-13.8765],[26.3784,-12.0491],[27.1613,-10.1619],[27.8094,-8.2243],[28.3194,-6.2459],[28.6889,-4.2364],[28.9160,-2.2059],[28.9995,-0.1645],[28.9391,1.8778],[28.7351,3.9107],[28.3884,5.9242],[27.9009,7.9083],[27.2748,9.8532],[26.5134,11.7491],[25.6203,13.5867],[24.6001,15.3569],[23.4578,17.0509],[22.1990,18.6602],[20.8301,20.1769],[19.3577,21.5935],[17.7893,22.9029],[16.1326,24.0985],[14.3958,25.1746],[12.5875,26.1257],[10.7168,26.9472],[8.7928,27.6349],[6.8253,28.1854],[4.8238,28.5960],[2.7984,28.8647],[0.7591,28.9901],[-1.2839,28.9716],[-3.3206,28.8093],[-5.3408,28.5040],[-7.3345,28.0572],[-9.2918,27.4711],[-11.2029,26.7487],[-13.0585,25.8935],[-14.8492,24.9098],[-16.5663,23.8025],[-18.2011,22.5770],[-19.7455,21.2394],[-21.1920,19.7965],[-22.5333,18.2552],[-23.7627,16.6233],[-24.8741,14.9090],[-25.8621,13.1206],[-26.7218,11.2671],[-27.4487,9.3577],[-28.0395,7.4018],[-28.4911,5.4092],[-28.8012,3.3897],[-28.9684,1.3534],[-28.9918,-0.6896],[-28.8713,-2.7291],[-28.6075,-4.7552],[-28.2017,-6.7576],[-27.6559,-8.7265],[-26.9728,-10.6521],[-26.1559,-12.5248],[-25.2091,-14.3353],[-24.1372,-16.0747],[-22.9455,-17.7343],[-21.6399,-19.3058],[-20.2269,-20.7816],[-18.7134,-22.1542],[-17.1071,-23.4168],[-15.4159,-24.5632],[-13.6482,-25.5876],[-11.8127,-26.4851],[-9.9186,-27.2511]]);
translate([0,0,3.9900]) linear_extrude(height=40.0100) polygon([[-60.0000,-45.0000],[8.0000,-45.0000],[8.0000,-40.0000],[-60.0000,-40.0000]]);
translate([0.0000,0.0000,3.9900]) cylinder(h=1.0100, d=8.0000, $fn=64);
translate([4.5500,13.5000,3.9900]) cube([6.0000,14.0000,5.7100]);
translate([0,0,3.9900]) linear_extrude(height=7.8100) polygon([[-10.8636,26.8883],[-11.6565,26.5542],[-12.4391,26.1967],[-13.2108,25.8162],[-13.9709,25.4129],[-14.7186,24.9872],[-15.4534,24.5396],[-16.1746,24.0704],[-16.8816,23.5799],[-17.5737,23.0687],[-18.2503,22.5372],[-18.9109,21.9859],[-19.5548,21.4152],[-20.1815,20.8257],[-20.7904,20.2178],[-21.3810,19.5921],[-21.9529,18.9492],[-22.5053,18.2896],[-23.0380,17.6139],[-23.5504,16.9227],[-24.0421,16.2166],[-24.5126,15.4962],[-24.9615,14.7622],[-25.3885,14.0152],[-25.7931,13.2558],[-26.1750,12.4848],[-26.5338,11.7028],[-26.8693,10.9105],[-27.1812,10.1086],[-27.4691,9.2978],[-27.7328,8.4788],[-27.9722,7.6523],[-28.1869,6.8191],[-28.3768,5.9799],[-28.5417,5.1355],[-28.6815,4.2865],[-28.7960,3.4337],[-28.8852,2.5779],[-28.9490,1.7199],[-28.9872,0.8603],[-29.0000,0.0000],[-28.9872,-0.8603],[-28.9490,-1.7199],[-28.8852,-2.5779],[-28.7960,-3.4337],[-28.6815,-4.2865],[-28.5417,-5.1355],[-28.3768,-5.9799],[-28.1869,-6.8191],[-27.9722,-7.6523],[-27.7328,-8.4788],[-27.4691,-9.2978],[-27.1812,-10.1086],[-26.8693,-10.9105],[-26.5338,-11.7028],[-26.1750,-12.4848],[-25.7931,-13.2558],[-25.3885,-14.0152],[-24.9615,-14.7622],[-24.5126,-15.4962],[-24.0421,-16.2166],[-23.5504,-16.9227],[-23.0380,-17.6139],[-22.5053,-18.2896],[-21.9529,-18.9492],[-21.3810,-19.5921],[-20.7904,-20.2178],[-20.1815,-20.8257],[-19.5548,-21.4152],[-18.9109,-21.9859],[-18.2503,-22.5372],[-17.5737,-23.0687],[-16.8816,-23.5799],[-16.1746,-24.0704],[-15.4534,-24.5396],[-14.7186,-24.9872],[-13.9709,-25.4129],[-13.2108,-25.8162],[-12.4391,-26.1967],[-11.6565,-26.5542],[-10.8636,-26.8883],[-8.4286,-20.8616],[-9.0438,-20.6024],[-9.6510,-20.3250],[-10.2498,-20.0298],[-10.8395,-19.7169],[-11.4196,-19.3867],[-11.9897,-19.0393],[-12.5493,-18.6753],[-13.0978,-18.2948],[-13.6347,-17.8982],[-14.1597,-17.4858],[-14.6722,-17.0580],[-15.1718,-16.6152],[-15.6580,-16.1578],[-16.1305,-15.6862],[-16.5887,-15.2008],[-17.0324,-14.7020],[-17.4610,-14.1902],[-17.8743,-13.6660],[-18.2719,-13.1297],[-18.6533,-12.5818],[-19.0184,-12.0229],[-19.3667,-11.4534],[-19.6980,-10.8739],[-20.0119,-10.2847],[-20.3082,-9.6865],[-20.5866,-9.0798],[-20.8469,-8.4650],[-21.0888,-7.8429],[-21.3122,-7.2138],[-21.5169,-6.5784],[-21.7025,-5.9371],[-21.8691,-5.2907],[-22.0165,-4.6396],[-22.1444,-3.9844],[-22.2529,-3.3257],[-22.3417,-2.6641],[-22.4109,-2.0001],[-22.4604,-1.3344],[-22.4901,-0.6675],[-22.5000,0.0000],[-22.4901,0.6675],[-22.4604,1.3344],[-22.4109,2.0001],[-22.3417,2.6641],[-22.2529,3.3257],[-22.1444,3.9844],[-22.0165,4.6396],[-21.8691,5.2907],[-21.7025,5.9371],[-21.5169,6.5784],[-21.3122,7.2138],[-21.0888,7.8429],[-20.8469,8.4650],[-20.5866,9.0798],[-20.3082,9.6865],[-20.0119,10.2847],[-19.6980,10.8739],[-19.3667,11.4534],[-19.0184,12.0229],[-18.6533,12.5818],[-18.2719,13.1297],[-17.8743,13.6660],[-17.4610,14.1902],[-17.0324,14.7020],[-16.5887,15.2008],[-16.1305,15.6862],[-15.6580,16.1578],[-15.1718,16.6152],[-14.6722,17.0580],[-14.1597,17.4858],[-13.6347,17.8982],[-13.0978,18.2948],[-12.5493,18.6753],[-11.9897,19.0393],[-11.4196,19.3867],[-10.8395,19.7169],[-10.2498,20.0298],[-9.6510,20.3250],[-9.0438,20.6024],[-8.4286,20.8616]]);
}
translate([0.0000,0.0000,-1.0000]) cylinder(h=7.0000, d=3.9000, $fn=64);
translate([4.5400,13.4900,6.3000]) cube([3.2100,14.1100,2.4000]);
translate([0,0,11.3000]) linear_extrude(height=0.7000) polygon([[-16.8937,-14.4039],[-20.0345,-17.0394],[-20.2595,-16.7713],[-17.1187,-14.1358]]);
translate([-21.4492,-17.9981,11.4500]) rotate([0,0,130.00]) linear_extrude(height=0.5500) text("-40", size=1.600, font="Liberation Sans:style=Bold", halign="center", valign="center");
translate([0,0,11.3000]) linear_extrude(height=0.7000) polygon([[-17.3861,-13.8056],[-19.4349,-15.4063],[-19.6504,-15.1305],[-17.6016,-13.5298]]);
translate([0,0,11.3000]) linear_extrude(height=0.7000) polygon([[-17.8573,-13.1904],[-19.9608,-14.7187],[-20.1665,-14.4355],[-18.0630,-12.9073]]);
translate([0,0,11.3000]) linear_extrude(height=0.7000) polygon([[-18.3068,-12.5592],[-20.4623,-14.0131],[-20.6580,-13.7229],[-18.5025,-12.2690]]);
translate([0,0,11.3000]) linear_extrude(height=0.7000) polygon([[-18.7339,-11.9126],[-20.9389,-13.2904],[-21.1243,-12.9936],[-18.9194,-11.6158]]);
translate([0,0,11.3000]) linear_extrude(height=0.7000) polygon([[-19.1383,-11.2516],[-22.6890,-13.3016],[-22.8640,-12.9984],[-19.3133,-10.9484]]);
translate([-24.2487,-14.0000,11.4500]) rotate([0,0,120.00]) linear_extrude(height=0.5500) text("-30", size=1.600, font="Liberation Sans:style=Bold", halign="center", valign="center");
translate([0,0,11.3000]) linear_extrude(height=0.7000) polygon([[-19.5193,-10.5768],[-21.8149,-11.7974],[-21.9793,-11.4884],[-19.6836,-10.2678]]);
translate([0,0,11.3000]) linear_extrude(height=0.7000) polygon([[-19.8765,-9.8891],[-22.2134,-11.0289],[-22.3668,-10.7143],[-20.0299,-9.5746]]);
translate([0,0,11.3000]) linear_extrude(height=0.7000) polygon([[-20.2095,-9.1894],[-22.5847,-10.2469],[-22.7271,-9.9272],[-20.3519,-8.8697]]);
translate([0,0,11.3000]) linear_extrude(height=0.7000) polygon([[-20.5179,-8.4785],[-22.9286,-9.4525],[-23.0597,-9.1280],[-20.6490,-8.1540]]);
translate([0,0,11.3000]) linear_extrude(height=0.7000) polygon([[-20.8013,-7.7573],[-24.6541,-9.1596],[-24.7738,-8.8307],[-20.9210,-7.4284]]);
translate([-26.3114,-9.5766,11.4500]) rotate([0,0,110.00]) linear_extrude(height=0.5500) text("-20", size=1.600, font="Liberation Sans:style=Bold", halign="center", valign="center");
translate([0,0,11.3000]) linear_extrude(height=0.7000) polygon([[-21.0594,-7.0266],[-23.5321,-7.8301],[-23.6403,-7.4972],[-21.1675,-6.6937]]);
translate([0,0,11.3000]) linear_extrude(height=0.7000) polygon([[-21.2918,-6.2874],[-23.7911,-7.0040],[-23.8875,-6.6676],[-21.3882,-5.9509]]);
translate([0,0,11.3000]) linear_extrude(height=0.7000) polygon([[-21.4982,-5.5405],[-24.0210,-6.1695],[-24.1057,-5.8299],[-21.5829,-5.2009]]);
translate([0,0,11.3000]) linear_extrude(height=0.7000) polygon([[-21.6785,-4.7868],[-24.2217,-5.3274],[-24.2944,-4.9850],[-21.7513,-4.4445]]);
translate([0,0,11.3000]) linear_extrude(height=0.7000) polygon([[-21.8323,-4.0273],[-25.8701,-4.7393],[-25.9308,-4.3946],[-21.8931,-3.6826]]);
translate([-27.5746,-4.8621,11.4500]) rotate([0,0,100.00]) linear_extrude(height=0.5500) text("-10", size=1.600, font="Liberation Sans:style=Bold", halign="center", valign="center");
translate([0,0,11.3000]) linear_extrude(height=0.7000) polygon([[-21.9596,-3.2629],[-24.5343,-3.6248],[-24.5830,-3.2782],[-22.0083,-2.9163]]);
translate([0,0,11.3000]) linear_extrude(height=0.7000) polygon([[-22.0601,-2.4946],[-24.6459,-2.7663],[-24.6824,-2.4183],[-22.0967,-2.1465]]);
translate([0,0,11.3000]) linear_extrude(height=0.7000) polygon([[-22.1337,-1.7232],[-24.7274,-1.9045],[-24.7518,-1.5554],[-22.1581,-1.3740]]);
translate([0,0,11.3000]) linear_extrude(height=0.7000) polygon([[-22.1804,-0.9497],[-24.7788,-1.0404],[-24.7910,-0.6906],[-22.1926,-0.5999]]);
translate([0,0,11.3000]) linear_extrude(height=0.7000) polygon([[-22.2000,-0.1750],[-26.3000,-0.1750],[-26.3000,0.1750],[-22.2000,0.1750]]);
translate([-28.0000,0.0000,11.4500]) rotate([0,0,90.00]) linear_extrude(height=0.5500) text("0", size=1.600, font="Liberation Sans:style=Bold", halign="center", valign="center");
translate([0,0,11.3000]) linear_extrude(height=0.7000) polygon([[-22.1926,0.5999],[-24.7910,0.6906],[-24.7788,1.0404],[-22.1804,0.9497]]);
translate([0,0,11.3000]) linear_extrude(height=0.7000) polygon([[-22.1581,1.3740],[-24.7518,1.5554],[-24.7274,1.9045],[-22.1337,1.7232]]);
translate([0,0,11.3000]) linear_extrude(height=0.7000) polygon([[-22.0967,2.1465],[-24.6824,2.4183],[-24.6459,2.7663],[-22.0601,2.4946]]);
translate([0,0,11.3000]) linear_extrude(height=0.7000) polygon([[-22.0083,2.9163],[-24.5830,3.2782],[-24.5343,3.6248],[-21.9596,3.2629]]);
translate([0,0,11.3000]) linear_extrude(height=0.7000) polygon([[-21.8931,3.6826],[-25.9308,4.3946],[-25.8701,4.7393],[-21.8323,4.0273]]);
translate([-27.5746,4.8621,11.4500]) rotate([0,0,80.00]) linear_extrude(height=0.5500) text("10", size=1.600, font="Liberation Sans:style=Bold", halign="center", valign="center");
translate([0,0,11.3000]) linear_extrude(height=0.7000) polygon([[-21.7513,4.4445],[-24.2944,4.9850],[-24.2217,5.3274],[-21.6785,4.7868]]);
translate([0,0,11.3000]) linear_extrude(height=0.7000) polygon([[-21.5829,5.2009],[-24.1057,5.8299],[-24.0210,6.1695],[-21.4982,5.5405]]);
translate([0,0,11.3000]) linear_extrude(height=0.7000) polygon([[-21.3882,5.9509],[-23.8875,6.6676],[-23.7911,7.0040],[-21.2918,6.2874]]);
translate([0,0,11.3000]) linear_extrude(height=0.7000) polygon([[-21.1675,6.6937],[-23.6403,7.4972],[-23.5321,7.8301],[-21.0594,7.0266]]);
translate([0,0,11.3000]) linear_extrude(height=0.7000) polygon([[-20.9210,7.4284],[-24.7738,8.8307],[-24.6541,9.1596],[-20.8013,7.7573]]);
translate([-26.3114,9.5766,11.4500]) rotate([0,0,70.00]) linear_extrude(height=0.5500) text("20", size=1.600, font="Liberation Sans:style=Bold", halign="center", valign="center");
translate([0,0,11.3000]) linear_extrude(height=0.7000) polygon([[-20.6490,8.1540],[-23.0597,9.1280],[-22.9286,9.4525],[-20.5179,8.4785]]);
translate([0,0,11.3000]) linear_extrude(height=0.7000) polygon([[-20.3519,8.8697],[-22.7271,9.9272],[-22.5847,10.2469],[-20.2095,9.1894]]);
translate([0,0,11.3000]) linear_extrude(height=0.7000) polygon([[-20.0299,9.5746],[-22.3668,10.7143],[-22.2134,11.0289],[-19.8765,9.8891]]);
translate([0,0,11.3000]) linear_extrude(height=0.7000) polygon([[-19.6836,10.2678],[-21.9793,11.4884],[-21.8149,11.7974],[-19.5193,10.5768]]);
translate([0,0,11.3000]) linear_extrude(height=0.7000) polygon([[-19.3133,10.9484],[-22.8640,12.9984],[-22.6890,13.3016],[-19.1383,11.2516]]);
translate([-24.2487,14.0000,11.4500]) rotate([0,0,60.00]) linear_extrude(height=0.5500) text("30", size=1.600, font="Liberation Sans:style=Bold", halign="center", valign="center");
translate([0,0,11.3000]) linear_extrude(height=0.7000) polygon([[-18.9194,11.6158],[-21.1243,12.9936],[-20.9389,13.2904],[-18.7339,11.9126]]);
translate([0,0,11.3000]) linear_extrude(height=0.7000) polygon([[-18.5025,12.2690],[-20.6580,13.7229],[-20.4623,14.0131],[-18.3068,12.5592]]);
}
