WongyuKoh/Toccata/hardware/mechanical/key-action-v4/printables/stage0/scad/C06b.scad

// Toccata stage-0 C06b - 스프링 북 (허브 주머니·가둠 홈·넣는 슬롯·긴 다리 창 복제 + 실 감는 북 R20) (generated by make_stage0.py; print orientation, z = build direction)
$fn = 64;
difference(){
union(){
translate([0.0000,0.0000,0.0000]) cylinder(h=5.0000, d=42.0000, $fn=128);
translate([0.0000,0.0000,4.9900]) cylinder(h=2.0200, d=8.5000, $fn=64);
intersection(){
union(){
translate([0,0,7.0000]) linear_extrude(height=3.0000) polygon([[1.3142,-4.0942],[1.0575,-4.1679],[0.7967,-4.2255],[0.5329,-4.2669],[0.2669,-4.2917],[0.0000,-4.3000],[-12.9500,-10.5000],[-12.9500,-0.0000],[-4.6924,-0.0000],[-8.1847,-3.2763],[-7.7057,-3.7868],[-3.2797,0.3655],[-3.3000,-0.0153],[-3.2762,-0.3959],[-3.2086,-0.7712],[-3.0982,-1.1362],[-2.9465,-1.4861],[-2.7553,-1.8161],[-2.5274,-2.1218],[-2.2658,-2.3992],[-1.9738,-2.6446],[-1.6556,-2.8547],[-1.3152,-3.0266],[-0.9572,-3.1581],[-0.5865,-3.2475],[-0.2079,-3.2934],[0.1734,-3.2954]]);
translate([0,0,7.0000]) linear_extrude(height=3.0000) polygon([[-4.2828,0.3843],[-4.2140,0.8559],[-4.0933,1.3170],[-3.9224,1.7620],[-3.7033,2.1852],[-3.4387,2.5817],[-3.1319,2.9464],[-2.7866,3.2749],[-2.4070,3.5632],[-1.9979,3.8077],[-1.5642,4.0054],[-1.1113,4.1539],[-0.6447,4.2514],[-0.1703,4.2966],[-1.8063,2.7618],[-1.9295,2.6771],[-2.0487,2.5870],[-2.1638,2.4916],[-2.2744,2.3911],[-2.3803,2.2856],[-2.4814,2.1755],[-2.5773,2.0609],[-2.6680,1.9421],[-2.7532,1.8193]]);
}
translate([0.0000,0.0000,6.9000]) cylinder(h=3.2000, d=21.0000, $fn=96);
}
}
rotate_extrude($fn=128) translate([20.0,2.5]) polygon([[0,-0.6],[1.6,-2.2],[1.6,2.2],[0,0.6]]);
translate([0.0000,0.0000,-1.0000]) cylinder(h=13.0000, d=4.1000, $fn=64);
translate([-3.1257,-17.7265,-1.0000]) cylinder(h=7.0000, d=1.6000, $fn=64);
translate([-21.5000,-0.3500,4.4000]) cube([4.0000,0.7000,0.8000]);
translate([0.0000,-10.0000,4.4000]) rotate([0,0,0.00]) linear_extrude(height=0.8000) text("C06b", size=3.000, font="Liberation Sans:style=Bold", halign="center", valign="center");
}
