WongyuKoh/Toccata/hardware/mechanical/key-action-v4/printables/stage0/scad/C11a.scad

// Toccata stage-0 C11a - 윗판 브리지 출력 쿠폰 (핀 사이 39.86, 모델 프레임 그대로 z50 위) (generated by make_stage0.py; print orientation, z = build direction)
$fn = 64;
union(){
intersection(){translate([6.0000,0,0]) rotate([90,0,90]) linear_extrude(height=1.8000) polygon([[31.5000,-42.5000],[64.5000,-42.5000],[64.5000,13.3500],[64.0000,13.3500],[63.5000,13.3500],[63.0000,13.3500],[62.5000,13.3500],[62.0000,13.3500],[61.5000,13.3500],[61.0000,13.3500],[60.5000,13.3500],[60.0000,13.3500],[59.5000,13.3500],[59.0000,13.3500],[58.5000,13.3500],[58.0000,13.3500],[57.5000,13.3500],[57.0000,13.3500],[56.5000,13.3500],[56.0000,13.3500],[55.5000,13.3500],[55.0000,13.3500],[54.5000,13.3500],[54.0000,13.3500],[53.5000,13.3500],[53.0000,13.3500],[52.5000,13.3500],[52.0000,13.3500],[51.5000,13.3500],[51.0000,13.3500],[50.5000,13.3500],[50.0000,13.3500],[49.5000,13.3500],[49.0000,13.3500],[48.5000,13.3500],[48.0000,13.3500],[47.5000,13.3500],[47.0000,13.3500],[46.5000,13.3500],[46.0000,13.3500],[45.5000,13.3500],[45.0000,13.3500],[44.5000,13.3500],[44.0000,13.3500],[43.5000,13.3500],[43.0000,13.3500],[42.5000,13.3500],[42.0000,13.3500],[41.5000,13.3500],[41.0000,13.3500],[40.5000,19.8500],[40.0000,19.8500],[39.5000,19.8500],[39.0000,19.8500],[38.5000,19.8500],[38.0000,19.8500],[37.5000,19.8500],[37.0000,19.8500],[36.5000,19.8500],[36.0000,19.8500],[35.5000,19.8500],[35.0000,19.8500],[34.5000,19.8500],[34.0000,19.8500],[33.5000,19.8500],[33.0000,19.8500],[32.5000,19.8500],[32.0000,19.8500],[31.5000,19.8500]]); translate([-10,-10,2.5000]) cube([400,400,200]);}
intersection(){translate([6.1000,0,0]) rotate([90,0,90]) linear_extrude(height=1.6000) polygon([[7.5000,-42.5000],[31.5000,-42.5000],[31.5000,19.8500],[31.0000,19.8500],[30.5000,19.8500],[30.0000,19.8500],[29.5000,19.8500],[29.0000,19.8500],[28.5000,19.8500],[28.0000,19.8500],[27.5000,19.8500],[27.0000,19.8500],[26.5000,19.8500],[26.0000,19.8500],[25.5000,19.8500],[25.0000,19.8500],[24.5000,19.8500],[24.0000,19.8500],[23.5000,19.8500],[23.0000,21.3500],[22.5000,21.3500],[22.0000,21.3500],[21.5000,21.3500],[21.0000,21.3500],[20.5000,21.3500],[20.0000,21.3500],[19.5000,21.3500],[19.0000,21.3500],[18.5000,21.3500],[18.0000,21.3500],[17.5000,21.3500],[17.0000,21.3500],[16.5000,21.3500],[16.0000,21.3500],[15.5000,21.3500],[15.0000,21.3500],[14.5000,21.3500],[14.0000,21.3500],[13.5000,21.3500],[13.0000,21.3500],[12.5000,21.3500],[12.0000,21.3500],[11.5000,21.3500],[11.0000,21.3500],[10.5000,21.3500],[10.0000,21.3500],[9.5000,21.3500],[9.0000,21.3500],[8.5000,21.3500],[8.0000,21.3500],[7.5000,21.3500]]); translate([-10,-10,2.5000]) cube([400,400,200]);}
intersection(){translate([47.6580,0,0]) rotate([90,0,90]) linear_extrude(height=1.8000) polygon([[31.5000,-26.0000],[64.5000,-26.0000],[64.5000,13.3500],[64.0000,13.3500],[63.5000,13.3500],[63.0000,13.3500],[62.5000,13.3500],[62.0000,13.3500],[61.5000,13.3500],[61.0000,13.3500],[60.5000,13.3500],[60.0000,13.3500],[59.5000,13.3500],[59.0000,13.3500],[58.5000,13.3500],[58.0000,13.3500],[57.5000,13.3500],[57.0000,13.3500],[56.5000,13.3500],[56.0000,13.3500],[55.5000,13.3500],[55.0000,13.3500],[54.5000,13.3500],[54.0000,13.3500],[53.5000,13.3500],[53.0000,13.3500],[52.5000,13.3500],[52.0000,13.3500],[51.5000,13.3500],[51.0000,13.3500],[50.5000,13.3500],[50.0000,13.3500],[49.5000,13.3500],[49.0000,13.3500],[48.5000,13.3500],[48.0000,13.3500],[47.5000,13.3500],[47.0000,13.3500],[46.5000,13.3500],[46.0000,13.3500],[45.5000,13.3500],[45.0000,13.3500],[44.5000,13.3500],[44.0000,13.3500],[43.5000,13.3500],[43.0000,13.3500],[42.5000,13.3500],[42.0000,13.3500],[41.5000,13.3500],[41.0000,13.3500],[40.5000,19.8500],[40.0000,19.8500],[39.5000,19.8500],[39.0000,19.8500],[38.5000,19.8500],[38.0000,19.8500],[37.5000,19.8500],[37.0000,19.8500],[36.5000,19.8500],[36.0000,19.8500],[35.5000,19.8500],[35.0000,19.8500],[34.5000,19.8500],[34.0000,19.8500],[33.5000,19.8500],[33.0000,19.8500],[32.5000,19.8500],[32.0000,19.8500],[31.5000,19.8500]]); translate([-10,-10,2.5000]) cube([400,400,200]);}
intersection(){translate([47.7580,0,0]) rotate([90,0,90]) linear_extrude(height=1.6000) polygon([[4.1000,-44.5000],[26.2000,-44.5000],[26.2000,-26.0000],[31.5000,-26.0000],[31.5000,19.8500],[31.0000,19.8500],[30.5000,19.8500],[30.0000,19.8500],[29.5000,19.8500],[29.0000,19.8500],[28.5000,19.8500],[28.0000,19.8500],[27.5000,19.8500],[27.0000,19.8500],[26.5000,19.8500],[26.0000,19.8500],[25.5000,19.8500],[25.0000,19.8500],[24.5000,19.8500],[24.0000,19.8500],[23.5000,19.8500],[23.0000,21.3500],[22.5000,21.3500],[22.0000,21.3500],[21.5000,21.3500],[21.0000,21.3500],[20.5000,21.3500],[20.0000,21.3500],[19.5000,21.3500],[19.0000,21.3500],[18.5000,21.3500],[18.0000,21.3500],[17.5000,21.3500],[17.0000,21.3500],[16.5000,21.3500],[16.0000,21.3500],[15.5000,21.3500],[15.0000,21.3500],[14.5000,21.3500],[14.0000,21.3500],[13.5000,21.3500],[13.0000,21.3500],[12.5000,21.3500],[12.0000,21.3500],[11.5000,21.3500],[11.0000,21.3500],[10.5000,21.3500],[10.0000,21.3500],[9.5000,21.3500],[9.0000,21.3500],[8.5000,21.3500],[8.0000,21.3500],[7.5000,21.3500],[7.0000,21.3500],[6.5000,21.3500],[6.0000,21.3500],[5.5000,21.3500],[5.0000,21.3500],[4.5000,21.3500],[4.1000,21.3500]]); translate([-10,-10,2.5000]) cube([400,400,200]);}
intersection(){translate([6.0000,0,0]) rotate([90,0,90]) linear_extrude(height=43.4580) polygon([[2.0000,21.3500],[2.0000,24.3500],[3.5000,24.3500],[3.5000,25.3500],[64.5000,25.3500],[64.5000,13.3500],[64.0000,13.3500],[63.5000,13.3500],[63.0000,13.3500],[62.5000,13.3500],[62.0000,13.3500],[61.5000,13.3500],[61.0000,13.3500],[60.5000,13.3500],[60.0000,13.3500],[59.5000,13.3500],[59.0000,13.3500],[58.5000,13.3500],[58.0000,13.3500],[57.5000,13.3500],[57.0000,13.3500],[56.5000,13.3500],[56.0000,13.3500],[55.5000,13.3500],[55.0000,13.3500],[54.5000,13.3500],[54.0000,13.3500],[53.5000,13.3500],[53.0000,13.3500],[52.5000,13.3500],[52.0000,13.3500],[51.5000,13.3500],[51.0000,13.3500],[50.5000,13.3500],[50.0000,13.3500],[49.5000,13.3500],[49.0000,13.3500],[48.5000,13.3500],[48.0000,13.3500],[47.5000,13.3500],[47.0000,13.3500],[46.5000,13.3500],[46.0000,13.3500],[45.5000,13.3500],[45.0000,13.3500],[44.5000,13.3500],[44.0000,13.3500],[43.5000,13.3500],[43.0000,13.3500],[42.5000,13.3500],[42.0000,13.3500],[41.5000,13.3500],[41.0000,13.3500],[40.5000,13.3500],[40.5000,19.8500],[40.0000,19.8500],[39.5000,19.8500],[39.0000,19.8500],[38.5000,19.8500],[38.0000,19.8500],[37.5000,19.8500],[37.0000,19.8500],[36.5000,19.8500],[36.0000,19.8500],[35.5000,19.8500],[35.0000,19.8500],[34.5000,19.8500],[34.0000,19.8500],[33.5000,19.8500],[33.0000,19.8500],[32.5000,19.8500],[32.0000,19.8500],[31.5000,19.8500],[31.0000,19.8500],[30.5000,19.8500],[30.0000,19.8500],[29.5000,19.8500],[29.0000,19.8500],[28.5000,19.8500],[28.0000,19.8500],[27.5000,19.8500],[27.0000,19.8500],[26.5000,19.8500],[26.0000,19.8500],[25.5000,19.8500],[25.0000,19.8500],[24.5000,19.8500],[24.0000,19.8500],[23.5000,19.8500],[23.5000,21.3500],[23.0000,21.3500],[22.5000,21.3500],[22.0000,21.3500],[21.5000,21.3500],[21.0000,21.3500],[20.5000,21.3500],[20.0000,21.3500],[19.5000,21.3500],[19.0000,21.3500],[18.5000,21.3500],[18.0000,21.3500],[17.5000,21.3500],[17.0000,21.3500],[16.5000,21.3500],[16.0000,21.3500],[15.5000,21.3500],[15.0000,21.3500],[14.5000,21.3500],[14.0000,21.3500],[13.5000,21.3500],[13.0000,21.3500],[12.5000,21.3500],[12.0000,21.3500],[11.5000,21.3500],[11.0000,21.3500],[10.5000,21.3500],[10.0000,21.3500],[9.5000,21.3500],[9.0000,21.3500],[8.5000,21.3500],[8.0000,21.3500],[7.5000,21.3500],[7.0000,21.3500],[6.5000,21.3500],[6.0000,21.3500],[5.5000,21.3500],[5.0000,21.3500],[4.5000,21.3500],[4.0000,21.3500],[3.5000,21.3500],[3.0000,21.3500],[2.5000,21.3500],[2.0000,21.3500]]); translate([-10,-10,2.5000]) cube([400,400,200]);}
intersection(){translate([7.8000,0,0]) rotate([90,0,90]) linear_extrude(height=1.0000) polygon([[16.5000,17.2500],[40.5000,17.2500],[40.5000,19.8500],[23.5000,19.8500],[23.5000,21.3500],[15.5000,21.3500],[15.5000,18.2500]]); translate([-10,-10,2.5000]) cube([400,400,200]);}
intersection(){translate([46.6580,0,0]) rotate([90,0,90]) linear_extrude(height=1.0000) polygon([[16.5000,17.2500],[40.5000,17.2500],[40.5000,19.8500],[23.5000,19.8500],[23.5000,21.3500],[15.5000,21.3500],[15.5000,18.2500]]); translate([-10,-10,2.5000]) cube([400,400,200]);}
intersection(){translate([8.8000,0,0]) rotate([90,0,90]) linear_extrude(height=1.3000) polygon([[19.0000,17.2500],[40.5000,17.2500],[40.5000,18.0500],[19.0000,18.0500]]); translate([-10,-10,2.5000]) cube([400,400,200]);}
intersection(){translate([45.3580,0,0]) rotate([90,0,90]) linear_extrude(height=1.3000) polygon([[19.0000,17.2500],[40.5000,17.2500],[40.5000,18.0500],[19.0000,18.0500]]); translate([-10,-10,2.5000]) cube([400,400,200]);}
intersection(){translate([6.0000,0,0]) rotate([90,0,90]) linear_extrude(height=33.2400) polygon([[64.5000,-42.5000],[67.5000,-42.5000],[67.5000,25.3500],[64.5000,25.3500]]); translate([-10,-10,2.5000]) cube([400,400,200]);}
intersection(){translate([39.2400,0,0]) rotate([90,0,90]) linear_extrude(height=10.2180) polygon([[64.5000,-26.5000],[67.5000,-26.5000],[67.5000,25.3500],[64.5000,25.3500]]); translate([-10,-10,2.5000]) cube([400,400,200]);}
intersection(){translate([13.1250,0,0]) rotate([90,0,90]) linear_extrude(height=4.4000) polygon([[63.3000,-0.5000],[64.5000,-0.5000],[64.5000,13.3500],[63.3000,13.3500]]); translate([-10,-10,2.5000]) cube([400,400,200]);}
intersection(){translate([26.9100,0,0]) rotate([90,0,90]) linear_extrude(height=4.4000) polygon([[63.3000,-0.5000],[64.5000,-0.5000],[64.5000,13.3500],[63.3000,13.3500]]); translate([-10,-10,2.5000]) cube([400,400,200]);}
intersection(){translate([39.5330,0,0]) rotate([90,0,90]) linear_extrude(height=4.4000) polygon([[63.3000,-0.5000],[64.5000,-0.5000],[64.5000,13.3500],[63.3000,13.3500]]); translate([-10,-10,2.5000]) cube([400,400,200]);}
translate([1.0000,7.5000,0.0000]) cube([9.8000,60.0000,2.5000]);
translate([44.6580,7.5000,0.0000]) cube([9.8000,60.0000,2.5000]);
translate([1.0000,58.5000,0.0000]) cube([53.4580,9.0000,2.5000]);
}
