WongyuKoh/Toccata/hardware/mechanical/key-action-v4/printables/stage0/scad/C15a.scad

// Toccata stage-0 C15a - 앞 펠트 반발 낙하관 (Ø19.05 강철 공) (generated by make_stage0.py; print orientation, z = build direction)
$fn = 64;
difference(){
union(){
translate([-22.0000,-22.0000,0.0000]) cube([44.0000,44.0000,6.0000]);
translate([0.0000,0.0000,5.9900]) cylinder(h=145.7781, d=23.8500, $fn=96);
}
translate([0.0000,0.0000,5.9900]) cylinder(h=146.7781, d=19.8500, $fn=96);
translate([-3.0000,0.0000,8.0000]) cube([6.0000,23.8500,27.0000]);
translate([3.6000,10.7250,9.8000]) cube([5.0000,2.2000,0.4000]);
translate([3.6000,10.7250,10.8000]) cube([3.0000,2.2000,0.4000]);
translate([3.6000,10.7250,11.8000]) cube([3.0000,2.2000,0.4000]);
translate([3.6000,10.7250,12.8000]) cube([3.0000,2.2000,0.4000]);
translate([3.6000,10.7250,13.8000]) cube([3.0000,2.2000,0.4000]);
translate([3.6000,10.7250,14.8000]) cube([5.0000,2.2000,0.4000]);
translate([3.6000,10.7250,15.8000]) cube([3.0000,2.2000,0.4000]);
translate([3.6000,10.7250,16.8000]) cube([3.0000,2.2000,0.4000]);
translate([3.6000,10.7250,17.8000]) cube([3.0000,2.2000,0.4000]);
translate([3.6000,10.7250,18.8000]) cube([3.0000,2.2000,0.4000]);
translate([3.6000,10.7250,19.8000]) cube([5.0000,2.2000,0.4000]);
translate([3.6000,10.7250,20.8000]) cube([3.0000,2.2000,0.4000]);
translate([3.6000,10.7250,21.8000]) cube([3.0000,2.2000,0.4000]);
translate([3.6000,10.7250,22.8000]) cube([3.0000,2.2000,0.4000]);
translate([3.6000,10.7250,23.8000]) cube([3.0000,2.2000,0.4000]);
translate([3.6000,10.7250,24.8000]) cube([5.0000,2.2000,0.4000]);
translate([3.6000,10.7250,25.8000]) cube([3.0000,2.2000,0.4000]);
translate([3.6000,10.7250,26.8000]) cube([3.0000,2.2000,0.4000]);
translate([3.6000,10.7250,27.8000]) cube([3.0000,2.2000,0.4000]);
translate([3.6000,10.7250,28.8000]) cube([3.0000,2.2000,0.4000]);
translate([3.6000,10.7250,29.8000]) cube([5.0000,2.2000,0.4000]);
translate([3.6000,10.7250,30.8000]) cube([3.0000,2.2000,0.4000]);
translate([3.6000,10.7250,31.8000]) cube([3.0000,2.2000,0.4000]);
translate([3.6000,10.7250,32.8000]) cube([3.0000,2.2000,0.4000]);
translate([3.6000,10.7250,33.8000]) cube([3.0000,2.2000,0.4000]);
translate([3.6000,10.7250,34.8000]) cube([5.0000,2.2000,0.4000]);
translate([0,0,123.218]) rotate([0,90,0]) cylinder(h=40, d=3.3, center=true, $fn=24);
translate([0,0,59.486]) rotate([0,90,0]) cylinder(h=40, d=3.3, center=true, $fn=24);
translate([14.0000,-15.0000,5.4000]) rotate([0,0,0.00]) linear_extrude(height=0.8000) text("C15", size=4.000, font="Liberation Sans:style=Bold", halign="center", valign="center");
}
