WongyuKoh/Toccata/hardware/mechanical/key-action-v4/printables/stage0/scad/C16a.scad

// Toccata stage-0 C16a - 레버 캐리어 (C 자리, 생산 부품 그대로, 3개) (generated by make_stage0.py; print orientation, z = build direction)
$fn = 64;
union(){
translate([0,0,0.0000]) linear_extrude(height=0.7200) difference(){polygon([[3.0000,3.0000],[18.8000,3.0000],[18.8000,2.0000],[44.6000,2.0000],[44.6000,20.0000],[43.8000,23.0000],[37.8000,23.0000],[37.8000,19.4000],[16.8000,19.4000],[16.8000,23.0000],[6.0000,23.0000],[5.4147,22.9424],[4.8519,22.7716],[4.3333,22.4944],[3.8787,22.1213],[3.5056,21.6667],[3.2284,21.1481],[3.0576,20.5853],[3.0000,20.0000]]); translate([57.0500,3.5000]) circle(d=3.9, $fn=48);}
translate([0,0,9.8800]) linear_extrude(height=0.7400) difference(){polygon([[3.0000,3.0000],[18.8000,3.0000],[18.8000,2.0000],[44.6000,2.0000],[44.6000,20.0000],[43.8000,23.0000],[37.8000,23.0000],[37.8000,19.4000],[16.8000,19.4000],[16.8000,23.0000],[6.0000,23.0000],[5.4147,22.9424],[4.8519,22.7716],[4.3333,22.4944],[3.8787,22.1213],[3.5056,21.6667],[3.2284,21.1481],[3.0576,20.5853],[3.0000,20.0000]]); translate([57.0500,3.5000]) circle(d=3.9, $fn=48);}
translate([0,0,0.6800]) linear_extrude(height=9.2400) difference(){polygon([[3.0000,3.0000],[44.6000,3.0000],[44.6000,20.0000],[43.8000,22.0000],[6.8000,22.0000],[6.8000,23.0000],[6.0000,23.0000],[5.4147,22.9424],[4.8519,22.7716],[4.3333,22.4944],[3.8787,22.1213],[3.5056,21.6667],[3.2284,21.1481],[3.0576,20.5853],[3.0000,20.0000]]); translate([57.0500,3.5000]) circle(d=3.9, $fn=48);translate([3.8000,3.0000]) square([40.0000,19.0000]);}
translate([0,0,0.6800]) linear_extrude(height=9.2400) difference(){polygon([[2.0000,21.5000],[3.4019,21.5000],[3.4945,21.6500],[3.6000,21.8000],[3.7202,21.9500],[3.8576,22.1000],[4.0157,22.2500],[4.2000,22.4000],[4.4197,22.5500],[4.6923,22.7000],[5.0633,22.8500],[6.0000,23.0000],[2.0000,23.0000]]); translate([57.0500,3.5000]) circle(d=3.9, $fn=48);}
translate([0,0,0.6800]) linear_extrude(height=9.2400) difference(){polygon([[44.6000,3.0000],[46.3000,3.0000],[46.3000,4.5000],[44.6000,4.5000]]); translate([57.0500,3.5000]) circle(d=3.9, $fn=48);}
translate([0,0,0.0000]) linear_extrude(height=3.8200) difference(){polygon([[61.3500,3.5000],[61.2035,4.6129],[60.7739,5.6500],[60.0906,6.5406],[59.2000,7.2239],[58.1629,7.6535],[57.0500,7.8000],[55.9371,7.6535],[54.9000,7.2239],[54.0094,6.5406],[53.3261,5.6500],[52.8965,4.6129],[52.7500,3.5000],[52.8965,2.3871],[53.3261,1.3500],[54.0094,0.4594],[54.9000,-0.2239],[55.9371,-0.6535],[57.0500,-0.8000],[58.1629,-0.6535],[59.2000,-0.2239],[60.0906,0.4594],[60.7739,1.3500],[61.2035,2.3871]]); translate([57.0500,3.5000]) circle(d=3.9, $fn=48);}
translate([0,0,6.7800]) linear_extrude(height=3.8400) difference(){polygon([[61.3500,3.5000],[61.2035,4.6129],[60.7739,5.6500],[60.0906,6.5406],[59.2000,7.2239],[58.1629,7.6535],[57.0500,7.8000],[55.9371,7.6535],[54.9000,7.2239],[54.0094,6.5406],[53.3261,5.6500],[52.8965,4.6129],[52.7500,3.5000],[52.8965,2.3871],[53.3261,1.3500],[54.0094,0.4594],[54.9000,-0.2239],[55.9371,-0.6535],[57.0500,-0.8000],[58.1629,-0.6535],[59.2000,-0.2239],[60.0906,0.4594],[60.7739,1.3500],[61.2035,2.3871]]); translate([57.0500,3.5000]) circle(d=3.9, $fn=48);}
translate([0,0,0.0000]) linear_extrude(height=3.8200) difference(){polygon([[44.1000,3.5000],[44.1000,14.0000],[57.0500,7.8000],[57.0500,3.5000]]); translate([57.0500,3.5000]) circle(d=3.9, $fn=48);}
translate([0,0,6.7800]) linear_extrude(height=3.8400) difference(){polygon([[44.1000,3.5000],[44.1000,14.0000],[57.0500,7.8000],[57.0500,3.5000]]); translate([57.0500,3.5000]) circle(d=3.9, $fn=48);}
translate([0,0,3.7800]) linear_extrude(height=3.0400) difference(){polygon([[58.3642,7.5942],[58.1075,7.6679],[57.8467,7.7255],[57.5829,7.7669],[57.3169,7.7917],[57.0500,7.8000],[44.1000,14.0000],[44.1000,3.5000],[52.3576,3.5000],[48.8653,6.7763],[49.3443,7.2868],[53.7703,3.1345],[53.7500,3.5153],[53.7738,3.8959],[53.8414,4.2712],[53.9518,4.6362],[54.1035,4.9861],[54.2947,5.3161],[54.5226,5.6218],[54.7842,5.8992],[55.0762,6.1446],[55.3944,6.3547],[55.7348,6.5266],[56.0928,6.6581],[56.4635,6.7475],[56.8421,6.7934],[57.2234,6.7954]]); translate([57.0500,3.5000]) circle(d=3.9, $fn=48);}
translate([0,0,3.7800]) linear_extrude(height=3.0400) difference(){polygon([[52.7672,3.1157],[52.8360,2.6441],[52.9567,2.1830],[53.1276,1.7380],[53.3467,1.3148],[53.6113,0.9183],[53.9181,0.5536],[54.2634,0.2251],[54.6430,-0.0632],[55.0521,-0.3077],[55.4858,-0.5054],[55.9387,-0.6539],[56.4053,-0.7514],[56.8797,-0.7966],[55.2437,0.7382],[55.1205,0.8229],[55.0013,0.9130],[54.8862,1.0084],[54.7756,1.1089],[54.6697,1.2144],[54.5686,1.3245],[54.4727,1.4391],[54.3820,1.5579],[54.2968,1.6807]]); translate([57.0500,3.5000]) circle(d=3.9, $fn=48);}
translate([0,0,10.5800]) linear_extrude(height=0.9750) difference(){polygon([[60.0500,3.5000],[59.8216,4.6481],[59.1713,5.6213],[58.1981,6.2716],[57.0500,6.5000],[55.9019,6.2716],[54.9287,5.6213],[54.2784,4.6481],[54.0500,3.5000],[54.2784,2.3519],[54.9287,1.3787],[55.9019,0.7284],[57.0500,0.5000],[58.1981,0.7284],[59.1713,1.3787],[59.8216,2.3519]]); translate([57.0500,3.5000]) circle(d=3.9, $fn=48);}
translate([0,0,0.6800]) linear_extrude(height=1.1400) difference(){polygon([[18.8000,2.0000],[30.3000,2.0000],[30.3000,3.0000],[18.8000,3.0000]]); translate([57.0500,3.5000]) circle(d=3.9, $fn=48);}
translate([0,0,8.7800]) linear_extrude(height=1.1400) difference(){polygon([[18.8000,2.0000],[30.3000,2.0000],[30.3000,3.0000],[18.8000,3.0000]]); translate([57.0500,3.5000]) circle(d=3.9, $fn=48);}
translate([0,0,0.6800]) linear_extrude(height=0.9400) difference(){polygon([[3.8000,22.0000],[16.8000,22.0000],[16.8000,23.0000],[3.8000,23.0000]]); translate([57.0500,3.5000]) circle(d=3.9, $fn=48);}
translate([0,0,8.9800]) linear_extrude(height=0.9400) difference(){polygon([[3.8000,22.0000],[16.8000,22.0000],[16.8000,23.0000],[3.8000,23.0000]]); translate([57.0500,3.5000]) circle(d=3.9, $fn=48);}
translate([0,0,0.6800]) linear_extrude(height=0.9400) difference(){polygon([[37.8000,22.0000],[43.8500,21.8000],[43.8500,23.0000],[37.8000,23.0000]]); translate([57.0500,3.5000]) circle(d=3.9, $fn=48);}
translate([0,0,8.9800]) linear_extrude(height=0.9400) difference(){polygon([[37.8000,22.0000],[43.8500,21.8000],[43.8500,23.0000],[37.8000,23.0000]]); translate([57.0500,3.5000]) circle(d=3.9, $fn=48);}
}
