WongyuKoh/Toccata/hardware/mechanical/key-action-v4/printables/tools/scad/pin_gauge.scad

// pin_gauge (밸런스 핀 높이 게이지) -- generated by make_tools.py from /private/tmp/claude-501/-Users-kwg-Desktop-mydrive-project-Toccata/2f19e142-4ac2-4c90-bd1e-b3b469f97487/scratchpad/v4/final; USE coordinates mapped to the print bed
$fn=48;
multmatrix([[1, 0, 0, 26.0], [0, -1, 0, 138.0], [0, 0, -1, 33.0], [0, 0, 0, 1]]) union(){
 difference(){
  union(){
   multmatrix([[0,0,1,-26.0000],[1,0,0,0],[0,1,0,0],[0,0,0,1]]) linear_extrude(height=52.0000) polygon(points=[[132.0000,19.0000],[132.3100,19.0000],[132.3100,33.0000],[132.0000,33.0000]]);
   multmatrix([[0,0,1,-26.0000],[1,0,0,0],[0,1,0,0],[0,0,0,1]]) linear_extrude(height=52.0000) polygon(points=[[132.3000,19.0000],[133.8500,19.0000],[133.8500,33.0000],[132.3000,33.0000]]);
   multmatrix([[0,0,1,-26.0000],[1,0,0,0],[0,1,0,0],[0,0,0,1]]) linear_extrude(height=52.0000) polygon(points=[[136.7500,19.0000],[137.1000,19.0000],[137.1000,33.0000],[136.7500,33.0000]]);
   multmatrix([[0,0,1,-26.0000],[1,0,0,0],[0,1,0,0],[0,0,0,1]]) linear_extrude(height=52.0000) polygon(points=[[137.0900,19.3000],[138.0000,19.3000],[138.0000,33.0000],[137.0900,33.0000]]);
   multmatrix([[0,0,1,-26.0000],[1,0,0,0],[0,1,0,0],[0,0,0,1]]) linear_extrude(height=52.0000) polygon(points=[[133.8400,24.5000],[136.7600,24.5000],[136.7600,33.0000],[133.8400,33.0000]]);
   multmatrix([[0,0,1,-26.0000],[1,0,0,0],[0,1,0,0],[0,0,0,1]]) linear_extrude(height=52.0000) polygon(points=[[130.5000,15.0000],[132.0100,15.0000],[132.0100,33.0000],[130.5000,33.0000]]);
   multmatrix([[0,0,1,-3.0000],[1,0,0,0],[0,1,0,0],[0,0,0,1]]) linear_extrude(height=6.0000) polygon(points=[[133.8400,19.0000],[136.7600,19.0000],[136.7600,24.5100],[133.8400,24.5100]]);
   multmatrix([[0,0,1,20.0000],[1,0,0,0],[0,1,0,0],[0,0,0,1]]) linear_extrude(height=6.0000) polygon(points=[[133.8400,23.4000],[136.7600,23.4000],[136.7600,24.5100],[133.8400,24.5100]]);
   multmatrix([[0,0,1,16.0000],[1,0,0,0],[0,1,0,0],[0,0,0,1]]) linear_extrude(height=4.0000) polygon(points=[[133.8400,23.2000],[136.7600,23.2000],[136.7600,24.5100],[133.8400,24.5100]]);
   multmatrix([[0,0,1,-26.0000],[1,0,0,0],[0,1,0,0],[0,0,0,1]]) linear_extrude(height=6.0000) polygon(points=[[133.8400,23.4000],[136.7600,23.4000],[136.7600,24.5100],[133.8400,24.5100]]);
   multmatrix([[0,0,1,-20.0000],[1,0,0,0],[0,1,0,0],[0,0,0,1]]) linear_extrude(height=4.0000) polygon(points=[[133.8400,23.2000],[136.7600,23.2000],[136.7600,24.5100],[133.8400,24.5100]]);
  }
  translate([0,0,18.9900]) linear_extrude(height=4.3100) polygon(points=[[1.2500,135.3000],[1.2260,135.5439],[1.1548,135.7784],[1.0393,135.9945],[0.8839,136.1839],[0.6945,136.3393],[0.4784,136.4548],[0.2439,136.5260],[0.0000,136.5500],[-0.2439,136.5260],[-0.4784,136.4548],[-0.6945,136.3393],[-0.8839,136.1839],[-1.0393,135.9945],[-1.1548,135.7784],[-1.2260,135.5439],[-1.2500,135.3000],[-1.2260,135.0561],[-1.1548,134.8216],[-1.0393,134.6055],[-0.8839,134.4161],[-0.6945,134.2607],[-0.4784,134.1452],[-0.2439,134.0740],[-0.0000,134.0500],[0.2439,134.0740],[0.4784,134.1452],[0.6945,134.2607],[0.8839,134.4161],[1.0393,134.6055],[1.1548,134.8216],[1.2260,135.0561]]);
  multmatrix([[1.0, -0.0, 0, 0.0], [0.0, 1.0, 0, 134.25], [0, 0, 1, 32.6], [0, 0, 0, 1]]) linear_extrude(height=0.410) text("PIN 23.30", size=3.20, font="Arial:style=Bold", halign="center", valign="center");
  multmatrix([[1.0, -0.0, 0, 21.5], [0.0, 1.0, 0, 134.25], [0, 0, 1, 32.6], [0, 0, 0, 1]]) linear_extrude(height=0.410) text("GO>|", size=2.60, font="Arial:style=Bold", halign="center", valign="center");
  multmatrix([[1.0, -0.0, 0, -21.5], [0.0, 1.0, 0, 134.25], [0, 0, 1, 32.6], [0, 0, 0, 1]]) linear_extrude(height=0.410) text("|<GO", size=2.60, font="Arial:style=Bold", halign="center", valign="center");
 }
 
}
