WongyuKoh/Toccata/hardware/mechanical/key-action-v4/printables/tools/scad/assembly_use.scad

$fn=40;
color("SteelBlue") difference(){ union(){ translate([0,0,3.0000]) linear_extrude(height=2.0000) polygon(points=[[-36.0000,-8.0000],[36.0000,-8.0000],[36.0000,214.0000],[-36.0000,214.0000]]); multmatrix([[0,0,1,-36.0000],[1,0,0,0],[0,1,0,0],[0,0,0,1]]) linear_extrude(height=72.0000) polygon(points=[[132.3000,5.0000],[138.4000,5.0000],[138.4000,19.0000],[132.3000,19.0000]]); multmatrix([[0,0,1,-16.3000],[1,0,0,0],[0,1,0,0],[0,0,0,1]]) linear_extrude(height=4.0000) polygon(points=[[138.4000,5.0000],[143.6000,5.0000],[143.6000,26.0000],[138.4000,26.0000]]); multmatrix([[0,0,1,12.3000],[1,0,0,0],[0,1,0,0],[0,0,0,1]]) linear_extrude(height=4.0000) polygon(points=[[138.4000,5.0000],[143.6000,5.0000],[143.6000,26.0000],[138.4000,26.0000]]); multmatrix([[0,0,1,-13.0000],[1,0,0,0],[0,1,0,0],[0,0,0,1]]) linear_extrude(height=26.0000) polygon(points=[[195.8000,5.0000],[200.0000,5.0000],[200.0000,20.0540],[195.8000,20.0540]]); multmatrix([[0,0,1,-10.8000],[1,0,0,0],[0,1,0,0],[0,0,0,1]]) linear_extrude(height=4.0000) polygon(points=[[200.2000,5.0000],[207.5000,5.0000],[207.5000,37.0000],[200.2000,37.0000]]); multmatrix([[0,0,1,6.8000],[1,0,0,0],[0,1,0,0],[0,0,0,1]]) linear_extrude(height=4.0000) polygon(points=[[200.2000,5.0000],[207.5000,5.0000],[207.5000,37.0000],[200.2000,37.0000]]); multmatrix([[0,0,1,-17.0000],[1,0,0,0],[0,1,0,0],[0,0,0,1]]) linear_extrude(height=4.0000) polygon(points=[[185.1400,5.0000],[191.5400,5.0000],[191.5400,27.9000],[190.6400,27.9000],[190.6400,26.9000],[186.0400,26.9000],[186.0400,27.9000],[185.1400,27.9000]]); multmatrix([[0,0,1,13.0000],[1,0,0,0],[0,1,0,0],[0,0,0,1]]) linear_extrude(height=4.0000) polygon(points=[[185.1400,5.0000],[191.5400,5.0000],[191.5400,27.9000],[190.6400,27.9000],[190.6400,26.9000],[186.0400,26.9000],[186.0400,27.9000],[185.1400,27.9000]]); multmatrix([[0,0,1,-17.0000],[1,0,0,0],[0,1,0,0],[0,0,0,1]]) linear_extrude(height=4.0000) polygon(points=[[177.1100,5.0000],[183.5100,5.0000],[183.5100,27.9000],[182.6100,27.9000],[182.6100,26.9000],[178.0100,26.9000],[178.0100,27.9000],[177.1100,27.9000]]); multmatrix([[0,0,1,13.0000],[1,0,0,0],[0,1,0,0],[0,0,0,1]]) linear_extrude(height=4.0000) polygon(points=[[177.1100,5.0000],[183.5100,5.0000],[183.5100,27.9000],[182.6100,27.9000],[182.6100,26.9000],[178.0100,26.9000],[178.0100,27.9000],[177.1100,27.9000]]); multmatrix([[1,0,0,0],[0,0,-1,123.6000],[0,1,0,0],[0,0,0,1]]) linear_extrude(height=5.2000) polygon(points=[[12.9000,5.0000],[29.9000,5.0000],[20.9000,55.5000],[20.9000,65.5000],[12.9000,65.5000]]); multmatrix([[0,0,1,-4.0000],[1,0,0,0],[0,1,0,0],[0,0,0,1]]) linear_extrude(height=8.0000) polygon(points=[[208.5000,5.0000],[213.0000,5.0000],[213.0000,33.5000],[208.5000,33.5000]]); } translate([0,0,10.3000]) linear_extrude(height=8.7100) polygon(points=[[0.9500,135.3000],[0.9176,135.5459],[0.8227,135.7750],[0.6718,135.9718],[0.4750,136.1227],[0.2459,136.2176],[0.0000,136.2500],[-0.2459,136.2176],[-0.4750,136.1227],[-0.6718,135.9718],[-0.8227,135.7750],[-0.9176,135.5459],[-0.9500,135.3000],[-0.9176,135.0541],[-0.8227,134.8250],[-0.6718,134.6282],[-0.4750,134.4773],[-0.2459,134.3824],[-0.0000,134.3500],[0.2459,134.3824],[0.4750,134.4773],[0.6718,134.6282],[0.8227,134.8250],[0.9176,135.0541]]); multmatrix([[0,0,1,-16.3100],[1,0,0,0],[0,1,0,0],[0,0,0,1]]) linear_extrude(height=31.6100) polygon(points=[[139.6211,22.8789],[139.4686,22.7072],[139.3374,22.5189],[139.2291,22.3164],[139.1454,22.1026],[139.0875,21.8804],[139.0560,21.6530],[139.0515,21.4234],[139.0740,21.1950],[139.1232,20.9707],[139.1984,20.7538],[139.2986,20.5472],[139.4224,20.3538],[139.5681,20.1763],[139.7336,20.0172],[139.9166,19.8786],[140.1147,19.7625],[140.3251,19.6705],[140.5448,19.6039],[140.7708,19.5635],[141.0000,19.5500],[141.2292,19.5635],[141.4552,19.6039],[141.6749,19.6705],[141.8853,19.7625],[142.0834,19.8786],[142.2664,20.0172],[142.4319,20.1763],[142.5776,20.3538],[142.7014,20.5472],[142.8016,20.7538],[142.8768,20.9707],[142.9260,21.1950],[142.9485,21.4234],[142.9440,21.6530],[142.9125,21.8804],[142.8546,22.1026],[142.7709,22.3164],[142.6626,22.5189],[142.5314,22.7072],[142.3789,22.8789],[141.0000,24.2577]]); multmatrix([[0,0,1,-10.8100],[1,0,0,0],[0,1,0,0],[0,0,0,1]]) linear_extrude(height=20.6100) polygon(points=[[201.8711,34.8789],[201.7186,34.7072],[201.5874,34.5189],[201.4791,34.3164],[201.3954,34.1026],[201.3375,33.8804],[201.3060,33.6530],[201.3015,33.4234],[201.3240,33.1950],[201.3732,32.9707],[201.4484,32.7538],[201.5486,32.5472],[201.6724,32.3538],[201.8181,32.1763],[201.9836,32.0172],[202.1666,31.8786],[202.3647,31.7625],[202.5751,31.6705],[202.7948,31.6039],[203.0208,31.5635],[203.2500,31.5500],[203.4792,31.5635],[203.7052,31.6039],[203.9249,31.6705],[204.1353,31.7625],[204.3334,31.8786],[204.5164,32.0172],[204.6819,32.1763],[204.8276,32.3538],[204.9514,32.5472],[205.0516,32.7538],[205.1268,32.9707],[205.1760,33.1950],[205.1985,33.4234],[205.1940,33.6530],[205.1625,33.8804],[205.1046,34.1026],[205.0209,34.3164],[204.9126,34.5189],[204.7814,34.7072],[204.6289,34.8789],[203.2500,36.2577]]); }
color("DimGray") union(){ translate([0,0,11.3000]) linear_extrude(height=12.0000) polygon(points=[[1.0000,135.3000],[0.9659,135.5588],[0.8660,135.8000],[0.7071,136.0071],[0.5000,136.1660],[0.2588,136.2659],[0.0000,136.3000],[-0.2588,136.2659],[-0.5000,136.1660],[-0.7071,136.0071],[-0.8660,135.8000],[-0.9659,135.5588],[-1.0000,135.3000],[-0.9659,135.0412],[-0.8660,134.8000],[-0.7071,134.5929],[-0.5000,134.4340],[-0.2588,134.3341],[-0.0000,134.3000],[0.2588,134.3341],[0.5000,134.4340],[0.7071,134.5929],[0.8660,134.8000],[0.9659,135.0412]]); multmatrix([[0,0,1,-16.3000],[1,0,0,0],[0,1,0,0],[0,0,0,1]]) linear_extrude(height=31.6000) polygon(points=[[143.0000,21.5000],[142.9616,21.8902],[142.8478,22.2654],[142.6629,22.6111],[142.4142,22.9142],[142.1111,23.1629],[141.7654,23.3478],[141.3902,23.4616],[141.0000,23.5000],[140.6098,23.4616],[140.2346,23.3478],[139.8889,23.1629],[139.5858,22.9142],[139.3371,22.6111],[139.1522,22.2654],[139.0384,21.8902],[139.0000,21.5000],[139.0384,21.1098],[139.1522,20.7346],[139.3371,20.3889],[139.5858,20.0858],[139.8889,19.8371],[140.2346,19.6522],[140.6098,19.5384],[141.0000,19.5000],[141.3902,19.5384],[141.7654,19.6522],[142.1111,19.8371],[142.4142,20.0858],[142.6629,20.3889],[142.8478,20.7346],[142.9616,21.1098]]); multmatrix([[0,0,1,-10.8000],[1,0,0,0],[0,1,0,0],[0,0,0,1]]) linear_extrude(height=20.6000) polygon(points=[[205.2500,33.5000],[205.2116,33.8902],[205.0978,34.2654],[204.9129,34.6111],[204.6642,34.9142],[204.3611,35.1629],[204.0154,35.3478],[203.6402,35.4616],[203.2500,35.5000],[202.8598,35.4616],[202.4846,35.3478],[202.1389,35.1629],[201.8358,34.9142],[201.5871,34.6111],[201.4022,34.2654],[201.2884,33.8902],[201.2500,33.5000],[201.2884,33.1098],[201.4022,32.7346],[201.5871,32.3889],[201.8358,32.0858],[202.1389,31.8371],[202.4846,31.6522],[202.8598,31.5384],[203.2500,31.5000],[203.6402,31.5384],[204.0154,31.6522],[204.3611,31.8371],[204.6642,32.0858],[204.9129,32.3889],[205.0978,32.7346],[205.2116,33.1098]]); multmatrix([[0,0,1,-15.8000],[1,0,0,0],[0,1,0,0],[0,0,0,1]]) linear_extrude(height=31.6000) polygon(points=[[190.3400,28.9000],[190.3016,29.2902],[190.1878,29.6654],[190.0029,30.0111],[189.7542,30.3142],[189.4511,30.5629],[189.1054,30.7478],[188.7302,30.8616],[188.3400,30.9000],[187.9498,30.8616],[187.5746,30.7478],[187.2289,30.5629],[186.9258,30.3142],[186.6771,30.0111],[186.4922,29.6654],[186.3784,29.2902],[186.3400,28.9000],[186.3784,28.5098],[186.4922,28.1346],[186.6771,27.7889],[186.9258,27.4858],[187.2289,27.2371],[187.5746,27.0522],[187.9498,26.9384],[188.3400,26.9000],[188.7302,26.9384],[189.1054,27.0522],[189.4511,27.2371],[189.7542,27.4858],[190.0029,27.7889],[190.1878,28.1346],[190.3016,28.5098]]); }
color("Orange") difference(){ union(){ multmatrix([[0,0,1,-6.3000],[1,0,0,0],[0,1,0,0],[0,0,0,1]]) linear_extrude(height=12.6000) polygon(points=[[148.8000,30.9000],[195.4000,30.9000],[200.0500,30.9000],[200.0500,40.0000],[191.4000,42.0000],[191.4000,53.4000],[148.8000,53.4000]]); multmatrix([[0,0,1,-6.3000],[1,0,0,0],[0,1,0,0],[0,0,0,1]]) linear_extrude(height=12.6000) polygon(points=[[207.8500,33.5000],[207.8106,34.1004],[207.6933,34.6906],[207.4998,35.2603],[207.2337,35.8000],[206.8994,36.3003],[206.5027,36.7527],[206.0503,37.1494],[205.5500,37.4837],[205.0103,37.7498],[204.4406,37.9433],[203.8504,38.0606],[203.2500,38.1000],[202.6496,38.0606],[202.0594,37.9433],[201.4897,37.7498],[200.9500,37.4837],[200.4497,37.1494],[199.9973,36.7527],[199.6006,36.3003],[199.2663,35.8000],[199.0002,35.2603],[198.8067,34.6906],[198.6894,34.1004],[198.6500,33.5000],[198.6894,32.8996],[198.8067,32.3094],[199.0002,31.7397],[199.2663,31.2000],[199.6006,30.6997],[199.9973,30.2473],[200.4497,29.8506],[200.9500,29.5163],[201.4897,29.2502],[202.0594,29.0567],[202.6496,28.9394],[203.2500,28.9000],[203.8504,28.9394],[204.4406,29.0567],[205.0103,29.2502],[205.5500,29.5163],[206.0503,29.8506],[206.5027,30.2473],[206.8994,30.6997],[207.2337,31.2000],[207.4998,31.7397],[207.6933,32.3094],[207.8106,32.8996]]); multmatrix([[0,0,1,-6.3000],[1,0,0,0],[0,1,0,0],[0,0,0,1]]) linear_extrude(height=12.6000) polygon(points=[[119.0000,57.5000],[156.0000,57.5000],[156.0000,65.5000],[119.0000,65.5000]]); multmatrix([[0,0,1,-6.3000],[1,0,0,0],[0,1,0,0],[0,0,0,1]]) linear_extrude(height=12.6000) polygon(points=[[148.8000,53.3900],[156.0000,53.3900],[156.0000,57.5100],[148.8000,57.5100]]); multmatrix([[0,0,1,6.2900],[1,0,0,0],[0,1,0,0],[0,0,0,1]]) linear_extrude(height=5.5100) polygon(points=[[119.0000,63.9000],[123.0000,63.9000],[123.0000,65.5000],[119.0000,65.5000]]); } multmatrix([[0,0,1,-6.3100],[1,0,0,0],[0,1,0,0],[0,0,0,1]]) linear_extrude(height=12.6200) polygon(points=[[205.2000,33.5000],[205.1625,33.8804],[205.0516,34.2462],[204.8714,34.5834],[204.6289,34.8789],[204.3334,35.1214],[203.9962,35.3016],[203.6304,35.4125],[203.2500,35.4500],[202.8696,35.4125],[202.5038,35.3016],[202.1666,35.1214],[201.8711,34.8789],[201.6286,34.5834],[201.4484,34.2462],[201.3375,33.8804],[201.3000,33.5000],[201.3375,33.1196],[201.4484,32.7538],[201.6286,32.4166],[201.8711,32.1211],[202.1666,31.8786],[202.5038,31.6984],[202.8696,31.5875],[203.2500,31.5500],[203.6304,31.5875],[203.9962,31.6984],[204.3334,31.8786],[204.6289,32.1211],[204.8714,32.4166],[205.0516,32.7538],[205.1625,33.1196]]); multmatrix([[0,0,1,-3.1000],[1,0,0,0],[0,1,0,0],[0,0,0,1]]) linear_extrude(height=9.4100) polygon(points=[[149.8000,32.8000],[190.2000,32.8000],[190.2000,52.2000],[149.8000,52.2000]]); }
color("DimGray") union(){ multmatrix([[0,0,1,-2.9000],[1,0,0,0],[0,1,0,0],[0,0,0,1]]) linear_extrude(height=9.0000) polygon(points=[[150.0000,33.0000],[190.0000,33.0000],[190.0000,52.0000],[150.0000,52.0000]]); }
