WongyuKoh/Toccata/hardware/mechanical/key-action-v4/verification/verify44/printables/stage0/stage0_procedure.md

# Toccata W1+ r4.4 — 단계 0 시험 키트 (출력 시편·지그와 절차)

2026-09-28 · `make_stage0.py`가 단일 모델(`final/model_v4.py`, `metrics.json`)에서 만들었다. 모든 합격선·설계값·민감도는 모델 값이고, 모델에 없는 값은 **제안**이라고 적었다. 단위 mm·g·N. 좌표는 DESIGN.md와 같다(z0 책상, y0 백건 립 앞끝). 숫자는 보인 자리에서 반올림(0.5는 0에서 멀어지는 쪽).

여기서는 아무도 물리 시험을 할 수 없다. 이 키트는 DESIGN.md 17장의 20개 시험(+ 모델 밖 3개: 밸런스 핀 압입 P, 캡스턴 너트 트랩 C, 펠트·천 두께 T)을 **집에 있는 도구로** 할 수 있게 시편(STL), 재는 법, 합격 숫자, 그리고 결과마다 모델의 어느 값을 얼마나 바꾸는지를 모았다. 결과는 `stage0_results_template.csv`에 적는다.

## 0. 한눈에

| 순서 | 시험 | 시편 | 합격 | 설계(모델) | 떨어지면 바꿀 모델 값 |
|---|---|---|---|---|---|
| 1 | 1 패드 반발 (계 실효 e) | C01a~d | e ≤ 0.07 | e 0.06 | `pad_e`; e > 0.10이면 `gap_us_w/_b` −0.2 + `pad_E` 1.4 |
| 2 | 2 패드 강성 | C02a·b | 25 % 압축 18.3~36.7 N | 26.2 N (E 1.0) | `pad_E` |
| 3 | 3 윗판 패드 자리 처짐 (굽힘 띠 E + 프레임 조각) | C03a~e | 띠 E ≥ 1823 MPa; 프레임 C# 처짐 ≤ 0.103 mm @98 N | E 1950; 0.057 mm | 윗판 채움 100 %, `plate_t` +0.6~1.2 |
| 4 | 20 강철 블록 유지 (캐리어 스냅 + 접착) | C16a·b | 접착: 116 N에 움직임 ≤ 0.05; 스냅만 빠짐 힘 기록 | 스냅만 빠짐 43 ~ 66 N | 접착 필수 (r4.4 고침 2) |
| 4b | 16 윗판 브리지 출력 | C11a | 처짐 ≤ 0.3 | - | 서포트 유지 (§15) |
| 5 | 15 층간 강도 (핀-윗판 이음) | C12a | 층간 ≥ 30 MPa | 이음 최대 12.9 MPa | `s_rare`·`s_cyc`, 이음 살 3 |
| 6 | 5 스냅 노치 반지름 | C04a~c | 빠짐 1~2 N | 1.99 N (R2.55) | `notch_R` + `lift_play/_abuse/_popout` |
| 7 | 6 가이드 탭 천 | C05a·b | 끌림 ≤ 0.02 N, 놀음 < 0.1 | 놀음 0.05 | `tab_w_b`·`tab_w`·`tab_cloth`·`tab_play` |
| 8 | P 밸런스 핀 압입 (모델 밖 제안) | C07a·b | 돌출 4.30 ± 0.1, 누름 15~80 N (제안) | - | 새 `pin_hole_print` |
| 9 | C 캡스턴 너트 트랩 (모델 밖 제안) | C08a | 토크 3~40 N·mm (제안) | 1/8회전 0.0625 mm | 너트 홈 폭·잠김 구멍 Ø |
| 10 | T 펠트·천 두께 (모델 밖 기준, 조정 환산) | C09a·b | 공칭 ±10 % (제안) | 표 T | 펀칭·심·캡스턴 환산 |
| 11 | 4 앞 펠트 반발 | C15a | e ≤ 0.22 | 0.20 | `front_e`, PU 2T |
| 12 | 8 비틀림 보조 스프링 | C06a·b | k_t 8.0 ± 15 %, 자유각 -30 ± 5° | 쉼 4.19 N·mm | `spring_kt`·`spring_free_deg` |
| 13 | 12 패드 바 놀음·잎 크리프 | C10a~c | 1주 40 °C 뒤 잎 힘 ≥ 50 % | 10.1 g | `bar_leaf` 두께 0.8 |
| 14 | 19 USB-C 케이블 맞춤 | C13a | 몰드 ≤ 12.5 × 7.6 × 25 | - | (회로 고정값, 케이블만 바꿈) |
| 15~ | 7·9·10·11·13·14·17·18  | 조립 모듈 | 17장 그대로 | - | 각 절 참조 |

**가장 먼저 1번(패드 반발)을 한다** — 모든 동역학 결과가 e 0.06 가정 위에 있다(DESIGN §18). 3번의 띠 시험은 화음 자리(설계 492, 합격선 460 N/mm)에 여유가 6.5 %밖에 없다는 것을 처음으로 확인한다: 출력한 윗판의 실효 E가 모델 1950 MPa의 93.5 % 아래이면 화음 자리가 합격선 아래로 내려간다.

## 1. 준비물

| 도구·재료 | 쓰는 곳 | 비고 |
|---|---|---|
| 정밀 저울 0.1 g (최대 200~500 g) | 2 무게, 5 쿠폰, 8 추, 12 잎 힘, C 토크 | 추 컵·쿠폰 무게 |
| 주방 저울 1 g (최대 5 kg, 가능하면 10 kg) | 3 굽힘·프레임 처짐, 5 빠짐 힘, P 누름 힘 | 손으로 누르는 힘 = 저울 읽음 |
| 디지털 버니어 캘리퍼스 0.01 (깊이 막대 있는 것) | 2, 3, 12, 16, P, T |  |
| 다이얼 게이지 0.01 mm, 줄기 Ø8, 행정 10 | 3 | 약 1.5만 원; 스탠드는 C03d·e 출력 |
| 휴대폰 슬로 모션 240 fps | 1, 4, 8, 9, 10 | 삼각대(또는 책 더미)로 눈금판에 수직 |
| PET 심 0.1 (OHP 필름 6×12.2), 영수증 종이 0.05 | 1, 6, 12, 14 | 부품 목록에 있음 |
| Ø4 SUS 봉 토막 24 ×1, 40 ×1, 16 ×1, 45 ×2 | C01, C04c, C06, C12 | 레버 봉 4 m에서 자름 |
| 강철 블록 SS400 9×19×40 ×2 | 1, 3, 9, 12, T | 레버용과 같은 것 |
| Ø19.05 (3/4") 강철 공 1개 (28.4 g) | 4 | 베어링 볼 |
| 대나무 꼬치 Ø3, 가는 실(재봉실/낚싯줄), 순간접착제, 흑연 가루 | 1, 4, 5, 8, 15 |  |
| M3×12 나사 2개, M3 너트·M3×6 버튼헤드 5개씩 | C03d·e, C08 | 캡스턴 재고 |
| 물병·쌀 봉지(무게를 주방 저울로 잰 것), 10 L 양동이, 수건 | 2, 15 |  |
| 40 °C를 1주 유지할 곳 (요구르트 제조기·식품 건조기·온열 매트 + 온도계) | 12 | 여름 차 안은 60 °C를 넘어 안 됨 |
| 후보 패드: ① 미세셀 우레탄 6T + 펠트 1T, ② 점탄성 PU 시트, ③ ①+부틸 1T | 1, 2 | 6×12로 자름 |

## 2. 출력

모든 부품은 256×256 베드, PETG, **서포트 없이** 출력한다(C11a는 서포트 없는 브리지 자체가 시험). STL은 이미 출력 방향(z = 쌓는 방향)으로 놓여 있다. ‘생산과 같은 설정’이라고 적은 쿠폰은 그 부품(프레임·건반·패드 바)을 뽑을 슬라이서 설정을 그대로 써야 결과가 모델로 옮겨진다.

| ID | 이름 | 시험 | 방향 | 설정 | 크기 (mm) | 부피 (cm³) | 브리지 (mm²) |
|---|---|---|---|---|---|---|---|
| C01a | 패드 반발 진자대 (받침·눈금판·패드 자리) | 1 | 브래킷 뒷면을 베드에 (눈금판·보스·패드 블록·발이 위로 솟음). 서포트 없음 | PETG, 0.2 층, 벽 4, 채움 40 % (패드 블록은 채움 100 % 권장: 슬라이서 수정자), 서포트 없음 | 156.0 × 113.0 × 64.0 | 128.2 | 0 |
| C01b | 시험 레버 (강철 9×19×40 자리, 허브 Ø3.9, 지침) | 1 | 옆면(두께 9 방향)을 베드에. 강철 칸은 관통, 윗면이 패드 구간 y153~187에서 열림 | PETG, 0.2 층, 벽 4, 채움 100 % (질량·관성을 모델과 맞춤), 서포트 없음 | 82.5 × 28.5 × 9.0 | 3.1 | 0 |
| C01c | 패드 받침판 (2개: 후보 재료마다 1개) | 1 | 넓은 면을 베드에 | PETG, 0.2 층, 벽 4, 채움 100 % (질량·관성을 모델과 맞춤), 서포트 없음 | 46.0 × 11.0 × 4.0 | 1.7 | 0 |
| C01d | 봉 끝 칼라 (2개) | 1 | 눕혀서 | PETG, 0.2 층, 벽 4, 채움 100 % (질량·관성을 모델과 맞춤), 서포트 없음 | 21.0 × 9.0 × 3.0 | 0.3 | 0 |
| C02a | 패드 압축 지그 (바탕·안내 통) | 2 | 바닥을 베드에 | PETG, 0.2 층, 벽 3, 윗/아랫면 5층, 채움 40 % 자이로이드, 서포트 없음 | 60.0 × 60.0 × 26.0 | 19.2 | 0 |
| C02b | 패드 압축 누름 막대 (추 받침판 80×80) | 2 | 받침판을 베드에 (막대가 위로) | PETG, 0.2 층, 벽 4, 채움 100 % (질량·관성을 모델과 맞춤), 서포트 없음 | 80.0 × 80.0 × 27.0 | 26.5 | 0 |
| C03a | 윗판 굽힘 띠 (3개) | 3 | 넓은 면을 베드에 (윗판처럼 층이 수평) | PETG, 생산 프레임과 같은 슬라이서 설정 (층·벽·채움 그대로), 서포트 없음 | 120.0 × 44.0 × 5.5 | 23.7 | 0 |
| C03b | 3점 굽힘 받침 (R2 두 날, 간격 100) | 3 | 바닥을 베드에 (날은 x 방향 프리즘) | PETG, 0.2 층, 벽 3, 윗/아랫면 5층, 채움 40 % 자이로이드, 서포트 없음 | 30.0 × 120.0 × 14.0 | 17.8 | 0 |
| C03c | 누름 코 (R2 날 + 손가락 받침 24×24, 가운데 Ø4 다이얼 구멍) | 3 | 평평한 윗판을 베드에 (날이 위) | PETG, 0.2 층, 벽 3, 윗/아랫면 5층, 채움 40 % 자이로이드, 서포트 없음 | 24.0 × 24.0 × 13.0 | 3.2 | 0 |
| C03d | 다이얼 게이지 스탠드, 낮은 (굽힘 띠용) | 3 | 옆면(두께 16)을 베드에. Ø8 줄기 구멍은 눈물방울(위 뾰족), 구멍에서 윗면까지 1.0 틈 + M3 나사(가로, Ø2.7에 자가 탭) | PETG, 0.2 층, 벽 3, 윗/아랫면 5층, 채움 40 % 자이로이드, 서포트 없음 | 60.0 × 57.0 × 16.0 | 23.1 | 12 |
| C03e | 다이얼 게이지 스탠드, 높은 (프레임 조각 윗판용) | 3 | 옆면(두께 16)을 베드에. Ø8 줄기 구멍은 눈물방울(위 뾰족), 구멍에서 윗면까지 1.0 틈 + M3 나사(가로, Ø2.7에 자가 탭) | PETG, 0.2 층, 벽 3, 윗/아랫면 5층, 채움 40 % 자이로이드, 서포트 없음 | 60.0 × 117.0 × 16.0 | 34.6 | 12 |
| C04a | 스냅 노치 반지름 쿠폰 (백건 블록 폭, R2.50~2.60, 5개) | 5 | 건반처럼 뒤집어 (블록 윗면 = 손잡이 판을 베드에, 노치가 출력 맨 위의 열린 홈) | PETG, 생산 건반과 같은 슬라이서 설정 (윗면을 베드에, 층 0.2), 서포트 없음 | 130.8 × 26.0 × 12.3 | 14.1 | 0 |
| C04b | 스냅 노치 반지름 쿠폰 (흑건 블록 폭, R2.50~2.60, 5개) | 5 | 건반처럼 뒤집어 (블록 윗면 = 손잡이 판을 베드에, 노치가 출력 맨 위의 열린 홈) | PETG, 생산 건반과 같은 슬라이서 설정 (윗면을 베드에, 층 0.2), 서포트 없음 | 111.0 × 26.0 × 12.3 | 10.8 | 0 |
| C04c | 봉 받침 (당김 시험용, 저울 위) | 5 | 바닥을 베드에, 봉 구멍은 눈물방울 | PETG, 0.2 층, 벽 3, 윗/아랫면 5층, 채움 40 % 자이로이드, 서포트 없음 | 90.0 × 60.0 × 29.0 | 18.6 | 0 |
| C05a | 가이드 탭 날 (프레임 쪽, 흑 6.8·6.9·7.0 / 백 7.4·7.5·7.6) | 6 | 바닥을 베드에, 날이 수직 (프레임처럼) | PETG, 생산 프레임과 같은 슬라이서 설정 (층·벽·채움 그대로), 서포트 없음 | 66.0 × 22.0 × 15.0 | 9.5 | 0 |
| C05b | 건반 홈 쿠폰 (흑 벽 사이 8.0, 백 갈비 사이 8.6) | 6 | 건반처럼 뒤집어 (윗판 쪽을 베드에, 홈이 위로 열림) | PETG, 생산 건반과 같은 슬라이서 설정 (윗면을 베드에, 층 0.2), 서포트 없음 | 33.0 × 14.0 × 14.0 | 1.4 | 0 |
| C06a | 비틀림 스프링 시험대 (브래킷·뒷벽 홈 복제·레버 각 눈금) | 8 | 브래킷 뒷면을 베드에 (홈 보스·눈금 고리·발이 위로) | PETG, 0.2 층, 벽 3, 윗/아랫면 5층, 채움 40 % 자이로이드, 서포트 없음 | 89.0 × 74.0 × 44.0 | 30.5 | 36 |
| C06b | 스프링 북 (허브 주머니·홈 복제 + 실 감는 북 R20) | 8 | 북 앞면을 베드에 (허브가 위) | PETG, 0.2 층, 벽 4, 채움 100 % (질량·관성을 모델과 맞춤), 서포트 없음 | 42.0 × 42.0 × 8.0 | 6.6 | 0 |
| C07a | 밸런스 핀 압입 레일 쿠폰 (구멍 Ø1.80~2.00, 5개) | P | 바닥을 베드에 (구멍이 수직, 프레임 레일처럼) | PETG, 생산 프레임과 같은 슬라이서 설정 (층·벽·채움 그대로), 서포트 없음 | 70.0 × 12.2 × 14.0 | 11.7 | 0 |
| C07b | 핀 돌출 게이지 (4.30) | P | 밑면을 베드에 (Ø2.4 막힌 구멍이 아래로 열림) | PETG, 0.2 층, 벽 3, 윗/아랫면 5층, 채움 40 % 자이로이드, 서포트 없음 | 30.0 × 10.0 × 8.0 | 2.4 | 5 |
| C08a | 캡스턴 너트 트랩 빔 쿠폰 (5종) | C | 건반처럼 뒤집어 (빔 윗면 = 바탕 판을 베드에); 너트 홈 천장은 5.6~5.8 브리지 | PETG, 생산 건반과 같은 슬라이서 설정 (윗면을 베드에, 층 0.2), 서포트 없음 | 86.0 × 26.0 × 8.7 | 10.1 | 312 |
| C09a | 두께 측정 받침 (22×22 자리 + 깊이 막대 다리) | T | 바닥을 베드에 (다리 윗판 12 브리지) | PETG, 0.2 층, 벽 3, 윗/아랫면 5층, 채움 40 % 자이로이드, 서포트 없음 | 34.0 × 70.0 × 27.0 | 12.6 | 248 |
| C09b | 누름판 (발 20×20, 강철 블록 자리) | T | 누름판 윗면을 베드에 (발이 위, 강철 자리 홈은 바닥 쪽 1.5 깊이) | PETG, 0.2 층, 벽 3, 윗/아랫면 5층, 채움 40 % 자이로이드, 서포트 없음 | 24.0 × 60.0 × 6.0 | 6.0 | 385 |
| C10a | 패드 바 잎 혀 쿠폰 (3개) | 12 | 패드 바처럼 넓은 면을 베드에 (혀 0.6 = 3층) | PETG, 생산 패드 바과 같은 슬라이서 설정 (층·벽·채움 그대로), 서포트 없음 | 38.0 × 18.0 × 1.5 | 0.5 | 0 |
| C10b | 잎 크리프 받침 (0.3 / 0.6 눌림 두 자리) | 12 | 바닥을 베드에 | PETG, 0.2 층, 벽 3, 윗/아랫면 5층, 채움 40 % 자이로이드, 서포트 없음 | 48.0 × 26.0 × 4.0 | 3.1 | 0 |
| C10c | 잎 힘 측정 받침 (뿌리 물림 턱 높이 12) | 12 | 바닥을 베드에 | PETG, 0.2 층, 벽 3, 윗/아랫면 5층, 채움 40 % 자이로이드, 서포트 없음 | 30.0 × 24.0 × 12.0 | 5.4 | 0 |
| C11a | 윗판 브리지 출력 쿠폰 (핀 사이 39.86, 모델 프레임 그대로 z50 위) | 16 | 바로 세워 (프레임처럼), 서포트 없이 — 시험 자체가 서포트 없는 브리지 | PETG, 생산 프레임과 같은 슬라이서 설정 (층·벽·채움 그대로), 서포트 없음 | 53.5 × 65.5 × 25.4 | 30.2 | 2565 |
| C12a | 층간 인장 쿠폰 (핀 두께 1.8 × 폭 2.0, 3개) | 15 | 바로 세워 (당김 방향 = 층을 가로지름, 프레임 핀과 같음); 끝 구멍은 눈물방울 | PETG, 생산 프레임과 같은 슬라이서 설정 (층·벽·채움 그대로), 서포트 없음 | 60.0 × 8.0 × 45.0 | 9.1 | 0 |
| C13a | USB-C 몰드 게이지 (12.5 × 7.6 × 25) | 19 | 창이 수직이 되게 세워 (xy 정밀도) | PETG, 0.2 층, 벽 3, 윗/아랫면 5층, 채움 40 % 자이로이드, 서포트 없음 | 20.5 × 15.6 × 25.0 | 5.6 | 0 |
| C14a | 추 컵 (DW·스프링·캡스턴 토크) | 7 | 바닥을 베드에 | PETG, 0.2 층, 벽 3, 윗/아랫면 5층, 채움 40 % 자이로이드, 서포트 없음 | 31.0 × 26.0 × 18.0 | 2.5 | 0 |
| C15a | 앞 펠트 반발 낙하관 (Ø19.05 강철 공) | 4 | 바닥을 베드에 (관이 수직) | PETG, 0.2 층, 벽 3, 윗/아랫면 5층, 채움 40 % 자이로이드, 서포트 없음 | 44.0 × 44.0 × 151.8 | 31.2 | 33 |
| C16a | 레버 캐리어 (C 자리, 생산 부품 그대로, 3개) | 20 | 생산처럼 옆벽을 베드에 (허브 구멍이 세로), 강철 칸 안 지지대 1개(z 틈 0.2) — 생산 캐리어와 같은 설정 | PETG, 생산 캐리어와 같은 슬라이서 설정 | 59.4 × 23.8 × 11.6 | 2.9 | 778 |
| C16b | 강철 누름 받침 (옆벽을 받치고 가운데 9.6 홈으로 강철이 내려감) | 20 | 바닥을 베드에 | PETG, 0.2 층, 벽 3, 윗/아랫면 5층, 채움 40 % 자이로이드, 서포트 없음 | 40.0 × 46.0 × 8.0 | 11.2 | 0 |

브리지 칸이 0이 아닌 것은 짧은 천장뿐이다: C08a 너트 홈 천장 5.6~5.8, C09a 다리 윗판 26, C09b 강철 자리 9.5, C07b Ø2.4 구멍 천장, C15a 창 윗변 6, C06a 홈 보스. 45°보다 가파른 내민 면은 C03d·e의 가로 M3 구멍(Ø2.7/3.3)과 C15a 꼬치 구멍(Ø3.3)뿐이다. 모든 STL은 닫힌 몸(watertight)이다.

공통: Ø3.9로 출력한 봉 구멍(C01a·b·d, C06a)은 Ø4.0 드릴로 뚫는다(모델 S11과 같음). 봉을 끼우는 구멍에는 흑연 가루를 조금 넣는다(모델 레버와 같은 마찰).

## 3. 시험 절차

### 시험 1 — 패드 반발 (가장 먼저)

**무엇을 재나.** 모델의 `pad_e`는 ‘레버 혼자, 단단한 자리 위의 패드를 PLAY 각속도(건반 앞 1.5 m/s → 레버 31.9 rad/s)로 칠 때의 실효 반발계수’다(`PadTable.calibrate`). C01은 이것을 그대로 만든다: 모델 레버와 같은 자리(봉 L 기준 y150~190, z33~52)에 강철을 잡은 시험 레버(C01b, 강철 포함 58.0 g, 무게중심 반지름 33.01, 봉 둘레 관성 75672 g·mm² — 모델 레버 57.0 g, 75492 g·mm²)를 모델의 패드 면 자리에 놓은 패드에 **중력으로** 떨어뜨린다. 받침은 모델 좌표를 115.3° 돌려, 패드에 처음 닿는 각(b0 = 10.45°)에서 레버 무게중심이 봉 바로 아래에 오게 했다. 그래서 닿는 순간이 흔들림의 맨 아래이고, 되튄 높이(각)만 읽으면 e가 나온다.

**시편.** C01a 받침(봉 구멍·눈금 θ −20~160°, 2° 눈금·20°마다 숫자·패드 블록), C01b 시험 레버, C01c 패드 받침판(후보마다 1개), C01d 칼라, Ø4 봉 24, 강철 블록 1, 후보 패드(6×12).

**준비.**
1. C01a·C01b·C01d 구멍을 Ø4.0으로 뚫는다. 봉(24)을 C01a 뒷면에서 밀어 넣는다(뒷면과 같은 면, 보스 앞면에서 14 나옴). 헐거우면 순간접착제.
2. 강철 블록을 C01b 칸에 옆에서 밀어 넣어 양면을 같게 하고 순간접착제 한 방울로 고정한다. **C01b를 출력할 때 베드에 닿았던 면이 브래킷 쪽**이다(뒤집으면 강철 윗면이 패드 반대쪽을 본다).
3. 봉에 흑연 가루, C01b를 끼우고(허브가 보스 Ø12에 닿음) C01d로 막는다(축 방향 놀음 1 mm 이하).
4. 패드(폼 6T + 펠트 1T, 생산과 같은 풀)를 C01c 표시 자리(6×12)에 펠트가 바깥으로 오게 붙인다. C01c를 C01a 패드 블록 홈에 위에서 끝까지 밀어 넣는다.
5. 받침을 평평한 탁자에 두고 레버가 늘어진 채 패드에 **막 닿는지** 본다: 영수증 종이(0.05)를 강철과 패드 사이에 넣고 당기면 살짝 끌려야 한다. 떨어져 있으면 C01c 뒤에 PET 심(0.1)을 넣고, 눌려 있으면(레버가 패드에 밀려 기울면) C01c 뒷면을 사포질한다. 이때 지침이 가리키는 값 θ_h를 적는다(설계 0°, 모든 읽음에서 뺀다).
6. 휴대폰을 눈금판에 수직으로 30 cm 앞에 고정한다(240 fps).

**마찰 보정 (패드 없이).** C01c를 뺀다. 레버를 θ0 = 6°에서 놓는다(**7°를 넘기지 말 것** — 반대쪽 -8°에서 패드 블록과 1 mm 안으로 들어온다). 영상에서 연속한 꼭짓점 각 a0, a1, a2, a3, a4(양쪽 번갈아)를 읽는다. 반 흔들림마다 줄어드는 각 Δ = (a0 − a4)/4 (라디안으로 바꿈), 마찰 비 f = Δ/2. 봉 마찰 0.28 N·mm(μ 0.25)이면 Δ ≈ 1.7°.

**반발.** C01c(패드)를 다시 넣는다. θ0 = 90°, 120°, 150°에서 각각 3번 놓는다(강철 쪽 틀을 손가락으로 잡았다 뗌; 150°는 거의 거꾸로 선 자세). 영상에서 실제 놓은 각 θ0(움직이기 시작한 첫 프레임)과 **첫 되튐의 꼭짓점 각 θr**을 읽는다(둘 다 θ_h를 뺀 값).

**계산.** e = √{[(1 − cos θr) + f·θr] / [(1 − cos θ0) − f·θ0]} (f 항의 각은 라디안). 레버 질량·무게중심은 식에서 지워진다. 판정 값은 θ0 150°(모델 PLAY 각속도의 96 %)의 평균이다. 90° → 150°로 e가 커지면(속도 의존) 150° 값을 직선으로 PLAY 속도(100 %)까지 늘려 쓴다.

마찰이 없을 때 e별 되튐 각 θr (도):

| θ0 | 충돌 각속도 (rad/s, PLAY 대비) | e 0.04 | e 0.05 | e 0.06 | e 0.07 | e 0.08 | e 0.10 | e 0.12 | e 0.15 | e 0.20 | e 0.25 | e 0.30 |
|---|---|---|---|---|---|---|---|---|---|---|---|---|
| 60° | 15.8 (49 %) | 2.3 | 2.9 | 3.4 | 4.0 | 4.6 | 5.7 | 6.9 | 8.6 | 11.5 | 14.4 | 17.3 |
| 90° | 22.3 (70 %) | 3.2 | 4.1 | 4.9 | 5.7 | 6.5 | 8.1 | 9.7 | 12.2 | 16.3 | 20.4 | 24.5 |
| 120° | 27.3 (86 %) | 4.0 | 5.0 | 6.0 | 7.0 | 7.9 | 9.9 | 11.9 | 14.9 | 19.9 | 25.0 | 30.1 |
| 150° | 30.4 (96 %) | 4.4 | 5.5 | 6.6 | 7.8 | 8.9 | 11.1 | 13.3 | 16.7 | 22.3 | 27.9 | 33.7 |

**합격: e ≤ 0.07** (설계 0.06). 모델 확인: 패드 표가 설계 e에서 되돌린 값 0.060.

**결과에 따라** (모델 `metrics.json` `sens`):

| 측정 e | 판정 | 모델에서 바꿀 것 | 모델 결과 (백 / 흑) |
|---|---|---|---|
| e ≤ 0.07 | 통과 | pad_e = 측정값 | 모델 'pad e 0.07': 들림 0.142 / 0.061, ABUSE 0.137 / 0.240, 연타 16.3 / 18.9 Hz |
| 0.07 < e ≤ 0.10 | 조건부 | pad_e = 측정값, 다른 합격선(E·앞 펠트)은 공칭이어야 | 모델 'pad e 0.10': 백 들림 0.153, 흑 ABUSE 0.334, 연타 16.5 / 19.3 Hz; 최악 조합이면 백 PLAY 들림 0.204 > 0.20 |
| 0.10 < e ≤ 0.15 | 대안 ① | 대안 ①: gap_us_w −0.40 → −0.60, gap_us_b −0.45 → −0.65 (PET 심 2장 더), pad_E 1.4 | 모델 대안 ①(e 0.15): 들림 0.115 / 0.043, ABUSE 0.198 / 0.204, 연타 17.5 / 20.8 Hz |
| e > 0.15 | 불합격 | 다른 패드 후보 (② 점탄성 PU, ③ 부틸 1T 덧댐) | 모델 e 0.25: 백 들림 0.208, 백 ABUSE 키퍼 -0.16(닿음), 흑 ABUSE 0.400 |

민감도(한 가지만 바꿈, 백 / 흑): e 0.06 → 0.07 → 0.10 → 0.15 → 0.25에서 PLAY 들림 0.139 / 0.142 / 0.153 / 0.177 / 0.208, 흑 ABUSE 들림 0.183 / 0.240 / 0.334 / 0.398 / 0.400, 백 0.45 N 유령 재무장 0.16 / 0.22 / 0.46 / 0.98 / 1.00 (모두 펌웨어가 거름), 연타 백 16.2 / 16.3 / 16.5 / 16.8 / 17.0 Hz.

참고: DESIGN D11의 ‘캡 모양 60 g 추를 2.5 m/s로 떨어뜨림’은 17장(레버를 PLAY 속도로 휘두름)과 다르다. 모델의 `pad_e` 정의는 17장 쪽이므로 이 키트는 C01을 기준 방법으로 한다(D11 문구는 다음 개정에서 17장에 맞출 것).

| 기록 | θ0 90° | θ0 120° | θ0 150° |
|---|---|---|---|
| θr 1 / 2 / 3회 (°) |  |  |  |
| e (마찰 보정) |  |  |  |

### 시험 2 — 패드 강성

**모델.** 폼 법칙 σ = E·ε / (1 − ε/ε_D), E 1.0 MPa(펠트 면 포함), ε_D 0.8, 패드 6×12×7. 25 % 압축(1.75 mm)에서 σ 0.364 MPa = 26.2 N.

**방법.** C02a 바탕 자리(6.4×12.4×1)에 패드를 펠트가 위로 가게 놓고 C02b 누름 막대를 통에 넣는다. C02b 무게 m_p를 잰다. 버니어 깊이 막대를 C02b 모서리 Ø4.2 구멍으로 넣어 C02a 바탕 윗면까지의 깊이 D0를 잰다. 추(주방 저울로 잰 쌀 봉지·물병) 0.5 / 1.0 / 1.5 / 2.0 / 2.5 / 3.0 / 3.5 kg을 받침판 가운데에 차례로 올리고, 30초 기다린 뒤 D를 잰다. 눌림 d = D0 − D, 힘 F = (추 + m_p)·9.81/1000 N. 마지막에 추를 모두 내리고 1분 뒤 D를 다시 잰다(영구 눌림).

| 눌림 d (mm) | ε | F (N), E 0.7 | E 1.0 (설계) | E 1.4 |
|---|---|---|---|---|
| 0.35 | 0.05 | 2.7 | 3.8 | 5.4 |
| 0.70 | 0.10 | 5.8 | 8.2 | 11.5 |
| 1.05 | 0.15 | 9.3 | 13.3 | 18.6 |
| 1.40 | 0.20 | 13.4 | 19.2 | 26.9 |
| 1.75 | 0.25 | 18.3 | 26.2 | 36.7 |
| 2.10 | 0.30 | 24.2 | 34.6 | 48.4 |

**계산.** d = 1.75에서의 F를 이웃 두 점으로 보간 → σ25 = F/72 MPa → E = σ25 × (1 − 0.25/0.8)/0.25 = 2.750 × σ25. **합격: E 0.7~1.4 MPa (F25 18.3~36.7 N).**

- E < 0.7 → 두꺼운/단단한 등급 (모델 'pad E 0.7': 흑 ABUSE 들림 0.310)
- 0.7 ≤ E ≤ 1.4 → pad_E = 측정값 (통과)
- E > 1.4 → pad_E = 측정값, 윗판 하중 다시 (모델 'pad E 1.4': 백 업스톱 힘 104.2 N (설계 89.3))

### 시험 3 — 윗판 패드 자리 처짐

모델의 자리 강성은 윗판 그릴리지 FE(`plate_fe`, E_PETG 1950 MPa, 판 두께 = z_top 72.9 − 밑면)에서 나온다. 모든 강성이 E에 비례하므로, 출력한 윗판의 **실효 E**를 재면 모델의 자리 강성이 얼마나 줄어드는지 곧바로 안다: 한 건반 자리 1490·r, 6건반 화음 자리 492·r N/mm (r = E_eff / 1950).

**3a. 굽힘 띠 (C03a~d) — 먼저.** C03a는 **윗판을 뽑을 설정 그대로**(벽·윗/아랫면 층·채움) 뽑는다. 두께 t·폭 b를 세 곳에서 잰다.
1. 주방 저울 위에 C03b(날 간격 100)를 놓고 띠를 가운데에 걸친다. 띠 가운데에 C03c(누름 코, 날이 아래)를 얹는다. C03d 스탠드를 같은 저울판 위에 세우고 다이얼 게이지를 줄기로 물려 **끝을 C03c 가운데 Ø4 구멍으로 넣어 띠 윗면에 직접** 0.5 mm쯤 눌러 댄다(누름 코·날 접촉이 읽음에 들어가지 않음). 저울을 0으로 맞춘다.
2. 손가락으로 C03c의 두 날 쪽 판을 고르게 눌러 저울 204 g(2 N)에서 다이얼을 0으로 맞춘다. 510 / 1020 / 1530 / 2040 g(5 / 10 / 15 / 20 N)에서 다이얼을 읽는다(20 N에서 약 1.17 mm). 다시 2 N으로 돌아와 0 근처인지 본다. 3번 되풀이하고, k는 세 번 기울기의 평균.
3. k = (20 − 2) N / (δ20 − δ2). 모델 띠(12×5.5, 경간 100, 굽힘 + 전단)는 k = 15.4 N/mm. E_eff = 1950 × (k / 15.4) × (5.5 / t)³ × (12 / b).

**합격: r = E_eff / 1950 ≥ 0.935 (E_eff ≥ 1823 MPa)** — 화음 자리 합격선 460 N/mm ÷ 모델 491.9. 한 건반 자리(830 N/mm)만 보면 r ≥ 0.557.

| r | 모델에서 바꿀 것 | 근거 (윗판 FE, PLAY 패드 힘) |
|---|---|---|
| r = E_eff/1950 ≥ 0.935 | (선택) E_PETG = 1950 r | 통과 |
| 0.834 ≤ r < 0.935 | 윗판 채움 100 % 다시; 그래도면 plate_t +0.6 (z_top 73.4) | FE 화음 자리 492 → 552 N/mm |
| 0.785 ≤ r < 0.834 | plate_t +1.2 (z_top 74.0 = 높이 목표 끝) | FE 화음 자리 586 N/mm |
| r < 0.785 | 재료·설정 바꿈 (다른 PETG, 온도) | 두께만으로 못 채움; 한 건반 자리 선 r 0.557 |

윗판 두께 민감도(FE): z_top +0 / +0.6 / +1.2 → 화음 자리 492 / 552 / 586 N/mm, 한 건반 C# 1492 / 1765 / 2041 N/mm. +1.2는 높이 목표 z74의 끝이다. 두께를 바꾸면 z_top·가림판·건반 위 틈이 모두 바뀌므로 `plate_t`를 고치고 run_all을 다시 돌린다.

**3b. 프레임 조각 (생산 프레임 파일, 프레임이 나온 뒤).** 권장 조각 S1 = 모듈 프레임 x0~85(건반 C~F, 핀 x0.2~1.8 / 40.76~42.56 / 82.42~84.22) — 17장의 ‘D·D#·E 3건반 조각’은 패드 바 두 칸에 걸치고 C# 자리가 없으므로 S1으로 바꿀 것을 권한다(FE로 S1의 C# 자리는 모듈과 0.7 % 차이).
1. 프레임(또는 S1)을 바닥으로 주방 저울(가능하면 10 kg) 위에 놓는다. 강철 블록을 9×19 끝면으로 윗판 윗면 C# 자리 위에 세운다: 가운데 x21.2, y175.7 (패드 하중 중심).
2. C03e 스탠드를 저울판 위에 세우고 다이얼 끝을 윗판 윗면 x28.2, y175.7(블록 오른쪽 가장자리에서 2.5)에 댄다.
3. 블록 위를 손가락으로 눌러 5 N(510 g)에서 0, 49 N(5.0 kg)과 98 N(10 kg)에서 읽는다. 3번.

| 하중 | 모델 다이얼 점 처짐 (모듈 / S1) | 합격 (한 건반 830 N/mm 선) | 모델 패드 자리 (6×12 발) |
|---|---|---|---|
| 49 N | 0.029 / 0.029 mm | ≤ 0.051 mm | 0.033 mm |
| 98 N | 0.057 / 0.058 mm | ≤ 0.103 mm | 0.066 mm |

다이얼 0.01로는 화음 선(r 0.935)을 가를 수 없다 — 그것은 3a가 한다. 화음 자리 시험(6자리 × 60 N, 17장)은 360 N이 필요해 부엌 도구로는 어렵다; 대신 F|F# 핀 발이 기판 홈을 지나 바닥에 닿는지(틈 0, 17장 불합격 조치)를 눈으로 확인한다.

### 시험 16 — 윗판 브리지 출력 (C11a)

C11a는 모델의 프레임 기둥(`fixed_prisms`)에서 가장 넓은 칸(칸 2, 핀 사이 39.86)을 z50 위로 잘라낸 것이다: 윗판(밑면 z68.9 / 67.4 / 60.9), 두 핀, 뒷벽, 스프링 홈 보스, L 레일과 립. **서포트 없이** 프레임 설정으로 뽑는다.
1. 뒤집어 윗판 윗면을 평평한 곳에 놓는다. 쇠자를 두 바닥 띠 위에 걸치고, 버니어 깊이 막대로 쇠자 윗면에서 윗판 밑면까지 잰다: 핀 옆(핀 면에서 3) 두 곳과 가운데, y150(앞 홈)·y176(패드 구간)·y200(뒤) 세 줄.
2. 처짐 = 핀 옆 평균 − 가운데. **합격: 모든 줄에서 ≤ 0.3.** 레일 립이 서 있고(늘어짐 ≤ 0.3), 1.5T 띠(패드 바 조각 또는 C01c)가 레일에 끝까지 들어가야 한다.
3. 불합격이면 트리 서포트를 유지한다(§15, 모듈당 88 g, 88건반 약 0.6 kg).

### 시험 15 — 층간 강도 (C12a)

핀-윗판 이음은 층을 가로질러 당겨진다. 모델 응력: 한 건반 PLAY 2.5 MPa, 6건반 화음 9.5 MPa, ABUSE 2.0 m/s 화음 12.9 MPa. 한계는 r3 기준(s_cyc 5, s_rare 15 MPa = 강도의 1/6, 1/2). 17장의 10^6회 반복 인장은 기계 없이는 못 하므로, 이 키트는 **정적 층간 강도**로 한계를 확인한다.
1. C12a(목 2.0×1.8, 단면 3.6 mm²) 3개를 프레임 설정으로 바로 세워 뽑는다. 목의 폭·두께를 잰다.
2. 위 구멍에 Ø4 봉(45)을 끼워 튼튼한 막대(의자 두 개 사이 빗자루)에 건다. 아래 구멍 봉에 줄로 양동이를 단다. 밑에 수건.
3. 물을 0.5 L씩 30초마다 붓는다. 끊어지면 양동이+물+봉+줄 무게를 잰다. 강도 = 무게(kg) × 9.81 / 단면.
**합격: ≥ 30 MPa (108 N = 11.0 kg).** 최소 허용 25.9 MPa (ABUSE 화음 12.9 MPa가 강도의 절반).
- ≥ 30 MPa → 그대로 (통과)
- 25.9~30 MPa → s_rare = 강도/2, s_cyc = 강도/6 로 모델 한계 바꿈; 이음 모서리 살 3 (ABUSE 화음 12.9 MPa가 강도의 절반 아래)
- < 25.9 MPa → 출력 온도↑·팬↓, 이음 모서리 살 3 mm (불합격)
- (선택) 크리프 파단: 한 개에 46.5 N(4.75 kg, ABUSE 화음 응력)을 1주 걸어 둔다 — 끊어지면 불합격.

### 시험 5 — 스냅 노치 반지름 (C04)

C04a(백 D 블록 폭 11.96)와 C04b(흑 C# 블록 폭 8.00)는 모델 `notch_block_poly`를 R만 바꿔 뽑은 블록이다(블록 밑면 봉 중심 아래 0.75, 계단 z22.3). **건반과 같은 방향·설정**(윗면을 베드에, 노치가 출력 맨 위의 열린 홈)으로 뽑아야 출력 오차까지 같다.
1. 각 노치에 부싱 천 0.5T(12 × 9, 생산과 같은 풀)를 붙이고 하루 굳힌다.
2. C04c에 Ø4 봉(40)을 끼우고 날개에 1 kg 추를 얹어 주방 저울(1 g)에 놓는다. 저울 0.
3. 쿠폰을 봉에 위에서 눌러 끼운다(딸깍). 두 줄 구멍에 실을 꿰어 가운데를 잡고 2~3초에 걸쳐 곧게 위로 당긴다. 저울 화면을 영상으로 찍어 빠지기 직전 가장 작은 읽음(음수) = 빠짐 힘을 읽는다(g × 0.00981 = N). 5번, 첫 번은 천 길들이기라 빼고 2~5번 평균.

| R | 쉼 입술 틈 | 입술 닿는 들림 | 빠지는 들림 | 모델 추정 빠짐 백 / 흑 (N) | PLAY 최대 들림(0.161) 대비 | 모델 값 |
|---|---|---|---|---|---|---|
| 2.5 | 0.000 | 0.000 | 0.750 | 3.97 / 2.65 | 입술이 일함 | `notch_R` 2.5, `lift_play` 0.000, `lift_popout` 0.750, `lift_abuse` 0.375 |
| 2.525 | 0.034 | 0.095 | 0.775 | 2.92 / 1.95 | 입술이 일함 | `notch_R` 2.525, `lift_play` 0.095, `lift_popout` 0.775, `lift_abuse` 0.387 |
| 2.55 | 0.069 | 0.200 | 0.800 | 1.99 / 1.33 | 닿지 않음 | `notch_R` 2.55, `lift_play` 0.200, `lift_popout` 0.800, `lift_abuse` 0.400 |
| 2.575 | 0.103 | 0.318 | 0.825 | 1.19 / 0.79 | 닿지 않음 | `notch_R` 2.575, `lift_play` 0.318, `lift_popout` 0.825, `lift_abuse` 0.413 |
| 2.6 | 0.138 | 0.459 | 0.850 | 0.54 / 0.36 | 닿지 않음 | `notch_R` 2.6, `lift_play` 0.459, `lift_popout` 0.850, `lift_abuse` 0.425 |

추정 빠짐 힘 = 모델 입술 법칙 1.99 N(R2.55, 백) × (적도에서 입술이 넘어야 할 겹침 비)^1.5(천 접촉 법칙 지수), 흑은 블록 폭 비 0.669를 곱함 — 쿠폰이 이 추정을 대신한다. **합격: 백·흑 모두 1~2 N.** 모델 추정으로는 R2.55가 백 1.99 / 흑 1.33 N이라 흑이 1 N 근처다.

**고르는 법.** 백·흑이 모두 1~2 N인 가장 큰 R. 없으면 흑 ≥ 1 N을 먼저(덜걱 방지), 백은 2.5 N까지 허용. 고른 R을 건반 파일에 넣고 모델에서 `notch_R`와 들림 판정(`lift_play` = 입술 닿는 들림, `lift_popout`, `lift_abuse` = 빠짐/2)을 표대로 바꿔 run_all을 다시 돌린다. **R2.525 이하는 입술 닿는 들림(0.095)이 PLAY 최대 들림(0.161)보다 작아 판정식(‘PLAY에서 입술이 일하지 않음’)을 다시 세워야 한다.** 천 두께가 0.5에서 Δ만큼 다르면 유효 반지름이 −Δ 바뀐다(표 T): 천 0.025 두꺼움 = R 0.025 작음.

끼운 채 DW 변화(≤ 0.5 g)는 고른 R로 뽑은 실제 건반에서 시험 7과 함께 잰다.

### 시험 6 — 가이드 탭 천 (C05)

모델: 흑 탭 6.9 + 천 0.5 × 2 = 7.9가 흑 벽 사이 8.0에, 백 탭 7.5 + 천 × 2 = 8.5가 갈비 사이 8.6에 들어가 옆 놀음 0.05(`tab_play`), 끌림 0.02 N(`guide_drag`).
1. C05a 날(흑 6.8 / 6.9 / 7.0, 백 7.4 / 7.5 / 7.6) 양면에 천을 붙인다: 흑은 0.4 / 0.5 / 0.6T, 백은 0.5T.
2. C05b 홈 쿠폰 하나(100 % 채움이면 0.9 g)에 10원 동전(1.22 g)·클립을 붙여 저울로 2.0 g(= 끌림 0.02 N)에 맞춘다. 날 위에 홈을 얹었을 때 **저절로 끝까지 내려가면** 끌림 ≤ 0.02 N.
3. 날을 한쪽 벽에 밀고 반대쪽 틈에 PET 심 0.1을 넣어 본다. **들어가지 않으면** 놀음 < 0.1(합격).
4. 두 조건을 모두 채우는 날 두께·천을 고른다 → `tab_w_b`·`tab_w`·`tab_cloth`, 잰 놀음의 반을 `tab_play`로 넣고 틈 검사(run_all)를 다시 돌린다.

### 시험 P — 밸런스 핀 압입 (모델 밖, 제안 기준)

모델은 핀 꼭대기 z23.30 ± 0.1(P32)과 핀 x 놀음 0.10(`yaw_pin`)만 정하고 레일 구멍 지름은 없다(DESIGN 1c: ‘핀을 압입하는 구멍이 모델에 없을 뿐’). C07a는 레일 낮은 부분(z5~19.0)과 같은 높이에 Ø1.80~2.00 관통 구멍 5개다.
1. C07a를 주방 저울에 놓고 0. 핀을 구멍에 세우고 C07b 게이지(밑면 구멍 깊이 4.30)를 씌워 게이지가 레일 윗면에 닿을 때까지 손바닥(또는 바이스)으로 누른다. 저울의 가장 큰 읽음 = 누름 힘.
2. 캘리퍼로 돌출(핀 꼭대기 − 레일 윗면)을 잰다: 4.30 ± 0.1.
3. 핀 머리를 옆으로 밀어 흔들림이 느껴지는지, 구멍 둘레가 하얗게(응력 백화) 되는지 본다.
**제안 합격: 누름 힘 15~80 N**(15 N 아래는 청소 때 빠질 수 있음, 80 N 위는 레일이 갈라질 위험), 돌출 4.30 ± 0.1, 흔들림·백화 없음. 고른 지름을 모델에 새 값 `pin_hole_print`로 넣고 레일 구멍으로 geometry에 내보낸다(지금 geometry는 핀과 레일이 15.2 mm² 겹침).

### 시험 C — 캡스턴 너트 트랩 (모델 밖, 제안 기준)

모델(D02): M3 육각 너트를 옆에서 끼우고, 위 Ø2.8 자가 잠김 구멍으로 M3×6 ISO 7380 버튼헤드를 돌려 머리 꼭대기 z31.0. 1/8회전 = 0.0625 mm → DW 백 +0.19 / 흑 +0.10 g, 바닥 캡 높이 +0.19 / +0.12 mm. C08a는 빔(폭 8.0, z21.8~27.5)의 너트 홈 폭·잠김 구멍 5가지다: 1) 홈 5.6 / Ø2.8, 2) 홈 5.7 / Ø2.8, 3) 홈 5.8 / Ø2.8, 4) 홈 5.6 / Ø2.7, 5) 홈 5.6 / Ø2.9.
1. 너트를 옆 홈에 손가락으로 밀어 넣는다. 쿠폰을 뒤집어 두드려도 빠지지 않아야 한다.
2. 버튼헤드를 바탕 판 쪽(Ø7 구멍)에서 2.0 육각 렌치로 돌려 넣는다. 렌치 긴 팔 끝(축에서 40 mm)에 실로 C14 추 컵을 달고 물을 부어 나사가 돌기 시작하는 무게 m을 잰다: 토크 = m × 0.00981 × 40 N·mm.
3. 1/8회전씩 8번(1회전) 돌려 머리 높이 변화를 캘리퍼로 잰다: 0.50 ± 0.05 mm. 20번 풀고 조인 뒤 2를 다시 한다.
**제안 합격: 너트 유지, 토크 3~40 N·mm(처음·20번 뒤 모두)**(3 아래면 진동에 돌 수 있음, 40 위면 2.0 렌치가 헛돌고 PETG 나사산이 뭉개짐). 고른 홈 폭·구멍 지름을 건반 파일과 모델 `key_body` ‘nut trap’에 넣는다.

### 시험 T — 펠트·천 두께 (C09)

모델은 두께를 공칭으로 쓴다. 실제 두께가 다르면 아래 환산으로 조정한다. C09b 발 20×20: 빈 누름판(무게를 잼; 100 % 채움이면 7.5 g → 0.18 kPa), 강철 1개(+53.7 g → 1.50 kPa), 강철 2개(→ 2.82 kPa).
1. C09a 자리(22×22)에 시편 없이 C09b를 얹고, 다리 윗면에서 Ø4 구멍으로 깊이 막대를 내려 누름판 끝까지 깊이 D0를 잰다(세 하중 모두).
2. 시편(22×22)을 놓고 같은 방법으로 D를 잰다. 두께 = D0 − D.

| 재료 | 공칭 (모델) | 두께가 공칭보다 Δ 두꺼우면 | 조정 |
|---|---|---|---|
| 앞 펠트 3T (+ PU 1T) | 3.0 | 건반 앞 바닥이 Δ 높아짐 (dip −Δ) | 업스톱 시점: PET 심을 Δ/0.181장 더 (한 장 = 건반 앞 0.18 / 0.22) |
| 쉼 펠트 1.5T | 1.5 | 건반 앞이 2.49 × Δ 낮게 쉼 | 종이 펀칭(0.1)을 Δ/0.1장 뺌 (한 장 = 건반 앞 0.25) |
| 키퍼 펠트 2T | 2.0 | 키퍼 틈 1.5 − Δ | Δ ≤ 0.3이면 그대로 (PLAY 최소 여유 0.34, 합격선 재료 조합) |
| 캡스턴 펠트 2T | 2.0 | 캡스턴을 Δ 올린 것과 같음 → DW +3.06 × Δ g | 캡스턴을 (Δ/0.0625) × 1/8회전 조여 머리를 낮춤 |
| 패드 펠트 1T + 폼 6T | 7.0 | 업스톱 틈이 Δ 더 음수 | PET 심 Δ/0.1장 뺌 (한 장 = 레버 0.23°) |
| 부싱 천 0.5T | 0.50 | 노치 유효 반지름 −Δ, 탭 폭 +2Δ | 시험 5·6을 그 천으로 (R 표에서 Δ만큼 큰 R) |

**제안 합격: 강철 1개 하중에서 공칭 ±10 %.** 벗어나도 위 조정으로 맞출 수 있으면 쓴다.

### 시험 4 — 앞 펠트 반발 (C15a)

모델 앞 펠트: K 30 N/mm^1.5, 실효 e 0.20 (30 g, 접촉 법칙은 질량·속도에 무관; Ø19.05 공 28.4 g로 모델을 돌리면 e 0.200).
1. PU 1T와 펠트 3T를 Ø19.5 원판으로 잘라 C15a 관 바닥에 PU·펠트 순서로 붙인다(생산 앞 레일과 같은 쌓음).
2. 꼬치(Ø3)를 위 구멍(공 밑이 펠트 위 114.7 mm = 1.5 m/s) 또는 아래 구멍(51.0 mm = 1.0 m/s)에 꿰고 공을 얹는다. 창 옆 1 mm 눈금이 보이게 240 fps로 찍으며 꼬치를 뺀다.
3. 공 밑이 펠트에 닿은 높이와 첫 되튐 꼭짓점의 차 h_r을 읽는다. e = √(h_r / h). 5번 평균.

| e | 0.15 | 0.20 (설계) | 0.22 (합격선) | 0.25 | 0.28 |
|---|---|---|---|---|---|
| 1.5 m/s 되튐 (mm) | 2.58 | 4.59 | 5.55 | 7.17 | 8.99 |
| 1.0 m/s 되튐 (mm) | 1.15 | 2.04 | 2.47 | 3.19 | 4.00 |

- e ≤ 0.22 → front_e = 측정값 (통과)
- 0.22 < e ≤ 0.28 → front_e = 측정값 후 run_all (모델 'front felt e 0.28'만: 들림 0.141 / 0.058, ABUSE 0.181 / 0.227 (모두 통과))
- e > 0.28 → 펠트 밑 PU 1T → 2T (앞 레일을 1.0 낮게: w_felt_line) (§17 불합격 조치)

### 시험 8 — 비틀림 보조 스프링 (C06)

모델(D05): SUS304-WPB d0.50, ID 4.5, 4.2권, k_t 8.0 N·mm/rad(코일만 8.98), 자유각 -30°(b = 0에서 30° 감김), 쉼 4.19 / 바닥 5.95 N·mm. C06a는 모델 뒷벽 홈(바닥 y209.8, 폭 1.2, z47~58)을 봉 L 기준 같은 자리에, C06b는 허브 주머니(Ø6.1×3.0)와 다리 홈(35°)을 그대로 복제했다. 긴 다리가 홈 바닥을 미는 팔은 21.39 mm.
1. C06a·C06b 구멍을 Ø4.0으로 뚫고 봉(16)을 C06a에 박는다. 봉에 흑연. 스프링 코일을 C06b 주머니에 넣고 짧은 다리를 홈 위 면에 얹은 채 C06b를 봉에 끼우고(허브가 브래킷 쪽) C01d 칼라로 막는다. 긴 다리를 C06a 홈에 밑에서 넣는다(생산 조립과 같음 — 시험 13 연습).
2. 실을 C06b 매듭 구멍(위쪽)에 묶어 북 홈 위로 시계 방향으로 감고 **오른쪽(+y, 홈 쪽)에서** 내려 C14 추 컵을 단다(팔 = 북 홈 반지름 20.0 + 실 반지름).
3. 추 컵 무게(물 포함)를 10 / 15 / 20 / 25 / 30 / 35 / 40 g으로 바꾸며 북 눈금(레버 각 b)을 읽는다. 각 무게에서 북을 살짝 위·아래로 건드려 멈춘 두 값의 평균(마찰 상쇄).
4. 토크 T = m × 0.00981 × 20.0(N·mm)를 b에 대해 직선 맞춤: 기울기 = k_t, T = 0인 b = 자유각.

| b (°) | -20.0 | -10.0 | 0.0 | 5.0 | 10.0 | 12.6 | 16.0 | 20.0 | 25.0 |
|---|---|---|---|---|---|---|---|---|---|
| 모델 T (N·mm) | 1.40 | 2.79 | 4.19 | 4.89 | 5.59 | 5.95 | 6.42 | 6.98 | 7.68 |
| 추 (g) | 7.1 | 14.2 | 21.4 | 24.9 | 28.5 | 30.3 | 32.7 | 35.6 | 39.2 |

**합격: k_t 6.80~9.20 N·mm/rad, 자유각 -35~-25°, 쉼(b 0) 3.56~4.82, 바닥(b 12.6) 5.06~6.85 N·mm.**
- 자유각 벗어남 Δ° → spring_free_deg = 측정값 (쉼 토크 0.140 N·mm/° → DW·UW 0.37 g/° (캡스턴 1/8회전 0.19 g로 맞춤); ±5° 넘으면 홈 바닥 y를 0.373 mm/° 옮기거나 스프링 다시 주문)
- k_t 벗어남 → spring_kt = 측정값 후 run_all (연타·복귀)

### 시험 12 — 패드 바 잎 크리프 (C10)와 바 놀음

모델: 잎 혀 0.6×1.6×8, 설치 휨 0.3(돌기 0.6 = 틈 0.3 + 휨), 힘 0.099 N(10.1 g), 늘 굽힘 8.2 MPa(공차 끝 +0.3이면 16.5 MPa)로 2 MPa 크리프 선 위. 두 잎의 힘은 패드 붙은 바 무게의 6.0배라 83 % 넘게 풀려야 바가 처진다(§18).
1. **처음 힘.** C10c 턱 윗면에 쿠폰 뿌리를 얹고 강철 블록으로 누른다. 혀가 0.1 g 저울판 위로 나가 돌기가 아래를 보게 한다. C10c 밑에 PET 심 3장 + 카드를 괴어 돌기가 저울판에 **막 닿게**(0.1~0.3 g) 한다. 심 3장을 빼면 돌기가 0.3 눌린다 → 읽음 = F0 (모델 10.1 g).
2. **크리프.** 쿠폰 1·2를 C10b ‘0.3’ 자리, 쿠폰 3을 ‘0.6’ 자리(공차 끝)에 돌기가 아래로 가게 놓고 뿌리 위에 강철 블록을 얹는다. 40 °C에서 7일.
3. 꺼내 1시간 식힌 뒤 1을 다시 한다 → F1. 남은 비 = F1/F0.

- 남은 힘 ≥ 50 % → 그대로 (바 무게의 3배 이상)
- 17~50 % → bar_leaf 두께 0.6 → 0.8 권장 (힘 ×2.37, 응력 ×1.33)
- < 17 % → bar_leaf (0.8, 1.6, 8, 0.5) 또는 손 맞춤 (바가 0.3 처져 딸깍 (83 % 풀림 = 모델 한계))
- 조립 모듈에서는 17장 그대로: 바를 뒤 멈춤까지 넣고 위아래로 흔들어 놀음 없음, 흑 칸에서 10번 빼기(21.5 mm부터 밀어 올림).

### 시험 20 — 강철 블록 유지 (C16a·b, r4.4 고침 2)

모델(4-DOF 동역학): 패드가 강철 윗면을 누를 때 캐리어가 강철을 받치는 힘이 매 음(PLAY 1.5 m/s) 51.6 N, ABUSE 77.6 N이다. 옆벽(0.8) 판 모델로는 **스냅 립만으로는 버티지 못한다**: 이 힘이 립에서 옆벽 밖으로 치우쳐 걸려, 립 선이 한쪽 0.79 ~ 1.20 mm 벌어지고(물림 1.0) 옆벽 립 뿌리가 층 안 19 MPa를 넘는다. 그래서 강철을 **스냅으로 끼운 뒤 두 19×40 옆면을 에폭시로 접착**한다(접착 면 1411 mm², 매 음 전단 0.067 MPa).

1. C16a 3개를 생산 캐리어 설정으로 뽑고 허브를 Ø4.0으로 뚫는다. 강철 블록 3개(생산품)의 옆면을 사포(#120)로 긁고 알코올로 닦는다. 캐리어 옆벽 안쪽도 #120.
2. **스냅만 (캐리어 1)**: 강철을 밑에서 눌러 아래 립을 넘긴다. C16b를 주방 저울(10 kg) 위에 놓고, 캐리어를 옆벽 밑면으로 C16b 위에 얹는다(강철은 가운데 홈 위, 허브는 받침 뒤로 나감). C03c(누름 코, 날을 아래로 → 판을 아래로 뒤집어)로 강철 윗면 패드 자리(레버 y170~182)를 천천히 누르며 저울을 본다. 강철이 립을 밀고 빠지는 힘을 적는다. 모델: 43 ~ 66 N(판의 앞·뒷벽 받침 핀 ~ 고정).
3. **접착 (캐리어 2·3)**: 강철 두 옆면에 2액형 에폭시(5분형)를 얇게(한 면 약 0.07 mL) 바르고 스냅으로 끼운다. 밖으로 나온 것은 닦는다(립·캡스턴 펠트 자리에 묻지 않게). 24시간 굳힌다.
4. 캐리어를 C16b에 얹고 강철 윗면을 116 N(11.9 kg; 욕실 저울 또는 바이스 + 저울)으로 10초씩 3번 누른다. 다이얼(C03e 스탠드)을 강철 윗면 앞쪽(뚜껑 뒤 y155)에 대고 캐리어 뚜껑과의 높이 차이를 누르기 전·후에 잰다. **합격: 움직임 ≤ 0.05 mm, 립·옆벽에 흰 줄 없음.**
5. 같은 캐리어를 1 m에서 나무 바닥에 세 방향(옆벽·앞·허브 쪽)으로 떨어뜨린다. 강철이 그대로면 합격.
6. 10^5회 반복(매 음 52 N)은 모터 캠 장치가 필요해 이 키트에 없다(시험 10과 같음). 대신 완성 모듈을 1주일 연주한 뒤 캐리어 몇 개를 빼 4번을 다시 한다.

평철 모서리 반지름(압연 모서리)은 접착하면 상관없다(검증자 지적 (a)는 스냅만일 때의 문제). 스냅만으로 116 N 넘게 버티면 판 모델이 비관적이라는 뜻이지만, 그래도 아래 립 뿌리 층간 응력이 매 음 한계 5 MPa를 넘으므로 접착은 그대로 둔다.

### 시험 19 — USB-C 케이블 (C13a)

회로 인터페이스(고정값): 플러그 몰드 ≤ 12.5 × 7.6 × 25(z10.7~18.3), 선반 홈 x76.45~91.55(가장자리 틈 1.3). C13a 창(12.5 × 7.6, 길이 25)을 출력 뒤 캘리퍼로 확인하고(작으면 줄로 다듬음), 케이블 몰드가 창을 **끝까지 걸림 없이** 지나면 합격이다. 사기 전에 상품 페이지 치수가 12.5 × 7.6을 넘는 것은 거른다. 프레임 뒤 조각이 나오면 17장대로 10번 꽂고 뺀다.

### 조립 모듈 시험 (7, 9, 10, 11, 13, 14, 17, 18)

건반·레버·프레임이 나온 뒤 17장 그대로 한다. 키트에서 쓰는 것과 숫자:

- **7 DW/UW** — C14a 추 컵 바닥 가운데를 백 y13(흑 앞 끝 + 10)에 놓고 물을 스포이트로 넣어 건반이 끝까지 내려가는 무게 = DW, 끝까지 누른 컵에서 물을 빼 건반이 올라오는 무게 = UW. 합격 DW 47~55 g(모델 51.9 / 51.0), 백 립 y0 ≥ 47 g(47.1), UW ≥ 20 g(42.8 / 40.8). 조정: 강철 앞 퍼티 1 g = DW +1.23 / +1.14 g, 캡스턴 1/8회전 = +0.19 / +0.10 g.
- **9 복귀 시간** — 1 N = 강철 블록 2개(107.4 g = 1.05 N)를 건반 앞에 1초 얹었다가 옆으로 밀어 떨어뜨리고 240 fps로 앞끝을 찍는다. 합격 t50 ≤ 37.6 ms(= 1/(2 × 13.3 Hz)), 끝까지 ≤ 60 ms; 모델 t50 30.8 / 26.6, 끝까지 45.5 / 39.9 ms(마찰 2배 48.6 / 42.5).
- **10 노치 들림** — 노치 옆 흰 점을 240 fps. 합격 PLAY ≤ 0.20, ABUSE ≤ 0.40(모델 PLAY 0.161, 합격선 재료 화음 0.149, ABUSE 0.178, ABUSE 재료 조합 최대 0.349). 입술 천 10^5회 마모는 모터 캠 장치가 필요해 이 키트에 없다.
- **11 유령** — 17장 그대로(거름 켜고 끔). 모델: 350 경우 중 재무장 28건, 거르지 못한 것 0.
- **13 스프링 넣기** — C06에서 한 순서를 생산 캐리어 3개로.
- **14 종이 띠** — 0.05 띠: 백 0.75 N에서 미끄러지고 1.04 N에서 물림, 흑 0.96 / 1.43 N (1 N ≈ 추 컵 102 g). PET 심 한 장 = 레버 0.23° / 0.24°.
- **17 느낌** — y90 131 g, 흑 1 N 바닥이 펠트 위 0.27 mm. 흑 바닥이 무르면 `gap_us_b` −0.45 → −0.30.
- **18 90° 세움** — 모든 건반 앞 높이 ±0.2. 빠지면 노치 R 한 단계 작게(시험 5 표).

## 4. 결과를 모델에 넣는 법

1. `stage0_results_template.csv`를 채운다(판정 O/X).
2. 바뀐 값만 `model_v4.py`의 `P`에 넣는다: `pad_e`, `pad_E`, `front_e`, `notch_R`(+ `lift_play`·`lift_abuse`·`lift_popout`), `tab_w_b`·`tab_w`·`tab_cloth`·`tab_play`, `spring_kt`·`spring_free_deg`, `bar_leaf`, 필요하면 `E_PETG`(= 1950 r)·`plate_t`, `gap_us_w/_b`(대안 ①), `s_rare`·`s_cyc`(층간 강도).
3. `run_all.py`를 다시 돌려 0.2장의 모든 목표가 통과인지 본다. 통과하지 않는 값이 있으면 위 표의 다음 대안으로.
4. 모델에 아직 없는 값(시험 P의 핀 구멍 Ø, 시험 C의 너트 홈 폭·잠김 구멍 Ø)은 새 매개변수로 넣고 geometry에 내보낸다.

## 5. 파일

- `make_stage0.py` — 이 키트를 만드는 스크립트 (`MODEL_DIR` 환경변수, 기본 `../`). OpenSCAD로 STL, STL을 다시 읽어 PNG.
- `stage0_geometry.json` — 부품 C01a~C16b의 치수·출력·질량·브리지 면적, 시험별 합격선·결과 대응, 모델 해석 값.
- `stl/`, `png/`, `scad/` — 부품별 STL(출력 방향), 두 방향 그림, 생성된 OpenSCAD 원본.
- `stage0_results_template.csv` — 결과 기록표.
