WongyuKoh/Toccata/hardware/mechanical/before/cad/renders/v1.5-multipart/assembly_front.png

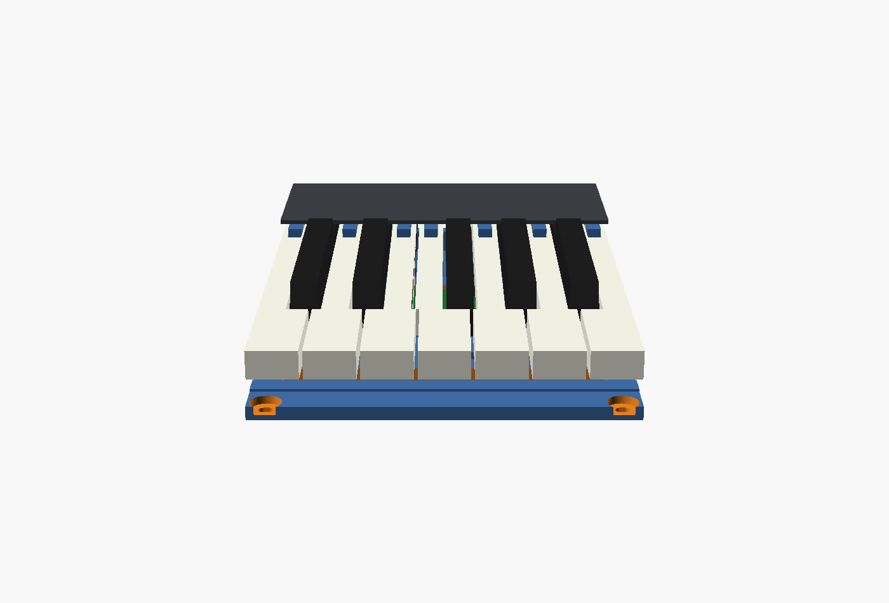
hardware/mechanical/before/cad/renders/v1.5-multipart/assembly_front.png
