WongyuKoh/Toccata/hardware/mechanical/cad/src/body_v3_tall.py

"""Toccata rear bar / body as Part instances (world coordinates, assembled pose).

Sources (the only numeric sources):
  spec/body_speakers.json        speaker parts L/R (5 okoume panels + printed baffle each), grille + spacer ring, EVA
                                 gasket, XT30 holders, feet + 4 mm spacers, dovetail blocks, toggle latch L64
  spec/body_centre_unit.json     centre unit (11 okoume panels), CU tray (re-laid component bosses), CU lid, I/O plate,
                                 lid corner supports + L65 magnets, power-bank holder, key-storage insert, small-parts box
  spec/keyaction_features_frame.json   cheek extents + the M3 bolt seats (bracket.proposal_v4) for the v4 bracket

Decisions applied (task):
  - feet at the drawing positions y299 / y379 (x from body_speakers feet[]); the 4 mm foot spacer appears in both spec
    files and is emitted once (14 pcs)
  - the EVA 3T strip between centre unit and speaker parts is left out on purpose: the 2 dovetails + the toggle latch fix
    the joint, and a 3 mm strip would push the female grooves 3 mm away from the males so they could not drop in
    (overall width stays 1254, A05)
  - CU tray / I/O plate component layout = body_centre_unit.json re-layout (supersedes drawing 10)
  - v3 A12 flat bracket cannot mount in v4 -> new L bracket (printed, L and R), see bracket(); its bolt x = the cheek
    seats the key-action frame generator cuts (BRK_SEAT_X), left leg notched for the headphone cables
  - review fixes (2026-09-30): speaker-wire holes x140 / x1082 (WIRE_HOLE_X), CU-tray pilot pads full height from z22,
    XT30 holder R screws y235 (XT30R_*), speaker-side rear ear screw off the back-panel end grain (REAR_EAR_*), latch seats
    9.5 thick (LATCH_SEAT_Y), grille spacer ring 11 (GRILLE_FACE_Y), CU-tray rib pitch constant TRAY_RIB_PITCH
Not modelled: plywood-to-plywood glue, wood screws other than the bracket screw, rubber-foot screws + washers,
dovetail / XT30 / tray / I/O / holder / insert 13 mm screws, latch M3x10 screws, board screws (F05..F10).

Every printed part: kind='print', one body, lies on the bed via to_bed(orient(...)), print folder 05_본체출력물.
Horizontal holes in printed parts are teardrops whose apex points up in the print orientation.
"""
import json
import math
import os

from manifold3d import CrossSection, FillRule, Manifold

from cadlib import box, cone_z, cyl_x, cyl_y, cyl_z, diff, mirror_x, orient, prism_x, prism_y, prism_z, rot_x, rot_y, \
    to_bed, union
from parts import COLORS, Part

HERE = os.path.dirname(os.path.abspath(__file__))
SPEC = os.path.normpath(os.path.join(HERE, "..", "spec"))

FOLDER = "05_본체출력물"
SRC_S = "spec/body_speakers.json"
SRC_C = "spec/body_centre_unit.json"
SRC_F = "spec/keyaction_features_frame.json"

G_SPK = {"L": "스피커 파트 L", "R": "스피커 파트 R"}
G_CU = "가운데 유닛"
G_CUP = "CU 칸 출력물"
G_JOIN = "뒷바 이음·발"
G_BR = "방진 브래킷"

PETG = "PETG 회색"
PLY = "오꾸메 합판 11.5T"
MIRROR_X = 611.0          # speaker parts L/R are mirror images about x = (-16 + 1238) / 2

R_NONE = [[1, 0, 0], [0, 1, 0], [0, 0, 1]]
R_FLIP = rot_x(180)       # top face (max z) on the bed
R_YMIN = rot_x(90)        # print z = world y  -> the min-y face on the bed
R_YMAX = rot_x(-90)       # print z = -world y -> the max-y face on the bed
R_XMAX = rot_y(90)        # print z = -world x -> the max-x face on the bed
R_XMIN = rot_y(-90)       # print z = world x  -> the min-x face on the bed



def tray_tabs(fe):
    """A8: the spec's left tab at y240..260 puts the 8-ho screw head (about Ø8 x 3 on the tab face x528.75) onto the PED
    board edge (x531, z38.5..40.1). Both left tabs move into the free wall stretch between the PED board (y..294) and the
    Pi 5 (y336..): y298..314 and y318..334, 16 wide. Right tabs stay as specified."""
    out = []
    for t in fe["divider_screw_tabs"]["tabs"]:
        t = json.loads(json.dumps(t))
        if t["side"] == "left":
            if t["box"]["y"][0] < 300:
                t["box"]["y"] = [298.0, 314.0]
                t["hole_center"][1] = 306.0
            else:
                t["box"]["y"] = [318.0, 334.0]
                t["hole_center"][1] = 326.0
        out.append(t)
    return out
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
